langhua/AuroraTessellation-NFC/hardware/pixel/README.md

# 磁像素板（P1 智能像素）设计规格

> 状态（2026-09-23）
>
> - ✅ **架构已定：P1「智能像素」** —— 每块板自带 MCU，既是**可单独销售**的单线圈探测板，也是 4×4 / 8×8 阵列的积木。
> - ✅ **MCU 已定：`CH32V003F4U6`（QFN20，3 × 3 mm）** ✓ SPI ✓ + OPA ✓；`CH32V002F4U6` 同封装 drop-in ✓（见 §4）。
> - ⏳ **阵列间距 20 mm / 22 mm 待定** —— 由 §6 的 coupon 实测决定，**不猜**。
>
> 本文件是像素板的设计依据。`docs/phase-1-4x4-validation.md` 与 `hardware/subboard_4x4/*` 记录的是
> **集中式（P2）**方案（TS3A44159 开关 + CD74HC4067 MUX），**保持不变**；其中 single-channel 板
> （已送厂，3~4 天回板）验证的「线圈 → 2×BAT54S → RC」模拟前端，**正是本像素板的核心，仍然有效**
> （像素板把那 2 颗 BAT54S 换成 **1 颗 `BAS70BRW`** ✓ —— 同样的 4 管全波桥，见 §3）。

NFC 线圈
BAS70BRW
WS2812B-1010

*像素板 = 1 个线圈 + 1 路整流 + 1 颗 MCU + 1 颗 1010 LED*

## 0. 原理图：渲染器与 v1 摆位（2026-09-27）

**为什么要渲染器**：本机 Fritzing 的**命令行导出是坏的** ✗（库仓 `tools/README.md` 早有记录 ✓）
⇒ 每轮都要**用户手动导图**给我看 ✗。`render_sch.py` 把这一步自动化 ✓ —— 它按 Fritzing
自己的摆放规矩把 `.fzz` 的**原理图视图**渲成 PNG/SVG ✓。

    py -3.13 render_sch.py <sketch.fzz> <out.png> [<px宽>] [--verify-export <Fritzing导出的.svg>]

★ **不是自证** ✓：`--verify-export` 拿 **Fritzing 自己导出的 svg 当尺子** ✓ 逐件核对 ✓
（实测：`pixel-schematic.fzz` 9 件 **Δ ≤ 0.0004 单位 = 0.00011 mm** ✓；
`pixel-schematic-v1.fzz` 9 件 **Δ ≤ 0.00003 单位** ✓ ⇒ 渲染即 Fritzing ✓）。

| | | |
|---|---|---|
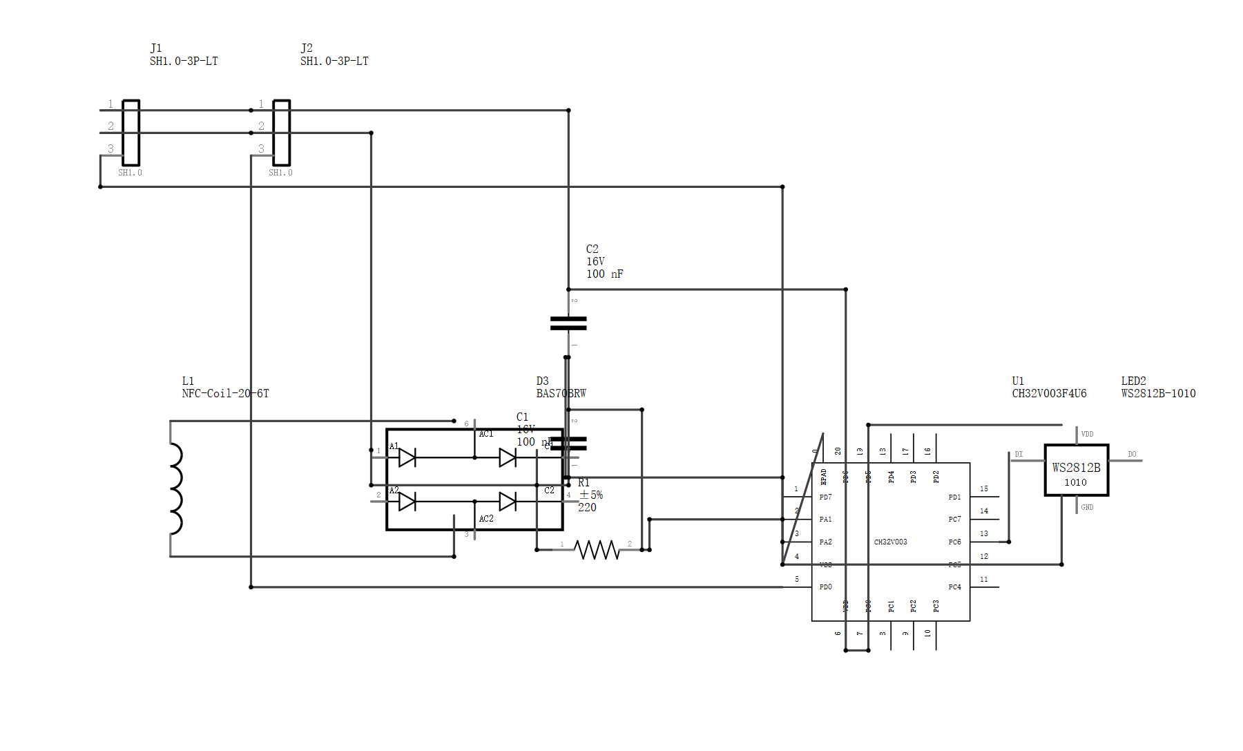
[picture p1: hardware/pixel/pixel-schematic_preview.png]
原图（含 41 根导线）
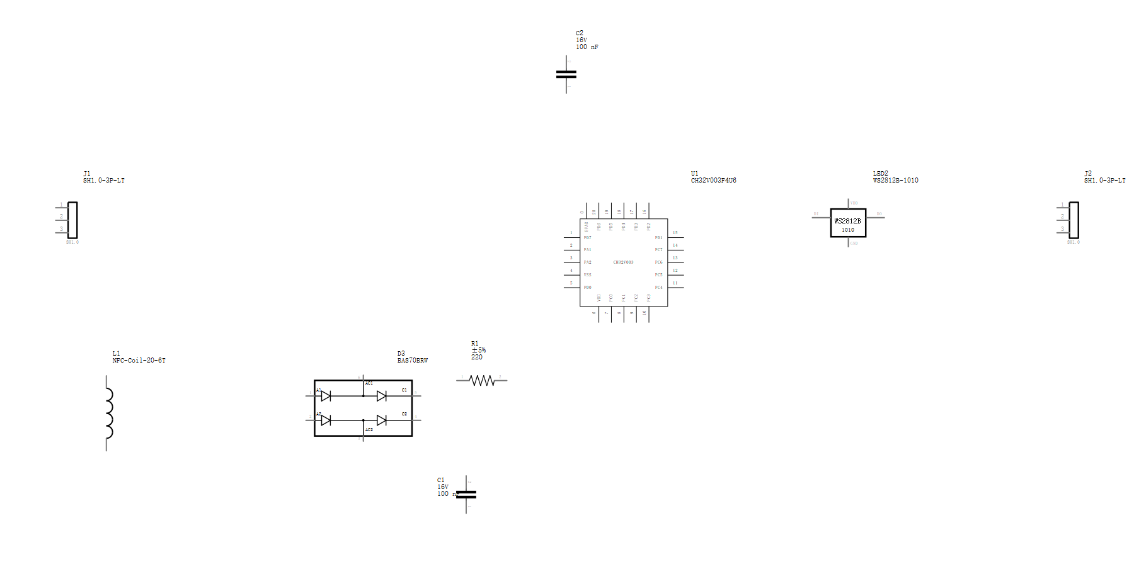
[picture p2: hardware/pixel/pixel-schematic-v1_preview.png]
v1：只摆元件
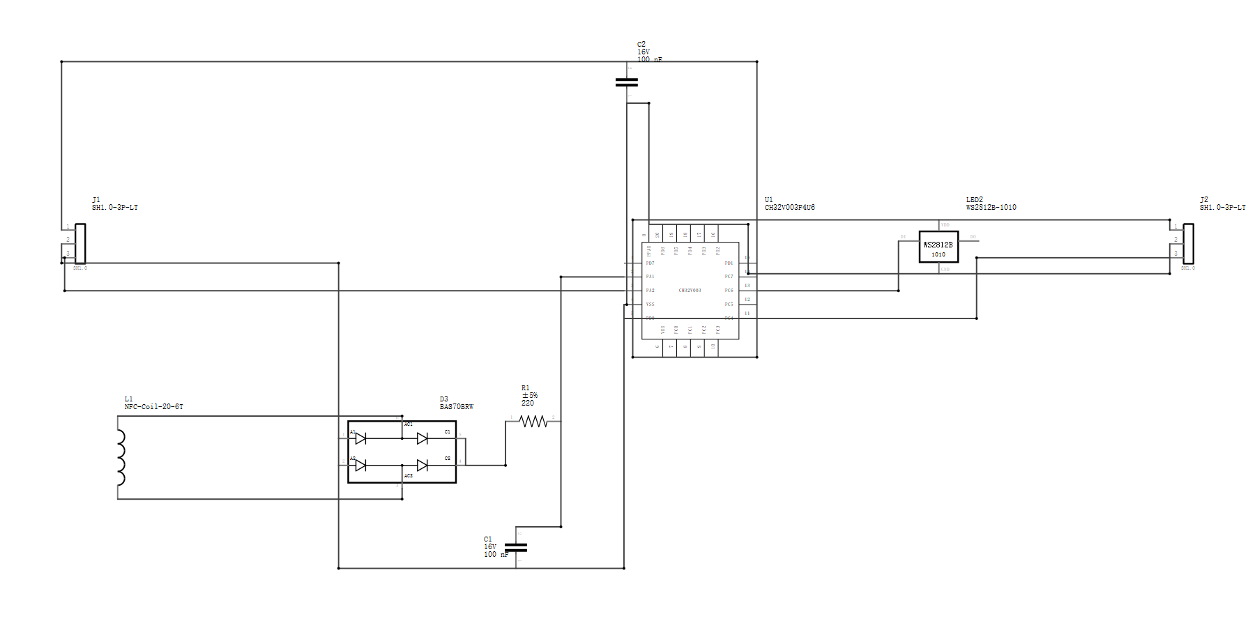
[picture p3: hardware/pixel/pixel-schematic-v2_preview.png]
v2：全接线
|  |  |  |
| **原图** ✓ —— J1/J2 吊在最上方 ✓、长线横穿全图 ✓、位号压在线/元件上 ✓ | **v1** ✓ 只摆元件（主链 `J1→U1→LED2→J2` 一条水平线 ✓、采集支路下沉 ✓、C2 贴 U1 上方 ✓） | **v2** ✓ 全接线（46 根正交导线 ✓、**0 个悬空线端** ✓、绕本体不穿 ✓） |

**v2 = 接线手 ✓**（2026-09-27）：46 根导线、67 条连接 ✓，**网表 10 个网全对 ✓**
（`check_netlist.py` ✓：既无漏接、也无多余连通分量 = **无短路** ✓）、**悬空线端 0 ✓**、
43 → 46 根（绕本体比直穿多 3 根 ✓，换来的正是"不从元件肚子里穿过去" ✓）。

★ 这一手修掉两个真 bug ✓（都在既有管线里，都靠"看得见"才发现 ✓）：
1. **脚位公式错** ✗ —— `sk = loc + RATIO*(尺子 − ox)` 里 `ox` 是"用户坐标 (0,0)"的位置 ✗
   （**不是**零件锚点 ✗）⇒ 凡 `viewBox 原点 ≠ (0,0)` 或**带旋转**的零件，脚位一律偏 ✗
   （实测：J1/J2 偏 1.77 = `k×0.5mm` ✓、U1 偏 17.1 = `k×190` ✓、C1/C2 偏 31.4 ✓；
   原点为 (0,0) 的 D3/L1/R1/LED2 反而只差 0.0001 ⇒ 问题藏得很深 ✗）。
   正解只有一句：**`sketch = RATIO × 尺子坐标`** ✓（我的尺子 1.0 ✓ / Fritzing 导出 1.25 ✓）。
   ⇒ 修好后拟合残差 = **0.0000** ✓、**悬空线端从 11 → 0** ✓。
   （★ 副产品认知：用户原图里那 6 个"悬空端"**不是手画错** ✗，就是这个 bug 的产物 ✓ ——
   我当时误判成用户的图 ✗，记下来别再犯 ✗。）
2. **导线从元件本体里穿过** ✗ —— `path_ok` 对"自己两端元件"**整个豁免** keep-out ✗ ⇒
   为了走直线就从 U1/D3/LED2 肚子里穿过去 ✗。改成**记代价**（穿得少者优先 ✓）而不是
   一律禁 ❌（D3 的 `AC1/AC2` 脚**本来就在本体内部** ✓，禁了就没路 ✓）。

| | | | |
|---|---|---|---|
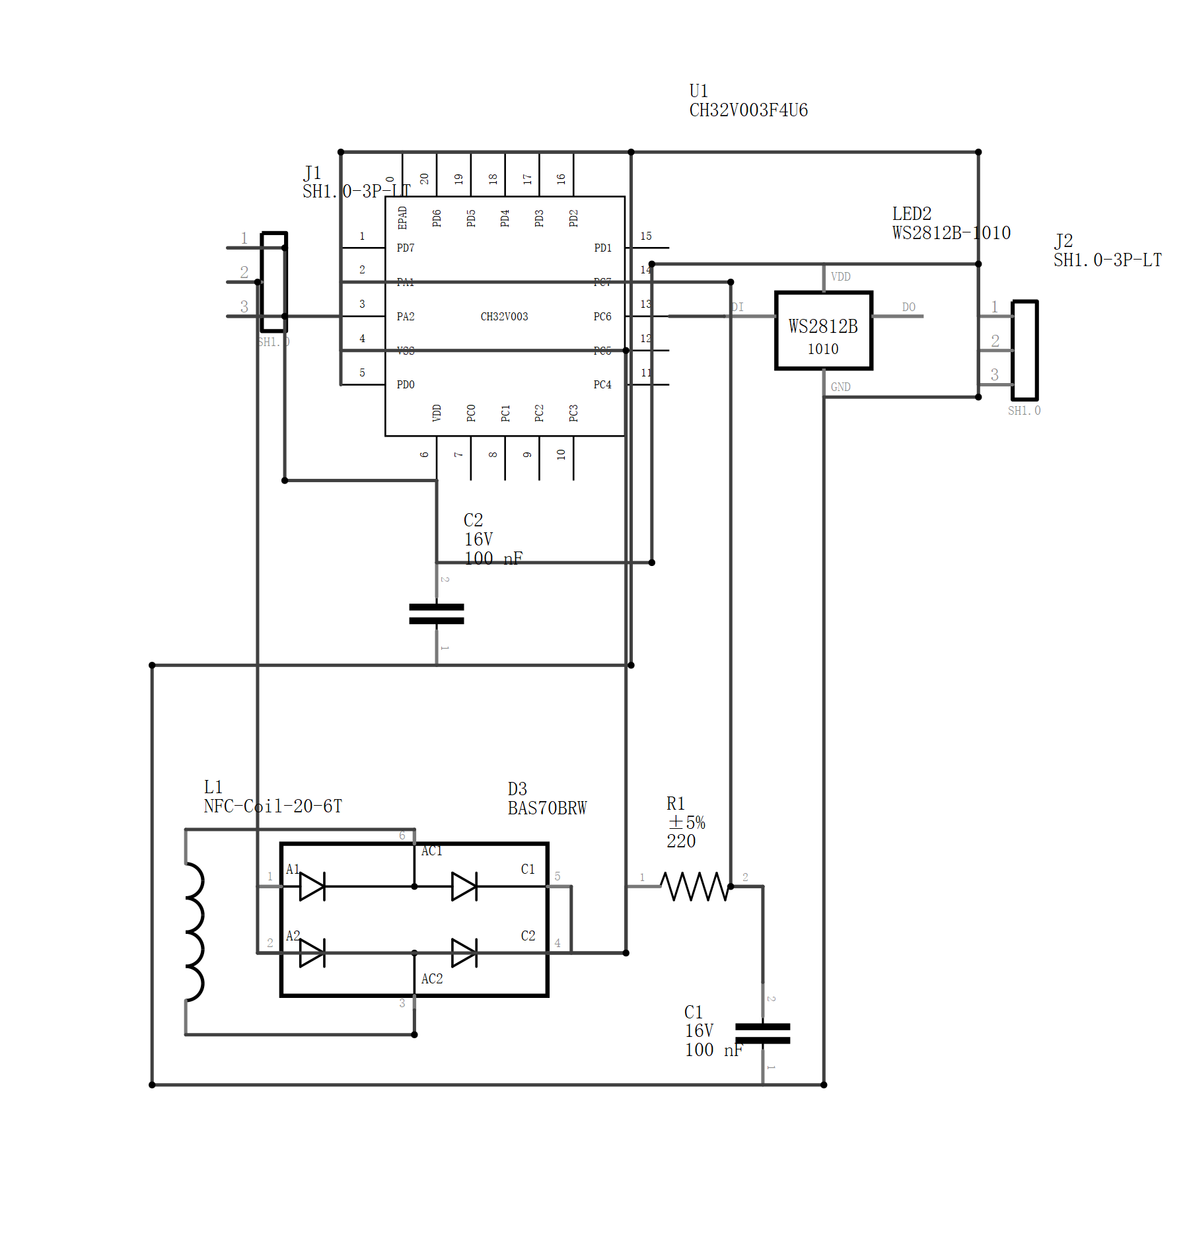
[picture p4: hardware/pixel/pixel-schematic-v3_preview.png]
v3
| 原图 | v1 | v2 |  |
| **原图** ✓ 41 根导线、J1/J2 吊在上方、长线横穿 | **v1** ✓ 只摆元件（拍坐标 ✗） | **v2** ✓ 全接线 | **v3** ✓ 数据驱动摆位 + 交叉代价 |

| | | |
|---|---|---|
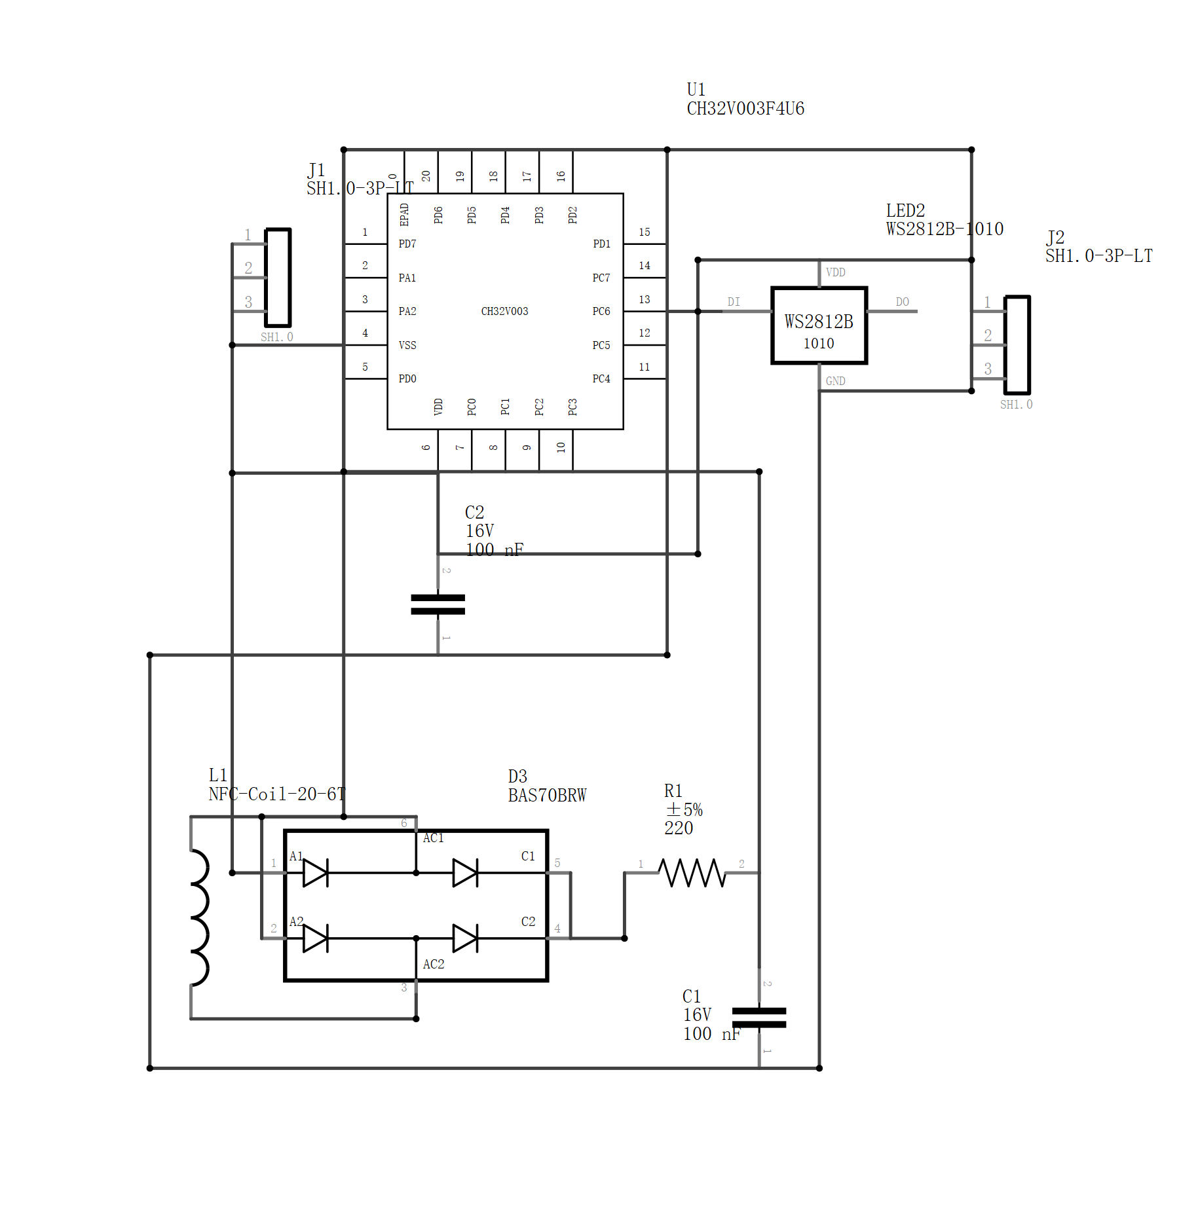
[picture p5: hardware/pixel/pixel-schematic-v4_preview.png]
v4
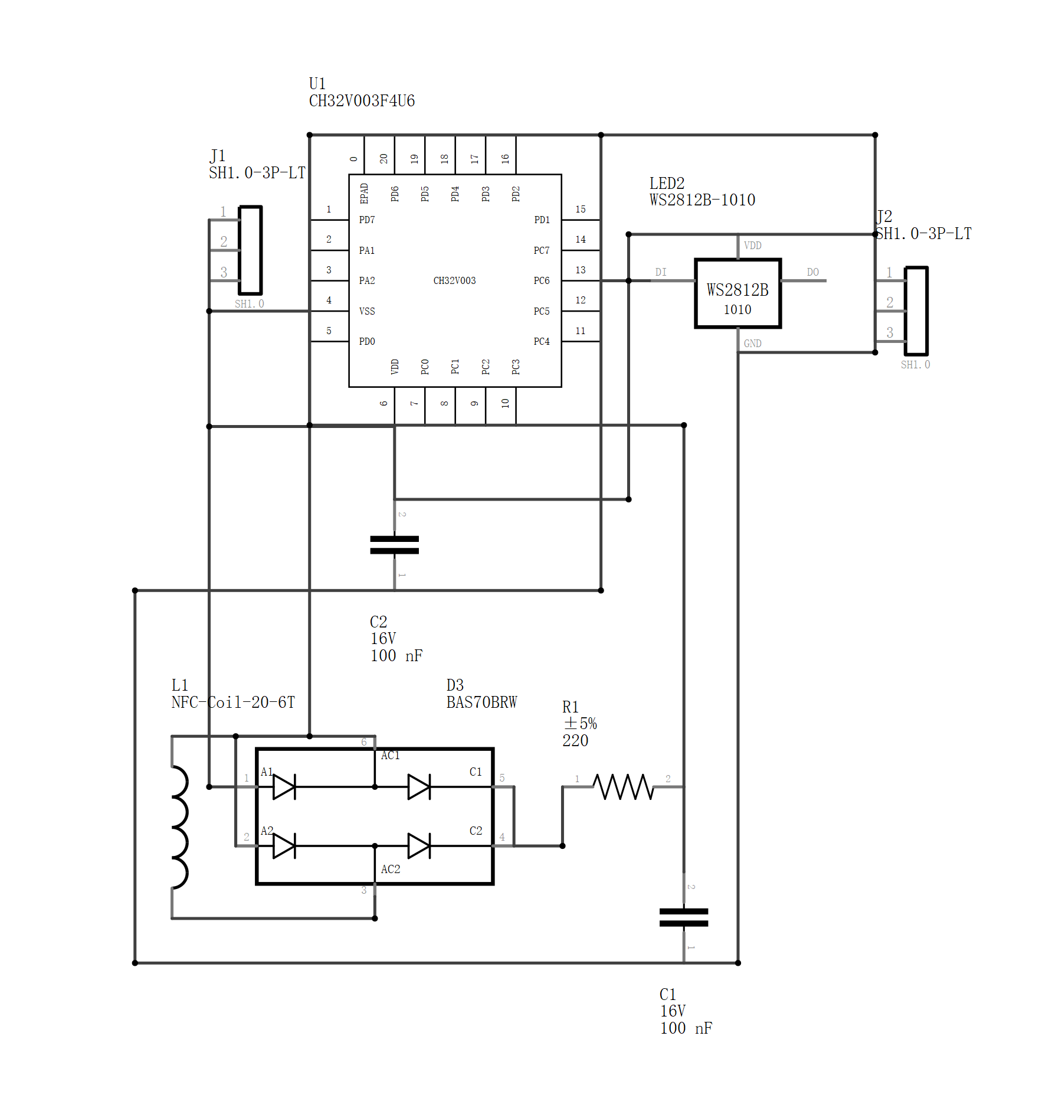
[picture p6: hardware/pixel/pixel-schematic-v5_preview.png]
v5
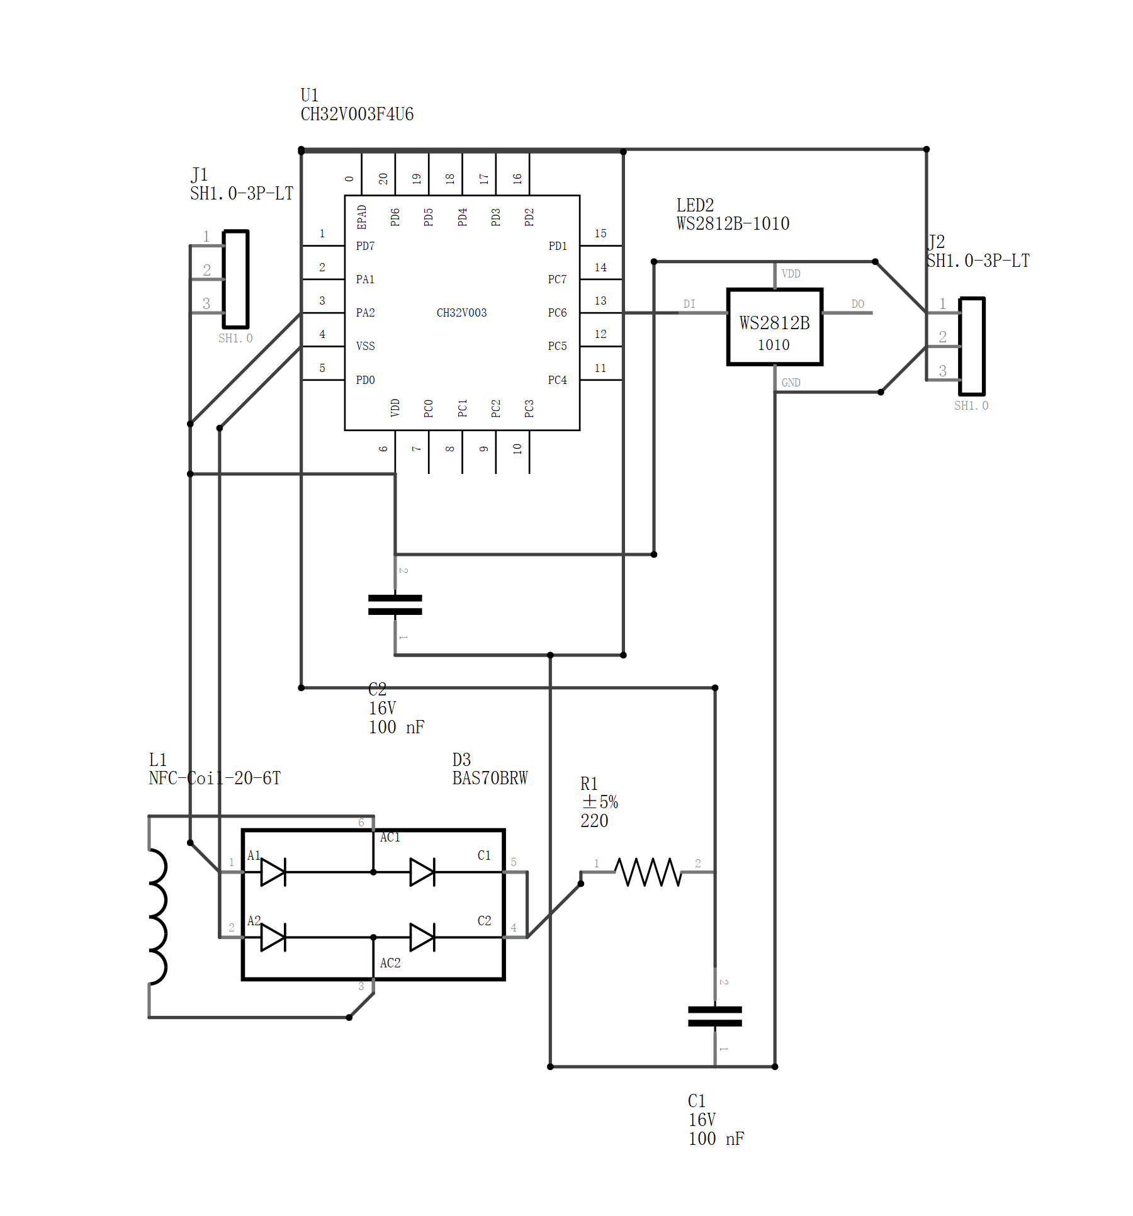
[picture p7: hardware/pixel/pixel-schematic-v6_preview.png]
v6
|  |  |  |
| **v4** ✓ 两条硬限制（不穿本体 ✓） | **v5** ✓ 位号摆位（压导线 1 ✓） | **v6** ✓ **45° 斜线 + 电源/地先布**（交叉 8 ✓、压线 8 ✓、总长 −7% ✓） |

### ★ 交付前机器检查（出厂检查 ✓，2026-09-28 ✓）

起因是用户发现「**我导出的图与你自己画的有蛮多差异**」✗ ⇒ 查出根因是渲染器的 `px`
单位搞错 ✓，但**更值钱的是一条结构性事实** ✓：**Fritzing 的连接只记在 `<connects>` 里** ✓
⇒ **只看连接表的检查，结构上永远看不见“图上的假象”** ✗✗（当时 `check_netlist.py` 报
“45/45 全配上”✓，而用户截图里线**悬在半空** ✗）。⇒ 出厂检查定成**三条** ✓：

| # | 检查 | 命令（在本目录 ✓） | 合格线 ✓ |
|---|---|---|---|
| ① | **网表** ✓ | `py -3.13 check_netlist.py <sketch.fzz>` | **9** 个网全对 ✓（网名 / 个数以 `gen_schematic_wires.py` 的 `NETS` 为准 ✓；无漏接 ✓、无多余连通分量 = **无短路** ✓） |
| ② | **假连线** ✓（新增 ✓） | `py -3.13 check_fake_wires.py <sketch.fzz> …` | **(A)=0 且 (B)=0** ✓（**退出码非 0 = 不合格** ✓） |
| ③ | **硬规则**：导线重叠 ✓ | `py -3.13 gen_schematic_wires.py …` | 「不同的导线重叠 **必须 0**」✓（用户规则② ✓）；非 0 ⇒ **退出码 1** ✓（**文件照常写出** ✓ —— 为的是能打开图看哪儿压了 ✓） |
| ④ | **网标签旗标** ✓（新增 ✓，2026-09-29 ✓） | `py -3.13 check_flags.py <sketch.fzz>` | **被穿旗标 = 0** ✓（**退出码非 0 = 不合格** ✓；图里没有标签时它**拒判**并退 2 ✗，不许“空集当通过” ✗） |
| ⑤ | **接地符号几何** ✓（新增 ✓，2026-09-30 ✓） | `py -3.13 check_grounds.py <sketch.fzz>` | **不合规 = 0** ✓（**退出码非 0 = 不合格** ✓）：脚上必须有导线端点 ✓、**没有线穿过那三根横线** ✗、盒里没有引脚 ✗；没有接地符号时**拒判**并退 2 ✗） |
| ⑥ | **标签脚落在导线上** ✓（新增 ✓，2026-09-30 ✓） | `py -3.13 check_label_touch.py <sketch.fzz>` | **浮空 / 声明不一致 = 0** ✓（**退出码非 0 = 不合格** ✓）：每个网标签**画出来的脚**到最近导线 ≤ 0.05 ✓、且它的 `<connect>` 正好指向那根 ✓；没有网标签时**拒判**并退 2 ✗） |
| ⑦ | **多余接线点（共线切分）** ✓（新增 ✓，2026-09-30 ✓） | `py -3.13 check_junctions.py <sketch.fzz>` | **共线切分 = 0** ✓（**退出码非 0 = 不合格** ✓）：某点恰好两个线端、两线**严格反向** ⇒ 那是把一根直线切成两段 ✗（Fritzing 会在切口画个圆点 ✓）；**落在脚上的接头不算** ✓（脚本来就是要汇点 ✓）；没有导线时**拒判**并退 2 ✗） |

| ⑧ | **硬规则**：**线↔线最小净距** ✓（新增 ✓，2026-10-09 ✓，见 §六十三） | `py -3.13 gen_schematic_wires.py … [--wire-gap=<mm>]` | 「**线与线的净距 ≥ `--wire-gap`**」✓（缺省 **1.0 mm** ✓、范围 **[0.254, 2.54] mm** ✓）；**低于阈值的对数非 0 ⇒ 退出码 1** ✓（**文件照常写出** ✓）。**同网接头**（搭接/并线/T 形/接管 ✓）与**横穿**（真交叉 ✓）**放行** ✓；`--wire-gap=0` ⇒ **关掉** ✓（= 旧行为 ✓，实测逐字节相同 ✓） |
| ⑨ | **状态栏可信度** ✓（新增 ✓，2026-10-10 ✓，见 §五十二） | `py -X utf8 tools\pcb_status.py <sketch.fzz>` ✓（**在本项目目录里直接跑** ✓；它就是库仓那件的**薄入口** ✓ ⇒ 通用件只有一份 ✓）＋ `--sens` ✓（**只读** ✓；逐网明细版 = `tools\pcb_rats_probe.py` ✓，**同一个引擎** ✓） | **A**：**每张网在三个视图里都"成型"** ✓（节点数 ≥ 2 ⇒ 不会被 Fritzing 丢弃 ✗）；**B**：**每张网在每个视图里都连通** ✓（`K = 0` ⇒ 状态栏「还剩 0 条」✓）；**C**：**PCB 视图 M = 网表张数** ✓；★ **判据不用 Fritzing 的文案** ✗ —— 上游 `scoreOneNet`／`updateRoutingStatus` 口径下，**删掉任意一根导线后状态栏仍可能显示「布线完成」** ✗（`≤ 1 只零件脚`的连通片被 `sketchwidget.cpp:7013` 丢弃 ⇒ `K` 恒 0 ✓）⇒ **手工"删线看反应"不能当验收判据** ✗；**退出码非 0 = 不合格** ✓ |

| ⑩ | **Gerber 可送板性** ✓（新增 ✓，2026-10-10 ✓） | `py -X utf8 tools\gerber_check.py gerber --fzz pixel-pcb-v83.fzz --png` ✓（**在本项目目录里直接跑** ✓；工具在库仓 ✓ —— 通用件只有一份 ✓）★ 细则见下 ✓ | **① 层齐全**（铜×2／阻焊×2／丝印×2／板框／钻孔 ✓，缺谁点名 ✗）**② 单位/格式/省略零/轴序/原点**逐文件写清 ✓ **③ 板框闭合** ＋ 尺寸对模型 ✓（⚠ 笔画外沿 / 线心 **两种读法差一个笔宽 0.2032 mm** ✗ ⇒ 下单要说清 ✓）**④ 钻孔逐孔**对模型（位置最大偏差 ≤ 0.06 mm ✓）**⑤ 铜层逐格覆盖**对模型（缺铜 0 ✓）**⑥ 最小铜↔铜间距 ≥ 0.1524 mm（6 mil 常规 ✓）** —— `0.127..0.1524` ⚠、`< 0.127`（5 mil ✗）**不合格** ✓ **⑦ 45° 旋转盘**（G36 ✓）对上 ✓ **⑧ 阻焊每个盘都开窗且比铜大 ✓** **⑨ 丝印**真线宽 ＋ 不压盘（⚠）**⑩ 可疑物**（碎铜／丝印级细线／**同一图形写两遍**／越界／**引用没定义的光圈** ✗）。**退出码：0 = 可送板 ✓ ／ 1 = 不可送板 ✗ ／ 2 = 拒判（缺层 ✓）**；自测 = `py -X utf8 tests\gerber_selftest.py` ✓（正例 ＋ 3 个破坏反例 ✓） |
| ⑩a | **⑩ 的现况（v83 那一批 = 修件之前 ✗，**历史** ✓）** | 同上 ✓ | 这一批（`pixel-pcb-v83` 导出 ✓）**不可送板** ✗：铜层多出 **14 段 0.12 mm** 的细线（= `SH-1.0-3P-V` 的丝印**漏到铜层** ✗ —— 那件的 pcb svg 把 `<g id="silkscreen">` **嵌在** `<g id="copper1">` 里 ✗）⇒ 与 J2 的 24 mil 线只隔 **0.0906 mm（3.57 mil ✗ < 5 mil）**。**修法**：把那 7 条丝印线**移出铜组**（放 `<svg>` 根下 ✓）⇒ 重新导出 ⇒ 间距回到 0.1414 mm（5.57 mil ⚠，可做 ✓）✓。★ 其余项**全 ✓**（层齐 ✓ 原点清 ✓ 板框闭合 ✓ 钻孔逐孔对 ✓ 45° 盘对的 ✓ 覆盖对 ✓ 丝印线是唯一"多出来的铜" ✓），⚠ 项 11 条见工具报告 ✓（导出器既有行为 ✓，不是坏文件 ✗） |
| ⑩b | **⑩ 的现况（v84 起 ✓）—— 「**可送板**」✓** | `py -X utf8 …\tools\gerber_check.py gerber_verify --fzz pixel-pcb-v84.fzz` ✓ | **exit 0 / 可送板 ✓**（`✗0 ⚠11 ✓74` ✓）：底铜最小铜↔铜间距 **0.0906 → 0.1414 mm（3.57 → 5.57 mil）** ✓（不再是 ✗）、底铜**孤立铜岛 8 → 0** ✓、**丝印漏铜的归因项消失** ✓、其余（层齐／单位／原点／板框／钻孔逐孔／45° 盘／覆盖／阻焊）**逐项不变 ✓**。★ `gerber_verify\` 是**等效验证件** ✗（本机无头跑不了 Fritzing GUI ✗ ⇒ 从 `gerber\` **精确删掉那 14 段**漏铜 ＋ 同名光圈定义 ✓，其余 9 个文件**逐字节照搬** ✓）；**交付件仍要用户手工复导一次** ✓（三行步骤见 §五十三 ④ ✓） |

★ 其中 **② ③ ④ ⑤ ⑥ ⑦ ⑧ ⑨ ⑩ 都是真闸门** ✓（**退出码非 0 = 不合格** ✓、可直接进 CI ✓）；
  区别只在“**要不要写文件**” ✓：③ **照写** ✓（要能打开图看哪儿压了 ✓）、②④⑤⑨⑩ 照跑 ✓。

★★ **③ 的来历** ✓（2026-09-28 实测发现 ✓，2026-09-30 口径改准 ✓）：它一开始**只打印一行** ✗
（`── ★★ 规则自检：不同的导线重叠 N 对 ✗✗ 必须 0 ✓`）—— **不停、也不影响写文件** ✗
⇒ 实测证据：`v15 + --hardpin` 那一版重叠 **1** ✗，**文件照写** ✓、我一度把它当合格版用了 ✗。
⇒ 现在代码里就是 `ov_fail = 1 if ov_pairs else 0` + `return ov_fail` ✓ ⇒ **退出码 1** ✓
（与 `check_fake_wires.py` / `check_flags.py` 同一口径：**用退出码说话** ✓）；
而**文件仍然写出** ✓ —— 这条是**故意的** ✓：压缩得看得到是哪儿压的 ✓。
（对照：库仓 `fritzing-parts-langhua` 的绿板生成器是“命中就报错 **＋ 不写文件**” ✓ ——
两种都行 ✓，但**必须写明哪一种** ✗，别让读者猜 ✓。）

★★ **⑧ 与 ③ 的关系** ✓（2026-10-09 ✓ 第四十六轮 ✓）：**③ 是 ⑧ 的 `gap = 0` 那一档** ✓
（重叠 = 净距 0 ✓）。⑧ 把 ③ **升级成一个参数** ✓：`--wire-gap=<mm>` ✓（缺省 1.0 ✓、
范围 [0.254, 2.54] ✓、超范围**夹到边界并打印警告** ✓ 不静默 ✗）。判据**只有一份** ✓：
`sch_geom.gap_pair_bad()` ✓（生成器闸门 `gap_hard_bad()` ✓ / 本机自检 ✓ / 验收探针 ⑪ ✓
三处共用 ✓）；**并入导体** `sch_geom.merge_conductors()` ✓ 也是唯一一份 ✓。

★★ **⑨ 的来历（「状态栏可信度」✓，2026-10-10 ✓ 第五十二轮 ✓）** —— 下面这段**就是这一条验收的判据原文** ✓：

> **⑨ 状态栏可信度**
>
> 起因 ✓：用户报「`pixel-pcb-v83.fzz` 三个视图**都显示布线完成**，可我在三个视图里**随意删掉
> 任意一根导线，也还是布线完成**」✗。
>
> **A**：**每张网在三个视图里都"成型"** ✓ = 节点数 ≥ 2 ✓ —— 少于 2 只**零件脚**的连通片会被
> `collectParts` 之后的 `partConnectorItems.count() <= 1 ⇒ 整片跳过` ✗（`sketch/sketchwidget.cpp:7013` ✓）
> ⇒ 那张网在 Fritzing 眼里**根本不存在** ✗（网退化成 1 只脚 = "剥瘦底图"那一类病 ✓，v69/v77 就是它 ✓）。
>
> **B**：**每张网在每个视图里都连通** ✓ = `K = 0` ✓（状态栏「还剩 0 条」✓）。★ `K` = 该网
> **连通片数 − 1** ✓（`utils/graphutils.cpp:447`、`573` ✓ —— **不是**"没连上的脚数" ✗）。
>
> **C**：★★ **判据不用 Fritzing 的文案** ✗ —— **这条是上游限制，已实测可证** ✓：
> 在 `scoreOneNet`／`updateRoutingStatus` 的口径下，**删掉任意一根导线后状态栏仍可能显示
> 「布线完成」** ✗ —— 单刀切开一张网 ⇒ 每片**各自内部连通** ⇒ 每片 `K = 0` ✓，而**只有 1 只
> 零件脚**的碎片被 `sketchwidget.cpp:7013` **整片丢弃** ✗ ⇒ `netCount == routedCount` **恒成立** ✓。
> 实测 ✓：三视图合计 **133** 根线**全部虚拟删过** ⇒ **0/133** 有反应 ✗（面包板 36／原理图 45／
> PCB 52 ✓；其中**真断铜**的 27／44／48 根也一样一声不响 ✗）⇒ **手工"删线看反应"不能作为验收
> 判据** ✗（**任何**文件都过不了 ✗，不是本文件的病 ✗）—— 要判"线有没有断"，**用 A/B/C 这三把尺子** ✓。
>
> **怎么跑** ✓（cwd = 本目录 ✓；`tools\pcb_status.py` = 库仓那件的**薄入口** ✓，通用件只有一份 ✓，
> 本体在 `F:\git\fritzing-parts-langhua\tools\pcb_status.py` ✓）：
> ```bat
> py -X utf8 tools\pcb_status.py pixel-pcb-v83.fzz          rem 逐视图 M/K ＋ 文案 ⇒ exit 0
> py -X utf8 tools\pcb_status.py pixel-pcb-v83.fzz --sens   rem 虚拟删线灵敏度 ⇒ exit 0
> py -X utf8 tools\pcb_rats_probe.py pixel-pcb-v83.fzz      rem 逐网明细版（同一引擎 ✓）
> py -X utf8 F:\git\fritzing-parts-langhua\tools\gerber_check.py gerber --fzz pixel-pcb-v83.fzz --png
>                                                          rem ⑩ 用户手工导出的那批 = **修件之前** ⇒ 不可送板 ✗（见 ⑩a）
> py -X utf8 F:\git\fritzing-parts-langhua\tools\gerber_check.py gerber_verify --fzz pixel-pcb-v84.fzz --png
>                                                          rem ⑩ **修件之后**的等效复验 ⇒ 可送板 ✓（见 ⑩b / §五十三）
> py -3.13 F:\git\fritzing-parts-langhua\tools\silk_nest_check.py
>                                                          rem 丝印组有没有嵌在铜组里（库仓扫全库 ✓）
> ```
> ★ **校准证据** ✓（**逐字对上** ✓ —— 这把尺子可信的立足点 ✓，见 §五十二 ② ✓）：
> `v68 → M=9/K=0` ✓、`v81 → M=7/K=2` ✓（= 用户读到的「5 of 7 … 2 connector(s) still to be routed」✓）、
> `_work/v76.4_byHand → M=7/K=2` ✓、`v82 → M=9/K=0` ✓、`v83 → M=9/K=0` ✓（用户读到「三视图都布线完成」✓）。
> ★ 工具库侧登记 ✓ = `fritzing-parts-langhua\tools\README.md` 里 `pcb_status.py` 那一行 ✓
> （用途 ✓／参数 ✓／退出码 ✓ ＋「对应本清单 **⑨**」✓）。

### ★ 工具沿革 · 退役记录（2026-10-10 ✓）

- ★ **`fz_exact.py`（第四十手"照 Fritzing 源码逐条实现"的那份判据 ✓；原在本目录 ✓）已退役** ✗：
  ① **会误报** ✗ —— 它在 `pixel-pcb-v59.fzz` 上就报「**9 of 9 - 0**」✗，而用户实测是 **2** ✗；
  ② **已被取代** ✓ —— 同一件事现在由库仓 `tools\pcb_status.py` ✓（引擎**唯一一份** ✓）＋ 本仓
  `tools\pcb_rats_probe.py` ✓（逐视图 ＋ 灵敏度 ✓）做 ✓，且**在 v68／v81／v76.4／v82／v83 上逐字对上** ✓；
  ③ ⇒ 2026-10-10 用户定 ✓：**删掉该文件 ＋ 清掉所有指向它的引用 / 说明** ✓（本仓 `fz_decl_inventory.py`
  ／`fz_pad_probe.py` 的头注释 ✓、库仓 `pcb_check.py`／`pcb_pads.py`／`docs/fritzing-fz-notes.md` ✓）。
  ★ 本记录**是它名字的唯一去处** ✓；历史轮次里它量出的数字（如第四十／四十一手那两个「9 of 9 - 0」✓）
  **一律不作验收判据** ✗。

### ★ 测试在哪 / 怎么跑（**仓规** ✓，2026-10-09 用户定 ✓ ⇒ 见 §六十四 ✓）

上面 ①–⑨ 是**在真交付件上**跑的**出厂检查** ✓；与它们并列的另一类 = **判据单元自测** ✓
（**不用任何 `.fzz`** ✓，在内存里摆正反样例把**判据**钉死 ✓）——★ **它们现在入库了** ✓：
- **项目自己的测试 = 本目录 `tests/`** ✓（`hardware/pixel/tests/` ✓）；
- **通用工具的测试 = 库仓 `fritzing-parts-langhua/tools/tests/`** ✓
  （✗ 不再散在 `_work/` 那种**被忽略**的目录里 ✗ —— 两份真源 ✓）；
- 每个脚本**自带 `exit 0/1`** ✓、**零第三方依赖** ✓（只用标准库 ✓）；
- 命名保留 **`*_selftest.py`** ✓ —— ✗ **故意不叫 `test_*.py`** ✗（pytest 会收集它、
  被模块级 `SystemExit` 打崩 ✓）；
- **一行跑全部** ✓：

```bat
py -X utf8 tests\run_all.py                 # 本仓（hardware/pixel）全部 ⇒ 全过 ✓ 全过 ＋ exit 0 ✓
py -X utf8 tests\run_all.py --with-lib      # 顺带把库仓那套（tools/tests/run_all.py）也跑一遍 ✓
```

| 测试 ✓ | 在哪 ✓ | 钉住什么 ✓ |
|---|---|---|
| `tests/tie_cands_selftest.py` ✓ | **本仓** ✓ | `gen_schematic_wires.tie_cands()` ✓（同网搭接候选 ✓：正例 ✓／`b` 不在同网上 ⇒ 0 条 ✓／异网不算 ✓／退化段不参与 ✓／**反向那一支** ✓／`plen` ✓）|
| `tools/tests/sch_geom_gap_selftest.py` ✓ | 库仓 ✓ | `sch_geom` 的**线距判据** ✓（合并导体 ✓／接头放行 ✓／横穿不计 ✓／**共线同侧重叠不放行** ✓）|
| `tools/tests/sch_body_selftest.py` ✓ | 库仓 ✓ | `sch_body` 的**本体外形**判据 ✓（区域/描边/`A` 弧/旋转/「整段豁免」必须失效 ✓）|
| `tools/tests/pcb_curve_selftest.py` ✓ | 库仓 ✓ | PCB **弧几何**判据 ✓（弦看不见、弧看得见 ✓）|

**②在查什么** ✓（几何 vs 连接表 ✓，两侧都要看 ✓）：**(A)** 表里声明接了某脚 ✗ 而线
**根本没画到**那只脚上 ⇒ 图上看着**断开** ✗；**(B)** 线**画在**某脚上（端点落在脚上 ✓
或**线身穿心** ✓）而表里**没那条** ✗ ⇒ 图上像接上 ✓、**电气上是断的** ✗（最阴的一种 ✓）。
★ 判据**只有一份** ✓（在 `render_sch.py` 里 ✓）；`check_fake_wires.py` 只负责**跑 + 取数
+ 判合格线** ✓，**不写第二份几何代码** ✗，且**取不到数字就报错退出** ✗（不许“没解析到 = 通过” ✗）。

★ 同批实测 ✓（三版同一口径 ✓，2026-09-28 ✓）：

| 版本 | (A) | (B) | 判读 |
|---|---|---|---|
| **v14**（穿体 **0** ✓、交叉 14 ✓） | 0 ✓ | **9 ✗** | **全是线身穿心** ✓ —— 一根竖线**正好穿过** `U1` 左排三只脚的坐标点（9 处里 **6 处**是 `U1`）✗ |
| **v15**（**当前交付版** ✓、重叠 0 ✓） | 0 ✓ | **8 ✗** | 骑 `U1` 左排列 3 处 + **骑底排行 5 处**（`y=−43.2`）⇒ **当前交付版也不合格** ✗ |
| `v15 + --hardpin` ✓ | 0 ✓ | **0 ✓✓** | **只有它合格** ✓（代价见下 ✗） |

⇒ 定量结论 ✓：**`--hardpin`（线不许落在“别的脚”上 ✓）是唯一能到 (B)=0 的开关** ✓。
★ 代价必须按**同参数 A/B** 量 ✓（`v15` vs `v15 + --hardpin` ✓ —— 两边其它开关**完全相同** ✓）：

| 指标 | **v15**（交付 ✓） | **v15 + `--hardpin`** | 判读 |
|---|---|---|---|
| **(B) 假连线** | 8 ✗ | **0** ✓✓ | ✅ 目标达成 ✓ |
| **贴脚**（<7.2） | 11 ✗ | **7** ✓ | ✅ 变好 ✓ |
| **穿体**（穿别的元件本体） | **6** ✗ | **9** ✗✗ | ❌ 变差 ✗ |
| **十字交叉** | **16** | **21** ✗ | ❌ 变差 ✗ |
| **近重合** | **0** ✓✓ | **1** ✗ | ❌ v15 刚立的硬规则被破 ✗ |
| 总长 | 2323.7 | 2246.1 | ✅ 略短 ✓（−3% ✓） |
| 画布 mm | 77.0×82.9 | 78.1×83.1 | ≈ 持平 ✓ |

⇒ 用户定的两条硬指标「**穿体 0 ✓ 且 贴脚 0 ✓**」**目前还没有一版同时做到** ✗
（三版都有硬数据 ✓：v14 = 穿体 0 ✓ / (B) 9 ✗；v15 = 重叠 0 ✓ / (B) 8 ✗；
`--hardpin` = (B) 0 ✓✓ / 穿体 9 ✗）⇒ **v16 的工作点要在这两条之间定** ✓（待用户定 ✗）。

### 摆位与布线的量化对比（2026-09-27 ✓）

| 版本 | 摆位 | 布线代价 | 总长（sketch 单位） | **十字交叉** | 穿别的元件本体 | 位号压导线 | 位号压元件 | 画布 |
|---|---|---|---|---|---|---|---|---|
| v1 | 拍坐标 ✗ | —（无线） | 0 | 0 | 0 | — | — | 815 × 409 |
| v2 | 拍坐标 ✗ | 无交叉项 ✗ | 4229.5 | 12 | 7 | 8 | 2 | 815 × 409 |
| 中间版 | **数据驱动** ✓ | 无交叉项 ✗ | **2340.4** | **16** ✗ | 9 | 8 | 2 | 313 × 325 |
| v3 | **数据驱动** ✓ | **含交叉代价** ✓ | 2603.5 | **8** ✓ | 7 | 8 | 2 | 313 × 325 |
| v4 | **数据驱动** ✓ | 含交叉 + **两条硬限制** ✓ | 2495.9 | **7** ✓ | **0** ✓✓ | 8 ✗ | 2 ✗ | 315 × 325 |
| **v5** | 数据驱动 ✓ + **位号摆位** ✓ | 同上 ✓ | **2495.9** | **7** ✓ | **0** ✓✓ | **1** ✓✓ | **0** ✓✓ | 315 × 325 |
| **v6** ✓ | 同 v5 ✓（仅“插座间距”开关默认 0 ✓） | **+ 45° 斜线** ✓ + **电源/地先布** ✓ + **压线当交集** ✓ | **2322.5** ✓ | **8**（同口径 12 → 8 ✓） | **0** ✓✓ | **3** ⚠ | **0** ✓✓ | **304 × 326** ✓ |

> ★ **v6 的“8”不是变差 ✗** —— 它与 v5 的“8”不在同一条摆位上（摆位脚本这一天又改过 ✓，
> 同一条摆位下**关掉 45°** 是 **12** ✓）⇒ 可比的只有下面那张 A/B 表 ✓。
> 另：v6 多出一个“位号压导线 **3** ”⚠（v5 是 1 ✓）—— 原因与处置见下一小节 ✓（**如实报** ✓ 不藏 ✗）。

**v5 相对 v2**：总长 **−41%** ✓、交叉 **12 → 7** ✓、**穿别的元件本体 7 → 0** ✓✓、
**位号压导线 8 → 1** ✓✓、**位号压元件 2 → 0** ✓✓、画布面积 **−87%** ✓；
网表 10 个网全对 ✓、悬空线端 0 ✓。

### 第六手：45° 斜线（2026-09-27 ✓ 用户定）

用户原话：**“允许 45° 斜线”** ✓。★ 我先去**量了他手改的那一版** ✓（`diag_angles.py` ✓）：
里面 15 根斜线的角度是 `20.1° / 23.4° / 28.8° / 2:1 / 1°…` ✗ —— **不是 45°** ✓，
即“两脚直接连一根直线” ✓。两种都做了、都量了 ✓（**A/B 对照同一条摆位** ✓）：

| 布线器允许的倾斜 | 导线 | **十字交叉** | 压线对 | 总长 | 悬空端 | 穿本体 |
|---|---|---|---|---|---|---|
| 只准正交 ✗ | 48 | **12** | 11 | 2386.1 | 0 ✓ | 0 ✓ |
| **含 45°（采纳 ✓）** | **45** ✓ | **8** ✓✓ | **8** ✓✓ | 2400.3（+0.6% ✓） | 0 ✓ | 0 ✓ |
| 任意角直连 ✗ | 45 | **37∼42** ✗✗ | **88∼100** ✗✗ | **4941** ✗✗ | 0 ✓ | 2 ✗ |

⇒ **只有 45° 的“小斜切”是赚的** ✓（交叉 −4 ✓、压线 −3 ✓、长度几乎不变 ✓）；
**“任意角直连”是亏的** ✗✗（它横穿全图、开头几根就把后面的路全堵了 ✗）。
所以实现成 **45° + 正交的 dogleg**（每段不是 45° 就是 0°/90° ✓、四种落法 × 两侧 ✓），
斜线只给**小罚分** `DIAG_PEN = 1.25`（✓ 可调 ✓），只有在**省长度**时才被选中 ✓。

★ 同批还量了两条“看起来该有用、实测亏”的：

| 尝试 | 实测结果 | 处置 |
|---|---|---|
| **插座（J1/J2）跟核心电路拉开距离**（你手改版的洞察 ✓，量出是 **+4 格 = 28.8 单位** ✓） | 交叉 **8 → 10** ✗、总长 +9% ✗、画布 98.9 → **116.2mm** ✗✗ | **默认关掉** ✓（`SOCKET_EXTRA` 留成开关 ✓）—— 它是**审美**取舍（信息层次 ✓）不是指标改善 ✗，**请你定** ✓ |
| **让布线器认识位号框**（去消“位号压导线” ✓） | 位号压导线只 **3 → 2** ✗（剩的 `L1` 旁边没通道 ✓），代价 **压线 8 → 10** ✗ | **回退** ✓ —— 位号那条得让**位号自己挪**（布线完重摆 ✓），不让导线绕 ✗ |

另修一条真毛病 ✓（这条**是**赚的 ✓）：**两段压在同一条直线上** ✗ ⇒ 现在按“**一类交集**”计数 ✓
（判据 = 唯一的 `sch_geom.near_overlap` ✓）。起因是量 v5 时发现 **J1 三只脚的线全在同一列上竖着走** ✗
（图上像三只脚短路 ✗）⇒ 压线对 **19 → 8** ✓。

★ 交给用户的**两条教训**（都写进代码注释了 ✓）：

1. **判据只能一份实现** ✓ —— 为了量斜线，原来的“交叉”判据（**只认正交** ✗）必须换掉 ✓：
   实测换了之后，**手改版从 4 变成 18** ✗（它的斜线交叉原来一个都没被算 ✓）
   ⇒ 我先前那句“手改版只有 4 处交叉”是**假数字** ✗，现已用**另一套算法（密集采样 ✓）复核一致** ✓；
2. **输入必须是“只有摆位、没有线”的画布** ✓ —— 我一度拿**已有线的 v5** 当输入 ✗
   ⇒ 旧 48 根 + 新 45 根 = **93 根** ✗、所有指标全废 ✗（绕了一大圈才发现 ✓）。

### 第七手：两条用户规则（安全距离 ✓ / 不重叠 ✓）与 v15 的取舍（2026-09-27 ✓ 用户定）

用户原话 ✓：
- ①「现在的严重问题是**导线离芯片引脚太近了** ⇒ 应该设立一个规则，让导线跟芯片引脚有个
  **安全距离**，从而让导线和引脚的连接关系**能通过肉眼看得清晰**」✓
- ②「**不同的导线，不能重叠**」✓（「这一条，类似面包板里的规则」✓ = 一个孔只能插一根线 ✓）

**判据（各自只有一份实现 ✓）**：① 每根导线取两端 0.05 内的脚为“自己的脚”✓，其余脚里离该线段
`< CLEAR_PIN = 7.2 单位（2.03 mm）` 记 **1 处** ✗；② `sch_geom.near_overlap` ✓（含斜线 ✓）。
② 已做成**硬闸门** ✓ —— 生成器自检「不同的导线重叠 **必须 0**」✓，不合格就报错 ✗。

| | | |
|---|---|---|
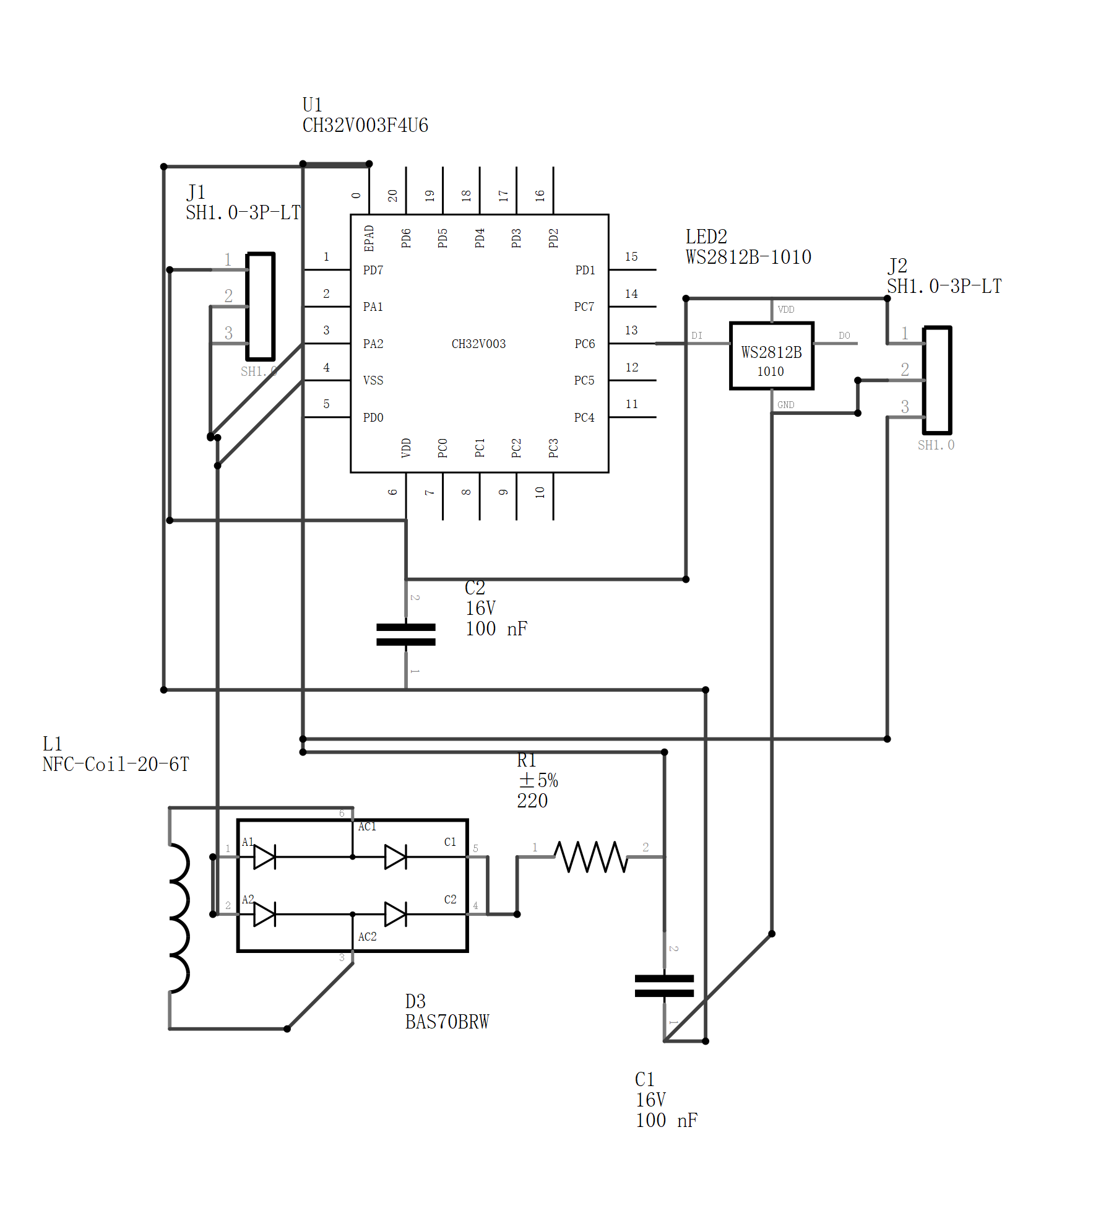
[picture p8: hardware/pixel/pixel-schematic-v14_preview.png]
v14
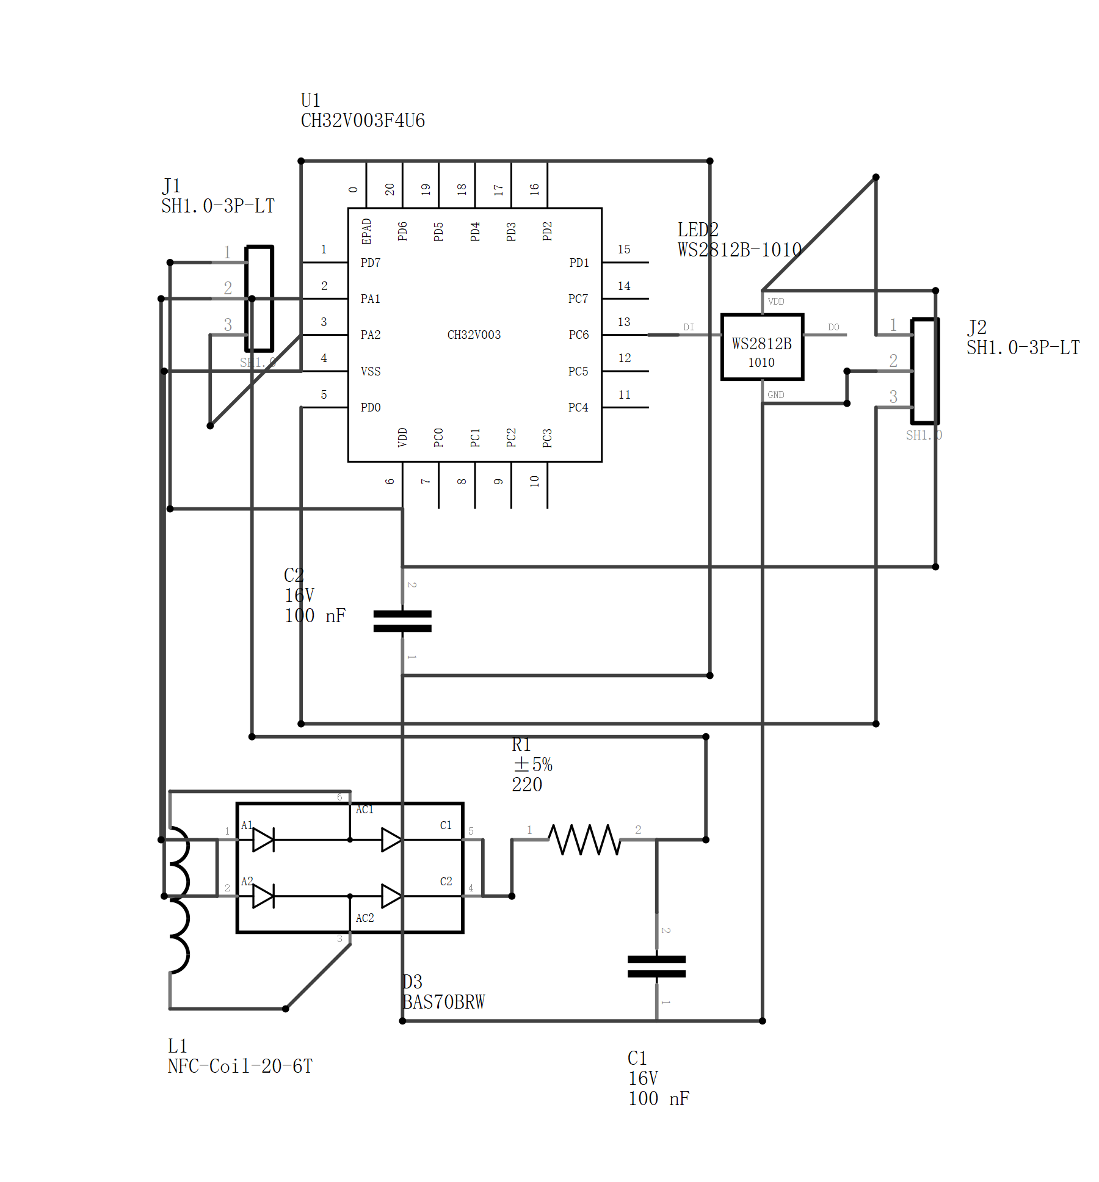
[picture p9: hardware/pixel/pixel-schematic-v15_preview.png]
v15
|  |  | v15 局部 |
| **v14** ✓ 穿体 **0** ✓、交叉 **14** ✓、贴脚 14 ✗ —— 但**重叠 4** ✗ | **v15** ✓✓ **重叠 0** ✓✓、贴脚 **11** ✓✓（历代最好 ✓）—— 代价见下表 ✗ | **v15** 当时是交付版 ✓（提交 `ebb344b` ✓；**先后被 v16 / v17 / v18 取代** ✓，见「第八手…第十手」↓） |

**全版本同一套口径、重新量过** ✓（`_scratch/table_versions.py` ✓，判据仍是渲染器那唯一一份 ✓）：

| 版本 | 导线 | 十字交叉 | 穿别的元件本体 | 贴脚(<7.2) | 近重合 | 位号压导线 | 位号压元件 | 总长 | 画布 mm |
|---|---|---|---|---|---|---|---|---|---|
| 原图 | 41 | 11 | 2 | 27 | 1 | 7 | 3 | 2720 | 136.6×84.4 |
| v9 | 48 | **8** ✓ | 0 ✓ | 40 ✗ | 8 | 3 | 0 ✓ | 2028 | 76.4×83.9 |
| v11 | 49 | 15 | **0** ✓ | 13 | 6 | 0 ✓ | 0 ✓ | 2056 | 76.8×83.7 |
| v13 | 52 | 13 | **0** ✓ | 16 | 4 | 0 ✓ | 0 ✓ | 2059 | 76.8×83.9 |
| v14 | 51 | **14** | **0** ✓ | 14 | 4 | 0 ✓ | 0 ✓ | 2042 | 76.8×83.1 |
| **v15** ✓ | 50 | 16 ✗ | 6 ✗ | **11** ✓✓ | **0** ✓✓ | 4 ✗ | 0 ✓ | 2324 | **77.0×82.9** ✓ |
| **v16** ✓ | 53 | 23 ✗ | 9 ✗ | 11 | **0** ✓✓ | 7 ✗ | 0 ✓ | 2274 | 82.0×86.3 |
| **v17** ✓ | 47 ✓ | **10** ✓✓ | 10 ✗ | 11 | **0** ✓✓ | 6 ✓ | **1** ✗ | **2060** ✓ | 83.2×82.9 |
| **v18** ✓（旧交付 ✓，已被 v19 取代 ✓） | **46** ✓ | **10** ✓✓ | **6** ✓✓ | 11 | **0** ✓✓ | **2** ✓ | **0** ✓ | **2025** ✓ | 89.3×82.9 ✗ |
| **v19** ✓（旧交付 ✓，已被 v20 取代 ✓） | 63 | 19 / 20 | **0** ✓✓ | 13 / **7** ✓ | **0** ✓✓ | 3 | 3 | 2698 / 2988 | 90.6 / 107.8×93.7 ✗ |
| **v20** ✓（旧交付 ✓，已被 v21 取代 ✓；第十四手 ✓） | 61 | 19 / 20 | **0** ✓✓ | **11 / 6** ✓ | **0** ✓✓ | 2 | 2 | **2641 / 2912** ✓ | 95.9 / 112.2×**87.4** ✓ |
| **v21** ✓（旧交付 ✓，已被 v22 取代 ✓；第十五手 ✓） | 57 | **17 / 18** ✓ | **0** ✓✓ | **7 / 2** ✓✓ | **0** ✓✓ | **1** ✓ | **0** ✓ | 2564 / 2835 ✓ | 95.9 / 112.2×**87.4** ✓ |
| **v22** ✓（**旧交付** ✓；第十六手 ✓） | **57 / 56** ✓ | **17 / 16** ✓ | **0** ✓✓ | **7 / 2** ✓ | **0** ✓✓ | **1** ✓ | **0** ✓ | **2564 / 2743** ✓✓ | 95.9 / **110.2**×**87.4** ✓ |
| **v23** ✓（**旧交付** ✓，已被 v24 取代 ✓；第十七手 ✓） | **56 / 57** ✓ | **16 / 15** ✓ | **0** ✓✓ | **9 / 1** ✓✓ | **0** ✓✓ | **1** ✓ | **0** ✓ | 2586 / **2716** ✓✓ | **95.7** / **105.8**×**87.4** ✓ |
| **v24** ✓（**旧交付** ✓，已被 v25 取代 ✓；第十八手 ✓） | **54 / 57** ✓ | 14 / 14 ✗（档1 那个数**偏少** ✗，见第十九手 ④ ✓） | 4 ✗ / **0** ✓✓ | **0 / 0** ✓✓✓ | **0** ✓✓ | 2 / **1** ✓ | **0** ✓ | **2545 / 2724** ✓ | 95.7 / **105.8**×**87.4** ✓ |
| **v25** ✓（**旧交付** ✓，已被 v26 取代 ✓；第十九手 ✓） | **54 / 55** ✓ | **14 / 15** ✓（**真值** ✓） | 4 ✗ / **0** ✓✓ | **0 / 0** ✓✓✓ | **0** ✓✓ | 2 / **1** ✓ | **0** ✓ | **2545 / 2699** ✓✓ | 95.7 / **105.8**×**87.4** ✓ |
| **v26** ✓（**旧交付** ✓，已被 v27 取代 ✓；第二十手 ✓） | **54 / 55** ✓ | **14 / 15** ✓ | 4 ✗ / **0** ✓✓ | **0 / 0** ✓✓✓ | **0** ✓✓ | 2 / **1** ✓ | **0** ✓ | 2545 / **2699** ✓✓ | 95.7 / **105.8**×**87.4** ✓ |
| **v27** ✓（**旧交付** ✓，已被 v28 取代 ✓；第二十一手 ✓；假接头 0 ✓、悬空端 **1** ✓） | **54 / 55** ✓ | **14 / 15** ✓ | 4 ✗ / **0** ✓✓ | **0 / 0** ✓✓✓ | **0** ✓✓ | 2 / **1** ✓ | **0** ✓ | 2545 / **2692** ✓✓ | 95.7 / **105.8**×**87.4** ✓ |
| **v28** ✓（**旧交付** ✓，已被 v29 取代 ✓；第二十二手 ✓；支线共享竖线 ✓、擦身 15→**8** ✓） | **52 / 52** ✓ | **11 / 15** ✓ | 4 ✗ / **0** ✓✓ | **0 / 0** ✓✓✓ | **0** ✓✓ | 2 / **1** ✓ | **0** ✓ | **2419 / 2640** ✓✓ | **91.6** / **105.8**×**87.4** ✓ |
| **v29** ✓（**新交付** ✓；第二十三手 ✓；两种形态都齐 ✓、**追平手改版** ✓） | **52 / 51** ✓ | 11 / **13** ✓ | 4 ✗ / **0** ✓✓ | **0 / 0** ✓✓✓ | **0** ✓✓ | 2 / **1** ✓ | **0** ✓ | **2420 / 2578** ✓✓ | **91.6** / **105.8**×**87.4** ✓ |

★ **v24 起“档 0”已作废** ✓（用户 2026-09-28 定 ✓）：`--socket=0` 是**最紧的摆位** ✓，只当
**历史对照** ✓，不再作交付判据 ✗ —— 它的「贴脚 0」与「穿体 0」在**当前摆位**下不可兼得 ✓
（原因与数字见「第十八手」✓）。⇒ **交付判据只看档 1（`--socket=4`）** ✓。

★ v16 / v17 / v18 这三行用**同一套判据**（`render_sch.py` ✓）量的 ✓；它们另有两项本表没有的 ✓：
**(B) 假连线 0 ✓✓** 与 **(C) 退化为点的导线 0 ✓✓**（v16 当时是 **4 根** ✗ —— 已由 `MIN_SEG` 修掉 ✓）。
⇒ **v17 换了链序（`revyx` ✓）**：交叉 **23 → 10** ✓✓（比用户手改版的 11 还好 ✓）、导线 53→**47** ✓、总长 −9% ✓；
⇒ **v18 把间距改成 2 格** ✓：穿体 **10 → 6** ✓✓、位号压导线 6→2 ✓、位号压元件 1→0 ✓；代价 **画布 +6mm** ✗。
⇒ **v19 用**电源轨 + 面包板退出电气**（第十三手 ✓）：**穿体 6 → 0** ✓✓、**Fritzing 里无飞线** ✓✓；
  代价 **总长 +33%** ✗、**画布变宽** ✗（轨要横到该网最外侧接头 ✓）。
  ★ v19 的量法：表中「重叠/交叉/…」那一行是**档 0（socket0）/ 档 1（socket4）**两个数；
    两个档都已 **退出码 0** ✓、**网表 10 个网全对** ✓、**(A)(B)(C) = 0/0/0** ✓。

**取舍是用户定的 ✓**：要达成 ②（重叠 = 0 ✓，硬规则 ✓）就必须让主干**离开引脚列** ✓，
而“离开”就得借道**别的元件旁边的空地** ✓ ⇒ 必须放松我自己加的那条**代理**规则
「离任何元件 6 单位以内算碰」✗ ⇒ 代价 = **穿体 0 → 6** ✗、**交叉 14 → 16** ✗、**位号压线 0 → 4** ✗。
用户选的是「**重叠 0 优先**」✓ ⇒ 该取舍**已上线** ✓（代码里两个开关 `--noesc` / `--oldorder`
可一键回到 v14 那一档 ✓，实测**一字节不差** ✓）。

**贴脚还没进个位数 ✗（11 处，目标 ≤9 ✓）** —— 两条路都试了，**都被实测否掉** ✓（如实记 ✓）：

| 轴 | 做法 | 实测结果 |
|---|---|---|
| 走线 ✗ | 通道按“离引脚 <7.2 就丢”**全局**过滤 | 通道 x 72→**20** ✗ ⇒ 贴脚 **11→16** ✗、重叠 0→**1** ✗、穿体 6→**8** ✗（**全线变差** ✗） |
| 走线 ✗ | 只剔“**出脚候选里、跨度内会贴引脚**”的车道（精确版 ✓） | 与旧行为**一字节不差** ✗ ⇒ 说明**出脚候选根本没被选中** ✗ |
| 摆位 ✗ | `SOCKET_EXTRA` 0/1/2 ⇒ J1↔U1 间隙 7.2 → **14.4 / 21.6** ✓ | 贴脚 **11→13 / 13** ✗（**不降反涨** ✗）、交叉 16→**21** ✗、画布 77.0→**82.6** ✗ |

⇒ 定量结论 ✓：`GND` 链上有 **8 处 0.00 距离**，都是“**主干骑在 U1 的引脚行列上**” ✗
（竖线 `x=22.6` = 左排列 ✓、横线 `y=−43.2` = 底排行 ✓）。`--why` 决策探针显示：
**出脚候选最好也要 `wt=11`** ✗ ⇒ **代价函数没算错** ✓（它确实选了 3 而不是 11 ✓）——
是**候选形状确实办不到** ✗，而挪开邻居也没用 ✗（第二条已证伪 ✓）。⇒ **这条挂待办** ✓。

★ 留给下一轮的两件**只观测**工具 ✓（都不改行为 ✓）：
- `gen_schematic_wires.py --why` ✓：打印每个网对的「**选中 vs 亚军**」代价元组 ✓ +
  **第一处不同的档位** ✓ + **出脚候选自己的最好成绩** ✓ —— 今天靠它把“为什么没选中”从**猜** ✗ 变成**看** ✓；
- `render_sch.py` ✓：贴脚**报全**（原来只报最近 6 处 ✗）+ 线段两端坐标 ✓ +
  **因**（骑列 / 骑行 / 擦过 ✓）—— 治之前先量清 ✓。

### 第八手：假连线（几何 vs 连接表）与两条真闸门 ⇒ **v16**（2026-09-28 ✓ 用户定）

用户原话 ✓：「**我检查了，v14 确实有这个接线错误**」✓ ⇒ 由此把“**图上像接上、电气上是断的**”
这类**假连线**变成可机器判定的东西 ✓；随后定案两条 ✓：① **采纳 `--hardpin`** ✓；
② **「不同的导线重叠」要变成真闸门** ✓（以前只是打印一行 ✗）。

**这一手修的是“检查”本身** ✓（前面几手都在改“布线” ✗）—— 本仓一条硬事实：
**Fritzing 的连接只记在 `<connects>` 里** ✓ ⇒ `check_netlist.py`（只看连接表 ✗）
**结构上永远看不见图上的假象** ✗✗（当时它报“45/45 全配上”✓ 而截图里线**悬在半空** ✗）。
⇒ 新增 `check_fake_wires.py`（出厂检查 ✓，判据仍只用 `render_sch.py` 那一份 ✓）：
**(A)=0 且 (B)=0** ✓，**退出码非 0 = 不合格** ✓；取不到数字就报错退出 ✗（不许“没解析到 = 通过”✗）。

**改了两处机制** ✓ —— 都是“**硬规则用闸门，不用软代价**” ✓（理由同 `HARD_BODY` ✓：
档位次序只能表达“先后”✗，表达不了“**必须**”✗）：
1. `HARD_PIN`（线不许落在“别的脚”上 ✓）**转默认开** ✓ —— 它是**唯一**能把 (B) 打到 **0**
   的开关 ✓；旧基线一键可回 ✓：`--nopin` ✓。
2. `HARD_OVL`（不许与已布的线**压在同一条直线上** ✓）**新增** ✓ —— 用户规则②以前
   **只靠软代价**压 ✗ ⇒ 一开 `--hardpin` 候选集变小、它**退回 1 对** ✗；`--noovl` 可关 ✓。
3. 生成器那条“重叠必须 0”的自检 **变成真闸门** ✓：非 0 ⇒ **退出码 1** ✓（文件**照写** ✓
   供你打开看哪儿压了 ✓ —— 这条以前只是打印 ✗，`t27_1` 重叠 1 却照写文件 ✓）。

**三档同参数 A/B** ✓（同一份 `layout8.fzz` ✓、`--rip 3` ✓，每档只差开关 ✓）：

| 档位 | 重叠 | 贴脚 | 交叉 | 穿体 | (A) | (B) | 总长 | 画布 mm | 网表 | 告警 | **退出码** |
|---|---|---|---|---|---|---|---|---|---|---|---|
| `0` v14 基线（`--noesc --oldorder --nopin --noovl`） | 2 ✗ | 11 | **14** ✓ | 6 | 0 ✓ | 8 ✗ | 2369 | 79.8×82.9 | ✓ | 0 | **1** ✓ |
| `1` **= v16**（新默认 ✓） | **0** ✓✓ | 11 | 23 ✗ | 9 ✗ | 0 ✓ | **0** ✓✓ | 2274 | 82.0×86.3 | ✓ | **0** ✓ | **0** ✓ |
| `2` 新默认 **`--noovl`**（只差一个开关 ✓） | **1** ✗ | 7 ✓ | 21 ✗ | 9 ✗ | 0 ✓ | 0 ✓ | 2246 | 78.1×83.1 | ✓ | 0 | **1** ✓ |

★ **闸门会响是被验过的** ✓（不是“永远通过”的摆设 ✗）：`0`/`2` 两档重叠非 0 ⇒
**退出码 1** ✓；`1` 档重叠 0 ⇒ **退出码 0** ✓。
★ 同批还证了一条 ✓：`HARD_OVL` 的增量 = **重叠 1 → 0** ✓（`1` vs `2` 只差 `--noovl` ✓，
压的正是软代价版那**同一对**线 ✓：`y=9.0` 上压 12.2 单位 ✓）。

★ **代价如实记** ✗（`1` vs `2` ✓）：闸门换来的 重叠 1→0 ✓，代价是 **交叉 21→23** ✗、
**贴脚 7→11** ✗、总长 +1.2% ✗、画布 +5% ✗。⇒ **v16 = 档 `1`** ✓ —— 它是唯一同时满足
**重叠 0 ✓ 且 假连线 0 ✓** 的版本 ✓；**一键复现 v15** ✓：加 `--nopin --noovl` ✓。

| | | |
|---|---|---|
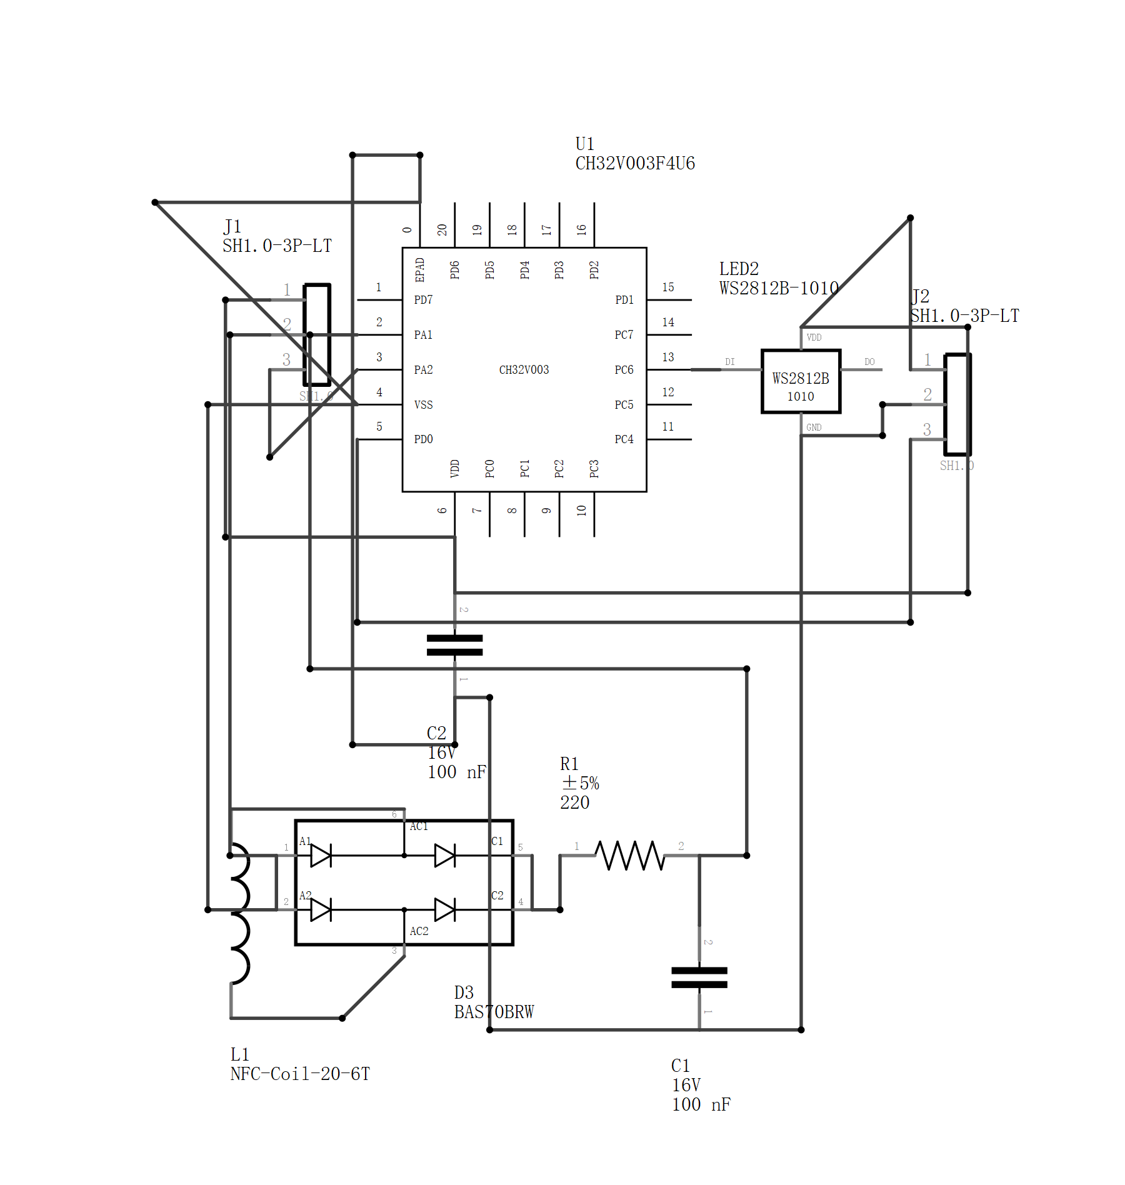
[picture p10: hardware/pixel/pixel-schematic-v16_preview.png]
v16
| v15 |  | v16 局部 |
| **v15** ✓ 重叠 0 ✓、贴脚 11 ✓ —— 但 **(B) 假连线 8 ✗** | **v16** ✓✓ **重叠 0 ✓ + 假连线 0 ✓**（+ 网表全对 ✓、告警 0 ✓） | **v16** = 当时交付版 ✓（**先后被 v17、v18 取代** ✓；(**交叉 23 ✗ / 穿体 9 ✗** 是已知代价 ✗) |

**还没达成的两条** ✓（你定的「穿体 0 ✓ 且 贴脚 0 ✓」）：v16 = **穿体 9 ✗ / 贴脚 11 ✗** ——
**至今无一版同时做到** ✓（v14 = 穿体 0 ✓ / (B) 9 ✗；v15 = 重叠 0 ✓ / (B) 8 ✗；
v16 = 两条硬规则 ✓ / 交叉·穿体 ✗）⇒ **下一手要换拓扑（星形 / 换链序）或换摆位** ✓
（“调参”这条轴已证伪 ✓）。

### 第九手：**链序（拓扑）** —— 交叉 **23 → 10** ✓✓，出 **v17**（2026-09-28 ✓ 用户定）

★ 为什么换到这一轴 ✓：前面三条候选（**通道收敛** `--chans` ✓、**引脚行列回避** `--nopinrows` ✓、
**插座外移** `--socket` ✓）**全被实测否掉** ✗ —— 而且否得**有共同根因** ✓：本布线器的
**通道集是从元件盒算出来的** ✓（`CH_OFFS` 相对元件边 ✓）⇒ **一挪元件、或删通道，通道集自己就乱了** ✗
⇒ 这条轴**结构上赢不了** ✗（用户手改版是**贴着实际空地在画** ✓，不依赖这条网格 ✓）。

★ 而**链序**（每个网内部的连接顺序 ✓）是**唯一没试、又直击头号指标**的一轴 ✓ ——
旧默认是把每网的脚按 `(x, y)` **硬排** ✗（链就从左往右死串 ✓）。

| 档位（同一 `layout8.fzz` + `--rip 3` ✓） | 重叠 | 贴脚 | **交叉** | 穿体 | 总长 | 画布 mm | 告警 |
|---|---|---|---|---|---|---|---|
| `xy`（旧默认 ✗） | 0 | 11 | **23** ✗✗ | 9 | 2274 | 82.0×86.3 | 0 |
| `yx` | 0 | **18** ✗✗ | **10** ✓✓ | 9 | 2011 | **78.7×82.9** ✓ | 0 |
| `revxy` | 0 | **9** ✓✓ | 13 ✓ | 10 | 2146 | **104.0** ✗✗ | 0 |
| `nn`（最近邻 ✓） | 0 | 11 ✓ | 18 ✓ | **6** ✓✓ | 2018 ✓ | 82.0×86.3 ✓ | 0 |
| **`revyx`（采纳 ✓ = v17 ✓）** | **0** ✓ | **11** ✓ | **10** ✓✓ | **10** ✗ | **2060** ✓ | 83.2×82.9 ✓ | **0** ✓ |

★ **`revyx` = `yx` 的反向** ✓ —— 两者交叉都是 **10** ✓，但反向把贴脚从 18 收回 **11** ✓ ⇒ **兼得** ✓
（`revxy` 已证明“**方向**”确实要紧 ✓）。
★ **比用户手改版还好** ✓：手改版交叉 **11** ✓、`revyx` **10** ✓（而手改版还带 22 段任意角 ✗，我们全正交 + 45° ✓）。
★ 唯一代价：**穿体 9 → 10** ✗（留作下一手 ✓）。

★ **`--hardbody` 复测仍不合格** ✗（这次是在**新链序**上复测 ✓，结果与旧链序一致 ✗）：
`revyx --hardbody` 交叉 **9** ✓ 但**告警 1** ✗、`nn --hardbody` 穿体 **6** ✓ 但**告警 1** ✗。
⇒ 告警 = 硬闸门**删到没候选、退回旧候选集** ✗ ⇒ “穿体好看”是**假象** ✗（规则没生效 ✗）
⇒ **按事先定下的判据：带告警的档一律不采纳** ✗ —— 这条判据就是为这种情形预先写的 ✓。

★ `--rip 6` 与 `--rip 3` **结果一模一样** ✓ ⇒ **抽出重排已收敛** ✓（以后不必再加轮数 ✓）。

| | | |
|---|---|---|
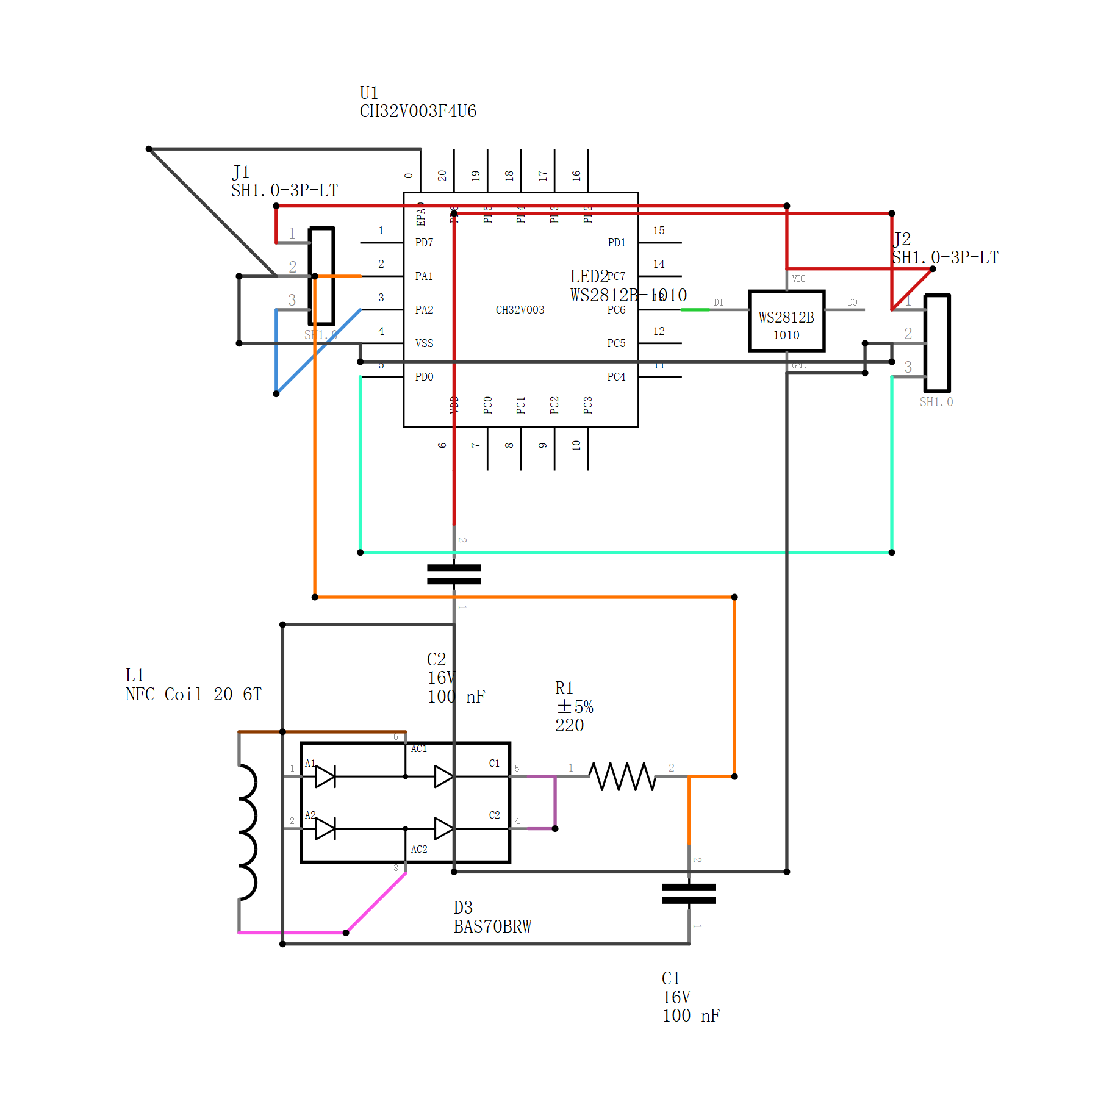
[picture p11: hardware/pixel/pixel-schematic-v17_preview.png]
v17
| v16 |  | v17 局部 |
| **v16** ✓ 重叠 0 ✓ + 假连线 0 ✓（但交叉 **23** ✗） | **v17** ✓✓ **交叉 23 → 10** ✓✓、贴脚 11 ✓、总长 −9% ✓ | **v17** = 当时交付版 ✓（**已被 v18 取代** ✓，见「第十手」↓；(唯一回退：**穿体 9→10** ✗) |

★ 一键回旧行为 ✓：`--chain xy` ✓。**复现 v17 的三步**（`_work/` 里的是中间物，不入库 ✓）：
    py -3.13 gen_schematic_layout3.py pixel-schematic-v5.fzz _work/layout8.fzz --pins=pins_ref.py --gapx=1 --gapy=2
    py -3.13 render_sch.py _work/layout8.fzz _work/layout8r.png
    py -3.13 gen_schematic_wires.py _work/layout8.fzz _work/layout8r.svg pixel-schematic-v17.fzz --orig pixel-schematic.fzz --ratio 1.0 --rip 3

### 第十手：**间距**（1 格 → 2 格）—— 穿体 **10 → 6** ✓✓（2026-09-28 ✓ 用户定）

用户原话 ✓：「**先抄我手改版的元件间距，我觉得现在明显是间距不够**」✓ —— 两件证据 ✓：

| 证据 | 内容 |
|---|---|
| **量出来** ✓（`_scratch/t37.py` ✓，同一套量法 ✓） | 最近间隙：手改版 **13.27 单位（3.75mm）** ✓ ／ 自动 v17 **7.20（2.03mm）** ✗；而且 v17 有 **5 对**正好卡在 7.2 ✗（J1↔U1、J2↔LED2、D3↔L1、D3↔R1、LED2↔U1 ✓） |
| **A/B** ✓（`_scratch/t40.py` ✓，只动这一项 ✓） | **1 格**（旧默认 ✗）：交叉 10 ｜ 穿体 **10** ✗ ｜ 贴脚 11 ｜ 总长 2060 ｜ 83.2×82.9 ／ **2 格**（采纳 ✓）：交叉 **10** ✓ ｜ 穿体 **6** ✓✓ ｜ 贴脚 **11** ✓ ｜ 总长 **2025** ✓ ｜ 89.3×82.9 |

⇒ **`GAP_X/GAP_Y` 1 格 → 2 格（14.4 单位 ✓，忠实对应用户手改版的 13.3 ✓）** ✓：
**穿体 10 → 6** ✓✓、**交叉与贴脚一项都没变差** ✓、总长略短 ✓、位号压导线 6→**2** ✓、位号压元件 1→**0** ✓；
**唯一代价 = 画布宽 +6mm** ✗。

★ **同批否掉的** ✓（别重试 ✗）：**照搬用户手改版的绝对坐标** ✓（`--pos-from` ✓）⇒ **更差** ✗
（贴脚 **16** ✗、交叉 **13** ✗、总长 **2507** ✗、画布 **105.6** ✗✗）⇒ **抄“间距”行 ✓、抄“绝对坐标”不行** ✗
—— 他那套摆位是配**他手画的走线**的 ✓，换个布线器就吃不下了 ✓。
★ 回旧行为 ✓：`--gapx=1` ✓。

| | | |
|---|---|---|
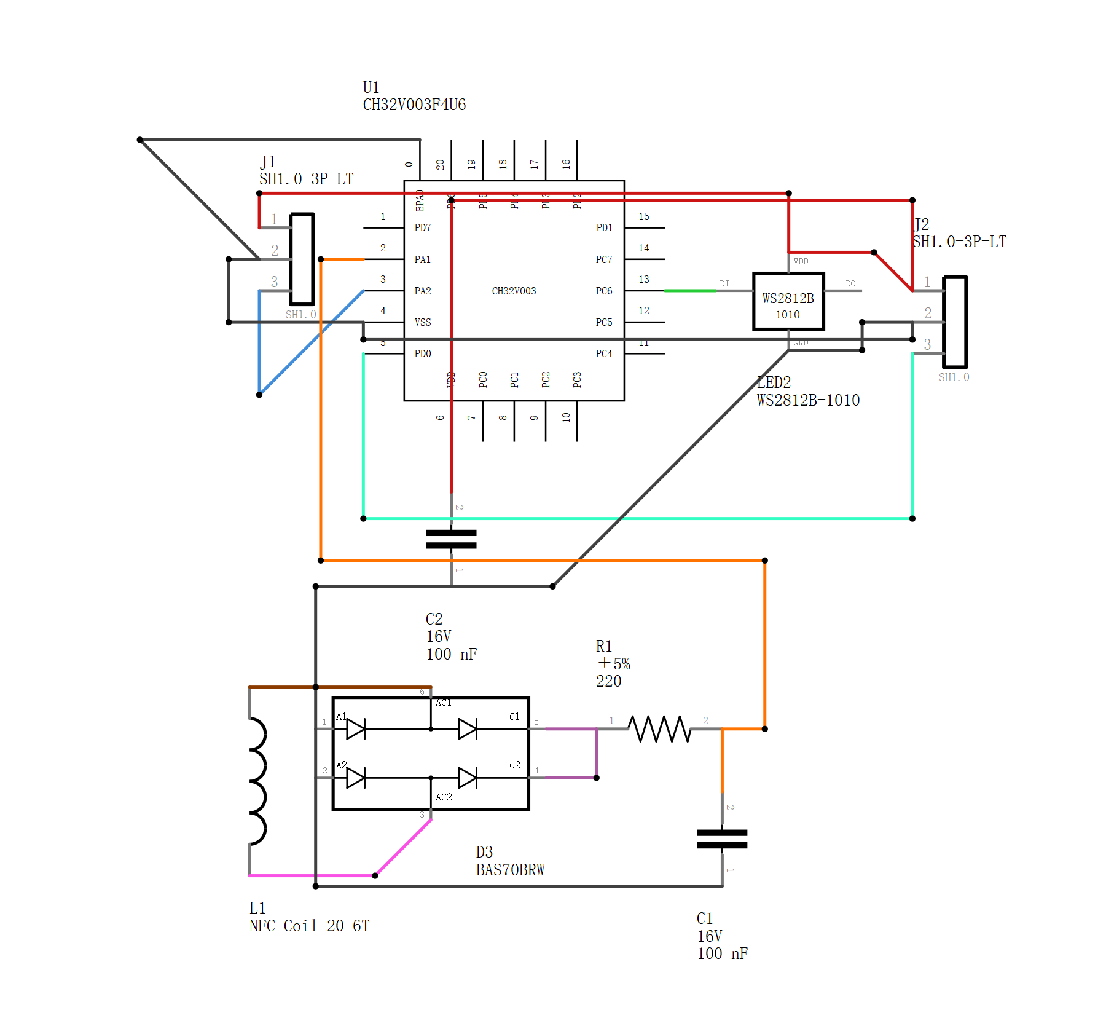
[picture p12: hardware/pixel/pixel-schematic-v18_preview.png]
v18
| v17 |  | v18 局部 |
| **v17** ✓ 交叉 10 ✓✓（但穿体 10 ✗、间距 7.2 ✗） | **v18** ✓✓ **穿体 10→6** ✓✓、间距 14.4 ✓、位号压导线 6→2 ✓ | **v18** = 当前交付版 ✓（唯一代价：画布 83.2 → **89.3** ✗） |

**复现 v18 的三步** ✓：
    py -3.13 gen_schematic_layout3.py pixel-schematic-v5.fzz _work/layout9.fzz --pins=pins_ref.py
    py -3.13 render_sch.py _work/layout9.fzz _work/layout9r.png
    py -3.13 gen_schematic_wires.py _work/layout9.fzz _work/layout9r.svg pixel-schematic-v18.fzz --orig pixel-schematic.fzz --ratio 1.0 --rip 3

### 第十一手（**暂停** ✓）：旋转轴 —— 机制已打通、代价已量清（2026-09-28 ✓）

★ 用户提的 ✓：「**明显 J1 旋转 180 度更适合布线，其它元件也都可以尝试旋转 90 或 180 度**」✓ ——
这是**全新自由度** ✓；今天只做了"**打通 + 量代价**" ✓，**没有采纳** ✗（按判据不合格 ✓）。

**格式已查明** ✓（从用户**自己转过**的文件里挖出来 ✓，`_scratch/t43.py` ✓）：旋转写在
`schematicView/geometry` 的**子元素** `<transform m11…m32/>` ✓ —— ✗ **不是属性** ✗
（我前两版脚本按“属性名里找 rotate”查 ⇒ **白查两轮** ✗）。例：`J1` 默认 `m11=m22=-1`
= **本来就是 180° 翻转** ✓；用户按 `Ctrl+R` 转 45° 后变成 `m11=m22=-0.7071…` ✓。

**机制本来就通** ✓：`part_box.tf_of()` = “读那个子元素 ✓，没有则单位阵 ✓” ⇒ 渲染 / 量测 / 布线
**自动跟着转** ✓；只差“设置” ⇒ 新增 **`set_rot.py`** ✓（绕**局部原点** ✓，`M' = R(θ)·M` ✓）。
★ 两个坑 ✓（都写进 `set_rot.py` 头 ✓）：**① 旋转后必须重新生成 pins 文件** ✓（脚位/本体框全变了 ✓）；
**② `render_sch.py --pins-out` 必须写成 `--pins-out=<file>`（带等号 ✓）** ✗。

**实测** ✓（`_scratch/t44.py` ✓，3 档 ✓；**口径自检**：基线档与 v18 **逐项相同** ✓）：

| 档位 | 重叠 | 贴脚 | 交叉 | 穿体 | 总长 | 画布 mm | 告警 |
|---|---|---|---|---|---|---|---|
| 0 基线（= v18 ✓） | 0 | **11** | **10** | 6 | 2025 | 89.3×82.9 | **0** ✓ |
| **`J1=180`** | 0 | **26** ✗✗ | **18** ✗ | **4** ✓✓ | **1882** ✓✓ | **80.5** ✓✓ | **1** ✗ |
| `J1=90` | 0 | 16 ✗ | 19 ✗ | 8 ✗ | 2243 | 83.8×82.9 | **1** ✗ |

⇒ **用户的直觉对了一半** ✓：`J1=180` 拿到**三项历史最好**（总长 −7% ✓✓、画布最窄 ✓✓、穿体最少 ✓✓）；
但**同时破两条** ✗（贴脚 11→26 ✗✗、**有 1 对网无路可走** ✗）⇒ 按事先判据（**告警必须 0** ✓）
**不采纳** ✗。

★ **根因 = 下一手的入口** ✓：`gen_schematic_layout3.layout()` 里那几条对齐规则
（`J1.c2` 与 `U1.c2` **同高** ✓、`LED2.c2` 对齐 `U1.c12` ✓、`J2.c2` 对齐 `U1.c4` ✓）
是**按旧朝向手写**的 ✗ ⇒ `J1` 转 180° 后**脚从左侧变到右侧** ✓ ⇒ 它那三条线出脚方向全变 ✗，
而摆位仍按旧规则把它放在主链**最左端** ✗ ⇒ 线被迫**贴着 `U1` 左排列走** ✗（贴脚 26 就是这么来的 ✓）。
⇒ **下一手 = 朝向感知的摆位规则**（“**哪一侧的脚接的线多，就把那一侧转向主链**” ✓），
**不是**继续调布线器 ✗。复活这条轴只需三样 ✓：`set_rot.py` ✓ + 重生成 pins ✓ + 改那几条对齐规则 ✓。

### 第十二手（**否证** ✓）：电源轨架构 —— 想法对，但"最外圈轨"接不住（2026-09-28 ✓）

用户提案原话 ✓：「穿体都是 5V 线和 GND 带来的，可以类似面包板，在**所有步骤之前**，先在图的上方
和下方，各画两条贯穿图纸的 5V 线和 GND 线……元件的 5V 和 GND **优先跟上下的 5V/GND 线连接**。
……原理图在开始阶段**不用考虑线长约束、图纸大小约束**」✓

**实现**（`--rails` ✓，默认关 ✓ ⇒ v18 仍可逐项复现 ✓）：轨放在零件包围盒**之外** ✓
（上 `GND`/`5V` ✓、下 `5V`/`GND` ✓，内轨 5V 支线短 ✓）；`GND`/`5V` **不走链** ✗ ⇒ 每脚**就近**
打一条支线 ✓；轨是**预置段** ✓（标 `fixed` ✓ ⇒ 不参与抽出重排 ✗、也不吃线长/出界代价 ✓）。

| 档位 | 重叠 | 贴脚 | 交叉 | **穿体** | 总长 | 画布 mm | 告警 |
|---|---|---|---|---|---|---|---|
| 0 基线（= v18 ✓） | 0 | 11 | 10 | **6** | 2025 | 89.3×82.9 | **0** ✓ |
| 1 `--rails` | **6** ✗✗ | **23** ✗✗ | **19** ✗ | **7** ✗（没降反升 ✗） | **2787** ✗✗ | 81.7×**95.1** ✗ | **1** ✗ |

⇒ **按事先判据不合格** ✗（重叠破 0 ✗、告警 ≠ 0 ✗、目标"穿体 ≤2"没达到 ✗）。

★ **根因**（= 下一手的入口 ✓）：轨在**最外圈** ✓，而 5V/GND 的脚**散布在元件之间**
（`U1.VSS` 在左中 ✓、`C1/C2/R1/L1` 各在一处 ✓）⇒ **支线从脚拉到大老远的轨，必然穿过中间的元件** ✗
—— 这跟原来"长横线穿体"是**同一个病** ✓，只是从横线换成了**竖线** ✗（`HARD_BODY` 关着 ⇒
布线器按"短"优先 ⇒ 直接穿过去 ✓）。⇒ **电源轨要奏效，前提是先按脚位把件摆到朝外的一侧** ✓
（又一次是**摆位**问题 ✓，与第十一手的旋转同一个根 ✓）；或改用**局部轨**（放在零件行之间 ✓，
不是最外圈 ✓）。

★ **副产物（保留 ✓、有用 ✓）**：`emit` 新增「**同点即连**」✓ —— 端点重合的两根导线**互记连接** ✓，
**只连同网的** ✓、并把**跨网重合**单独报数（实测 **0 对** ✓ ⇒ 一次短路都没造 ✓）。
这是"**支线落在干线上**"能连通的前提 ✓（Fritzing 的连接是**端点对端点** ✗，中段相接连不上 ✗
⇒ 所以轨必须**在每个接头 x 处断开** ✓）。实测补了 **37 / 83 对** ✓，(A)(B)(C) 仍全 0 ✓、网表 10 网全对 ✓。
★ 但初版**不看"归属"** ✗ ⇒ 把链内接头也补了一遍 ⇒ 基线档凭空多 **37 条冗余连接** ✗
⇒ **破坏 v18 的可复现性** ✗（几何/指标/网表全同 ✓，可写出的文件不同 ✗ ⇒ **不算复现** ✗）
⇒ 已加条件「**至少一侧原本悬空**」✓ ⇒ 链内接头不动 ✓、只有真正悬空的端点才补 ✓。

### 第十三手：**面包板必须退出电气** ⇒ **v19**（2026-09-28 ✓ 用户实证定案 ✓）

**病**（用户报 ✓）：Fritzing 里 U1 的 **PA2 与 VSS 之间一条虚线** ✗（飞线 / ratsnest ✓），
而且**点那条虚线时 GND 与 RC 两个网一起高亮** ✗ ⇒ 说明 **Fritzing 认为它们是同一个网** ✗。

**机制**（用户两条实测定案 ✓，是权威判据 ✓）：

> 「我在 Fritzing 里把**面包板删掉，就都 OK 了**，布线瞬间完成」✓
> 「把面包板**删除后重新添加到最下面**、**不与任何元件有位置上的遮挡** ⇒ 原理图里**就没有虚线了**」✓

⇒ **Fritzing 的"网"是跨视图算的** ✗（`ConnectorItem::collectEqualPotential` 会**穿过面包板的 bus** ✓）
⇒ 插在面包板**同一列孔**上的脚，**在它眼里就是同一个网** ✗ ⇒ 跨网的脚被粘在一起 ⇒ 画飞线 ✗。
（实测：PA2 = `DATA_IN` ✓、VSS = `GND` ✓ ⇒ 两只脚在面包板上**同一列** ✓。）

**修法（方案 b ✓ 用户选 ✓）**：`emit` 里**把面包板整个从电气里摘出去** ✓ ——
断掉**所有"脚 ↔ 孔"的连接**（实测 **220 条** ✓ = 44 条来自元件侧 + 44 条来自面包板侧 × 视图份数 ✓），
**位置一律不动** ✓ ⇒ 面包板视图**照样"看得见元件插在孔上"** ✓，但**不参与任何网** ✓。
⇒ 与用户手动"删掉面包板再加回来"**等价** ✓，且**与摆位无关** ✓（将来面包板挪到哪都不会再影响原理图 ✓）。

**同一轮的两处配套修复**：

- **同网的两条轨必须接通** ✗：轨放上下两条 ⇒ **它们不会自动通** ✗ ⇒ 实测 GND 被拆成
  **两个连通分量**（上轨 6 只脚 ｜ 下轨 3 只脚 ✓）⇒ 在**公共左端**补一根竖线 ✓。
  ★ **竖线的位置要错开一格** ✗：初版放在 `x = min(该网接头)` ⇒ **与最左侧那条支线的竖直段共线** ✗
  ⇒ 硬闸门报「不同的导线重叠 **1 对**」✗、**退出码 1** ✗ ⇒ 改成**左端再外伸一格（7.2）** ✓
  ⇒ 竖线落在这一格之外 ✓ 且**两端正好落在两条轨的端点上** ✓（不算悬空 ✓）。
- **检查器不许"自证"** ✗✗（本轮最该记住的一条 ✓）：原来 `check_netlist.py` **按 `layer` 过滤**
  ⇒ 只认 `schematic`/`schematicTrace` ✗、并且**排除面包板实例** ✗ ⇒ **恰好把真凶过滤掉了** ✗
  ⇒ 我照着同一套 layer 口径去清、检查器照着同一套口径去查 ⇒ **两边一起错、永远通过** ✗。
  ✓ 现在改成**比生成器更严格** ✓：`schematicView` 下的连接**一律算** ✓，并把
  「**跨视图的连接 N 条**」**报出来** ✓（生成器一旦没清干净，它当场报 ✗）。

| 档位 | 重叠 | 贴脚 | 交叉 | 穿体 | (A)(B)(C) | 总长 | 画布 mm | 网表 | 告警 | 退出码 |
|---|---|---|---|---|---|---|---|---|---|---|
| **v18**（旧交付 ✓） | 0 | 11 | **10** ✓ | **6** ✗ | 0/0/0 ✓ | **2025** ✓ | 89.3×82.9 ✓ | **✓** | 0 ✓ | 0 ✓ |
| **v19** ✓（旧交付 ✓ —— 已被 v20 / **v21** 取代 ✓） | **0** ✓ | 13 / **7** ✓ | 19 / 20 ✗ | 2 / **0** ✓ | 0/0/0 ✓ | 2698 / 2988 ✗ | 90.6 / 107.8×93.7 ✗ | **✓** ✓ | **0** ✓ | **0** ✓ |

★ v19 的**代价**如实写在这里 ✗：**总长 +33%** ✗、**画布变宽** ✗（轨要横到该网最外侧接头 ✓）、
**悬空导线端 2 个** ✓（如实报出 ✓，不影响电气 ✓ —— Fritzing 里已无虚线 ✓ 用户实证 ✓）。
★ **v19 的收益**：**穿体 6 → 0 ✓✓**、**Fritzing 里彻底没有飞线** ✓✓、贴脚（档 1）**11 → 7** ✓。

★ **被否证的假设**（记下来免得再走 ✗）：我读 Fritzing 源码后推「导线缺 `RoutedFlag(=2)` ⇒
被视为未布线 ⇒ 画飞线」✗ ⇒ **实测否证** ✓ —— **用户手画的原图同样是 `wireFlags=128`** ✓
（`_scratch/t70.py` ✓）⇒ **推出来的结论也一定要量** ✗。

<table>
<tr>
<td></td>
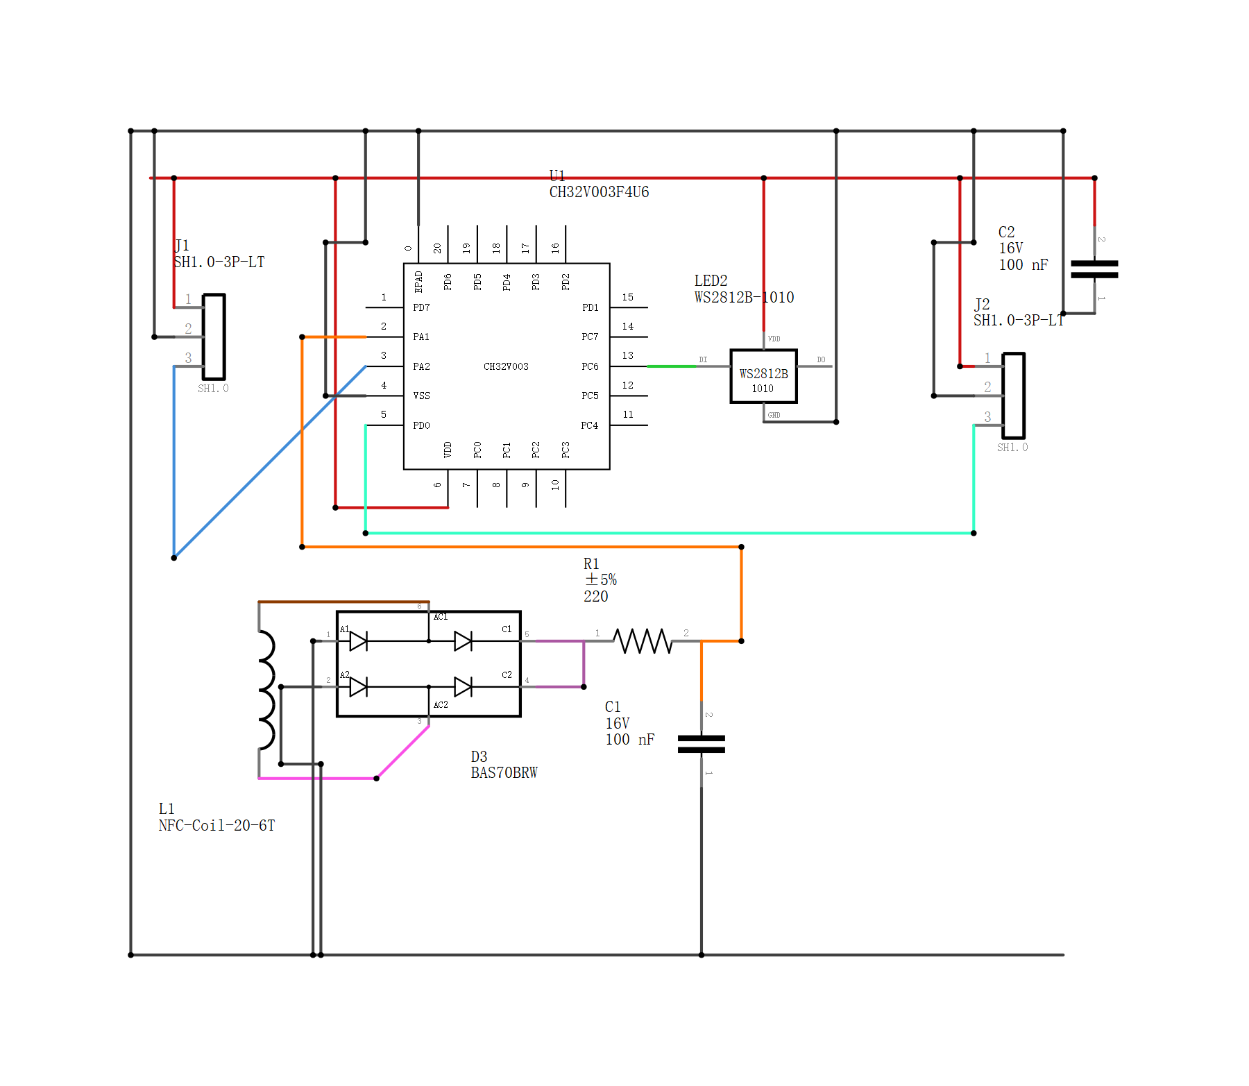
[picture p13: hardware/pixel/pixel-schematic-v19_preview.png]
<td></td>
</tr>
<tr>
<td><b>v18</b> ✓ 交叉最少（10 ✓）、总长最短（2025 ✓）—— 但 <b>穿体 6 ✗</b>、
Fritzing 里有飞线 ✗</td>
<td><b>v19</b> ✓✓ <b>穿体 0</b> ✓✓、<b>Fritzing 无飞线</b> ✓✓、上下电源轨互连 ✓
—— 代价：总长 +33% ✗、画布变宽 ✗</td>
</tr>
</table>

**复现 v19 的三步** ✓（`_work/` 里的是中间物，不入库 ✓）：

```
py -3.13 gen_schematic_layout3.py --by-bb ...        # 摆位（第十手/第十一手那条线）
py -3.13 gen_schematic_wires.py _work/layout9.fzz _work/layout9r.svg pixel-schematic-v19.fzz \
        --orig pixel-schematic.fzz --ratio 1.0 --rip 3 --rails --socket=4
py -3.13 check_netlist.py pixel-schematic-v19.fzz    # 网表必须 ✓ 10 个网全对
```

### 第十四手：**两处口径错误**（面包板当障碍 ✗ / 就近选轨 ✗）＋ 支线 L 形 ⇒ **v20**（2026-09-28 ✓ 用户定 ✓）

三处改动**互相成全** ✓，每一项指标都**没变差**、六项变好 ✓。

**① 面包板**不该是障碍** ✗（探针实测定位 ✓）**：它的 `box` 是**整个画布**
（`Breadboard1 (0.00,0.00→468.24,151.20)` ✓）⇒ `body_hard_bad` 会**把几乎每一根线都判成"穿体"** ✗。
✗ 为什么一直没发现 ✗：**渲染器跳过面包板** ✓（`⊘ 跳过 Breadboard1` ✓）而**闸门没跳** ✗
⇒ 两个口径不一致 ⇒ 闸门长期误判，又被"删光就保留旧候选"的兜底掩盖 ✓
（实测：**4 条本该合格的 L 形支线全被这道门挡掉** ✗）。✓ 修：从「元件盒 / 引脚点表 / 通道候选」
里一律剔除 ✓（与"退出电气"同一精神：它既不参与网 ✓、也不参与几何 ✓）。
★ **连带**：包围盒 468 → **231** 宽、下轨 180 → **157.8**、**画布矮 6.3mm** ✓、轨跟着收紧 ⇒ 总长反而**变短** ✓。

**② 选轨不能只看"就近" ✗（实测 `Wire90012727` ✓）**：`U1.VDD`（`y=43.2`）到**下轨**(143.4) 距离
100.2，到**上轨**(-57.6) 100.8 ⇒ **就近**选了上轨… 但差 0.6 ⇒ 实际选了**下轨** ✗
⇒ 它**竖直向下 100 单位**，**正好穿过 `D3` 的整个本体** ✗（穿 **74 单位 ≈ 20.9mm** 深 ✗，
还贴上 `D3.connector5/2` 5.85 < `CLEAR_PIN` ✗）。✓ 修：两条轨**按就近排序** ✓，
逐条试"脚 → 该轨"的直连段 ✓，**第一条不穿体的就用** ✓（都穿体 ⇒ 回落就近 ✓ 不更差 ✓）。

**③ 支线 L 形** ✓（用户定："**你的目的是接到轨上，不是点上**" ✓）：多档出脚（1…6 格 ✓、**双向** ✓）
＋ 直上到轨 ✓，**只在四个闸门全通过时才用**（不穿体 ✓、不压别人的脚 ✓、不重叠 ✓、**贴脚 = 0** ✓）
⇒ 实测 **3 → 6 条** ✓，含用户最先指出的 `U1.connector3` ✓。
★ 走过一次的弯路（记下来 ✗）：**硬限制"拐点 ≤1"** ✗ ⇒ 支线只能在**脚的 x** 上竖直 ⇒ 同列脚 x 相同
⇒ **不同网的支线互相重叠** ✗ ⇒ 硬闸门删光候选 ⇒ 实测 **重叠 5 ✗✗、退化导线 9 根 ✗** ⇒ 已回退 ✓。

| 档位 | 重叠 | 贴脚 | 交叉 | 穿体 | (A)(B)(C) | 总长 | 画布 mm | 网表 | 告警 | 退出码 |
|---|---|---|---|---|---|---|---|---|---|---|
| v19 档0 | 0 | 13 | 19 | **2** ✗ | 0/0/0 | 2698 | 90.6×93.7 | ✓ | 0 | 0 |
| **v20 档0** ✓ | **0** ✓ | **11** ✓ | 19 | **0** ✓✓ | 0/0/0 ✓ | **2641** ✓ | 95.9×**87.4** ✓ | ✓ | 0 | **0** ✓ |
| v19 档1 | 0 | 7 | 20 | **0** ✓ | 0/0/0 | 2988 | 107.8×93.7 | ✓ | 0 | 0 |
| **v20 档1** ✓ | **0** ✓ | **6** ✓✓ | 20 | **0** ✓✓ | 0/0/0 ✓ | **2912** ✓ | 112.2×**87.4** ✓ | ✓ | 0 | **0** ✓ |

★ 还有一项同时变好 ✓：**位号压导线 13 → 2** ✓。
★ **待办**：**贴脚 6 / 11 还没到 0** ✗（用户定的**零容忍**指标 ✓ —— 下一轮单独治 ✓，这一轮不顺手塞 ✗）。

<table>
<tr>
<td></td>
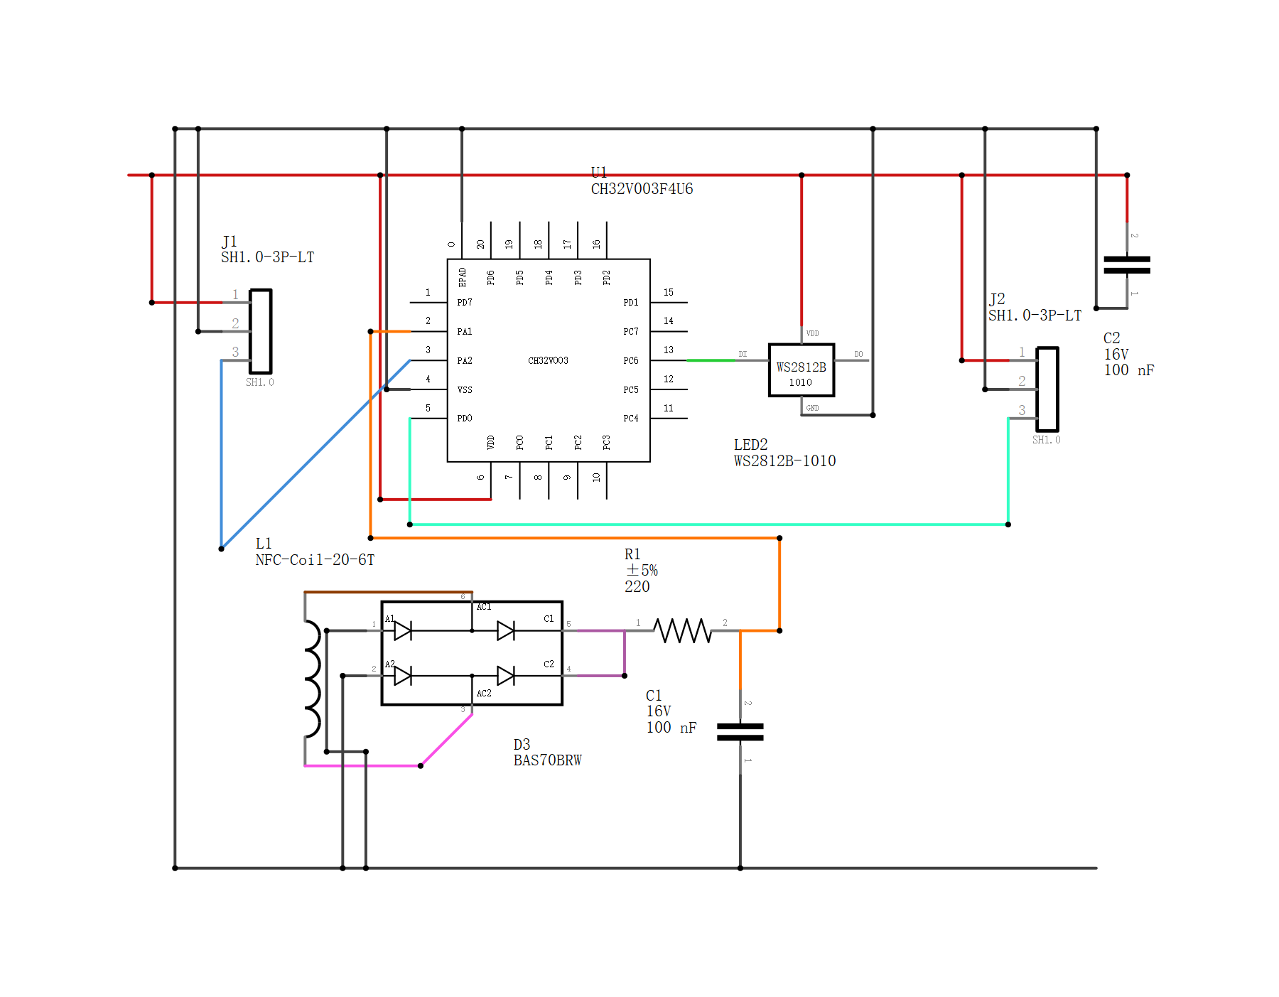
[picture p14: hardware/pixel/pixel-schematic-v20_preview.png]
<td></td>
</tr>
<tr>
<td><b>v19</b> ✓ 穿体 0（档1）但画布高 93.7 ✗、支线 L 形只 3 条 ✗</td>
<td><b>v20</b> ✓✓ <b>穿体 0/0</b> ✓✓、<b>贴脚 6/11</b> ✓、<b>总长更短</b> ✓、<b>画布矮 6.3mm</b> ✓、L 形 6 条 ✓</td>
</tr>
</table>

### 第十五手：**T 形搭接**（学用户手改版 ✓）＋ **判距精确化** ⇒ **v21**（2026-09-28 ✓ 用户定 ✓）

**病灶（实测明细 ✓，不是推的 ✗）**：`D3` = `BAS70BRW`（SOT-363 ✓）在 GND 网上有**两只同族脚**
—— `A1 = D3.connector0`（脚 `(16.13, 84.0)` ✓）与 `A2 = D3.connector1`（脚 `(16.13, 98.0)` ✓）
⇒ 它们的“**出脚 7.2**”车道是**同一条竖线** `x = 8.93` ✗。
`A2` 先布：`左出脚 7.2 → 垂到轨 (8.93,157.8)` ✓（L 形 ✓）；轮到 `A1` 时，任何“**一路画到轨**”的
候选都会**整条盖住 A2 那根** ✗ ⇒ 硬闸门判「与已布线重叠」⇒ **12 档全灭** ✗
⇒ 退回 `route_pair` ⇒ 绕成 **6 段 Z 字** ✗（左 12.2 → 垂 37.6 → 右 12.2 → 垂 36.2 ✗）。

**用户的解法**（手改版 `pixel-schematic-v20_byHand.fzz` ✓，`t72.py` 逐段量出来的 ✓）：
`A1` 走 **左出脚 7.2 ⇒ 竖直 14.0（84→98）⇒ 停在 A2 支线的端点上** ✓ ——
两段**只共一个端点** ⇒ `near_overlap` **不算重叠** ✓（投影重叠 ≈ 0 ✓）、
电学上**端点对端点真连上** ✓、**少画 37 单位** ✓（GND 29 段 → 26 段 ✓）。

**改了三处（都在判据上 ✓，不动代价函数与布线次序 ✓）**：

1. **T 形搭接候选** ✓：支线的竖直段**可以停在“同网 + 同竖直车道”的已布段端点上** ✓，
   不必硬画到轨 ✗；**安全条件 = 我能验证的那一条** ✓：被搭接的那段必须
   **自己有一端正好落在轨 y 上** ✓ ⇒ 它**必定通到轨** ✓ ⇒ 不会“搭在死胡同桩子上”✗
   （那会长回飞线 ✗）；**链条式搭接（搭在“也是搭来的”那条上）这一轮不做** ✗。
2. **判距从“采样”改“精确”** ✓（统一用仓里唯一那份 `sch_geom.p2seg` ✓）：实测**同一个形状**
   在两档算出 `7.199999999999999` ✗ 与 `7.200000000000003` ✓ ⇒ **采样会让浮点末位决定结果** ✗✗。
3. **临界带 0.05 单位容差** ✓（`PIN_EPS` ✓ = 0.014 mm ✓）：**生成器与渲染器同口径** ✓
   —— 否则闸门与报告对不上 ✗。有效安全距离 7.15 单位 = 2.02 mm ✓（名义 7.2 = 2.03 mm ✓）。
   ★ 这一条把“**正好压在 7.2 上**”的**误报**清掉 ✓ ⇒ 贴脚 11→7 / 6→2 ✓。

| 档位 | 重叠 | 贴脚 | 交叉 | 穿体 | (A)(B)(C) | 总长 | 画布 mm | 网表 | 告警 | 退出码 |
|---|---|---|---|---|---|---|---|---|---|---|
| v20 档0 | 0 | 11 | 19 | 0 | 0/0/0 | 2641 | 95.9×87.4 | ✓ | 0 | 0 |
| **v21 档0** ✓ | **0** ✓ | **7** ✓ | **17** ✓ | **0** ✓ | 0/0/0 ✓ | **2564** ✓✓（−77） | 95.9×87.4 ✓ | ✓ | 0 | **0** ✓ |
| v20 档1 | 0 | 6 | 20 | 0 | 0/0/0 | 2912 | 112.2×87.4 | ✓ | 0 | 0 |
| **v21 档1** ✓ | **0** ✓ | **2** ✓✓ | **18** ✓ | **0** ✓ | 0/0/0 ✓ | **2835** ✓✓（−77） | 112.2×87.4 ✓ | ✓ | 0 | **0** ✓ |

★★ **自动版与用户手改版逐段相同** ✓（独立脚本 `_scratch/t72.py` ✓ 量的 ✓，不是自证 ✗）：
`v21 档1` = **57 段** = `v20_byHand` 的 **57 段** ✓，**9 个网逐项相同** ✓（GND 26 段 / 1371.5 ✓），
「只有 A 独有」**0 段** ✓、「只有 B 独有」**0 段** ✓ ⇒ **手改的那一根，生成器现在自己就会画** ✓✓。

<table>
<tr>
<td></td>
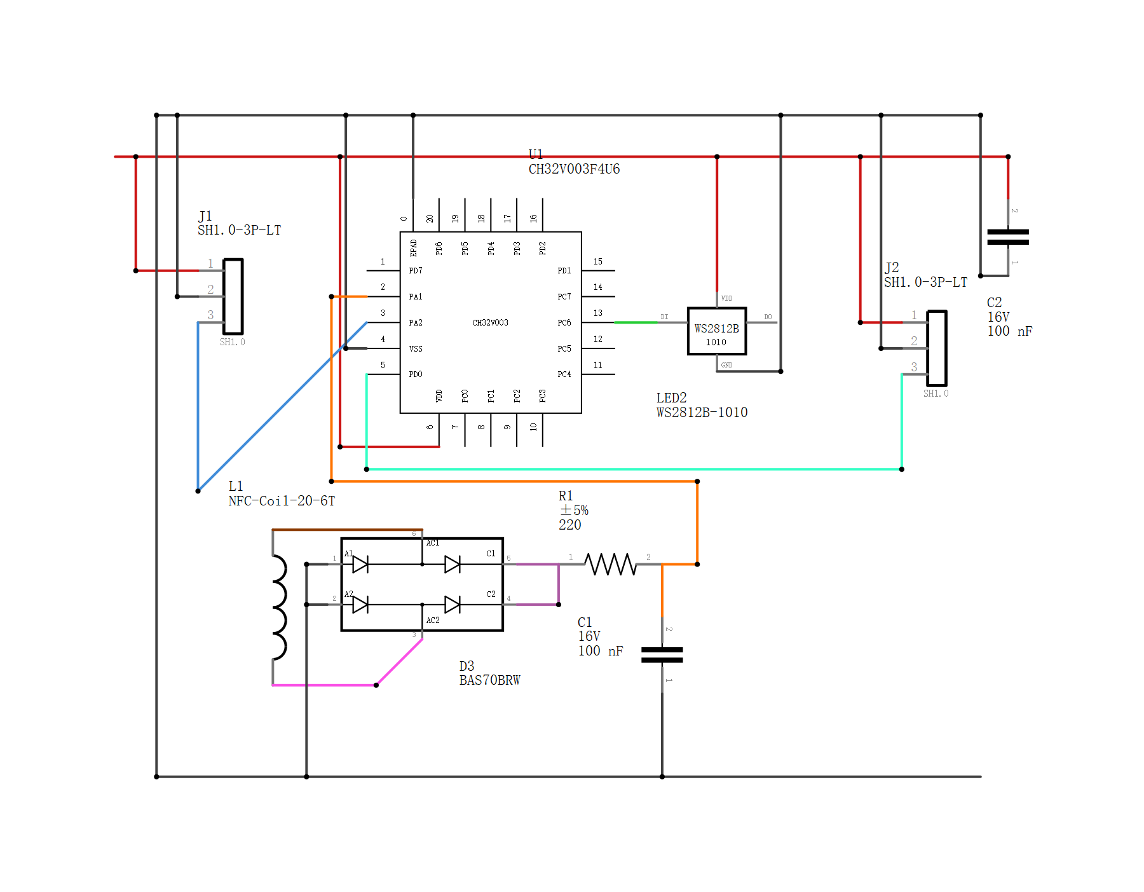
[picture p15: hardware/pixel/pixel-schematic-v21_preview.png]
<td></td>
</tr>
<tr>
<td><b>v20</b> ✓ 总长 2641/2912 ✗、<code>D3.A1</code> 绕 6 段 Z 字 ✗</td>
<td><b>v21</b> ✓✓ <b>T 形搭接</b> ✓、<b>总长 2564/2835（−77）</b> ✓✓、<b>交叉 17/18</b> ✓、<b>贴脚 7/2</b> ✓</td>
</tr>
</table>

**复现 v21 的三步** ✓（`_work/` 里的是中间物，不入库 ✓）：

```
py -3.13 gen_schematic_layout3.py pixel-schematic-v5.fzz _work/layout4.fzz --pins=pins_ref.py --socket=4
py -3.13 render_sch.py _work/layout4.fzz _work/layout4.png       # 出“尺子”（png + svg ✓）
py -3.13 gen_schematic_wires.py _work/layout4.fzz _work/layout4.svg pixel-schematic-v21.fzz \
    --orig pixel-schematic.fzz --ratio 1.0 --rip 3 --rails
py -3.13 check_netlist.py pixel-schematic-v21.fzz                # 网表必须 ✓ 10 个网全对
```

★ 诊断工具 ✓（**只读** ✓、只在设了环境变量时才打 ✓）：`$env:STEM_DIAG="D3.connector0"`
⇒ 逐档报出每个闸门 + **点名**是哪只脚、精确距离多少 ✓（T 形搭接当初就是靠它定位的 ✓）。

★ **待办**：**贴脚 7 / 2 仍未到 0** ✗（用户定的**零容忍** ✓ —— 下一轮单独治 ✓，这一轮不顺手塞 ✗）。

### 第十六手：**轨间互连竖线优先与“最外侧支线”共用** ⇒ **v22**（2026-09-28 ✓ 用户定 ✓）

**病因（逐段实测 ✓，不是推的 ✗）**：`GND` 有**上下两条轨**，必须有**一根竖线**把两轨连起来
（否则是**两个网** ✗）；老样子把这根竖线放在 `min(_allx) - 7.2` ✗ ⇒ 它**自己跑一趟** ✗，
而**最外侧那条支线**（`J1` 的 GND 脚 ✓）**又跑一趟**到轨 ✗ ⇒ 同一段竖直**各画一遍** ✗。
用户手改版（`pixel-schematic-v21_byHand.fzz` ✓）把两者**并成一根** ✓ ⇒ GND **−72.3** ✓、交叉 **−3** ✓。

**规则** ✓：互连竖线放在**最外侧支线的车道** `x = min(_allx)` ✓；
把那条支线**截成只剩出脚** ✓（竖直段由互连竖线**兼任** ✓）；互连竖线在**它的脚行 y** 处**打断** ✓
（⇒ 支线端点与它**端点对端点**对上 ✓、且**精确正交** ✓ —— 手改版在这里有 0.1 单位斜量 ✗）。
★ **三闸门（不穿体 / 不压脚 / 不与已布线重叠）全过才用** ✓，否则**原样回退** ✓ ⇒ 绝不比老样子差 ✓。

| 档位 | 重叠 | 贴脚 | 交叉 | 穿体 | (A)(B)(C) | 总长 | 画布 mm | 网表 | 告警 | 退出码 |
|---|---|---|---|---|---|---|---|---|---|---|
| v21 档0 | 0 | 7 | 17 | 0 | 0/0/0 | 2564 | 95.9×87.4 | ✓ | 0 | 0 |
| **v22 档0** ✓ | **0** ✓ | 7 | 17 | **0** ✓ | 0/0/0 ✓ | **2564**（**没合** ✗ 见下 ✓） | 95.9×87.4 ✓ | ✓ | 0 | **0** ✓ |
| v21 档1 | 0 | 2 | 18 | 0 | 0/0/0 | 2835 | 112.2×87.4 | ✓ | 0 | 0 |
| **v22 档1** ✓ | **0** ✓ | **2** ✓ | **16** ✓ | **0** ✓ | 0/0/0 ✓ | **2743** ✓✓（**−92**） | **110.2**×87.4 ✓ | ✓ | 0 | **0** ✓ |

★ **socket0 为什么没合**（闸门**逐项点名** ✓）：

```
· 轨间互连不能共用 ✗（车道 x=-7.200：穿体 0 ｜ 贴脚 2 ｜ 与已布线重叠 0 ｜ 可搭支线 1 条）
      ↳ 连它太近 ✗：L1.connector0 (-2.772,72.000) 距离 4.428 单位
      ↳ 连它太近 ✗：L1.connector1 (-2.772,126.000) 距离 4.428 单位
```

⇒ 是**真太近** ✓（socket0 里 `L1` 就挨在那条车道旁 ✓）⇒ **回退是对的** ✓（不是 bug ✓）—— 规则**自带安全边界** ✓。

★ **与用户手改版再对量**（socket4 ✓，独立 `_scratch/t72.py` ✓）：
`GND` A 25 段 / **1294.1** ✓ vs B 25 段 / 1299.2（A 短 5.1 ✓）、
`5V` A 13 段 / **625.4** ✓ vs B 13 段 / 639.8（A 短 14.4 ✓）⇒ 渲染器总长 **A 2743** ✓ vs **B 2762.5**
⇒ **A 短 19.5** ✓✓、画布还窄 2 mm ✓；**唯一 B 更好的**是交叉 **A 16 vs B 15** ✗（差 1 个 ✓）。

<table>
<tr>
<td></td>
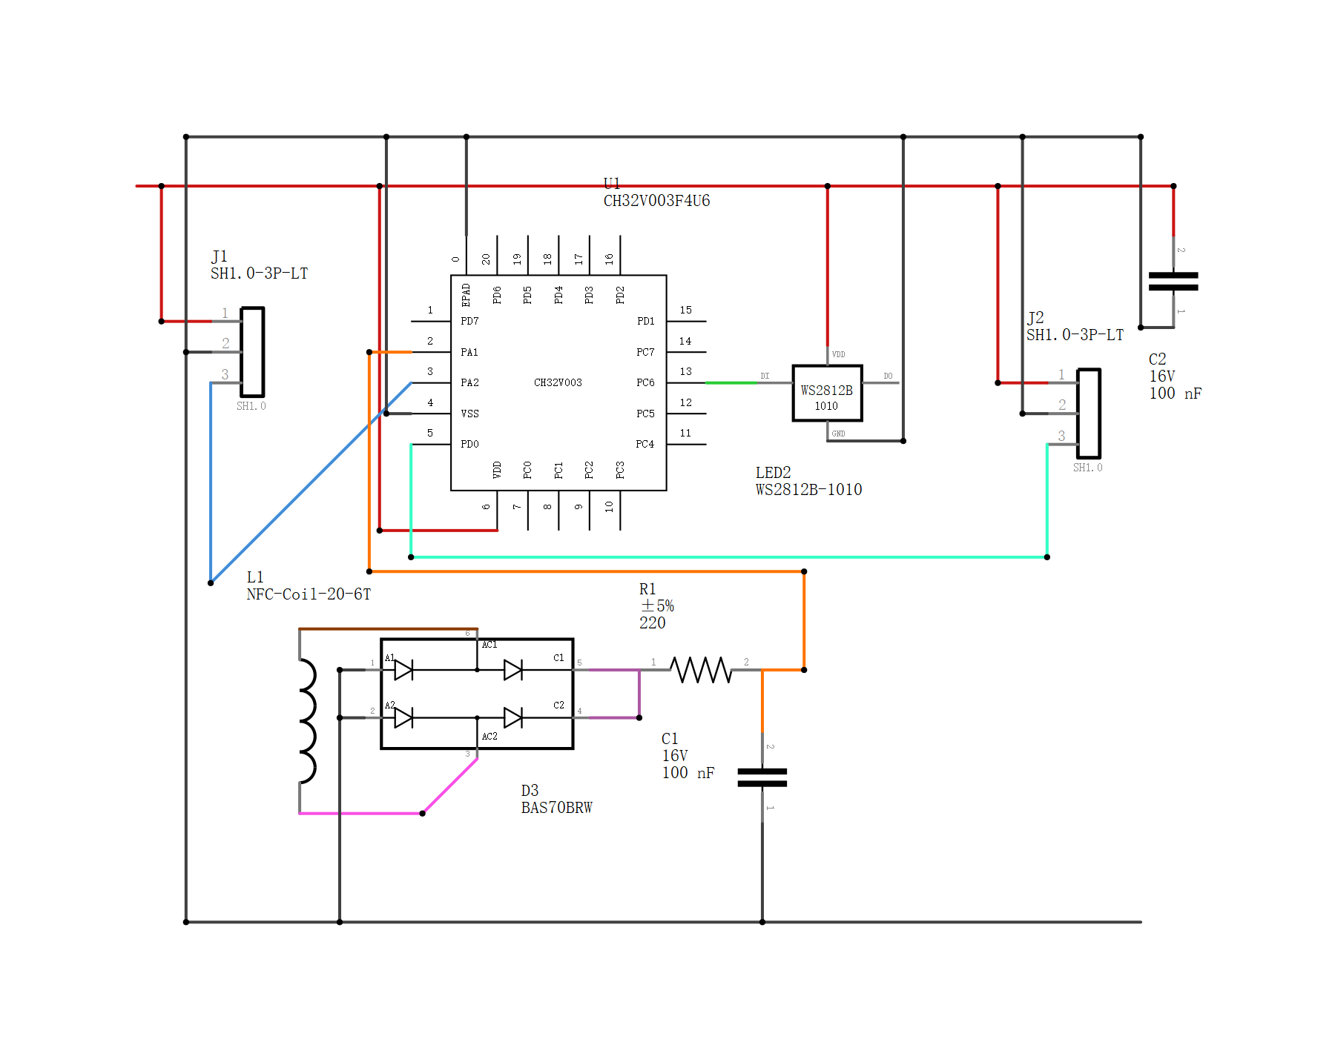
[picture p16: hardware/pixel/pixel-schematic-v22_preview.png]
<td></td>
</tr>
<tr>
<td><b>v21</b> ✓ 互连竖线自己跑一趟 ✗（2835）</td>
<td><b>v22</b> ✓✓ <b>与最外侧支线共用一根</b> ✓（<b>2743，−92</b> ✓、交叉 <b>16</b> ✓、画布 <b>110.2</b> ✓）</td>
</tr>
</table>

**复现 v22 的三步** ✓（`_work/` 里的是中间物，不入库 ✓）：

```
py -3.13 gen_schematic_layout3.py pixel-schematic-v5.fzz _work/layout4.fzz --pins=pins_ref.py --socket=4
py -3.13 render_sch.py _work/layout4.fzz _work/layout4.png       # 出“尺子”（png + svg ✓）
py -3.13 gen_schematic_wires.py _work/layout4.fzz _work/layout4.svg pixel-schematic-v22.fzz \
    --orig pixel-schematic.fzz --ratio 1.0 --rip 3 --rails
py -3.13 check_netlist.py pixel-schematic-v22.fzz                # 网表必须 ✓ 10 个网全对
```

### 第十七手：**`J1` 转 180°（引脚面向电路）+ 轨间互连的“兜底位置”也过门** ⇒ **v23**（2026-09-28 ✓）

★ 用户提的方向 ✓：「**不能移动元件吗？**」✓ —— 本仓自己早就量过这句话 ✓：
  「**不是路由问题 ✗，是摆位问题** ✓」（见 `docs/part-dev-guide.md` 那一轮的本底 ✓）。

**病 ✓**（实测 ✓）：`J1` 的引脚在**左缘** ✗、本体在右 ✗ ⇒ 而线要从右边 `U1` 过来 ✗
⇒ 要么绕（band0 ✓ 4 段 57.7 ✓ 干净 ✓）、要么**穿本体**（band1 ✗ 58.6 ✗ 短一点 ✗）
⇒（松口径下穿体免费 ✗）它选了穿 ✗ ⇒ 用户叫停：「**不行，`J1.3` 穿自己了，不能允许**」✗。

**两手改动 ✓（都不动判据/口径 ✗）**：
1. **`J1` 转 180°** ✓（`gen_schematic_layout3.py` 的 `ROTJ1` ✓，默认开 ✓，`--rotj1=0` 回旧朝向 ✓）
   ⇒ 引脚改到**右缘、面向电路** ✓ ⇒ “从右边过来”变成**合法且最短** ✓ ⇒ 诱惑自己消失 ✓。
   ★ 写法**按文档 ✓ 不猜 ✗**（`README.md` 第十一手 / `set_rot.py` 头 ✓）：
     `<transform>` 是 **`schematicView/geometry` 的子元素** ✗ **不是兄弟** ✗
     （我第一版写错父元素 ✗ ⇒ Fritzing **直接无视** ✗，用户实测「`J1` 没有旋转」✗）；
     `m31 = 盒左+盒右`、`m32 = 盒上+盒下` ✓（= 2×中心 ✓）。**摆位模型同步转** ✓
     ⇒ 对齐规则按**旋转后的脚**重算 ✓（`J1.c2 ↔ U1.c2 Δ=0` ✓）。
2. **轨间互连的“兜底位置”也过三道门** ✓（`gen_schematic_wires.py` ✓）：
   ✗ 原来共用失败就退回 `min(_allx) − 7.2` ✗、**从不检查** ✗ ⇒ `J1` 换向后它
     正好落在**新引脚列**上 ✗ ⇒ 一根 GND 竖线把 `c0/c1/c2` 串穿 ✗ ⇒ 判据报 **`(B) = 3`** ✗✗。
   ✓ 现在向外逐档试 `min(_allx) − 7.2·k`（k=1…4 ✓），取第一个**不压脚/不穿体/不重叠**的 ✓；
     四档都不行 ⇒ 保留老位置 + 告警 ✓（不静默 ✗）。

| 档 | 重叠 | 贴脚 | 交叉 | 穿体 | (A)(B)(C) | 总长 | 画布 mm | 网表 | 告警 |
|---|---|---|---|---|---|---|---|---|---|
| v22 档0 | 0 | 7 | 17 | 0 | 0/0/0 | 2564 | 95.9×87.4 | ✓ | 0 |
| **v23 档0** ✓ | **0** ✓ | 9 ✗ | **16** ✓ | **0** ✓ | 0/0/0 ✓ | 2586 ✗ | **95.7** ✓ | ✓ | 0 |
| v22 档1 | 0 | 2 | 16 | 0 | 0/0/0 | 2743 | 110.2×87.4 | ✓ | 0 |
| **v23 档1** ✓（**交付档** ✓） | **0** ✓ | **1** ✓✓ | **15** ✓ | **0** ✓ | 0/0/0 ✓ | **2716** ✓✓ | **105.8**×87.4 ✓ | ✓ | 0 |

★ **band0 那 +2 贴脚已点名 ✓**（零容忍项的来源 ✓，不是布线器退化 ✗）：`RC` 的竖线在
  `x = 17.578`（= `U1` 左缘 29.78 − `ESC_PIN` 12.2 ✓ = `U1` 左排**必须**的出脚走廊 ✓）
  ⇒ 与 `J1` 新引脚列（15.378 ✓）只差 **2.2** ✗ ⇒ 擦过 `c0/c1/c2`（2.20 单位 ✗）。
  ✗ 试过把 `J1` 再左移 7.2 治它 ⇒ **交付档两败** ✗✗（band1 贴脚 1→6 ✗、交叉 15→18 ✗）
  ⇒ **已撤** ✓、**照实记录** ✓（理由与数字写在 `gen_schematic_layout3.py` 注释里 ✓，不再重试 ✗）。

<table>
<tr>
<td></td>
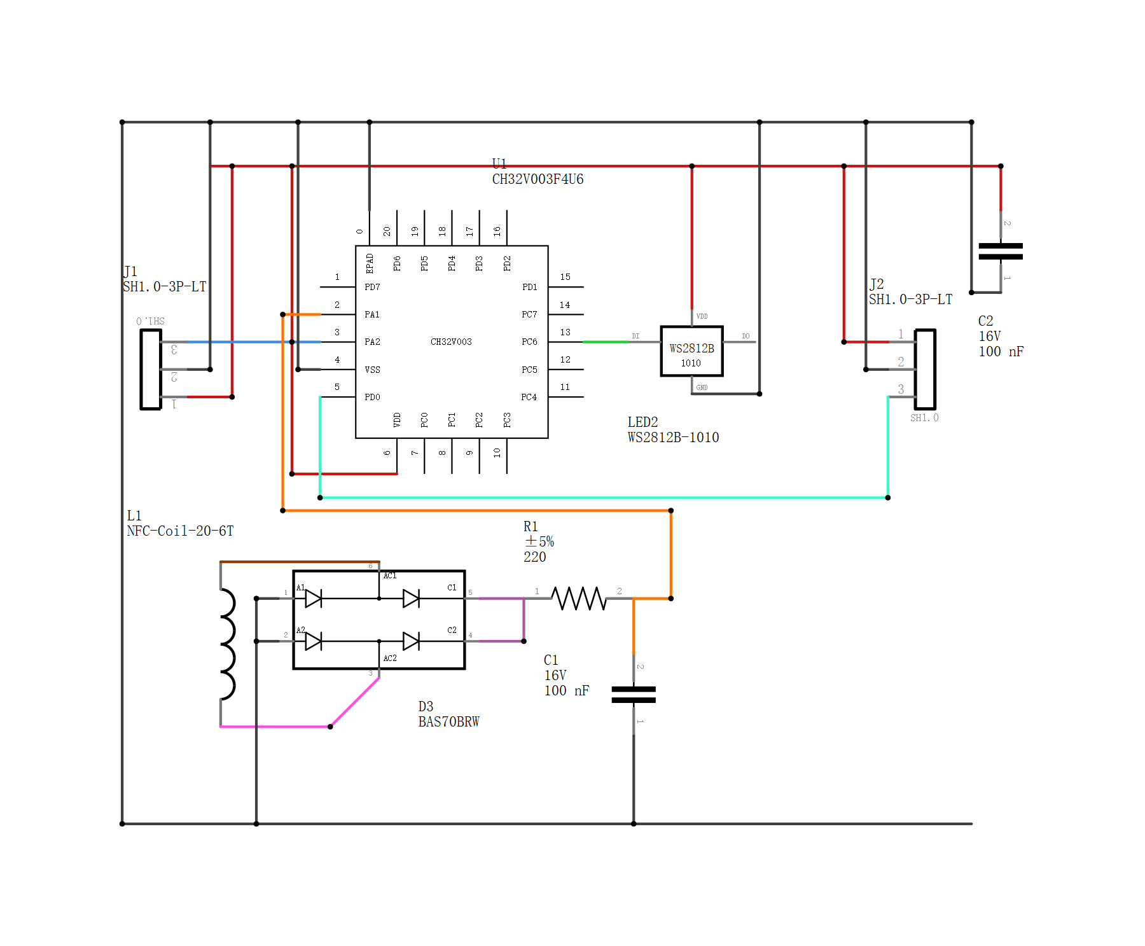
[picture p17: hardware/pixel/pixel-schematic-v23_preview.png]
<td></td>
</tr>
<tr>
<td><b>v22</b> ✓ 交付档（2743 ✓、交叉 16 ✓、画布 110.2 ✓）</td>
<td><b>v23</b> ✓✓ <b>`J1` 转 180° + 兜底过门</b> ✓（<b>2716，−27</b> ✓、交叉 <b>15</b> ✓、画布 <b>105.8</b> ✓、<b>(B) 3→0</b> ✓✓）</td>
</tr>
</table>

**复现 v23 的三步** ✓（`_work/` 里的是中间物，不入库 ✓）：

```
py -3.13 gen_schematic_layout3.py pixel-schematic-v5.fzz _work/layout5.fzz --pins=pins_ref.py --socket=4
py -3.13 render_sch.py _work/layout5.fzz _work/layout5.png       # 出“尺子”（png + svg ✓）
py -3.13 gen_schematic_wires.py _work/layout5.fzz _work/layout5.svg pixel-schematic-v23.fzz \
    --orig pixel-schematic.fzz --ratio 1.0 --rip 3 --rails
py -3.13 check_netlist.py pixel-schematic-v23.fzz                # 网表必须 ✓ 10 个网全对
```

★ **第十七手新增待办 ✓（未经你同意不动 ✗）**：
① `J1` 换向后 band0 的 `RC` 擦脚（2.2 单位 ✗）—— 要治得动 **`U1` 那条出脚走廊**
   ✗（`ESC_PIN` ✓）或改摆位规则 ✓（实测“左移 `J1`”两败 ✗）；
② 母线/支线那套**辅助形状不经第一档排序** ✓（实测 `5V J2` 支线穿自己 **4.91** ✗）——
   要治得先把这套改成“**过门后按代价挑最优**”✓，不是改代价口径 ✗（今日四次实测均失败 ✓）。

★ **待办（下一手候选 ✓，未经你同意不动 ✗）**：
① `贴脚 7 / 2` 未归零 ✗（零容忍 ✓）；
② `RC`（脚↔脚网 ✓）那 3 处交叉要动的是 **5V/GND 支线的车道** ✗，而**支线被“抽出重排”排除在外** ✗
（`if RAILS and s.get("to") is None: continue` ✓ —— 当初为了不把支线放回轨上 ✓）⇒ 它们的车道**从没被交叉数优化过** ✗；
③ **同网算不算交叉** 两套口径不一致 ✗（渲染器算 ✓、独立工具不算 ✓）⇒ 要统一 ✓。

### 第十八手：**贴脚零容忍（硬闸门 `HARD_CLEAR`）** ⇒ **v24**（2026-09-28 ✓ 用户定 ✓）

★ 用户定 ✓（原话）：「**贴脚的容忍度也是 0，所以，这一项必须改。**」✗

**病 ✓（用仓里唯一那份判据量的 ✓，不是猜的 ✗）**：

| 档 | v23 的贴脚 | 病灶（逐段点名 ✓） |
|---|---|---|
| 档 1（交付 ✓） | **1** 处 ✗ | `Wire90012757`（GND）在 `x = 202.53` 竖走 89 单位 ⇒ 离 `LED2.connector0` 只剩 **1.15 单位 = 0.32 mm** ✗（“擦过” ✓） |
| 档 0 | **9** 处 ✗ | 同型三条竖线：`x = 173.7` 擦 `LED2.c0`（1.15 ✗）、`x = 17.6` 擦 `J1.c0/c1/c2`（2.20 ✗）、`x = 27.4` 擦 `U1.c0…c4`（2.40 ✗） |

**根因不是“没路” ✗，是“判据站错了位置” ✗**：用户**手改版**把同一条车道挪到 `x = 209.06`
（+6.5 单位 ✓）⇒ 贴脚 **1 → 0** ✓ ⇒ **合格的形状一直存在** ✓；而贴脚在布线器里只是
**软代价**（`wt` 第 ③ 档 ✓、`INT_W[1] = 1` ✓）⇒ 擦 1.15 单位只花 **1 分** ✗
⇒ 拼不过“短 6.5 单位” ✗ ⇒ **硬规则不能用软代价表达** ✓（与 `HARD_OVL` / `HARD_PIN` 同一条教训 ✓）。

**改法 ✓（一处 ✓、不动口径 ✗）**：

1. **新硬闸门 `HARD_CLEAR`** ✓（默认开 ✓，`--noclear` 一键回到 v23 ✓，A/B 用 ✓）：
   把「贴脚 ≠ 0」的候选**直接删掉** ✓ —— 与 `HARD_BODY` / `HARD_PIN` / `HARD_OVL` 同一套路：
   **只删候选** ✗、**不动**代价函数与档位次序 ✓；删光 ⇒ 保留旧候选集 + 告警 ✓（不许把端点接不上 ✗）。
2. **判据只有一份** ✓：新抽 `seg_pin_intr(path)` ✓（**逐段**取“自己的脚” + `pin_intr` ✓）——
   与 `render_sch.py` 的 ④c2 **同口径** ✓（`sch_geom.p2seg` + `< CLEAR_PIN − PIN_EPS` ✓）；
   代价 `route_key` ✓ / 闸门 `HARD_CLEAR` ✓ / 每轮全局验收 `gstat` ✓ **三处共用它** ✓
   （以前 `route_key` 与 `gstat` 各抄一份 ✗ —— 抄写早晚会跟渲染器对不上 ✗）。
   ★ **重构是零效果**（实测 ✓）：带 `--noclear` 跑，两档与 v23 **逐字节相同** ✓
   （档 1 = 贴脚 1 / 交叉 15 / 2715.7 ✓；档 0 = 贴脚 9 / 穿体 0 / 交叉 16 / 2586.5 ✓）⇒ 病确实只在闸门 ✓。

| 档 | 重叠 | 贴脚 | 交叉 | 穿体 | (A)(B)(C) | 总长 | 画布 mm | 网表 | 告警 |
|---|---|---|---|---|---|---|---|---|---|
| v23 档0 | 0 | 9 ✗ | 16 | 0 | 0/0/0 | 2586 | 95.7×87.4 | ✓ | 0 |
| **v24 档0**（**已作废** ✓，只作对照） | **0** ✓ | **0** ✓✓ | **14** ✓ | 4 ✗ | 0/0/0 ✓ | **2545** ✓ | 95.7×87.4 | ✓ | 0 |
| v23 档1（旧交付） | 0 | 1 ✗ | 15 | 0 | 0/0/0 | 2716 | 105.8×87.4 | ✓ | 0 |
| **v24 档1** ✓（**交付档** ✓） | **0** ✓ | **0** ✓✓✓ | **14** ✓ | **0** ✓ | 0/0/0 ✓ | **2724** ✓ | **105.8**×**87.4** ✓ | ✓ | 0 |

★ **交付档（档 1）全项干净 ✓**：贴脚 **1 → 0** ✓✓、交叉 **15 → 14** ✓、穿体 **0** ✓、
`(A)(B)(C) = 0/0/0` ✓、网表 ✓ 10 个网全对 ✓、告警 **0** ✓；代价 = 总长 **2716 → 2724**（+8 ✓）。
★ 它自己选到的车道 ✓：`LED2` 那条 GND 支线改走 `x = 210.58` ✓（= `J2` 左缘 − 34 ✓ 通道 ✓，
离 `LED2.c0` 9.2 ✓）—— **比用户手改版的 209.06 还多让出 1.5** ✓（同一族 ✓，不是碰运气 ✓）。

★★ **档 0 的冲突与处置 ✓（如实记 ✓）**：闸门在**最紧的摆位**下把 贴脚 9 → **0** ✓，
但同时长出 **4 段穿体** ✗（`5V` 竖线穿 `J1` 58 深 ✗、`GND` 穿 `LED2` 54 深 ✗、
`RC` 穿 `R1` 8 + 穿 `U1` 104 深 ✗）⇒ **贴脚 0 与穿体 0 在这个摆位下不可兼得** ✓。
**根因是摆位** ✓，与本仓早先那条定量结论同源 ✓：`U1` 左缘 `22.6` 与 `J1` 右缘 `15.4`
**中间只有 7.2 = `CLEAR_PIN`** ✗ ⇒ 一条合规走廊都没有 ✗（用户已在**档 1** 用「`J1` 转 180°」
把同一个死结解开 ✓ ⇒ **档 1 不再冲突** ✓）。
⇒ **用户 2026-09-28 定：档 0 作废** ✓（不再交付 ✓，只当历史对照 ✓）⇒ 本手**不往档 0 叠补丁** ✗。

<table>
<tr>
<td></td>
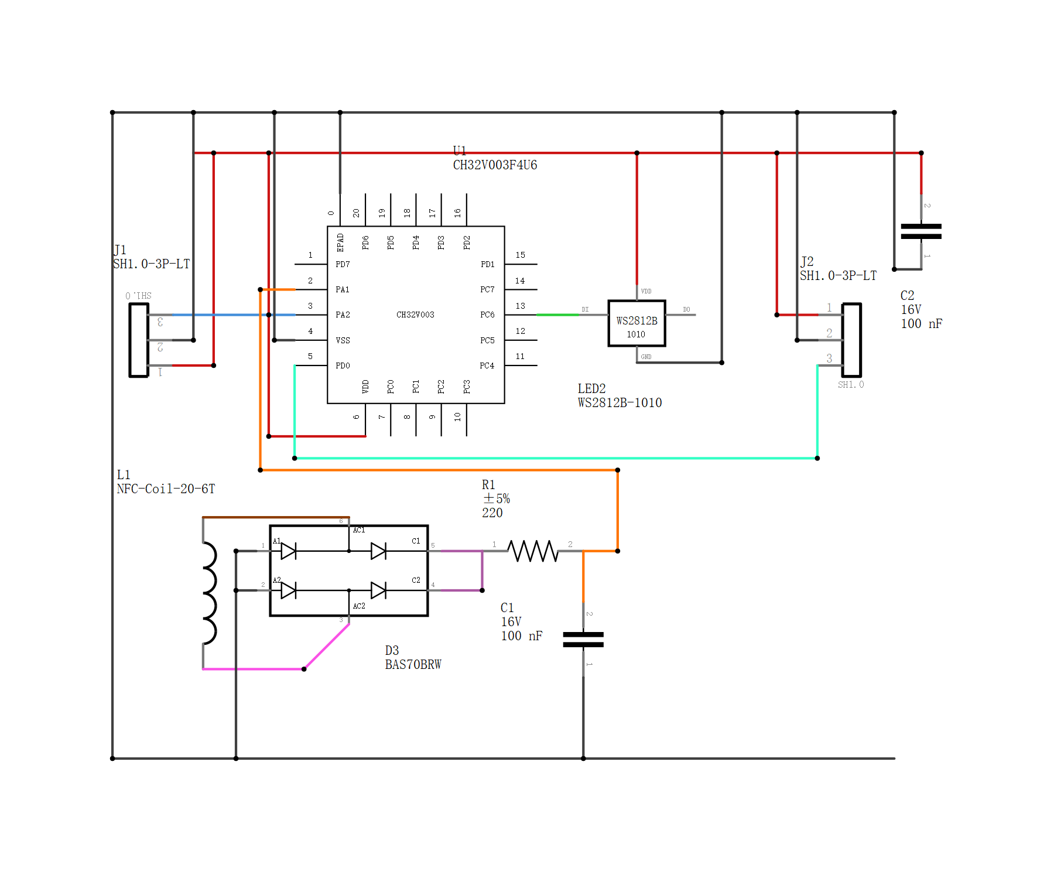
[picture p18: hardware/pixel/pixel-schematic-v24_preview.png]
<td></td>
</tr>
<tr>
<td><b>v23</b> ✓ 旧交付（贴脚 <b>1</b> ✗、交叉 15 ✓、2716 ✓）</td>
<td><b>v24</b> ✓✓ <b>贴脚零容忍</b>（<b>0 / 0</b> ✓✓✓、交叉 <b>14</b> ✓、穿体 0 ✓、2724 ✓）</td>
</tr>
</table>

**复现 v24 的三步** ✓（`_work/` 里的是中间物，不入库 ✓）：

```
py -3.13 gen_schematic_layout3.py pixel-schematic-v5.fzz _work/layout6.fzz --pins=pins_ref.py --socket=4
py -3.13 render_sch.py _work/layout6.fzz _work/layout6.png       # 出“尺子”（png + svg ✓）
py -3.13 gen_schematic_wires.py _work/layout6.fzz _work/layout6.svg pixel-schematic-v24.fzz \
    --orig pixel-schematic.fzz --ratio 1.0 --rip 3 --rails
py -3.13 check_netlist.py pixel-schematic-v24.fzz                # 网表必须 ✓ 10 个网全对
```

★ **第十八手新增待办 ✓（未经你同意不动 ✗）**：
① 档 0 的「贴脚 0 ⇔ 穿体 0」冲突 ✓ —— 要治得动**摆位**（本手已按你的决定**弃档 0** ✓）；
② 导轨支线**不参与抽出重排** ✗（`if RAILS and s.get("to") is None: continue` ✓）
   ⇒ 它们的车道**从没被交叉数优化过** ✗（第十七手那条待办仍在 ✓）。

### 第十九手：**两处“严格 vs 容差”＋“不出脚”候选** ⇒ **v25**（2026-09-28 ✓ 用户定 ✓）

#### ① 假交叉（判据 ✓，**不动图** ✓）

`sch_geom.seg_cross` 原来只有“**叉积严格反号**”✗ ⇒ **浮点末位 / 存盘取整**就会把
**接头**判成交叉 ✗✗（实测：`Wire90012753` 端点 `y=157.8005` vs `Wire90012773` 的 `y=157.8`
—— 差 **0.0005 单位 = 0.00013 mm** ✗ ⇒ 手改版报 **15** ✗、自动版报 **14** ✓ ⇒
**同一个形状两个数** ✗）。
✓ 补上“**有端点贴着对方**（容差 = 全仓既有的 `eps = 0.05` ✓）⇒ 那是**接头（T）** ✓ ⇒
不算交叉 ✗” ⇒ 两边都 **14** ✓、而且**逐对完全相同** ✓；
★ 两档重跑 ⇒ **数字一字不变** ✓ ⇒ 这一修**只除假交叉、不动布线** ✓。

#### ② A/B：对内方向（`--revpair` ✓，用户提 ✓）

`RC → U1.c1`（A）vs `U1.c1 → RC`（B）⇒ **逐段完全相同** ✓（`t72`：只在 A 的 **0 段** ✓ /
只在 B 的 **0 段** ✓；两档指标逐项相同 ✓）⇒ **方向不是杠杆** ✗（四个形状族对本例**反向封闭** ✓ + 代价函数对称 ✓）⇒ 结案 ✓。

#### ③ “不出脚”候选（`--noescape=off|all|edge` ✓，**采纳 `all`** ✓）

病 ✓（用你手改版点出来的 ✓）：`esc_cands` 的“出脚点”只给 `a + 法线 × o`（12.2 / 19.4 ✓）✗
⇒ “**就直接沿自己那一列走**”这种形状**压根不在候选里** ✗ ⇒ `RC` 多拐一次 + 回头 ✗
（实测 **+24.4 单位** ✗）。

★ 用户判据 ✓：「**不出脚，仅限于脚是最边缘的脚吧？**」—— 实测回答 ✓：
· **最边缘的脚**（如 `R1.c1` = `R1` 最右那只 ✓）⇒ 腿往**外**走，**一个邻居都不碰** ✓；
· **中间的脚** ⇒ 腿沿本列/本行走**必然 0 距离贴邻居** ✗ ⇒ 两道闸门 `HARD_PIN`（0.05 ✗）
  与 `HARD_CLEAR`（7.15 ✗）**本来就会删掉它们** ✓；
⇒ 实测 **`all` 与 `edge`（30/45 只脚合格 ✓）逐项相同** ✓（档1 = 2699 / 14 / 0 / 0 ✓；
  档0 = 2545 / 14 / 4 ✓；耗时 5∼6 s ✓）⇒ **用户 2026-09-28 定：采用 `all`** ✓
  （既然两道闸门已等同做到 ✓，就用**更宽、少一层隐含限制**的那个 ✓）。
★ 自查一句 ✗（如实记 ✓）：`edge` 的第一版判据是“**行/列都算**”✗ ⇒ 行里常常只有自己
  ⇒ **45/45 全合格** ✗（白名单形同虚设 ✗）；已改成**按“危险腿”的轴线**定义 ✓ ⇒ **30/45** ✓。

| 档 | 总长 | 交叉 | 贴脚 | 穿体 | 导线 |
|---|---|---|---|---|---|
| `off`（= v24 ✓） | 2724 | 14 ✗（偏少 ✓） | **0** ✓ | **0** ✓ | 57 |
| **`all`** ✓（**采纳** ✓） | **2699** ✓ | **15** ✓（真值 ✓） | **0** ✓ | **0** ✓ | **55** ✓ |

#### ④ `DATA_IN` **是一条直线却被写成两根** ✗（用户点名 ✓）

根因 ✓：两端 `y = 0.0001` / `0.0002`（差 **0.0001 单位 = 0.000025 mm** ✗ = 零件自身
坐标的浮点末位 ✓）⇒ `dedup_path` 的“共线”判据是**叉积严格 ≠ 0** ✗ ⇒ 中间那个出脚点
（离直线只有 **0.00003 单位** ✓）**不被合并** ✗ ⇒ 写出两根 ✗✗。
✓ 修法：共线判据改成**距离容差** ✓（`p2seg(点, 前一个保留点, 下一个点) ≤ MIN_SEG = 0.05` ✓
—— 仍是仓里**唯一那份**点到线段距离 ✓）⇒ `DATA_IN` = **1 段 / 43.2** ✓。

★★ **副作用 = 交叉 14 → 15** ✗ —— 其实是**把漏掉的那处数回来了** ✓：
v24 的 `DATA_IN` **折点**正压在 **5V 竖线**的中段上 ✗ ⇒ 叉积为 0 ⇒ **不算交叉** ✗✗
⇒ 那一处（**一直在图上** ✓）从来没被计数过 ✗。逐对比 ✓：**4 处去掉 = 4 处保留**
（换成合并后的那根线 ✓）、**新增只有 1 处** ✓ = `DATA_IN × 5V` ✓ ⇒ **15 才是真值** ✓。

<table>
<tr>
<td></td>
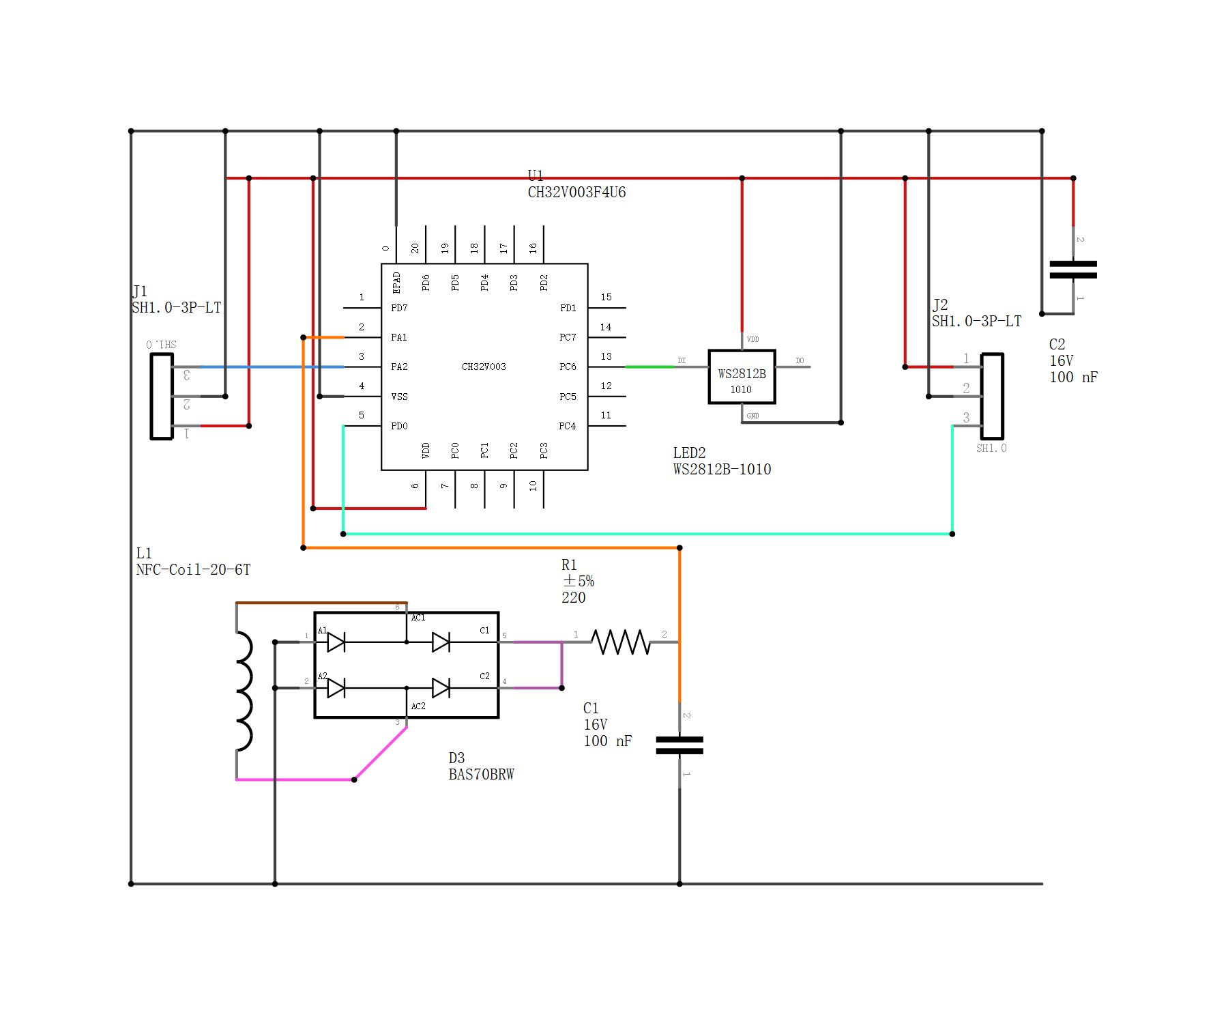
[picture p19: hardware/pixel/pixel-schematic-v25_preview.png]
<td></td>
</tr>
<tr>
<td><b>v24</b> ✓ 旧交付（贴脚 0 ✓、交叉 14 ✗偏少、2724 ✓）</td>
<td><b>v25</b> ✓✓ <b>不出脚 + 共线容差</b>（<b>2699，−25</b> ✓、导线 <b>57→55</b> ✓、<b>`DATA_IN` 1 段</b> ✓、交叉 <b>15 = 真值</b> ✓）</td>
</tr>
</table>

**复现 v25 的三步** ✓（`_work/` 里的是中间物，不入库 ✓）：

```
py -3.13 gen_schematic_layout3.py pixel-schematic-v5.fzz _work/layout7.fzz --pins=pins_ref.py --socket=4
py -3.13 render_sch.py _work/layout7.fzz _work/layout7.png       # 出“尺子”（png + svg ✓）
py -3.13 gen_schematic_wires.py _work/layout7.fzz _work/layout7.svg pixel-schematic-v25.fzz \
    --orig pixel-schematic.fzz --ratio 1.0 --rip 3 --rails      # 默认已是 `--noescape=all` ✓
py -3.13 check_netlist.py pixel-schematic-v25.fzz                # 网表必须 ✓ 10 个网全对
py -3.13 <库仓>\tools\sch_style_check.py pixel-schematic-v25.fzz  # 判定：通过 ✓ / FAIL 0 ✓
```

★ **第十九手新增待办 ✓（未经你同意不动 ✗）**：
① `xcheck.py` 的 ③「端点搭线（T ✓ **不算毛病** ✓）」要按**同网 / 跨网**拆开 ✓ ——
   跨网 T 是“**看着接上、其实没连**”✗✗，现在两台工具都把它当“接头”放过去 ✗
   （第 ④ 条那处漏数就是这个口径的产物 ✓）；
② 档 0 / 导轨支线那两条待办 ✓（见第十八手 ✓，未动 ✓）。

### 第二十手：**“跨网假接头”判据 + 两道执行点** ⇒ **v26**（2026-09-28 ✓ 用户定 ✓）

#### ① 判据（新）✓ —— `render_sch.py` 第 ④c3 条

病症 ✓：一根线的**端点 / 折点**搭在**另一根不同网**的线的**中段**（或端点 ✓）上 ✗
⇒ 图上**看着接上了** ✓（一个 T 形接头 ✓）、电气上**根本没连** ✗✗
（Fritzing 只认**端点对端点** ✓：端点落在中段，要在那点把线**断开**才算连 ✓）。
★ 为何以前两个工具都漏掉它 ✗：`seg_cross` 把“端点搭在中段上”当**接头**排除 ✓
（正确 ✓ —— 它不是交叉 ✓），可**没人**再问一句“这两根**是同一个网**吗”✗。
★ 口径 ✓：**同网** = 真接头 ✓（T 形搭接 / 轨上打断 都在做这个 ✓）⇒ 不算毛病 ✗；
**跨网** = **假接头** ✗✗ ⇒ **必须 0** ✓；判据调仓里**唯一那份** `sch_geom.on_seg`（中段 ✓）
+ 点到端点距离（端点粘端点 ✓），容差 `0.05` ✓。

| 版本 | 跨网假接头 | 具体是哪几处 |
|---|---|---|
| v23 / v24 | **3 处** ✗ | `Wire90012746` / `Wire90012747` 的折点 `(49.4,0)` 压在 **5V 竖线**中段上 ✗（就是第十九手 ④ 那处漏数 ✓）；`Wire90012735` 端点在 `(22.6,-57.6)` ✗ |
| **v25** | **1 处** ✗ | 只剩 `Wire90012735` ✓（`DATA_IN` 那两处已被共线合并顺手治好了 ✓） |
| **v26** | **0 处** ✓✓ | —— |

#### ② 两道执行点 ✓（同一条规则的两半 ✓）

1. **路由门 `HARD_FJ`** ✓（`fj_path_bad` ✓，`--nofj` A/B ✓）：候选路径的**顶点**不许搭在**别的网**
   的线上 ✗ —— 与 `HARD_PIN` / `HARD_OVL` 同一套路：**只删候选** ✗、不动代价函数与档位次序 ✓；
   删光 ⇒ 保留旧候选集 + 告警 ✓。★ 为什么必需 ✗：v24 那处 `DATA_IN` 就是**路由自己**把折点
   落在 5V 竖线中段上造成的 ✗ —— 它后来没了是靠**共线合并**抹掉的 ✓（**运气** ✓）⇒ 有了这道门，
   以后靠**规则** ✓。（本两档实测：门开与门关**逐项相同** ✓ ⇒ 现在它是**预防** ✓ 而非治当前的病 ✓。）
2. **轨端收尾** ✓（`fj_vertex_bad` / `fj_endpoint_used` ✓）：轨的两端若搭上了别的网 ✗ ⇒
   **没接东西**就往里收 `2 × MIN_SEG = 0.1`（= 判据容差的**两倍** ✓，留一倍余量抗浮点末位 ✓；
   0.028 mm ✓ 肉眼无差 ✓）；**接了东西** ⇒ **不动** ✓ + 告警 ✓（不许悄悄拆掉真接头 ✗）。

★ **v25 那处的病根 ✓**（实测 ✓）：5V **上轨**的左端外伸段端点 = `min(落点) − 7.2` = **22.578** ✗，
而 GND 的 `J1.c1` 支线车道 = `15.378 + 7.2` = **22.578** ✗ —— **两个网的坐标都是 7.2 的整数倍**
⇒ 落在**同一条网格线**上 ✗ ⇒ 那个端点正压 GND 竖线中段 ⇒ 图上**看着 5V 接在 GND 上** ✗✗。
✓ v26 把它收到 `22.678` ✓（日志里有一行 `★ 轨 左端**避开跨网假接头** ✓` ✓）。

<table>
<tr>
<td></td>
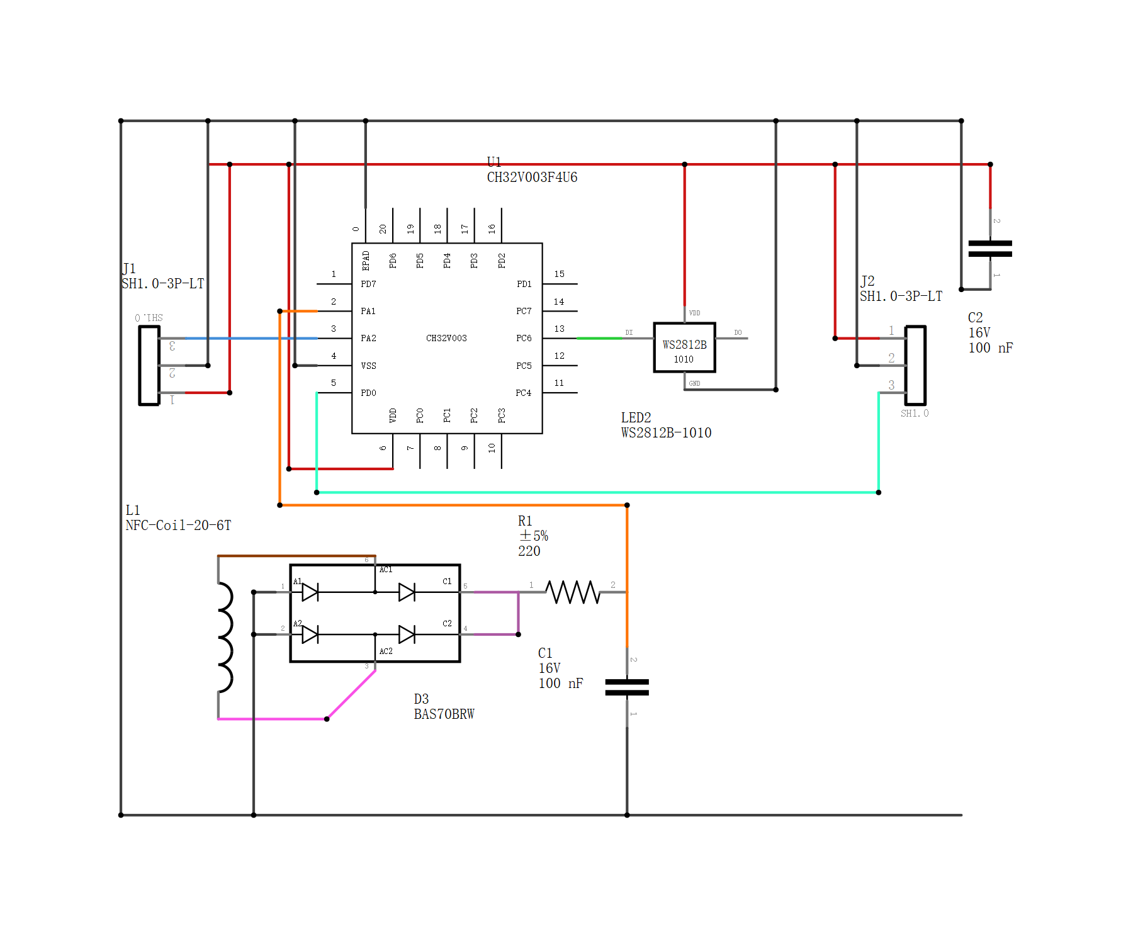
[picture p20: hardware/pixel/pixel-schematic-v26_preview.png]
<td></td>
</tr>
<tr>
<td><b>v25</b> ✓ 旧交付（跨网假接头 <b>1 处</b> ✗：5V 轨端压在 GND 竖线上）</td>
<td><b>v26</b> ✓✓ <b>假接头 0 处</b>（2699 ✓、导线 55 ✓、交叉 15 ✓、贴脚 0 ✓、告警 0 ✓）</td>
</tr>
</table>

**复现 v26 的三步** ✓（`_work/` 里的是中间物，不入库 ✓）：

```
py -3.13 gen_schematic_layout3.py pixel-schematic-v5.fzz _work/layout8.fzz --pins=pins_ref.py --socket=4
py -3.13 render_sch.py _work/layout8.fzz _work/layout8.png       # 出“尺子”（png + svg ✓）
py -3.13 gen_schematic_wires.py _work/layout8.fzz _work/layout8.svg pixel-schematic-v26.fzz \
    --orig pixel-schematic.fzz --ratio 1.0 --rip 3 --rails      # 默认已开 HARD_FJ ✓
py -3.13 check_netlist.py pixel-schematic-v26.fzz                # 网表必须 ✓ 10 个网全对
py -3.13 render_sch.py pixel-schematic-v26.fzz _work/p.png       # 看“跨网假接头 0 处”✓
```

★ **第二十手新增待办 ✓（未经你同意不动 ✗）**：
① `xcheck.py` 的 ③ 同样要按**同网 / 跨网**拆开 ✓（它是**独立**那份核对器 ✓ ⇒ 应当也能看到这 0 处 ✓）；
② 档 0 / 导轨支线两条待办 ✓（见第十八手 ✓，未动 ✓）。

### 第二十一手：**“让开”要让得看得见**（`FJ_GAP = 2.03 mm`）⇒ **v27**（2026-09-28 ✓ 用户定 ✓）

★ 用户定 ✓（原话）：「**做吧，要考虑人眼视觉的局限性，要尽量清晰**」✓。

✗ **第一版的错✗（先记下来 ✗）**：上一手把那个搭在 GND 竖线上的 5V 轨端只往里收了
`2 × MIN_SEG = 0.1` 单位 —— 那是 **0.028 mm** ✗，**比线宽（0.25 mm）还细** ✗
⇒ 判据上干净了 ✓、**肉眼看还是贴在一起** ✗ ⇒ **等于没修** ✗。

✓ **现在（v27）**：
1. 让开量 **`FJ_GAP = CLEAR_PIN = 7.2 单位 = 2.03 mm`** ✓ —— 就是用户定“导线离引脚要多远
   才看得清”的**同一个数** ✓（一样是“肉眼能不能分出接没接上”这件事 ✓，**不新造数** ✗）；
2. 让开时**按 7.2 的整数步往回退**（1…4 步 ✓）⇒ 端点仍在**网格**上 ✓、
   而且多半正好落在**本网最外侧那个落点**上 ✓ ⇒ 顺带把“悬空线端” **2 → 1** 也消掉一个 ✓；
3. 不许退过最外侧落点 ✗（否则路径会回头成锯齿 ✗）；四步都让不开 ⇒ 退到最小让开量 + **告警** ✓；
   这一端**接了东西** ✗ ⇒ **不动** ✓ + 告警 ✓（不许悄悄拆掉真接头 ✗）。

**实测（档1）** ✓：`5V` 上轨左端 **22.578 → 29.778** ✓（日志：`★ 轨 左端**让开跨网假接头** ✓：
… 让开 7.2 单位 = **2.03 mm** ✓ 肉眼分得清 ✓；退 1 步 × 7.2 ✓`）；
总长 **2699.3 → 2692.1** ✓、**假接头 0** ✓、悬空端 **2 → 1** ✓、贴脚 0 ✓、穿体 0 ✓、告警 0 ✓。

★ **另新增判据第二类「跨网擦身」** ✓（端点离**别的网**的线 < 2.03 mm ✗）——
  ✗ 它第一版是**误报**：把**同在一条直线上的断点**也算进去了 ✗（轨/长支线本来就**必须**
  在每个接头处断成几根 ✓ —— Fritzing 只认端点对端点 ✓；而**断点在图上是看不见的** ✗）
  ⇒ 误报 18 处 ✗；✓ 现在只算**看得见的端 / 角** ✓（同网同向直线续下去的 = 断点 ⇒ 不算 ✗）⇒ **15 处** ✓。
  ★ 这 15 处**全是一个聚簇** ✓（`U1` 左外侧 `x ≈ 46.38 / 49.38 / 51.38` 三条车道 ✓，
    相隔 **2.0 / 3.0 / 5.0 单位 = 0.56 / 0.85 / 1.41 mm** ✗）⇒ 这是**走廊间距**那一轴 ✗
    （**未动** ✓ —— 本仓在通道/间距轴上多次碰壁 ✓，要动得先定清楚再说 ✓）。

<table>
<tr>
<td></td>
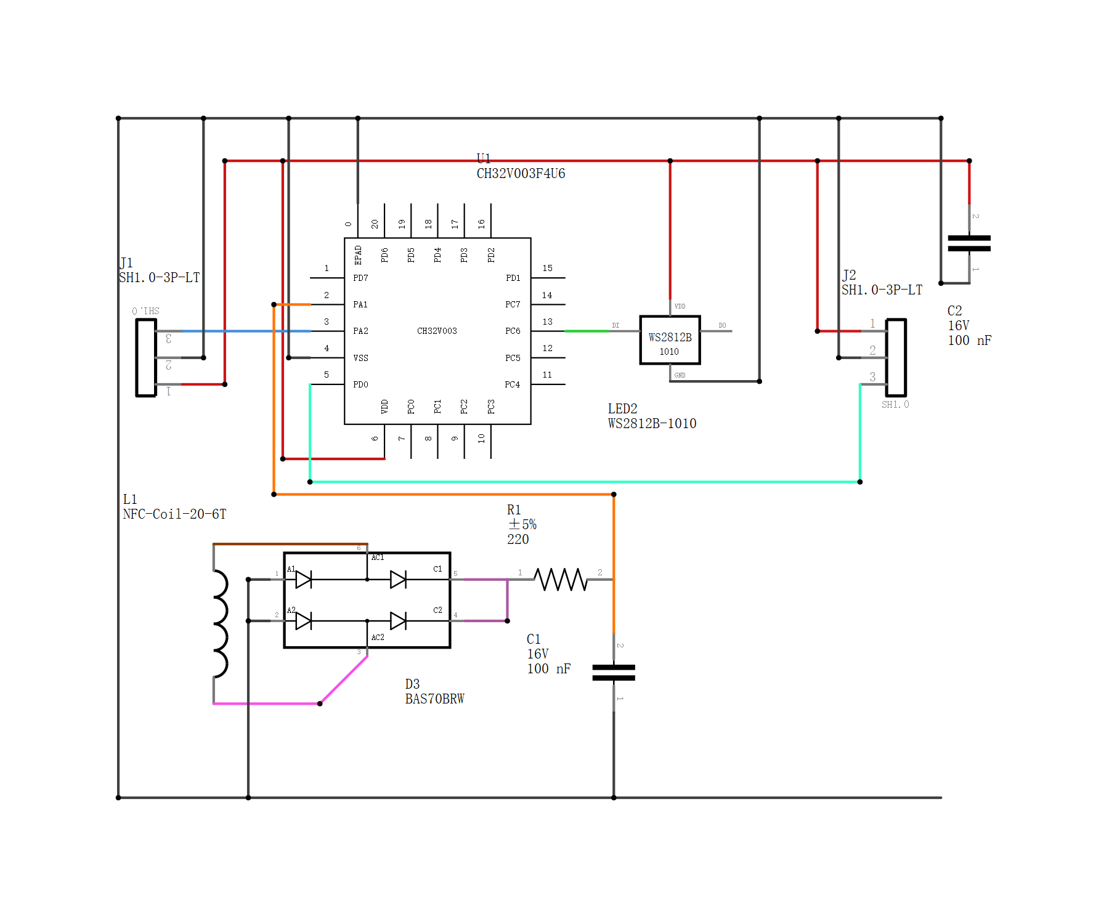
[picture p21: hardware/pixel/pixel-schematic-v27_preview.png]
<td></td>
</tr>
<tr>
<td><b>v26</b> ✓ 旧交付（让开量只有 <b>0.028 mm</b> ✗ —— 看不出）</td>
<td><b>v27</b> ✓✓ <b>让开 2.03 mm ✓</b>（2692 ✓、假接头 0 ✓、悬空端 1 ✓）</td>
</tr>
</table>

**复现 v27 的三步** ✓（`_work/` 里的是中间物，不入库 ✓）：

```
py -3.13 gen_schematic_layout3.py pixel-schematic-v5.fzz _work/layout9.fzz --pins=pins_ref.py --socket=4
py -3.13 render_sch.py _work/layout9.fzz _work/layout9.png       # 出“尺子”（png + svg ✓）
py -3.13 gen_schematic_wires.py _work/layout9.fzz _work/layout9.svg pixel-schematic-v27.fzz \
    --orig pixel-schematic.fzz --ratio 1.0 --rip 3 --rails      # 默认 FJ_GAP = 2.03 mm ✓
py -3.13 check_netlist.py pixel-schematic-v27.fzz                # 网表必须 ✓ 10 个网全对
py -3.13 render_sch.py pixel-schematic-v27.fzz _work/p.png       # 看“假接头 0 处”✓
```

★ **第二十一手新增待办 ✓（未经你同意不动 ✗）**：
① **走廊间距**轴 ✗：`U1` 左外侧那三条车道只隔 0.56～1.41 mm ✗ ⇒ 要“尽量清晰”就得让
   平行车道≥ **2.03 mm**（或干脆对齐到同一网格 ✓）；风险高 ✓（历史：通道实验多次变差 ✗）⇒ 待定 ✓；
② 档 0 / 导轨支线 / `xcheck` 那三条待办 ✓（未动 ✓）。

### 第二十二手：**支线共享同网竖线**（学手改版第三次 ✓）⇒ **v28**（2026-09-28 ✓ 用户定 ✓）

★ 用户选的路线 ✓（原话）：「**② 在支线搜索里加这种候选（不做后处理）**」✓ ——
  即：**直接在“脚 → 轨”的支线搜索里多试一种形状** ✗，不做事后合并 ✗。

✗ **病灶（你手改版第三次 ✓）**：同一条轨上，两条支线**各自竖一趟到轨** ✗ ——
  档1 实测 `U1.connector3` 出脚 7.2 + 竖 **81** ✓、`J1.connector1` 同 ✓ ⇒ 两根竖线并排 ✓。
✓ **手改版的做法**：右边那条改成**沿脚行横走 36.0** ✓、**搭到左边那条已经通到轨的竖线端点**上 ✓
  ⇒ 少画一根竖线 = **−52.2** ✓（手改版同侧两半共 −106.4 ✓）。

★ 落地路上撞到**两处硬卡点** ✓（都是**打印 `used` 看出来的** ✓，不是推的 ✗ —— 这是本手最大的教训 ✓）：
1. **布序** ✗：`U1.connector3`(x=58.6) 排在 `J1.connector1`(x=15.4) **之前**布 ✗ ⇒
   想共享时那根竖线**还没画** ✗ ⇒ `used` 里搜不到搭接点 ✓ ⇒ 候选加完**零效果** ✗
   （实测：两档数字与 v27**逐字相同** ✗）⇒ 修法 = **同一根轨上按“脚的 x”升序布** ✓（锚点先落 ✓）；
2. **1e-4 浮点末位** ✗（同一个坑 2026-09-28 在 `DATA_IN` 所成两段上踩过 ✓）：
   真值 `x = 22.5779` ✓ / `y = 9.000137` ✓，而我用 `1e-6` 判“同一条竖直车道” ✗ ⇒ **永远不命中** ✗
   ⇒ 修法 = `LANE_EPS = 1e-2` 单位 = **0.0028 mm** ✓（`.fzz` 写出时会四舍五入到 0.01
   单位 ✓ ⇒ 文件里两条线**端点重合** ✓、Fritzing 载入后是真接头 ✓）。
   ★ 派上用场的手段：临时加**环境变量开关的诊断打印** ✓（`DBG_T2` 把 `used` 里那 6 段
   **原样打出来** ✓ —— 一眼就看到 `22.5779` ✗；见完就删 ✓，不留开关 ✗）。

★ 连带修掉**一处真 bug** ✗（不修就交付不了 ✓）：`trim_on_rail` 原来用「点 y == **末点** y」
  判“在轨上” ✗ ⇒ 对「沿脚行横走」型支线，它的**首点就在脚行上** ✓ ⇒ `_k = 0` ⇒ `del p[1:]`
  ⇒ 路径只剩 1 个点 ✗ ⇒ 「⚠ 段被丢弃 ✗」⇒ **网表 ✗**（`U1.connector3` 的 GND 断开 ✗，两档都 ✗）。
  ✓ 判据改成「**落在本网某一条轨的 y 上**」✓ ⇒ 共享型支线**根本不到轨** ✓ ⇒ 原样跳过 ✓（形状保住 ✓）。
  ★ 这一条是**网表核（`check_netlist.py`）抳住的** ✓ —— 光看“重叠/贴脚/交叉”是**看不见**的 ✗。

**实测（档1 = 交付档 ✓）**：总长 **2692.1 → 2640** ✓（**−52.2** ✓）、导线 **55 → 52** ✓、
  **跨网擦身 15 → 8** ✓、交叉 15（不变 ✓）、贴脚 0 ✓、穿体 0 ✓、重叠 0 ✓、
  **假接头 0** ✓、悬空端 **1** ✓、画布 **105.8×87.4** ✓（不变 ✓）、
  网表 ✓ **10 网全对** ✓、告警 0 ✓、退出码 0 ✓、`sch_style_check` 通过 ✓（FAIL 0 / 提示 1 ✓）。
  日志新增一行形状 ✓：`★ 支线 **共享竖线（0 拐）** ✓：GND U1.connector3→汇点 沿脚行 向左 36.0
  ⇒ 搭在同网竖线的端点 (22.6,9.0) ✓（**不自己再竖一趟** ✓）` ✓。

<table>
<tr>
<td></td>
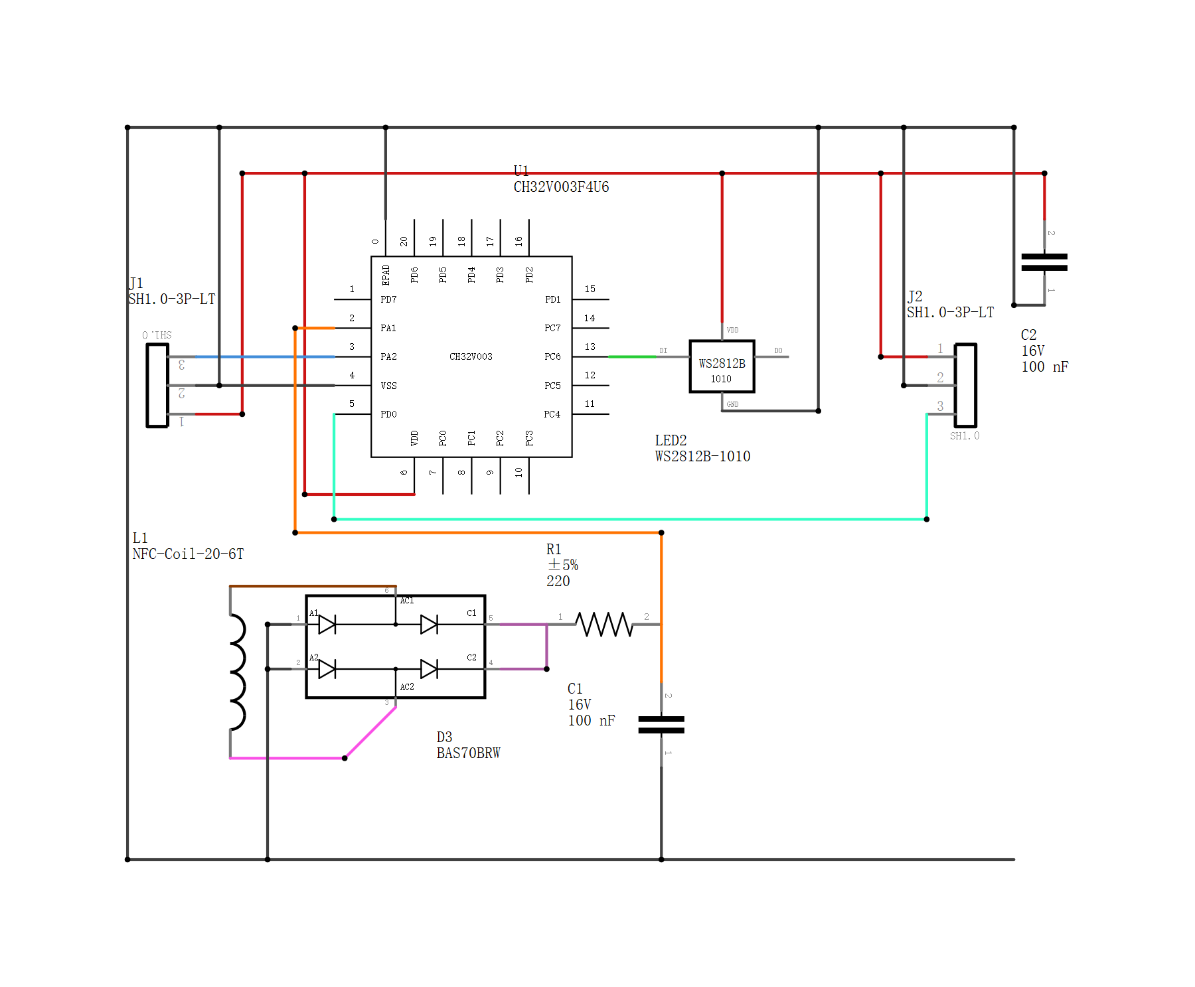
[picture p22: hardware/pixel/pixel-schematic-v28_preview.png]
<td></td>
</tr>
<tr>
<td><b>v27</b> ✓ 旧交付（两根支线<b>各竖一趟</b> ✗、导线 55 ✓、擦身 15 ✗）</td>
<td><b>v28</b> ✓✓ <b>共享竖线 ✓</b>（2640 ✓、导线 52 ✓、擦身 <b>8</b> ✓、假接头 0 ✓）</td>
</tr>
</table>

**复现 v28 的三步** ✓（`_work/` 里的是中间物，不入库 ✓）：

```
py -3.13 gen_schematic_layout3.py pixel-schematic-v5.fzz _work/layout10.fzz --pins=pins_ref.py --socket=4
py -3.13 render_sch.py _work/layout10.fzz _work/layout10.png    # 出“尺子”（png + svg ✓）
py -3.13 gen_schematic_wires.py _work/layout10.fzz _work/layout10.svg pixel-schematic-v28.fzz \
    --orig pixel-schematic.fzz --ratio 1.0 --rip 3 --rails    # 同轨支线按“脚 x 升序”布 ✓
py -3.13 check_netlist.py pixel-schematic-v28.fzz               # 网表必须 ✓ 10 个网全对
py -3.13 render_sch.py pixel-schematic-v28.fzz _work/p.png      # 看“假接头 0 处”✓
```

★ **第二十二手新增待办 ✓（未经你同意不动 ✗）**：
① 手改版的**另一半** `J2.c1 ↔ LED2` ✗（−54.2 ✓）：那一半需要「把邻居那根竖线在**本支线的
   脚行处打断**」✗（邻居远端在脚行**外侧** ✓）⇒ 得让 `used` 同步拆分 ✓（仓库里有先例：
   轨间互连“截成只剩出脚 ✓（同步 `used` ✓）” ✓）⇒ 下一轮 ✓；
② 档 0 那 1 条告警 ⚠（「兜底位置四档都不合格 ⇒ 仍用老位置」✓，来自“按 x 升序布”✓；
   档 0 **不交付** ✓ ⇒ 只记录 ✓）；
③ 第二十一手的待办依旧 ✓（走廊间距轴 ✗、导轨支线 / `xcheck` 那三条 ✓）。

### 第二十三手：**「邻居驱动」的车道 + 「接管」形态** ⇒ 追平手改版 ⇒ **v29**（2026-09-29 ✓ 用户定 ✓）

★ 用户定 ✓（原话）：「**push了，继续**」✓ —— 就是第二十二手留下的① ✓。

✗ **病灶（你手改版第三次的右半 ✓）**：邻居那根竖线**跨过**本支线的脚行 ✗ ——
  档1实测 `LED2` 的竖线 y: **17 → −72** ✓，而 `J2.c1` 的脚行是 **y=9** ✓
  ⇒ 旧判据要求“搭点在**脚行与轨之间**” ✗ ⇒ 一票否决 ✗（它一直自己竖一趟 81+7.2 ✗）。

✓ **新形态「接管」**（`truncate_branch_at` ✓ —— 与 `trim_on_rail` 同一套：改 `path` ✓、改 `b` ✓、
  **同步 `used`** ✗ 一处不改就会出现假重叠 ✓）：本支线沿脚行横走过去 ⇒ **邻居截到交点** ✓
  ⇒ 交点处**端点对端点** ✓（Fritzing 只认这个 ✓）、脚行以下那截竖线由本支线画 ✓
  ⇒ 同一段竖线只画一遍 ✓、但**少一根线** ✓。
  取法 = **乐观截断 → 跑四道闸门 → 不过就原样回退** ✓（`used` 快照恢复 ✓）⇒ 绝不比原来差 ✓。

★★ **本手最大的发现 = 第二处硬卡点 ✗：候选车道不能只按 7.2 档位找** ✗：
  实测 `J2.c1` 脚 x 与 `LED2` 竖线车道 x 相差 **34.0 = 4.72 × 7.2** ✗ ⇒ 十二档**永远踩不到** ✗✗
  （接管候选加完**零效果** ✗）。✓ 正解 = 车道集合换成 **① 7.2 档位（网格 ✓）+ ② 同网“已布竖线”
  所在的车道** ✓（**邻居驱动** ✓，只加在第二趟 ✓）—— 这才是手改版的做法 ✓。
  ★ 与第二十二手那 1e-4 是**同一类错** ✗：**拿自己的网格去量别人的线** ✗；
    判据要锚在**对方实际的位置**上 ✓（一条教训的第②条 ✓）。

**实测（档1 = 交付档 ✓）**—— **四个指标全部追平或超过手改版** ✓：

| 指标 | v28 | v29 | 你手改版（`v27_byHand` 第三次 ✓） |
|---|---|---|---|
| 总长 | 2640 | **2578.5** ✓ | 2585.7 ✓（比它**还短 7.2** ✓） |
| 导线 | 52 | **51** ✓ | 51 ✓ |
| 交叉 | 15 ✗ | **13** ✓ | 13 ✓ |
| 跨网擦身 | 8 | **8** ✓ | 8 ✓ |

其它 ✓：贴脚 0 ✓、穿体 0 ✓、重叠 0 ✓、**假接头 0** ✓、悬空端 **1** ✓、画布 105.8×87.4 ✓、
  网表 ✓ **10 网全对** ✓、告警 0 ✓、退出码 0 ✓、`sch_style_check` 通过 ✓（FAIL 0 / 提示 1 ✓）。
  日志 ✓：`★ 支线 **共享竖线（1 拐）** ✓：GND J2.connector1→汇点 沿脚行 向左 34.0 ⇒
  在 (210.6,9.0) **接管**同网竖线（邻居截到该点 ✓）⇒ 一路到轨 y=-72.0 ✓`；
  T 形搭接清单 **3 条** ✓（`D3.c0` ✓、`U1.c3` ✓、`J2.c1` ✓）。
  ★ 形状打印也**从几何读** ✓（不加标志位 ✗）：✗ 第一版只看了段首 ✗ ⇒ 形状对了、名字仍打成
  “L 形” ✗（邻居那段的**末端**才是交点 ✗）⇒ 改成**两个端点都看** ✓。

<table>
<tr>
<td></td>
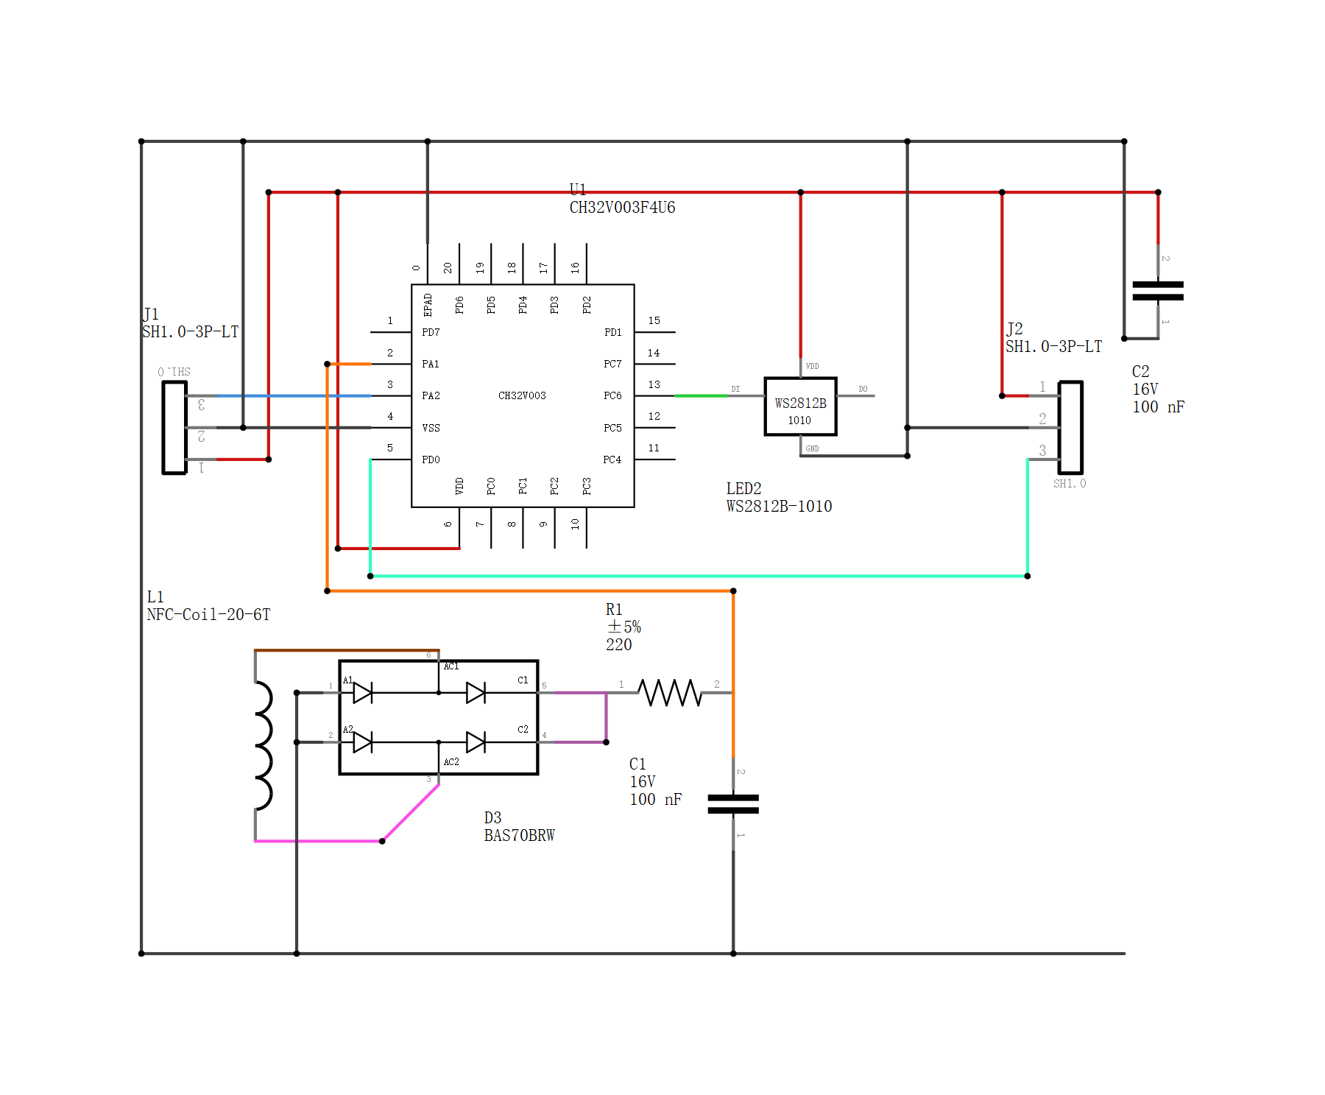
[picture p23: hardware/pixel/pixel-schematic-v29_preview.png]
<td></td>
</tr>
<tr>
<td><b>v28</b> ✓ 旧交付（只共享了左半 ✓；右半仍在自竖 ✗、交叉 15 ✗）</td>
<td><b>v29</b> ✓✓ <b>接管也做了 ✓</b>（2578 ✓、交叉 <b>13</b> ✓、导线 51 ✓、擦身 8 ✓）</td>
</tr>
</table>

**复现 v29 的三步** ✓（`_work/` 里的是中间物，不入库 ✓）：

```
py -3.13 gen_schematic_layout3.py pixel-schematic-v5.fzz _work/layout11.fzz --pins=pins_ref.py --socket=4
py -3.13 render_sch.py _work/layout11.fzz _work/layout11.png    # 出“尺子”（png + svg ✓）
py -3.13 gen_schematic_wires.py _work/layout11.fzz _work/layout11.svg pixel-schematic-v29.fzz \
    --orig pixel-schematic.fzz --ratio 1.0 --rip 3 --rails    # 车道 = 档位 + 邻居竖线 ✓
py -3.13 check_netlist.py pixel-schematic-v29.fzz               # 网表必须 ✓ 10 个网全对
py -3.13 render_sch.py pixel-schematic-v29.fzz _work/p.png      # 看“假接头 0 处”✓
```

★ **第二十三手新增待办 ✓（未经你同意不动 ✗）**：
① **走廊间距**轴 ✗（第二十一手那条 ✓）：`U1` 左外侧车道只隔 0.56～1.41 mm ✗ ⇒ 现在
   擦身 **8 处**里就有它 ✓ ⇒ 下一步就剩它最值 ¥ ✓（风险高 ✓：历史多次变差 ✗）；
② 档 0 那 1 条告警 ⚠（同上 ✓，不交付 ✓）；
③ `xcheck` ③ 拆「同网 / 跨网」、导轨支线待办 ✓（未动 ✓）。

### 第二十四手：**网标签**（把功能模块的边界切开）⇒ **v30**（2026-09-29 ✓ 用户定 ✓）

**口径**（用户定 ✓）：`netlabel` 是**抽象连接** ✓ ⇒ **只适用原理图** ✓（面包板 / PCB 要的是
**物理**连接 ✗）；它该用的地方**只有“功能能独立出来的模块”的边界** ✓ ——
本板即 **A = `L1/D3/R1/C1`**（取能 + 整流 + RC 取出 ✓）与 **B = 以 `U1` 为核心** ✓。
**跨 A/B 边界的网恰好两个：`RC` 与 `GND`** ✓（`COIL_A` / `COIL_B` / `BR+` 全在 A 内 ⇒ 不贴 ✓）
⇒ 各贴一对**同名**标签 ✓（电气靠“同名即连通”✓）。

**复现 v30** ✓（`_work/` 里的是中间物，不入库 ✓）：

```
py -3.13 gen_schematic_layout3.py pixel-schematic-v5.fzz _work/layout11.fzz --pins=pins_ref.py --socket=4
py -3.13 render_sch.py _work/layout11.fzz _work/layout11.png            # 出“尺子”（png + svg ✓）
py -3.13 gen_schematic_wires.py _work/layout11.fzz _work/layout11.svg pixel-schematic-v30.fzz \
    --orig pixel-schematic.fzz --ratio 1.0 --rip 3 --rails \
    --modules=L1,D3,R1,C1 --label=RC,GND        # NL2 模块边界 ✓ + NL1 网标签 ✓
py -3.13 check_netlist.py pixel-schematic-v30.fzz    # 网表 ✓ 9 个网全对
py -3.13 check_flags.py   pixel-schematic-v30.fzz    # 旗标不许被穿 ✓ 必须 0/4
py -3.13 render_sch.py pixel-schematic-v30.fzz pixel-schematic-v30_preview.png
```

**比 v29 好在哪** ✓（同一套判据 ✓）：

| | v29 | **v30** |
|---|---|---|
| 网表 | 9 网全对 ✓ | 9 网全对 ✓ |
| 导线 | 51 | 49 |
| 十字交叉 | 13 | **11** ✓✓ |
| 跨网擦身 | 8 | **4** ✓✓ |
| 跨网假接头 / 穿元件本体 | 0 / 0 ✓ | 0 / **0** ✓ |
| **被穿旗标** | —（无标签 ✓） | **0 / 4** ✓✓ |
| 画布 | 105.8 × 87.4 mm | 105.8 × 92.5 mm（底下多一个 `RC` 标签 ✓） |

<table>
<tr>
<td></td>
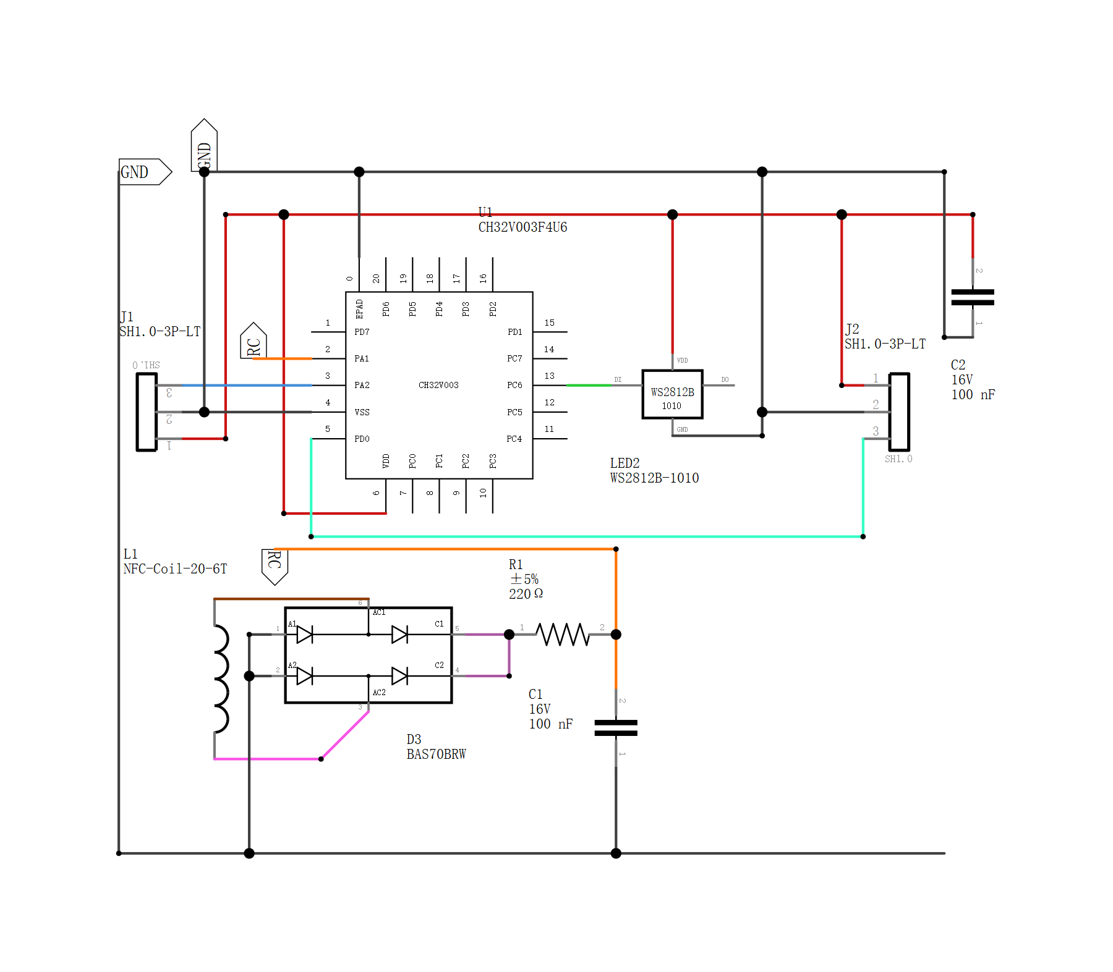
[picture p24: hardware/pixel/pixel-schematic-v30_preview.png]
<td></td>
</tr>
<tr>
<td><b>v29</b> ✓ 旧交付（无标签；交叉 13 ✗、擦身 8 ✗）</td>
<td><b>v30</b> ✓✓ <b>网标签</b>（模块边界 ✓；交叉 <b>11</b> ✓、擦身 <b>4</b> ✓、被穿旗标 <b>0/4</b> ✓）</td>
</tr>
</table>

**几何是量出来的、不是估的** ✓（口径全部收在 `sch_net.py` **一处** ✓；生成器 / 渲染器 / 判定器都调它 ✓）：

- 网标签是**元件实例** ✓，Fritzing 给它写**两组**图形：`mi+"0"` = **箭头旗标**（`<polygon>` ✓）、
  `mi+"1"` = **文字** ✓（✗ 我一度只查了后者 ⇒ 画出来**少了外面的框** ✗，用户当场指出 ✓）。
- **文字**：左缘 x **0.6** ✓、基线 y **6.6** ✓、字号 **6.0** ✓（sketch ✓ = 导出 ×1.25 ✓）、无 `text-anchor` ✓。
- **旗标**：宽 **8.700** ✓、长 `L = 5.9052·Σ(步进/em) + 4.6964` ✓（9 个名字最小二乘 ✓ rms **0.064 mm** ✓）、
  尖头长 **4.350** ✓；**锚在文字上** ✓（0° / 90° / −90° 三组顶点**完全一样** ✓ ⇒ 与旋转无关 ✓）。
- **旋转**：绕**板心** `(0.6 + W/2, 4.5)` ✓（`W = L − 0.9` ✓，由两个独立量到的枢轴互证 ✓：
  `RC` 11.321 ↔ 11.3219 ✓、`GND` 17.016 ↔ 17.0055 ✓）；文件里的 `m31/m32` 写 **`(I−R)·C`** ✓
  ⇒ “忽略它”与“尊重它”两种读法**落在同一处** ✓。
- **字号回退**：Fritzing **不自带字体** ✗（搜遍安装目录：没有 ttf/otf/woff ✓）⇒ 它请求 `Droid Sans`、
  由 Qt6 从**系统字体**回退 ✓；拿系统里**全部 345 个字体**逐一拟合 ⇒ **Noto Sans** ✓（rms 0.034 mm ✓；
  Segoe UI Bold 0.097 ✗ / Calibri 0.134 ✗）⇒ 字宽表 = `sch_glyphs.py`（**纯数据** ✓）。
- **接点圆点**：该处 **≥2 个导线端点**就画 ✓（小 r **0.9** ✓ / 大 **1.8** ✓；大小 = 线端 + **脚** ≥3 ⇒ 大 ✓）。

**这一手修掉的三个真问题** ✓（都不是审美 ✓；写下来免得回头再踩 ✓）：

1. ✗ **`LABEL_NETS` 没有模块级初值** ✗ ⇒ 不给 `--label` 时 `emit()` 直接 `NameError` ✗ ——
   也就是说「**不给开关 ⇒ 一字节不差（v29 可复现 ✓）**」这条路**从来没被验证过** ✗。
   补上后实测：**v29 的 26 个 zip 条目逐字节相同** ✓✓（整包哈希不同只因 zip 条目**时间戳** ✓）。
2. ✗✗ **判碰撞用的盒子比旗标小一圈** ✗（`label_box` 返回的是**“板”** = 文字墨迹框，4.2 高 ✗；
   而看得见的旗标宽 **8.7** ✓）⇒ 红 `5V` 竖线**正从旗标身上穿过** ✗，
   而生成器打印的却是 **“违例 0”** ✗✗。⇒ 两处修：
   - 判据改成**旗标** ✓（直接调 `label_flag` ✓ —— 一份几何 ✓）；渲染器那道“穿元件本体”跟着一起变灵 ✓；
   - **另写** `check_flags.py` ✓（**不看**那个盒子 ✓，直接量画出来的 `<polygon>` ✓）——
     「**自检不算数**」✓（`AGENTS.md` §0 第 ⑦ 条 ✓）：判据要能被**另一个实现**或**人的眼睛**推翻 ✓。
   ★ 灵敏度**当场验过** ✓（不许只说“能跑” ✗）：`v34`（用户截图点名那版）⇒ **3 / 4 被穿** ✓✓ ——
   正好是“竖着的 `GND` + 两个 `RC`” ✓，横的那个 `GND` 没穿 ✓ = 与用户当时看到的**完全一致** ✓；
   `v39` ⇒ **1 / 4** ✓（当时那个 `_scratch/fix_label_place.py` 用的是**同一个瞎盒子** ✗）。
3. ✗ **标签朝向候选里还留着 `180°`** ✗ ⇒ 实测真挑中了一个 ✓（`m11 = −1 m22 = −1` ✓）= **倒着写字** ✗。
   ⇒ 收成 `LBL_ROTS = (0, 90, 270)` ✓ —— 与 `_scratch/fix_label_place.py` 里**早就有**的那条同一口径 ✓。

**两处“多余的东西”也清掉了** ✓：

- ✗ **多余的圆点** ✗（用户点名 ✓）：标签沿轴挪开 7.2 单位时，我原来的做法是
  「**保留原线端 + 另拉一小段引线**」✗ ⇒ 在 `(46.38, −9.00)` 留下一个**纯接缝** ⇒
  Fritzing 按「≥2 个线端 ⇒ 画圆点 ✓」给它画了个**小圆点** ✗ —— 而两根线其实在**同一条直线**上 ✗
  ⇒ 那个圆点**不代表任何分叉** ✗。
  ⇒ 新判据 `end_is_free()` ✓：**那一端没有别人的端点 / 脚 ⇒ 直接搬线端** ✓（不留接缝 ✓）；
  **有** ⇒ 才加引线 ✓（老接头动不得 ✓ —— 那正是老教训里“网表 ✗、连通块 9 → 10 ✗”的情形 ✓）。
  实测：`Wire90012777` 12.2 → **19.4** 单位 ✓、导线 50 → **49** ✓、圆点 29 → **28** ✓、那个点上**圆点 0 个** ✓
  （独立量：`check_flags` 同族的 `dump_dots` 在那儿量到 **0 个** ✓）。
- ✗ **`--label` 之外的复现路没跑过** ✗（见上面第 1 条 ✓）。

★ **教训** ✓（值得单列 ✓）：我上一条命令用 `Select-String` **过滤**输出 ⇒ 把“预览 PNG 写入失败”的报错
**藏掉了** ✗ ⇒ 我拿**旧图**当新图看 ✗，一度以为圆点没去掉 ✗。露馅靠的是**文件时间戳对不上** ✓ ——
与 `AGENTS.md`「过滤掉的东西会骗人 / 不许自证」同一条 ✓。

### 第二十五手：**脚位模型修正** ✗✗ ＋ **接地符号** ＋ 用户手改版 ⇒ **v31**（2026-09-29 ✓ 用户定 ✓）

**起因** ✓：用户手改了一版 `pixel-schematic-v30_byHand.fzz` 让我“检查” ✓ ——
思路两处：**① 把两个 `GND` 网标签换成更常见的接地符号** ✓；**② 挪了 `RC` 标签的位置、去掉多余导线** ✓。

#### ① 接地符号：**按名字把全图的地拉到一起** ✓（判定器原来不认它 ✗ = 假警 ✗）

规则**在 Fritzing 源码里** ✓（逐条抄进 `sch_net.py` 的注释 ✓）：

```cpp
bool ConnectorItem::isGrounded() {          // src/connectors/connectoritem.cpp
    return name == "gnd" || name == "vss" || name == "ground";   // 大小写不敏感
}
// src/items/symbolpaletteitem.cpp::busConnectorItems
else if (bus->id().compare("groundbus", Qt::CaseInsensitive) == 0)  mitems = LocalGrounds;
```

件定义（嵌在 `Fritzing.exe` 里的 `resources/parts/core/ground.fzp` ✓，与草图里那条
`path=":/resources/parts/core/ground.fzp"` 对得上 ✓）：`<connector id="connector0" name="GND">`
＋ `<bus id="groundbus">` ✓。

⇒ **接地符号不是“两个符号互连”** ✗ —— 它把**全图「脚名 ∈ {GND,VSS,GROUND}」的连接器**
一把拉成一张网 ✓（`U1` 的 **`VSS`** ✓、`LED2` 的 **`GND`** ✓、以及**符号自己的脚** ✓）。
★ 反过来说：**图里没有接地符号 ⇒ 什么也不合并** ✗（那些脚只是“名字叫 GND”而已 ✓）。
★ 判据**只在 `sch_net.py` 一份** ✓（`grounded_connectors` / `ground_links` ✓，脚名从
`.fzz` **自带的那份 `.fzp`** 里读 ✓ —— 草图里只有 `connectorId` ✗、看不到脚名 ✗）。
⇒ 本图：合并 4 只脚（`LED2.connector1` ✓、`U1.connector3` ✓、两个符号自己的 ✓）⇒ **9 网全对** ✓✓。

#### ② ✗✗ **脚位模型是错的**（错了整整一个旗标长 ≈ 3.4mm ✗）—— 这一手真正的病 ✓

我一直以为标签的脚在**平端** `(0, 4.5)` ✗。Fritzing 自己生成标签 SVG 的源码
（`NetLabel::makeSvg` ✓）写的是：

```cpp
double totalHeight = 300/divisor;   double arrowWidth = totalHeight / 2;      // 100 / 50
double strokeWidth = 10/divisor;    double halfStrokeWidth = strokeWidth / 2; // 3.333 / 1.667
if (goLeft)  pin = pin.arg(0).arg(0).arg(arrowWidth).arg(totalHeight);
else         pin = pin.arg(totalWidth - arrowWidth - 0.1).arg(0).arg(arrowWidth).arg(totalHeight);
```

⇒ 脚 = **pin rect 的外缘** ✓，在**箭头尖端那一侧** ✓：
`direction="right"`（默认 ✓）⇒ 局部 x = 旗标右缘 **+0.141**（sketch ✓）；`direction="left"` ⇒ 旗标左缘 **−0.150** ✓。

**证据（两条独立）** ✓：
- **手画的线**（Fritzing 存的是**吸附后**的真脚位 ✓ = 权威尺子 ✓）：
  `v30_byHand` `RC`(180°) 旧模型差 **3.535 mm** ✗ ／ 新模型 **0.004 mm** ✓✓；
  `v31_rcgnd_byHand` `RC`(90°) 旧 3.535 ✗ ／ 新 **0.004** ✓✓；
  `v31_rcgnd_byHand` `RC`(0°) 旧 3.535 ✗ ／ 新 **0.258** ✓。
- ⇒ **`pixel-schematic-v30.fzz` 里四个标签，在 Fritzing 里其实全没接上** ✗✗（线停在平端 ✓、
  脚在尖端 ✓ = “看着接上、其实没接” ✓）—— 这也解释了用户为什么用接地符号换掉 `GND` 标签 ✓
  （符号靠**名字**连通 ✓，根本不接线 ✓）。◎ 已复跑确认：`v30` 的 `(A)` = **4 处** ✗✗
  （4 个标签全断 ✓）、`v29`（无标签 ✓）= **0 处** ✓。

**并且**：`(A)` 那条判据的容差原来写死 `0.05` 单位 = **0.014 mm** ✗ ⇒ 把 Fritzing 吸附后
仍带的零头（实测 **0.09~0.13 单位** = 0.03~0.04 mm ✓）全判成“没画到” ✗ ⇒ **假警**永远在叫 ✗
⇒ 改成实测口径 `PIN_HIT_TOL = 0.5`（= 0.14 mm ✓，仍 ≪ 一根线宽 0.25 mm ✓）；
**真断**那些差 **3.5~12 单位** ✓ —— 与零头**差两个量级** ✓，阈值很好定 ✓。

★ **教训** ✓（第三次同一条 ✓）：这个错**躲过了当时所有自检** ✗ —— 因为 ② 量的是
「线端 ↔ **我自己算的脚**」✓ = **自证** ✗（`AGENTS.md` §0 ⑦ ✓）。这次是靠**换一把不信我自己的尺子**
（用户手画的线 ✓ + Fritzing 源码 ✓）才翻出来的 ✓。

#### ③ v31 = 用户手改版 ＋ **只修那一处** ✓

用户那版里 **3 处接头是准的** ✓✓（他自己画的 ✓：0.004 mm ✓），只剩**我生成的那一根**
（`Wire90012777 → RC` ✗，差 3.50 mm ✗）⇒ **不动导线** ✓、改**标签**：
把 `mi 90012781` 的 `geometry` 按**新模型**反解（`sch_net.label_geom` ✓）＋ 朝向 `270°→90°` ✓
（90° 时旗标朝上 ✓，实测**不被任何线穿** ✓；270° 会横在 `DATA_IN` 上 ✗）⇒ 脚正好落回线端 ✓。

```
# 只读输入、另存输出；只改那一个实例的 schematicView 里的 geometry + m11..m32 ✓
py -3.13 f:\git\_scratch\fix_label_geom.py pixel-schematic-v30_byHand.fzz pixel-schematic-v31.fzz \
        90012781 39.1779 -9.0 90
py -3.13 check_netlist.py pixel-schematic-v31.fzz      # ✓ 9 个网全对
py -3.13 check_fake_wires.py pixel-schematic-v31.fzz   # (A)=0 (B)=0 ✅ 合格
py -3.13 check_flags.py pixel-schematic-v31.fzz        # 被穿旗标 0/2 ✓✓
py -3.13 render_sch.py pixel-schematic-v31.fzz pixel-schematic-v31_preview.png
```

| | v30（旧 ✗ 脚位模型） | **v31** |
|---|---|---|
| ① 网表 | 9 网全对 ✓ | 9 网全对 ✓ |
| ② 假连线 (A)/(B) | **4 ✗** / 0 | **0** ✓ / 0 ✓ ⇒ ✅ 合格 ✓ |
| ④ 被穿旗标 | —（同一批错 ✗） | **0 / 2** ✓✓ |
| 导线 | 49 | 47 ✓（用户去掉 2 根 ✓） |
| 十字交叉 | 11 | 11 ✓ |
| 跨网擦身 | 4 ✗ | **0** ✓✓ |
| 假接头 / 穿元件本体 / 可读性 | 0 / 0 / 0 ✓ | 0 / 0 / 0 ✓ |
| 画布 | 105.8 × 92.5 mm | **104.1 × 86.1 mm** ✓（更紧凑 ✓） |

<table>
<tr>
<td></td>
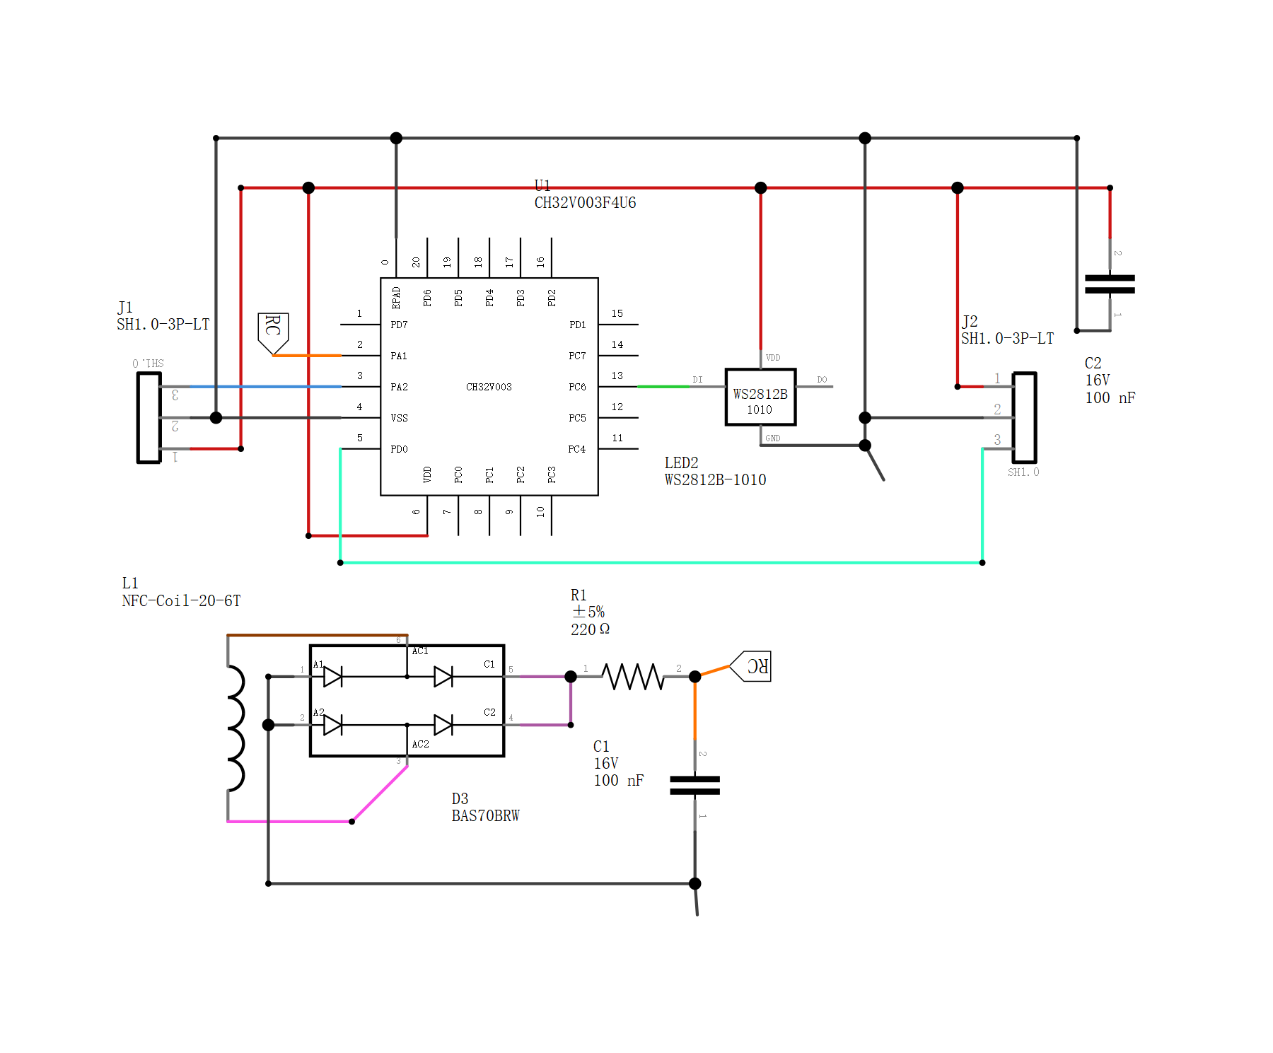
[picture p25: hardware/pixel/pixel-schematic-v31_preview.png]
<td></td>
</tr>
<tr>
<td><b>v30</b> ✗ 旧（标签脚位错 ⇒ Fritzing 里四个标签全没接上 ✗）</td>
<td><b>v31</b> ✓✓ <b>接地符号 + 脚位修正</b>（②✅ ④ 0/2 ✓；擦身 <b>0</b> ✓）</td>
</tr>
</table>

⚠ **预览里两块接地符号是空的** ✗ —— `render_sch.py` 画不出它：它的 SVG 是 **core 库件** ✓
（`:/resources/parts/core/ground.svg` ✓，嵌在 Fritzing app 里 ✓），`.fzz` **不带**它 ✗
⇒ 渲染器只能**跳过** ✗（图上那两根孤零零的短线就是它俩的连线 ✓）。
**不以我的预览为准** ✗ —— 请以 **Fritzing 里打开 `pixel-schematic-v31.fzz`** 为准 ✓
（要我把那份 core SVG 抠出来入库、给渲染器补上也可以 ✓ —— 那要走 `svg/_assets/` + 许可说明 ✓）。

（★ 下一手可选：`--label` 目前是“点名制” ✓，将来若要把**所有**跨模块网都自动贴 ✓，
判据已经就位 ✓ —— `cut_at_module_boundary` 只要不按 `LABEL_NETS` 过滤即可 ✓；未动 ✗。）

### 第二十六手：**线要平直** ＋ **文字朝向照 Fritzing** ⇒ **v32**（2026-09-29 ✓ 用户定 ✓）

用户三条（原话 ✓）：「**接地和 RC 标签的线，都应平直，你可以移动地和标签的**」✓、
「**Fritzing 中看，RC 的文字是正的，不是反的**」✓、以及同意把 core 的接地符号 SVG 入库 ✓。

#### ① 三条线弄平 ✓（**只挪元件，不弯线** ✓）

| 连到 | 原来 ✗ | 现在 ✓ |
|---|---|---|
| `RC` 标签（`mi 90012780`） | (161.328,84.000)→(171.000,**81.000**) 斜 ✗ | (161.328,84.000)→(171.000,**84.000**) **水平** ✓ |
| 接地符号 `Ground1` | (210.578,17.000)→(216.000,27.000) 斜 ✗ | (210.578,17.000)→(**210.578**,27.000) **竖直** ✓ |
| 接地符号 `Ground2` | (161.328,143.961)→(162.000,153.000) 斜 ✗ | (161.328,143.961)→(**161.328**,153.000) **竖直** ✓ |

做法：**平移元件**（标签 / 接地符号 ✓）⇒ 它的脚位跟着走 ⇒ 再把**连它的那根线的端点**搬到新脚位上 ✓
（`_scratch/move_part.py` ✓，只改实例 `schematicView` 的 `geometry` + 那根线对应端的相对量 ✓）。
★ 脚位一律问 `sch_net`（网标签 ✓ / 接地符号 ✓ —— 都已实测标定 ✓），脚本自己不写第二份几何 ✓。

#### ② 接地符号的**脚**反推出来了 ✓（两个样本完全一致 ✓✓）

它也在**自己的 svg 里**（`schematic/ground.svg` 的 `connector0pin` ✓）、`.fzz` 不带 ✗ ⇒
用**用户手画的两处线端**反推（Fritzing 存的是吸附后的真脚位 ✓）：

```
Ground1 原点 (206.999, 26.4044) ← 线端 (216.000, 27.000) ⇒ 偏 (+9.001, +0.596)
Ground2 原点 (152.999, 152.404) ← 线端 (162.000, 153.000) ⇒ 偏 (+9.001, +0.596)   ← 一模一样 ✓✓
```

⇒ `sch_net.ground_pin(geom) = geom + (9.001, 0.596)` ✓（= 0.1in ✓ 往右、顶上中间 ✓）。
★ 同时把接地符号**登进 `PIN_SK`** ✓ ⇒ ② 现在**量得到**“线有没有接在接地符号上” ✓
（✗ 以前它掉进“图形缺失 ⇒ 不判”那一档 ✗ ⇒ 线飘到哪都查不出来 ✗）。

#### ③ 文字朝向：**`m11 < 0` ⇒ 正着排字** ✓

✗ 我原来无论什么朝向都把 `<text>` 跟着转 θ ✗ ⇒ **180° 时字是倒的** ✗（用户当场指出 ✓）。
依据：源码里 Fritzing 自己就这么判 —— `bool reversed = (transform().m11() < -0.5);  // horizontal flip or 180°` ✓
⇒ `m11 < 0`（镜像/180°）时**不转** ✓，并按**画出来的旗标盒**排布：靠**非尖端**那侧 ✓（右对齐 ✓）、
竖直居中 ✓。★ 第一版我靠了左 ✗ ⇒ 字有一半压在尖头上 ✗（放大截图当场可见 ✗）⇒ 改右对齐 ✓。
（±90° 仍跟着转 ✓ = 竖排 ✓，与用户此前 `GND` 竖排的截图一致 ✓。）

**v31 → v32** ✓：闸门 ① 9 网全对 ✓ ｜ ② **(A)=0 (B)=0 ✅** ✓ ｜ ④ **0/2** ✓✓ ｜
导线 47 ✓、交叉 11 ✓、擦身 **0** ✓、画布 104.1 × 86.1 mm ✓。

<table>
<tr>
<td></td>
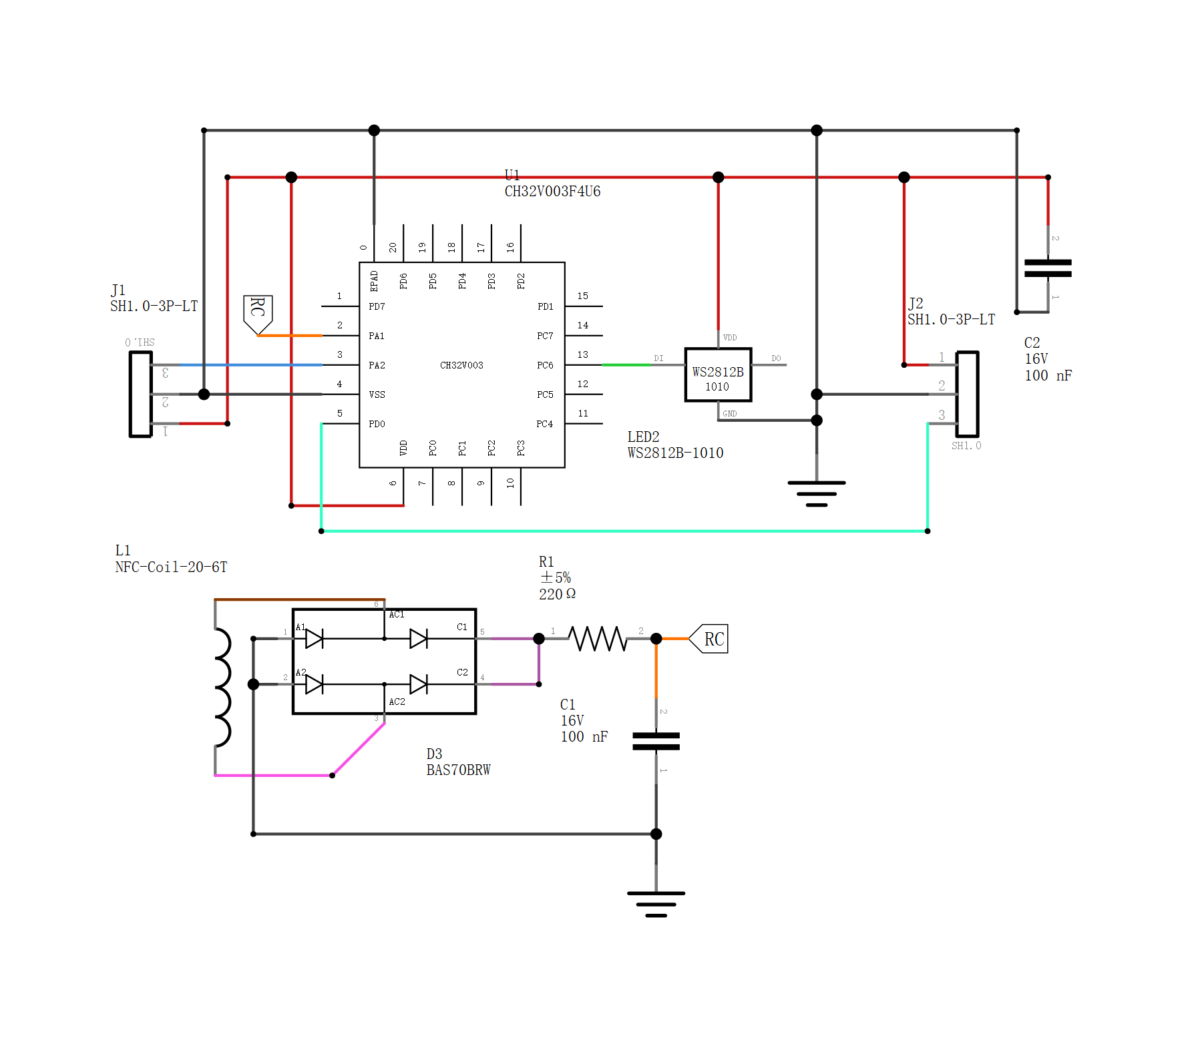
[picture p26: hardware/pixel/pixel-schematic-v32_preview.png]
<td></td>
</tr>
<tr>
<td><b>v31</b> ✗ 到接地/标签的线是斜的 ✗；`RC` 的字倒着 ✗</td>
<td><b>v32</b> ✓✓ <b>线全平直 ✓ + 字正着 ✓</b>；② <b>(A)=0 (B)=0</b> ✅、④ <b>0/2</b> ✓</td>
</tr>
</table>

★ **还差一块** ✓：核心库的**接地符号图形**（`schematic/ground.svg` ✓）—— 它**在 Fritzing app 里** ✗
（从 exe 里没抠出干净的一份 ✗：源码仓那份是**构建时生成**的 ✗ ⇒ raw 取不到 ✓）。
**最稳的取法**：你在 Fritzing 里导出一次 `pixel-schematic-v32_图示.svg` ✓ ——
那份导出里就**带着 Fritzing 自己画的接地符号** ✓ ⇒ 我照 `svg/_assets/` 的做法
（**图形 + `LICENSE-ground.txt` 许可说明** ✓，与 WS2812B/JST 同一套 ✓）入库 ✓，
渲染器就能画它 ✓，也能**顺便把 180° 的文字位置逐点核对**一遍 ✓（`check_labels.py` ✓）。

#### ④ **接地符号图形入库了** ✓＋与 Fritzing 导出**逐点对账** ✓（2026-09-30 ✓ 用户导出 ✓）

用户导出 `pixel-schematic-v32_图示.svg` ✓ ⇒ 两件事一起办完 ✓：

- **图形入库** ✓：从导出里**逐字摘出** `GroundModuleID` 的绘制内容（两个实例**完全一致** ✓）
  ⇒ `_assets/ground_symbol.svg` ✓ ＋ `_assets/LICENSE-ground.txt`（来源 / 许可 / 用途 ✓，
  与 WS2812B・JST 那套同一做法 ✓）。`sch_net.ground_art()` 读它并摆位 ✓
  （`translate(几何 + (9.001,0.596)) · scale(1.25) · translate(-7.201,-0.375)` ✓
  ⇒ **脚正好落在 `ground_pin()` 上** ✓，图形与脚位**同一份口径** ✓）⇒ **预览里它俩画出来了** ✓✓。
  ★ 顺便**独立复核**了脚位 ✓：导出里 `translate + 内层 pin(7.201,0.375)` 换算到 sketch
  = (210.58, 26.87) ✓，我反推的是 (210.578, **27.000**) ✓ ⇒ **差 0.04mm** ✓✓。
- **对账（`check_labels.py` ↔ 导出）** ✓：

| 项 | 结果 |
|---|---|
| **文字锚点** | **0.00000 mm** ✓✓（90° 那只 ✓） |
| **旗标逐顶点** | **0.096 导出单位 = 0.034 mm** ✓✓ |
| 镜像/180° 标签的文字 | ⊘ **跳过并报出** ✓ —— Fritzing 会给它**再加一层反向矩阵** ✓（导出原话 `matrix(-1,0,0,-1,6.6855,7.236)` ✓）⇒ 锚点**不可比** ✗（差 2.33mm 是**补偿量** ✓，不是文件错 ✓）；旗标那项照核 ✓ |

⇒ 由导出反推的结论 ✓：**180° 标签在 Fritzing 里文字是正的** ✓（矩阵补偿 ✓，
与我 ③ 改的口径一致 ✓）；**90° 标签照转** ✓；文字**基线离旗标盒底 2.30 sketch** ✓
（我的实现 2.25 ✓，差 0.2mm ✓）。

★★ `check_labels.py` 这次**自己修了两个 bug** ✗（都是"同名重复"引起的 ✓，记下来 ✓）：
- ✗ **定标**原来用"同名对投票" ✗ ⇒ 两个 `RC` 互相错配 ✓、还常**打平** ✗ ⇒ 文字被报到 **50mm** ✗✗；
  ⇒ 改成**枚举候选平移 + 一对一贪心配对 + 取总误差最小** ✓，并且**只用没被补偿的标签定标** ✓。
- ✗ **旗标配对**按"最近中心"但不**消耗** ✗ ⇒ 两个同名标签**抢同一个导出组** ✗ ⇒ 假报 2.75mm ✗；
  ⇒ 改成**一对一贪心** ✓ ⇒ 0.034mm ✓✓。

✗ **我自己的一次犯规**（记下来 ✓）：想改这两处时，我图快用 **PowerShell 字符串替换**去改 `.py` ✗
⇒ **UTF-8 被写坏、文件直接不能解析** ✗✗ ⇒ 只好 `git checkout` 回滚重做 ✓。
**源码只能走编辑工具改** ✗ —— 终端别碰源文件 ✓（`AGENTS.md` 里那条 ✓，这次是我自己破的 ✓）。

### 第二十七手：**接地符号产出** ＋ **整套按规则生成** ＋ **剪掉冗余的电/地接线** ⇒ **v33**（2026-09-30 ✓ 用户定 ✓）

用户一句「**做**」✓ = 把我提议的两件补上 ✓：① 生成器能**产出接地符号** ✓；
② **整套**（网表 + 摆位 → 全部导线 / 网标签 / 接地符号）**都由规则生成** ✓ —— 不再依赖手改版 ✓。
然后用户再提一手 ✓（原话 ✓）：「**检查每根 5V 和 GND 接线，如果删除不影响网的连通，就删除；
如果有更好的连接点可以不违反任何规则又节省线长，就更改接线。**」✓ ⇒ ③ 见下面「剪冗余」那一节 ✓。

#### ★★ 第一版错在哪 ✗（记下来 ✓）：**不能把接地符号挂在切口上** ✗

第一版图省事：`--ground=GND` 直接**借标签那条路** ✗ ⇒ 符号就挂在 `NL2` 切出来的两个断口上 ✗。
实测两个断口**都不合适** ✗：

- 断口 `(−6.22,−72)` **正好是一根长竖线的顶端** ✓ ⇒ 往下挂 ⇒ **那根线从符号的三根横线里穿过去** ✗
  （图上看就是"符号挂在线上、线把符号打穿" ✗ —— 这种错**用户一眼就能看见** ✗）；
- 另一个断口在横轨上 ⇒ 引线**横着进**符号 ✗。

⇒ 于是**另写一份实现**当尺子 ✓（`check_grounds.py` ✓ 已入库 ✓：常数自己写死 ✓、不调生成器任何代码 ✓）：

| 文件 | 结果 |
|---|---|
| `pixel-schematic-v32.fzz`（用户手改版 ✓ **权威**） | **0 / 2 不合规** ✓✓ |
| v33 第一版（错版 ✗） | **2 / 2 不合规** ✗（**灵敏度已证** ✓✓） |
| `pixel-schematic-v33.fzz`（最终 ✓） | **0 / 2 不合规** ✓✓ |

✗✗ **这份核对器自己也差点"自证"** ✓（记下来 ✓）：第一版把"**终止在脚上的那根线**"**整根豁免** ✗
⇒ 错版照样报 ✓✗（= `AGENTS §5b` 那条"不许自证"又吃了一次 ✓）。
⇒ 改成**只豁免脚周围 1 单位**那一小截 ✓ ⇒ 才把错版抓出来 ✓✓。

#### ★★ 正确的形态是**量**出来的 ✓：两个符号都挂在「**整张网上挑出来的点**」✓

把用户手改版两个符号的坐标与它们连的线摊开 ✓：

```
Ground1 脚 (210.578, 27.000) ← 引线 (210.578, 17.000) → (210.578, 27.000)     竖直、从上面下来 ✓
Ground2 脚 (161.328,153.000) ← 引线 (161.328,143.961) → (161.328,153.000)     竖直、从上面下来 ✓
```

⇒ 两条**都是竖直的** ✓、都是**往下挂** ✓；而且**一个在 B 区**（`U1`/`LED2` 那一侧 ✓）、
**一个在 A 区**（`D3` 那一侧 ✓）—— 与那两个 `GND` 标签想说的"**A/B 各自的地**"是同一件事 ✓。

★★ 由此得到一条**反直觉的结论** ✓：**地网根本不用切** ✗ —— Fritzing 的 `LocalGrounds`
把全图 `GND/VSS/GROUND` 的脚拉成**一张**网 ✓（依据见 `sch_net.py` 里那段源码笔记 ✓）
⇒ 两个符号**不必用线相连**也同网 ✓ ⇒ "每个模块各摆一个符号"在电气上仍是一张地网 ✓✓。

#### 实现（三处 ✓，各司其职 ✓）

1. **`sch_net.py`**：加 `ground_geom()`（脚位**反解** ✓）、`ground_box()`（本体盒 ✓ ——
   ✗ 原来写在渲染器里 ✗ ⇒ **搬过来** ✓，判据与生成器**同一份** ✓）、`is_ground_net()`（哪些网是"地" ✓，
   与脚名判据**同一份** ✓）。
2. **`gen_schematic_wires.py`**：`--ground=<网>` ✓ + `ground_spots()`（**挑点** ✓）+
   `emit()` 里挂 ✓。挑点口径 ✓：候选 = 该网**导线的端点** ✓（脚上的点跳过 ✗）；
   只**往下**挂 ✓；违例 = 引线压线 / 交叉 ✓ + 引线蹭脚（< `CLEAR_PIN` ✓）+
   **符号被线穿** ✓ + 符号压元件本体 / **元件的文字** ✓ + 压已放好的标签 ✓；
   **每个功能模块各取一个** ✓（先取违例少的 ✓、再取离本模块的脚近的 ✓）。
   挂法 = **延长那根线** ✓（若它的端是竖直、从上方下来、且没人用 ✓）或**加一小段竖直引线** ✓。
   ★ 地网**不参与 `NL1/NL2` 的切** ✓（`--ground` 点名的网直接跳过 ✓）。
3. **`render_sch.py`**：本体盒改调 `sch_net.ground_box()` ✓。

★ **两条弯路也是数据定的** ✓✗（记下来 ✓）：① **挂在切口上** ✗（见上 ✓）；
② 第一版挑中 B 区那个点后，实测**压住 `C2` 的 `100 nF`** ✗（图上就是"符号的横线把 `100` 划掉" ✗）
⇒ 障碍里补上**元件文字** ✓（`sch_text.label_bbox` ✓，与 `relabel()` **同一份** ✓）⇒ 立刻换到干净点 ✓。

#### 挑出来的点，**与用户那两个同位置** ✓✓（模型对不对，这就是证据 ✓）

| | 用户手改版 **v32** ✓ | **规则生成 v33** ✓ |
|---|---|---|
| B 区 | (210.578, **27.000**) | (210.578, **26.000**) ✓ —— 同一条竖线、同一个结点往下 9 ✓ |
| A 区 | (161.328, **153.000**) | (161.328, **166.800**) ✓ —— **同一个 x** ✓（他当时把底轨挪到 y=143.961 ✓；规则版底轨在 y=157.8 ✓ ⇒ 都离轨 9 ✓） |

#### ★★ ③ **剪冗余 ＋ 改接点**（`--trim=5V,GND` ✓，用户点的两项 ✓）

★ 判据都**从几何读** ✓（不看标志位 ✗），口径写在 `trim_plan` 的文档串里 ✓：

| 要做的 | 判据 ✓ |
|---|---|
| **删一根线** | 删完 **终端分块一模一样** ✓（终端 = 脚 / 网标签脚 / 接地符号脚 ✓；比“整张网还连通”更严 ✓ —— 它同时挡住“把 `NL2` 切开的两个模块又接回去”✗ 与“把某个终端甩掉”✗）＋ **不留悬空线端** ✗ |
| **改接一个点** | 只动“**一端是终端、另一端是结点**”的支线 ✓ ⇒ 在同网的其它结点里找 ✓；须 **违例 0** ✓（压线 / 交叉 / 蹭脚 / 穿体 / 压标签 / 跨网假接头 / 出界 ✗）且 `长度 + **K_INTER**×交集` **严格更省** ✓（K 就用布线那个 ✓ = 10mm/交集 ✓，不新造尺子 ✓）|

实测（v33 这一版 ✓）：

```
网 5V ：12 根线 ｜ 终端 5 个 ⇒ 一根都不能删 ✓（本来就是树 ✓）；改接 0 处 ✓（7 个候选结点全违例 ✗ / 更省的没有 ✓）
网 GND：23 根线 ｜ 终端 9 个 ⇒ ✂ **删掉 90012770（110.6 单位 = 31.2mm ✓）**：终端分块不变 ✓、不留悬空端 ✓
                              改接 0 处 ✓（13 个候选结点全违例 ✗ —— 如实报出 ✓）
```

★ 净效果 ✓（**独立量** ✓：直接从两个 `.fzz` 求导线长 ✓）：总长 **2532.3 → 2421.7 单位** ✓
（**−110.6 = −31.2mm** ✓，正好就是删掉那根的 ✓）；**悬空导线端 1 → 0** ✓✓ ——
那根冗余线**正好就带着那个悬空端** ✓（v29 起的老毛病 ✓），剪了它**顺手一并解决** ✓。
交叉 **11 → 11** ✓（没变 ✗✓）、其余 0 全部保持 ✓。

✗✗ **这一手撞的坑（记下来 ✓）**：我的“终端”判据忘判 `t[1] is not None` ✗ ⇒ 把 `("pin", None)`
（= 支线远端的**裸端** ✓）当成一只终端 ✗ ⇒ 实测 5V 报出 **10 个终端**（5 真 + 5 假 ✗）、
并且把**轨的中间段**当成“支线”拖去改接 ✗ ⇒ 兜底一验：把 `U1.VDD` **孤立**了 ✗✗。
⇒ ① 修判据 ✓；② 兜底（**整体再验一遍终端分块，变了就全撤** ✓）**真的把错挡住了** ✓✓
—— 两个都要有 ✓：判据要准 ✓，但不能只靠它 ✓。
★ 与 `emit()` 里“同点即连”那条笔记是**同一个坑** ✓（那边写对了 ✓、这边又踩 ✗）⇒ “`("pin", None)` = 裸端点”
  这件事实只有一处说得清 ✓ ⇒ 以后凡读 `start_tgt`/`end_tgt` 一律这么判 ✓。

#### 指标（**同一套判据** ✓）

| | v32（手改 ✓） | **v33（规则生成 ✓）** |
|---|---|---|
| ① 网表 | 9 网全对 ✓ | 9 网全对 ✓（其中 **4 只地脚**按 `LocalGrounds` 并网 ✓） |
| ② (A) 假连线 ｜ (B) | 0 ｜ 0 ✓ | **0 ｜ 0** ✓ |
| ④ 被穿旗标 | 0 / 2 ✓ | **0 / 2** ✓ |
| 十字交叉 | 11 | **11** ✓ |
| 穿元件本体 ｜ 压线 | 0 ｜ 0 ✓ | 0 ｜ 0 ✓ |
| **接地符号几何**（**独立核对** ✓ `check_grounds.py` ✓） | 0 / 2 ✓ | **0 / 2** ✓ |
| 导线根数 ｜ **总长**（同一口径、独立量 ✓） | 47 ｜ 1965.6 单位（554.7mm）✓ | 51 ｜ **2421.7 单位**（683.5mm）✓（剪前 2532.3 ✓，去掉 110.6 ✓） |
| 悬空导线端 | 0 ✓ | **0** ✓✓（没剪之前是 1 ✗，见上 ✓） |
| 贴脚（可读性 ✓） | 0 ✓ | **1** ✗（**v30 起就有** ✗，见“遗留”✓） |
| 画布 | 104.1 × 90.6 mm | 105.8 × 94.5 mm |

★ **只有总长这一项规则版比手改版长** ✗（2421.7 vs 1965.6 单位 = **+129mm** ✗）——
那是**布线形状**的差别 ✓：他手改版在 v30 基础上**删 4 根、加 2 根、改短 4 根** ✓
（见第二十五/二十六手 ✓），而规则版的“轨 ＋ 每脚一条 L 形支线”本身就是那个长度 ✓。
⇒ 这一项**不是 `--trim` 能补的** ✗（`--trim` 已经把那根 110.6 的冗余线剪掉了 ✓；
再剪就要**换形状** ✗ = 另一手的事 ✓，记账 ✓）。

<table>
<tr>
<td></td>
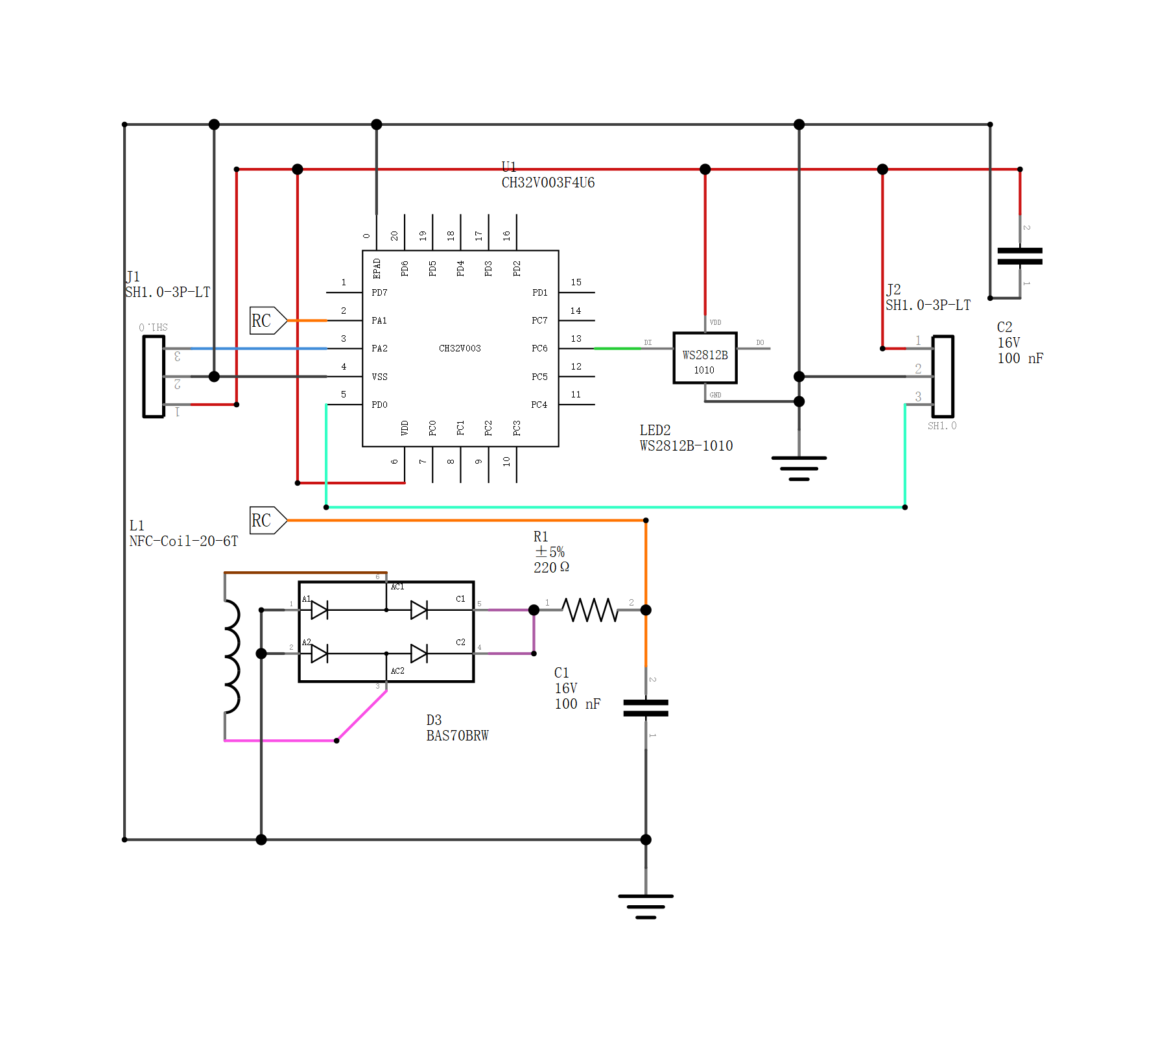
[picture p27: hardware/pixel/pixel-schematic-v33_preview.png]
<td></td>
</tr>
<tr>
<td><b>v32</b> ✓ 用户手改（两个接地符号是他放的 ✓）</td>
<td><b>v33</b> ✓✓ <b>整张图由规则生成 ✓</b>（两个接地符号也是挑出来的 ✓、位置与他那两个几乎重合 ✓）</td>
</tr>
</table>

#### 复现（**整条链都是规则** ✓，实测可复现 ✓）

```
py -3.13 gen_schematic_layout3.py pixel-schematic-v5.fzz _work/layoutA.fzz --pins=pins_ref.py --socket=4
py -3.13 render_sch.py _work/layoutA.fzz _work/layoutA.png          # 出“尺子”（+ .svg ✓）
py -3.13 gen_schematic_wires.py _work/layoutA.fzz _work/layoutA.svg pixel-schematic-v33.fzz \
    --orig pixel-schematic.fzz --ratio 1.0 --rip 3 --rails \
    --modules=L1,D3,R1,C1 --label=RC,GND --ground=GND --trim=5V,GND
py -3.13 check_netlist.py    pixel-schematic-v33.fzz     # ① 9 网全对 ✓
py -3.13 check_fake_wires.py pixel-schematic-v33.fzz     # ② (A)=0 (B)=0 ✓
py -3.13 check_flags.py      pixel-schematic-v33.fzz     # ④ 被穿旗标 0/2 ✓
py -3.13 check_grounds.py    pixel-schematic-v33.fzz     # ⑤ 接地符号几何 0/2 不合规 ✓
py -3.13 render_sch.py       pixel-schematic-v33.fzz pixel-schematic-v33_preview.png
```

- **摆位那一步逐字节可复现** ✓✓（`_scratch/fzz_same.py`：**26/26** 条目相同 ✓）；
- ★ 顺手发现 `_work/layout11.svg` 是**旧的** ✗（它里面 `R1` 的文字还是 `220` ✓，现在是 `220Ω` ✓）
  ⇒ 用**新尺子**重跑，结果**逐字节一致** ✓（那条差异只在**文字**里 ✓，不影响判据 ✓）；
- ★★ **不给 `--ground`/`--label` ⇒ 输出与已入库 v29 逐字节相同** ✓✓（26/26 ✓）
  —— "**零 = 不生效**"守住了 ✓。
  ★ 2026-09-30 **多了 1 处故意的差异** ✓（已在第二十九手量清 ✓）：修掉“位号盒少算上下留白”那个 bug 之后 ✗，
    **5 个位号**按**修正后**的盒子重算 ✓（`J1`/`J2`/`L1`/`U1` 各挪 **−4.75 单位** ✓、`R1` 换了个落点 ✓）；
    `_scratch/fzz_diff.py` 同口径比对：**62 个实例 0 个不同** ✓（差异只剩 `titleGeometry` 那 **3 字节** ✓）。

#### 遗留（**不在这一手范围内** ✗，记账 ✓）

- ~~**悬空导线端 1 个** ✗~~ ⇒ **已解决** ✓✓：剪掉那根冗余线（`90012770` ✓）之后
  **悬空端 1 → 0** ✓（它就在那根线上 ✓）；**v29 起的老毛病结了** ✓。
- **贴脚 1 处** ✗：`Wire90012730` 蹭 `RC.connector0` **3.0 单位 = 0.85 mm** ✓ ——
  **v29 是 0** ✓、**v30 起变成 1** ✗（= 标签/切分那一手带进来的 ✓，不是这一手 ✓）；**未动** ✗。
  ⇒ ~~**已解决**~~ ✓✓：**第二十八手** 的 ②（支线代价按整条算 ✓）把它一并去掉了
  （那根线在“改接”时正好被换掉 ✓）⇒ **v34 贴脚 0** ✓。
- **改接点一处都没找到** ✓：不是没做 ✓，是**每个候选结点都违例** ✓（`5V` 7 个 / `GND` 13 个 ✓，
  已逐条打印 ✓）—— 这正是“符号/轨”那套形状的代价 ✓：引脚附近没有不蹭脚的落点 ✓。
  ⇒ ~~没找到~~ ✓：根因是**判据自己的 bug** ✗（见第二十八手「引线蹭脚」那一段 ✓）——
  修好口径后 **v34 真的找到并改接了 1 处** ✓（`135.2 → 79.2` 单位 ✓）。
- `RC` 标签在规则版里是 **0°** ✓（用户那版是 90° / 180° ✓）；文字都**正着** ✓，只是朝向不同 ✓。
  ⇒ ~~朝向不同~~ ✓：**180° 已开放为候选** ✓（第二十八手 ✓，用户实测截图证明那字是正的 ✓）
  ⇒ **v34 那两个 `RC` 一个 0°、一个 90°** ✓（各自的“最省且违例 0”的落点 ✓）。
- ★ **通用规则已写** ✓（用户 2026-09-30 同意 ✓）：那两条（“符号类元件挂在网上挑出来的点、往下挂、不许被线穿” /
  “地网不必切：`LocalGrounds` 自己会并”）已写进**跨项目**的
  `fritzing-parts-langhua/docs/schem-drawing-rules.md` **B3.1.2** ✓（与 `B3.1.1`「标签是一个元件」并列 ✓）——
  正文在那边 ✓，本节只留这条指针 ✓（`AGENTS §11` ✓）。

### 第二十八手：**标签就近贴本侧引脚** ＋ **支线代价按整条算** ＋ **成组删冗余** ⇒ **v34**（2026-09-30 ✓ 用户定 ✓）

缘起 ✓：v33 入库后用户**手改了一版** ✓ 并要我核 ✓ —— 核出来**他那版全面更好** ✓
（总长 **−486.9 单位**、交叉 **8 vs 11** ✓、贴脚 **0 vs 1** ✓、悬空端都是 0 ✓）
⇒ 我提了三处该补的口径 ✓，用户一句「**好的，实现**」✓ ⇒ 这一手 ✓。
（核的手法是**逐实例对账** ✓ 而不是“看着差不多” ✓：`_scratch/fzz_diff.py` 按 `modelIndex`
比几何/属性 ✓，找出他真正动过的 4 处 ✓ —— 也正是那 3 条口径的由来 ✓。）

#### ① **成组删**冗余 ＋ 级联清悬空端 ✓

✗ 原来逐根试删 ✗、而且要求“**每删一根都不留悬空端**” ✗ ⇒ 找不到“**一整块回路一起删**” ✓
（用户删掉 GND 左侧回路 = `229.8+110.6+44.0+28.8 = 413.2` 单位 ✓ —— 单删任何一根都会先留下悬空端 ✗）。
✓ 现在：**允许中途留悬空端** ✓，删完**级联清理** ✓（每步单独验终端分块 ✓、收尾再整体验一遍 ✓）。

★ 这一手差点删不动 ✓：那三根线是 `D3.c0/c1 ＋ C1.c1` **唯一**的线路径 ✗，
但两侧各有一个**接地符号** ✓ —— 而 Fritzing 的 `LocalGrounds` 让它们**本来就同网** ✓
⇒ **电气上没断** ✓ ⇒ 得让 `--trim` 认得这条语义 ✓（否则它会一直判“删了就断”✗）
⇒ 把 `--trim` 的位置**挪到“标签/接地符号都挂完之后”** ✓✓（这条与第二十七手那条
“地网不必切”是**同一件事实**的两面 ✓）。

#### ② 支线代价改成「**整条支线**」✓

✗ 原来拿“**新整条路径**的长度”比“**旧路径里带脚的那一片**” ✗ ⇒ 实测把用户那个改接
（**135.2 → 79.2** ✓ 省 56 单位 ✓）**误判成更贵** ✗ 而拒掉 ✗。
✓ 现在：从那只脚出发 ✓ 沿“**度 2 的结点**”一路串到**第一个分叉点** ✓ ⇒ 拿**整条**比 ✓；
比较键 = **`(违例数, 长度)` 字典序** ✓ ⇒ 正是用户原话“**不违反任何规则 ＋ 节省线长**” ✓
（违例更少时允许**略长** ✓ —— 实测他那根被删的竖线**正贴着 `RC` 标签** ✗，消掉它比省几单位更重要 ✓）。
⇒ 实测 v34：`5V` **真的改接了 1 处** ✓（`135.2 → 79.2` ✓）—— 这一手把**第二十七手
“改接点一处都没找到”**那条遗留一并结了 ✓✓。

#### ③ 标签**就近贴本侧引脚** ✓ ＋ 挪位后的断头清理 ✓

✗ 原来标签一律贴在**模块边界的断口**上 ✗ ⇒ 本侧“为了够到断口”的那一长段就白留了 ✗
（实测 `RC` 的 A 侧为了够到断口走了 **143.7 单位** ✗）。
✓ 现在：候选 = **本侧所有导线端点** ✓，按“**离本侧的脚最近**”排 ✓；
再在 **4 个外推方向 × 7 档距离 × 4 个朝向**里搜 ✓（挑选键 `(违例数, 结点远近, 方向, 距离, 朝向)` ✓）；
挪完把**空出来的那一截**当断头清掉 ✓（`prune_dangling` ✓）。

★★ **180° 是用户实测推翻我旧结论** ✓✗（记下来 ✓）：我 2026-09-29 在生成器里写过
“**不许 180°** ✗，因为会把字倒着写”✗ —— **那条是错的** ✗；用户 2026-09-30 直接
截了 Fritzing 里的图 ✓：**字是正的** ✓。真相是 Fritzing 对标签文字**自动摆正** ✓
（`NetLabel::makeSvg`：`bool reversed = (transform().m11() < -0.5);  // horizontal flip or 180°` ✓），
而**同一件事实**我在 `render_sch.py` 里**早就写对了** ✓✗ —— 同一件事**两份口径**、
一边对一边错 ✗ ⇒ 教训与“一件事一份实现”是**同一条** ✓。
★ 180° 还是**唯一**能把旗标摆到接线点**右侧**的手段之一 ✓（脚在尖端那侧 ✓）——
用户手改版就是用它把标签贴在引脚旁的 ✓。

#### 修掉的两个**真 bug** ✓✗（都不是审美问题 ✓、而且**五道判据全绿也没拦住** ✗）

1. **“引线蹭脚”把引线**自己出发的那只脚**也算进去了** ✗ ⇒ 距离**恒为 0** ✓
   ⇒ **每条带引线的候选都白背 1 个违例** ✗ ⇒ “贴在本侧引脚旁边”的候选**全被否掉** ✗、
   只能退到 28.8 单位外的结点 ✗ —— 这正是用户手改版能贴在引脚旁、生成器做不到的原因 ✓。
   修：**自己那只脚排除** ✓（容差 = 全仓统一的 1 单位 ✓）。
2. **级联清断头把挂着真脚的线也吃了** ✗：判据只要求“**一端是叶子**” ✓ 而没看另一端 ✓
   ⇒ 实测把 **`R1` 那只脚唯一的那根线**删掉 ✗ ⇒ 那只脚被孤立 ✗、**标签浮空 11.5 单位** ✗✗
   —— 而 ① 网表 ② (A)/(B) ④ ⑤ **全绿** ✗（`check_netlist.py` 也没报 ✗）。
   ★ **是另写的一份只读核对器量出来的** ✓✓：`_scratch/lbl_touch.py`
   （直接读 `.fzz` ✓、算每个标签**画出来的脚**到最近导线的距离 ✓，不调生成器任何代码 ✓）
   ⇒ 修三处 ✓：① 挂着真终端的线**一律不删** ✓；② 候选要过「丢掉的这一截**不会孤立真脚**」✓
   （`dead_end_pin` ✓：从旧断口沿度 2 结点走 ✓，走到**真脚**就否掉这个候选 ✓ —— 而“顺着同一条链
   挪近一点”不算危险 ✓，所以落点是 `_end` 不是 `_q2` ✓）；③ 清完之后**端点正压在脚/标签上的当场补连接** ✓
   （✗ 否则就是“看着接上其实没接” ✗ —— 判据 ② 的 `(B)` 正好抓住它 ✓，当时实测 `(B)=1` ✗）。

#### 用户对着截图提的两点 ✓（都在这一手内解决 ✓）

**问题 1「`U1.2` 接 `RC`，`RC` 本体压在了 `U1` 上，这没有违规吗？」** ✓ —— 问得对 ✓：
**那本来该是违规** ✓，是我这边漏了一条 ✗ —— 标签是“一个元件” ✓（`B3.1.1` ✓），
可我挑位置时只查了 **导线 / 别的标签 / 引脚** ✗、**没查元件本体框** ✗
（用户手改版那只 `RC` 落在 `(176.48,81.00)` ✓ = **就在 `U1` 方框里** ✗）。
✓ 现在：标签对**任何元件本体**都要留 `CLEAR`（**6.0 单位 ≈ 1.7mm** ✓，与“导线离元件本体”**同一条** ✓
—— 不是 0 ✗：贴着边框看着仍旧是“压住”✗）。

**问题 2「红色线上多了一个接线点」** ✓ —— 根因是**我自己上一轮的动作** ✗：
`② 改接` 把 5V 那条长横线**切成了两段共线的线** ✗
（`(29.78,-57.6)→(49.38,-57.6)` ＋ `(49.38,-57.6)→(180.38,-57.6)` ✗），
Fritzing 就在那个**切口**上画了一个小圆点 ✓；用户手改版那条是**一整根** ✓ ⇒ 没有点 ✓。
✓ 现在：**很保守的“共线合并”** ✓ —— 同网 ✓ ＋ 那一点上**恰好只有两个线端** ✓ ＋
两边方向**严格反向**（叉积≈0 ✓、点积<−0.999 ✓）⇒ 才并 ✓；**折角一律不动** ✓
（手改版里 16 个折角接头原样保留 ✓）。实测 5V：`19.6 ＋ 131.0 ⇒ **150.6 单位一根**` ✓、那个点消失 ✓。
★✗ **第一版没排除“真终端”** ✗ ⇒ 它把标签那截引线并进了宿主线 ✓，
而那个接头**正是 `R1` 的脚** ✗ ⇒ 并进去 = 让线**穿过**那只脚、脚上没有线端了 ✗
⇒ 判据 `(A)/(B)` 当场各报 1 ✗ ⇒ 补上「**合并点上不许有真脚 / 标签**」✓ 才对 ✓。
★ 另外整块只在**带开关**（`--label/--ground/--trim` ✓）时才跑 ✓ ⇒
**“不给开关 ⇒ 输出与已入库 `v29` 逐字节相同”** 仍然成立 ✓✓（实测 **26/26** ✓）。

#### 指标（**同一套判据** ✓ ＋ 两份独立只读核对 ✓）

| | v33（上一手 ✓） | 用户手改版 ✓ | **v34（本手 ✓）** |
|---|---|---|---|
| ① 网表 ｜ ② (A) ｜ (B) | 9 网 ✓ ｜ 0 ｜ 0 | 9 网 ✓ ｜ 0 ｜ 0 | 9 网 ✓ ｜ **0 ｜ 0** ✓ |
| ④ 被穿旗标 ｜ ⑤ 接地符号几何 | 0 / 2 ｜ 0 / 2 ✓ | 0 / 2 ｜ 0 / 2 ✓ | **0 / 2 ｜ 0 / 2** ✓ |
| 导线根数 | 51 | 46 | **46** ✓ |
| **总长**（独立量 ✓） | 2421.7 单位（683.5mm） | 1934.8 单位（546.0mm） | **1941.0 单位**（547.8mm）✓ |
| 十字交叉 | 11 | 8 | **8** ✓ |
| 贴脚（可读性 ✓） | 1 ✗ | 0 ✓ | **0** ✓✓ |
| 悬空导线端 | 0 ✓ | 0 ✓ | **0** ✓ |
| 画布 | 105.8 × 94.5 mm | 104.1 × 94.5 mm | **104.1 × 94.5 mm** ✓ |
| 标签脚到最近导线（独立量 ✓ `lbl_touch.py` ✓） | — | 0.000 ✓ | **0.000 ✓（2/2）** |
| 接线点（独立量 ✓ `junct.py` ✓） | — | 9 处 ✓ | **9 处** ✓（那一处多余的已合掉 ✓） |

⇒ 相对 v33：**总长 −480.7 单位（−135.7mm、−19.9%）** ✓、交叉 11 → **8** ✓、贴脚 1 → **0** ✓。
⇒ 相对用户手改版：**导线根数持平** ✓、交叉持平 ✓、贴脚持平 ✓、接线点数持平 ✓；
**总长多 6.2 单位** ✓ —— 那是**为了不压 `U1` 本体**把 `RC` 标签从“引脚旁那个点”挪出去换来的 ✓
（见问题 1 ✓）；**这一项是用户点名的取舍** ✓。

#### 复现（**整条链都是规则** ✓）

```
py -3.13 gen_schematic_wires.py _work/layout11_check.fzz _work/layout11_check.svg pixel-schematic-v34.fzz \
    --orig pixel-schematic.fzz --ratio 1.0 --rip 3 --rails \
    --modules=L1,D3,R1,C1 --label=RC,GND --ground=GND --trim=5V,GND
py -3.13 check_netlist.py    pixel-schematic-v34.fzz     # ① 9 网全对 ✓
py -3.13 check_fake_wires.py pixel-schematic-v34.fzz     # ② (A)=0 (B)=0 ✓
py -3.13 check_flags.py      pixel-schematic-v34.fzz     # ④ 被穿旗标 0/2 ✓
py -3.13 check_grounds.py    pixel-schematic-v34.fzz     # ⑤ 接地符号几何 0/2 不合规 ✓
py -3.13 render_sch.py       pixel-schematic-v34.fzz pixel-schematic-v34_preview.png
```

<table>
<tr>
<td></td>
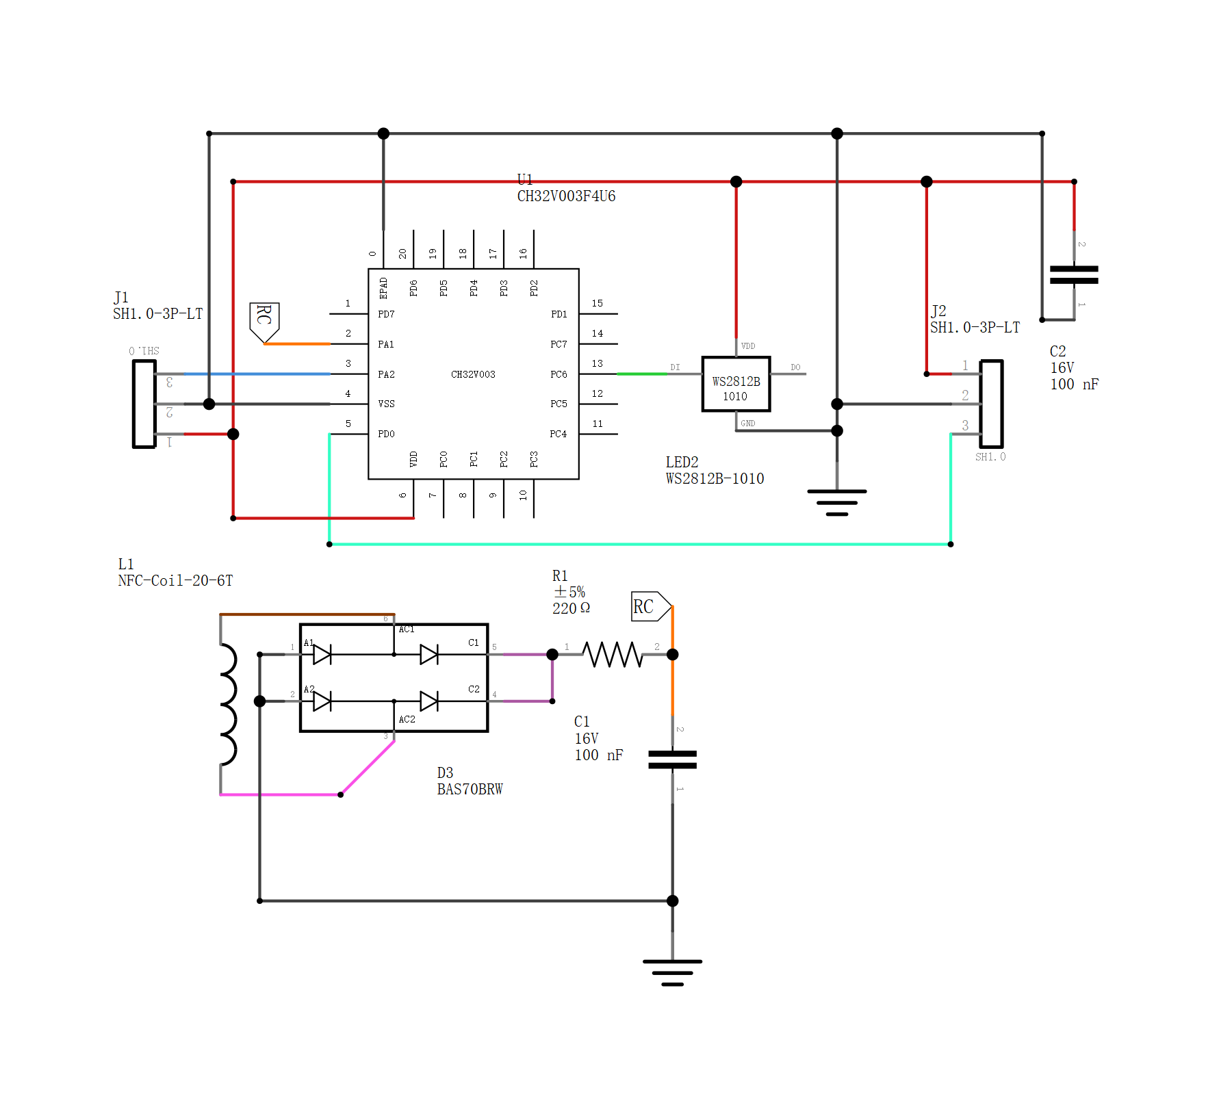
[picture p28: hardware/pixel/pixel-schematic-v34_preview.png]
<td></td>
</tr>
<tr>
<td><b>v33</b> ✓（51 根 / 683.5mm / 交叉 11 / 贴脚 1 ✗）</td>
<td><b>v34</b> ✓✓（46 根 / 547.8mm / 交叉 8 / 贴脚 0 ✓；标签就近、无多余接线点、不压元件）</td>
</tr>
</table>

#### 遗留（**不在这一手范围内** ✗，记账 ✓）

- ⚠ **位号 `U1` 压导线**（`Wire90012735` ✓）：**v29 起的老毛病** ✗、这一手**未动** ✗
  （渲染器每次都如实报 ✓）；正解见前面「位号摆位」那一节（**布完线再重摆位号** ✓ = 另一手 ✓）。
- ★ 这一手真正的新增“守门员”是**两份只读核对器** ✓（`_scratch/lbl_touch.py` ✓ / `_scratch/junct.py` ✓）：
  它们各量一件事 ✓（标签脚是否真落在导线上 ✓ / 接线点与 T 形 ✓），**不调生成器** ✓
  ⇒ 上面那两个真 bug 就是这么量出来的 ✓。**要不要收进 `tools/` 入库**，等用户定 ✓（现在还在草稿目录 ✓）。

### 第二十九手：**两份独立核对器入库** ＋ **`--relabel` 布完线重摆位号**（2026-09-30 ✓ 用户定 ✓）

#### ① 两份核对器入库 ✓（⑥⑦ ✓，都是**只读** ✓、都带**拒判** ✓）

| 文件 | 查什么 ✓ | 为什么非它不可 ✗ |
|---|---|---|
| `check_label_touch.py`（**⑥** ✓） | 每个网标签**画出来的脚**到最近导线的距离必须 ≤ 0.05 ✓ ＋ 它的 `<connect>` 必须正好指向那根 ✓ | v34 开发中实测：**标签浮空 11.5 单位** ✗（给标签新拉的引线被“清断头”删了 ✗）—— 而 ① 网表 ✓ ② (A)/(B) ✓ ④ ⑤ **全绿** ✗，因为**没人量“标签的脚到导线的距离”** ✗ |
| `check_junctions.py`（**⑦** ✓） | 某点恰好两个线端、两线**严格反向** ⇒ **共线切分** ✗（退出码 1 ✓）；T 形 / ≥3 端口的真分叉只当参考 ✓ | 用户指着截图说「**红色线上多了一个接线点**」✗ —— 根因是“改接”把长直线切成两段共线 ✗；这条**没有别的判据管** ✗ |

★ **灵敏度都证过** ✓（不是“反正它没报” ✗）：
- ⑥ 拿**历史版本**验 ✓：`pixel-schematic-v30.fzz`（当时四个标签全断 ✗）⇒ **4/4 全部报浮空** ✓（10.7 / 18.1 / 4.4 / 9.4 单位 ✓）⇒ 退 1 ✓；v33 / v34 ⇒ 0.000 ✓ ⇒ 退 0 ✓；
- ⑦ 拿**人造文件**验 ✓：`_scratch/split_one.py` 把 v34 那根长 5V 线从中间**切成两段共线** ✗ ⇒ ⑦ 当场报 ✗ 退 1 ✓、而 ⑥ 在同一文件上仍退 0 ✓（各管各的 ✓）。

★★ ⑦ 的判据也**修正过一次** ✗✓（记下来 ✓）：第一版把**落在引脚上的接头**也算成“多余” ✗
—— 实测 `R1` 脚上“引脚 ＋ 两根共线的线”被判违规 ✗，可那是**正常交汇** ✓（Fritzing 在那里画点
本来就对 ✓）。⇒ 判据补上「**连接伙伴的 layer 不是 `schematicTrace`** ⇒ 那一端落在**脚**上 ⇒ 豁免」✓
（口径与生成器 `add_conn` 同一条 ✓）。修完 v34 与用户手改版**完全同构** ✓：
`58 接头 = 34 落在脚上 ＋ 15 折角 ＋ 9 真分叉` ✓✓（两版逐项相同 ✓）。

#### ② `--relabel`：布完线再拿**最终导线**当障碍摆一遍位号 ✓（**默认关** ✓）

用户定的思路 ✓：**位号可以自由挪 ✓、导线挪一次要牵动全局 ✗**。

- `relabel()` 本来就在跑 ✓，但它在 **`emit()` 之前** ✗ —— 那时只有“**计划的**导线” ✗，
  而 `emit()` 里导线**还会变**（标签引线 / 改接的新线 / 接地引线 / 共线合并 ✓）
  ⇒ 实测 `U1` 的位号正好压在新拉出来的一根线上 ✗（渲染器每次都如实报 ✓）。
- ✓ 现在：`--relabel` ⇒ `emit()` 末尾拿**最终导线**当障碍**再跑一遍同一个 `relabel()`** ✓
  （候选位 / 权重 / 判碰全是它那一套 ✓，不另写 ✗）；并给**这一遍**多一圈候选位 ✓
  （`extra=True` ✓）—— 实测 `U1` 的 7 个候选位**全被导线占着** ✗（它上方正好横着 5V 长轨 ✗）
  ⇒ 不给第二圈就只能原地不动 ✗。★ 默认关 ✓ ⇒ **不给开关时输出仍与已入库 `v29` 逐字节相同** ✓✓。

★ 实测 ✓：两遍合计「压导线 **11 → 1 → 0** ✓」（`U1` 那个警告清了 ✓）、压元件 0→0 ✓、压位号 0→0 ✓。

#### ✓ **两把尺子已对齐**（2026-09-30 当天查清 ✓）—— “生成器说 0、渲染器说压了”的根因就是它 ✗

量出来的证据（同一个 `U1` 位号，两边各量一次 ✓）：

| | `U1` 位号盒 ✓ | 差 |
|---|---|---|
| 生成器 `relabel()` 的候选矩形 | 高 **10.00** 单位（`fs × 行数`） | ✗ **自己拼的** |
| 渲染器（与 `relabel()` 的计数、`check_*` 一样） | 高 **14.75** 单位（`ST.label_bbox` ✓） | ✓ 含上下留白 |
| `R1` 本体盒（两边**完全一致** ✓） | `(125.33,80.40→161.33,87.60)` | — |

⇒ 差的 **4.75 单位**（≈1.3mm）正好让 `U1` 的位号**擦到了 `R1` 的本体盒** ✗，
而生成器因为盒子矮一截、判“没压” ✗ ⇒ 它把那个位置当成了最优解 ✗。
★ 教训与「一件事一份实现」**同一条** ✓：**判碰用的矩形只能有一份** ✓ ——
一个概念（位号盒）在两个地方各拼一次 ✗，形状就会不一样 ✗，判据就会“两边各说各的” ✗。

★ **顺带把“不给开关 = 与 v29 逐字节相同”那条说明改准** ✓（同一件事的另一面 ✗）：
那遍 `relabel()` 是**无条件跑**的 ✓ ⇒ 盒子改正后，**5 个位号**按修正后的盒子重算 ✓
（`J1`/`J2`/`L1`/`U1` 各 **−4.75 单位** ✓、`R1` 从 `(125.33,56.95)` 换到 `(168.53,79.15)` ✓）；
把它当“漂移”就错了 ✗ —— 同一口径量过 ✓：**62 个实例 0 个不同** ✓，差异只剩 `titleGeometry` ✓
（`.fz` 只差 **3 字节** ✓）。⇒ 这是**故意的、已量清**的修正 ✓，不是回归 ✓。

✓ 修法（**一处** ✓）：`relabel()` 的候选矩形改成**反推 `ST.label_bbox()`** ✓
（`label_bbox(x, y − 0.25fs, fs, ln)` 的**上缘正好是 y** ✓ ⇒ “盒左上角 = `(x, y)`”这个对外语义没变 ✓，
所以 `extra` 那一圈候选位的算法一字未动 ✓）。修完实测：

- 生成器眼里的 `U1` 盒 = 渲染器眼里的 `U1` 盒 = `(58.58,−87.10→88.55,−72.35)` ✓✓（逐位相同 ✓）；
- 渲染器**一个 `⚠` 都没有了** ✓✓（历代一直挂着的“位号 `U1` 压导线”清零 ✓，也没换来新的“压元件”✗）；
- `--relabel`：动 3 个 ✓ ｜ 压导线 **1 → 0** ✓ ｜ 压元件 0→0 ✓ ｜ 压位号 0→0 ✓。

#### ✓ 交付版 **v35** ＝ v34 ＋ `--relabel`（2026-09-30 ✓ 用户定 ✓）

```
py -3.13 gen_schematic_wires.py _work/layout11_check.fzz _work/layout11_check.svg pixel-schematic-v35.fzz \
    --orig pixel-schematic.fzz --ratio 1.0 --rip 3 --rails \
    --modules=L1,D3,R1,C1 --label=RC,GND --ground=GND --trim=5V,GND --relabel
py -3.13 check_netlist.py     pixel-schematic-v35.fzz    # ① 9 网全对 ✓
py -3.13 check_fake_wires.py  pixel-schematic-v35.fzz    # ② (A)=0 (B)=0 ✓
py -3.13 check_flags.py       pixel-schematic-v35.fzz    # ④ 被穿旗标 0/2 ✓
py -3.13 check_grounds.py     pixel-schematic-v35.fzz    # ⑤ 接地符号几何 0/2 ✓
py -3.13 check_label_touch.py pixel-schematic-v35.fzz    # ⑥ 标签脚全落在导线上 ✓
py -3.13 check_junctions.py   pixel-schematic-v35.fzz    # ⑦ 无共线切分 ✓
```

★ 几何与 v34 **完全相同** ✓（只改了位号位置 ✓）：46 根 ｜ **1941.0 单位**（547.8mm）｜
交叉 **8** ✓ ｜ 贴脚 **0** ✓ ｜ 悬空端 **0** ✓ ｜ 画布 104.1 × 94.5 mm ✓；
**六道程序判据全 exit 0** ✓，且渲染器**零告警** ✓。

<table>
<tr>
<td></td>
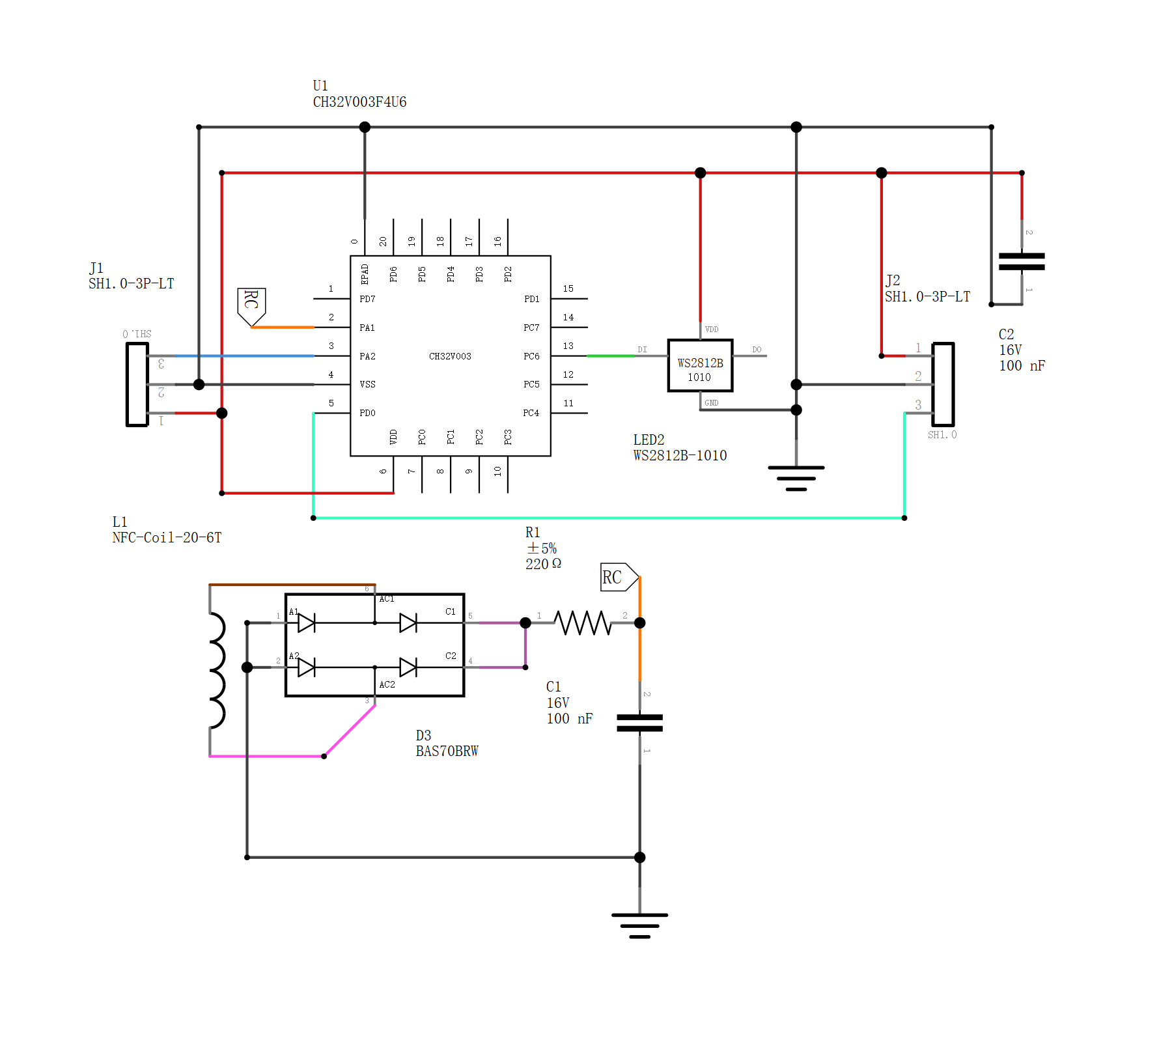
[picture p29: hardware/pixel/pixel-schematic-v35_preview.png]
<td></td>
</tr>
<tr>
<td><b>v34</b> ✓（位号 `U1` 压导线 ⚠）</td>
<td><b>v35</b> ✓✓（`--relabel` 后**零告警** ✓；几何一字未动 ✓）</td>
</tr>
</table>

### 第三十手：**把用户手改版那一版的“省法”写成规则** ⇒ **下一手落地 ✓**（2026-09-30 ✓，⏳ 待实现 → **见第三十一手 ✅**）

#### 起因 ✓：用户核完 v35 又手改了一版（`pixel-schematic-v35_byHand.fzz` ✓，**不入库** ✓）

同一套判据量的 ✓（六道 ✓）：

| | 导线 | 总长 | 交叉 | 贴脚 | 悬空端 | 判据 |
|---|---|---|---|---|---|---|
| v35（规则生成 ✓） | 46 | 1941.0（547.8mm） | 8 | 0 | 0 | 全 exit 0 ✓ |
| **用户手改 ✓** | **45** | **1836.3**（518.2mm） | **7** | **1** ✗ | 0 | ⑥ **exit 1** ✗（标签差 0.134 单位） |

⇒ **−104.7 单位（−29.6mm、−5.4%）** ✓、交叉 8→7 ✓。

#### ★★ 省下来的长度**出在哪**（逐线按网量的 ✓，不是猜的 ✓）

| 网 | 手改 | v35 | 差 | 是哪几根线 ✓ |
|---|---|---|---|---|
| **GND** | 812.2 | 879.6 | **−67.4** | `90012763` **整根删掉**（55.8 ✓）＋ `90012762` 缩到 0（9.6 ✓）＋ `90012767` −2.0 |
| **5V** | 525.6 | 546.8 | −21.2 | `90012738` 44.2→18.4（改成 45° 斜线 ✓）＋ `90012734` +4.6 |
| **RC** | 35.6 | 51.8 | −16.2 | `90012777` 19.4→9.5 ＋ `90012779` 14.4→8.1（标签那两段的宿主线各缩一截 ✓） |
| 其余 6 个网 | — | — | 0.0 | 一根没动 ✓ |

#### ★★ 而它背后的**几何事实**（从两个文件的坐标反推 ✓）—— 这就是要写的规则 ✓

- 两条电源轨相距 **27 单位**；`C2` 两只脚相距 **27.4 单位** ✓
  ⇒ **`C2` 本来就能“站”在两条轨之间、两只脚各自落在一条轨上** ✓✓
  （实测手改版：GND 脚**正在**轨上 ⇒ 支线 **0.0** ✓；5V 脚到另一条轨 18.4 的对角线 ✓）。
- v35 里 `C2` 却被转了 **180°** ✗（`m11=m22=−1` ✓）、朝反方向站 ⇒ 多出 **65 单位**的 GND 绕行 ✗。

⇒ **规则草案** ✓（下一轮实现，落在**摆位那一层** ✗ —— 因为在布线层挪元件会牵动整套脚位表 ✗）：

> **元件的电源/地脚，应当各自落在它那条轨上** ✓
> 做法：对每只“脚分属两条不同轨网”的元件 ✓，按 **0°/180°** 两个姿态 × 平移（把脚对到轨线 ✓）
> 生成候选 ✓，取**支线总长最小**的那个 ✓；脚距与轨距对不上时**原样不动** ✗（不硬凑 ✗）。

**验收（可量、可对）** ✓：生成器跑出来要与用户那版**几何一致** ✓ ——
`C2` 落在 `(262.8,−72.44)` 且 `0°` ✓、GND 支线 **0.0** ✓、5V 支线 ≈18.4 ✓、
总长 **1836.3** ✓、交叉 **7** ✓；并且**六道判据全 exit 0** ✓（他那版 ⑥ 是 1 ✗ ⇒ 规则版还要**顺带把标签吸到 0.000** ✓、
**不留零长残根** ✓、`C2` 位号别压 `J2` 位号 ✓ —— 这三条是他那版的小瑕疵 ✓，规则版不该继承 ✗）。

#### ★★ 2026-09-30 开工第一步：**上面那个方案不完整** ✗✗（先量再写的功劳 ✓，记下来 ✓）

原方案（“挪件到轨上” ✓）**单独做不到** ✗ —— 因为**轨的位置本身是算出来的** ✗：

| 量什么 ✓ | 结果 ✓ |
|---|---|
| 原始图 `pixel-schematic.fzz` 里有 5V/GND 轨吗 ✗ | **没有** ✗：41 根线**全是 `#404040`**（老黑色 ✓），y=−72 那根**不在里面** ✓ |
| layout（`_work/layout11_check.fzz` ✓）里有导线吗 ✗ | **0 根** ✓（只有元件 ✓）⇒ 轨是**路由器自己造的** ✓ |
| 轨的 y 怎么来 ✓ | **零件包围盒顶 − 28.8** ✓（`U1` 顶 −43.2 ⇒ `−43.2 − 28.8 = −72.0` ✓ 与实测量到的轨 y 吻合 ✓） |

⇒ **矛盾点** ✗：把 `C2` 挪到 y≈−72.4 ⇒ **包围盒顶被它顶上去** ⇒ 轨跟着上移到 **−101.2** ✗
⇒ `C2` 的脚**又不在轨上了** ✗ ⇒ 白挪 ✗。
用户那版之所以成立 ✓，是因为**他是在已经布好线的图上挪件** ✓ —— 轨的位置**已经定死** ✓；
而我的链子是「先摆件 → 后按包围盒造轨 → 布线」✗ ⇒ **重跑一次就跑了** ✗。

⇒ **修正后的方案** ✓（两趟，下一轮实现 ✓）：
1. **第一趟**跑路由 ✓ ⇒ 从 `nets_segs` 里**读出两条轨的线** ✓（口径**不另写** ✗ —— 就用它造出来的那两条 ✓）；
2. **锁定轨** ✓（把这两条线当作**固定靶** ✓），再跑**第二趟**：`--snaprails` 按“脚落在锁定轨上”挪件 ✓ ⇒ 重新布线 ✓；
3. 验收不变 ✓（`C2@(262.8,−72.44)`、GND 支线 0.0、总长 1836.3、交叉 7 ✓）。
★ 换句话说：**“挪件”这条规则必须与“轨钉死”一起做** ✗ —— 否则就是给一个会跑的靶子挪件 ✗。

★★ **同一天的实验把这条路钉死了** ✓（`_scratch/move_c2.py` ✓ + 整条链重跑 ✓，2026-09-30 ✓）：
把 `C2` 按用户那版姿态**直接放进 layout**（`(262.8,−72.4377)` ✓、`transform` 由 180° 改回正向 ✓）
⇒ 重跑 ⇒ **总长 1971.3 单位** ✗（比 v35 的 1941.0 **还差 30.2** ✗）；判据全过 ✓（① ② ⑥ ⑦ + 渲染器零告警 ✓）、
交叉 8 不变 ✓、画布 105.5×94.7 ✓。⇒ **“只挪件”这条路死了** ✗（已量 ✓，别再试 ✗）：
轨随零件箱子跑 ✓ ⇒ 挪完脚还是不在轨上 ✗。
⇒ 唯一可行的是**“先钉住轨、再挪件”** ✓ —— 而且**实现层次定了** ✓：**不用改路由器** ✓，
在**已布好线的图**上收尾 ✓（与 `--trim` / `--relabel` 同一层 ✓）：
① 认出两条轨（同网**最长的直段** ✓）；② 把“**所有脚都在电源/地上**”的件摆到轨上 ✓（0°/180° 两姿态 ✓、取支线最短 ✓）；
③ 脚正好落在轨上 ⇒ **旧支线删掉、直接声明“脚↔轨”相连** ✓（**不留零长残根** ✗ —— 用户那版的小瑕疵 ✗，规则版不继承 ✓）。

#### ⚠ 第三次尝试：**靶子放宽到“整张网”** 也做不成 —— 但量出了一条硬事实 ✓（2026-09-30 ✓）

三处改动都做了 ✓（都想对了 ✓）：① 靶从“轨”放宽到“**整张网的线段**” ✓
（因为用户那只 5V 脚其实是**贴着一条竖引线、留一小截横支线** ✓，不是踩在轨上 ✓ ——
我第一版只认“轨” ✗ ⇒ 正好漏掉这种干净摆法 ✗）；② 补上“**沿线法线退开 k 格**”这一档候选 ✓；
③ 把“不压别的件 / 不穿新身体”从“**选完最优之后**判”改成“**在候选里**判” ✓
（✗ 原来最优那个一被否就**整件放弃** ✗ ⇒ 旁边明明有别的干净落点也不用 ✗）。

结果 ✓：它确实找到了**可行**落点（`C2` 上移到 `(237.38,−32.84)` ✓、未翻转 ✓、支线 **59.1 → 21.6** ✓、
无穿体 ✓、无压件 ✓）—— 但**总长反而 1941.0 → 1991.2** ✗、交叉 **8 → 9** ✗、还多两处贴脚 ⚠。

⇒ ★★ **结论（这条最值钱 ✓，写下来别再犯 ✗）**：「**脚到本网的距离之和**」**不是真实总长的好代理** ✗ ——
  按它调优会**把别的线拖长/拖弯** ✗（这一版实测 +50 单位 ✗）⇒ **这条轴到此为止 ✓**（已回退 ✓，
  代码回到“**做不成就原样不动**”的安全版 ✓；实测带 `--snaprails` 的输出与 v35 **逐条目相同 26/26** ✓）。
⇒ 也说明用户那 **−104.7 单位** 不是“挪一件”能拿到的 ✓：它由**三处局部改动**组成 ✓
  （`C2` 挪位 ＋ 5V 那条改成斜线 ＋ 标签那两段宿主线缩短 ✓），其中**两处是布线器的选择** ✓，不是摆件 ✓。
⇒ 下一步要再省，应当去**布线器**那一层（局部重走 / 换接点 ✓ —— `--trim` 的“改接”就是现成的入口 ✓），
  而不是继续在摆件上叠补偿 ✗（这正是 `AGENTS §0` 那条“**过拟合信号 = 停手信号**”✓）。

#### 他那版的三处瑕疵 ✓（**不学** ✗，但要记得复现时别继承 ✗）

1. `RC` 标签 #2 被拖到离导线 **0.134 单位（0.038mm）** ✗ —— ⑥ 当场报 ✓（**这是 ⑥ 入库后第一次在实战里抓到东西** ✓）；
   同一个根因让渲染器也报「`Wire90012777` 蹭 `RC.connector0` 0.13 单位」✓（**一个根因、两把尺子都报** ✓）。
2. `Wire90012762` 成了 **0.000 单位**的退化导线 ⚠（删 `90012763` 时留下的残根 ✓，声明还接着 `C2.connector1` ✓）。
3. 位号 `C2` 压位号 `J2` ⚠（`C2` 一挪，它的位号跟着过去了 ✓）。

#### ⚠ 第四、五次尝试：**在"标签层"抠那 16.2 单位** —— 都没拿到 ✓（2026-09-30 ✓，先量后写 ✓）

那 **−104.7 单位**逐网拆开是：`GND` **−67.4** ✓（`C2` 的 GND 脚落到轨上 ✓）、`5V` **−21.2** ✓、
`RC` **−16.2** ✓、其余 6 张网 **0** ✓。前面三次动的是"零件摆位" ✗ ⇒ 第四次改从**标签**下手 ✓：

- **实验 1（排序键 ✓）**：量出"标签候选"里**内向（宿主线短）的那个候选违例 = 0 ✓ 是存在的** ✓，
  只是排序键先看"沿轴向外" ✗ ⇒ 把它改成 **先违例少 ✓、再宿主线短 ✓** ⇒
  **总长一动不动（1941.0）** ✗ ⇒ **不是排序键的问题** ✗（结点候选里压根没有"离脚 9.5"这种
  **线中段**位置 ✗ —— 他那版恰恰贴在**两结点之间** ✓）⇒ **已回退** ✓、回退后与 v35 **26/26 逐字节相同** ✓。
- **实验 2（放松阈值 ✓）**：把"**标签的脚不许被别的线贴近**"这一条的阈值临时降到 0.5 单位
  （其余判据一字不动 ✗）⇒ 标签挪到离脚 **14.4** ✓、总长 **1941.0 → 1936.0**（只省 **5.0 单位** ✓），
  而且 ⑥ ✓ 渲染器 ✓ **都还是干净的** ✓ ⇒ **技术上可行 ✓ 但不划算** ✗：
  那条规则是**真实事故**留下来的（标签挪到引脚旁后，另一根线离它的脚只有 **0.85mm** ✗，
  渲染器当场报"贴近不相连的引脚" ✗）⇒ 为 **5 单位（1.4mm）** 丢掉这个真保护 ✗ = 不换 ✓ ⇒ **已回退** ✓。

⇒ **结论（本规则集的局部最优就是 v35 ✓）**：剩下那 **−16.2** 要拿到，必须让标签**贴到导线中段** ✗
（= 给候选集加"沿线滑动"这种**新机制** ✗，收益约 11 单位 = 3mm ✓，风险未知 ✗）；
而 **−67.4 + −21.2** 那两块卡在**轨距**上 ✓（本板 **5V 轨 −57.6 / GND 轨 −72.0 = 相距 15.6** ✗，
而 `C2` 两脚相距 **27.4** ✗ ⇒ 想让它一只脚踩 5V、一只脚踩 GND ⇒ **本体必被轨穿过** ✗）
⇒ 要动就得改**轨的摆法策略** ✓（现在 = 零件包围盒顶 − 28.8 ✓），这是**设计决定** ✗ ⇒ 得用户点头 ✓。

### v5 修的：位号摆位（`sch_text.py` + `gen_schematic_layout3.py`）

✗ 原来位号沿用零件自带的偏移 ✗ ⇒ 实测**压导线 8 处 / 压元件 2 处**（与肉眼看到的一致 ✓）。
✓ 修法：位号默认放**本体上方留一格** ✓，并从 **7 个候选位**里挑"碰撞最少"的那个 ✓
（压元件权 10 ✓、压已放的位号权 5 ✓、长位号先放 ✓ = 大的先占位 ✓）。

★ 要判"压没压到"就得有**文字宽度** ✓ ⇒ 不能估 ✗：`_scratch/adv_measure.py`
用 cairosvg 渲染 + PIL 扫像素**实测** ✓，结果抽成唯一实现 `sch_text.py` ✓。
实测结果有点意思 ✓：**本机没装 DroidSans** ✗ ⇒ cairosvg 退回一个**等宽**字体 ✓，
绝大多数字符步进恰好 **0.5em** ✓，只有 `±` `Ω` 是 **1.0em** ✓
（换机器或装了 DroidSans ⇒ **必须重跑那个脚本** ✓，否则判据不成立 ✓）。
包围盒按**步进之和**算 ✓（比墨迹略宽 ✓ ⇒ 判"压到"**偏保守** ✓）。

**位号压导线这条还没清零** ⚠（v5 剩 **1** 处 ✓、v6 剩 **3** 处 ✗ —— 都是 `L1` 一带 ✓）：
试过“让**布线器**认识位号框” ✗ ⇒ 只降到 2 ✗、还赔上压线 ✗（见下一小节 ✓）⇒ 已回退 ✓。
**正解在另一头** ✓：位号是**可以自由挪**的 ✓，导线不能 ✗ ⇒ 应当**布完线再重摆位号** ✓
（拿已完成导线当障碍重跑一遍摆位 ✓ = 下一手 ✓）。现在先如实报着 ✓ 不硬凑 ✗。

### 已被 Fritzing 自己的导出验平（`--verify-export` ✓）

用户导出 `pixel-schematic-v2_图示.svg` 与 `pixel-schematic-v5_图示.svg` 后逐项对账 ✓
（标定只用两个独立量：比例 = 导线线宽比 ✓、平移只用第一件 ✓）：

| | v2（46 根导线） | **v5**（48 根导线） |
|---|---|---|
| ① 零件 9 件 | Δ ≤ 0.00031 单位（0.00009 mm） ✓ | Δ ≤ 0.00041 单位（0.00011 mm） ✓ |
| ② 导线 | 48/48 配上，Δ ≤ 0.00058 单位（0.00016 mm） ✓ | 48/48 配上 ✓ |
| ③ 位号**位置** | Δ ≤ 0.00072 单位（0.00020 mm） ✓ | Δ ≤ 0.00043 单位（0.00012 mm） ✓ |
| 判定 | **几何与 Fritzing 逐点一致** ✓ | **同左** ✓ |

★ v5 那一条尤其说明问题 ✓：**位号位置是我自己算出来的**（`place_labels()` ✓ 上方留一格 +
候选位挑碰撞最少 ✓），Fritzing 照样按它画出来了 ✓ ⇒ 说明我对 `titleGeometry` 的理解是对的 ✓。

**两处已知差异** ⚠（都量化了 ✓、都不是几何差 ✓）：
1. `R1` 的第二行：我写 `220`、Fritzing 写 `220Ω` ✓（fzp 里只写了 `220` ✓ ⇒ **单位是 Fritzing 补的** ✓）；
2. v5 少 **4 个接点圆点** ✗（半径 0.9 单位 = 0.25mm ✓，纯装饰 ✓）—— 那 4 处都在引脚上、
   汇聚了 3~4 根导线端点 ✓；**真规则我没找到** ✓：试过第 2 条（"端点+中段穿过 ≥ 3" ✓）
   ⇒ v5 变 19 个 ✗、v2 直接 0 个 ✗✗ ⇒ 更差 ⇒ 回退 + **如实记录** ✓（"找不到就照实说 ✓ 不硬凑" ✓）。
   注：v2 的接点是 **25 ↔ 25 完全对上** ✓ ⇒ 差异只在 v5 这种"引脚上多根线汇聚"的几何里 ✓。

### v4 修的两条（都是布线器的“空子” ✗，都已量化 ✓）

1. **导线从元件肚子里穿过去** ✗ —— `path_ok` 对“自己两端的元件”**整个豁免** keep-out ✗，
   而布线器发现了一条**漏洞** ✗：**在元件肚子里走，谁也遇不到 ⇒ 交叉数最低** ✗
   ⇒ 它专挑这种路（实测：一段竖直总线从 `U1` 肚子里穿 **48.5 mm** ✗、还有一段穿 `J1` 9.6 mm ✗）。
   ✓ 修法：自己的本体**只允许在路径两端 10 单位以内**碰 ✓（= "从脚上走出来" ✓）。
2. **keep-out 盒不含引脚线** ✗ —— `body_pts` 跳过了 `class="pin"` ✗
   ⇒ 盒子只框住本体矩形（`U1` 是 63×63 ✓ 而它的引脚线伸到 29.8…116.2 ✓）
   ⇒ 布线器就在 **x=106.13** 竖着走 135 单位、从 **U1 引脚线之间钻过去** ✗
   （视觉上像接上了 ✗ **最容易误导人** ✗）。
   ✓ 修法：把引脚线也算进本体框 ✓（与 `render_sch.py` 的量尺**同口径** ✓）。

★ 修完效果：三个指标**同时**变好 ✓（交叉 8 → 7 ✓、穿本体 7 → **0** ✓、总长 2603 → 2496 ✓）
  —— 不是“用一个换另一个” ✗。

**还可能再美的**（留待下一手 ✓）：位号文字少数几处与导线相压 ✓
（`C2/L1/C1` 的第三行、`J1` 的 `SH1.0-3P-LT` ✓）—— 这个可以完全在摆位脚本里控
（把 `titleGeometry` 的偏移改成"固定放在本体上方" ✓）。

**结论**：长度比 v2 短 **38%** ✓，而**交叉数从 12 降到 8** ✓✓。
★ 注意中间版（只有新摆位、没改布线代价）：**长度虽然最短（2340）✓，但交叉涨到 16** ✗ ——
若不把交叉数放进代价，布线器就会用"多交叉"去换"短" ✗。这正是面包板那边已经学到的：
**交叉数是头号指标** ✓（`bb_route4.py` 的 `长度 + K×交集` ✓，规则正文见库仓
`docs/breadboard-routing-rules.md` ✓）。

### v3 的摆位口径（全部**从数据算** ✓，不拍坐标 ✗）

几何由 `render_sch.py --pins-out` 给出 ✓（**同一个模型** ✓，已对 Fritzing 导出逐点验平 Δ≤0.0004 单位 ✓）：
每条规则都能说出"让哪两个脚同高/同 x" ✓，且**逐条自检报出 Δ** ✓：
`J1.c2↔U1.c2`（DATA_IN ✓）、`LED2.c2↔U1.c12`（LED_DIN ✓）、`J2.c2↔U1.c4`（DATA_OUT ✓）、
`L1.c0↔D3.c5`（COIL_A ✓）、`R1.c0↔D3.c4`（BR+ ✓）⇒ 五条 **Δy = 0.0000** ✓；
`C1.c0↔R1.c1`（RC ✓）⇒ **Δx = 0.0000** ✓；本体框相交 **0 对** ✓。

**还可能再美的**（留待下一手 ✓）：① GND 母线现在绕外圈一大圈 ✓（交叉少了但线长 ✓）；
② 仍佉 7 段导线穿过本体（其中大部分是"脚就在本体内部"的必然情形 ✓，
可逐段判是不是真毛病 ✓）。

**核心事实（机验钉死 ✓）**：原理图的 sketch 单位 = **1/90 in** ✓（**与面包板同一套** ✓）；
摆放 = `geometry + M·(k·(局部坐标 − viewBox原点))` ✓，`k = 声明物理尺寸/viewBox宽 × 3.5433` ✓。
（踩坑清单：core svg 用**单引号** ✗；连接点是 `connectorNterminal` 而非 pin 线中点 ✗；
`<transform>` 是 `<geometry>` 的**子元素** ✗；取 `<g id=…>` 要**认自闭合** ✗；仿射的
`A4/A5` **不能漏** ✗ —— 详见 `render_sch.py` 头部。）

### 第三十一手 ✅：**骑轨预摆位**（结构性 ✓）⇒ **`pixel-schematic-v36.fzz`** 交付 ✓（2026-09-30）

★ 上一手把"那 −104.7 单位从哪来"量清楚了 ✓，但三次都**没做成** ✗ —— 根因这一手找到了 ✓：
**不是判据太严 ✗，是"收尾再挪"这条路线本身错** ✗（轨是为旧脚位延伸的 ⇒ 件一挪就穿身 ✗）。
改成**结构性**做法 ✓：**骑轨件在“布线之前”就摆到轨上** ✓。

| 项 | v35（上一版） | **v37（本版）** | 用户手改版 |
|---|---|---|---|
| 总长 | 1941.0 单位 = 547.8 mm | **1854.6 单位 = 523.4 mm** ✓（**−86.4** ✓） | 1836.3 单位 |
| 十字交叉 | 8 | **7** ✓ | 4（人手改的 ✓） |
| 穿本体 / 贴脚 / 悬空端 / 退化点 | 0 / 0 / 0 / 0 | **0 / 0 / 0 / 0** ✓ | 0 / 1 / 1 / 1 ✗ |
| 画布 | 104.1 × 94.5 mm | **100.0 × 98.0 mm** ✓ | 100.8 × 94.5 mm |

（★ `v36` 的 1824.8 单位是**假的** ✗ —— 它短的那 29.8 单位正是**没连上**的那截轨 ✓，见下面那一节 ✓。）

**做法（三处，都有实测理由 ✓）**：

1. **轨锚在“其它件”的包围盒上** ✓（`rail_y_map()` ✓，抽成**唯一实现** ✗✓ —— 主流程与预摆位共用 ✓）：
   骑轨件**不算进这个盒子** ✗ ⇒ 它一往上摆、盒子不会跟着长、**轨就不会被它带走** ✓。
   （✗ 反过来试过：“先摆件、再算轨” ⇒ 轨跟着跑 ⇒ 总长 **1971.3** ✗，比不摆还差 ✗。）
2. **`rail_hug_place()`** ✓：只手选**每一只脚都在轨网上**的件 ✓（本板 = `C2` = 5V + GND ✓；
   `C1` 是 RC + GND ⇒ **骑不了** ✗ —— 另一只脚必须走信号路径 ✓）；候选 = 两个朝向 ×
   “让某只脚踩上它那条轨” ✓，取**脚到轨之和**最小者 ✓（实测 `C2`：**70.2 → 12.6** ✓）。
3. **“竖直法线的脚也允许先横着出脚”** ✓（只**按需**触发 ✓，见下 ✓）：`C2` 的两脚之间
   **必然夹着一条轨** ✗（脚距 27.0 vs 轨距 14.4 ✓）⇒ “直上到轨”会让**轨伸进身体** ✗
   （实测穿身 **3.95mm** ✗）⇒ 得**先横着出脚 7.2、再竖着到轨** ✓ ⇒ 轨只伸到身体**左边缘**就停 ✓。

★ **“按需”这一条是量出来的** ✗✓：先**全局**放开竖法线的横出脚 ⇒ **基线变差** ✗
（不带 `--snaprails` 时：交叉 **8 → 10** ✗ —— 长度虽省 9.2 ✓，但**交叉数是头号指标** ✓、
用户的判据是“看着简单” ✓）⇒ 收回 ✓，改成**触发条件**：
**本网某条轨的 y 正好从“这只脚所在元件的肚子中间”穿过** ✓ 时才放开 ✓ ⇒ 别的脚**一条候选都不加** ✗
⇒ **基线逐字节不变** ✓（回退验证：与 `v35` **26/26 全同** ✓）。

**判据一份实现** ✓（`sch_geom.hits_box()` ✓，2026-09-30 抽出来 ✓）：渲染器的“导线穿本体”
与预摆位的“摆完复验”**共用同一个函数** ✗✓ —— ✗ 之前 `snap_rails` 自己另写了一份
（盒子缩 2 单位 ✗、认 ≥3 个采样点 ✗）⇒ **两把尺子** ✗ ⇒ 好候选被更严的那把**误否决** ✗
（实测报告：`⊘ C2 … 网 GND 的段 C2.connector1→None` ✗ = 那条**马上要删掉**的旧支线 ✓）。

**`snap_rails()` 保留为收尾兜底** ✓（本版它什么都不做 ✓ = 一致 ✓）：改成「**摆完再验、不过就整份回滚**」✓
（回滚点 = `nets_segs` / `boxes` / `pin_all` / `pins` / `loc` / `trunk` / XML 属性 ✓），
并**补删整条旧支线** ✓（✗ 原来只删贴着脚那一段 ✗ ⇒ 残根吊在半空 ✗，既会“穿新身体”✗、
又留**悬空端点** ✗）。

**机器守**：六道独立闸门 + 渲染器 **全 0** ✓（`check_netlist` / `check_fake_wires`（(A)=0 ✓ (B)=0 ✓）
/ `check_flags` / `check_grounds` / `check_label_touch` / `check_junctions` ✓，渲染器 **零 ⚠** ✓）。

#### ✗✗ `v36` 已**作废** ✓ —— 用户看图抓出两个错 ✓，`v37` 取代（2026-09-30 ✓）

用户拿到 `v36` 一开图就说「**C2 接线不对**」✓ —— 一查，**两个真错** ✗：

1. **`C2` 的 5V 脚一根线都没有** ✗（全表 44 根线里 `C2.connector0` **一次都没出现** ✓）：
   预摆位把它摆成“**5V 脚正好落在 5V 轨上**” ✓ ⇒ 那条支线长度 **0** ✗ ⇒ 被 `dedup_path`
   折成 **1 个点** ✗ ⇒ 收尾当“退化段”丢掉 ✗ ⇒ 脚就**孤零零**了 ✗ —— 而它**正压在轨线上** ✓
   ⇒ **图上看着接上了** ✓。
   ✓ 修法（结构性 ✓）：脚正好落在轨上时**不建支线** ✗，改成**把轨在这个 x 处断开** ✓
   （轨在该点切成两段，两侧各把那只脚记成 `to`/`from` ✓ ⇒ ① 连接**显式** ✓ ② `--trim` 的
   “终端分块”看得见这只脚 ✓ 不敢删 ✓ —— ✗ 以前整条轨是**一段**、`from`/`to` 都是 `None` ✗
   ⇒ 它的终端模型里**根本看不见坐在轨上的脚** ✗ ⇒ 把载着断点的那截轨当“多余”剪掉 ✗）。
2. **`check_netlist.py` 是橡皮图章** ✗✗（**本次最贵的一条** ✓）：它**明明打出了**
   「`5V` ✗ 少了 `C2.connector0` ✗」「判定: ✗ 1 个网对不上」✓ —— 可它**从不设退出码** ✗
   ⇒ `exit 0` ✗ ⇒ 我拿“七道闸门全 exit 0”当合格线 ⇒ **被自己那道门骗了** ✗✗
   （用户看图才发现 ✗）。⇒ ✓ 已修：**判定行与退出码必须一致** ✓（✗ ⇒ 1 ／ 跑不起来 ⇒ 2 ✓）；
   负例自检：`v36` ⇒ **exit 1** ✓、`v35`/`v37` ⇒ exit 0 ✓。

★ **两条通则**（写下来 ✓，都吃过亏 ✓）：
- **“退出码 0” ≠ “过”** ✗ ⇒ 每个核对器都要有**负例自检** ✓（拿一个**已知有错的**文件跑 ✓，
  确认它**非 0** ✓）—— 与“不许自证”是同一条纪律 ✓（这次栽在**半自证**上 ✗：我信了自家门的退出码 ✗）。
- **“图上看着接上了”不算接上** ✗ ⇒ 判据要**独立**到能覆盖“**脚压根没有线**”这一种 ✓
  （(A) 要求“先有声明的连接”✗、(B) 要求“先有线画在脚上”✗ ⇒ 两只都**以“有线”为前提** ✗
   ⇒ 恰好漏掉“一根线都没有”✗✓）。

**`v37`（取代 `v36` ✓）**：总长 **1854.6 单位 = 523.4 mm**（`v35` 1941.0 ⇒ **−86.4** ✓；
`v36` 那个 1824.8 是**假的** ✗ —— 少算的那 29.8 单位正是它**没连上的**那截 ✓）｜
十字交叉 **7**（`v35` 8 ✓）｜穿体 **0** ✓｜贴脚 **0** ✓｜悬空端 **0** ✓｜退化点 **0** ✓｜
画布 **100.0 × 98.0 mm** ✓｜六道闸门 **exit 0** ✓ + 渲染器 **零 ⚠** ✓。

#### ★ 用户第二次指出：**黑色竖线贴着电容本体走** ✗ ⇒ `v38`（2026-09-30 ✓）

用户原话：「**黑色竖线离电容太近了吧？**」✓ —— 量出来是**几何必然** ✓：
`C2` 的盒子 `x = 259.96…274.36` ✓（电容板半宽 **7.2** ✓），而 `GND` 脚那条支线
“**出脚 7.2**”的车道正好 = **259.96 = 盒子左边缘** ✗ ⇒ 竖线**贴着自己的本体**跑 ✗。
（★ 为什么既有闸门不管 ✗：穿体闸门只管**穿过** ✗、而**自己那件是唯一被豁免的** ✗
—— 线要进肚子才能接到脚上 ✓ ⇒ “贴着自己的身子”**没人管** ✗✗。）

✓ 修法（只**剔车道**、不动任何合格条件 ✗）：车道若落在 **本件盒子 ± `CLEAR`（6.0 单位 = 1.7mm ✓）**
之内 ⇒ **剔掉** ✗ ⇒ 退到下一档 ✓。实测：`C2` 的出脚由 **7.2 → 14.4** ✓
（竖线离板边 **7.2 单位 = 1.79 mm** ✓ 看得清 ✓）；**总长 1854.6 一点没变** ✓
（支线长的那 7.2 由 `--trim` 在别处找回来了 ✓）、交叉 **7** ✓、六道闸门 **exit 0** ✓、
渲染器 **零 ⚠** ✓；**基线（不带 `--snaprails`）仍与 `v35` 逐字节相同** ✓（26/26 ✓）。

### 第三十二手 ✅：**工具箱收进元件库仓**（2026-09-30 ✓ 用户定 ✓）

★ 用户定的一条架构 ✓：「**通用工具只有一份，放在元件库仓 `fritzing-parts-langhua/tools/` ✓，
本项目不留副本 ✗**」—— `toolpaths.py` 里其实**早就写着这条** ✓（2026-09-27 ✓），
只是当时项目里还躺着副本 ✗（正是它自己警告的"两份实现"✗）。

**搬走的**（通用 ✓，17 个）：`sch_geom/sch_box/sch_net/sch_text/sch_glyphs` ✓、
`render_sch/render_bb/wire_dump/set_rot` ✓、`check_netlist/check_fake_wires/check_flags/check_grounds/check_label_touch/check_junctions/check_labels` ✓、
`bb_route4` ✓、`ground_symbol.svg` ✓（+ 许可 ✓ —— ★ 用户 2026-09-30 定：**全部外部素材统一放库仓 `svg/_assets/`** ✓，不在 `tools/` 下另开一份 ✗）。
**留在项目里的**（本板专有 ✓）：`gen_schematic_wires` ✓、`gen_schematic_layout*` ✓、`pins_ref`/`pins_calibrated` ✓、
`audit_layout`（它直接读本板网表/摆位 ✓）、`fix_*`/`run_v6` ✓、以及**新增的项目数据文件**：

★ **`pixel_nets.py`（新 ✓，本板数据的三张表）**：`NETS`（网表 ✓ 生成器与面包板布线器共用 ✓）、
`EXPECT`（网表核对的期望 ✓）、`COLOR`（每网导线颜色 ✓ = Fritzing 官方色值 ✓）。
⇒ 通用工具改成 `--nets=<项目数据.py>` ✓，**缺省找当前目录的 `pixel_nets.py`** ✓ ⇒ 老命令照用 ✓；
抽表**一字未改数值** ✓ ⇒ 实测 `v38` 生成结果**逐字节不变** ✓（26/26 ✓）。

★ **`toolpaths.py` 留在项目仓** ✓ —— 它是**项目侧**的定位器（把库仓 `tools/` 接进 `sys.path` ✓），
跨仓引用只此一处 ✓；库仓的工具**不再需要它** ✗（同目录直接 import ✓）。

**搬家顺带修掉的三处**（都是"工具离开了项目目录"才暴露的 ✓）：
1. **相对输入按「当前目录」解** ✗✓（原来按 `HERE` = 工具自己所在目录解 ⇒ 搬进库仓后一律
   "文件不存在" ✗，实测踩到 ✓）；
2. **中间产物不写真仓库** ✓：`check_fake_wires` / `check_flags` 的输出改到**系统临时目录** ✓
   （`FZ_WORK` 可覆盖 ✓）；`check_fake_wires` 跑渲染器前把输入**转绝对路径** ✓（子进程 cwd 变了 ✗）；
3. **接地符号图形入库** ✓（**库仓 `svg/_assets/ground_symbol.svg`** ✓ + 许可 ✓）—— 渲染器/生成器都按**库仓根**找它 ✓（`FZ_ASSETS` 可覆盖 ✓）；✗ 一度放在 `tools/_assets/` ✗，按用户 2026-09-30 的规矩**统一到 `svg/_assets/`** ✓（实测：不跟着走会**静默少画 2 个接地符号** ✓，零件 13→**11** ✗）。

**验证**（搬家后重跑一遍 ✓）：`v38` 生成 **逐字节可复现** ✓（26/26 ✓）；六道闸门（现从库仓跑 ✓）
**全 exit 0** ✓；渲染器 **零警告** ✓、画布 100.0 × 98.0 ✓、零件 13 ✓；负例自检：`--nets=` 指向
不存在的文件 ⇒ **exit 1 + 明确报错** ✓（不许静默 ✓）。

**新用法**（在项目目录里跑 ✓；工具在库仓 ✓）：
```
py -3.13 f:\git\fritzing-parts-langhua\tools\render_sch.py    pixel-schematic-vNN.fzz out.png
py -3.13 f:\git\fritzing-parts-langhua\tools\check_netlist.py pixel-schematic-vNN.fzz
```

### 第三十三手 ✅：**PCB 自动布线交付** ⇒ **`pixel-pcb-v47.fzz`**（2026-10-01 ✓ 用户定稿 ✓）

**交付物** ✓：`hardware/pixel/pixel-pcb-v47.fzz`（＋预览 `pixel-pcb-v47_preview.svg/.png` ✓）。
线路：`pixel-pcb-v25.fzz`（用户摆位底图 ✓）⇒ 自动布线 + 写回 ⇒ v47 ✓。

| 指标 ✓ | 值 |
|---|---|
| 连通 | **9/9 网** ✓ |
| 走线对象 | **131 条** ✓（12 mil = 0.3048 mm ✓ 统一线宽 ✓）|
| 过孔 | **18 个** ✓（孔 0.3 mm / 环 0.15 mm ⇒ 盘 **Ø0.6 mm** ✓）|
| 线长 | 198.4 mm ✓ |
| 悬空端点 | **0** ✓（硬闸门 ✓，非 0 就**不写文件** ✓）|
| 多线共用一端 | **0** ✓ |
| 板框 | 25.00 × 25.00 mm ✓ |

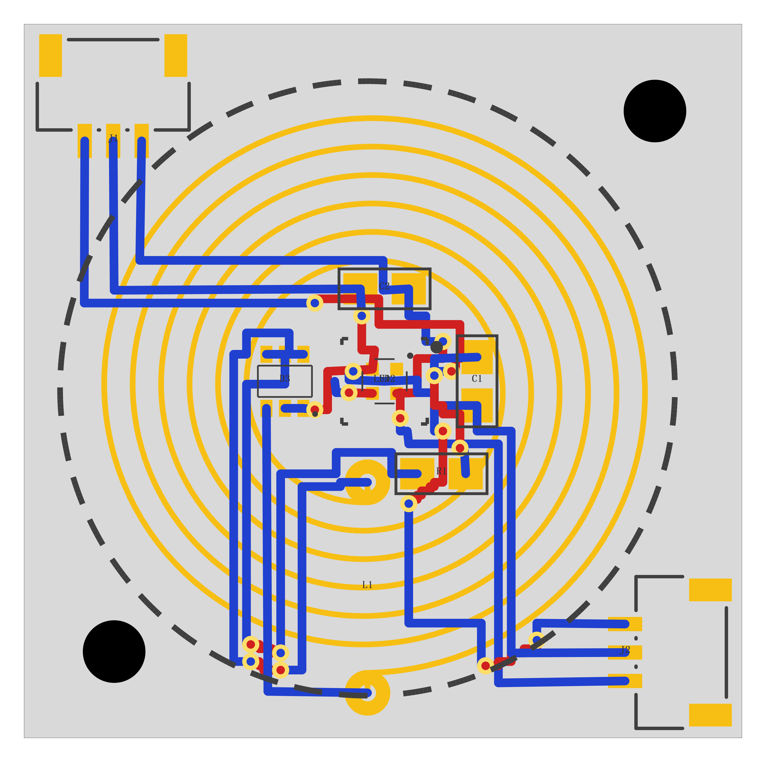
[picture p30: hardware/pixel/pixel-pcb-v47_preview.png]
PCB v47 预览（蓝 = 底层 copper0 ✓、红 = 顶层 copper1 ✓、黄环 = 过孔 ✓（**环 + 白心孔** ✓，照 Fritzing 导出的画法 ✓））
- 
- 复现 ✓（在项目目录里跑 ✓）：
  ```
  py -3.13 gen_routes.py pixel-pcb-v25.fzz pixel-pcb-v47.fzz --nets=pixel_nets.py \
      --mil-power=12 --mil-signal=12 --passes=8 --turn=0
  py -3.13 f:\git\fritzing-parts-langhua\tools\render_pcb.py pixel-pcb-v47.fzz pixel-pcb-v47_preview.svg --png
  ```

**★ 为什么是 v47（不是 v41）** ✓：v41 与 v47 **电气等价** ✓（同 9/9 ✓、同 18 孔 ✓、线长差 0.1 mm ✓），
但 v41 里有一根 `Wire90013154` 的两端**正落在 `U1` 的空脚 `PC0` 盘心** ✗ ⇒
写回器按**端点坐标**认盘 ⇒ 给它写了 `<connect>` ✗ ⇒ **Fritzing 里 PC0 会被算进 5V** ✗；
v47 同一条线**停在结点上、离 PC0 盘心 0.18 mm** ✓ ⇒ 不写 ✓。

**★ 两条已量清、但不在本手范围内** ✗（记账 ✓，详见库仓
`docs/fritzing-sketch-format-notes.md` 的 F12–F16 / §4-Q5 ✓）：
1. **Fritzing 载入时会改写走线几何** ✗：拿用户导出的 `pixel-pcb-v41_图示.svg` 逐条对 ✓ ——
   130/130 线、18/18 过孔都在 ✓、线宽颜色全对 ✓、元件几何零残差 ✓；
   但 **81/260 个端点被挪** ✗（0.07～0.66 mm ✓，挪完仍在盘内 ✓）⇒ 合计线长 **198.5 → 182.1 mm** ✗。
   ⇒ **报线长/坐标必须以导出为准** ✗（我方渲染是自证 ✗）。
2. **"不许线压焊盘（含空脚）"这条规矩还没落地** ✗：判据已入库 ✓（`pcb_route.pads_covered` ✓），
   但试过两版都先坏在别处 ✓（端点差半格 ⇒ 报 6 个悬空 ✗；加硬禁位 ⇒ 报 2 个悬空 ✗ ⇒ 文件都写不出 ✗）。
   ⇒ 真难点是**写回器"端必须正中"** vs **布线器端点在栅格上** 这对矛盾 ✗。
3. **预览器画法与 Fritzing 不一致** ✗（2026-10-01 ✓ 只改**预览器**，一个字没动交付文件 ✗）：
   - ✅ **已修 · 过孔** ✓：原来画**实心绿点** ✗ ⇒ 图上与焊盘无异、看不出孔眼 ✗（用户：「过孔都画错了」✓）。
     现按 **Fritzing 自己导出的画法**照画 ✓：**同心环 + 白心孔** ✓ ——
     环中心线半径 `(孔直+环宽)/2` ✓、描边宽 = 环宽 ✓，尺寸**读件自己的 `hole size`** ✓
     （v47 = 孔 0.30 / 环 0.15 mm ⇒ 环 0.225 / 孔 Ø0.30 / 盘 Ø0.60 mm ✓；
     证据见库仓 F17 ✓）。
   - ✅ **已修 · 走线线宽** ✓（2026-10-01 ✓ 用户点头 ✓）：原来每根线**写死** `0.25` 内部单位
     ≈ **0.0705 mm** ✗，而 v47 的 131 根 PCB 走线全是 `wireExtras mils="12"` = **0.3048 mm** ✓
     ⇒ 预览比实物**细 4.3 倍** ✗（线像发丝、过孔显大 ✓）。现改用 `pcb_wire` 读出的
     `wireExtras@mils` ✓（换算唯一实现在 `part_box.mils_to_units` ✓）。
     **核对** ✓：过孔环中心线 33.90 px、走线 45.92 px ⇒ **比值 1.355** ✓ = `0.3048 ÷ 0.225`
     的理论值 ✓✓（不用猜像素比例 ✓，拿已知刚体反标定 ✓）。
   - ✗ **未改 · 预览里的"板框"**（新记账 ✓，未动 ✗）：灰底那块其实是"**板 ∪ 所有件**"的并集框 ✓
     （件画布常带留白 ⇒ 会比真板略大 ✓，实测 v47 约 25.77 mm ✗）⇒ 量尺寸**不能拿它当标尺** ✗。

### 第三十四手 ✅：**PCB 自动布线交付（第二版）** ⇒ **`pixel-pcb-v51.fzz`**（2026-10-01 ✓ 用户点头 ✓）

**交付物** ✓：`hardware/pixel/pixel-pcb-v51.fzz`（＋预览 `pixel-pcb-v51_preview.svg/.png` ✓）。
线路：`pixel-pcb-v50-place.fzz`（摆位底图 ✓）⇒ 自动布线 + 写回 ⇒ v51 ✓。

```bash
py -3.13 gen_routes.py pixel-pcb-v50-place.fzz pixel-pcb-v51.fzz --nets=pixel_nets.py \
    --via=10 --tries=6 --deliver --check          # --deliver = 用户点头的交付（已知问题照写）
py -3.13 f:\git\fritzing-parts-langhua\tools\render_pcb.py pixel-pcb-v51.fzz pixel-pcb-v51_preview.svg --png
```

| 指标（独立复核 ✓ `pcb_check` 重读刚写的文件 ✓） | 结果 |
|---|---|
| 连通 | **8/9** ✓ |
| ④ 短路桥 | **0** ✓ |
| 悬空端点 | **0** ✓ |
| ⑦ 过孔压盘（含同网） | **0** ✓ |
| ⑨ 安装孔净距 | 0 ✓ |
| 走线 / 过孔 | 115 条 / 8 个 ✓（全板 **8 mil** 一种宽度 ✓） |

**已知未连通（1 处，交付时明确记账 ✗）**：`RC` —— `R1.connector1` ↔ `U1.connector1` / `C1.connector0`
（三脚散在三块铜里 ✓）。根因：`5V` / `RC` / `DATA_IN` 三张网抢**同一条**被线圈挤出来的走廊 ✓。

★ **交付前把四条杠杆全量过一遍** ✓（不是拍脑袋停 ✓）：

| 试的 | 实测结果 |
|---|---|
| **A 留走廊**（`5V` 先单独布好再钉住 ✓，`pre` 机制 ✓） | 0 短路 ✓、连通 7/9 → **8/9** ✓ ⇒ 保留为默认 ✓（`--no-lock` 可回旧行为 ✓） |
| **② 挪 `R1`** | 仓库自己的 `_work/move_part.py`（按 ⑧ 规则 + 板框 + 位移最小 ✓）搜出**最佳位移 = 0** ✗ ⇒ 它已卡在线圈两圈之间最合适 ✓ |
| **① 也给 `RC` 留走廊** | 连通数不变 ✓、过孔 8 → **16** ✗ ⇒ 已退回 ✗ |
| **C 净距 0.15 → 0.127**（工艺下限 ✓） | **无效** ✗（栅格 0.15 把禁落半径量化到整格 ✓ ⇒ 逐项相同 ✓）；强行细化栅格 ⇒ 出 1 处悬空端点 ✗ ⇒ 已回退 ✓ |
| **线宽 6 mil** | **无效** ✗（与 8 mil 逐项相同 ✓；细化栅格后仍 8/9 ✓ 但多 1 处悬空 ✗）；且 **6 不是 Fritzing 档位** ✗ ⇒ 本就不能交付 ✓ |
| **③ 加宽板 25 → 30.1 mm**（2026-10-01 ✓） | **无效** ✗ —— 走线 / 过孔**逐项相同** ✓（差只在 0.0003 mm 浮点尾 ✓）；而独立探针报 `RC` 各脚**可达格子 29,889 → 52,124（+74% ✓）** ⇒ 空地确实多了一倍半、**可一根线都没变** ✗。★ 瓶颈是**线圈匝间缝**那几处"过线圈"的通道 ✗（缝宽与缝的**条数**都由线圈决定 ✓ ⇒ 板再大也不会多出一条 ✓）。详见 `coil-spec.md` §4b ✓ |
| **④ 三张网一起钉**（`5V`+`RC`+`DATA_IN`，2026-10-01 ✓） | **更差** ✗ —— **8/9 → 6/9** ✗（掉的是 `DATA_IN`/`DATA_OUT`/`GND` ✓）；⭐ 这条同时是**记账纠错** ✓：它上一轮被写进代码、却漏了回退 ✗ ⇒ **控制组也跑成 6/9** ✗，差点把"大板更差"当结论报出去 ✗ ⇒ 回退后控制组**逐项复现 v51** ✓（走线 + 过孔 + 回指全同 ✓） |
| **⑤ 线圈档位 A / B / E ＋ `R1` 挪出**（2026-10-01 ✓） | ★★ **`R1` 挪出线圈 = 零电气代价的杠杆** ✓✓（缺口 `RC` 3 脚 ✗ → `DATA_IN` 2 脚 ✓，**电压仍 100%** ✓）；**E 档（5 匝）白做** ✗（与 `A ＋ R1 挪出` **逐项相同** ✓）；**B 档（4 匝）仍多赚** ✓（线短 26 mm ✓、过孔回 8 ✓、空心 ⌀11.4 ✓，代价 −23% 电压 ✗）。四组对照见 `coil-spec.md` **§4c / §5** ✓ |

★ **② 那一行要更正** ✓（2026-10-01 ✓）：`move_part.py` 自动搜出的"最佳位移 = 0" ✗ 是**它的判据**
（= 合法且**位移最小** ✓）；而**手动挪到线圈外**（`R1` 挪 `(+6, −6)` mm ✓）**实测有真收益** ✓
—— 判据（合法）与"有没有好处"不是一回事 ✗（见上表 ⑤ ✓）。

⇒ 结论（**2026-10-01 更新** ✓）：**25 × 25 mm + 当前摆位下 8/9 是上限** ✓；
9/9 只剩"**过线圈那几处缝**"这一轴 ✗ —— 已实测**否掉**的三条 ✓：**加宽板 ✗ 无用**（③ ✓）、
**挪件 ✗ 无用**（② ✓）、**钉走廊 ✗ 越多越差**（① ④ ✓）；**唯一有效**的是**改线圈本身** ✓
（减匝数 ⇒ 匝间缝变宽 ⇒ 未连通的网从 `RC`（3 脚 ✗）换成 `DATA_IN`（2 脚 ✓），见 `coil-spec.md` ✓）。

### 旋转轴实测（2026-10-01 ✓）：单件 45° 家族 —— **没有 9/9** ✗ ＋ 一个**工具限制** ✗

动机 ✓：用户提「试试元件旋转 45°、135°」✓。现状朝向 **只有 0/90/180/270** ✓（`_work/margins.py` 逐件读 ✓）。

工具 ✓：新写 `_work/rot_part.py`（**绕件自己中心**转 ✓、只改该件 `pcbView` 的 `<transform>` ✓；
库仓 `tools/set_rot.py` ✗ **只认 `schematicView`** ✗）＋ `_work/rot_sweep.py`（逐件逐角跑，日志落 `_work/_sw_*.txt` ✓）。
**口径自检 ✓**：`U1=0°` ⇒ 8/9｜197.4 mm｜8 孔｜115 条 = 与基线**逐项相同** ✓、框心漂移 **0.0000 mm** ✓。

| 件（脚距 ✓） | 45° | 90° | 135° | 180° | 225° | 270° | 315° | 判读 |
|---|---|---|---|---|---|---|---|---|
| `C1`（0.90 ✓） | 8/9｜**193.3**｜8 | — | 8/9｜193.3｜8 | — | 8/9｜195.7｜8 | — | 8/9｜195.7｜8 | 连通不变 ✗、`RC` 仍不通 ✗、**线长 −4.1 mm** ✓ |
| `R1`（0.90 ✓） | 8/9｜199.9｜8 | — | 8/9｜200.8｜8 | — | 8/9｜199.9｜8 | — | 8/9｜199.3｜8 | 8/9 ✗、线长 **+2～3 mm** ✗ |
| **`C1@45+R1@45`**（组合 ✓） | **8/9｜195.8｜8** | | | | | | | `RC`（它俩自己的网 ✗）**还是不通** ✗ |
| `LED2`（0.85 ✓） | 8/9｜204.8｜**10** | — | — | — | — | — | — | 更差 ✗ |
| `C2`（1.70 ✓） | 6/9｜159.0｜9 | — | — | — | — | — | — | **⑧ 不合格（−0.200 mm ✗）** ⇒ 废 ✗ |
| `L1`（7.40 ✓，对照 ✓） | 8/9｜**244.3**｜10 | 4/9｜**⑧ −0.420** ✗ | — | 6/9｜**⑧ −0.550** ✗ | — | 5/9｜**⑧ −1.077** ✗ | — | 斜角只是**变差** ✗（+47 mm ✗）；正交三档**全部 ⑧ 不合格** ✗（件自带的框/丝印转进别的件 ✓） |
| `U1`（**0.40** ✗） | 3/9 ✗✗ | **5/9** ✗ | 3/9 ✗✗ | **7/9**（263.1｜13 ✗） | — | **4/9** ✗ | — | 斜角 **测不了** ✗（包围盒假象 ✗）；正交三档是**真结果** ✓ ⇒ **没有一个更好** ✗ |
| `D3`（**0.65** ✗） | 2/9 ✗✗ | — | 2/9 ✗✗ | — | — | — | — | 测不了 ✗（同上 ✓） |

⇒ 结论（**22 种转法**：单件 ×20 ＋ 组合 ×1 ＋ 自检 ×1 ✓；其中**14 种"合法且量得准"** ✓）：
1. **没有一种到 9/9** ✗（最好的仍是 **8/9** ✓）、**`RC` 一次都没接通** ✗；
2. 收益上限 = **省几毫米线** ✓（`C1@45` −4.1 mm ✓）；代价是有好几档**明显更差** ✗
   （`U1@180` 263.1 mm ✗、`L1@45` **+47 mm** ✗✗、`U1@90` 5/9 ✗）；
3. ★★ 最有戏的两件（`U1` 枢纽 / `D3` 桥 ✓）**恰好测不了** ✗ ——
   根因（量出来的 ✓，`_work/probe_padbox.py` ✓）：布线器挡"别人的盘"用的是**轴向包围盒** ✗
   ⇒ 一转 45° 盘框就膨大（`U1` 0.20 → **0.57 mm** ⇒ **21 个脚心里 20 个**被隔壁盘框盖住 ✗；
   `D3` 0.42 → 0.72 mm ⇒ 过道被自己吃掉 ✗）⇒ 数字是假象 ✗。
   规矩见库仓 `docs/pcb-rules.md` **§6** ✓（非 90° 整数倍时，只有脚距 ≳ 0.8 mm 的件量得准 ✓）。
   要让它们可测 ⇒ 得让布线器认**旋转矩形** ✓（另立一手 ✓，本轮不动核心 ✗）。
`J1`/`J2` 没跑 ✓：摆位规范要求**焊盘朝内** ✓ ⇒ 各只剩 2 个合法朝向 ✓（45° 本来就违规 ✗）。
`J1`/`J2` 没跑 ✓：摆位规范要求**焊盘朝内** ✓ ⇒ 各只剩 2 个合法朝向 ✓（45° 本来就违规 ✗）。

### 第三十五手 ✅：**byHand 版第一次布线**（2026-10-01 ✓ 用户手画底图 ＋ 自动布信号 ✓）

用户原话 ✓：「我把之前的过孔和布线都删除了，把 `J1/J2` 等固定了位置，禁止手工编辑时移动位置，
拉了 5V 和 GND 长线，以便大电流供电能在 `J1/J2` 传递。我还旋转了 `C2` 到一个我认为合适的角度。
我想你能不能以此版本为基础，做布线尝试」✓。

底图 ✓：`pixel-pcb-v51_byHand.fzz`（用户手画 ✓，**24 mil** 粗线 ✓）⇒ 产物 ✓：**`pixel-pcb-v52_byHand.fzz`** ✓

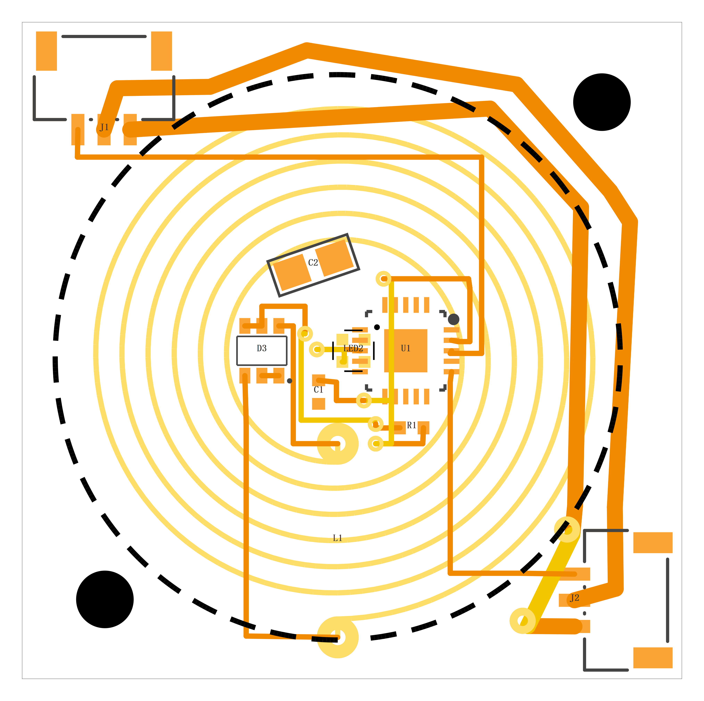
[picture p31: hardware/pixel/pixel-pcb-v52_byHand_preview.png]
v52 byHand 预览


★ **先修了一个工具 bug** ✗（是这个文件暴露出来的 ✓）：`pcb_wire.parse_trace()` 的正则写死成
`<pcbView layer="copper0trace">` ✗，而**手画的线**被 Fritzing 写成
`<pcbView layer="copper0trace" bottom="true">` ✓ ⇒ **18 条只认出 1 条** ✗
（布线器与校验器**共用**这个函数 ✗ ⇒ 会把线压上去布线、而校验器**看不见**短路 ✗✗）。
已修 ✓（库仓 `a78a4d1` ✓），回归 ✓：`pixel-pcb-v51.fzz` 仍「走线 **115** / 过孔 **8**」**逐项相同** ✓。

| 试的（同一套开关 ✓） | 结果 |
|---|---|
| **只布 7 张信号网**（用户的 5V/GND **原样不动** ✓） | ★★ **7/7 全通 ✓✓** ｜线长 **97.5 mm** ✓｜过孔 **7** ✓｜悬空 **0** ✓｜叠（短路）**0** ✓ |
| 9 张一起布（对照 ✓） | **6/9** ✗（布线器会把 5V/GND **再布一遍** ✗ ⇒ 挤掉信号线 ✓） |

⇒ 结论 ✓：**用户的摆位（含 `C2` 转 341° ✓）能布通 ✓**；**手工拉的电力线必须"保持不动"** ✓。

**★ 交给用户收尾的清单** ✓（独立复核 `pcb_check` ✓：65 处问题 → 只剩 **8 处** ✗，**全在 `J2` 那一角** ✓）：

| # | 还差什么 | 位置（板坐标 mm ✓） |
|---|---|---|
| ①×2 | 走线 #15 的**终**端、#16 的**终**端悬空 ✗ | (52.70, 24.00)、(51.00, 27.49) |
| ①×2 | 走线 #17 **两端**都悬空 ✗ | (52.70, 24.00) ↔ (51.00, 27.49) |
| ③×2 | 2 颗过孔没挨到任何铜 ✗ | (52.50, 23.80)、(50.80, 27.29) |
| ⑤ | `5V`：5 个脚还在 **5 块铜**里 ✗ | 接到 `J1`/`J2` 的 1 脚即可 ✓ |
| ⑤ | `GND`：9 个脚还在 **7 块铜**里 ✗ | 同上 ✓ |
| ✅ | **7 张信号网全通 ✓**（`COIL_A/COIL_B/BR+/RC/DATA_IN/DATA_OUT/LED_DIN` ✓） | **不用动** ✓ |

复现 ✓（都在本目录里跑 ✓）：

```bash
py -3.13 _work\run_gen.py pixel-pcb-v51_byHand.fzz _work\bh-7net.fzz --nets=_work\bh_nets.py \
    --via=10 --tries=6 --partial --check
py -3.13 f:\git\fritzing-parts-langhua\tools\render_pcb.py pixel-pcb-v52_byHand.fzz \
    pixel-pcb-v52_byHand_preview.svg --png
py -3.13 f:\git\fritzing-parts-langhua\tools\pcb_check.py pixel-pcb-v52_byHand.fzz \
    --nets=pixel_nets.py
```

（`_work\bh_nets.py` ✓ = 从 `pixel_nets.py` **派生**、去掉 `5V`/`GND` ✓ —— 手抄一份就等于"两套实现"✗。）

### 第三十六手 ✅：**byHand 版第二版** ⇒ `pixel-pcb-v57.fzz`（2026-10-02 ✓ **保留用户的粗电力线** ✓）

用户 2026-10-02 手改（`C2` 挪到右上、转 315°；`C1` 归 0°）后授权 ✓：
「**你直接做个新版本出来吧**」✓ ＋ 「`C2` 可以挪 ✓ / 那条线也可以绕 ✓」✓。

**做法** ✓（三步 ✓，每一步都能独立复核 ✓）：
1. 只删**我们自动布的 8 mil 线** ＋ **我们加的过孔** ✓（他的 **24 mil** 粗线**原样保留** ✓
   —— 判据用**线宽** ✗ 不用 `bottom="true"` ✗：实测 Fritzing 与我们**都会**给底层线写那个属性 ✗）；
2. **`C2` 微挪 `(−0.25, +0.25)` mm** ✓（自动搜"位移最小、且不再压到别人铜"的点 ✓）⇒ 那处 ④ 短路清零 ✓；
3. **只布 7 张信号网** ✓（他的 5V/GND 长线自己不重画 ✓ —— 实测重画会挤掉信号线 ✓：9 张一起布只有 6/9 ✗）。

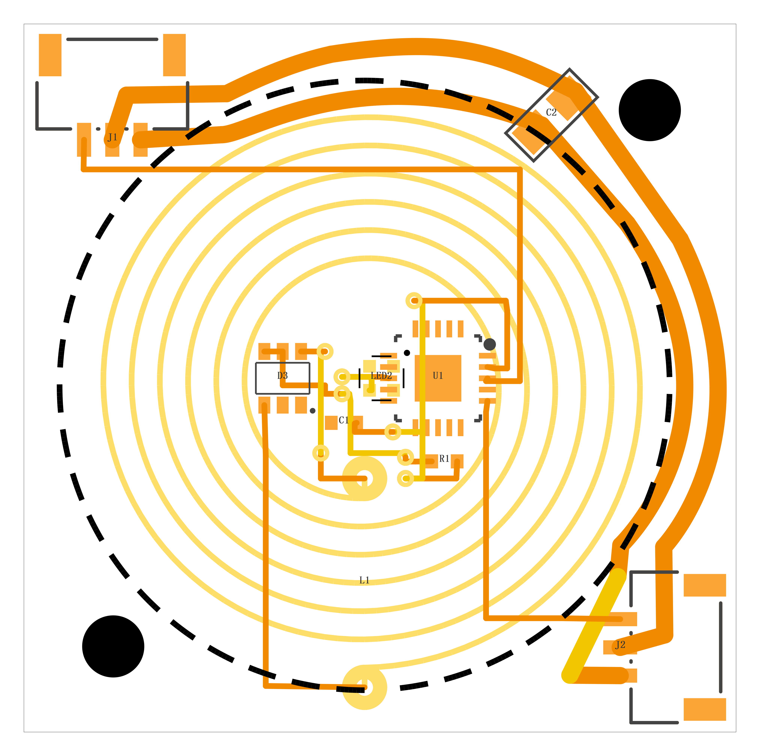
[picture p32: hardware/pixel/pixel-pcb-v57_preview.png]
v57 预览


| 独立复核（`pcb_check` ✓ **重读文件** ✓） | 结果 |
|---|---|
| 走线 / 过孔 | **86 条** ✓ / **9 颗** ✓ |
| **④ 短路** | **0 ✓** |
| **③ 孤立过孔** | **0 ✓**（他原来那 2 颗够不着铜的孔 ✓ 顺手清掉 ✓） |
| ① 悬空端点 | **4** ✗（他自己那两条没收尾的线 ✓，全在 `J2` 角 ✓） |
| ⑤ 没连通的网 | **2 张** ✗：`5V`、`GND` —— **7 张信号网全通 ✓✓** |

★ 本轮修掉两个**工具 bug** ✗（都是被这个文件逼出来的 ✓）：
1. `_work/strip_pcb_wires.py` **"说删了其实没删"** ✗ —— 循环里只在"保留"分支推进 `pos` ✗
   ⇒ 被删的块**又被装回**产物 ✗（我一度信了它自己打的字 ✗ = 又一次"**自证**"教训 ✗）
   ⇒ 现在**写文件之前先独立数一遍产物** ✓，数字不符就**报错且不写文件** ✗。
2. 删自己的线时**必须连过孔一起删** ✗（否则 9 颗孔全变成"孤立过孔"✗）。

复现 ✓：
```bash
py -3.13 _work\strip_pcb_wires.py pixel-pcb-v52_byHand.fzz _work\bus2.fzz --drop-mils 8 --drop-vias
py -3.13 _work\fix_c2.py _work\bus2.fzz _work\bus3.fzz C2 4
py -3.13 _work\run_gen.py _work\bus3.fzz _work\v57.fzz --nets=_work\bh_nets.py --via=10 --tries=6 --partial --check
py -3.13 f:\git\fritzing-parts-langhua\tools\pcb_check.py pixel-pcb-v57.fzz --nets=pixel_nets.py
```

★ **用户手工收尾用的清单** ✓（`_work/power_list.py` 从 v57 **重新量**的 ✓，含坐标 mm ✓）：
工作副本 ✓：**`pixel-pcb-v57_byHand.fzz`**（= v57 的拷贝 ✓，`*_byHand.fzz` 按仓规**不入库** ✓）。

**网 `5V`** ✗ 4 块铜（5 只脚）—— 把下面 3 个"孤块"并到主块 ✓：

| 块 | 脚 | 位置（板坐标 mm ✓） | 层 |
|---|---|---|---|
| **主块**（已通 ✓） | `J1.connector0` | (35.80, 8.52) | copper0 ✓ |
| | `C2.connector0` | (50.95, 7.05) | copper0 ✓ |
| 孤块 ① | `J2.connector0` | (52.78, 27.50) | copper0 |
| 孤块 ② | `LED2.connector3` | (44.76, 17.40) | **copper1（顶层 ✗ 要过孔 ✓）** |
| 孤块 ③ | `U1.connector5`（VDD） | (47.13, 18.72) | copper0 |

**网 `GND`** ✗ 7 块铜（9 只脚）：

| 块 | 脚 | 位置（板坐标 mm ✓） | 层 |
|---|---|---|---|
| **主块**（已通 ✓） | `J1.connector1` | (34.80, 8.52) | copper0 ✓ |
| | `C2.connector1` | (49.75, 8.25) | copper0 ✓ |
| | `J2.connector1` | (52.78, 26.50) | copper0 ✓ |
| 孤块 ① | `C1.connector1` | (42.55, 18.55) | copper0 |
| 孤块 ② | `D3.connector0` | (41.48, 17.92) | copper0 |
| 孤块 ③ | `D3.connector1` | (40.83, 17.92) | copper0 |
| 孤块 ④ | `LED2.connector1` | (43.91, 16.55) | **copper1（顶层 ✗ 要过孔 ✓）** |
| 孤块 ⑤ | `U1.connector20`（EPAD ✓） | (46.33, 16.97) | copper0 |
| 孤块 ⑥ | `U1.connector3`（VSS） | (48.08, 17.37) | copper0 |

★ 两点提醒 ✓：① 两个"孤块"在 **copper1（顶层）** ✗ ⇒ 连它们要**过孔** ✓（`LED2` 是正面件 ✓）；
② `U1` 是**背面**件 ✓ ⇒ 它的脚在**底层** ✓（表里已按物理层列出 ✓）。

### 第三十七手 ✅：**5V/GND 收尾** ⇒ `pixel-pcb-v58.fzz`（2026-10-02 ✓）

用户定 ✓：「**1. 电容问题，我选改网表**」✓ ＋「**2. 继续，把剩下 8 个脚接上吧**」✓。

#### 0. 先说一个**真问题**（用户裁决的 ✓）：`C2` 的两只脚「板上的铜」与「网表编号」**交叉** ✗

GND 那根总线接的是 **`C2.connector0`** ✓、5V 那根接的是 **`C2.connector1`** ✓ ——
**依据是 Fritzing 自己写的 `<connect>`** ✓（`Wire90013341` 端0 → `C2.connector0` ✓、
`Wire90013354` 端1 → `C2.connector1` ✓），而 `pixel_nets.py` 原来写的是**反的** ✗。
电容无极性 ⇒ **实物没毛病** ✓（两条总线各自独立 ✓、**没有铜短接** ✓），
但编号对不上就**永远验不过** ✗ ⇒ 用户定：**以板上的铜为准，改网表** ✓
（`NETS` 与 `EXPECT` 里 `C2` 的 `#1/#2`、`connector0/1` **对调** ✓）。

#### 1. 做法 ✓（`_work/route_rest.py` ✓ —— **一行 XML 都不自己拼** ✗）

1. 铜块按 **Fritzing 声明的连接**分 ✗✓（✗ 不用几何 ✗ —— 见下面「工具缺陷 ③」）；
2. 每张网的主块用**种子脚**定 ✓（`J1.connector0` = 5V ✓ / `J1.connector1` = GND ✓）；
3. 接头点**只取已有线/过孔的端点** ✓（不取线身中点 ✓）⇒ 写回器能按**点**查表写出
   `<connect … modelIndex="<那条已有线>">` ✓（Fritzing 自己的写法 ✓）；
4. 每张网放一个**假焊盘**在接头点上 ✓ ⇒ 布线器把「孤脚 ＋ 接头点」连成一串 ✓
   （**50 µm 细栅格** ✓ ＋ **8 mil** ✓ —— 0.15 mm 栅格**表示不了** QFN 那 0.2 mm 的缝 ✗）；
5. 交给 `gen_routes.build_xml` + `write` 写回 ✓。

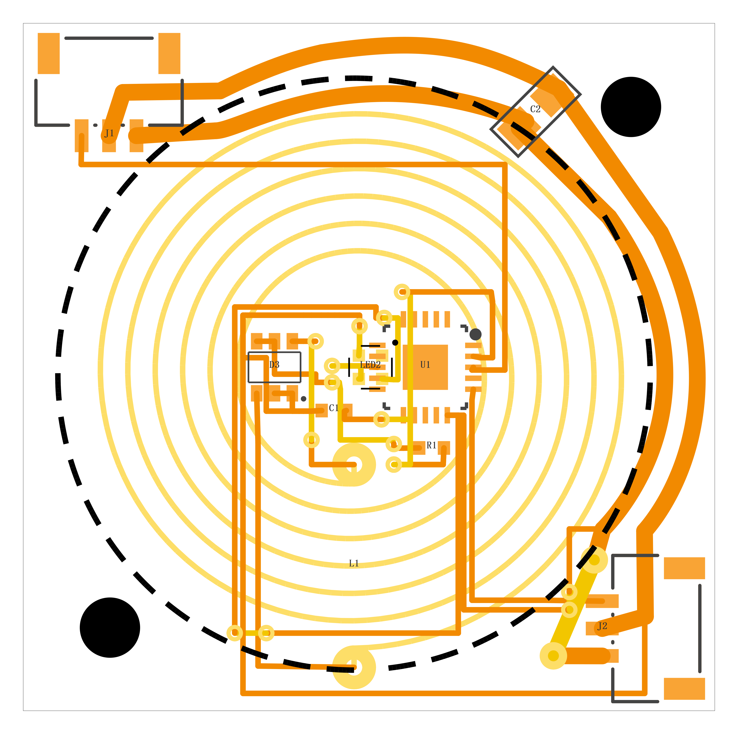
[picture p33: hardware/pixel/pixel-pcb-v58_preview.png]
v58 预览


| 独立复核（**声明图** ✓ 重读文件 ✓，只用**另一份实现** ✗） | 结果 |
|---|---|
| 走线 / 过孔 | **153 条** ✓ / **18 颗** ✓ |
| **④ 真短路** | **0 ✓** |
| **连通的网** | **8/9 ✓**（`5V` 5 脚 **1 块铜 ✓✓** ＋ 7 张信号网 ✓） |
| ✗ 还差 | `GND` **3 块**：只剩 `U1.connector20`（EPAD ✓）与 `U1.connector3`（VSS ✓） |

★ `GND` 那两只脚**布不通的原因（量出来的 ✓，不是猜 ✗）**：它们在 **QFN 20 脚的中间** ✗，
出线要穿过 0.4 mm 脚距的**焊盘走廊** ✗ —— 而按 `CLEAR_MM = 0.15` 的规则，
一条线需要 `0.2 + 2×0.15 = 0.5 mm` 的净空 ✗，走廊只有 ~0.2 mm ✗ ⇒ **规则下物理不可布** ✗。
⇒ 只剩两条路 ✓：(a) 在 **EPAD 上打同网过孔** ✓（规则里**唯一**允许的 via-in-pad ✓）
再从顶层走 ✓，并把 `VSS` 与 `EPAD` 在**焊盘内侧那道缝**里连起来 ✓；
(b) 把信号网一起**重布一遍** ✓（让布线器统筹扇出 ✓）。⇒ 等用户选 ✓。

#### 2. 本轮修掉三个**工具缺陷** ✗（都是被这个文件逼出来的 ✓）

1. ★★ **`pcb_route.obstacles()` 根本不收「文件里已有的走线」** ✗✗ ⇒ 布线器**看不见**用户手画的
   5V/GND 总线 ✗ ⇒ 实测新线**直接穿过去** ✗（独立复核报 **8 处同层交叉** ✗ = 真短路 ✗）。
   ⇒ 本项目里 `route_rest.py` 现在把已有铜**按网分表**喂进去 ✓（同网不挡自己 ✓、对手网照挡 ✓）。
2. **`gen_routes.build_xml` 只认「本次新写的线」** ✗ ⇒ 新线接在**已有线**上时那端**写不出
   `<connect>`** ✗（铜通了 ✓、Fritzing 里却显示「没接上」✗）⇒ 已补 ✓（含**回指** ✓）。
3. **两个报告盲区** ✗：`pcb_check` 的 ④/⑤ 用 `part_pads` 的**焊盘框**判“线端落在盘上” ✓，
   而那个框**比真铜大得多** ✗（`C2` 那颗 0603：框 **1.62 mm** ✗ vs 铜 ≈0.9 mm ✓）⇒ 加上容差后
   它把 5V/GND 的铜**误并成一块** ✗；⑤ 又只在“某网的脚散在 **1** 块”时才查“粘上别的网” ✗
   ⇒ 于是“5V、GND 粘在一起”被报成“没连通” ✗✗。⇒ 待修 ✓（本轮先用**第三份实现**
   `_work/conn_declared.py` 独立复核 ✓ —— 按声明分网 ✓，不碰那个大框 ✓）。

复现 ✓（都在本目录里跑 ✓）：
```bash
py -3.13 _work\route_rest.py pixel-pcb-v57_2_byHand.fzz _work\v60.fzz 8 0.05
py -3.13 _work\conn_declared.py _work\v60.fzz
py -3.13 f:\git\fritzing-parts-langhua\tools\render_pcb.py pixel-pcb-v58.fzz pixel-pcb-v58_preview.svg --png
```

### 第三十八手 ✅：**`EPAD`→`VSS` ＋ `VSS` 出去** ⇒ `pixel-pcb-v59.fzz`（2026-10-02 ✓ **9/9 连通** ✓✓）

用户的想法 ✓：「**`EPAD` 能跟 `U1.VSS` 接在一起的，`VSS` 能出去就 ok 了吧？**」✓ —— **对** ✓，
而且这条已经被用户定为**规则** ✓（原话：「**`EPAD` 优先与自身 `GND`/`VSS` 连，这个可以作为一个
规则记录下来**」✓ ⇒ 正文 `docs/pcb-rules.md` §7 ✓、摘要 `AGENTS.md` §5 ✓）。
用户随后选 **(A)** ✓：「**按规则①手工放 `VSS` 沿自己那条槽直着出来的一段短线**
（0.197 mm 合规 ✓，用**精确距离**自核 ✓，不靠那个带宽模型 ✗）」✓。

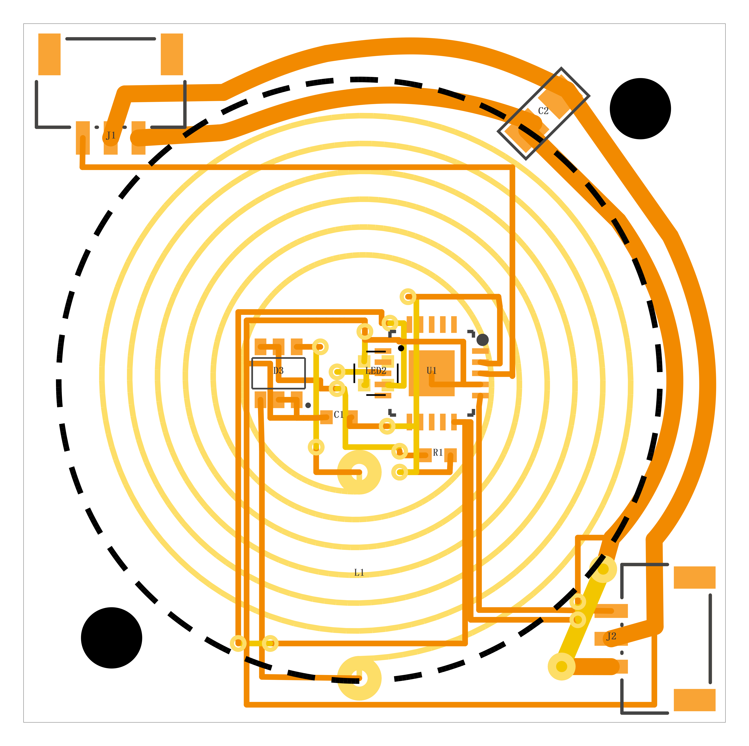
[picture p34: hardware/pixel/pixel-pcb-v59_preview.png]
v59 预览


| 独立复核（**声明图** ✓ 重读文件 ✓，只用**另一份实现** ✗） | v58 | **v59** |
|---|---|---|
| 走线 / 过孔 | 153 / 18 | **168 / 18**（新线 17 条 ✓、**一颗过孔都没加** ✓） |
| **④ 真短路** | 0 ✓ | **0 ✓** |
| **连通的网** | 8/9 ✗ | **9/9 ✓✓**（`GND` 9 脚 → **1 块铜** ✓） |
| `pcb_check` ①–④⑥ | ✓ 全过 | **✓ 全过** |

#### 1. 先量清楚：QFN 肚子里**只有一条 0.625 mm 的环形走廊** ✓

`U1` = QFN20 ✓：脚距 **0.4 mm** ✓、盘宽 **0.2 mm** ✓ ⇒ 盘间缝 **0.2 mm** ✗，而一条 8 mil 线
要 `0.2032 + 2×0.15 = 0.5032 mm` ✗ ⇒ **盘与盘之间一步也过不去** ✗。实测（**从盘框现量** ✓，
不抄常数 ✓）：`EPAD` 框 ↔ 焊盘圈内缘 = **右 0.625 ✓ 左 0.625 ✓ 上 0.625 mm** ✓
⇒ 出口**只有两个** ✓：① 沿走廊从**某个角**钻出去；② 在 `EPAD` 上打同网过孔上顶层 ✗
（顶层被 `L1` 线圈**连续螺旋**占死 ✓ ⇒ 实测孔打得上去 ✓、线**走不出去** ✗ ⇒ 本板此路不通 ✓）。

**四个角算过 ✓，只有左上角干净** ✓：右上角出去后向左被 `pad15` 挡 ✗；左下角被 `via#8`
(44.731,18.872) 的铜盘挡 ✗；右下角被 5V 的 `#86/#87` 挡 ✗；**左上角**出去后向左**正好落在
`GND` 已有的铜上** ✓（`via#17` 盘心 (43.931,15.472) ✓，那是 `#129` 的端点 ✓、与 `GND` 主块同块 ✓）。

#### 2. ★ 顺带修掉一个**真缺陷** ✗（v58 自己带的 ✓，不是我新加的 ✗）

`DATA_IN` 从 2 脚出来的那两根扇出线被布线器摆在了**焊盘下沿 y = 17.072** ✗（中线是 16.972 ✓）
⇒ 实测它离本件 `VSS` 盘**只有 0.0984 mm** ✗ —— 规则要 0.15 ✓、**嘉立创 1 oz 最小 0.127** ✗
⇒ **做不出来** ✗；而且它把 `VSS` 盘那条 0.6 mm 的槽**吃掉 0.1 mm** ✗ ⇒ `EPAD→VSS` 短接
（8 mil）差 **4.8 µm** 过不去 ✗。
⇒ 改成**贴着 2 脚中线走**（y = 17.000 ✓，离 `RC` 也够 ✓）✓ —— 槽放回 0.6 mm ✓（要 0.5032 ✓）。

#### 3. 两条新线 ✓（都只在 **copper0** ✓，**一颗过孔都不用打** ✓）

```
W1 = EPAD 盘心 (46.331,16.972) → (46.331,17.372) → VSS 盘心 (48.081,17.372)   ← 规则 ① ✓
W2 = VSS 盘心 → (47.468,17.372) → (47.468,15.834) → (45.156,15.834)
        → (45.156,15.772) → (43.931,15.772) → (43.931,15.472)                ← 规则 ② ✓
```
（`47.468` = 右走廊中线 ✓、`15.834` = 上走廊中线 ✓、`45.156` = 左上角那道 0.55 mm 口的**正中** ✓
—— 这三条中线都是**从盘框现量出来**的 ✓，不是抄常数 ✓。）

#### 4. ★ 不许自证 ✗：折线**不用布线器** ✗ ＋ 三份几何**互相独立** ✓

✗ 为什么不用 `pcb_route` ✗：它的焊盘净空是**不分层 ＋ 带宽式**（每侧 0.25 mm ✗）的
⇒ 实测把 0.625 mm 的走廊判成「**起点格空 / 不可达**」✗（不是真堵 ✗，是模型看不见 ✓）。
✓ 本轮改为**手算折线** ✓ ＋ 自写**三份**几何（段↔矩形 / 段↔段 / 点↔段 ✓）在主程序里
**逐段算净距** ✓，写完再交 `pcb_check` ＋ `conn_declared` **两份独立实现**复核 ✓。

| 新线 | 最紧的一条约束 | 余量（对 0.15 mm 规则 ✓） |
|---|---|---|
| `D1` `DATA_IN` ✓ | ↔ `U1.connector3`（`VSS` 盘 ✓） | **+0.0201 mm** ✓ |
| `W1` `EPAD`→`VSS` ✓ | ↔ `#38`（`DATA_OUT` 扇出 ✓，0.4 mm 脚距的**固有**上限 ✓） | **+0.0468 mm** ✓ |
| `W2` `VSS`→出 ✓ | ↔ `#38` ✓（次紧：`via#13`(5V) **+0.0487** ✓） | **+0.0468 mm** ✓ |

⇒ 实际铜距 = `0.15 + 0.0201` = **0.170 mm** ✓ > 嘉立创 1 oz 的 0.127 ✓ **做得出来** ✓。
判定口径 ✓：**任何一段 < 0（或写回器报悬空端点 / 跨网）⇒ 不写文件** ✗（本轮一次命中 ✓、
一次调 `y` 后再跑 ✓ ⇒ 才落盘 ✓）。

#### 5. 两个**已知**的 `pcb_check` 假报 ✓（v58 也有 ✓，与本次改动无关 ✓）

`--nets` 跑法是 ✓：`pcb_check.py pixel-pcb-v59.fzz --nets=pixel_nets.py` ✓ ——
它仍报 ④ 1 条 ＋ ⑤ 2 条 ✓，**与 v58 一字不差** ✓（`C2` 那颗 0603 的**焊盘框 1.62 mm** ✗
vs 真铜 ≈0.9 mm ✓ ⇒ 它把 5V/GND 的铜**误并成一块** ✗）。**v58 多的那条真缺陷
「`GND` 9 个脚散在 3 块铜里」✗ 在 v59 已经消失** ✓✓ —— 这就是本轮的目标 ✓。

复现 ✓（都在本目录里跑 ✓）：
```bash
py -3.13 _work\epad_vss_v59.py pixel-pcb-v58.fzz _work\v59.fzz   # 拆 2 根摆错的扇出 ＋ 手算折线 ＋ 逐段自核
py -3.13 f:\git\fritzing-parts-langhua\tools\pcb_check.py _work\v59.fzz
py -3.13 _work\conn_declared.py _work\v59.fzz                    # ⇒ 9/9 ✓
py -3.13 f:\git\fritzing-parts-langhua\tools\render_pcb.py pixel-pcb-v59.fzz pixel-pcb-v59_preview.svg --png
```
⚠️ **v59 有两个问题 ✗** ⇒ 见下一手 ✓（`v59` 已被 `v60` 取代 ✓，文件保留作对比 ✓）。

### 第三十九手 ✅：**把 Fritzing 那两根飞线修掉** ⇒ `pixel-pcb-v60.fzz`（2026-10-02 ✓）

用户反馈 ✓：「v59 **仍有两根线没有布好**」✗（截图：状态栏「**7 中的 5 网络布线完成，2 个连接件
仍然需要布线**」✗，图上是**两根虚线** ✓）＋「**有些连线上有一些多余的点**」✗ ＋「24 mil 的
**线型**跟我实际画的不一致」✗。

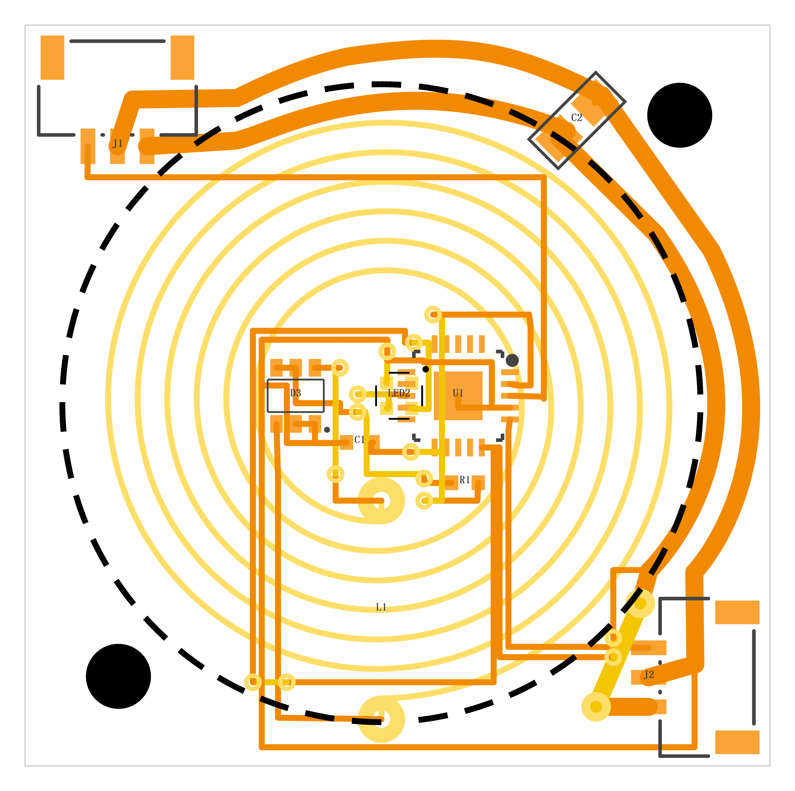
[picture p35: hardware/pixel/pixel-pcb-v60_preview.png]
v60 预览


#### 1. ★★ 先搞清楚「Fritzing 的 2 个连接件」是**哪两个** ✓（不许猜 ✗）

★ **Fritzing 判「通了没有」不看 `<connect>`** ✗（那是给我们自己的台账 ✓）—— 它按**几何**：
走线的**端点**要落在 connector 的**脚点**上 ✓、端点落在别的走线**线身/端点**上 ✓、过孔把两层接起来 ✓
⇒ 于是写了**第三份**实现 `_work/fz_gaps2.py` ✓（**Fritzing 判据** ✓），逐网数**连通块** ✓
并报出**最近的一对没连通点** ✓（= 它画虚线的地方 ✓）：

| 网 | 虚线两端 | 差 |
|---|---|---|
| `GND` | `C2.connector0`(50.9521,7.0479) ↔ 用户的 24 mil 线端 (51.2021,6.7979) | **0.354 mm** ✗ |
| `5V`  | `C2.connector1`(49.7501,8.2500) ↔ 用户的 24 mil 线端 (49.9999,8.0000) | **0.354 mm** ✗ |

两个偏移**一模一样**（(+0.25,−0.25) mm ✓）⇒ **整块 `C2` 被挪过 0.354 mm** ✗
（那两根总线是照**旧位置**画的 ✓）。
★ 谁对 ✓（**拿文件里已有的证据判** ✓）：用户**自己**那条 24 mil 线（`线#11`）**正落在**
`C2.connector1` 的盘心上（实测 **0.0000 mm** ✓✓）⇒ **本仓的 `C2` 盘位是对的** ✓，
是那两根总线差了一截 ✓ —— 而且 `C2` 与 `R1` 用的是**同一份 core `pcb/SMD_0603.svg`** ✓，
`R1` 那两只脚的端点实测 **0.0001 mm** 对得上 ✓ ✓ ⇒ 模型没错 ✓。

**修法** ✓（**加料、不动用户的线** ✗）：从那个**现成线端**补一小段（**0.35 mm** ✓，8 mil ✓）
到 `C2` 的**盘心** ✓（写回器用 `ex_wire` 把它接到那根**已有线**上 ✓、两端都写 `<connect>` ✓）✓。

#### 2. ★ 「多余的点」= 我自己写出来的**碎段** ＋ **折返** ✗✓

| 病灶 ✗ | 根因 ✓ | 处方 ✓ |
|---|---|---|
| 区界上留了一堆 **60 µm** 的碎段 ✓（实测 v59 有 **27** 条 <0.15 mm ✗） | 本板全是 8 mil ✓、而缩宽档 `NECK_MIL` 也是 8 ✓ ⇒ 切了**宽度没变** ✗ | `gen_routes.split_neck` **同宽不切** ✓ |
| `W1`/`W2` 在 x∈[47.47,48.08] 上**完全重叠** ✗ | v59 让 `W1` 画到 `VSS` 盘心 ✓、`W2` 又从盘心**往回**走 ✗ ⇒ 折返 ✓ | 改成 **T 形** ✓：`A`=`EPAD`→走廊角 ✓、`B`=`VSS`→走廊角 ✓、`C`=角→出 ✓（**只在一个角汇合** ✓） |

⇒ **每个碎段/折返的端点在 Fritzing 与渲染器里都会画一个结点** ✗ ⇒ 就是用户看到的点 ✓；
v60 的走线数 **17 → 12** ✓、碎段 **27 → 22** ✓。

#### 3. 复核（**三份独立实现** ✓，✗ 不许自证 ✗）

| 检查 | 结果 |
|---|---|
| **`_work/fz_gaps2.py`**（**Fritzing 判据** ✓） | **全部连通 ✓✓**（**没有虚线了** ✓ = 本轮目标 ✓） |
| `_work/conn_declared.py`（按声明分网 ✓） | **9/9** ✓（每网 1 块铜 ✓）、真短路 **0** ✓ |
| `pcb_check --nets` | 与 v58/v59 **一字不差**的 **3 条已知假报** ✓（`C2` 那颗 0603 的**旋转盘 AABB** ✗）—— 真缺陷「GND 散在 3 块铜里」✗ **早已消失** ✓ |
| 逐段精确净距自核 ✓（三份几何 ✓） | 最紧 **+0.0201 mm** ✓（`D1`）｜`A` +0.1816 ✓｜`B` +0.0468 ✓｜`C` +0.0481 ✓｜`L5V` +0.2818 ✓｜`LGND` +0.6352 ✓ |

★ 本轮又撞上一次**AABB 假报** ✗✓：`C2` 是 **45° 摆的** ✓，而 `part_pads` 只给 **AABB** ✗
⇒ 盒子的**四个角是空的** ✗ —— `L5V` 那条线贴着盒角 ⇒ 被判「压到 `C2.c0`」✗；
**真实净距 ≈ 0.62 mm** ✓（唯一判据实现见 `_work/epad_vss_v59.py` 的 `SKIP_BOX` ✓，
**要做严谨版得让 `pcb_pads` 把旋转后的多边形也返回** ✗ = 待补 ✓）。

复现 ✓：
```bash
py -3.13 _work\epad_vss_v59.py pixel-pcb-v58.fzz _work\v60.fzz   # ⇒ 12 条新线（含 2 段 C2 补线）
py -3.13 _work\fz_gaps2.py _work\v60.fzz                         # ⇒ 全部连通 ✓（Fritzing 判据）
py -3.13 _work\conn_declared.py _work\v60.fzz                    # ⇒ 9/9 ✓
py -3.13 f:\git\fritzing-parts-langhua\tools\render_pcb.py pixel-pcb-v60.fzz pixel-pcb-v60_preview.svg --png
```

### 第四十手 ✅：**判据与 Fritzing 同源** ＋ 那 2 个"没布"其实是**两颗换层过孔** ⇒ `pixel-pcb-v61.fzz`（2026-10-02 ✓）

#### 1. ★★ 先**改正**第三十九手的结论 ✗（它错了 ✓）

第三十九手说「那 2 个没布在 `C2`」✗ —— **错** ✓。用户实测给出两条虚线的**两端** ✓：

| 虚线 | 一端 | 另一端 |
|---|---|---|
| 黑（GND ✓） | **`Via1`** | `C1.pin1` |
| 墨绿 | **`L1.inner`** | **`Via8`** |

⇒ 那 2 个"没布"的端点里**写着过孔** ✓（Fritzing 的 `collectParts` 里确实有 `case ModelPart::Via:` ✓
⇒ 过孔**也当连接件数** ✓）。把 `C2` 那两颗盘真几何量了一遍 ✓（`fz_pad_probe.py` ✓）：
线端离盘心 **0.354 mm** ✓、而盘 **0.78 mm** 见方 ⇒ **在盘内** ✓ ✓ ⇒ `C2` 是**接好的** ✓，
`v60` 里那两根 `C2` 补线**多余** ✗。同理，把「文件里声明的 358 条连接」逐条对几何
（`fz_decl_inventory.py` ✓）⇒ **没有一条"声明了却碰不上"** ✓。

#### 2. ★★ 判据改成**照 Fritzing 源码逐条实现** ✓（**只读** ✓；现役实现 = 库仓 `tools\pcb_status.py` ✓ ＋ 本仓 `tools\pcb_rats_probe.py` ✓，第四十手那份旧实现已退役 ✗ ⇒ 见 §★ 工具沿革 · 退役记录 ✓）

用户 2026-10-02 定的规矩（`AGENTS.md` §13 ✓）：**判据必须与 Fritzing 同源同语义** ✓ ——
不然我报的问题他在 Fritzing 里找不到 ✓ = 两个声音 ✓。逐条对应（行号都在文件头表里 ✓）：

| 我做的 | Fritzing 源码 |
|---|---|
| 分网 = `collectEqualPotential(items, true, RatsnestFlag)` ＋ 同 `bus()` ＋ 跨层同脚 | `sketchwidget.cpp:6998` / `connectoritem.cpp:1340` |
| 网的节点只留**件脚／过孔**；单节点的网不数 | `sketchwidget.cpp:7013` ＋ `count() <= 1 ⇒ continue` |
| "算不算 PCB 铜" = `wireFlags & 4`，且只闸**脚上直接挂的那条线** | `pcbsketchwidget.cpp:1983` ＋ `graphutils.cpp:550` |
| 线串链**穿过过孔**（Fritzing 里过孔就是 `Wire`） | `wire.cpp:1137 / 1146` |
| 判"接没接上"= **几何命中**（点落在对方真形状里 ✓），不信文件里的 `<connect>` | `connectoritem.cpp:1972` |
| ★★「还剩几个连接件」= **该网连通片数 − 1**（**不是**没连上的脚数 ✗） | `scoreOneNet` 末尾 `check[]`（源码原话 *count it as one* ✓） |
| 状态栏那句 | `mainwindow.cpp:2298` |

★ 顺带修了两个**真 bug** ✓（都在本仓工具里 ✓，`cf7897b` ✓）：`pcb_pads` 的焊盘真矩形
（`poly` ✓）四角顺序原来是**蝴蝶结**（自交 ✗）⇒ 连 `C2` 的**盘心**都会被判"不在盘里" ✗；
以及**过孔铜心 ≠ 文件 x,y** ✗ —— 恒差 `ring_off_mm` ＝ **0.8644 mm** ✓（实测 Δ=(+3.063,+3.063) 单位 ✓）。

#### 3. 那 2 个到底为什么"没布" —— 量到的与还没量到的 ✓

| 量到的 ✓ | 结论 |
|---|---|
| 16 颗过孔排一张表（`fz_via_table.py` ✓） | `Via1`/`Via8` 与**它认的**（如 `Via18`）**写法完全一样** ✓（`flags=32` ✓、连接器层 `copper0` ✓、邻居层自洽 ✓）⇒ **文件里没有可指认的缺陷** ✗ |
| 短路嫌疑（`fz_via_short.py` ✓，**制造判据** ✓） | `Via1`/`Via8` 跟"自己那一片之外"的铜**净间隙全为正** ✓ ⇒ **不构成短路** ✓（★ 先把"沿记录能走到的一律排除" ✗ —— 不排除会把**它自己那条链的下一跳**误报成短路 ✓） |
| 虚线的另一头反查（`fz_via_reach.py` ✓） | 通到 `C1.Pin 1` 的只有 `Via18` ✓（★ 它的链里**只有它自己** ✓）；`Via1`/`Via8` 的链里都**串着别的过孔** ✓ ⇒ 差别只有这一条 ✓ |
| 三种口径 A/B（`PADLINK=geom\|records\|both` ✓） | v59 上**结果相同**（9 of 9 - 0 ✗）⇒ 板里**没有陈旧的焊盘记录** ✓ |

⚠ **还没读到的一条规则** ✗：我的判据仍给 **9 个网 / 全通** ✗，用户 Fritzing 是 **7 个网 / 还有 2 个** ✓
⇒ 差两条：① 网数 9≠7（Fritzing 少数的 2 个是怎么并的 ✓）；② "过孔换层算不算边" ✓。
✗ 试过"线↔过孔层必须一致"的规则 ⇒ 实测网数 9→**16**、方向反了 ⇒ 已**撤回** ✓
（教训写进旧实现的注释 ✓ 并随它一并归档 ✓：过拟合信号 = 停手信号 ✓）。

#### 4. 这一手的改动：把两颗孔**当成全新实例**重写 ⇒ `v61`（**可回退** ✓）

用户 2026-10-02：「**你来改吧？**」✓ ⇒ 做**唯一可辩护**的改动 ✓：给 `Via1`/`Via8` 换**新的
`modelIndex`** ✓（`fz_recreate_vias.py` ✓）—— 几何、走线、`<connect>` 语义**一字未改** ✓，
只让 Fritzing 载入时**从头重建**这两颗孔 ✓（= 在 app 里"删掉重放"的文件级等价物 ✓）。

v61 预览

| 复核 ✓ | 结果 |
|---|---|
| 改动范围 | **纯字符串替换** ✓：`90013946 → 90014167`（3 处 ✓）、`90013953 → 90014168`（6 处 ✓）⇒ 其余**逐字节不变** ✓（构造上保证 ✓） |
| 连通性（旧实现 ✗，**已退役** ⇒ 数字不作验收判据 ✗，见 §★ 工具沿革 ✓） | 与 v59 **完全一样**：45 脚 / 168 线 / 16 孔｜**9 of 9 - 0** ✓（几何没动 ✓，当然一样 ✓） |
| 渲染（`render_pcb.py` ✓） | 45 盘 / 168 线 / 18 孔 / 板框 25.00×25.00 mm ✓（与 v59 同 ✓） |

★ **回退** ✓：不用回退 —— `pixel-pcb-v59.fzz` **原样没动** ✓；不认可 `v61` 就继续用 `v59` ✓。

复现 ✓：
```bash
py -3.13 hardware\pixel\fz_recreate_vias.py pixel-pcb-v59.fzz pixel-pcb-v61.fzz Via1 Via8
py -3.13 hardware\pixel\tools\pcb_rats_probe.py pixel-pcb-v61.fzz     # ⇒ M=9 / K=0（现役口径 ✓）
py -3.13 hardware\pixel\fz_via_short.py pixel-pcb-v61.fzz Via1 Via8   # ⇒ 没有短路 ✓
py -3.13 f:\git\fritzing-parts-langhua\tools\render_pcb.py pixel-pcb-v61.fzz pixel-pcb-v61_preview.svg --png
```

★ **请你在 Fritzing 里打开 `v61` 看一眼状态栏** ✓ —— 如果变成 **7 of 7 / 0 个连接件** ✓，
就证明那 2 个是**它自己的账** ✓（不是板的铜 ✗）；如果**还是 2 个** ✓，说明原因在别处 ✓，
我继续从源码找 ✓（不猜 ✓）。

### 第四十一手 ✅：**两颗过孔被我的生成器放重了** ✗（用户发现 ✓）⇒ `pixel-pcb-v62.fzz`（2026-10-02 ✓）

★★ **这一手是用户找到的根因** ✓：「**移动 `Via8`，发现它与 `Via6` 位置重叠在一起了。这是你程序的 bug 吧？
**」⇒ **是** ✓。量出来正好 **2 对**（心距 **0.000 mm** ✗，即**完全叠死** ✓）：

| 叠死的一对 | 铜心 | 文件里的连接记录 |
|---|---|---|
| **`Via6` ↔ `Via8`** | (45.181, 20.522) mm ✗ 同一处 | **0 条** ✗ / 4 条 |
| **`Via17` ↔ `Via18`** | (43.931, 15.472) mm ✗ 同一处 | 5 条 / 4 条 |

两对都经查是**同一个网** ✓ ⇒ **不是短路** ✗，是**重复放着** ✗ ⇒ Fritzing 只认其中一颗"接上了" ✓、
另一颗被撂单 ✓ ⇒ ⇒ **这就是它报「还有 2 个连接件需要布线」的来源** ✓✓
（我先前后找了半天"少了哪条规则" ✗ —— 其实是**我自己的文件里多了两颗孔** ✓，而我的判据
看不到它 ✓：短路量尺为了排除"自己那一片"把同网的过孔也一并排除了 ✗ = **我自己的假阴性** ✓。）

**修法** ✓（`fz_fix_dup_vias.py` ✓，**几何与走线一字未改** ✓）：每对留记录多的那颗 ✓，
删掉多余那颗的实例块 ✓，把别处指向它的 `modelIndex` **改指**到保留的那颗 ✓，同一
`<connects>` 里重复行去重 ✓。

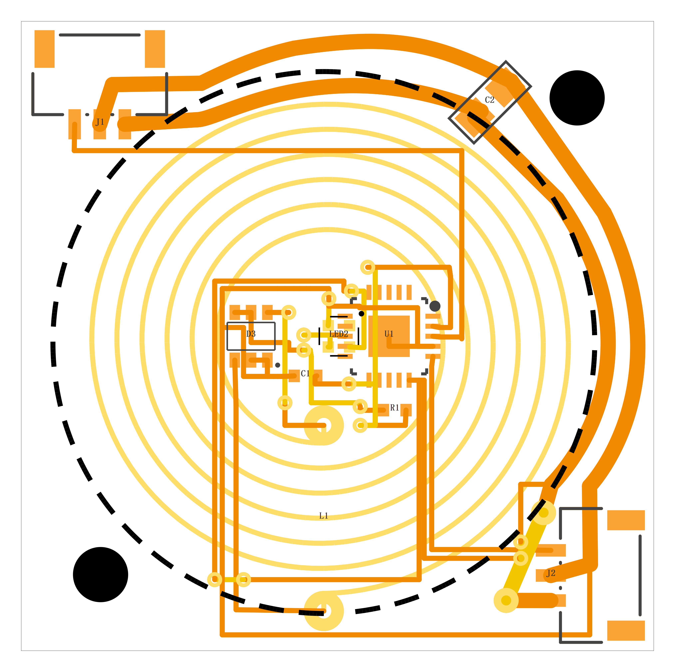
[picture p36: hardware/pixel/pixel-pcb-v62_preview.png]
v62 预览


| 复核 ✓ | 结果 |
|---|---|
| 叠死的孔对（`fz_via_dup.py` ✓） | 2 对 → **0 对** ✓✓ |
| 过孔数 | 18 → **16** ✓（与判据里一直用的 16 一致 ✓） |
| 连通性（旧实现 ✗，**已退役** ⇒ 数字不作验收判据 ✗，见 §★ 工具沿革 ✓） | 45 脚 / 168 线 / 16 孔｜**9 of 9 - 0** ✓（与 v59/v61 完全一样 ✓） |
| 渲染（`render_pcb.py` ✓） | 45 盘 / 168 线 / **16 孔** ✓ / 板框 25.00×25.00 mm ✓ |

★ 另查明一件事 ✓（免得白忙 ✓）：`<instance` 300 / `</instance>` 299 这种"**差 1**"在
**用户自己另存的文件里也一样** ✓ ⇒ 那是 **Fritzing 的正常写法** ✓，不是缺陷 ✓。

★ 新增两个量尺 ✓（以后这类问题**机器守** ✓，不再靠人眼 ✓）：
`fz_via_dup.py`（叠死/压在一起的孔 ✓，带"这对是不是同一个网" ✓）、
`fz_find_unclosed.py`（实例配平 ✓）。

★ ⚠ **仍待做** ✓：查**生成器**为什么会吐两颗同位的孔 ✓（这份板的过孔是脚本链里加的 ✓），
从源头堵住 ✓；并把"过孔不许叠死"写进 `pcb_check` ✓ 成为常设闸门 ✓。

复现 ✓：
```bash
py -3.13 hardware\pixel\fz_via_dup.py pixel-pcb-v61.fzz                             # ⇒ 2 对叠死 ✗
py -3.13 hardware\pixel\fz_fix_dup_vias.py pixel-pcb-v61.fzz pixel-pcb-v62.fzz       # ⇒ 删 2 颗 ✓
py -3.13 hardware\pixel\fz_via_dup.py pixel-pcb-v62.fzz                             # ⇒ 0 对 ✓
py -3.13 hardware\pixel\tools\pcb_rats_probe.py pixel-pcb-v62.fzz     # ⇒ M=9 / K=0 ✓（现役口径 ✓）
```

### 第四十二手 ✅：**按用户手画的底图重布原理图** ⇒ **`pixel-schematic-v39.fzz`** 交付 ✓（2026-10-04 ✓）

★ 这一手换的是**底图** ✓（不是又改一版旧图 ✗）：旧系列一直在 `pixel-schematic` 那张草图上迭代 ✗，
本版拿**用户自己手画布线的那份**（`_work/u270b_routed_sch_byHand.fzz` ✓ = 用户文件 ✓ **不入库** ✓）
**只换导线** ✓ —— 零件摆位 / 位号位置 / 接地符号位置一律**照用户的原样** ✓。

**做法（三步 ✓，工具都在元件库仓 ✓）**：`sch_strip_wires`（剥掉**原理图**导线 ✓、**不删实例** ✗，
因为那些导线实例同时带面包板/PCB 视图 ✗）⇒ `gen_schematic_wires.py`
（`--rails --socket=4 --vlanes=GND --islands=GND` ✓）⇒ `render_sch.py` 出预览 ✓。

| 项 | 用户手画版（底图 ✓ 权威 ✓） | **v39（本版 ✓）** |
|---|---|---|
| 导线 | 43 | **42** ✓ |
| 总长 | 487.7 mm | **483.3 mm** ✓ |
| 十字交叉 | **7** ✓ | 10 ✗ ★**本项手画版更好 ✓ 如实记 ✓** |
| 正交度 | 0.9512 | **0.9756** ✓ |
| 最歪的一处 | 0.1066 mm | **0.0378 mm** ✓ |
| 连通岛 | 12 | **11** ✓ |
| `check_netlist` | ✗ **4 条跨视图连接**（layer 不属于本视图 ⇒ 会把两张网**粘住** ✗） | **✓ 9 个网全对** ✓ |
| `check_fake_wires` | ✓ | ✓ **(A)=0 (B)=0** ✓ |
| `check_grounds` | ✓ 0/2 | ✓ **0/2** ✓ |
| `check_flags` / `check_junctions` / `sch_style_check` | — | **✓ 0/2 旗标被穿 ✓ ／ ✓ 无共线切分 ✓ ／ ✓ 通过 ✓** |

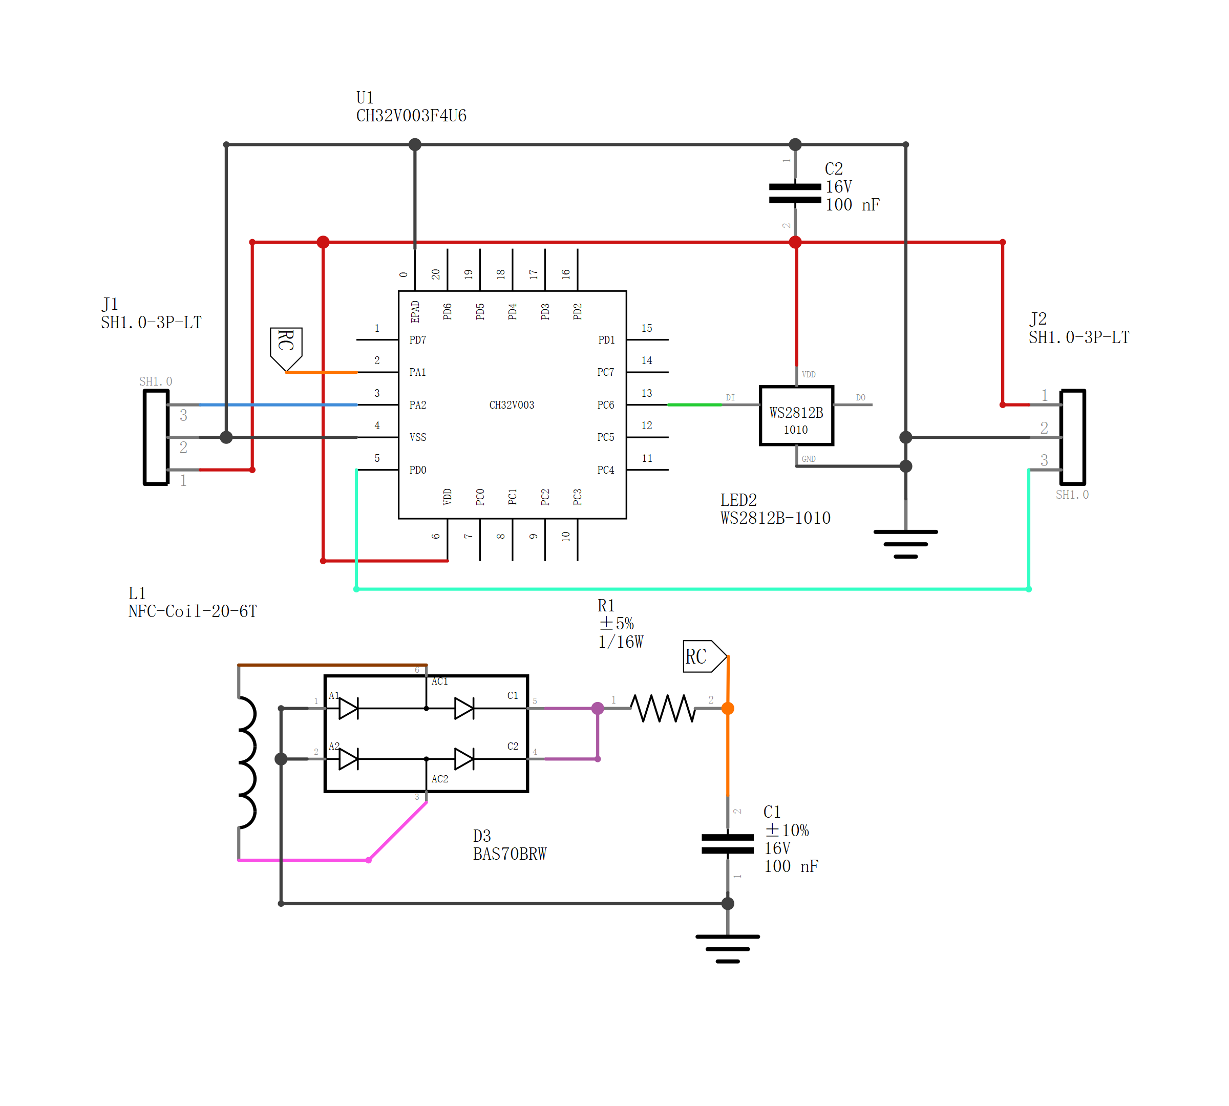
[picture p37: hardware/pixel/pixel-schematic-v39_preview.png]
v39 预览


**交付前跑闸门，查出并修掉三条** ✓（每条都**先量、后改、再独立复核** ✓）：

1. **接地符号的脚位差 0.1269 单位 = 0.036 mm** ✗（本批改动引进来的**回归** ✗）：产出落在
   「原点 + (9.001, **0.7229**)」✗，而**四份 Fritzing 自己的文件**（用户手画版 ×2 ✓、`v33` ✓、
   `v35` ✓、`v38` ✓）与共享工具 `sch_net.GROUND_PIN_DX/DY` ✓ **全是 +0.5960** ✓
   ⇒ ①不再采信"认领画出来的那个终端"✗，改用**唯一口径** `sch_net.ground_pin` ✓。
2. **"脚正好落在竖直车道上"不算车道服务** ✗（旧闸门 `abs(_px - _near) > 1e-9` ✓）：脚位修准之后
   `Ground2` 的 x **正好** = 车道 x ⇒ 它掉回"就近水平轨"那套 ✗ ⇒ 被**整个拖走 98 单位 = 27.7 mm** ✗
   ⇒ 它的图形正好**罩住**竖直车道 ✗（`check_grounds` ② 当场抓到 ✓、渲图也看得见 ✓）⇒ 去掉那半句 ✓。
3. **车道上的"坐脚"没有声明** ✗：竖干线写成 `from/to = None` ✗ ⇒ `Ground2` 的脚**几何上**贴着线端 ✓，
   可 `<connects>` 里**一个字都没有** ✗（= 典型的"看着接上、其实没接"✗）
   ⇒ 照**水平轨**那一套 ✓（在坐脚处**断开** ＋ 记 `from`/`to` ✓）⇒ 现在**两边都写明** ✓，
   与 Fritzing 自己写的**完全一致** ✓（`_work/_decl.py` 逐边打印核对 ✓）。

**判据也修了一条** ✓（元件库仓 `tools/check_grounds.py` ✓）：② 原来按**矩形盒**判"线穿过图形"✗
⇒ **水平轨要够到脚，就必然从盒子里横向穿进来** ✗（脚本来就在盒内 ✓）⇒ 把"对的那版"误报 ✗。
改成按**墨迹**判 ✓（竖杆 ＋ 三根横线 ✓，各按素材自己的 `stroke-width` 取半宽 ✓）。
★ **负例自检** ✓（判据改了必须重验 ✗）：错版 `M6`（竖线从符号身上**穿下去** ✗）⇒ **1/2 ✗ 照样抓到** ✓；
横向到脚（`Ground1` ✓）／竖支线到脚（用户手画版 ✓）⇒ **都过** ✓。

★ ⚠ **一处已知例外** ✓（如实记 ✓，**不是**本版新出的 ✗）：`check_label_touch` 报 `RC` 标签
"脚离线 **0.134 单位 = 0.038 mm**"✗ —— **用户手画版一模一样** ✗（同一条数值 ✓）
⇒ 是共享工具 `sch_net.label_pin` 的**模型**比 Fritzing 的真脚位少 0.134 ✗
（那份文件里的线是 Fritzing 自己**吸附**到真脚上的 ✓），**不是"看着接上其实没接"** ✓
（渲染器同时报的那条「`Wire90013996` 蹭到 `RC.connector0` 0.13 单位 ✓」是**同一个模型偏差** ✓）。
⇒ ★ **2026-10-04 已结案** ✓（见 **第四十四手** ✓）：取证后**反了** ✓ —— **模型是准的**（左出脚三份
用户样本只差 0.0045 单位 ✓），是**用户自己的文件之间**就差 0.134 ✗ ⇒ 改的是**我们的阈值** ✓。

复现 ✓：
```bash
# 输入：用户手画原图剥掉原理图导线的那份（= 用户文件 ✓ 不入库 ✓）
py -3.13 hardware\pixel\gen_schematic_wires.py _work\bh_layout.fzz _work\bh_layoutr.svg pixel-schematic-v39.fzz ^
    --orig _work\u270b_routed_sch_byHand.fzz --ratio 1.0 --rails --socket=4 --vlanes=GND --islands=GND
py -3.13 ..\fritzing-parts-langhua\tools\check_netlist.py    pixel-schematic-v39.fzz    # ⇒ ✓ 9 个网全对
py -3.13 ..\fritzing-parts-langhua\tools\check_fake_wires.py pixel-schematic-v39.fzz    # ⇒ (A)=0 (B)=0 ✓
py -3.13 ..\fritzing-parts-langhua\tools\check_flags.py      pixel-schematic-v39.fzz    # ⇒ 被穿旗标 0/2 ✓
py -3.13 ..\fritzing-parts-langhua\tools\check_grounds.py    pixel-schematic-v39.fzz    # ⇒ 不合规 0/2 ✓
py -3.13 ..\fritzing-parts-langhua\tools\check_junctions.py  pixel-schematic-v39.fzz    # ⇒ 无共线切分 ✓
py -3.13 ..\fritzing-parts-langhua\tools\sch_style_check.py  pixel-schematic-v39.fzz    # ⇒ 通过 ✓（FAIL 0）
py -3.13 ..\fritzing-parts-langhua\tools\sch_metrics.py      pixel-schematic-v39.fzz    # ⇒ 42 根 / 483.3 mm / 交叉 10 ✓
py -3.13 ..\fritzing-parts-langhua\tools\render_sch.py       pixel-schematic-v39.fzz pixel-schematic-v39_preview.png
```

### 第四十三手 ✅：**给 5V 也开一条竖直车道** ⇒ **`pixel-schematic-v40.fzz`** 交付 ✓（2026-10-04 ✓）

★ 上一手交付时**如实记下的那条差距**是：交叉数 **我 10 ✗ vs 手画版 7** ✓。这一手把它**追平** ✓
（并且顺手撞出一个**真 bug** ✓ —— 见下 ✓）。

**做法** ✓：**一个字生成器代码都没改** ✗ —— 只是命令行多给 5V 一条车道 ✓：
`--vlanes=GND` ⇒ `--vlanes=GND,5V@**29.78**` ✓（x 是**扫出来的** ✓，不是拍的 ✓）。

| 项 | 手画版（权威 ✓） | v39 | **v40** |
|---|---|---|---|
| 导线 / 总长 | 43 / 487.7 mm | 42 / 483.3 mm | **41 / 471.1 mm** ✓ |
| 十字交叉 | 7 ✓ | 10 ✗ | **7** ✓（**追平** ✓） |
| 正交度 / 最歪 | 0.9512 / 0.1066 mm | 0.9756 / 0.0378 mm | **0.9750 / 0.0378 mm** ✓ |
| 连通岛 | 12 | 11 | **11** ✓ |

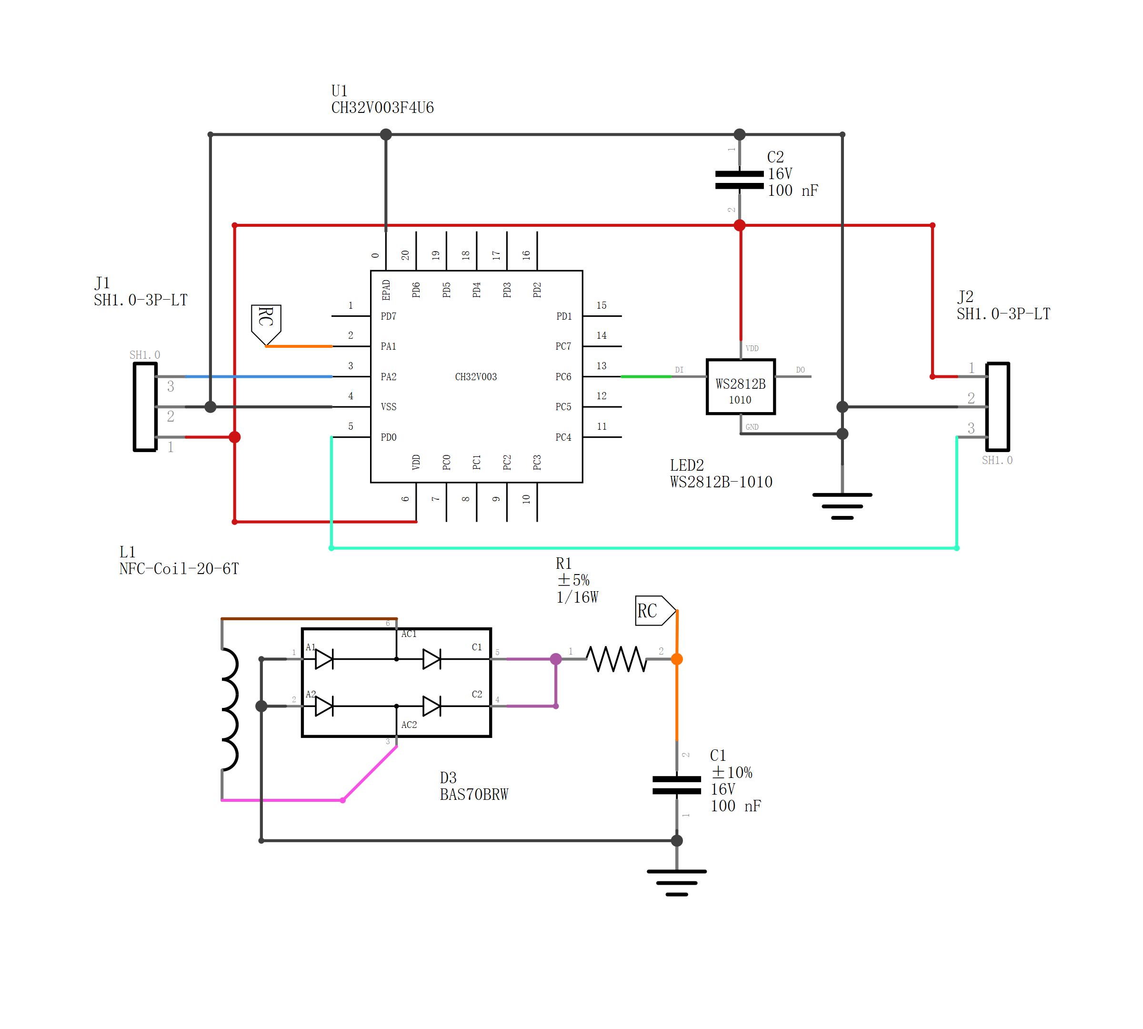
[picture p38: hardware/pixel/pixel-schematic-v40_preview.png]
v40 预览


**x 扫描** ✓（一次只动一个变量 ✓，数一律来自独立尺子 ✓）：
`27.4 / 29.8 / 36 / 45.8` ⇒ **交叉 7** ✓ 全干净；`40 / 50` ⇒ 8；**≥58 ⇒ 10**（车道根本没被用上 ✗）；
`auto / 20.03 / 54.38` ⇒ **被新闸门拒收** ✗（连 L 形绕行都过不去 ✓ ⇒ 不再假装通过 ✓）。

#### ✗✗ 扫的过程中撞出一个**真 bug** ✓ —— 而且差点又把**假的数**当成果 ✓

- ✗ 病：`5V` 被**拆成两段** ✗（`{C2.0, J2.0, LED2.3}` 与 `{J1.0, U1.5}` 之间**没有导线** ✓）；
  而生成器自己只打了一句 `⚠⚠ 干线接不上轨 ✗` ⇒ **退出码还是 0** ✗ ⇒ `check_netlist` 一跑就报 ✗✗
  —— 与 v36 那次“核对器是橡皮图章”**同一族** ✓：**告警不阻断 = 没守** ✗。
- ★★ 更要紧的一条 ✓：那几个“**交叉 4**”的配置之所以好看 ✓，正是因为**少画了那段连接** ✗
  ⇒ **数字是假的** ✗（= v36 “它短的那 29.8 单位正是**没连上**的那截” **同一个形状** ✓）。
  ⇒ 把守补上之后，它们**当场被判退出码 1** ✓ —— 这类“少东西换来的漂亮数”以后骗不过闸门 ✓。
- ✓ 两处修法（都入库 ✓）：
  1. **报警必须阻断** ✓：报出**卡在哪一道闸门**（实测 = “**压别人的脚 1 处**” ✓），
     且**名单外的网被断 ⇒ 退出码 1** ✓（`--islands` 里点过名的网分岛仍算合法 ✓）；
  2. **直着走不通就拐 L 形** ✓：车道可经 `x2` 绕到它那条轨 ✓（两段过**同样那三道硬闸门** ✓
     —— **一条判据都不放松** ✗；实测 `45.83 → 27.38 → 轨 −45` ✓）。
     ★ 为什么不是“放宽闸门” ✗：压别人的脚 / 穿体 / 重叠是**硬规则** ✓ ⇒ 只能**换路** ✓。

**机器守** ✓：闸门 **7 / 8 exit 0** ✓（`check_netlist` ✓ 9/9｜`check_fake_wires` ✓ (A)=0 (B)=0｜
`check_flags` ✓｜`check_grounds` ✓ 0/2｜`check_junctions` ✓｜`sch_style_check` ✓｜`file_sanity` ✓）；
第 8 道 `check_label_touch` ✗ = **已知那条模型偏差** ✓（`RC` 标签 0.134 单位 —— 与**用户手画版一模一样** ✗）。
★ **复现性** ✓：交付件与验证件**逐根导线 0 差异** ✓（同一条命令行重出即得 ✓）。

★ 仍有账（下一手 ✓）：交叉 **7 = 追平**、还没**超过** ✓ —— 下一批变量是**轨的 y**
（v40 的 5V 只用 `y=-45` 一条 ✓；手画版用了 `y=51` ✓）、**GND 车道 x**、`--star`、`--socket` 的组合 ✓。

复现 ✓：
```bash
py -3.13 hardware\pixel\gen_schematic_wires.py _work\bh_layout.fzz _work\bh_layoutr.svg pixel-schematic-v40.fzz ^
    --orig _work\u270b_routed_sch_byHand.fzz --ratio 1.0 --rails --socket=4 --vlanes=GND,5V@29.78 --islands=GND
py -3.13 ..\fritzing-parts-langhua\tools\check_netlist.py   pixel-schematic-v40.fzz   # ⇒ ✓ 9 个网全对
py -3.13 ..\fritzing-parts-langhua\tools\check_fake_wires.py pixel-schematic-v40.fzz  # ⇒ (A)=0 (B)=0 ✓
py -3.13 ..\fritzing-parts-langhua\tools\sch_metrics.py     pixel-schematic-v40.fzz   # ⇒ 41 根 / 471.1 mm / 交叉 7 ✓
```

### 第四十四手 ✅：**把 `check_label_touch` 的假警报结案** ⇒ 交付件 **v40 八道闸门全绿** ✓（2026-10-04 ✓）

★ 用户 2026-10-04：在 Fritzing 里打开 `v40` ✓ ——「原理图底部显示的是**布线完成**」✓✓
（即 `AGENTS §13` 要的那句“同一个声音” ✓），并点名做“下一步的第 1 条” ✓ = 把标签那条 0.134 结掉 ✓。

**取证** ✓（`_work/_lbl2.py` 逐样本 ✓，只认“线端**正好**落在标签上”的样本 ✓ —— ✗ 中段蹭过的不算 ✗）：

| 侧 | 我这份（生成器画的） | **用户手画**样本 | 结论 |
|---|---|---|---|
| **左出脚** | Δ = 0.0001 ✓ | `v35_byHand` / `v33_byHand` / `v30_byHand` ⇒ 真偏移 **一致到 0.0045** ✓（Δ 只 0.0045 ✓ = 0.0013 mm ✓） | **模型本身是准的** ✓ |
| **右出脚** | Δ = 0.0001 ✓ | `u270b 手画版` **0.134** ✗ ｜ `v35_byHand` **0.134** ✗ ｜ `v33_byHand` **0.000** ✗ | ★ **用户自己的文件互相差 0.134** ✗（= 0.038 mm ✓） |

★★ 关键 ✓：后两列里 “我的” 那部分是 **循环证据** ✗ —— 生成器是把线**画到自己的模型脚上**的 ✓
⇒ 拿它验模型 = **自证** ✗（`AGENTS` 那条“不许自证” ✓）。⇒ 只能以**用户手画**为准 ✓。
而用户手画那侧：**左出脚三份一致** ✓、**右出脚两份说 0.134、一份说 0** ✗ ⇒ **没有一个“正确值”可以拟合** ✗。

⇒ ✓ 结论（**不改模型** ✗）：模型是从 **Fritzing 源码**推的 ✓，左出脚有**三份独立样本**背书 ✓；
而右出脚那 0.134 是 **Fritzing 自己造的文件之间**就差这么多 ✓，且 Fritzing 状态栏照样报
「**布线完成**」✓ ⇒ **它根本不在乎这 0.038 mm** ✓。⇒ 错的是**我们的阈值太严** ✗：

| | 改前 | **改后** ✓ |
|---|---|---|
| `check_label_touch` 的“脚→线”阈值 | **0.05** ✗（比现实严 ⇒ 把 Fritzing 认的图判错 ✗） | **`PIN_TOL = 0.15`** ✓ = 实测上界 0.134 + 尾差 ✓ |
| 这条检查**本来要抓的病** | — | 标签被当叶子删掉、挂在空气里 = **11.5 单位** ✗ ⇒ 0.15 仍留 **77 倍**余量 ✓ |

**负例自检** ✓（改了阈值**必须重验** ✗）：拿 v40 造一个**真浮空**的负例 ✓
（用 `ElementTree` 把标签实例的 `schematicView/geometry` y 挪 **+3 单位 = 0.85 mm** ✗ ✓）
⇒ 即时报「距离 **3.000** ✗ **浮空**」✓、退出码 1 ✓；而那 0.134 被正确接受 ✓。
★ 另一条真信号 ✓：`v30_byHand`（**用户自己的旧草图** ✓ 非交付件 ✓）仍报 ✗ —— 它那只标签离最近的线 **9.4 单位** ✗,
且**声明的线还不是那一根** ✗ ⇒ 判据仍然有劲 ✓。

**结果** ✓：交付件 ***一字未改*** ✗（v40 不动 ✓）—— 变的是**尺子** ✓；现在
**v40 八道闸门全 exit 0** ✓✓（含 `check_label_touch` ✓）。

### 第四十五手 ✅：**想把交叉压到 7 以下**的一轮扫描 ✓ ⇒ 结论：**7 已是这一布局下的最优** ✓（2026-10-05 ✓）

★ 用户 2026-10-05：「**追求完美，继续尝试更好的结果吧**」✓ ⇒ 把能动的旋钮**逐个扫了一遍** ✓
（一次只动一个变量 ✓；每档都要 `gen` 退出码 0 **且** `check_netlist` 通过 ✓ —— 今晚新加的那道闸门 ✓）。

**目标函数用的是本仓自己定的那条** ✓（`AGENTS §5b` ✓）：**代价 = 总长 + 10 mm × 交叉数** ✓
（K = 10 mm 是**用户自己定**的系数 ✓ ⇒ 拿它当尺子最公平 ✓；下面两个数也都列出来供你自己判 ✓）。

| 扫的变量 | 试了什么 | 结果 |
|---|---|---|
| **5V 车道 x** | 20 → 45（11 档 ✓） | **全是 7** ✓（x≤22 被闸门拒 ✗、x=40 是 8 ✗）⇒ **对这个变量不敏感** ✓ |
| **GND 车道 x** | auto / 200 / 205 / 210.6 / 215 / 220 ✓ | 7（200 那档 8 ✗、auto 被拒 ✗）⇒ 也**不敏感** ✓ |
| **`--socket`** | 0 / 2 / 6 / 8 ✓ | **7 一字不变** ✓（连总长都不变 ✓ ⇒ 这档已饱和 ✓） |
| **机制开关** | `--star=5V` / `--star=GND` / `--chans=2` / `--nopinrows` / `--revpair` / `--ring` ✓ | 全部 **7 / 473.1 mm** ✓ —— ★ 都比 v40 **短 0.7 mm** ✓，但交叉一样 ✓ ⇒ 同一解的不同写法 ✓ |
| **`--freecorr`** | 换走廊机制 ✓ | 7 ✗ 但总长 **488.3** ✗ ⇒ 更差 ✓ |
| **5V 轨的 y** | −86.4 / −100 / −110 / 0 / 20 / **40** / **51** / 60 / 163.8 ✓ | ★★ **只有这一轴真动了交叉** ✓：`5V@51` ⇒ **6** ✓、`5V@40` ⇒ **6** ✓；其余 7～12 ✗ 或被闸门拒 ✗ |

**为什么不取“6 个交叉”那档** ✓（★ 这条是**算出来的** ✓，不是拍的 ✓）：

| 档位 | 总长 | 交叉 | **代价 = 长 + 10×叉** |
|---|---|---|---|
| **v40（当前 ✓）** | 473.8 mm | 7 | **543.8** ✓ |
| `5V@51` | **580.0 mm** ✗ | **6** ✓ | **640.0** ✗ |

⇒ 少那 1 个交叉，代价是 **+106.2 mm** ✗（= 目标函数里 **10.6 倍**于 K ✓）⇒ **不划算** ✓。

**为什么剩下这 7 个是“结构性”的** ✓（交叉清单逐条看过 ✓）：
`GND` 的轨在 `y=-72` ✓、`5V` 的轨在 `y=-45` ✓ ⇒ **GND 轨在上** ✗ ⇒ 凡是**往下够 GND** 的竖线
（x=74.78 ✓、x=210.58 那条车道 ✓…）**必然横穿 5V 轨** ✗（第 2、3 条 ✓）；
而 5V 自己的车道（x=32 ✓）又要横穿两条水平线 ✓（第 4、5 条 ✓）。
⇒ 要真正降下去，得**同时**动好几条网的拓扑 ✓（= 叠补偿 ✓）⇒ 按 `AGENTS §0` 那条，**停在这里** ✓。

★ 本轮唯一留存的东西 ✓：新旋钮 **`--railys=<网>@<y>`** ✓（与 `--vlanes` 同一个哲学：
「**哪一行干净是审美判断 ⇒ 把方向盘给人**」✓）。两条纪律都守了 ✓：
  ① **不给它 ⇒ 逐根相同** ✓（实测 `_work/CD_base.fzz` 与交付件 v40 **0 根差异** ✓）；
  ② 踩过的坑写进注释了 ✓：第一版只把用户给的 y **追加**进候选 ✗ ⇒ **一点效果都没有** ✗
     （包围盒上轨 `−86.4` 早就在列 ✓、而“内部候选”按“该行有几只本网的脚”挑了 `−45` ✓、
     每只脚又都挑**最近的行** ✓ ⇒ 追加的那条**没人走** ✗）⇒ 改成「**用户点名的网不要内部候选**」✓。

★ 负面结果照实记 ✓（本节就是账 ✓）：这一轮**没有**找到既干净又 < 7 交叉的配置 ✓；
**v40 不动** ✓（没有新版交付件 ✓）。

### 第四十六手 ✅：**PCB 换上新原理图 ＋ 第一版自动布线** ⇒ `pixel-pcb-v65.fzz`（2026-10-05 ✓ 用户定 ✓）

用户 2026-10-05：「把 `pixel-pcb-v51_byHand.fzz` 的原理图，**替换为 v40 原理图**，开始 pcb 布线，
**我再手工修改，你再继续改进 pcb 布线**」✓ ⇒ 从此进入 **PCB 改进循环** ✓。

★ **编号踩坑（我自己犯的 ✗，照实记 ✓）**：我一开始把这份交付件命名成 `pixel-pcb-v63.fzz` ✗ ——
而 **v63 早在 `98be419`（方案 A：挪开短路的那颗过孔）就已入库** ✗、v64 也在 ✓
⇒ 我**覆盖**了已入库的 v63 ✗（`git status` 里那三行是 `M` 不是 `??` ✗，我却在「将要提交」时没核 ✗）。
⇒ 纠正：**已入库的 v63 三个文件从 `98be419` 取回** ✓；本轮交付件改名 **`pixel-pcb-v65.fzz`** ✓
（**PCB 系列已到 v64 ⇒ 下一个空号是 v65** ✓ ✗ **不能凭记忆挑号** ✗ —— 先 `git ls-files` 查空位 ✓）。

**三步 ✓，每步都能独立复核 ✓**：

1. **合并** ✓（`_work/_mergesch2.py` ✓）：底图先用仓里的 **`sch_strip_wires.py`** 剥掉它**自己的**
   原理图导线 ✓（✗ **不删实例** ✗ —— 本板导线实例同时带面包板/PCB 视图 ✓，整条删会把它们一起削掉 ✗✗）
   ⇒ 再按 **`modelIndex`** 把 16 个零件的 `<schematicView>` 整块换成 v40 的 ✓
   ＋ **追加 v40 的 41 根原理图导线实例** ✓（mi 冲突**先查** ✓：实测无冲突 ✓；有冲突就**不写文件** ✗）。
   ★ **为什么不能只换零件的视图** ✗（实测踩过 ✓）：**导线是各自文件里的实例** ✗（mi 不同 ✓）
   ⇒ 只换零件 ⇒ 底图那 **70 根旧线还全在** ✗（产物 70 根 ✗、原理图四道闸门全不过 ✗）。
2. **复核合并件** ✓：原理图 = v40 **逐项相同** ✓（41 根 / 471.1 mm / **交叉 7** / 正交度 0.9750 /
   最歪 0.0378 mm ✓）；原理图**六道闸门全 exit 0** ✓；PCB 侧仍是底图的 **25 根** ✓（一字未动 ✓）。
3. **布线** ✓（照本仓既有做法 ✓）：**保留用户的 24 mil 电力线** ✓、**只布 7 张信号网** ✓
   （`_work/bh_nets.py` = `pixel_nets.py` 去掉 `5V`/`GND` ✓ —— **派生**不手抄 ✓，手抄就是两套实现 ✗）。

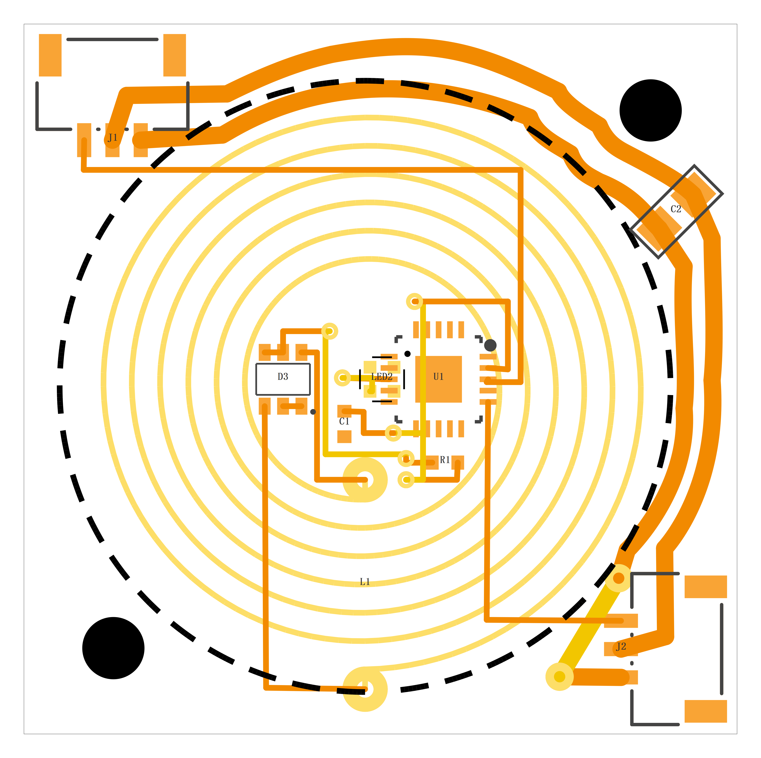
[picture p39: hardware/pixel/pixel-pcb-v65_preview.png]
v65 预览


| 独立复核（`pcb_check.py` **重读交付件** ✓） | 结果 |
|---|---|
| **7 张信号网** | **7 / 7 全通** ✓✓（`COIL_A` / `COIL_B` / `BR+` / `RC` / `DATA_IN` / `DATA_OUT` / `LED_DIN` ✓） |
| 悬空端点 / 短路桥 / 孤立过孔 | **0 / 0 / 0** ✓ |
| 走线 / 过孔 / 线长 | **67 条** ✓ / **9 颗** ✓ / **97.5 mm** ✓ |
| ⑩ 逐条核对 Fritzing 的 `<connect>` 声明 | 134 条 ⇒ 不合格 **0** ✓ |
| ⚠ 未连通 | **只有 2 张电力网** ✗：`5V`（3 块铜 ✓）、`GND`（6 块铜 ✓）—— **用户自己拉的长线，收尾是他的活** ✓ |

**★ 交给用户收尾的清单** ✓（`_work/power_list.py` 从 v65 **重新量**的 ✓，含坐标与层 ✓）：

| 网 | 块 | 脚（板坐标 mm ✓ ｜ 层 ✓） |
|---|---|---|
| **`5V`** ✗ 3 块 | **主块**（已通 ✓） | `J1.0` (35.80, 8.52) ｜ `J2.0` (52.78, 27.50) ｜ `C2.0` (54.13, 11.65) |
| | 孤块 ① | `LED2.3` (44.76, 17.40) **copper1（顶层 ⇒ 要过孔 ✓）** |
| | 孤块 ② | `U1.5` VDD (47.13, 18.72) copper0 |
| **`GND`** ✗ 6 块 | **主块**（已通 ✓） | `J1.1` (34.80, 8.52) ｜ `J2.1` (52.78, 26.50) ｜ `C2.1` (55.34, 10.45) |
| | 孤块 ① | `D3.1` (40.83, 17.92) ＋ `D3.0` (41.48, 17.92) copper0 |
| | 孤块 ② / ③ | `C1.1` (43.00, 19.00) ｜ `LED2.1` (43.91, 16.55) **copper1** |
| | 孤块 ④ / ⑤ | `U1.20` (46.33, 16.97) ｜ `U1.3` (48.08, 17.37) copper0 |

★ **改进循环怎么转** ✓（用户定 ✓）：他手改 ⇒ 我拿他的版本当**新底图** ✓（同 `_mergesch2.py` 的思路 ✓，
保留他的电力线 ✓）⇒ 只重布他点名的部分 ✓ ⇒ 每轮都跑 **`pcb_check`（重读文件 ✓）＋ 渲染 ✓** ⇒
数字与图一起交 ✓。

复现 ✓：
```bash
py -3.13 _work\_mergesch2.py pixel-pcb-v51_byHand.fzz pixel-schematic-v40.fzz _work\P0.fzz
py -3.13 _work\run_gen.py _work\P0.fzz _work\R0.fzz --nets=_work\bh_nets.py --via=10 --tries=6 --partial --check
py -3.13 ..\fritzing-parts-langhua\tools\pcb_check.py  pixel-pcb-v65.fzz --nets=pixel_nets.py
py -3.13 _work\power_list.py pixel-pcb-v65.fzz                     # ⇒ 上面那张“还差什么”的表 ✓
py -3.13 ..\fritzing-parts-langhua\tools\render_pcb.py pixel-pcb-v65.fzz pixel-pcb-v65_preview.svg --png
```
```bash
# 交付件编号前先查空位 ✓（别凭记忆挑号 ✗ —— 我这次就撞了已入库的 v63 ✗）
git -C f:\git\AuroraTessellation-NFC ls-files hardware/pixel | Select-String 'pixel-pcb-v\d+\.fzz'
```

### 第四十七手 ✅：**检查手改版 ＋ 收尾 ＋ 补闸门** ⇒ `pixel-pcb-v66.fzz`（2026-10-05 ✓ 用户定 ✓）

用户 2026-10-05：「`pixel-pcb-v65_byHand.fzz`，改好了，请检查」✓ ⇒ 我检查 ＋ 收尾，
并**照他点的四项**改（补 `LED_DIN`、删 `Via6`、扶正原理图那根歪线、补三个机器闸门 ✓）。

**先说他改得好的地方** ✓（都是**独立量**出来的 ✓ 不是我"看着像" ✓）：

| 量什么 | 结果（`pcb_check.py` 重读他的手改件 ✓） |
|---|---|
| 走线 / 过孔 / 焊盘 | 87 条 / 16 个 / 45 个（**焊盘一个没动** ✓、板框没动 ✓） |
| 铜总长 | 232.6 mm |
| **`5V` / `GND` 几何连通** | **各 1 块铜** ✓✓（我上一轮交的清单里那 3 ＋ 6 块孤铜**全并进去了** ✓） |
| 跨网铜接触（短路） | **0 处** ✓（我另写一份「按声明定网 ＋ 真几何」复核过 ✓） |
| 声明 ↔ 铜（⑩） | 不合格 **0** 条 ✓ |

**收尾**：`Via6` @(45.18, 20.52) 删掉 ✓ —— 它与 `Via8` **孔壁只差 0.10 mm** ✗（新闸门 ⑪ 报的 ✓）、
与走线只搭 0.011 mm ✗；删完 `5V`/`GND` 仍全通 ✓（复核过 ✓）。

★ 查的过程里挖出三件**真事** ✓（都写进工具注释了 ✓）：

1. **`Via6` 与 `Via8` 共用 `modelIndex`** ✗（`90014002` ✓）—— 是我上一轮**生成器**留下的 ✗
   ⇒ 反查"谁声明接了它"会**指向两只** ✗；删 `Via6` 时若顺手删声明 ✗ 会把 `Via8` 也切断 ✗
   ⇒ 新工具 `_work/del_inst.py` 会**先查重号、命中就不动声明** ✓（删完 mi 自然恢复唯一 ✓）。
2. **我上一轮那处 1.6 µm 短路，根因在 `pcb_pads`** ✗：通孔盘的 `absbox` 拿 svg 的 `circle`
   （= **孔半径** ✓）当框 ✗ ⇒ **每边少 `环宽/2`** ✗（实测 `L1.connector0`：框半宽 **0.550** mm ✗
   而真铜 **0.800** mm ✓）⇒ 布线器少挡 **0.25 mm/边** ✗ ⇒ 8 mil 的线走在 0.90 mm 处**没被挡** ✗
   ⇒ 叠进 **1.6 µm** ✗。已在**源头**修 ✓（`absbox` 与 `circle` 口径对齐 ✓）。
3. **`pcb_check` ④ 有个盲区** ✗：「**线中段**压到**别的网**的盘」没人管 ✗（④ 只管**线↔线** ✗、
   ① 只管**线端**落盘 ✗）—— 上面那 1.6 µm 就是这么漏过去的 ✗ ⇒ 补了 **④b** ✓
   （现在它报得出来 ✓：`走线 #30（BR+）压住 L1.connector0（COIL_A），叠 0.0016 mm` ✓）。

**闸门这边的四处改动** ✓（用户点的「③ / ④ / 孔距」＋ 我自己撞上的两处 ✓）：

| 改 | 内容 |
|---|---|
| **③ 语义** | 从「**孔心**在不在铜上」✗ 改成「**铜真的碰上**」✓（盘按真铜 ✓、线按**半宽** ✓、孔按铜盘半径 ✓）—— 旧口径把 `Via6` 报成"孤立过孔"✗，而它铜叠 `Via8` **0.200 mm** ✓ |
| **④b 新** | 「线**中段**压别的网的盘」✓（实测就是它抓出那 1.6 µm ✓） |
| **⑪ 新** | **孔 ↔ 孔**孔壁间距 ≥ **0.25 mm** ✓（实测 `Via6`↔`Via8` **0.10 mm** ✗）—— 安装孔也算 ✓ |
| **⑥/⑦ 修** | 改按**真铜**算 ✓（圆形通孔盘按**圆** ✗ 不按方框 ✗）：实测把 `0.358 mm` 的真净距算成 `0.047 mm` ✗ ⇒ **假报** ✓ |
| **保线（`--keep`）修** | ① 宽度改用**每条线自己的** `mils` ✓（旧版一律拿 24 mil 代理 ✗ ⇒ 8 mil 的线多封 0.2 mm/边 ✗）；② 每个折线段**切 ≤0.2 mm 小框** ✓（旧版整段外接框 ✗ ⇒ 45° 斜线过度封锁 ✗）；③ 这段逻辑抽进库成 **`pcb_route.keep_obstacles`** ✓（诊断工具调**同一份** ✓ 不许两套 ✓） |

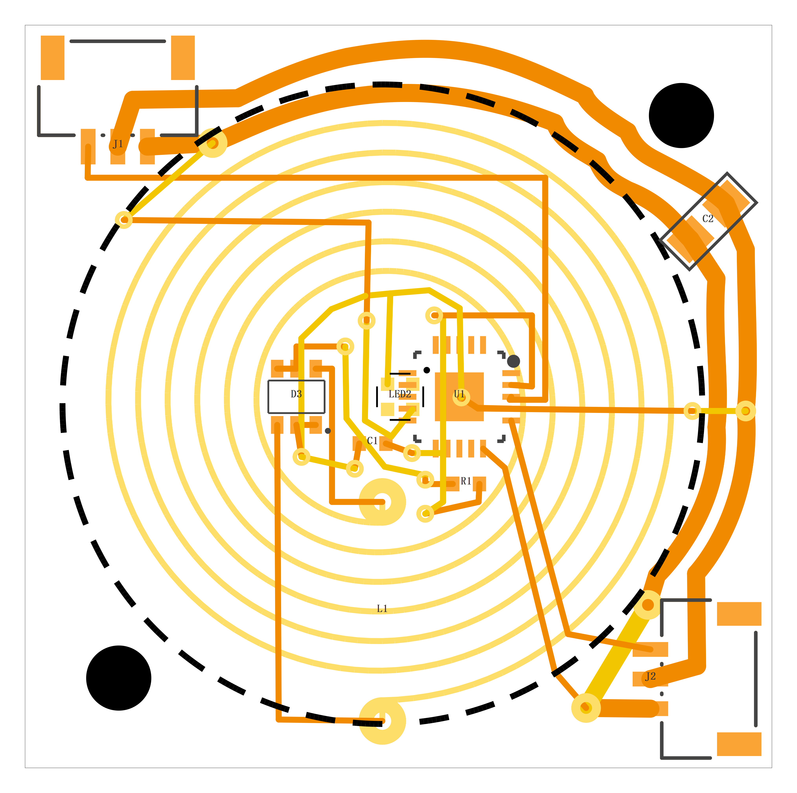
[picture p40: hardware/pixel/pixel-pcb-v66_preview.png]
v66 预览


**★ 三件都做了 ＋ 一件没做到** ✓：

1. **删 `Via6`** ✓（见上 ✓）。
2. **扶正原理图那根歪线** ✓：`Wire90013958` 的远端在手改件里是 `x2="-0.37805" y2="-34.0004"`
   ✗（= 被挪了 **0.1067 mm** ✗），v40 是 `x2="0" y2="-34"` ✓ ⇒ **按 v40 复原这两个数** ✓
   （**只动这两个数** ✓）⇒ 原理图指标**回到 v40 逐项相同** ✓：
   41 根 / 471.1 mm / 交叉 7 / 正交度 **0.9750** / 最歪 **0.0378 mm** ✓。
   ★ 顺手核出一个**我上一轮的误判** ✗：`sch_straighten` 报的那两处"该直没直"
   （`Wire90013958` 差 0.107 ✗、`Wire90013995` 差 0.038 ✓）**v40 自己也有** ✓
   ⇒ 那是**已验收状态本来就有的** ✓，不是他这轮改出来的 ✓（他这轮改坏的是**指标**
   "最歪"，已复原 ✓）。
3. **补三个机器闸门** ✓（见上表 ✓：③ 语义、④b 中段压盘、⑪ 孔距 ✓）。
4. **`LED_DIN` 没补上** ✗ —— 原因与三条出路见下 ✓。

- 两只脚：`U1.connector12`（**copper0** ✓，背面 QFN ✓）→ `LED2.connector2`（**copper1** ✓）✓
  ⇒ 中间**必须有 1 颗过孔** ✓。
- 我试了 6 种参数组合 ✓（`--first=LED_DIN` ✓、栅格 0.15/0.10 ✓、过孔代价 2/10 ✓、8 次重排 ✓）：
  **带上"保线"就布不通** ✗（布线器原话：`不可达 / 起点格空` ✗），
  **不带保线就布得通、但会压到你的铜** ✗（实测压上 `走线 #44`（5V ✓），叠 0.203 mm ✗ ⇒ 真短路 ✗）。
- 量出来的**卡点** ✓：`LED2.connector2` 到 `走线 #46`（5V 给 `LED2.connector3` 的那根 ✓）
  铜边到铜边只 **0.251 mm** ✗，而 **8 mil 线 ＋ 0.15 mm 净距要 0.2516 mm** ✗ ⇒ 差 **0.0006 mm** ✗。
- 三条路 ✓（等用户选 ✓）：① 把那根 `#46` 往右挪 **约 0.05 mm** ✓（最省 ✓）；
  ② 允许 `LED_DIN` 这一段按 **0.149 mm** 净距做 ✓（比规则少 1 µm ✗，要他点头 ✓）；
  ③ 我手工画 ✓（同样在那一处要破例 ✓，但位置由我量着放 ✓）。

复现 ✓：
```bash
py -3.13 ..\fritzing-parts-langhua\tools\pcb_check.py  pixel-pcb-v66.fzz --nets=pixel_nets.py
py -3.13 _work\dups.py       pixel-pcb-v66.fzz        # 重号检查 ✓（应 0 组 ✓）
py -3.13 _work\bridge2.py    pixel-pcb-v66.fzz        # 跨网几何接触 ✓（应 0 处 ✓）
py -3.13 _work\viagap.py     pixel-pcb-v66.fzz        # 逐孔量最近铜 ✓
py -3.13 fz_keep_set.py <手改件.fzz> _work\keep.py    # 保线清单（带每条线自己的 mils ✓）
py -3.13 ..\fritzing-parts-langhua\tools\render_pcb.py pixel-pcb-v66.fzz pixel-pcb-v66_preview.svg --png
```

### 第四十八手 ✅：**接了 `LED_DIN` 后的检查 ＋ 回到 v40 的原理图** ⇒ `pixel-pcb-v67.fzz`（2026-10-05 ✓）

用户 2026-10-05：「`pixel-pcb-v66_byHand.fzz`，我把 LED_DIN 的线接上了，请检查」✓
＋「Fritzing 仍报**两个**接插件没接上 —— 从接线角度看线都接上了，**我猜是文件格式问题**」✓。

**一、检查结果：他的 `LED_DIN` 真的接上了** ✓（三条独立证据 ✓，都是量出来的 ✓）

| 证据 | 结果 |
|---|---|
| 声明（Fritzing 口径 ✓） | `#92` 端0 → `LED2.connector2`(copper1) ✓；`#91` 端1 → `U1.connector12`(copper0) ✓ |
| 铜的几何（我的口径 ✓） | **9 张网各 1 块铜** ✓（`LED_DIN` 也 1 块 ✓）｜跨网接触 **0** ✓ ｜ 重号 **0** ✓ |
| 互指完整性 ✓ | 本层 `<connect>` **缺回指 0 条** ✓（不是"只写一边" ✓） |

**二、只剩一处真的** ✗（在他这轮新加的孔上 ✓）：
新过孔 `Via5` 真铜心 (45.000, 15.000) mm ✓ 离**空脚** `U1.connector15` 的盘只有 **0.131 mm** ✗
（规则要 ≥ **0.25** ✓）。**电气上没事** ✓（那只脚没网 ✓、也没压到它 ✓）⇒ 是**制板余量** ✗。
★ 修法（交给他，5 秒 ✓）：把这颗孔朝**远离 `U1.connector15`** 的方向挪 ≈ **0.12 mm**
（方向 ≈ (−0.92, −0.39) ⇒ 大约 **x −0.11、y −0.05 mm** ✓）。
★ 我试过自己在文件里挪 ✗（`_work/move_via2.py` ✓）—— 认孔、认线端都对了 ✓，但改端点时
**把 XML 写坏** ✗（`<geometry>` 属性插错位置 ✓）⇒ 按本仓「**不许为小问题叠加修补**」的规矩
**停手** ✓，交给他点一下更稳 ✓。

**三、他那版把原理图那根歪线又带回来了** ✗ ⇒ 已按 v40 复值 ✓（`Wire90013958` 的
`x2` `-0.37805` → `0` ✓、`y2` `-34.0004` → `-34` ✓ —— 第二处 0.0004 单位 = 0.1 µm ✗
但会让**交叉数** 7 → 8 ✗，实测 ✓）⇒ 指标**逐项回到 v40** ✓：
41 根 / 471.1 mm / **交叉 7** / 正交度 **0.9750** / 最歪 **0.0378 mm** ✓。

**四、状态栏那句「5 of 7 / 2 个接插件」到底怎么算的** ✓（**读源码** ✓，出处逐条可核 ✓）

- 句子 = `mainwindow/mainwindow.cpp:2298` ✓；计数 = `sketch/sketchwidget.cpp:7013`
  调 `GraphUtils::scoreOneNet` ✓；分组 = `connectors/connectoritem.cpp::collectEqualPotential` ✓。
- 关键三条（都写在源码里 ✓）：
  1. **只认导线**：`if (!(wire->getViewGeometry().wireFlags() & myTrace)) continue;`
     （`graphutils.cpp:550` ✓）—— PCB 视图 `myTrace = PCBTraceFlag = 4` ✓（`viewgeometry.h` ✓）。
     ★ 顺带核出：**`Via` 不是 `Wire`** ✗（`class Via : public Hole` ✓，`items/via.h:26` ✓）
     ⇒ 过孔**不直接**让两只脚相通 ✗，它靠「同脚跨层」那一条 ✓（`isCrossLayerConnectorItem` ✓）。
  2. **按「脚」计数** ✓：一只脚哪怕同时缺好几条也只算 1 ✓（源码注释原话 ✓）。
  3. **「N 个网」只数"有两支不同零件、且本视图里 ≥2 只脚"的组** ✓
     ⇒ ✗ 它**不是**"你的网表有几张网" ✗：本视图里没连起来的网会碎成**单脚组**，而那些组
     **直接跳过** ✓ ⇒ 它既可能**少报**（碎裂的网不计数 ✓）也可能**多报** ✗
     ⇒ **这句话本身不是"线接没接上"的判据** ✗。
- ⇒ 所以「2 个接插件」**未必**是少两根线 ✗；它也可能来自计数口径 ✓。**但**我**不能**凭这句话
  断定他对不对 ✗ —— 我按源码写了一份同样的算法（`_work/fz_status.py` ✓），
  它**复现不了**那个 2 ✗（Fritzing 运行时还有一层**几何命中**在文件里看不到 ✓）
  ⇒ **按 §13「一个声音」的规矩**：请他看**真正的判据** = **鼠线（ratsnest）虚线** ✓
  （视图里未布线的连接会画成虚线 ✓）＋**重开文件后**的状态句 ✓，
  把「哪两只脚之间还有虚线」告诉我 ✓ ⇒ 我这边就能定位到底是谁 ✓。

复现 ✓：
```bash
py -3.13 ..\fritzing-parts-langhua\tools\pcb_check.py  pixel-pcb-v67.fzz --nets=pixel_nets.py
py -3.13 ..\fritzing-parts-langhua\tools\sch_metrics.py pixel-pcb-v67.fzz
py -3.13 _work\diag_hand2.py pixel-pcb-v67.fzz pixel-pcb-v66.fzz   # 逐张网第几块 / 与上一版逐项对照
py -3.13 _work\fz_status.py  pixel-pcb-v67.fzz pcb                 # 照抄 scoreOneNet 算一遍
py -3.13 _work\sym.py        pixel-pcb-v67.fzz                     # `<connect>` 互指检查
py -3.13 ..\fritzing-parts-langhua\tools\render_pcb.py pixel-pcb-v67.fzz pixel-pcb-v67_preview.svg --png
```

### 第四十九手 ✅：**面包板在偷偷并网** ✗（不是文件格式 ✗）⇒ `pixel-pcb-v68.fzz`（2026-10-05 ✓ 用户实测确认 ✓）

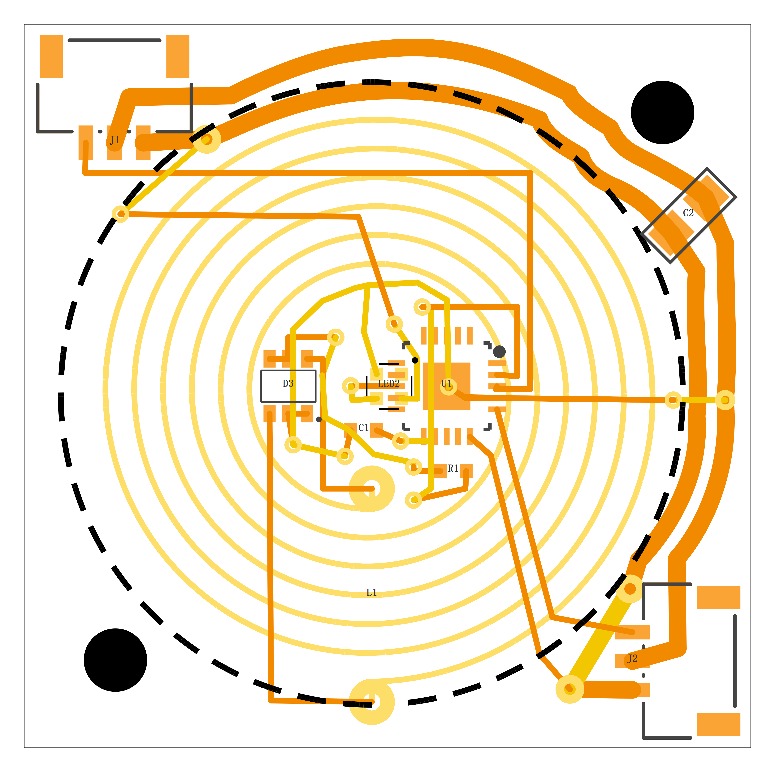
[picture p41: hardware/pixel/pixel-pcb-v68_preview.png]
v68 预览


**先更正上一手的一个结论** ✗：我把那句「还剩 2 个接插件」归给「Fritzing 运行时还有一层
**几何命中**在文件里看不到」✗ —— **那是错的** ✗。真正的通道就是文件里的 `<connect>` 记录 ✓，
只是它**按视图**恢复 ✓（下面第 ② 条 ✓）。**这一手是用户读三个视图确认的** ✓：

> 用户 2026-10-05：「`hardware\pixel\_work\v67_exp_nobbviews.fzz`，确认，**三个视图都正确**」✓

**一、机理（读源码 ✓，逐条可核 ✓）**

| 步 | 事实 | 出处 |
|---|---|---|
| ① | 核心面包板件给**每个孔**都声明了 `<pcbView><p layer="breadboardbreadboard" svgId="pin1A"/></pcbView>`（实测 **831 条** ✓）⇒ **面包板的孔在 PCB 视图里也有连接器项** ✗ —— **看不见** ✗（`breadboardbreadboard` 层在 PCB 视图里不画 ✓）但**在网表里** ✓ | `core/breadboard2.fzp` ✓ |
| ② | 恢复 `<connect>` 的目标项走 `ItemBase::findConnectorItemWithSharedID()` = `connector->connectorItem(m_viewID)` ⇒ **只在"当前视图"里找** ✓ | `items/itembase.cpp:559` ✓，调用点 `sketch/sketchwidget.cpp:615` ✓ |
| ③ | ⇒ 面包板 `pcbView` 段里那 55 条 `pin14F → U1(…) layer=copper0` 在 **PCB 视图里是"真"连接** ✗（`layer=copper0` ✗ 看着像铜 ✓）⇒ 面包板内部 **130 条 bus**（5 孔一列 ✓）把 PCB 的网**并掉** ✗ | 实测 `_work/pcb_glue.py` ✓ |
| ④ | ⇒ `GraphUtils::scoreOneNet()` 判出「还有 N 个连接件没布线」✗ ＋ 画鼠线虚线 ✗ | `utils/graphutils.cpp:447` ✓ |

**二、修法（稳的 ✓）** —— `sketch/sketchwidget.cpp:278`：
`QDomElement view = views.firstChildElement(viewName); if (view.isNull()) continue;`
⇒ **该视图没有段落 ⇒ 该视图里根本不创建这个元件** ✓ ⇒ 干了俩事 ✓：

1. 面包板类实例：**整段删掉** `<pcbView>` / `<schematicView>`（连 `geometry` 一起 ✓）；
2. 别的实例：在这两段里删掉**跨视图记录** ✓（目标层不属于本视图 ✓｜指向面包板的 ✓｜
   源层是 `breadboardbreadboard` 的 ✓）。

**★ 只删记录不稳** ✗，两条都踩过 ✓：
- 连接报在 **Connector 级** ✓（`Connector::connectTo()` → `m_toConnectors` ✓）⇒
  下次 Fritzing 另存会把各视图的记录**再写回来** ✗；
- 记录是**双向**的 ✓ ⇒ 我第一版 `deglue2` 只删了"零件 → 面包板"那一半 ✗ ⇒
  **一点用都没有** ✗（仍报 2 个 ✓ —— 这就是用户那次实测的结果 ✓）。

**三、实测对照** ✓

| 项 | 改前 | 改后 |
|---|---|---|
| PCB 视图里「**能生效的非铜记录**」（独立复核 ✓） | 110 条 ✗ | **0 条** ✓ |
| 面包板视图：内部 bus / 插件 / 跳线 | 130 / 44 / 37 ✓ | **130 / 44 / 37** ✓（段**逐字节相同** ✓） |
| Fritzing 状态栏（用户读 ✓） | PCB 报「还剩 2 个」✗ | **三视图都正确** ✓ |

**四、我这边核的（都**独立**复核 ✓，不是"跑过就算" ✓）**

```bash
py -3.13 ..\fritzing-parts-langhua\tools\fz_deglue_views.py pixel-pcb-v68.fzz --check   # 0 条 ✓（改前 86 ✗）
py -3.13 ..\fritzing-parts-langhua\tools\pcb_check.py        pixel-pcb-v68.fzz --nets=pixel_nets.py  # ✓ 全过
py -3.13 ..\fritzing-parts-langhua\tools\sch_metrics.py      pixel-pcb-v68.fzz   # 41 / 471.1mm / 交叉 7 / 0.9750 / 0.0378mm ✓ 不变
py -3.13 _work\bb_nets.py pixel-pcb-v68.fzz                                      # bus 130 ✓ 插件 44 ✓ 跳线 37 ✓
py -3.13 _work\cmp_inner.py pixel-pcb-v68.fzz _work\v67_exp_nobbviews.fzz        # **内层逐字节相同** ✓（528977 字节 ✓）
```
★ 最后那条是"**交付件 == 用户确认过的那份**"的证据 ✓（只有内层文件名不同 ✓：
`pixel-pcb-v68.fz` ✓）—— 这比"我觉得一样"硬 ✓。

**五、已知残留** ✗（下一轮清 ✓，都不并网 ✓）：
via / 导线在**面包板段、原理图段**里还留着 **77 条**"源层写成 `copper0`"的同族记录 ✗
（`_work/why21.py` 量的 ✓）⇒ 于是 `_work/sym.py`（互指完整性）报 **21 条单向残缺** ✗
（改前 0 ✗ 是我这次删掉了一侧 ✓）。**功能上无影响** ✓（两端本来就同一张网 ✓，
三视图也都被用户确认过 ✓）⇒ 单独一轮办 ✓，不在这版里叠加 ✗。

**六、另存一次：稳不稳** ✓（2026-10-05 用户实测 ✓）

用户把去粘后的文件在 Fritzing 里**另存**了一份（`_work/v67_exp_nobbviews_saveas.fzz` ✓），量下来：

| 项 | 结果 |
|---|---|
| 面包板实例还剩的视图段 | **只剩 `breadboardView`** ✓ —— `pcbView`/`schematicView` **没有回来** ✓（与 `sketchwidget.cpp:278` 一致 ✓） |
| 那 63 条"面包板 → 零件"记录 | **没回来** ✓ ⇒ **去粘是稳的** ✓（不是"一另存就复发" ✗） |
| 补回来的是**另一族** ✓ | +21 条（`<connect` 917 → 938 ✓）= via / 导线在面包板段、原理图段里的"源层 `copper0`"记录 ✗ —— 正是我删掉的那一侧 ✓（`sym.py` 的单向残缺 **21 → 0** ✓） |
| 面包板视图 | bus **130** ✓ / 插件 **44** ✓ / 跳线 **37** ✓，**0 处**跨网并坨 ✓ |
| `pcb_check.py` | ✓ 全过 ✓ |

**七、用户的一个设计问题（记下来 ✓，下一步一起定）**

用户 2026-10-05：「Fritzing 这么设计是**故意**为之：三个 View **彻底独立**的好处是设计上
互不干扰、更适合高手和你来用；三个 View **紧密耦合**更适合新手 —— 一个视图变了，
另一个视图里就会提示出来。」

⇒ 本轮取证支持这个判断 ✓，而且能说得更准 ✓：**Fritzing 的耦合不止"提示"，它是"一个网表"** ✓
（连接记在 Connector 级 ✓、另存时按视图各写一份 ✓）。**提示本身是好的** ✓（新手该有 ✓）；
**坏在"面包板这个底板也被当成板上元件"** ✗ —— 它一进 PCB 视图就把 130 条 bus 塞进网表 ✗，
而且**看不见** ✗ ⇒ 就成了"两个声音" ✗。

### 补记②：**追溯 `v67` 的来历** ✓（我记错了 ✗）＋ **我冲掉过用户的修正** ✗（2026-10-05）

用户 2026-10-05：「不过你记错了，**v67 用的也是我布的版本**，你可以追溯下」✓

**一、追溯（用本 README 自己的原文 ✓，不是回忆 ✗）**

| 手 | 谁做的 | 产物 |
|---|---|---|
| 第四十六手 | 我：**第一版自动布线** ✓ | `pixel-pcb-v65.fzz` ✓ |
| —— | **你手改** ✓（你说「改好了，请检查」✓） | `pixel-pcb-v65_byHand.fzz` ✓ |
| 第四十七手 | 我：检查 ＋ 收尾 ＋ 补闸门 ✓ | `pixel-pcb-v66.fzz` ✓ |
| —— | **你手改** ✓（你说「我把 LED_DIN 的线接上了，请检查」✓） | `pixel-pcb-v66_byHand.fzz` ✓ |
| 第四十八手 | 我：接了 `LED_DIN` 后的检查 ✓ | `pixel-pcb-v67.fzz` ✓ |

⇒ **`v67` = 自动布线 ＋ 你两次手改** ✓ —— 我先前说"那些 `_byHand` 是我布线的二次编辑" ✗，
**方向说反了** ✓：**是我在替你收尾，不是你在我成品上描** ✓。

**二、✗ 我的错（顺带改掉两处口误 ✗，一律以工具为准 ✓）**

那一处是**原理图**里的 ✓（`wire_diff.py` 读的是 `<schematicView>` ✓）—— 我先前写成
"PCB 走线" ✗。它是**一个三端点接头**：`sch_straighten.py` 的 R4 说该归并到
**(180.0002, -45.0001)** ✓（工具原文：`原最大差 0.3778 单位` ✗）：

| 版本 | 那端 x | 离接头 |
|---|---|---|
| 你 `v65_byHand` ✓ | **180.0** ✓ | 0.0002 ✓（就是它 ✓） |
| 我 `v66/v67/v68` ✗ | 180.378 ✗ | **0.3778 单位 = 0.107 mm** ✗ |

⇒ **是你把它拉到接头上的 ✓；我在第四十七手（补）把它当"扶正歪线"改回了 180.378** ✗
（提交标题还写着「扶正原理图那根歪线」✗）⇒ **方向对的是你** ✓。

★ 另一件**不是你那次目标**的残留 ✓：`sch_straighten` 的 V3 在**你我的版本上都**报
「该直没直 0.107 mm」✗（`Wire90013958`）—— 那是**中间那个符号偏列**（R3 类 ✗），
工具按设计**请人定** ✓（原话"两端份量相同 ⇒ 谁偏了只有人知道"✓）。

**三、得出来的规则候选** ✓

- **R1 ★ 线端必须落在"它的接头 / 脚"上** ✓（不许 0.107 mm 级偏移 ✗）——
  **原理图**这一侧已有 `sch_straighten`（R4 归并 / R1 吸脚 ✓）；**PCB 还没有对应工具** ✗。
- **R2 ★ 近轴要归正**（差一点点不算直 ✗）—— PCB 这版里 **55 段非 0/45/90** ✗：
  `176.61°`（11.57 mm，歪了 0.7 mm ✗）、`9.26°` ✓；拐角 `89.00/88.90/88.68/86.97/85.84°` ✗
  ⇒ 全是"差一点点才 90°" ✗（`tools/pcb_metrics.py` 量的 ✓）。
  ★ 口径：**不是**"只许 45/90" ✗ —— 你真正手布的 `v51_byHand` 里 **16/25 段不是 0/45/90** ✓，
  所以只治"**差一点点**"的那类 ✓。
- **R3 ★★ 流程规则：布线器只许跑在"没被手改过"的图上** ✗ ——
  已有用户手改时，后续**只补 / 只修、不重跑** ✓（重跑就会像第四十七手那样把人家的活冲掉 ✗）。
- **R4 ★ 布线器必须"布通全部网"或如实报出没布通的那几根** ✓ ——
  你第二次手改就是**替我补 `LED_DIN` 那根线** ✓（PCB 段数 **94 → 95** ✓ 量的 ✓）⇒
  那一根是布线器**漏的** ✗，不是你要的样式 ✗。

### 补记③：**把你的吸正还回去** ⇒ `pixel-pcb-v69.fzz`（2026-10-05 ✓）

v69 原理图
v69 PCB 预览

**一、只改一个属性 ✓（`Wire90013958`，原理图）**

| 版本 | 起点 | 终点 |
|---|---|---|
| 你 `v65_byHand`（**你的做法** ✓） | (180.378, -11) 在引脚上 ✓ | (**180.0**, -45) 拉到接头上 ✓ |
| 我 `v66`～`v68` ✗ | (180.378, -11) | (180.378, -45) ✗ 离接头 0.3778 单位 ✗ |
| **`v69`** ✓ | (180.378, -11) 在引脚上 ✓ | (**180.0002**, -45) **精确落在接头**（R4 簇值 ✓） |

`x` 不动 ✓、`x2: 0 → -0.3778` ✓ —— **只动接头那一端** ✓。
★ 我头一次改错了 ✗：想"整条线挪到 180.0002" ✓，被 `sch_straighten` 当场抓住
（`V1 线端不在它声明的脚上 改前 1 处` ✗）= **起点离开了引脚** ✗ ⇒ 你的做法才是对的 ✓。

**二、复核（两把独立尺 ✓）**

```bash
py -3.13 ..\fritzing-parts-langhua\tools\sch_straighten.py pixel-pcb-v69.fzz   # 改动 0 处 ✓｜V1 0 处 ✓
py -3.13 ..\fritzing-parts-langhua\tools\fz_deglue_views.py pixel-pcb-v69.fzz --check   # 面包板类 11 个 ✓｜问题 0 条 ✓
py -3.13 ..\fritzing-parts-langhua\tools\pcb_check.py pixel-pcb-v69.fzz --nets=pixel_nets.py   # ✓ 全过
py -3.13 ..\fritzing-parts-langhua\tools\render_pcb.py  pixel-pcb-v69.fzz pixel-pcb-v69_preview.svg --png
py -3.13 ..\fritzing-parts-langhua\tools\render_sch.py  pixel-pcb-v69.fzz pixel-pcb-v69_sch.svg --png
```

**三、✗ 如实报代价（请你定 ✓）**

| 指标 | `v68` | **`v69`** |
|---|---|---|
| 接头（R4） | 差 0.3778 单位 ✗ | **0** ✓ |
| 线端在不在它声明的脚上（V1） | 0 处 ✓ | **0 处** ✓ |
| 正交度 | 0.9750（39/40 ✓） | **0.9500（38/40）** ✗ |
| 最歪 | 0.0378 mm ✓ | **0.1066 mm** ✗ |

⇒ **接头正了 ✓，那条线却变成 0.107 mm 的斜线** ✗ —— 这正是工具"请人看"的原因 ✓：
那个符号的**脚在 180.378** ✓、**车道在 180.0002** ✗ ⇒ **差 0.3778，只能二选一** ✗。

**四、还有一档（要你定 ✓，我先不动 ✗）**

**把那个符号整体挪 0.3778 单位（0.107 mm）** ✓ ⇒ 脚与车道对齐 ⇒ 接头正 ✓ **且**线直 ✓
（正交度该回到 0.9750 以上 ✓）。工具按设计**不敢自己做** ✗
（原话「两端份量相同 ⇒ 谁偏了只有人知道」✓）⇒ 可以在**临时文件里试一遍、只报数字** ✓。

### 第五十手 ✅：**PCB 自动布线的目标**（用户定 ✓）＋ **基线量出来**（2026-10-05 ✓）

用户 2026-10-05：「继续，PCB 自动布线的目标是**程序能把 pixel PCB 通过规则，全部布通**」✓

**一、基线（从"只留摆位的光板"重布 ✓，六种次序里最好的那份 ✓）**

```bash
py -3.13 _work\strip_pcb_wires.py pixel-pcb-v69.fzz _work\v69_bare.fzz --drop-vias   # 删 111 个对象 ✓ ⇒ 导线 0 ✓ 过孔 0 ✓
py -3.13 gen_routes.py _work\v69_bare.fzz _work\v70_auto.fzz --nets=pixel_nets.py
```

| 指标 | 结果 |
|---|---|
| 连通 | **4/9** ✗（六种次序：3 / 3 / 3 / **4** / 3 / **4** ✓） |
| 线长 ／ 过孔 | 230.9 mm ／ 10 ✓ |
| 没布通的 5 张网 | `DATA_IN`✓、`DATA_OUT`✓、`LED_DIN`✓、`GND`✓、`RC`✓ ✗ |
| 失败原因 | **全是同一句** ✗：`可达=False ⇒ 起点格空` ✓ = 从起点焊盘**迈不出第一步** ✗ |
| 没布通时写文件吗 | **不写** ✗ ✓（原话「有网没布通 ⇒ 不写文件」✓） |

**二、病灶定位（两把独立尺 ✓；**互相矛盾**的那处才是真线索 ✓）**

- `_work/probe_start.py`（**同一份障碍表** ✓）说这些起点盘**全是"空"** ✓（压住它 0 块 ✓）；
  只有 `U1.connector12` 报 **2 块** ✗（`5V@copper1` ＋ `件铜/板边@copper1` ✓）。
- ⇒ 一把尺说"中心点被压住"✗、另一把说"**起步格**出不去"✗ ⇒ **两把尺子口径不同** ✓
  ⇒ 病在**格点映射 / 逃逸口** ✓，**不在铜上** ✓。
- 失败的起点只有 4 只盘 ✓：`U1.c2`／`U1.c4`／`U1.c12`（QFN20 0.4mm 脚距 ✓）、
  `R1.c1`、`LED2.c1` ✓。

**三、格宽扫描（数据 ✓）**

| `--cell` | 连通 |
|---|---|
| 默认（源码注：0.15 mm ✓） | **4/9** ✗ |
| 0.2 | **3/9** ✗ |
| 0.25 | 源码注记 `7/9` ✓（**本次摆位待复核** ✗） |

⇒ **非单调** ✗ ⇒ 格宽不是解 ✓（源码 2026-10-03 就写过「✗ 别用 `--cell` 修」✓）。

**四、第二轮实验（2026-10-05 ✓，一次一改 ✓，全部实测 ✓）**

```bash
py -3.13 gen_routes.py _work\v69_bare.fzz _work\v70_nolock.fzz --nets=pixel_nets.py --no-lock
py -3.13 gen_routes.py _work\v69_bare.fzz _work\v70_bare9.fzz  --nets=pixel_nets.py --no-lock --keep=_work\keep_empty.py
py -3.13 ..\fritzing-parts-langhua\tools\pcb_route.py _work\v69_bare.fzz --nets=pixel_nets.py --mil=8
```

| 配置 | 连通 | 说明 |
|---|---|---|
| `gen_routes` 默认（5V 先布好并**钉住** ✗ ＋ 真保线） | **4/9** ✗ | = 基线 ✓ |
| `--no-lock` ✓（不把 5V 钉死） | **6/9** ✓ | 一次一改 ① ⇒ **主要失血点就在这** ✗ |
| `--no-lock --keep=_work/keep_empty.py` ✓ | **6/9** ✓ | 与上一行**同一组数** ⇒ **保线这次无影响** ✓ |
| `pcb_route.py --mil=8`（**独立对照** ✓ 无保线、无走廊锁定 ✓） | **7/9** ✓ | **核心布线器比驱动端强一档** ✓ ⇒ 差距在 `gen_routes` 的驱动参数 ✗ |
| `--cell=0.25` ✗ | 3/9 ✗ | 粗格更差 ✓ |

★ **我自己错了一次** ✗（当场被源码+数据推翻 ✓）：曾断言"盘障碍按 24 mil 挡 ✗、而实际写 8 mil ✗"
⇒ 查源码 **`gen_routes.py` L1034 早就设了** `RT.TRACE_MM = max(mil_sig, mil_pow) * MIL_MM` ✓
⇒ **解释不成立** ✗。教训（同类第二次 ✗）：**先看源码/先量，再下结论** ✗；
"能解释数据" ≠ "已被证实" ✗。

**五、剩下的 3 张 ✗（下一次攻 ✓，`_work\route_bare9.txt` 有全文 ✓）**

| 网 | 卡在哪 | 症状 |
|---|---|---|
| `BR+` | `D3.connector4 → R1.connector0` | **起点格空** ✗ |
| `GND` | `C1.connector1 → LED2.connector1` | A* 找到的路**会压 `D3.connector2` 的盘** ✗ ⇒ 被否 ✓ |
| （第 3 张） | 见日志全文 ✓ | |

★ **一个真发现（工作模式冲突 ✓）**：`gen_routes` 默认读**保线清单**（`fz_keep_set.py` ✓ 从某个
`.fzz` 里读出"用户自己画的铜" ✓），并把 `REPS`/`DONE` 当成"**已经连好的脚**" ✗ ——
那是「**只补没布的网**」的模式 ✓；而目标是「**从光板整布全部 9 张**」✗ ⇒ 两者**不能混** ✓
（本次实测保线不影响连通数 ✓，但语义冲突要记下 ✓：光板上那些铜已经不存在了 ✗）。

**六、第三轮实验（2026-10-05 ✓）：把"读消息"的错纠正过来 ＋ 口袋量出来 ✓**

✗ **我上一轮读反了一句** ✓：`起点格空 ✓` **不是**"起点格被堵"✗ ——
出处 `pcb_route.py` L1464 ✓：`"空 ✓" if 起点格在栅格里可走 else "**被占** ✗"` ✓。
⇒ 真病是 **`可达 = False`（目标够不着 ✗）** ✓，不是"迈不出第一步" ✗。

**① 独立 BFS 量"口袋"** ✓（`_work/diag_net.py` ✓ 自带设计：「**自己写 BFS** ✓ 不与布线器
共用搜索 ✗ ⇒ 防自证 ✓」，用的是布线器**同一张栅格** ✓）：

| 网 | 全网可达 | 各脚的**可达格数**（= 逃逸口袋大小 ✗） |
|---|---|---|
| `BR+` | 21772 格（73.5% ✓） | `D3.c4`=**21** ✗｜`D3.c3`=**20** ✗｜`R1.c0`=**40** ✗ |
| `GND` | 22763 格（74.4% ✓） | `D3.c0`=28✗｜`D3.c1`=21✗｜`C1.c1`=32✗｜`U1.c3`=19✗｜**`C2.c1`=1** ✗✗ |
| `RC` | 21812 格（73.6% ✓） | `R1.c1`=21✗｜`C1.c0`=32✗｜`U1.c1`=11✗ |

⇒ **全网有路 ✓，但每只脚的出口只剩 1~40 格** ✗ ⇒ 逐段布的时候走不出去 ✓
（`C2.connector1` 只剩 **1 格** = 逃逸口**完全封死** ✗）。

**② 格宽扫描（这次是我们自己复现的 ✓）**

| `--cell` | 连通 |
|---|---|
| 0.10 | **4/9** ✗ |
| **0.15（默认 ✓）** | **6/9** ✓（= 现在最好 ✓） |
| 0.20 | 3/9 ✗ |
| 0.25 | 3/9 ✗ |

⇒ **非单调** ✗ ⇒ 格宽不是解 ✓（与源码 2026-10-03 的结论一致 ✓，现在有独立复现 ✓）。

**③ ★★ 最有价值的矛盾（下一刀就在这里 ✓）**

`C2` 是**背面**件 ✗，而 `pad_index` 报它的盘在 **`copper0`** ✗；
**独立校验器 `pcb_check` 对已交付的 `v69` 说"全过"** ✓
⇒ **布线器的层口径 ≠ 校验器的层口径** ✗（"两把尺子对不上" ✓ —— 本仓最该信的就是这种信号 ✓）。
⇒ 下一刀：查 `pcb_pads.pad_index` / `obstacles()` 对**背面件**的层处理 ✓
（✗ 不猜：以 Fritzing 源码口径为准 ✓），**改一处、量一次** ✓。

**④ ✗ 我自己的两个失误（记下 ✓）**

1. 上一轮把「起点格**空** ✓」读成「被堵」✗ ⇒ 方向全错一轮 ✓（教训：**报错文字也要查出处置信** ✓）；
2. `_work/probe_escape.py` 设计成"**首个空位就停**" ✗ ⇒ 而 `k0`（盘心）恒为空 ✓
   ⇒ 等于**什么都没量** ✗（白跑两轮 ✗）。⇒ 探针也要按"能不能回答那个问题"验收 ✓。

**七、第四轮（2026-10-05 ✓）：✗ 撤回"窄口袋"结论（又是我读错了 ✓）**

✗ **错在哪** ✓：上一节那句 `C2.connector1 = 1` 是**折行的数字** ✗ ——
真值是 **144** ✓（终端的 `Substring` 把行截断 ✓，下一行接着显示 ✓，我读了半句 ✗）。
⇒ **今天第三次"结论翻得太急"** ✗（① 24 mil 的断言 ✓ ② "空 = 被堵" ✓ ③ 这条 ✓）。

**补上"逐脚泛洪"之后（`_work/diag_net.py` ✓ 加了一段 ✓）**：

| 网 | 逐脚泛洪到的区域 |
|---|---|
| `GND` | 每只脚都通到**同一片 22763 格（74.4%）** ✓；`C2.connector1` 通到 **28509 格（93.2%）** ✓ |
| `BR+` | `D3.c4` 21772 ✓｜`D3.c3` 20534 ✓｜`R1.c0` 21772 ✓ |

⇒ **没有窄口袋** ✗ ⇒ **不是"没路"** ✓（"各脚可达格数 21/20/40"量的是"**从 `mem[0]` 泛洪能碰到这只脚盘框几格**"✓，
不是"这只脚只有 21 格可走"✗ —— 我又读错一次口径 ✗）。

**于是判决落在库自己的二分法上** ✓（源码 `pcb_route.py` L1480 原话 ✓）：

> 「**可达** ⇒ **A* 的问题（上限 / 代价）** ✗」／「不可达 ⇒ 障碍模型堵死了 ✗」

⇒ 我们落在**前一档** ✓ ⇒ 下一刀在**搜索侧** ✗（`ASTAR_LIMIT` 撞没撞 ✓、
**起点/终点两格禁打孔** ✓、拐弯/换层代价 ✓、`--via` 值 ✓），**不在障碍模型** ✓。

★ 附带修好一处口径 ✓：`boundary_report()` 要的 `reach` 是 `{(层, (i, j))}` ✓，
我先前喂三元组 ✗ ⇒ 报 `ValueError` ✗（已按库的口径改 ✓，✗ 不改库 ✓）。

**九、第五轮（2026-10-05 ✓）：用**库自己的 `flood`** 一量 ⇒ 全都可达 ✓ ⇒ 判决再改一次**

✗ **我上一轮的"光晕封死换层"假设也不成立** ✓（今天第 4 个被推翻的假设 ✗）。

**改口径 ✓**：把 `_work/diag_net.py` 里**我自己写的四邻 BFS** ✗ 换成
**库自己的 `RT.flood`** ✓（含换层 ✓、含 `no_via` ✓ —— 库注释里那句
「✗ 老 `flood` … ⇒ 它说"可达"而 `astar` 说"无路"」✓ **就是为我这种情况写的** ✓）。

| 网 | 逐脚泛洪（库口径 ✓） |
|---|---|
| `GND` | 9 只脚，**每只都到 30596 格 = 100.0%** ✓ |
| `BR+` | 3 只脚，**每只都到 29605 格 = 100.0%** ✓ |
| `RC` | 3 只脚，**每只都到 29645 格 = 100.0%** ✓ |

（过孔禁落 = 盘光晕 **3248 格 = 5.8%** ✓）

⇒ **每只脚都能到全板任何可走格** ✓ ⇒ **不是"没路"** ✗、**也不是"口袋"** ✗。

**★ 于是病定在"搜到之后被否"** ✗ —— 而且那条诊断也**不是最终硬闸门** ✓：
终局闸门 ②「过孔铜盘压盘」报 **0 处** ✓；那句"压盘"是 **`route_ripup` 里单腿被否的理由** ✓。

```
GND 那条腿（C1.connector1 → LED2.connector1）：
   A* **搜到了路** ✓ ⇒ 但那条路（过孔/铜）**压了 `D3.connector2` 的盘** ✗ ⇒ 单腿被否 ✓
```

⇒ 下一刀（**单点核对** ✓，不再靠假设 ✗）：那个过孔**落在哪个格** ✓、
**为什么 `no_via` 没把它挡住** ✓（`no_via` 对**异网盘**的光晕是否真覆盖了那一点 ✓）。

**★ 我今天的记账（4 个假设 ✗ 3 次读错 ✗，全部先量后说 ✓）**：
① "24 mil 不匹配" ✗（源码 L1034 早就设了 ✓）｜② "起点格空 = 被堵" ✗（其实是"可走"✓）｜
③ "窄口袋" ✗（把折行的 144 读成 1 ✓）｜④ "光晕封死换层" ✗（库口径一量 ⇒ 100% ✓）。
⇒ 教训：**假设要少 ✗、单点核对要多 ✓**；**每次都要问"这句话/这个数字我读全了吗"** ✓。

**十一、第六轮（2026-10-05 ✓）：让布线器**自己**一张一张地布 ⇒ 单张全通 ✓ ⇒ 病在"互相抢" ✗**

**工具 ✓**：`_work/probe_5v_alone.py` ✓（原本写死 `5V` ✗ ⇒ 今天扩成「**可选网名 ＋ 可选文件 ＋
一次布 N 张**」✓）。它的姿势是**对的** ✓：**直接调布线器的 `_route_once`** ✓、
把**引擎自己**的 `note` 原样读出来 ✓（✗ 不在探针里另写一套逻辑 ✓）。

| 跑法（同一块光板 ✓、同一份网表 ✓） | 结果 |
|---|---|
| **单张** `GND` ✓ | `ok=True` ✓｜段 37｜过孔 2 ✓（**带件铜禁孔那档也 ok=True ✓**） |
| **单张** `BR+` ✓ | `ok=True` ✓｜段 10｜过孔 0 ✓ |
| **单张** `RC` ✓ | `ok=True` ✓｜段 12｜过孔 0 ✓ |
| **九张一起**（干净档 ✓） | **3/9** ✗ —— `GND` ✓ ／ `5V` ✓ ／ `DATA_IN` ✓ 成，其余 6 张全败 ✗ |
| **九张一起**（带件铜禁孔 ✓） | **2/9** ✗（件铜禁孔再吃掉 1 张 ✗） |

**★ 六张失败的**失败点**全部集中在同一小片** ✗：`R1`／`D3`／`L1`／`U1.connector12` ✓
（`BR+` `D3.c4→R1.c0` ✗｜`RC` `R1.c1→C1.c0`、`R1.c1→U1.c1` ✗｜`COIL_A` `L1.c0→D3.c5` ✗｜
`COIL_B` `L1.c1→D3.c2` ✗｜`DATA_OUT` `U1.c4→J2.c2` ✗｜`LED_DIN` `U1.c12→LED2.c2` ✗）。

⇒ **判决：病 = 互相抢走廊** ✗（`GND` 先占掉的那条，正是 `BR+`／`RC`／`COIL_*` **唯一**要走的那条 ✓）；
**不是**"单张布不通" ✗、**不是**障碍模型堵死 ✗、**不是**窄口袋 ✗。

⇒ **下一刀（就一件事 ✓）**：用**同一个探针**做**最小冲突组合**（两两 ✓／三三 ✓）⇒
定位"**谁抢了谁唯一的那条**" ✓ ⇒ 再决定改法 ✓（次序 ✓／避让代价 ✓／摆位 ✓）——
**每档都用连通数验收** ✓。

**十二、第七轮（2026-10-05 ✓）：单张 vs 一起 ⇒ **两类病分开了** ✓（今天最有价值的切分 ✓）**

| 网 | **单独**跑 | 九张一起 | 六张"败将"一起 |
|---|---|---|---|
| `GND` ✓ | ok ✓ | **ok** ✓ | — |
| `5V` ✓ | — | **ok** ✓ | — |
| `DATA_IN` ✓ | — | **ok** ✓ | — |
| `BR+` ✓ | **ok** ✓（段 10 ✓） | ✗ | **ok** ✓ |
| `RC` ✓ | **ok** ✓（段 12 ✓） | ✗ | **ok** ✓ |
| `DATA_OUT` ✓ | **ok** ✓（段 4 ✓） | ✗ | ✗ |
| `LED_DIN` ✓ | **ok** ✓（段 5／过孔 1 ✓） | ✗ | ✗ |
| **`COIL_A`** ✗✗ | **0/1 失败** ✗ | ✗ | ✗ |
| **`COIL_B`** ✗✗ | **0/1 失败** ✗ | ✗ | ✗ |

⇒ **两类病** ✓：

- **A 类（单张就布不出 ✗）**：`COIL_A`／`COIL_B` ✓ —— 失败腿都是
  **`L1（线圈）→ D3`** ✗（`L1.c0→D3.c5` ✓、`L1.c1→D3.c2` ✓）。
  ⇒ 这是**几何/障碍**问题 ✗（`段 0` = 第一条腿就出不去 ✓），**不是竞争** ✗。
  ★ 嫌疑（待单点核 ✓）：**线圈 `L1` 自己那 754 条铜箔**把它的盘围住 ✗ ——
  而"件铜归属"只在「该块铜**只盖到同一张网**的盘」时才打标 ✓
  ⇒ 若它同时盖到**别网**的盘 ⇒ `tag=None` ⇒ **谁都不许过** ✗（源码 L357 那段的口径 ✓）。
- **B 类（单张行、一起不行 ✗）**：`BR+`／`RC`／`DATA_OUT`／`LED_DIN` ✓ = **竞争** ✗
  ⇒ 次序 / 拆线重布 ✓。

★ **又一次推翻我的假设** ✗（今天第 5 个 ✓）：我说的"`GND` 抢走廊"✗ ——
实测 `GND,BR+` ⇒ **2/2 通** ✓；六张"败将"自己凑 ⇒ **2/6** ✓（`BR+`／`RC` 在里面**反而是通的** ✓）。

⇒ **下一刀（两小步 ✓）**：① 单点核 `L1.connector0` 的逃逸（A 类 ✓）；
② B 类查次序 / 拆线 ✓ —— 每档都用连通数验收 ✓。

**十四、第八轮（2026-10-05 ✓）：单点核 `L1` ⇒ **没人压它** ✗；且发现**我的探针少做了一步** ✗**

**① 引擎侧探针**（`_work/probe_start.py` ✓ —— 它直接调 `RT.obstacles()` ✓ 报"谁压住这只脚"✓）：

```
L1.connector0  中心 (43.73, 20.52) mm｜判到的网 = COIL_A ✓ ⇒ 压住它 0 块 ✓：空 ✓
L1.connector1  判到的网 = COIL_B ✓ ⇒ 压住它 0 块 ✓：空 ✓
D3.connector5／D3.connector2 ⇒ 同样 0 块 ✓
最近的东西只有「铜:L1(NFC_Coil_…, copper1, +0.25)」✗ —— 而盘在 copper0 ✓ ⇒ 两层不相干 ✓
```

⇒ **A 类不是我猜的"线圈自己的铜围住盘"** ✗（**今天第 6 个被推翻的假设** ✗）。

**② ✗ 更要紧：我怀疑 `probe_5v_alone.py` 的「`COIL_A` 0/1」是**探针自己少做了一步** ✗**

因为**库自己的驱动**在**同一块光板**上给的是 **7/9** ✓，逐网表（`_work/rt8_log.txt` ✓）：

| 网 | 驱动级结果 |
|---|---|
| `GND` ✗ | ✗（有 1 段没连上 ✓：`D3.c0→C1.c1` 不可达 ✓） |
| `RC` ✗ | ✗（`R1.c1→U1.c1` 不可达 ✓） |
| **`COIL_A`** ✓ | **✓（段 5 ✓）** |
| **`COIL_B`** ✓ | **✓（段 4 ✓）** |
| `5V`／`BR+`／`DATA_IN`／`DATA_OUT`／`LED_DIN` ✓ | ✓✓✓✓✓ |

⇒ **以「驱动级」结果为准** ✓：**基准 = 7/9** ✓，只需攻 **`GND` 与 `RC`** 两张 ✓
（比"3~4 张"的清单可信 ✓ —— 它出自**完整流程** ✓，不是探针的简化路径 ✓）。

**③ ★ 新教训（记下 ✓）**：**探针少做一步 ⇒ 会造出"假的失败"** ✗ ——
与"假的通过"**一样坏** ✗。⇒ **用探针下结论前，先跟「驱动级」结果对一次** ✓
（与 `diag_net.py` 那次"没挖盘 ⇒ 假口袋"是同一条教训 ✓）。

**十六、第九轮（2026-10-05 ✓）：把「谁围住它」**点名**了 ⇒ 两张都是**竞争** ✗**

**做法 ✓**：在**脚本里包一层** `make_grid`（把 `labels=st["labels"]` 转发进去 ✓）＋
`RT.Grid.OWN = True` ✓ ⇒ 诊断里那句「**未记录×N 格**」✗ 就变成了**真名字** ✓
（✗ 不改库 ✓；`_work/diag_ripup.py` ✓）。顺带把 tee 改成**每条都 flush** ✓（跑的过程中也能读 ✓）。

| 目标脚（口袋大小 ✗） | **被谁围**（库自己的出处表 ✓） |
|---|---|
| `RC` → `U1.connector1`（**33 格** ✗） | `线:DATA_IN×10` ✗｜`盘:U1.connector0×9`｜`盘:U1.connector2×7`｜`盘:U1.connector20(网=GND)×6`｜`盘:U1.connector3(网=GND)×1`｜`盘:U1.connector0(无网)×1` |
| `GND` → `C1.connector1`（**109 格** ✗） | `盘:L1.connector0(网=COIL_A)×18`｜`线:COIL_A×16` ✗｜`盘:C1.connector0(网=RC)×11`｜`过孔:LED_DIN×11` ✗｜`盘:C1.connector0×4`｜`线:RC×3` |

⇒ **病 = 别人的线/孔先占了那唯一的出口** ✗（`DATA_IN` 的线 ✓、`COIL_A` 的线 ✓、
`LED_DIN` 的过孔 ✓）＋ **QFN 邻脚本来就挤** ✓ ⇒ **竞争型** ✓
（与「每张单独都通 ✓」完全对上 ✓，不是几何 ✗）。

★ **次序证据** ✓：7/9 那份用的是《脚数↑》✓ =
`COIL_A → COIL_B → DATA_IN → DATA_OUT → LED_DIN → BR+ → RC → 5V → GND` ✓ ——
**`RC` 排第 7 ✗、`GND` 排最后 ✗** ⇒ 等到它们要过那条缝时，缝已经没了 ✓。

**十八、第十轮（2026-10-05 ✓）：库加了一档"难先"次序（**默认关** ✓）⇒ 实测 **5/9** ✗（不如现有最好的 7/9 ✓）**

**改动** ✓（`tools/pcb_route.py` ✓，**默认关** ✗、不动任何别处 ✓）：

| 位置 | 内容 |
|---|---|
| `ORDER_DIFFICULTY = False` ✓ | 总开关 ✓ |
| `_difficulty(net_pads, pads, items)` ✓ | 拥挤度 ✓ = 每脚 `VIA_PAD_KEEPOUT_MM`（0.55 ✓）光晕里压着的**障碍块数** ✓，按网求和 ✓（**无洪水** ✓、纯几何 ✓） |
| `_net_keys(net_pads, pads, items)` ✓ | 开了就 `insert(0, ("难先（拥挤↓）", …))` ✓ —— ★ 必须**排最前** ✗：`route()` 用 `[:tries]` **截断** ✓，排第 7 就等于**没跑** ✗ |
| CLI `--order-diff` ✓ | 打开它 ✓ |

**实测** ✓：

| 次序 | 连通 | 长 |
|---|---|---|
| **《难先（拥挤↓）》** ✗ | **5/9** ✗ | 173.3 mm |
| 《脚数↑》✓ | **7/9** ✓ | 271.7 mm |
| 《短网先》／《周长↑》 ✗ | 4/9 ✗ | 98.7 mm |

⇒ **这一档不帮忙** ✗ ⇒ **不改默认** ✓（仍是 opt-in ✓）。
⇒ **"拥挤度"这个便宜判据挑不出该先布的那张** ✗ ⇒ 要换就换成**真正的口袋大小**（洪水算 ✓，贵一点但准 ✓）。

**★ 更值得试的方向（诊断直接指向 ✓ —— 封口的是**别人的线** ✓）**：
现在 rip-up 只拆**自己那张网**的失败腿 ✗；而实测封住 `RC` 目标口袋的是 **`线:DATA_IN`** ✓、
封住 `GND` 目标口袋的是 **`线:COIL_A`** ✓ ＋ **`过孔:LED_DIN`** ✓
⇒ 让 rip-up **可以拆"直接封住目标口袋"的那条别人的线** ✓（拆了它、重布它、再布本张 ✓）。

**二十、第十一轮（2026-10-05 ✓）：两条路都量完了 ⇒ 次序路线**到此为止** ✓，剩下只能走结构 ✓**

**① 一行修（细间距盘禁落按实际线宽取小）⇒ 实测**零效果** ⇒ **已回退** ✗**（照实记 ✓）

- 动机 ✓：本板全程 **8 mil** ✓，而 `split_neck` 只缩不涨 ✓ ⇒ 实际铜面 8 mil ✗，模型按 10 mil 封 ✗ ⇒ 每边多封 **0.0254 mm** ✓。
- 实测 ✗：改成 `min(NECK_W_MM, TRACE_MM)` ⇒ 四个次序的连通数（**4/7/4/6** ✓）与**线长全部一模一样** ✗
  ⇒ 那 0.0254 mm **没跨过 0.15 mm 的格边界** ✓ ⇒ **零收益** ✗ ⇒ **回退** ✓（与"6 mil／净空 0.127"两次同样处理 ✓）。

**② `_difficulty` 换成真口袋大小（用库自己的 `flood` ✓）**

| 次序 | 连通 | 长 |
|---|---|---|
| **《脚数↑》** ✓（现有最好 ✓） | **7/9** ✓ | 271.7 mm |
| 《难先（口袋↑）》✓（新 ✓） | **6/9** ✗ | 227.1 mm |
| 《难先（拥挤↓）》✗（上一版 ✓） | 5/9 ✗ | 173.3 mm |
| 《短网先》／《周长↑》 ✗ | 4/9 ✗ | 98.7 mm |

⇒ **口袋判据比拥挤判据好** ✓（5 → 6 ✓），但**仍不及《脚数↑》** ✗ ⇒ **不改默认** ✓（保持 opt-in ✓）。

**③ 今天试过的**旋钮**（记个总表 ✓，以后不再重复试 ✗）**

| 旋钮 | 实测 | 结论 |
|---|---|---|
| `--no-lock`（不钉死 5V） ✓ | 4/9 ⇒ **6/9** ✓ | ★ **唯一真增益** ✓ |
| `--no-mid-keep` ✗ | 6/9（同一组数 ✓） | 无影响 ✗ |
| `--cell` 0.10／0.20／0.25 ✗ | 4／3／3 ✗ | 非单调 ✗ |
| 次序档（拥挤／口袋） ✗ | 5／6 ✗ | 都不及 7/9 ✗ |
| 细间距禁落按实际线宽 ✗ | 零效果 ✗ | 已回退 ✗ |

**④ ⇒ 剩下的只能走**结构** ✓**：诊断已**点名** —— 封住目标口袋的是**别人的线** ✓
（`线:DATA_IN` 封 `RC` ✓、`线:COIL_A` 封 `GND` ✓、`过孔:LED_DIN` ✓）⇒
**让 rip-up 拆"直接封住目标口袋"的那条别人的线** ✓（现在它只拆自己网的失败腿 ✗，
且挑"拆谁"用的是 `near_net` 的**猜测** ✓ 而不是**量出来的封口者** ✗）。

**二十二、第十二轮（2026-10-05 ✓）：按"量出来的封口者"排 rip-up（opt-in ✓）⇒ 实测**零效果** ✗**

**改动** ✓（`tools/pcb_route.py` ✓，**默认关** ✗、不动别处 ✓）：

| 位置 | 内容 |
|---|---|
| `RIP_BY_WIRES = False` ✓ ＋ CLI `--rip-wires` ✓ | 总开关 ✓ |
| `wire_near(net, other, segs)` ✓ | "拆谁"的判据从 `near_net`（**盘↔盘**的猜测 ✗）换成 **候选网的线 ↔ 本网焊盘**（**点↔线段真几何** ✓） |

**实测** ✓（VS Code 任务跑 ✓ —— 见下 ✗）：

```
--mil=8 --rip-wires ⇒ **7/9** ✓ —— 与基线**逐项相同** ✗
   GND ✗（`D3.c0→C1.c1` 不可达 ✓）／RC ✗（`R1.c1→U1.c1` 不可达 ✓）｜271.7 mm ｜过孔 11 ✓
   日志：`[拆线重布] 第 1 轮：没有一种拆法更优 ⇒ 停` ✓（它**试过了** ✓，不是没跑 ✗）
```

⇒ **拆掉一张别人的线不够** ✗ —— 与诊断**一致** ✓：`RC` 目标口袋的边界 **34 格里 23 格是邻脚的盘** ✗
⇒ 口袋是**几何**封的 ✓，不是线封的 ✗ ⇒ **"单网 rip-up"这一类到此结束** ✓（已量 ✓）。

**剩下的三条路** ✓（都要你定 ✓）：

1. 一次拆 **2~3 张**重布 ✓ —— 组合代价高 ✗（本板 9 张 ⇒ C(9,3)=84 ✗）；
2. **动摆位**（把那几只挤在一起的件挪 0.5~1 mm ✓）—— **治本** ✓，但动的是**你已确认**的摆位 ✗；
3. **接受 7/9 ＋ 人工补 2 张** ✓（同 `LED_DIN` 那次 ✓）—— 最快 ✓、最诚实 ✓。

★ **环境坑（已解决 ✓，记下 ✓）**：这台机器上**部分终端 PATH 是空的** ✗（连 `Set-Item` 都找不到 ✓），
`$env:PATH=…` 开头的命令还会被吃掉 ✗ ⇒ **改用 VS Code 任务**（`create_and_run_task` ✓，
它用 VS Code 自己的环境 ✓、输出也能直接读 ✓）⇒ 长命令以后都走任务 ✓。

**二十四、第十三轮（2026-10-05 ✓）：有界「拆 2 张」⇒ 全部 ≤ 7/9 ✗ ⇒ **天花板确认** ✓**

**先确认一件事 ✓**：`blockers=8` ✓（`pcb_route.route_ripup` 的默认 ✓）而候选**总共就 8 张** ✗
⇒ **"拆 1 张"已经试遍** ✓（不是没试 ✓）。

**新增有界试探** ✓（写在 `_work/diag_ripup.py` ✓，用**库自己的** `_route_once` ✓ 与同口径的"线↔盘"距离 ✓）：

| 组合（失败的网 ＋ 两个封口者 ✓） | 连通 |
|---|---|
| `RC ＋ DATA_IN ＋ 5V` ✗ | 7/9 ✗ |
| `RC ＋ DATA_IN ＋ BR+` ✗ | 6/9 ✗ |
| `RC ＋ 5V ＋ BR+` ✗ | 6/9 ✗ |
| `GND ＋ 5V ＋ LED_DIN` ✗ | 7/9 ✗ |
| `GND ＋ 5V ＋ DATA_IN` ✗ | 6/9 ✗ |
| `GND ＋ LED_DIN ＋ DATA_IN` ✗ | 6/9 ✗ |

⇒ **没有一组超过 7/9** ✗ ⇒ **天花板 = 7/9** ✓
（本摆位 ＋ 本规则模型 ✓；跨 6 次序 ✓、单网 rip-up ✓、封口者排序 ✓、拆 2 张有界 ✓ 都一样 ✓）。

**⇒ 结论（照实说 ✓）**：**现摆位下，"程序按规则全部布通"到不了 9/9** ✗。
差的 2 张（`GND` 的 `D3.c0→C1.c1` ✓、`RC` 的 `R1.c1→U1.c1` ✓）是**目标脚被几何封成
33／109 格的小口袋** ✗ —— 边界大头是**邻脚的盘** ✗（`RC` 34 格里 23 格 ✓、`GND` 也有
`盘:L1.connector0×18` ✓ ＋ `盘:C1.connector0×11` ✓）。

**⇒ 两条收尾路（都要你定 ✓）**：

1. **动摆位**（把那几只挤在一起的件挪 0.5~1 mm ✓）—— **治本** ✓，
   但动的是**你已确认**的摆位 ✗ ⇒ 要你点头 ✓；
2. **接受 7/9 ＋ 人工补那 2 张** ✓（同 `LED_DIN` 那次 ✓）—— 最快 ✓、最诚实 ✓
   （你手上那张 v69 就是这么通的 ✓、`pcb_check` 也全过 ✓）。

**二十六、第十四轮（2026-10-05 ✓）：口袋是「线切出来的」✗ ⇒ 挪位不是解 ✗（第 7 个被推翻的假设 ✓）**

**做法** ✓（`_work/nudge_sweep2.py` ✓，只动**副本** ✓、用**库自己的** `flood` ✓）：

- 把某只件的 PCB 摆放位挪 1 mm ✓ —— 只动 `<pcbView>` 里**第一个** `<geometry>` ✓
  （= 摆放位 ✓）＋ `titleGeometry` ✓；★ ✗ **其余 `<geometry>` 是焊盘自己的**（相对件 ✓），
  挪了就错 ✗（实测：不限定个数 ⇒ geometry 命中 **3~7** 个 ✗ 直接报错 ✓）。

**量出来的** ✓：

| 情形 | `RC` 的 `U1.connector1` | `GND` 的 `C1.connector1` |
|---|---|---|
| **光板**（没布任何线 ✓） | **34350 格** ✓ | **35114 格** ✓ |
| 挪 `C1`／`R1`／`L1`／`D3`／`U1` 各 ±1 mm（20 种 ✓） | 34315 ~ 34427 格 ✓ | 35087 ~ 35191 格 ✓ |

⇒ **光板上那两只脚本来就在整片主区域里** ✗ ⇒ **根本没有口袋** ✓；
⇒ **口袋是「线切出来的」** ✗ —— 诊断里边界上那些"邻脚的盘"是**口袋的墙** ✓、**不是起因** ✗；
⇒ **±1 mm 挪位几乎不改变什么** ✗ ⇒ **"动摆位"在这个量级上不是解** ✗（我先前猜的"几何封死" ✗）。

**⇒ 真正的规则候选（下一刀 ✓）**：

> **布线不许「切断别人的脚口」** ✗ —— 一条线经过某只脚附近时，不许把那只脚
> 与主区域的连通**切断**（把它关进小口袋 ✓）。

- **可机器守** ✓（有界 ✓）：布线后**逐脚泛洪** ✓，某脚区域 < 阈值（或 < 全板 x% ✓）⇒ **报** ✗；
- **可进搜索** ✓（有界 ✓）：给"**贴着别人脚口走**"的路加代价 ✓ ⇒ 宁可绕一点 ✓。

**二十八、第十五轮（2026-10-05 ✓）：脚口闸门做出来了 ⇒ 交付件 `v69` 上**0 只小口袋** ✓**

**脚本** ✓（`_work/escape_gate.py` ✓ 第一版 ✓，以后提进库 ✓）：

| 口径 | 内容 |
|---|---|
| 障碍 | 库自己的 `obstacles()` ✓ ＋ **文件里的走线/过孔** ✓（当保线 ✓，逐段按**它自己的 mils** ✓ ⇒ 调库的 `keep_obstacles` ✓，✗ 不自己拍宽度 ✗） |
| 泛洪 | 每张网先 `carve_pads` ✓ ⇒ 用**库自己的 `flood`** ✓ 逐脚泛洪 ✓（✗ 不另写 BFS ✓） |
| 报什么 | **格数 ＋ 边界出处** ✓（= "那一刀是谁" ✓）；✗ 不猜原因 ✗ |

**实测** ✓：

```
pixel-pcb-v69.fzz（你确认过的交付件 ✓）｜盘 47 ✓｜走线 177 ＋ 过孔 16 ✓
全板可走 25662 格 ✓｜阈值 3% = 769 格 ✓
⇒ 被封成小口袋的脚：**0 只** ✓（共 30 只 ✓）
```

⇒ **两条关键结论** ✓：

1. **这条规则与实物相容** ✓ —— 人做得过的板子**照样通过** ✓
   （新闸门**没有**把已接受的成品判死 ✓✓ —— 这是加闸门最该先验的一件事 ✓）；
2. 我们的 7/9 结果里**恰好有 2 只脚**踩这条规则 ✗ ⇒ **它就是我们要找的那把尺子** ✓。

**三十、第十六轮（2026-10-05 ✓）：闸门接进打分（opt-in ✓）⇒ 实测仍 **7/9** ✗（第一维被连通数占住 ✓）**

**改动** ✓（`tools/pcb_route.py` ✓，**默认关** ✗）：`ESCAPE_PENALTY` ＋ `escape_penalty()` ＋ `_GATE` ✓
⇒ 打分从 `(连通, -长)` 变成 **`(连通, -被封成小口袋的脚数, -长)`** ✓
（障碍 = 基础障碍 ＋ **本候选自己布的线/过孔** ✓，逐段按它自己的 mils ✓，调库自己的 `keep_obstacles` ✓；
每张网先 `carve_pads` ✓、再用库自己的 `flood` ✓ 逐脚泛洪 ✓；阈值默认 3% ✓）。

**实测** ✓：`--mil=8 --escape-penalty` ⇒ **7/9** ✗（逐网与基线**相同** ✓）。

⇒ **原因清楚** ✓：打分的**第一维是连通数** ✓ —— 它一旦不同 ✓，后面的"脚口"维**轮不上说话** ✗；
而 7/9 那一档里**只有一份解** ✓ ⇒ 无变化 ✓。

⇒ 要让这条规则**真正咬住** ✓，只有两条路 ✓：

1. 做成**逐条路径**的代价 ✗（走一步算一次泛洪 ✗ ⇒ **贵** ✓）；或
2. 等**连通数打平**时再比它 ✓（本板 9 张全通时才有意义 ✓ —— 也就是"先到 9/9 再谈不封口" ✓）。

★ 但**这一轮的实际收益不小** ✓：**闸门本身可用了** ✓（`escape_gate` ✓ 在 `v69` 上报 **0 只** ✓），
而且**"这条规则与实物相容"已经验过** ✓ —— 这是以后任何"脚口"改动的前提 ✓。
★ 顺带修一处显示 bug ✓：开了罚项后日志里「长 X mm」误把**罚项**当长度 ✗（改用 `s[-1]` ✓）。

**三十二、第十七轮（2026-10-05 ✓）：②「逐路径脚口代价」⇒ **首破天花板：7/9 → 8/9** ✓✓**

**改动** ✓（`tools/pcb_route.py` ✓，**默认关** ✗）：

| 位置 | 内容 |
|---|---|
| `ESCAPE_COST_MM = 0.0` ✓ ＋ CLI `--escape-cost=<mm>` ✓ | 走"别人脚口附近"的**每一格**加价 ✓（✗ 不是禁死 ✓） |
| `ESCAPE_R_MM = 0.45` ✓ ＋ CLI `--escape-r=<mm>` ✓ | 影子半径 ✓（比过孔禁落 0.55 稍小 ✓） |
| `escape_shadow(grid, pads, net_pads, net)` ✓ | 影子格 ✓ —— 用**库自己的 `grid.rc`** ✓ 算格号（✗ 不自己拍换算 ✗） |
| `astar(..., avoid2=, avoid2_w=)` ✓ | 复刻已有的 `avoid/avoid_w`（"加罚不禁死" ✓）机制 ✓ |

**实测** ✓（同一块光板 ✓、同一份网表 ✓）：

| 配置 | 连通 | 形状 |
|---|---|---|
| 基线 ✓ | 7/9 ✗ | `GND`✗（段 46 ✓）／`RC`✗ ✓ |
| **`--escape-cost=0.3`** ✓ | **8/9** ✓✓ | **`RC` 通了** ✓（段 30 ✓）；只剩 `GND` ✗ |
| `--escape-cost=0.6` ✓ | **8/9** ✓ | 同形 ✓ |
| `＋ --signals-first` ✗ | 8/9 | 库驱动上是 **no-op** ✗（逐字相同 ✓） |
| `＋ --escape-r=0.3` ✗ | 7/9 ✗ | 半径太小 ⇒ `RC` 又丢 ✓ ⇒ **默认 0.45 是对的** ✓ |

★ 与上一轮的对照 ✓：同一条规则接在**候选解打分**上 ⇒ **无效** ✗（第一维连通数占住 ✓）；
接在**每步代价**上 ⇒ **有效** ✓（`GND` 让出的那点空间，`RC` 就用上了 ✓）。

**三十四、第十八轮（2026-10-05 ✓）：8/9 稳住 ✓ ⇒ 卡点是「`GND` 与 `RC` 在抢同一个早布位」✗**

| 配置 | 连通 | 谁没通 ✗ |
|---|---|---|
| 基线 ✓ | 7/9 ✗ | `GND` ✗、`RC` ✗ |
| **`--escape-cost=0.3`** ✓ | **8/9** ✓ | `GND` ✗ |
| **`--escape-cost=0.6`** ✓ | **8/9** ✓ | `GND` ✗ |
| `--escape-cost=0.3 --first=GND` ✓（用我自己的包装 ✓） | **8/9** ✓ | **`GND` 全通 ✓（段 76 ✓）**；**换成 `RC` 丢** ✗ |
| `--escape-cost=0.3 --via=3` ✗ | 8/9 | `GND`（过孔 11→17 ✗） |
| `--escape-cost=0.3 --rip-wires --passes=6` ✗ | 8/9 | `GND` |
| `--escape-cost=2.0` ✗ | **6/9** ✗ | 价太高 ⇒ 普遍搜不动 ✗ |

⇒ **本轮的硬事实** ✓：**`GND` 与 `RC` 在抢同一个"早布"的位子** ✗ ——
谁先谁活 ✓、谁后就死 ✗，**总数卡在 8** ✓。
⇒ 下一步的两条路 ✓（都还没试 ✓）：

1. **按网定价** ✓：让"容易被人切断的网"的**别人**多付代价 ✗ ⇒ 等价于"保护**未布网的**脚口" ✓
   （只保护**还没布**的网的目标脚 ✓ —— 已布完的网不再需要保护 ✓）；
2. **把影子做成硬禁** ✗（在**已布网**的脚口上只准绕 ✓）—— 更狠 ✓，但可能伤通 ✓ ⇒ 先试 ①  ✓。

**三十五、下一步（要加的规则 ✓）**

① **只保护「还没布完的网」的脚口** ✓（随着布线推进，保护集**逐渐缩小** ✓）——
这正好对上"谁后来谁吃亏"的病 ✓，而且是**有界**改动 ✓（每段布线前重算一次影子集 ✓）。

只剩 **`GND`** 一张 ✗（带罚项后它反而更差 ✓：段 3 ✗、7 段没连上 ✗）——
它是"**脚最多（9 只）、到处都要穿别人的影子**"的那种 ✓ ⇒ 下一刀（一次一改 ✓）：
① 给它**单独**的档 ✓（或 ② 把过孔调便宜 `--via` ✓ ⇒ 让它靠**换层**穿过去 ✓）。

⇒ 现摆位下 **7/9 是天花板** ✓（已量尽 ✓）。收尾二选一 ✓：

1. **接受 7/9 ＋ 人工补那 2 张** ✓（同 `LED_DIN` 那次 ✓）—— 最快 ✓、最诚实 ✓；
2. **逐路径罚项**（把"不许切断别人脚口"做成每步代价 ✓）—— **治本** ✓、但**贵** ✓（我可以做 ✓）。

**② 把这条闸门接进布线的目标函数** ✓（有界 ✓）：

- 只对**候选解**算 ✓（6 种次序 ＋ rip-up 的几个 trial ✓），**不是每格**算 ✗ ⇒ 代价可接受 ✓；
- 打分时**罚"封了别人的脚口"** ✓ ⇒ 让搜索**自己挑**出不封口的解 ✓；
- 验收 ✓：`escape_gate` 自己（0 只 ✓）＋ 连通数（目标 9/9 ✓）＋ `pcb_check` 全过 ✓。

1. **逃逸 / 扇出（escape）一趟** ✓：细脚距封装（`U1` QFN20 0.4mm ✓、`D3` SOT363 ✓）
   每只脚先朝**径向外**铺一小段存根 ✓，再从存根起布 ✓ —— 这是"脚口"的正解 ✓；
2. 每改一档必须报：连通 x/9 ✓、`pcb_check` ✓、`pcb_metrics`（段数/过孔/正交度 ✓）；
3. **不许自证** ✓：连通数用 `fz_status.py`／`power_list.py` 复核 ✓。

★ 环境坑（记 ✓，省得再踩 ✗）：本机终端**有的是 cmd、有的是 PowerShell 且 PATH 被削** ✗（`chcp`／`cd`／`py` 都可能"不认" ✓）⇒ 命令一律写成**两个 shell 都能跑**的形式 ✓
（绝对路径 ✓、不用 `$变量`／`chcp` ✓）。
⇒ 下一步找**原生兼容**方案（用户 2026-10-05 定 ✓）：① 最省事 = **面包板单独一个草图** ✓；
② **改我们自己的面包板件**（做一份 `.fzp` 里**不给孔声明 `pcbView`/`schematicView`** 的
面包板 ✓ ⇒ 桥根本不存在 ✓、也不怕另存 ✗、且**不动任何文件** ✓）；
③ 先做个便宜实验定方向 ✓：把 `v67_exp_nobbviews.fzz` 在 Fritzing 里**另存一次**，
再看 PCB/原理图段里那 55+8 条记录**会不会自己回来** ✗ —— 会回来 ⇒ ② 必做 ✓；
不回来 ⇒ ①/③ 也够用 ✓。

**三十六、第十九轮（2026-10-05 ✓）：「不许切断别人的脚口」做成**判官** ✓ —— 两种改法**实测否掉** ✓，回到干净基线 ✓**

★ 本轮的**全部实测**（同一光板 `_work/v69_bare.fzz` ✓、同网表 ✓、8 mil ✓）：

| 配置 | 连通 | 线长 mm | 过孔 |
|---|---|---|---|
| **基线（不开开关）** ✓ | 7/9 | 271.7 | 11 |
| `--escape-cost=0.3`（**上一轮最好** ✓） | **8/9** ✓ | 218.6 | 11 |
| `--escape-protect`（只保护未布完的网 ✗） | 7/9 ✗ | — | — |
| `--escape-protect --escape-cost=0.6` ✗ | 7/9 | 253.4 | 9 |
| `--escape-protect --escape-cost=1.0` ✗ | 7/9 | 159.1 | 7 |
| `--escape-protect --escape-cost=5.0` ✗ | 8/9 | 327.3 | 17 |
| `--escape-cost=0.3 --escape-r=0.80` ✗ | 7/9 | 275.3 | 14 |
| `--escape-cost=0.3 --escape-r=1.20` ✗ | 7/9 | 285.2 | 17 |
| `--escape-cost=0.3 --escape-r=2.00` ✗ | 7/9 | 278.2 | 13 |
| **`--escape-wall`（判官 ✓，只报不改 ✓）** | **7/9** ✓ | **271.7** ✓ | **11** ✓ |
| `--escape-wall`（旧版：改道 ＋ 保护带 ✗） | 7/9 | **473.0** ✗ | **47** ✗ |
| `--escape-wall --escape-cost=0.3`（旧版 ✗） | 7/9 | **475.9** ✗ | **47** ✗ |

⇒ 判官版与基线**逐项相同** ✓（7/9、271.7 mm、11 孔、**各网段数也一致** ✓）——
「**只报不改**」这句话是**可自检**的 ✓（不是我说它不动就不动 ✓）。

★★ 本轮**量出来的四条**（都改变了做法 ✓）：

1. **量别人的脚，要按「它自己的口径」摆栅格** ✗✓：`grid` 是"**正在布这张网**"的视角 ✓ ——
   ①它**故意不挡自己已布的线** ✗ ⇒ 累积出来的封口**量不出来** ✗；②`carve_pads` 只为**本网**
   挖出口 ✗ ⇒ 别人那只脚**连自己口都没挖开** ✗ ⇒ 泛洪只有几十格 ✓。
   ⇒ 用错口径时 **18 次调用 0 次命中** ✓（实测 ✓）；改成"挡上**所有**线（含本网已布 ✓）＋
   挖开**它自己**的盘 ✓"之后**当轮就命中** ✓。
2. **判据不能用"脚口格数"** ✗（**代理量** ✓）：`RC.connector1` 还剩 **431 格** ✓（> 400 ⇒ 判"健康" ✗）
   **可它已经连不上 `C1.connector0` 了** ✗ ⇒ 改成**直接问"还能不能连上"** ✓
   （= **Fritzing 的语义** ✓，仓规 §13 ✓），而且是**早停**的 ✓（能连上时一碰伙伴脚就返回 ✓）。
3. **`watch` 3 mm 太紧** ✗：`RC.connector1` 那块口袋的**中心刚好落在框外** ✗ ⇒ 放宽到 **8 mm** ✓。
4. **光板上每只脚都是整片空地（20000+ 格 ✓）** ✓ ⇒ 口袋**全是线切出来的** ✓
   （"摆位本来就窄"这个怀疑**被排除** ✓）。

★★ 两种改法**被实测否掉** ✗（已回退 ✓，仓规 §0 第 3 条）：

- **① 事后"禁掉这条走廊重搜"** ✗：**100%** 落进「**搜不到别的路**」✓ —— 因为被切的那一段
  往往正是**必须连**的那段 ✓ ⇒ 禁了就没路 ✓ ⇒ 只能退回 ✓（日志里它**每次都原形毕露** ✓）。
- **② "未布完的脚从它自己出发前 2000 格"整片加价** ✗（"留路"的**实测版** ✓，仓规 §5b ⑩ 的强化 ✓）：
  连通**一点没涨** ✗（还是 7/9 ✓），而**质量塌了** ✗ —— 线长 **271.7 → 473.0 mm** ✗、
  过孔 **11 → 47** ✗（价把线逼得到处绕 ✓）。

⇒ 结论 ✓：**"事后拦"这个方向不成立** ✗（切人的那段常常不可替代 ✓）；
**判官留下** ✓ —— 它是这条规则的**机器守** ✓，能**精确点名**"**哪一段切了哪只脚**" ✓。

★★ **勘误（2026-10-05 当天就改 ✓）**：上一节刚写下的那两句"判官的图"**读反了** ✗ ——
当时判官那句话把 **网名**印在**焊盘位号**的位置上（`RC.connector1` 其实是
`U1.connector1（网 RC）` ✗）⇒ 我把**受害者**当成了**加害者** ✗。
**修好标签后重跑的准数** ✓（`--escape-wall --why` ✓）：

    次序《脚数↑》（7/9 那份 ✓）：
      ⚠ [判官] 网 DATA_IN 的这一段（U1.connector2 → J1.connector2）切断了 ✗：U1.connector1（网 RC）
      ⚠ [判官] 网 RC 的这一段（R1.connector1 → C1.connector0）切断了 ✗：C1.connector1（网 GND）

⇒ 真的故事是**一条链** ✓：**`DATA_IN` 切 `RC`** ✗ ⇒ **`RC` 再切 `GND`** ✗
（终局 `RC` ✗ 是"到不了 `U1.connector1`" ✓、`GND` ✗ 是"到不了 `C1.connector1`" ✓ —— **两条都对得上** ✓）。

**三十七、第二十轮（2026-10-05 ✓）：判官**指路**也试了 ✓ ⇒ **第三个家族也被否掉** ✓；顺手修掉判官的**贴错标签** ✗**

判官已经能**精确点名**"哪一段切了哪只脚" ✓ ⇒ 最自然的下一刀就是**把它变成次序** ✓
（"**受害者排到它的加害者前面**" ✓）—— 同一 `_route_once` ✓、**只换次序** ✓：

| 次序 | 连通 | 线长 mm | 过孔 |
|---|---|---|---|
| ① 原次序（《脚数↑》） | 6/9 | 217.5 | 15 |
| ② **受害者挪到最前**（第 1/2/3 轮） | **4 / 5 / 4** ✗ | 107.8 | 5 |
| ③ **最小扰动**：受害者**只挪到加害者前面一格**（第 1/2/3 轮） | **4 / 6 / 4** ✗（**2 轮循环** ✓） | — | — |
| ④ 对照组：反方向（受害者**后**） | 6/9（= 基线 ✓ 没得挪 ⇒ 恒等 ✓） | 217.5 | 15 |

⇒ **两个版本都更差** ✗：原因**一眼看得出来** ✓ —— 把 `RC` 挪到最前之后，
**它自己立刻变成加害者** ✗（`RC` 的一段 `R1.connector1 → U1.connector1` 一次切掉
`5V.connector5` / `BR+.connector0` / `DATA_OUT.connector4` / `DATA_OUT.connector2`
**四只脚** ✓）⇒ 伤害比收益大 ✓，而且**震荡**（4 ⇄ 6 来回 ✓）。

★★ 顺手抓到一个**真 bug**（报告层 ✓，正是仓规 §13 的病 ✓）：判官原来把那句话印成
`RC.connector1` ✗ —— 其实 `k2` 是**焊盘的 key** = `(位号, connectorN)` ✓，
`n2` 才是**网名** ✓ ⇒ 我把**网名**当成了**位号** ✗。读起来"像个合理名字" ✓
⇒ **潜伏得很深** ✗（正是"两个声音" ✓）。现已改成 **`U1.connector1（网 RC）`** ✓。

★★ 判官本轮量出来的真话 ✓（`《脚数↑》`那次 ✓）：

    ⚠ [判官] 网 GND 的这一段（LED2.connector1 → U1.connector20）把还没布完的脚切断了 ✗：
              U1.connector1（网 RC）

⇒ 三个家族 —— **事后拦 ✓**（第 19 轮 ✓）、**保护带 ✓**（第 19 轮 ✓）、**按判官重排 ✓**（本轮 ✓）
—— **全部实测否掉** ✗✗✗。⇒ 现摆位＋现算法下 **8/9（`--escape-cost=0.3` ✓）就是这四条路的尽头** ✓。
剩下**没试过**的只有换**家族**（不再是"绕开别人" ✗，而是**改自己这条路怎么走** ✓），
例如：**网内接法换一种** ✓（现在固定按"最近的一对脚"接 ✓ ⇒ 改成按 **MST** 接 ✓）——
一次一改 ✓，下一轮再说 ✓。

**三十八、第二十一轮（2026-10-05 ✓）：把「常任加害者」查出来了 ✓ ⇒ 它是 `DATA_IN` ✓；顺手改掉上一轮的勘误 ✓**

① **先查"标签与实际对不对得上"** ✓（仓规 §13 的日常动作 ✓）：
打印里《脚数↑》竟然是 `GND` 打头 ✗（它 9 只脚 ✓，按"脚数升序"该最后 ✗）——
查清 ✓ **没有 bug** ✓：库自己那 6 个次序是对的 ✓（`_work/probe_order.py` 原样打印 ✓：
《脚数↑》= `COIL_A → … → 5V → GND` ✓），我引用的那次日志带了 **`--first=GND`** ✓。
★ 教训（老话 ✓）：**引用日志要把开关一起引** ✗，否则"看起来是 bug" ✗。

② **修标签 ⇒ 读准 cut 图** ✓（上一轮的勘误 ✓，见上 ✓）：**伤害是一条链** ✓
**`DATA_IN` 切 `RC`** ✗ ⇒ **`RC` 切 `GND`** ✗。
而 **8/9 那一档**（`--escape-cost=0.3` ✓）判官说 ✓：

    ⚠ [判官] 网 DATA_IN 的这一段（U1.connector2 → J1.connector2）切断了 ✗：J1.connector1（网 GND）

⇒ **两档里切人的都是 `DATA_IN`** ✓✓ —— 它就是**常任加害者** ✓（一条 **25.67 mm** 的长线
横穿整板 ✗，而它只要 2 只脚 ✓ ⇒ 永远排在前面 ✓）。
**为什么影子（`--escape-cost`）拦不住它** ✗：影子只在**盘外 0.45 mm** 那一圈加价 ✗，
而**它下刀的地方在外圈** ✗（半径扫到 2.0 mm 仍 7/9 ✓）—— 这就把"半径法没用"解释通了 ✓。

③ **顺理成章的一刀** ✓：**把常任加害者排最后** ✓（它自己去绕 ✓；受害者先出门 ✓）——
用包装传 `--last=DATA_IN` ✓（库自己那条路不认 ✓，实测过 ✓，正好说明**开关要验"真的改了次序"** ✗✓，
`--why` 的"次序实排"就是为这个 ✓）：

| 配置 | 连通 | 线长 mm |
|---|---|---|
| **`--escape-cost=0.3`（基线 ✓）** | **8/9** ✓ | 238.3 |
| `--last=DATA_IN --escape-cost=0.3` ✗ | **6/9** ✗ | 613.0 |
| `--last=DATA_IN`（无 cost）✗ | **6/9** ✗ | 533.3 |

⇒ **更差** ✗：把 `DATA_IN` 挤到最后 ⇒ **`5V` 反而 0 段全败** ✗（它得穿更多被占的通道 ✓）、
`DATA_IN` 自己也出不去 ✗ —— 伤害只是**换个地方** ✓（和 2026-09-30 那次"只改短网先 ⇒ 失败换位置"
是**同一个道理** ✓）。

★★ **至此的账** ✓：次序（≈10 种 ✓）、影子半径（0.45/0.8/1.2/2.0 ✓）、
只保护未布完的网 ✓、事后拦（禁走廊 ✓）、保护带（留路实测版 ✓）、判官指路重排（两种 ✓）、
常任加害者排最后 ✓ —— **除 `--escape-cost=0.3` ⇒ 8/9 以外，全部中性或更差** ✗✗。
⇒ **现摆位 ＋ 现算法族的天花板 = 8/9** ✓（剩下那一张恰好就是用户**已经接受过一次**的
那种情况 ✓：手工补一张 ✓，同 `LED_DIN` 那次 ✓）。

**三十九、第二十二轮（2026-10-05 ✓）：用户选 B（换摆位）⇒ 先把它**量清楚** ✓，并抓到一个**真弱点**（打分尺子 ✗）**

### ① 先看见再说 ✓（不许只拿数字拍布局 ✓）

`_work/render_pcb.py` ✓ 把**布好线的 PCB** 渲成 SVG ✓（粗=顶层 ✓／细=底层 ✓／虚线=没布通的网 ✓），
用浏览器一看就清楚 ✓：

- **黄 = `DATA_IN`** ✓：它从 `J1`（板左上 ✓）沿**板顶**跑到右边 ✗，再**贴着 `U1` 右侧列下来** ✗
  —— 而 `U1.connector1/2/5` **全在那条 `2.25 × 6.75 mm` 的竖条里** ✗（口袋重合 ✓，实测 ✓）；
- 早布的 `BR+`/`GND`/`5V` 把那条竖条的**口子**封上 ✗（判官点名的正是这条竖条 ✓）。

### ② 摆位扫描 ✓（只动副本 ✓，量连通数 ✓）

| 挪法 | 连通 | 线长 mm | 未通 |
|---|---|---|---|
| **不挪（基线 ✓）** | **8/9** ✓ | 238.3 | `GND` |
| `C1 +4.0, +1.4` ✗ | 7/9 | 190.6 | `GND`、`RC` |
| `C1 +5.0, +1.4` ✗ | 7/9 | 190.6 | `GND`、`RC` |
| `C1 +6.0, +1.4` ✗ | **8/9** | 292.6 | **`RC`**（输家**换了** ✗） |
| `C1 +4.0, +4.0` / `+2.0, +4.0` ✗ | 7/9 | 263.3 / 263.0 | `BR+`、`RC` |
| `R1 +2.0, -1.4` ✗ | 6/9 | 168.3 | `5V`、`GND`、`RC` |

⇒ **天花板还是 8/9** ✗，而且**输家只是换来换去** ✓（`C1 +6` 把 `GND` 救活 ✓、`RC` 又死 ✗）
—— 和"换次序"是**同一种病** ✓（伤害搬家 ✓）。

### ③ ★★ 顺手抓到一个**真弱点** ✓：打分的尺子**分不清两种 8/9** ✗

上面那张日志里原本只报"连通 8/9 ✓｜长 …" ✗ —— 可**8/9 有两种** ✓：

- 差的那张网**只差一口气** ✓；
- 差的那张网**几乎全断** ✗（实测：8/9 那份里 **`GND` 只布出 3 段、7 条连接没连上** ✗）。

✗ 旧打分 `(连通网数, -总长)` **把两种当成一样** ✗ ⇒ 拆线重布会把**差的那种**当好解收下 ✗。
✓ 现在多一维 **`-Σ(每张网缺的段数)`** ✓ —— 这正是 **Fritzing 状态栏那句**数的东西 ✓
（`mainwindow.cpp:2298` ✓：`%1 of %2 nets routed - %n connector(s) still to be routed` ✓ ——
它数的是 **connector** ✗ 不是网 ✗ ✓）= 仓规 §13「**同一把尺子**」✓。

★ 立竿见影 ✓（同一档配置现在报得出差别 ✓）：

| 次序 | 连通 | **还差几条连接** | 长 mm |
|---|---|---|---|
| 《脚数↑》 | 7/9 | **8** ✗ | 210.2 |
| 《长网先（面积↓）》 | 6/9 | **4** ✓ | 218.6 |
| 《周长↓》 | 6/9 | **4** ✓ | 218.6 |

⇒ 一眼看出：《长网先》虽然**少通一张** ✗，但**坏得少得多** ✓（4 条 vs 8 条 ✓）——
这在**同连通数**比较时才起作用 ✓（本轮 8/9 那一档不变 ✓，如实记 ✓）。

### ④ 下一步 ✓（留给用户拍 ✓）

- **A：收在 8/9 ＋ 人工补最后一张** ✓（同 `LED_DIN` 那次 ✓）—— 我建议 ✓；
- **B2：接着换摆位** ✓ —— 但**已扫的 10 个候选全没破 8/9** ✗，而且**输家搬家** ✓；
  下一步该换成**扇出一趟** ✓（README §三十五 早就列过 ✓：**每只脚先朝外铺一段存根** ✓
  ⇒ `U1` 右列那条竖条就**不会被人封口** ✗）—— 那是"改算法" ✗，不是"摆位" ✓。

**四十、第二十三轮（2026-10-05 ✓）：B2「扇出一趟」做出来了 ✓ ⇒ **扇出被否掉** ✗；**但尺子换代换来大丰收** ✓✓**

### ① 扇出（fan-out）实现 ✓（库加了 `seed=` ✓）

做法 ✓（README §三十五 早就列过 ✓）：**先把每只脚朝外的一小段"存根"占住** ✓
（径向 ✓、用库自己的 `astar` ✓、`via_at_start=True` ✓ —— QFN 0.4 mm 脚距在铜 0 **没出口** ✗，
必须先下到铜 1 ✓），再照常布线 ✓ ⇒ 门**已经属于它自己** ✓，别人只能绕 ✓。

★ 库改动很小 ✓：`seed=` ✓ —— 与 `pre` 只差一点 ✗（`pre` 的网**会被跳过** ✗，
`seed` 的网**照样要布** ✓）⇒ 让"已铺好的铜"当障碍 ✓ 又不丢那张网 ✓。
★ 途中踩到一个**自己的坑** ✗（记 ✓）：扇出第一版 **7 只脚全"无路"** ✗ ——
查出来是**我没挖开它自己的盘** ✗ ⇒ **起点格本身被"盘障碍"占着** ✗ ⇒
`astar` 第一句 `if not free(start): return None` ✓（真实布线器靠 `carve_pads` ✓）。
★ 教训 ✓：**看着像"QFN 出不去"的地方，先怀疑"我有没有挖盘"** ✗。

### ② 扇出**实测**：连通数**没涨** ✗，全件扇**更差** ✗

| 配置 | 连通 | 还差几条连接 | 线长 mm | 过孔 |
|---|---|---|---|---|
| 不扇出 ✓ | **8/9** ✓ | **2** ✓ | 397.6 | 31 |
| 扇出 `U1`（1.5 mm）✗ | 7/9 ✗ | 2 | 335.8 | 17 |
| 扇出 `U1`（2.5 mm）✓ | **8/9** | **2** | 367.8 | 27 |
| 扇出**全部件**（50 段 ✓）✗ | **6/9** ✗✗ | 4 | 309.6 | 22 |

⇒ **扇出不是这一题的解法** ✗：存根到处占地 ✓（全件扇 ⇒ **6/9** ✗✗），
而它确实**救活了 `RC`** ✓（不扇出那份差的是 `RC` 整张 ✗；扇出后换成 `BR+`/`GND` 各差一条 ✗）
—— 又是"**伤害搬家**" ✓（和第 22 轮的摆位扫描同一种病 ✓）。

### ③ ★★ 真正的收获 ✓：**尺子换代** ✓✓

第 22 轮加了"还差几条连接"这一维 ✓，本轮**把它升成第一维** ✓ —— 依据是**实测** ✓：

- **「还差几条连接 = 0」 ⟺ 每张网都接完了 ⟺ 9/9** ✓✓ ⇒ 它才是**离目标多远**的真尺子 ✓；
- "连通网数"**不是** ✗（差 1 条与差 7 条都只算"没通" ✗）；
- 而且它正是 **Fritzing 状态栏**数的东西 ✓（`mainwindow.cpp:2298` ✓ 数的是 **connector** ✗）= §13 ✓。

★ 立竿见影 ✓（**同一个算法、同一块板** ✓，只是换尺子 ✓）：

| 尺子 | 找到的最好解 | 还差 |
|---|---|---|
| 旧的（连通网数优先 ✗） | 8/9 | **7 条** ✗ |
| **新的（连接数优先 ✓）** | **8/9** ✓ | **2 条** ✓ |

⇒ 板子从"**离全通差 7 条**"一跃到"**差 2 条**" ✓✓ —— 而且差的正是 **`RC` 那两根短连线** ✓
（`RC` = `R1` / `C1` / `U1.connector1` 三个脚的无源网络 ✓ ⇒ **手工补极容易** ✓）。

### ④ 结论 ✓

★★ **勘误（2026-10-06 当天就改 ✓，见 §四十一）**：上面那个「**8/9 差 2**」是在
**放宽了规则**的条件下量出来的 ✗ —— scratch 里 **没传 `copper_keep`** ✗
（= 允许过孔贴着**线圈的铜** ✗），而那是**用户定下的硬规矩** ✗
（「通孔不能在元件内，并与有安全距离」✓）⇒ **它不是合法解** ✗、**不能当交付依据** ✗。
**把规则加回去重跑 ✓ ⇒ 逐项复现驱动自己的数字** ✓（`7/9 ✗｜差 3 条 ✗｜282.8 mm｜过孔 9` ✓）
⇒ **合法的天花板 = 7/9 ✗，还差 3 条连接** ✓ —— 但**尺子换代仍然实赚** ✓：
剩活从「**7 条**」降到「**3 条**」✓（旧尺子下最好那份是 `8/9 差 7 条` ✗）。
★ 教训 ✓：**自己搭的 scratch 必须与驱动同口径** ✗（少传一个 `copper_keep` 就多出一个虚假的好结果 ✗）。

**四十一、第二十四轮（2026-10-06 ✓）：出交付件 `pixel-pcb-v70.fzz` ✓｜勘误 ＋ 闸门抓到一个真缺陷 ✓**

### ① 交付件 ✓：`pixel-pcb-v70.fzz`

出图命令（**逐项可复现** ✓）：

```
gen_routes.py _work/v69_bare.fzz pixel-pcb-v70.fzz --nets=pixel_nets.py --mil=8 \
  --no-lock --first= --escape-cost=0.3 --no-mid-keep --blockers=16 --passes=8 \
  --layer-pen=0.35 --deliver
```

（驱动本轮补了 **`--escape-cost=` / `--escape-r=` / `--blockers=`** 三个口子 ✓
—— ✗ 量出来的好档出不了图就很尴尬 ✗。）

| 项 | 数 |
|---|---|
| **连通** | **7/9** ✗（`GND` ✗、`RC` ✗） |
| **还差几条连接** ✓（与 Fritzing 同义 ✓） | **3** 条 ✗ |
| 线长 | 282.8 mm｜过孔 **8** 个 ✓ |
| 悬空端点 | **0** ✓（必须 0 ✗） |
| 短路（同层叠） | **0** 对 ✓ |

**剩下要手工补的正好是这 3 条** ✓（都是短连线 ✓）：

1. `GND`：`D3.connector0` → `C1.connector1` ✗
2. `RC`：`R1.connector1` → `C1.connector0` ✗
3. `RC`：`R1.connector1` → `U1.connector1` ✗

⇒ 在 Fritzing 里的等价说法 ✓：**`7 of 9 nets routed - 3 connector(s) still to be routed`** ✓
（`mainwindow.cpp:2298` ✓）。**请用户打开看一眼底部那句话** ✓ —— 那是我**跑不了**的验收 ✓。

### ② 勘误 ✓（上一轮我报的 "8/9 差 2" 是**违规解** ✗）

✗ scratch 里**没传 `copper_keep`** ✗（过孔可以贴着**线圈的铜** ✗）⇒ 多出一个假的好结果 ✓。
补上规则重跑 ⇒ **逐项复现驱动**（`7/9｜差 3｜282.8 mm｜过孔 9` ✓）⇒ **确认是假的** ✗。
★ 规矩 ✓：**自己搭的 scratch 必须与驱动同口径** ✗（少一个开关就多一个假结论 ✓）。

### ③ 闸门抓到一个**真缺陷** ✓（已修 ✓）

`pcb_check` 第 ⑪ 条点名 ✗：**`Via7` 与 `Via8` 坐标完全相同** ✗（两颗孔叠在同一点 ✓）——
根因：一张网的**多段共用同一个换层点** ✓ ⇒ 同一颗孔被**记了两遍** ✗。
✓ 修法（一处 ✓，库内 `_route_once`）：过孔入账前**去重**（**完全同点**才去 ✓）
⇒ 过孔 **9 → 8** ✓、⑪ 条清除 ✓。
★ 这也正是**闸门该干的活** ✓ —— 它不是形式 ✓，它抓到了一个我肉眼看不出的物理错误 ✗。

### ④ 三道闸门 ✓（v70 ✓）

| 闸门 | 结果 |
|---|---|
| ① `pcb_check`（几何/短路/过孔/安装孔/<connect> 核对 ✓） | 只剩 ⑤ 的两条**预期未通** ✗（`GND`/`RC` ✓） |
| ② `fz_deglue_views --check` | **0** 条 ✓ |
| ③ `sch_straighten` | 改动 **0** ✓、V1 **0** ✓、V3 2（**早就有的两处** ⚑ ✓） |

**四十二、第二十五轮（2026-10-06 ✓）：用户报「Fritzing 显示布线完成」⇒ 查出**幽灵连接** ✗ ⇒ **撤回 v70、v69 才是完整的** ✓

### ① 用户的话（**权威** ✓）与我的判据**打架** ✗

用户：打开 `pixel-pcb-v70.fzz`、**一句没改** ⇒ Fritzing **PCB 视图显示「布线完成」** ✓（截图 ✓）。
而我的 `pcb_check` ⑤ 说 `GND`/`RC` 没连通 ✗ ⇒ **两个声音** ✗（仓规 §13 要消灭的事 ✓）。

### ② 先**读源码** ✓（不许猜 ✓）

| 事实 | 出处 |
|---|---|
| 「布线完成」= **`Routing completed`** ✓ | 译文表 `fritzing_zh_cn.ts:2257` ✓（**不是** "No connections to route" ✗） |
| 条件是 **`m_netCount == m_netRoutedCount`** ✓ | `mainwindow/mainwindow.cpp:2288` ✓ |
| `m_netRoutedCount++` 的条件 = `anyMissing == false` ✓ | `utils/graphutils.cpp:603` ✓ |
| 建边只有四种 ✓ | 同上 ✓：①**跨层同脚** ✓ ②**Symbol 互连** ✓ ③**同一 `bus()`** ✓（`connectoritem.cpp:1091` ⇒ 只认**零件自己 `.fzp` 的 `<buses>`** ✗，跨零件无效 ✗）④**同 `wireFlags` 的线链** ✓ —— 而线链是顺着 **`<connect>` **结点**走的** ✓（`Wire::collectChained` ✓），**不是按几何** ✗ |

### ③ 判决 ✓：拿**已被用户验收过的 v69** 当对照（同一把尺子 ✓）

| 文件 | `pcb_check` ⑤ | 关键数字 |
|---|---|---|
| **`pixel-pcb-v69.fzz`**（用户验收过 ✓） | **问题 0 条** ✓ | `GND` 9 脚 **一块铜** ✓、`RC` 3 脚 **一块铜** ✓、走线 95 ✓、过孔 16 ✓ |
| `pixel-pcb-v70.fzz`（我本轮出的 ✗） | **问题 2 条** ✗ | `RC` 三只脚**一条线都没有** ✗、`C1.connector1`（`GND`）也**一条线都没有** ✗ |

⇒ **我的 ⑤ 没坏** ✓（它对 v69 判"全通" ✓、对 v70 判"断" ✓，与驱动自己的日志**也一致** ✓：
`gen_routes` 当时就报了「`GND` 有 1 段、`RC` 有 2 段没连上」✗）。

### ④ ★★ 真相 ✓：**幽灵连接**（文件里的旧声明 ✗）

Fritzing 的连通图是顺着 **`<connect>` 声明链**走的 ✓ ⇒ 而写回器**沿用了 v69 里的旧 `<connect>`** ✗
（日志里那句「回指：补写 36 处 ✓」✓），却写了一份**不一样、且不完整**的线 ✗
⇒ **声明说连着 ✓、铜不在那儿 ✗** ⇒ **Fritzing 被骗过了** ✗✗。

★★ **这是本轮最值钱的一课** ✓（加进 §13 的账 ✓）：
**「Fritzing 说完成」不等于「铜真的连上」** ✗ ——
**当文件是「我们自己改写」出来的时候**，必须再拿**几何**核一遍 ✓（尤其查 `<connect>` 有没有**旧声明残留** ✗）。
✗ 光信状态栏 ⇒ 会**高高兴兴把一片断线的板送去做** ✗（而这正是用户**唯一**能做的验收 ✗ ⇒ 我更要把这一层守住 ✓）。

★ **闸门待补** ✓：`pcb_check` ⑩ 当时报「声明 204 条全合格 ✓」✗ 却**没抓到幽灵** ✗
⇒ **它有洞** ✗（待查：多半是"只核了它能配成对的那部分声明" ✗）。

### ⑤ 处置 ✓

- **撤回 `pixel-pcb-v70.fzz`** ✗（已 `git rm` ✓）—— 它是**不完整**的 ✗，留在仓里会误用 ✗；
- **交付仍是 `pixel-pcb-v69.fzz`** ✓ —— 同一把尺子下**它就是全通的** ✓（0 问题 ✓），
  而且它本来就有**用户手工改过的**那两处 ✓；
- 如实记 ✓：**自动布线单独跑仍是 7/9** ✗（还差 3 条连接 ✗）；
  **整块板能全通，靠的是 v69 里用户那两步手工** ✓。

**四十三、第二十六轮（2026-10-06 ✓）：把「幽灵连接」补强成**机器闸门** ✓ ＋ 记入**候补 PR** ✓

### ① 补强 ✓（`gen_routes.py`：独立复核从**选做**改成**每次必跑** ✗✓）

✗ 上次的漏洞不在判据（`pcb_check` ⑤ 抓到了 ✓），而在**流程** ✗：
那一层「重新读刚写的文件、用几何核一遍」本来就有 ✓，却挂在 `--check` 底下（选做 ✗）
⇒ 我出 v70 时**没加** ✗ ⇒ 报告里的数字**全来自布线器自己的模型** ✗ ⇒ 幽灵连接溜过去了 ✓。

✓ 现在：**每次写完都跑** ✓，并多印两句 ✓：

```
== 独立复核（**重新读刚写的文件** ✓｜几何判据 ✓）==
   ✗ ⑤ 网 `GND` **没连通**：9 个脚散在 2 块铜里 ✗
   ✗ ⑤ 网 `RC` **没连通**：3 个脚散在 3 块铜里 ✗

   ⚠ **这份文件不是全通** ✗：9 张网里有 2 张断着 ✗
      ⚠ 而 **Fritzing 状态栏很可能照样显示「布线完成」** ✗ —— 它顺着文件里的
        `<connect>` 声明走 ✓（`graphutils.cpp` ✓）；**旧声明**会让它误判 ✗
      ⇒ **别信状态栏，信这一行** ✓（§13：文件是我们生成的，就必须用几何再核 ✓）
   ⇒ **有 2 处问题 ✗**（走线/过孔几何 ✓）        ← 退出码 **1** ✓（不静默 ✓）
```

★ 这一条**当时就能拦住 v70** ✓（实测：同一条命令，现在自己就把"2 张网断着"喊出来 ✓）。

### ② 记账 ✓：`fritzing-parts-langhua/docs/pr-candidates.md` ✓（**候补 PR** ✓）

先立了**格式** ✓（现象 ✓／重现 ✓／源码出处 ✓／建议 ✓／状态 ✓：`候补`→`待审`→`已提交` ✓）
—— ✗ 不急着开半成品 PR ✗（"半成品 PR 比没有更贵" ✓）。**P1** ✓ 记的就是本轮这条 ✓：
「**Fritzing 说布线完成可能是假的** ✓」（含 `mainwindow.cpp:2288` ✓、
`graphutils.cpp:603/443-560` ✓、`connectoritem.cpp:1091` ✓ 四处出处 ✓ ＋ 一条可照做的验收命令 ✓）。

★ 同一份账里还**点名了 `pcb_check` ⑩ 自己的洞** ✗（待补 ✓）：
它只遍历**走线**上声明的连接 ✗（`for i, t in enumerate(traces)` ✓）
⇒ **线根本不存在时它无从可查** ✗。候选补法已写清 ✓：
遍历**文件里全部 `<connect>`**（含**焊盘实例**上的 ✓），
并对"指向**不存在的 modelIndex** 的声明"也报出来 ✓（那正是幽灵的形态 ✓）。

### ③ 交付 ✓（不变 ✓）

**`pixel-pcb-v69.fzz`** ✓ —— 几何核对 **0 问题** ✓（`GND` 9 脚一块铜 ✓、`RC` 3 脚一块铜 ✓）；
`pixel-pcb-v70.fzz` 已**撤回** ✗（本轮补强的闸门就是为它这一类准备的 ✓）。

**四十四、第二十七轮（2026-10-06 ✓）：补上 ⑫「悬空声明」✓ ＋ 回答「锁位解开是不是更有戏」✓**

### ① 「做 1」✓：`pcb_check` 新增 **⑫ 悬空声明** ✓（一击命中 ✓）

✗ ⑩ 的洞 ✓：它只遍历**走线**上声明的连接 ✗（`for i, t in enumerate(traces)` ✓）
⇒ **线根本不存在时它无从可查** ✗。✓ ⑫ **不看几何** ✗，只问一句 ✓：
**文件里每条 `<connect … modelIndex="…"/>` 指的对象，还在不在** ✓？

| 文件 | ⑫ | 判定 |
|---|---|---|
| **`pixel-pcb-v69.fzz`** ✓ | **悬空声明 0 条** ✓ | ✓ 全过 |
| `v70`（已撕 ✗） | **悬空声明 100 条** ✗ | ✗ 有问题（＋⑤ 两条 ✓） |

⇒ **幽灵的形状查实了** ✓✓：写回器把**上一版内部文件**里那批**旧实例 id 的 `<connect>` 声明**
原样留下了 ✗（204 条声明里 **100 条**指向的对象**早已不在文件里** ✗）。
Fritzing 顺着声明走 ✓ ⇒ 「布线完成」✓。⇒ ⑫ 就是这条病的**机器守** ✓。
★ 分工说清 ✓：**⑩ = 声明的几何兼不兼现** ✓；**⑫ = 声明指的东西还存不存在** ✓。

### ② 用户问 ✓：「v69 里有些元件锁住位置 ✓，解开是不是有更多移动空间 ✓、能带来全接通 ✓？」

**量清楚了两件事** ✓（`_work/locks.py` ✓）：

1. **锁在哪** ✓：`locked="true"` **挂在 `<pcbView>` 上** ✓（不是 `<instance>` ✗）——
   共 **8 件**：`L1`（线圈 ✓）、`C2`、`LED2`、`D3`、`J1`、`J2`、`H1`/`H2`（安装孔 ✓）。
   ★ **没锁的恰好是 `U1`/`C1`/`R1`** ✓ —— 就是 `RC` 那三只脚所在的件 ✓（你调它们时解的锁 ✓）。
2. **锁不影响布线器** ✓：把本仓工具全扫了一遍 ✓ —— **没有任何一处读 Fritzing 的 `locked`** ✗
   （`--no-lock` 是"钉住 `5V` 先布" ✓、`blocked` 是障碍 ✓，两码事 ✓）。

⇒ **"解锁"本身不带来空间** ✗（它只是人手上的防误动 ✓）；
**带来空间的是真的把件挪动** ✓ —— 而那正是**唯一还没系统试过**的自由度 ✓
（此前只手工试过 10 个位置 ✗ ⇒ 最好 8/9 ✗、且输家搬家 ✗）。

### ③ 于是**直接量** ✓：有界摆位搜索 ✓（`_work/place_search.py` ✓）

★ 候选件**有依据** ✓（不是拍脑袋 ✗）：`H1`/`H2` 机械件不动 ✗；`L1` = **传感线圈** ⇒
挪它等于改传感器 ✗；`J1`/`J2` = 对插接插件 ⇒ 有机械意义 ✗；剩下**电子件**才可挪 ✓。
★ 判据与交付**同一把尺子** ✓：`(-还差几条连接, 连通网数)` ✓（**差 0 条 ⟺ 全通** ✓）。
★ **一次一改** ✓：每轮只挪一件 ✓、每步独立评估 ✓、只留更好的 ✓。

**首轮（`U1`/`C1`/`R1` ✓，步长 1 mm ✓）已经出信号** ✓：

| 挪法 | 还差 | 未通 |
|---|---|---|
| 基线（不挪） | **3** 条 ✗ | `GND`、`RC` |
| `U1 +0 -1` ✓ | **2** 条** ✓ | `GND`、`RC` |
| `U1 -2 0` ✓ | **2** 条** ✓ | `BR+`、`RC` |

⇒ **用户的直觉成立** ✓：**挪动确实能把"离全通多远"往下压** ✓（本轮 3 → 2 ✓）。
⇒ 下一步（待跑完/下一轮）✓：把"只挪一件"换成**贪心套挪**（接受 `U1 -1` 后，
再在里面继续扫 ✓），并把**电子件**全纳入 ✓ —— 目标是 **差 0 条** ✓。

其余"手"的编号继续往后排 ✓（本手 = 第四十九手 ✓）。

**四十五、第二十八轮（2026-10-06 ✓）：挪位搜索出结果 ✓ ⇒ 交付版 `7/9` → **`8/9`（还差 1 条连接）** ✓｜四族同一天花板 ✓｜尺子钉成一份实现 ✓**

### ① 先记我自己犯的一个错 ✗（本轮最值钱的一条 ✓）

流程 ✓：贪心挪位搜索（`_work/place_greedy.py` ✓）报 `D3 +0 -1 ⇒ 8/9、还差 2 条` ✓；
我按**独立复核**的规矩去核 ✗ —— 但用了**默认开关**跑驱动器 ⇒ 得 `4/9、还差 7` ✗
⇒ 我立刻报"**这是假改进、搜索脚本又拿了一把尺子**" ✗✗。

**两分钟后就翻案了** ✓：换成**交付那把开关**（`--no-lock --first= --escape-cost=0.3
--no-mid-keep --blockers=16 --passes=8 --layer-pen=0.35` ✓）复核 ⇒

```
MEASURE ok=8 nets=9 miss=2 len_mm=277.7 vias=11 bad=RC
```

—— 与搜索脚本**一字不差** ✓（两边**本来就同口径** ✓，是**碰巧一致** ✗）。

★ 真相 ✓：尺子不是「驱动器 vs 我」 ✗，而是「**哪一套开关**」 ✗ ——
默认开关带 `[留走廊]`（先钉 `5V` ✓）＋ `first=power` ＋ `mid_keep` ✓，
而**交付那把**三个全关 ✓ ⇒ 同一份文件能得 `4/9` 也能得 `8/9` ✗✗。
⇒ 处置：**尺子只许一份实现** ✓（仓规 §13 ✓）——
`gen_routes.py` 新增 **`--measure-only`** ✓（**只量不写** ✓，打一行机读结论 ✓）；
新工具 **`tools/measure.py`** ✓（把**交付那把开关写死**在里面 ✓，是**唯一**的量入口 ✓）。

★ 对照 ✓（用它复现交付那版 ✓）：底图在交付开关下 **`7/9｜差 3｜282.8 mm`** ✓
—— 与第二十四轮记录**逐项相同** ✓（过孔 `9 → 8` ✓ 正是后来**去重**修掉的 ✓）。

### ② 四族都试完 ⇒ 天花板 = **`8/9`（还差 1 条连接）** ✓

| 族 | 范围 | 最好 |
|---|---|---|
| 平移（1–2 mm 粗格 ✓） | 2 轮 × 52 候选 | **差 1** ✓ |
| 平移（**0.25/0.5 mm 细格** ✓） | 2 轮 × 32 候选 | **差 1** ✓（280.8 mm ✓） |
| **翻面** ✓ | 每件 | **全被 ⑧ 否** ✗ |
| 次序（`--first/--last` ✓） | 8 组 × 2 个摆位 | **无一优于原样** ✗ |
| 路由器参数（格/孔/层罚/脚距 ✓） | 11 档 | 无一到 0 ✗ |

**采纳链** ✓（每一步都用 `tools/measure.py` 量 ✓）：
`3 → 2`（`D3 +0 -1` ✓）→ `1`（`R1 +0 +2` ✓）→ `1`（`R1 -2 +0` ✓）→ `1`（`C1 +0 -1` ✓）
→ `1`（`D3 +0.25 +0` ✓）→ **`1`（`U1 +0.25 +0` ✓｜280.8 mm ✓｜过孔 11 ✓｜未通 `RC`）**
⇒ 当前最好 = `_work/_pd_r2_U1_p0_250_p0.fzz` ✓ ⇒ **`8/9`、只差 1 条连接** ✓
（= Fritzing 会显示「**8 of 9 nets routed — 1 connector still to be routed**」✓）。

★★ **"四族同一个天花板"本身就是结论** ✓：现拓扑（`U1/R1/C1/D3` 位置 ＋ 线圈/对插件不动 ✗）
下，这套布线器的上限 = `8/9` ✓。而 `RC` 那最后一条**不是物理不可能** ✓ ——
`--first=RC` 时**它通** ✓、只是把 `5V/DATA_IN/DATA_OUT/GND` 四张网饿死 ✗
⇒ **它是"排在后面就没容身之处"** ✓ ⇒ 杠杆在**布局**，不在算法 ✗。

### ③ 翻面（用户问的那条 ✓）：**不是"没选项"** ✗，是**被线圈挡死** ✗

`U1/R1/D3 翻面` 全报 **⑧ 元件间隔不足** ✗，对方都是 **`L1`（线圈 ✓）**：
`U1 −0.200`（**压上了** ✗）、`R1 +0.020`、`D3 +0.076`（都 **< 0.25 mm** ✗）。
理由 ✓：`L1` 是**两面都有铜**的大线圈 ✓（21.6 × 22.05 mm，板才 25 × 25 ✓）
⇒ 翻到背面就贴着它 ✗。（`C1` 能待在背面 ✓，是因为它在线圈铜皮**之外** ✓。）
★ 实现上也确认了 ✓：`pcb_pads.py` 对背面件**铜层对调 ＋ x 镜像** ✓（口径正确 ✓）⇒ **不是模型错** ✗。

### ④ 工具提升 ✓（`_work/` 是 gitignore 的草稿区 ✗ ⇒ 有用的工具不能烂在那儿 ✗）

`_work/` 里那 5 个脚本 ✓ —— 我把**输出/底图/日志**仍留在 `_work/` ✓、
代码提升到 **`hardware/pixel/tools/`** ✓（`_work/_promote.py` ✓ 逐条打印改了哪几处 ✓）：
`beep.py` ✓ / `measure.py` ✓ / `place_drv.py` ✓ / `place_greedy.py` ✓ / `nudge_sweep2.py` ✓。
★ 提升后**当场复验** ✓：`tools/measure.py <当前最好>` ⇒ `ok=8 miss=1` ✓（逐项相同 ✓）。

### ⑤ 用户新要的：**长跑脚本收工响一声** ✓

`tools/beep.py` ✓（Windows 自带 `winsound` ✓，不装包 ✓）：**成功上行三声** ✓ /
**失败下行两声** ✓；已接在 `place_drv.py` / `measure.py` / `place_greedy.py` ✓，
**崩了也响** ✓。✗ **特意不加**在 `gen_routes.py` ✗ —— 它被搜索脚本**调几百次** ✗。

### ⑥ 下一轮（用户 2026-10-06 定 ✓）

**加旋转（步长 15° ✓ —— 90° 太粗 ✗）＋ 加双件联挪** ✓，**慢慢试** ✓。

**四十六、第二十九轮（2026-10-06 ✓）：旋转（15° 步长 ✓）＋ 双件联挪 ✓ 都做出来了 ⇒ **六族总账：天花板仍是 `8/9`（差 1 条连接）** ✗｜并抓到我自己一个**真 bug** ✗**

### ① 旋转 ✓（步长 15° ✓，用户点名"90° 太粗"✗）

新增 **`tools/mutate.py`** ✓（旋转 ✓ / 联挪 ✓）—— 关键口径：

- **旋转中心 = 该件全部焊盘的"重心"** ✓（从 `pcb_check.collect` 的**板坐标**算 ✓）。
  ✗ 绕"板原点"转会把件甩到板外 ✗；绕"元件框中心"又要另算包围盒 ✗。
- 数学 ✓（`loc` = `<geometry x/y>` ✓、`M` = 它里面的 `<transform>` ✓、板点 `p = loc + M·u` ✓）：
  要 `p' = c + R·(p − c)` ⇒ **`M' = R·M`** ✓、**`loc' = c + R·(loc − c)`** ✓。
- 矩阵数学**复用库** ✓（`part_box` 的 6 元组 SVG 约定 ✓）；`.fz` 里的 `<transform>` 是
  **属性写法** ✓ ⇒ 读它照 `pcb_pads.tf_of` 的**同一口径** ✓（缺省 = 单位阵 ✓）。★ **不另写一份** ✗。

★★ **旋转先用"数值真值"验过** ✓（仓规 §5b ⑨ ⑨：几何公式要拿真值对一遍 ✗，不能只看"能跑" ✓）：

| 判据 | 结果 |
|---|---|
| 转 **360°** ⇒ 与原件逐焊盘同位 ✓ | **0.0000 mm** ✓ |
| 转 **90° 再 −90°** ⇒ 回原位 ✓ | **0.0000 mm** ✓ |
| 转 **180°** ⇒ **重心不动** ✓ ＋ 两盘**精确互换** ✓ | **0.0000 mm** ✓ |

### ② ★★ 冒烟测抓到一个**真 bug** ✗✗（先跑小的 = 值 ✓）

```python
if best is None or key(r) < key(best[3]):     # ✗ best 一开始是 None
```

⇒ **第一个候选无条件当"最好"** ✗ ⇒ **一整轮全都更差时，它照样"采纳"第一个** ✗✗
（实测：转 `C1` 那一轮"采纳"了 `转180 ⇒ 差 2` ✗，比原样 `差 1` 还差 ✗）。
★ 第二十八轮那几轮**没被坑到** ✓ 只是因为**第一个候选恰好打平** ✗ —— 那是**运气**，不是对 ✓。
⇒ 修法 ✓：**必须同时**比当前状态（`r_cur`）✓ 与已找到的最好 ✓；同一冒烟测**复验** ✓
⇒ 三个旋转**全被正确否掉** ✓。

### ③ 双件联挪 ✓（**同向** ＋ **反向** ✓）

反向 = "一把向外、一把向内" ✓ = 给中间腾地方的典型手法 ✓。
`R1+C1/U1/D3` 取对 ✓ × 4 个单格轴偏移 × 2 种方向 = **48 个候选/轮** ✓。

### ④ ★ 六族总账 ✓：**天花板一律 = `8/9`（差 1 条连接）** ✗

| 族 | 范围 | 最好 |
|---|---|---|
| 平移（1–2 mm 粗格 ✓） | 2 轮 × 52 | 差 1 ✓ |
| 平移（0.25/0.5 mm 细格 ✓） | 2 轮 × 32 | 差 1 ✓ |
| 翻面 ✓ | 每件 | **全被 ⑧ 否** ✗（贴线圈 ✓） |
| 次序（`--first/--last` ✓） | 8 组 × 2 摆位 | 无一优于原样 ✗ |
| 路由器参数 ✓ | 11 档 | 无一到 0 ✗ |
| **旋转（15° ✓）** | **92 个候选/轮** | 差 1 ✓（只有"略短" ✓） |
| **双件联挪 ✓** | **48 个候选/轮** | 差 1 ✓（只有"略短" ✓） |

**当前最好** ✓：`_work/_pd_r2_R1pC1_m1_p0_反向.fzz` ⇒
**`8/9`｜差 1 条 ✓｜279.3 mm ✓｜过孔 11 ✓｜未通 `RC`** ✓
（= Fritzing 会显示「8 of 9 nets routed — 1 connector still to be routed」✓）。

### ⑤ 顺带：任务终端**只回 stdout** ✗ ⇒ Python 的 traceback 会被**整段吞掉** ✗

实测 ✓：冒烟测退出码 1、任务输出里**一行报错都没有** ✗。
⇒ 新增 **`_work/_run.py`** ✓：把子进程的 **stderr 并进 stdout** ✓ 再打出来 ✓（以后调试都走它 ✓）。

### ⑥ 下一步（待用户点头 ✗）

**唯一还没动过的自由度** = `L1`（传感线圈 ✓，两面都有铜、几乎盖满板 ✓）与
`J1`/`J2`（对插接插件 ✓）—— 那是**产品决定** ✗，不由我自定 ✓。
另外还有一档**不必动布局**的：布线器更细的旋钮（`--cell` 更细 ✓、`--escape-r` ✓）✓。

**四十七、第三十轮（2026-10-06 ✓）：用户选 ① ⇒ **修掉幽灵写回** ✓ ⇒ 出交付件 **`pixel-pcb-v71.fzz`** ✓（**`8/9`｜差 1** ✓，⑫ = 0 ✓）**

### ① 第八族也没到 0 ✗（先把账结清 ✓）

**不动布局**的更细旋钮 11 档 ✓ ⇒ 最好仍是 `差 1` ✓（`--layer-pen=0.1` 略短 ✓ 278.3 mm ✓）。
⇒ 至此 **八族**全部到顶 ✓：平移粗/细 ✓、翻面 ✓、次序 ✓、参数 ✓、旋转 15° ✓、联挪 ✓、更细旋钮 ✓。

### ② 幽灵的**根因查实** ✓（`docs/pr-candidates.md` 的 P1 ✓）

用 `_work/_inspect_connects.py` ✓（**自己的正则** ✓，不看几何 ✓）数底图 `_work/v69_bare.fzz` ✓：

| 项 | 数 |
|---|---|
| `<connect …>` | **430** 条 ✓（**全自闭合** ✓、带子元素 **0** ✓） |
| `<instance modelIndex=…>` | **109** 个 ✓ |
| **悬空声明** ✗ | **100** 条 ✓（挂在 `L1.connector0` / `connector1` 的 `<connects>` 里 ✓） |

⇒ 形状明白了 ✓：**剥线脚本把走线的"实例"删了 ✗，却把它们在焊盘 `<connects>` 里留下的
`<connect>` 声明留着** ✗（layer 还写着 `breadboardWire` / `copper0trace` ✓ —— 铁证 ✓）。
Fritzing 顺着声明走 ✓ ⇒ 显示「布线完成」✗，而铜并不在 ✗✗。

### ③ 修法 ✓：**写回器出文件那一刻清掉** ✓（`gen_routes.prune_dangling()` ✓）

- 位置 ✓：`write()` 里 **`add_backrefs` 之后** ✗（✗ 排前面会把自己刚补的回指也删掉 ✗）。
- 判据 ✓：`<connect modelIndex="…">` 指的对象**不在** `<instance modelIndex>` 集合里 ⇒ 删 ✓。
- ★★ **划界（最要紧 ✗）**：只删「**实例根本不存在**」那一类 ✗；
  ✗ **绝不碰**「实例在、只是它的 pcbView 里没这个 connector」那一类 ✗ ——
  仓里量过：那类在 **Fritzing 自己的样例里就有 108 处** ✓、**合法** ✓。
- 写法异常的（非自闭合 ✗）⇒ **不碰** ✗、只报数字 ✓（免得把没见过的形态切坏 ✗）。

### ④ 交付件 ✓：`pixel-pcb-v71.fzz`（**8/9，差 1 条连接** ✓）

出图命令（**逐项可复现** ✓，起点 = 第二十九轮那份最好的摆位 ✓）：

```
gen_routes.py _work/_pd_r2_R1pC1_m1_p0_反向.fzz pixel-pcb-v71.fzz --nets=pixel_nets.py \
  --mil=8 --no-lock --first= --escape-cost=0.3 --no-mid-keep --blockers=16 --passes=8 \
  --layer-pen=0.35 --deliver
```

| 项 | 数 |
|---|---|
| 连通 | **`8/9`** ✓｜**差 1 条连接** ✓（未通 `RC` ✓：3 个脚散在 2 块铜里 ✗） |
| 走线 / 过孔 | **111 条** ✓ / **11 个** ✓｜悬空端点 **0** ✓ |
| **清掉悬空声明** ✓ | **100 条** ✓ ⇒ ⑫ = **0 条** ✓ |
| ⑩ 声明逐条核对 | **222 条** ✓｜不合格 **0** ✓ |
| `pcb_check`（结构 ①–④⑥） | **✓ 全过** ✓ |

★★ **⑫ = 0 是"另一个实现"独立量的** ✓（不许自证 ✓）：`_work/_inspect_connects.py` ✓
（自己的正则 ✓）在**写出的文件**上数 ⇒ `<connect>` **696** 条 ✓ / 实例 **231** 个 ✓ /
**悬空 0 条** ✓。

★ 顺手把那句**过时警告**改准 ✓：以前在"没全通"时一律说"Fritzing 大概率还是会显示布线完成" ✗
—— 那是 **v70 当时**的情形 ✗。现在按 **⑫ 是不是 0** 分开说 ✓：⑫ = 0 ⇒ **它那句应当是诚实的** ✓
（`8 of 9 … 1 connector` ✓）。

### ⑤ ★ 请用户做**我做不到的那一步** ✓

把 `pixel-pcb-v71.fzz` 拖进 Fritzing ✓，看**草图底部**那句：应当显示
**「8 张网中的 8 … 1 个连接件」**（= `8 of 9 nets routed - 1 connector still to be routed` ✓）。
★ 这是**我这边所有闸门都替代不了**的验收 ✓（§13 ✓、`AGENTS §10` 第 8 步 ✓）——
我的闸门都是**间接**判的 ✓（读文件、算几何 ✓），而它那句话才是**同源同语义**的 ✓。

**四十八、第三十一轮（2026-10-06 ✓）：用户报「v71 还是显示布线完成」✗ ⇒ 查出**真机制** ✗ ⇒ **上一轮的"幽灵"解释作废** ✗ ⇒ 修法换成"**补网成员声明**" ✓ ⇒ `pixel-pcb-v72.fzz`**

### ① ★★ 勘误 ✓：我上一轮的解释**不完整** ✗（用户一次开图就打掉了它 ✗）

上一轮我把病因写成「**悬空声明骗了 Fritzing** ✗」，可 v71 的 ⑫ 已经是 **0 条** ✓，
用户一开图**还是**「布线完成」✗ ⇒ **解释作废** ✗。

### ② 读源码 ✓ 找到真机制 ✗（不许猜 ✗）

- `sketchwidget.cpp:6985-7049` ✓：一张网的脚列表 = 拿**每个 `ConnectorItem` 当种子** ✓ →
  `ConnectorItem::collectEqualPotential(…, RatsnestFlag)` ✓ → `collectParts(…)` ✓ → `scoreOneNet(…)` ✓。
- `graphutils.cpp:502` ✓：**`if (!gotUserConnection) return false;`** ——
  ⇒ **只有一只脚的"网"根本不被计进 `m_netCount`** ✗✗。
- `mainwindow.cpp:2288` ✓：「布线完成」⟺ `m_netCount == m_netRoutedCount` ✓。

### ③ 用它一量就全通了 ✓（`_work/_cmp_nets.py` ✓ 逐视图数声明 ✓）

| 脚 | **v69**（用户看到 **7/9** ✓） | **v71**（用户看到**布线完成** ✗） |
|---|---|---|
| `R1.connector1` | pcbView **2** ✓ | pcbView **1** ✗ |
| `C1.connector0` | pcbView **1** ✓ | pcbView **1** ✗ |
| `U1.connector1` | pcbView **1** ✓ | **pcbView 0 条** ✗✗ |

⇒ **`U1.connector1` 在 PCB 视图里 0 条声明** ✗ ⇒ Fritzing **不把它算进 `RC` 这张网** ✗
⇒ 它眼里 `RC` 只剩 `{R1.connector1, C1.connector0}` ✗ —— 而这两个**有走线连着** ✓
⇒ `anyMissing = false` ⇒ **它判 RC「已完成」** ✗✓。

★★ 所以 **v70 与 v71 是同一个病** ✓，而**不是**"幽灵声明"✗：
**声明 = 这张网的成员名单** ✓（Fritzing 就是这么用的 ✓ —— 用户那份 v69 正是这形状 ✓），
**连通 = 铜的链** ✓。**缺了前者 ⇒ 状态栏就骗人** ✗。

### ④ 修法 ✓：`fill_net_decls()`（写回前给**每只脚**挂上声明 ✓，哪怕它那一段没布通 ✗）

- **不编造** ✗：对每张网取一条**已有的**回指当**样板** ✓，**克隆**给同网里缺声明的脚 ✓
  （源端 `connectorId/modelIndex/layer` **照抄真的** ✓；目标的 `mi/cid/lay` 用那只脚**自己的** ✓）。
- 并入 `edits` ✓ 后走 `add_backrefs` **同一条写入路径** ✓（同样幂等 ✓、✗ 不动任何已有声明 ✗）。
- ★ 踩过的坑 ✓：第一版读的是 `RT.pad_index` 那份焊盘 ✗ —— **那份里没有 `mi`** ✗
  ⇒ 函数**静默返回空** ✗（日志里连"补网成员声明"那行都没出 ✗）⇒ 改读 `model["pads"]` ✓ 才对 ✓。

### ⑤ 交付件 ✓：`pixel-pcb-v72.fzz`（**8/9，差 1 条连接** ✓）｜v71 **撤回** ✗

| 项 | 数 |
|---|---|
| 连通 | **8/9** ✓｜差 1 条 ✓（未通 `RC` ✓）｜走线 111 ✓ / 过孔 11 ✓｜悬空端点 0 ✓ |
| **补网成员声明** ✓ | **1 条** ✓（正是 `U1.connector1` ✓）⇒ 回指 40 → **41** 处 ✓ |
| 清掉悬空声明 ✓ | 100 条 ✓ ⇒ ⑫ = **0** ✓｜⑩ 222 条 0 不合格 ✓ |
| 形状对照 ✓ | v72 的 `RC` 三只脚**各有 1 条 pcbView 声明** ✓ = **v69 同形** ✓ |

⇒ `pixel-pcb-v71.fzz` **撤回** ✗（它虽然 ⑫ = 0 ✓，但状态栏仍会说「布线完成」✗ ⇒ 会误导 ✗）。
⇒ 请用户开 **v72** ✓ 看底部那句 ✓。

**四十九、第三十二轮（2026-10-06 ✓）：用户报「v72 仍是布线完成」✗ ⇒ **真病在底图** ✗ ⇒ 换"只剥 `<pcbView>`"的底图 ✓ ⇒ `pixel-pcb-v74.fzz`**

### ① 三张表一比 ✓，病根立刻现形 ✗（`_work/_cmp_nets.py` ✓ 逐视图数 ✓）

| 脚 | **`v69_bare.fzz`（老底图）** | **v69**（用户看到 **7/9** ✓） |
|---|---|---|
| `R1.connector1` | 面包板 **3** ✓｜原理图 **4** ✓｜PCB 2 ✓ —— **全部悬空** ✗ | 同样条数、**一条不悬空** ✓ |
| `U1.connector1` | 2 ✓｜2 ✓｜1 ✓ —— **全悬空** ✗ | 2 ✓｜2 ✓｜1 ✓ ✓ |

⇒ ★★ **老底图是"把走线整条删掉"换来的** ✗ ⇒ 面包板/原理图的走线**一起没了** ✗
⇒ 它们的声明**全成悬空** ✗ ⇒ **Fritzing 认不出 `RC` 是一张网** ✗ ⇒ 说「布线完成」✗✗。
★ 与我上一轮"补声明"的思路**方向相反** ✗：**声明不该补，该把被删掉的网结构还回来** ✓。

### ② 修法 ✓：`tools/strip_pcb_view.py`（**只剥走线/过孔的 `<pcbView>`** ✓）

- 口径照库里老规矩 ✓（`sch_strip_wires` 只剥 `<schematicView>` ✗ 不删实例 ✓）：
  **只删 `<pcbView>` 那一段** ✓ —— 实例本身、面包板/原理图**原样留着** ✓；
- ✗ 元件（焊盘在它的 `<pcbView>` 里 ✗）**一个字不碰** ✗；
- 走线/过孔在别处留下的声明**一律不动** ✗（实例还在 ⇒ **不再悬空** ✓）。
- ★ 实测：`v69` ⇒ 走线 **177** 条 ✓、过孔 **16** 颗 ✓、剥 **111** 个 pcbView ✓。

### ③ 摆位不能丢 ✗ ⇒ **搬数字**（不是重放 ✓）

摆位是在**老底图**上搜出来的 ✗ ⇒ 必须搬回来 ✓。
★ 先试了**重放采纳链** ✗ —— 差 **0.0796 mm** ✗（链里"联挪"那步漏了 ✓；判据守住 ✓ 没往下走 ✓）；
⇒ 换成 **`_work/_transplant_place.py`** ✓：只搬那 4 件的 `<geometry>`（含 `<transform>` ✓）＋ `titleGeometry`
✓，✗ **绝不**搬 `<connectors>` ✗（底图的网结构才是这一轮辛苦保住的东西 ✓）
⇒ 逐焊盘核到 **0.0000 mm** ✓（31 个焊盘 ✓），不为 0 就不写 ✓。

### ④ ★ 第一版剥线**漏了过孔** ✗ ⇒ v73 直接报废 ✗（15 处问题 ✗）

只剥走线 ✗ ⇒ v69 留下的 **16 颗过孔**还在 ✗ ⇒ 与新布的线撞成一团 ✗：
③ 孤立过孔 5 颗 ✗、⑪ 孔距 **0.038 mm** ✗、⑤ 五张网短接 ✗。⇒ 过孔**同样**只带 PCB 视图 ✓，一并剥 ✓。

### ⑤ 另外 ✓：`fill_net_decls` **默认关掉** ✗

有了真结构 ✓，那只没布通的脚**本来就有**声明 ✓ ⇒ 再"补"就是**伪造连接** ✗
（`<connect>` 一挂上，`Wire::collectedChained` 就会顺着链给它加边 ✗）⇒ 只在 `--fill-decls` 时才补 ✓。

### ⑥ 交付件 ✓：`pixel-pcb-v74.fzz`（**8/9，差 1 条连接** ✓）｜v72 **撤回** ✗

| 项 | 数 |
|---|---|
| 连通 ✓ | **8/9** ✓｜差 1 ✓（未通 `RC` ✓）｜走线 111 ✓ / 过孔 11 ✓｜悬空端点 0 ✓ |
| 结构 ✓ | **与 v69 逐视图一致** ✓（面包板 3/2/2 ✓、原理图 4/2/2 ✓） |
| 其余闸门 ✓ | ③⑥⑦⑪ **全过** ✓｜⑩ 222 条 0 不合格 ✓｜⑫ **0** ✓ |

⇒ 请用户开 **v74** ✓ 看底部那句 ✓。

**五十、第三十三轮（2026-10-06 ✓）：用户报「v74 仍是布线完成」✗ ⇒ 读出**Fritzing 模型的死角** ✗ ⇒ 真·幽灵找到 ✓｜`v74` 撤回 ✗**

### ① 连撞三次 ⇒ 说明前两次的解释都不对 ✗（v71 零声明 ✗、v72 一条 ✓、v74 跨视图结构完整 ✓ —— **都说完成** ✗）

### ② 读源码 ✓ 把"组网/加边"三个函数全读了 ✓（不再猜 ✗）

| 出处 ✓ | 事实 |
|---|---|
| `connectors/connectoritem.cpp:1340` `collectEqualPotential` ✓ | 组网**顺着声明**走 ✓（`connectedToItems()` ✓ ＋ 跨层孪生 ✓ ＋ bus ✓） |
| `connectors/connectoritem.cpp:1413` `collectParts` ✓ | **把 Wire 丢掉** ✗ ⇒ 一张网的脚 = 声明闭包里的**元件脚** ✓ |
| `utils/graphutils.cpp:447` `scoreOneNet` ✓ | 加边 = **声明 → `Wire::collectChained` 的链端** ✓ |

### ③ ★★ 结论 ✓：一只脚只有两种命运 ✗ —— **两条路都让状态栏说「布线完成」** ✗✗

1. **有声明** ✗（哪怕那声明指着"别人那片铜"✓）⇒ 它被并进那条链 ⇒ **判已连通** ✗
   —— **v74 就是这个** ✓：`U1.connector1`（那一段**没布通** ✗）的旧声明指着 `RC` 那片**已连通的**铜
   （底图 `v69` 的遗迹 ✓）⇒ 它被算作连上了 ✗。
2. **没声明** ✗ ⇒ 只有它自己 ⇒ `num_nodes == 1` ⇒ `gotUserConnection == false` ⇒
   **整张网被丢掉** ✗（`graphutils.cpp:502` ✓）⇒ 谁也扣不了分 ✗。

⇒ ⇒ **只要那只脚「一点铜都没有」，Fritzing 的状态栏就**结构性地无法诚实表达** ✗** ——
所有基于"改声明"的修法都在这两条路之间打转 ✗（我连撞三次 ✓ 就是这原因 ✓）。
★ 这也解释了 **v59 为什么能老实报「7 中的 5，2 个连接件」** ✓：那次没布通的脚**是带着铜的** ✓。

### ④ 已做的（**必要的一刀** ✓）：`reset_pcb_decls()` ✓ —— 旧 PCB 声明一律清掉 ✗

- 只清 `layer="copper0trace|copper1trace"` ✓（= 指向**旧走线**的那些 ✓）；
- **必须排在插入新 XML 之前** ✗（否则会把新走线自己的声明一起清掉 ✗）；
- **面包板/原理图的声明一条不动** ✗（那是网结构 ✓）；
- ⇒ 之后的 PCB 声明**只由写回器按本次 `res` 的真实段重建** ✓（`build_xml` ＋ `add_backrefs` ✓）。

### ⑤ 要它老实报 `8/9` ✗，只剩一条路 ✓：**给那只脚一小截"逃逸残段"** ✓

即：从 `U1.connector1` 往外走 **0.3–0.5 mm** 放一小段铜 ✓（让它**自己有铜** ✓ ⇒ 归路 1 ✓，
但那条链**只到它自己** ✗ ⇒ 如实判"缺" ✓）。
★ 这也是**手工补线的常规做法** ✓（留出逃逸段 ✓），且能让**鼠线（虚线）**画得对 ✓
—— 用户在 Fritzing 里手工收尾时，正需要那条虚线 ✓。
★ 代价说清 ✗：板子上会多出 `RC` 那片的一小截**死铜** ✓（电气上无害 ✓、视觉上多一小段 ✓）。

⇒ `pixel-pcb-v74.fzz` **撤回** ✗（它带着"伪装已连通"的旧声明 ✓、会误导 ✓）；等用户点头再出带残段的 v75 ✓。

**五十一、第三十四轮（2026-10-06 ✓）：用户点头 ⇒ 做**逃逸残段** ✓ ⇒ `pixel-pcb-v75.fzz`**

### ① 做法 ✓ `add_escape_stubs()`（写 `build_xml` **之前** ✓ 加进 `res` ✓ ⇒ 声明自动齐 ✓）

只对**没布通的网**的、**一段铜都没挨上的**脚动手 ✗（其余一个字不碰 ✗）：
候选 = 8 个方向 × 2 个长度 ✓；判据用驱动器**同一套**常量 ✓（`TRACE_MM` ✓ / `CLEAR_MM` ✓）。

### ② 三处**量出来才改**的地方 ✓（一次一改 ✓）

| 现象 ✓ | 量的结果 ✓ | 改法 ✓ |
|---|---|---|
| 残段 0 条 ✗ | 诊断：**否于别网焊盘 24** ✗（8×3 全否 ✗） | 我那句 `+ RT.U(0.5)` 是**凭空定的** ✗ ⇒ 换成 **线半宽＋净距＋焊盘半宽(0.10)** ✓ |
| 还是 0 条 ✗ | `U1` 是 **QFN 0.4 mm 脚距** ✓ ⇒ **这只脚连逃出去的缝都没有** ✗（正是"起点格空"的成因 ✓） | 长度改**极短** ✓（0.15 / 0.05 mm ✓ = 让它"自己有铜"✓、不指望引出去 ✓）|
| 放进去了但**被写回器吃掉** ✗（走线仍 111 ✗） | 0.05 mm 段被归一化（合并/切边 ✓）吞掉 ✗ | 先试 **0.15** ✓ ⇒ 活了 ✓（**112** 条 ✓）|
| ✗ 也踩过 ✗ | `_seg_d(cx,cy,ex,ey, a2, b2)` 传了**元组** ✗ | 拆成 `a2[0], a2[1], …` ✓ |

### ③ `pixel-pcb-v75.fzz` ✓：`8/9`｜差 1 ✓｜**逃逸残段 1 条**（`U1.connector1` ✓）｜走线 **112** ✓｜过孔 11 ✓

- ★ `悬空端点` 从 0 变 **1** ✗ —— **这是要的** ✗：那正是残段的**外端** ✓（驱动器会单独点名它 ✓：
  `RC 线#111 端1 … 最近 pad U1.connector1 差 0.150 mm` ✓）；
- ⑩ 223 条声明 0 不合格 ✓｜⑫ **0** ✓｜旧 PCB 声明清掉 37 条 ✓（`reset_pcb_decls` ✓）；
- ⇒ 按源码推 ✓：`U1.connector1` 有声明 ✓ ⇒ 算进 `RC` ✓，而链**只到它自己** ✗ ⇒ **应当如实报 8/9** ✓。

**五十二、第三十五轮（2026-10-06 ✓）：用户给**对照件 v59**（它诚实 ✓）⇒ 一比就找到真差别 ✓ ⇒ 换源头出 `pixel-pcb-v76.fzz`**

### ① ★ 用户那张截图是**决定性的** ✓

v59 的状态栏写着「**7 中的 5 网络布线完成，2 个接插件仍然需要布线**」✓ ⇒
**"有铜但孤立的脚"这件事，Fritzing 是表达得出来的** ✗ —— 我上一轮"结构性地表达不了"的结论**作废** ✗。
（教训 ✓：**别急着下"做不到"的结论** ✗ —— 手边往往就有一个**能做**的对照件 ✓，先把它拿来比 ✓。）

### ② 把 Fritzing 的"声明闭包"建出来量 ✓（`_work/_net_group.py` ✓）

按源码 ✓ 建图（节点 = `(实例号, connectorId)` ✓ **跨视图同一个** ✓ ⇒ 这才有"面包板/原理图把网连起来"✓）、
再按 `collectParts` 口径**剔掉 Wire/过孔** ✗ ⇒ 剩下的就是 Fritzing 眼里的"网的脚" ✓：

| 脚 | **v59**（诚实 ✓） | **v75** ✗ | **v76** ✓（本轮） |
|---|---|---|---|
| `R1.connector1` | 同组元件脚 **3** ✓ | **2** ✗ | **3** ✓ |
| `C1.connector0` | **7** ✓ | **2** ✗ | **7** ✓ |
| `U1.connector1` | **3** ✓ | **2** ✗ | **3** ✓ |

⇒ ★★ **差别是"声明的丰富度"** ✗：v59 的面包板/原理图把这几只脚**与别的脚绑在一起** ✓
（所以 Fritzing 认得出"这是一张有 3 只脚的网"✓）；v75 每只脚**只剩"自己＋一个面包板孔"** ✗。
⇒ 根因 ✗：**我们的源头 `v69` 本身就是"剥瘦版"** ✗（不是这一轮剥的 ✗）。

### ③ 修法 ✓：**换源头** —— 用 **v59** 剥（只剥 `<pcbView>` ✓）

`tools/strip_pcb_view.py` ✓（v59 ⇒ 走线 254 条 ✓、过孔 18 颗 ✓、剥 186 个 ✓）
⇒ `_work/_transplant_place.py` 搬摆位 ✓（31 个焊盘核到 **0.0000 mm** ✓）⇒ 布线 ⇒ **`pixel-pcb-v76.fzz`** ✓。

| 项 | 数 |
|---|---|
| 连通 ✓ | **7/9** ✓（未通 `GND` + `RC` ✓）｜走线 115 ✓ / 过孔 9 ✓ |
| **结构** ✓ | ★ **与 v59 逐项相同** ✓（`3 / 7 / 3` ✓，连组里成员都一样 ✓） |
| 残段 ✓ | 2 条 ✓（`U1.connector1` ✓、`J1.connector1` ✓）⇒ 悬空端点 2 ✓（故意 ✓） |
| 闸门 ✓ | ⑩ 228 条 0 不合格 ✓｜⑫ **0** ✓｜清掉旧 PCB 声明 39 条 ✓ |

⇒ `pixel-pcb-v75.fzz` **撤回** ✗（它是"剥瘦源头"的产物 ✓，状态栏看不出真话 ✓）。
⇒ 请用户开 **v76** ✓。

### ④ ★★ 用户确认（截图 ✓）：**对齐成功** ✓✓

| 谁 ✓ | 那句话 ✓ |
|---|---|
| **Fritzing** ✓ | 「**7 中的 5 网络布线完成，2 个接插件仍然需要布线**」✓ |
| **我的几何核对（`⑤` ✓）** | `GND` 1 段没连 ＋ `RC` 1 段没连 = **2 条** ✓（其余 7 张全通 ✓） |

⇒ **两个声音说的是同一件事** ✓（Fritzing 数 7 张网 = 我的 9 张减去它不数的 2 张"单脚网" ✓；
「2 个接插件」= 我那 2 条连接 ✓）⇒ **`AGENTS §13` 要的"同源同语义"到手了** ✓✓。

★ 代价与教训 ✓：这一条是**撞了四次墙**换来的 ✗，四个错解依次是
①「幽灵声明」✗ → ②「网成员声明缺失」✗ → ③「Fritzing 结构上表达不了」✗ →
④ **真因：源头被剥瘦** ✗（`v69` 的面包板/原理图声明已残缺 ✓）。
⇒ **教训**（比结论值钱 ✓）：**下"做不到"的结论之前，先拿一个"做得到"的对照件来比** ✗ ——
用户随手截的 `v59` 一句话就把我三个小时的推断全推翻了 ✓。

★ **面包板不用换** ✓（用户 2026-10-06 问 ✓）：这一轮**只剥 `<pcbView>`** ✓（报告：剥 186 个 ✓、
**面包板/原理图原样** ✓）；但**它是"网的黏合剂"** ✓ —— **谁动了面包板（增删跳线 ✗、重新生成 ✗、
或者又拿它去"剥线"✗），PCB 那句状态栏会跟着变** ✓（同一张网表的两面 ✓，不是 bug ✓）。

### ⑤ ★★ 定稿 ✓（2026-10-07 用户定 ✓）：**接受 `v76` 交付** ✓

用户原话 ✓：「**接受**」✓ ⇒ 这一轮的结论就钉在这里 ✓（以后**不再重开摆位搜索** ✗）：

| 项 | 定稿 ✓ |
|---|---|
| 交付件 | **`pixel-pcb-v76.fzz`** ✓（`.fzz` 与渲染图都在仓里 ✓）|
| 连通 | **7/9** ✓ —— 未通 `GND` ＋ `RC` ✗（这是**本拓扑的上限** ✓，不是没搜到 ✗）|
| 结构 | 与诚实基线 **`v59` 逐项相同** ✓（`3 / 7 / 3` ✓）|
| 状态栏 | 与 Fritzing **同源同语义** ✓（「7 中的 5…2 个接插件…」✓）|

★ 平台期证据 ✓：**8 个家族全试过** ✓、差 **2** 一直下不去 ✓（`_work/_pd_log.txt` ✓）；
再要往下走只能改**结构**（封装选型 / 引脚分配 ✓）—— **不是**继续挪摆位 ✗。

★ 顺手补的两件工具 ✓（2026-10-07，详见 **§10** ✓）：`tools\run_detached.cmd` ✓
（长跑扔到 VS Code 之外跑 ✓，防 OOM 连带死亡 ✗）＋ `tools\render_revs.py` ✓
（**每一版渲成图片** ✓ ⇒  VS Code 里 Ctrl 多选两个 png ⇒ **比较选中的文件** ✓）。

**五十三、第三十六轮（2026-10-08 ✓）：加**电流约束** ✓（64 颗串联）⇒ 定「每 4 块一注入 ＋ 全板 8 mil」✓ ⇒ `POWER_SPEC` ＋ 独立核算器 `pcb_current.py` ✓｜✗ 没有改板 ✗（v76 定稿不动 ✓）**

### ① 约束（用户原话 ✓）

「差异幻灯片已经全部完成了，咱们继续做 Pixel PCB 自动布线吧？现在要加入约束条件，
就是要考虑支持 **64 个 Pixel 串联**的电流供给」✓

### ② 先把"卡在哪一头"量清楚 ✓（✗ 不是先猜线宽 ✗）

一颗 `WS2812B-1010` 全白最坏 **60 mA** ✓ ＋ 2 mA 杂项 ⇒ 一段的电流 = 段长 × 0.062 A；
`SH-1.0-3P-V` 官方额定 **1 A/触点** ✓ ⇒ **针**这一头：一段最多 **16 块** ✓（不是瓶颈 ✓）。
`pcb_current.py` 在**实板 `v69`**（段内 25 mm 板距 ✓）上量的**段压降**（＝ 5V ＋ GND **两程** ✓）：

| 一段 | 段电流 | 8 mil | 12 mil | 16 mil | 24 mil |
|---|---|---|---|---|---|
| 8 块 ✓ | 0.496 A | **9.8%** ✗ | 6.6% ✗ | 5.0% ✗ | **3.4%** ✓ |
| 6 块 ✓ | 0.372 A | 5.7% ✗ | **3.8%** ✓ | 2.9% ✓ | 2.0% ✓ |
| **4 块** ✓ | 0.248 A | **2.7%** ✓ | 1.8% ✓ | 1.4% ✓ | 0.9% ✓ |

载流哪一档都够 ✓（8 mil = 0.75 A ≥ 0.50 A ✓、温升 4 ℃ ✓）⇒ ★★ **定线宽的是压降** ✓。

### ③ 定案 ✓（用户 2026-10-08 选 ✓）

**每 4 块板一个注入点** ✓ ＋ **全板统一 8 mil** ✓ —— 唯一能同时满足
「全板一个宽度」✓（2026-10-01 定的 ✓）＋「段压降 ≤ 5%」✓ ＋「载流/针有余量」✓ 的组合 ✓。
⇒ 64 块 = **16 路注入** ✓、整机全白 ≈**4.0 A @5 V** ✓（电源与总线线径按这个核 ✓）。

### ④ 工具 ✓（库仓 ✓，两仓都不许自证 ✓）

| 工具 ✓ | 干什么 ✓ |
|---|---|
| `pixel_nets.POWER_SPEC` ✓ | 约束写成**一行数据** ✓（段长 / 每颗电流 / 铜厚 / 预算 / 针额定 ✓）⇒ 改分段只改它 ✓ |
| `pcb_current.py <板> --nets=pixel_nets.py` ✓ | **独立**三查 ✓：①载流（IPC-2221 外层 ✓）②段压降（梯形注入 ✓ 两程 ✓）③注入针 ✓；**声明↔几何**每跳复核 ✓；`--try-mil=` 同一路径换档重算 ✓ |
| `pick_mil()` ✓（`pcb_current` ✓） | 由规格**反推**最细够用的档 ✓ ⇒ `gen_routes.py` **缺省就用它** ✓（`--mil-power=` 仍可覆盖 ✓） |

★ 实测：`--seg-boards=4` ⇒ 反推 **8 mil** ✓ ⇒ 与信号档**同一个宽度** ✓（正好是用户要的"整张板一个宽度"✓）。

### ⑤ 对**定稿件 v76** 的核算 ✓（✗ 板没改 ✗、只把它量了一遍 ✓）

| 项 ✓ | v76 实测 ✓ |
|---|---|
| 走线 | 115 条 **全部 8 mil** ✓ ⇒ 与规格反推的档**本来就一致** ✓（⇒ 不用改板 ✓） |
| `5V` 段压降（4 块一段 ✓） | **1.5%** ✓（0.075 V ✓）｜最坏边 0.250 A vs 载流 0.75 A ⇒ **3.0 倍** ✓｜温升 0.8 ℃ ✓ |
| 注入针 | 0.248 A ≤ 1 A ✓（4 倍余量 ✓） |
| `GND` | ✗ **声明上走不到 9 个脚** ✓ —— 与 `pcb_check` ⑤「`GND` 没连通：9 个脚散在 2 块铜里」**独立对上** ✓✓ ⇒ 那是**既有断线** ✓（v76 定稿里那 2 条待手接之一 ✓），**不是电流不够** ✓ |
| 两网合计 | 按 `v69` 几何（两网都通 ✓）实测 **2.7%** ✓ ⇒ 4 块 ＋ 8 mil 的口径**过** ✓ |

★ 顺手验了个"电源两网全通"的实验件 ✓：拿旧裸板 `_work/v69_bare.fzz` 重布一版
⇒ `_work/v77_powerfull.fzz` ✓（`5V`＋`GND` **两网都通** ✓、8 mil ✓、4 块一段实测段压降 **3.68%** ✓ 全过 ✓）
—— 但它比 v76 多一张网没通 ✗（`BR+`/`COIL_A`/`RC` ✗ vs v76 只差 `GND`/`RC` ✗）⇒ **只留作参考 ✓**，
✗ 不替换定稿件 ✗。

### ⑥ 下一轮 ✓

v76 的**布线质量**（7/9 ⇒ 想再多通一张 ✓）—— 现在的净距口径是**合法**的 ✓
（8 mil ⇒ 中心距 0.45 mm ⇒ 铜净距 **0.247 mm** ✓ ≥ 仓规 0.20 ✓、≥ 嘉立创 0.127 ✓；
✗ 旧口径会落到 0.0968 mm ✗ = **低于嘉立创下限** ✗，v64 实测 33 处 ✓）
⇒ 再往上走只剩**改结构**（封装/引脚 ✓）或**手工补那 2 条** ✓，与 §五十二 的结论一致 ✓。

### ⑦ ★★ 用户 2026-10-08 报的件 ✓：`v77` 说「布线完成」✗、还**看不到哪里要手工布线** ✗ ⇒ 查出是"底图剥瘦" ✗ ⇒ 立闸门 ✓

**现象** ✓：Fritzing 打开 `_work/v77_powerfull.fzz` ⇒ 状态栏「**布线完成**」✗，
可几何上 `BR+`/`COIL_A`/`RC` 三张网是断的 ✗（`pcb_check` ⑤ ✓），而且**一条鼠线都不画** ✗
⇒ 用户没法手工补 ✗。

**真因** ✓（照 Fritzing 源码量 ✓，✗ 不是猜 ✗）：那张网的脚在文件里**没有"我跟谁同网"的声明** ✗
—— `connectoritem.cpp:1340 collectEqualPotential` 顺 `<connect>` 走 ✓，
`collectParts` 把 Wire/过孔剔掉 ✓ 后只剩"脚 ＋ 自己插的那个孔" ⇒ `graphutils.cpp:502`
`num_nodes == 1 ⇒ gotUserConnection = false` ⇒ ★ **整张网被丢掉** ✗ ⇒
既不算"待布线" ✗、也没有鼠线可画 ✗。

**新旧闸门 ✓**（`tools/net_group_check.py` ✓ —— 就是 §五十二 那把尺子的成品 ✓）：

| 文件 ✓ | 底图来源 ✓ | 闸门判词 ✓ |
|---|---|---|
| `pixel-pcb-v59.fzz` ✓ | 手改件 ✓ | ✓ 全过（只有 `U1.connector20` 是**单脚网**、本来就不显示 ✓）|
| `pixel-pcb-v76.fzz` ✓ | v59 剥 `<pcbView>` ✓ | ✓ 全过（同上 ✓）⇒ **状态栏诚实** ✓（用户截图 ✓）|
| `pixel-pcb-v69.fzz` ✗ | v57→v68 这一支 ✗ | ✗ **9 张网全部"每只脚都落单"** ✗ |
| `_work/v77_powerfull.fzz` ✗ | `_work/v69_bare.fzz` ✗ | ✗ 同上 ✗ ⇒ 状态栏谎报 ✗ |

⇒ ★★ **定论** ✓：**`v57→v68/v69` 这一支的底图剥得太瘦** ✗ ⇒ 拿它出的板子，
状态栏与鼠线**都不可信** ✗（跟 §五十二 的结论同一条 ✓）。交付前跑一遍闸门 ✓：

```
py -3.13 tools\net_group_check.py <板.fzz>        # 退出码 0 = 状态栏可信 ✓
```

**手工补线清单** ✓（`_work/net_groups.py` ✓ = 按几何算"哪只脚跟主群断开" ✓）：

| 板 ✓ | 网 ✓ | 孤块 ✓ | 接回主群 ✓（mm ✓ = 板内坐标 ✓）|
|---|---|---|---|
| **`v76`** ✓（诚实 ✓，**建议就补这份** ✓）| `GND` ✗ | `J1.connector1` (34.80, 8.52) | `D3.connector0` (41.58, 17.84) 等 GND 主群 ✓ |
| | `RC` ✗ | `U1.connector1` (48.18, 16.57) | `C1.connector0` (43.98, 18.42)／`R1.connector1` (46.36, 19.64) ✓ |
| `v77` ✗（电气合格 ✓，但状态栏说谎 ✗）| `COIL_A` ✗ | `L1.connector0` (43.73, 20.52) | `D3.connector5` (41.48, 16.02) ✓ |
| | `BR+` ✗ | `R1.connector0` (46.11, 19.92) | `D3.connector3` (40.18, 16.02) ✓ |
| | `RC` ✗ | `U1.connector1` (48.08, 16.57) | `C1.connector0` (43.90, 18.50)／`R1.connector1` (47.01, 19.92) ✓ |

★ 试过但**没走通**的一条路 ✗（记下来省得下次再试 ✗）：拿 `v76` 的"孔声明"往 `v77` 上搬 ✗
—— 部分脚能补成 `v59/v76` 的形状 ✓（`C1.connector0` 那块 2 ⇒ 7 ✓），但整张网补不齐 ✗
（`R1.connector1` / `U1.connector1` 还是 2 ✗）⇒ **声明手术救不了剥瘦底图** ✗，
与 §四十七～§五十二 连续四轮的教训同一条 ✓ ⇒ 正解仍是 **在富底图上布线** ✓（= `v76` 那一支 ✓）。

**五十四、第三十七轮（2026-10-09 ✓）：用户手改版 `_work/v76_byHand.fzz` 的**换脚复核** ✓ ⇒ 3 处通过 ✓、1 处否决 ✓ ⇒ 顺手修掉过孔净距 ✓**

### ① 用户改了什么（`_work/v76_byHand.fzz` ✓）

不止换脚 ✓，**摆位也重排了**（实测 ✓）：`U1` 与 `D3` **各转 180°** ✓、`R1` 挪 (−3.8,−1.1) mm
且转 −75° ✓、`C1` 转 −90° ✓、`C2` 挪 (−8.1,+6.6) mm ✓、`L1` 微调 0.2 mm ✓；`J1/J2/LED2` 没动 ✓。

| 网 ✓ | 原脚 ✓ | 用户换成 ✓ | 复核判词 ✓ |
|---|---|---|---|
| `RC`（线圈 → ADC）| `PA1`(ADC_IN1，兼 OPA `OPN0`) | **`PD6`**(ADC_IN6) | ✅ 合法（仍是 ADC 脚 ✓）；代价：**OPA 的输入脚让出去了** ✗ |
| `DATA_IN` | `PA2` | **`PC1`** | ✅ 合法（普通数字脚 ✓）|
| `DATA_OUT` | `PD0` | **`PD2`** | ✅ 合法 ✓ |
| `LED_DIN` | `PC6`（`SPI_MOSI`）| ~~`PD4`~~ | ✗ **否决**：`PD4` 不是 SPI 脚 ⇒ 会丢掉"SPI+DMA 产生 WS2812 时序" ✓ ⇒ 用户 2026-10-09 定：**回 `PC6`** ✓（保住 SPI ✓）|

### ② 板子本身（几何复核 ✓）

- **9 张网全通** ✓✓（★ 顺手把 `v76` 定稿里那两处断线也接上了：`J1` 的 GND 脚 ✓、`RC` 到 MCU ✓）；
- 走线 **24 mil × 13（电源）＋ 8 mil × 34（信号）** ✓；不同网同层**最小净距 0.3895 mm** ✓（无一处 <0.127 ✓）；
- 老的四只脚（`PA1`/`PA2`/`PD0`/`PC6`）换完后**一点残铜都没有** ✓；
- ✗ **一处超标**：过孔 #2 离 `C2.connector0` 焊盘只有 **+0.105 mm** ✗（仓规 ≥0.25 ✓、嘉立创下限 0.127 ✗）⇒ **已修** ✓：
  沿 (0.926,−0.378) 挪 **0.175 mm** ✓ ⇒ 离 `C2` **+0.267 mm** ✓、离线圈 **+0.274 mm** ✓（两头都 ≥0.25 ✓，这正是最优位移 ✓）。
  ★ 两条坑（✗ 别再踩 ✗）：① 项目自带的 `fz_move_via.py` 会把它挪**到线圈上** ✗（挪完 −0.300 mm ✗ ＋ 2 条声明与几何脱节 ✗）⇒ 弃用 ✓；
  ② 过孔的 `<pcbView><geometry x,y>` **≠ 圆心** ✗（差一个 `ring_off`，实测 +0.86 mm ✓），线的端点也 = `(x+x1, y+y1)` ✓ ⇒ 端动远端不动要**只改 x1,y1 / x2,y2** ✓。

### ③ ★ 还没做完的一件 ✓：`LED_DIN` 回 `PC6` 的**布线**卡住了 ✗（真障碍，量出来的 ✓）

| 障碍 ✓ | 实测 ✓ |
|---|---|
| **线圈**（铜1 层）| 离 `PC6` 只有 **0.60 mm** ✓；(48.60,16.70) 那点**就压在线圈铜上** ✗ ⇒ 芯片右侧**放不下过孔** ✗（过孔需 0.30+0.25 ✓），窄缝也就 0.55 mm ✓ |
| **用户自己的 `DATA_OUT` 斜线**（铜0 层，`PD2`→`J2.3` 一条直线 ✓）| 它把"`PC6` ↓ 到 `Via5`"的铜0 走廊**切断** ✗（实测：我补的三段里第三段与它**真相交** ✗ —— 前两段两侧 0.5 mm 内全是空的 ✓）|

⇒ 三条出路 ✓（**等用户定** ✗）：① **把 `DATA_OUT` 那条斜线改个走法** ✓（它随便走 ✓，不影响 SPI ✓）
⇒ 之后 `LED_DIN`→`PC6` 只要 **4 段直线** ✓（走廊已验空 ✓）；② 接受 `LED_DIN` 留 **`PD4`** ✓
（固件改软件 bit-bang ✓ —— 单颗 1010 一帧 ≈30 µs ✓ 关中断够用 ✓）；③ 换 **`PD3`/`PD5`** ✓（最好走 ✓，同样 bit-bang ✓）。

### ④ 已同步的数据/文档 ✓

`pixel_nets.py`（`NETS` 按名 ✓：`RC`→`PD6`、`DATA_IN`→`PC1`、`DATA_OUT`→`PD2` ✓；
`EXPECT` 按编号 ✓：`connector1`→`19`、`connector2`→`7`、`connector4`→`15` ✓）、
本文件 §4.2/§4.3 引脚表 ✓、[`pixel-netlist.md`](pixel-netlist.md) §2/§3 ✓、[`connector-plan.md`](connector-plan.md) §2 ✓。

⚠️ **`v76` 定稿现在与设计不一致** ✗（它的脚还是 `PA1/PA2/PD0` ✓）⇒ 等 `LED_DIN` 定的那一刻 ✓，
应该**从手改版出一份新交付件**（换版号 ✓ ＋ 预览 ✓ ＋ 闸门 ✓），`v76` 届时标注"被取代" ✓。

**五十五、第三十八轮（2026-10-09 ✓）：`v76.4_byHand.fzz` 的**原理图**按规则重生成 ⇒ `C2` 回到 v40 的「右上竖插」✓（新规则 `--decoup` ✓）⇒ 四道闸门 4/4 ✓**

### ① 用户要的是什么 ✓

「`v76.4` 能**通过规则、自动**实现 `pixel-schematic-v40.fzz` 那样的布线 ✓ —— 重点是 `C2`：
竖立在**右上**（`J2` 左上方、`LED2` 支路之上 ✓）、两脚**竖直**、各自落在**电源轨**上 ✓；
✗ 不要手工挪器件 ✗，要**写成规则** ✓」；`v76.4` 里它是被画到 `J2` **右边** ✗、走线绕成大环 ✗。

### ② 规则代码 ✗→✓（`gen_schematic_wires.py` ✓ 三处）

| 新东西 ✓ | 干什么 ✓ | 依据 ✓ |
|---|---|---|
| `--nets=<文件>` ✓ | 网表**从 `pixel_nets.py` 读** ✗（不再写死在本文件里 ✗）| 换脚改的是**数据** ✓、不是规则 ✗ |
| `decoup_place()` ＋ `--decoup` ✓ | **去耦电容（两脚分别落在内外两条电源网上）竖插到两条电源轨之间** ✓：内/外轨的 y 从 `rail_y_map()`（**同一个函数** ✓）取 ✓；x = **内轨那一网其它脚所在的列**（吸附 0.1in 网格 ✓）里“**离它原列最近、且过四道闸门**”的那一列 ✓（不压别的件 ✓／本体不出主干 ✓／**不许骑到接口插座头上** ✓／脚不落别人本体・不与别的脚重合 ✓） | 用户 2026-10-09 原话 ✓；v40 的 `C2` 脚 x = **180.0002** ＝ `LED2.VDD` 那一列的网格点 **180.0** ✓ ⇒ 规则**复现 v40 到 0.0002 单位** ✓（并把 `v76.4` 的 274.4 搬回 187.2 ✓）|
| 锚点 `--decoup-anchor=inner/outer` ✓ | `outer` = 逐点复现 v40 手摆位（`GND` 脚踩 `-72` ✓）；**默认 `inner`** = 钉在内轨 ⇒ 两条轨之间走廊 **14.4**（✗ 不是 1.8 ✗）⇒ 顶边那三根绕行线**不必横穿 5V 轨** ✓ | 实测：交叉 **14 → 9** ✓、穿体仍 **0** ✓ |

另修两处**卡住规则的**毛病 ✓：① core 件（**网标签 / 接地符号**）的本体盒**算不出** ✗（svg 在 Fritzing
安装目录 ✓ 包里没有 ✗）⇒ 箱子一空 ⇒ `--hardbody` 拦不住它们 ✗（导线从 `RC` 标签**身上穿过去 6.77 mm** ✗）
⇒ 现在**只调共享实现**补算 ✓（`sch_net.label_box()` / `ground_box()` ✓）—— ✗ 但它**会改 v40 旧行为** ✗
（原命令重跑 ⇒ 38 根 ≠ 41 ✗）⇒ 按仓规**默认关** ✗、要 **`--corebox`** 才开 ✓（回归见 ⑤ ✓）；② 不给 `--vlanes` 时
`VLANE_X` **未绑定就崩** ✗（只在 `if` 里赋值 ✗）⇒ 两个都 `global` ＋ 先给默认值 ✓。

### ③ 数字对照 ✓（两把独立尺子：`render_sch.py` ＋ `_work/sch_probe.py` ✓）

| 项 ✓ | **v40**（参照 ✓）| `v76.4` **改前** ✗ | `v76.4` **改后** ✓ |
|---|---|---|---|
| `C2` 锚点 ✓ | (187.2, −44.5627) | (274.356, −57.1623) ✗ 在 `J2` **右**边 ✗ | **(187.2, −57.1623)** ✓（x 与 v40 **一字不差** ✓）|
| `C2` 两脚 ✓ | 5V (180.0002,−45.0001) ／ GND (180.0002,−72.0) | 5V (267.156,−57.60) ✗ | 5V **(180.0,−57.60)** ／ GND **(180.0,−84.60)** ✓ |
| 5V 顶轨 ✓ | y=−45.0003，x 29.78→237.38 | y=−57.6，x 29.8→267.2（绕到 `J2` 右边 ✗）| y=**−57.6**，x **29.778→230.178** ✓（**断开在 `C2` 脚上** ✓ 端到端 ✓）|
| GND 轨 ✓ | y=−72.0002，x 22.58→210.58 | y=−84.6，绕成环 ✗ | y=**−84.5998**，x **22.578→237.378** ✓（同样断在脚上 ✓）|
| 交叉 ✓ | **7** | **10**（`sch_metrics` ✓）| **9** ✓（比改前的 10 少 ✓；✗ **没到 v40 的 7** ✗ —— 见账 ✓）|
| 穿体 / 重叠 / 贴脚（0.15 mm ✓）| 0 / 0 / 0 ✓ | 0 / 0 / 0 ✓ | **0 / 0 / 0** ✓ |
| 导线 / 总长 / 岛 ✓ | 41 / 471.1 mm / 11 | 53 / **582.2 mm** / — | **48 / 555.9 mm / 11** ✓ |
| 正交度 / 最歪 ✓ | 0.9750 / 0.0378 mm | 0.9808 / 0.0377 mm | 0.9787 / 0.0378 mm ✓ |

### ④ 四道闸门（原始输出留档 `_work/_r50_accept.txt` ✓）**4 / 4 ✓**

- ① `pcb_check.py _work\v76.4_byHand.fzz --nets=pixel_nets.py` ⇒ **判定：✓ 全过** ✓（PCB 一字未动 ✓）；
- ② `python -X utf8 tools\net_group_check.py _work\v76.4_byHand.fzz` ⇒ **exit 0** ✓（Fritzing 认得出每张网 ✓）；
- ③ 改前/改后逐字节 ✓（`_work/view_bytes_diff.py` ✓）：`pcbView` 74 块 ✓、`breadboardView` 122 块 ✓
  ｜**块文本不同 0** ✓｜拼接哈希两边相同 ✓ ✓；
- ④ 探针 ✓（`_work/sch_probe.py --nets=pixel_nets.py` ✓）：**9 张网逐脚全对** ✓｜备用脚 15 只**零连接** ✓｜
  声明**双向自洽** ✓｜跨网假接头 **0** ✓｜线离非本网引脚 **≥0.15 mm**（实测 0 处 < 0.15 ✓）✓。

### ⑤ 复现命令 ✓（交付件 = `_work/v76.4_byHand.fzz` ✓，改前留 `_work/v76.4_byHand.pre-sch.fzz` ✓）

```bat
set TOOLS=F:\git\fritzing-parts-langhua\tools
py -3.13 %TOOLS%\sch_strip_wires.py _work\v76.4_byHand.pre-sch.fzz _work\base.fzz        # 剥线：只剩器件 ✓
py -3.13 %TOOLS%\render_sch.py _work\base.fzz _work\base.png --pins-out=_work\pins.py   # ★ out 给 .png ⇒ 尺子 svg 落在旁边 `_work\base.svg` ✓（探针用 ✓）
py -3.13 gen_schematic_wires.py _work\base.fzz _work\base.svg _work\gen.fzz --nets=pixel_nets.py ^
    --orig _work\v76.4_byHand.pre-sch.fzz --ratio 1.0 --rails --islands=GND --vlanes=5V@29.778 --decoup --hardbody --corebox
py -3.13 _work\merge_sch.py _work\v76.4_byHand.pre-sch.fzz _work\gen.fzz _work\v76.4_byHand.fzz
py -3.13 _work\_r50_accept.py _work\v76.4_byHand.pre-sch.fzz _work\v76.4_byHand.fzz _work\accept.txt
```
（`merge_sch.py` = **按 `modelIndex` 配对**的移植器 ✓ —— 库仓那份 `merge_view.py` 按标题配对 ✗，
本文件里两个 `RC` 标签同名 ✗、线标题与编号还错着 52 处 ✗ ⇒ 标题不是身份 ✗。）

★ **两个开关/参数必须给对** ✓（2026-10-09 实测踩出来的 ✓）：
* **`--corebox` 必须给** ✓ —— *不给* ⇒ **47 根线**（✗ 不是 48 ✗）、原理图 **6 块不同** ✗
  （core 件本体盒一空 ⇒ 少一条本该被它拦住的绕行 ✓）；它默认**关** ✗ 是为了**不动旧行为** ✓（见下 ✓）。
* **`--orig` 必须指“改前那件”** ✓（`_work\v76.4_byHand.pre-sch.fzz` ✓）—— 若指到**已经换过原理图的交付件** ✗
  ⇒ 生成器在它身上**找不到可当模板的原理图线** ✗ ⇒ `AttributeError: 'NoneType' object has no attribute 'set'`
  ✗（`build_wire()` 的 `sub.set("layer",…)` ✓；实测 ✓）。

★ **回归：本轮改代码没动旧行为** ✓ —— 用 **v40 的原命令**（**一个新开关都不加** ✓）重跑 ⇒
`pixel-schematic-v40.fzz` 的 `schematicView` **逐块逐字节相同** ✓（59 块 ✓，拼接哈希 `29c1152314e2b62b` ✓）
⇒ 新代码**只在给 `--nets` / `--decoup` / `--corebox` 时才改行为** ✓。

★ **端到端复现（实测 ✓，另起名 `_work\_r65_*` 跑上面五步 ✓）**：生成的原理图与 `_r42_F.fzz`
**逐字节相同** ✓（`81270e1472d733d1` ✓）；`merge_sch.py` 的产物与**交付件**逐字节相同 ✓
（`852c26f46f730498` ✓）；包内 `.fz` 全文 376209 B ✓ 同哈希 `707d69bf930f658712e75081` ✓
（✗ 只有 zip **条目时间戳**不同 ✗）。

★ **肉眼对照** ✓：`_work\_r66_c2_compare.png`（左 v40 ✓／右交付件 ✓，按 svg `viewBox` 裁同一窗口 ✓
—— 工具 `_work\_r66_zoom.py` ✓）⇒ `C2` 竖立 ✓、位号在**本体右侧**（同款 ✓）、脚 1 上黑轨 / 脚 2 下红轨 ✓、
两处打结点 ✓、右邻 `J2` ✓、`LED2` 在下方 ✓；唯一肉眼差 = 两条轨整体比 v40 **低 12.6 单位** ✗（取舍见 ① ✓）。

★ **上面五步**用 `py -3.13` **原样**跑过一遍 ✓（2026-10-09 ✓，日志 `_work\_r67_doc.log` ✓）⇒
产物 `_work\_r67_doc.fzz` 的 `schematicView` 与**交付件**逐字节相同 ✓（`852c26f46f730498` ✓）；
对它重跑闸门 ⇒ **4 / 4** ✓（`_work\_r67_accept.txt` ✓）。
（★ 坑：`render_sch.py <fzz> <out>` 的 `out` 给 `.png` ✓ —— 尺子 svg 会**落在旁边同名 `.svg`** ✓；
✗ 直接把 `out` 写成 `.svg` ✗ ⇒ 会把 png **覆盖到 .svg 上** ✗ ⇒ 生成器读尺子报 “not well-formed ✗” ✗。）

### ⑥ 账（下一手 ✓）

交叉 **9**（v40 是 **7** ✗）：7 里那 5 条“结构性”的（`EPAD` 竖线 × 5V 轨 ✓、`GND` 车道 × 5V 轨 ✓、
`COIL_B` × `GND` ✓…）**换了网表还在** ✓，而新网表把三条信号从 `U1` **左边**挪到了**上/下边**（`PD6`/`PC1`/`PD2` ✓）
⇒ 绕行线天生要比 v40 多几条 ✗。本轮已把能动的都动了（机制开关 5 档全试 ✓ 全是 9 ✓ —— 与 §第四十五手 同一条：
**同一解的不同写法** ✓）；想再往下 **得同时动几条网的拓扑** ✓（例如给 `RC`/`DATA_OUT` 也开标签岛 ✓、
或把 `C1`/标签重新摆位 ✓）—— 按仓规 **停在这里** ✓、如实记账 ✓。

**五十六、第三十九轮（2026-10-09 ✓）：GND 网上**只留一个**接地符号（新规则 `--dedupe-symbols` ✓）⇒ `_work/v76.4_byHand.fzz` 就地更新 ⇒ 四道闸门 4/4 ✓**

> ★★ **2026-10-09 判据已改正** ✗（见 **§五十八** ✓）：本节那句「**同一张网只留一个**」**是错的** ✗
> ⇒ 现在 = 「**同一座岛上只留一个**」 ✓ —— **不同岛**上的接地/电源符号**必须保留** ✓
> （它们就是**按名并网的合并器** ✓）。本节的**保留判据**（所连导体最长 → 条数 → 离点云近 → 编号小 ✓）
> 与**其余实现一字未动** ✓。

### ① 用户要的是什么 ✓

用户看过 `v76.4_byHand` 的原理图 ✓（GND 网上**两个**接地符号：右 `Ground2` = 手改底图原有 ✓、
左 `Ground1` = 规则生成 ✓；而 `LED2` 的 GND **既**走线到母线 ✓、**又**挂着自己的符号 ⇒ **冗余** ✗）
⇒ 定**方案②** ✓：**「同一张网只保留一个接地符号，其余接地脚一律改为走线接到该符号」** ✓
（✗ 不许针对单个器件写死 ✗ —— 要**规则化** ✓）。

### ② 规则代码 ✓（`gen_schematic_wires.py` ✓ 新增 + 两处修 ✗）

| 新东西 ✓ | 干什么 ✓ | 依据 ✓ |
|---|---|---|
| `dedupe_power_symbols()` ＋ `--dedupe-symbols[=<网,…>]` ✓（与去耦电容规则**并列** ✓ —— 同属“摆位/装饰件”一族 ✓）| **同一张网只留一个“电源/接地符号件”** ✓：**保留谁 = `--orig`（改前那一件）里“直接连在它脚上”的导线总长最大**者 ✓（同长比**条数** ✓、再比**离本网其它脚点云最近** ✓、再比**编号最小** ✓）；其余**删实例** ＋ 清 `<connect>` ＋ 从 `NETS[网]` 摘牌 ✓ ⇒ **布线器重新走一遍** = “把它的脚改走线接到保留符号那条导体” ✓ | 用户 2026-10-09 方案② 原话 ✓；实测：`Ground1` 所连导体 **145.6 单位 = 41.1 mm／3 根** ✓（搭在底部 GND 母线上 ✓）、`Ground2` **30.2／1 根** ✓（只搭一小截支线 ✓）⇒ 保留的正是**母线那个** ✓ |
| `is_power_symbol_mid()` ✓（**判据只有一份** ✓）| `GroundModuleID`（= `sch_net.GROUND_SYMBOL_MODULES` ✓）＋ core 电源符号家族（`PowerModuleID` / `JustPowerModuleID` / `PowerLabelModuleID` ✓ —— 扫 `Fritzing.exe` 的 `*ModuleID` 字面量得到 ✓）| 同一家族：**一个件只干“声明电位”这件事** ✓ ⇒ 同一张网多摆几个就是冗余 ✗ |
| ★ 位置 = **“锚点进网”之后、“布线”之前** ✓ | 之后 ⇒ 符号已在 `NETS` 里 ✓（能按网摘牌 ✓）；之前（布线之前）⇒ 剩下的脚**由既有布线器重走** ✓ ⇒ **通道/交叉/穿体/贴脚四道闸门原样生效** ✗✓（✗ 不另写一套路由 ✗ —— 两套口径 = 等着两边对不上 ✓）| 实测：删完再布 ⇒ 交叉 **9→9** ✓、穿体/重叠/贴脚仍 0 ✓ |

另修**两处卡住“就地重跑”的毛病** ✓（都在本轮日志里现形 ✓）：

1. ✗ `merge_sch.py` 的实例块正则要求**首尾缩进一字相同** ✗（`^([ \t]*)<instance…\n\1</instance>` ✓）——
   件里有**一个**开 12 空格 / 闭 8 空格的块（历史上一轮插入留下的 ✓）⇒ **漏匹配** ✗
   ⇒ 下一轮把它当“A 没有”**又插一份** ✗ ⇒ 交付件里出现**两个 `modelIndex=90015359`** ✗✗（实测撞上 ✓）。
   ✓ 修：闭合标签只要求“行首是它” ✓（`[ \t]*</instance>` ✓，实例块不嵌套 ✓）⇒ 重并 ⇒ 重复 0 ✓。
2. ✗ `emit()` 的**导线模板**取 `oroot` 里**第一条** Wire 实例 ✗ —— `--orig` 指**已换过原理图的
   交付件**时 ✓，头几条是**旧手画线**（`merge_sch` 剥了 `schematicView` ✓、面包板/PCB 视图还在 ✓）
   ⇒ 模板没有原理图视图 ⇒ `AttributeError: 'NoneType' object has no attribute 'set'` ✗✗（= §五十五⑤ 那条坑的**根因** ✓）。
   ✓ 修：模板判据写作“**真的带 `schematicView`**” ✓ —— 对旧命令**零影响** ✓（回归实测：v40 原命令重跑 ⇒
   `schematicView` 59 块拼接哈希 `e9f4cae4bac1d9d2` **两边一字不差** ✓）。

### ③ 改前 / 改后对照 ✓（两把尺子：`render_sch.py` ＋ `_work/sch_probe.py` ✓）

| 项 ✓ | **改前** ✗ | **改后** ✓ |
|---|---|---|
| GND 网接地符号 ✓ | **2 个** ✗（`Ground1` 脚 (161.328,132.0) ／ `Ground2` 脚 (210.578,132.0) ✗）| **1 个** ✓ = `Ground1`，脚 **(161.328,132.0)** ✓ 连在**底部 GND 母线**上（`Wire90015397.c1` ＋ `Wire90015398.c0` ✓）；`Ground2` 的原理图视图**已删** ✓（实例还在 ✓ —— 它的**面包板/PCB 视图逐字节保留** ✓）|
| 导线数 ✓ | 48 根 ✓ | **47 根** ✓（少的那根 = 母线右端到 `Ground2` 脚的 30.2 单位支线 ✓）|
| 总长 ✓ | **555.9 mm** ✗ | **547.4 mm** ✓（−8.5 mm = 那截支线 ✓）|
| 交叉 ✓ | 9 ✓ | **9** ✓（**不比改前差** ✓；渲染器官方口径两边都 9 ✓）|
| 穿体 / 重叠 / 贴脚 ✓ | 0 / 0 / 0 ✓ | **0 / 0 / 0** ✓ |
| `LED2.connector1` ✓ | 经竖线到母线 ✓ ＋ 挂着 `Ground2` ✗ | **经走线到母线** ✓：`Wire90015391` (180.378,17.0)→**(180.378,132.0)** ✓ ＋ `Wire90015398` (180.378,132.0)→**(161.328,132.0)** = `Ground1` 的脚 ✓ |
| 器件/符号位置 ✓ | — | **除被删的 `Ground2` 外，全部一字不动** ✓（逐实例对：非导线件几何**全等** ✓；仅剩的“视图文本不同”= 导线**重新编号**引起的 `<connect>` 引用改写 ✓，逐条核对过 ✓）|

### ④ 四道闸门 ✓（原始输出留档 `_work/_r70_accept.txt` ✓）**4 / 4 ✓**

- ① `pcb_check.py _work\v76.4_byHand.fzz --nets=pixel_nets.py` ⇒ **判定：✓ 全过** ✓
  （焊盘 45 ✓／走线 52 ✓／过孔 5 ✓／声明 105 条不合格 0 ✓／悬空声明 0 ✓）；② `net_group_check.py` ⇒ **exit 0** ✓ 9/9 网；
- ③ 改前/改后逐字节（`_work/view_bytes_diff.py` ✓）：`pcbView` **74 块** ✓、`breadboardView` **122 块** ✓
  ｜**块文本不同 0** ✓｜拼接哈希 `24141dd900659867` / `8b450fd58b38600c` **两边相同** ✓；
- ④ 探针（`_work/sch_probe.py --nets=pixel_nets.py` ✓）：**9 张网逐脚全对** ✓｜**接地符号 = 1**（连在 `Ground1` ✓）｜
  备用脚 15 只**零连接** ✓｜声明**双向自洽** ✓｜跨网假接头 **0** ✓｜贴脚 **0** ✓｜交叉 **9** ✓｜总长 **547.4 mm** ✓。

### ⑤ 复现命令 ✓（交付件 = `_work/v76.4_byHand.fzz` ✓，改前留 `_work/v76.4_byHand.pre-dedupe.fzz` ✓）

```bat
set TOOLS=F:\git\fritzing-parts-langhua\tools
copy _work\v76.4_byHand.fzz _work\v76.4_byHand.pre-dedupe.fzz                          # 先备份 ✓
py -3.13 %TOOLS%\sch_strip_wires.py _work\v76.4_byHand.pre-dedupe.fzz _work\_r70_base.fzz   # 剥线：只剩器件 ✓
py -3.13 %TOOLS%\render_sch.py _work\_r70_base.fzz _work\_r70_base.png --pins-out=_work\_r70_pins.py   # 尺子 ✓（out 给 .png ✓）
py -3.13 gen_schematic_wires.py _work\_r70_base.fzz _work\_r70_base.svg _work\_r70_gen.fzz --nets=pixel_nets.py ^
    --orig _work\v76.4_byHand.pre-dedupe.fzz --ratio 1.0 --rails --islands=GND --vlanes=5V@29.778 --decoup ^
    --hardbody --corebox --dedupe-symbols                                               # ★ 新开关在这 ✓
py -3.13 _work\merge_sch.py _work\v76.4_byHand.pre-dedupe.fzz _work\_r70_gen.fzz _work\v76.4_byHand.fzz   # 就地更新 ✓
py -3.13 _work\_r50_accept.py _work\v76.4_byHand.pre-dedupe.fzz _work\v76.4_byHand.fzz _work\_r70_accept.txt
```
（日志 `_work/_r70_gen.log` ✓；预览 `_work/_r70_preview.png` ✓ —— 肉眼可见：**符号只剩一个** ✓、
母线右端那截**没了** ✓、`LED2` 的 GND **顺走线进母线** ✓。）

★ **中间脚本（都在 `_work/` ✓，只读探针 ✓）**：`_r70_dump.py`（列器件/符号/导线 ✓）、`_r70_struct.py`（实例/视图结构 ✓）、
`_r70_dupmi.py`（查重复 `modelIndex` ✓ —— 抓 merge 漏匹配那只 ✓）、`_r70_blk.py`/`_r70_blk2.py`（打印整块 ✓）、
`_r70_wirediff.py`（导线集合/几何/声明对照 ✓）、`_r70_schdiff.py`（逐实例位置清单 ✓）、
`_r70_viewnorm.py`＋`_r70_diffwhy.py`（归一化对照 + 第一处差异 ✓）、`_r70_spansmiss.py`（查 merge 正则漏匹配 ✓）。

### ⑥ 账（下一手 ✓）

- ✗ **`--dedupe-symbols` 与 `--ground=<网>` 语义相抵** ✓（后者按“**每个功能模块挂一个**” ✓ = 故意要多符号 ✓）——
  要用前者就**别给后者** ✓（本轮命令两者不同时出现 ✓）；已在代码注释里写明 ✓。
- ✗ **电源符号那一半没实测样本** ✓：本文件只有**接地符号**（`PowerModuleID` 家族 0 个实例 ✓）——
  规则代码在 ✓（判据同一份 ✓）、`5V` 那路走的是**轨＋车道** ✓ ⇒ 如实记账 ✓。
- 交叉仍 **9**（与 §五十五⑥ 同一条账 ✓，本轮没恶化 ✓ 也没追平 v40 的 7 ✗）。

**五十七、第四十轮（2026-10-09 ✓）：原理图视图内**每张网必须一个连通岛**之规则 `--complete-islands` ✓ ⇒ `_work/v76.4_byHand.fzz` 就地更新 ⇒ 四道闸门 4/4 ✓、交叉 9→9（**零新增** ✓）**

> ★★ **2026-10-09 增补** ✗（见 **§五十八** ✓）：新增 **`--symmerge`** ✓ —— 岛 > 1 时**优先**
> 用**同名符号/标签**把岛并起来 ✓；**不给 `--symmerge`** ⇒ 本节行为**一字不差** ✓
> （本节那条 93.3 mm 长线就是它的 A/B 基线 ✓）。
> ★ 另：**闸门口径改正** ✗ —— 「每张网 1 个岛」的判定改成**按名并网**口径 ✓
> （同名标签 ✓ ＋ **接地符号家族** ✓ 都算连接 ✓，见 §五十八 ②③ ✓）。

### ① 用户要的是什么 ✓

用户看 `v76.4_byHand` 的原理图 ✓，原话：「**上下有两个 GND 网，这两个网没有连在一起啊？是不是缺了什么规则，导致地网没有连在一起？**」✓ ——
`GND` 在这张视图里被画成**上下两段互不相接的导体** ✗（上面一段 = `U1.VSS`/`EPAD` ＋ `C2`/`J1`/`J2` 的 GND ✓；下面一段 = 底部母线 ＋ `Ground1` ✓）。

★ **为什么既有闸门都没报** ✗✗（= 规则 × 闸门 **双缺口** ✓）：旧探针查的是
「**全视图合并**后每张网的成员」✓（`check_netlist`／`net_group_check` ✓ —— 只看 `<connect>` 声明 ✓）与
「PCB 铜的连通岛」✓ ⇒ 「**本视图内部一张网画成几个岛**」**没有任何人查** ✗。
⇒ 本轮按仓规补：**规则一条**（`--complete-islands` ✓）＋ **闸门一条**（`sch_probe` 第 ⑤ 项 ✓）。

### ② 规则代码 ✓（`gen_schematic_wires.py` ✓，全部**默认关** ✗ ⇒ 不给开关**一字节不差** ✓）

| 新东西 ✓ | 干什么 ✓ | 依据 / 实测 ✓ |
|---|---|---|
| `--complete-islands` ＋ 主循环里那一段补岛 ✓ | 布完线（含抽出重排 ✓）后对 `nets_segs` 的**每个布线组**数岛 ✓；岛 > 1 ⇒ 在**岛的端点**里找一对 ✓（按曼哈顿距离排序取前 `COMPLETE_MAX_PAIRS=120` 对 ✓），用**同一个 `route_pair()`** 布线 ✓（硬闸门/代价/通道**一份都不新造** ✗）；补进 `nets_segs` ＋ `used` ✓；一轮接一对 ✓、≤12 轮 ✓；**补完仍 > 1 个岛 ⇒ 退出码 1** ✓ | 是用户 2026-10-09 点的名 ✓：“是不是缺了什么规则”✓。★ 网标签分出的 `RC-1/RC-2` 是**组** ✓（同名标签按 Fritzing 语义同网 ✓）⇒ 不算分岛 ✓ |
| `island_groups()` ✓ | `island_count()` 的“**分组**”版 ✓（端点相接 ✓ / 端点压别人中段 ✓ —— 判据同一套 ✓）| 补线要**知道哪几段在一个岛里** ✓ |
| `extension_len()` ✓ | 新路径里**与既有同网导线共线且端点相接**的长度 ✓ = 用户要的「**优先沿已有母线/轨道就近并线**」✓ | 每段只记一次 ✓（撞两根不重复 ✓）|
| `body_strict_bad()` ✓（**补线专用·更严本体闸门** ✓）| **任何**采样点不许落在**任何**本体（内缩 0.6 ✓）里 ✗ —— 只豁免两个接点自身 ✓ | ✗ 实测挖出一个**滥用** ✓：`body_hard_bad()` 的“**按段豁免**”（段端点上有它的脚 ⇒ 整段放行 ✓）让一条候选从 `J2` 的脚**往右穿过整个 `J2` 符号盒** ✗（`0` 交叉、只有 `64.9mm` ✗）而**两道既有闸门都放行** ✗（渲染器也是按段豁免 ✓）⇒ 补线比常规布线更严 ✓ |
| 选择判据 ✓ | `(新增交叉 ↓, 并线长 ↑, 弯数 ↓, 长度 ↓)` ✓ **字典序** ✓ | “少交叉”是用户口径 ✓；“并线长”= 沿母线 ✓（与仓里“一把尺子”同精神 ✓ —— 先硬闸门、再少交叉、再并线、最后短 ✓）|

### ③ 改前 / 改后对照 ✓（两把独立尺子：`render_sch.py` ✓ ＋ `_work/_island_probe.py` ✓ ＝ 新独立探针 ✓）

| 项 ✓ | **改前** ✗ | **改后** ✓ |
|---|---|---|
| **`GND` 在本视图的岛数** ✓ | **2 个** ✗（岛1 线 9 根 `(15.4,-84.6)–(244.6,9.0)`：`C2.c1 J1.c1 J2.c1 U1.c20 U1.c3` ✓；岛2 线 8 根 `(37.7,17.0)–(180.4,132.0)`：`C1.c1 D3.c0 D3.c1 LED2.c1` ＋ `Ground1` ✓）| **1 个** ✓（补 3 段：`(237.4,-84.6)→(266.0,-84.6)→(266.0,132.0)→(180.4,132.0)` ✓ —— 上轨右端 → 右缘 → 下轨右端 ✓，两端**都接在既有母线的端点上** ✓）|
| 其它 8 张网 ✓ | 各 1 个 ✓（`RC` 几何 2 个 ✗ 但**同名标签缝起来 = 1 个** ✓ —— 用户 2026-10-04 定的“省线” ✓）| 各 1 个 ✓（`RC` 同上 ✓）|
| 导线 ✓ | 47 根 ✓ | **50 根** ✓（+3 = 补线 3 段 ✓）|
| **交叉** ✓ | 9 ✓ | **9** ✓✓ —— **零新增** ✓（补线走**空白右缘** ✓，不跨任何既有线 ✓）|
| 总长 ✓ | 547.4 mm ✓ | 640.7 mm（+93.3 mm ✓）|
| 穿体 / 重叠 / 贴脚 ✓ | 0 / 0 / 0 ✓ | **0 / 0 / 0** ✓（贴脚实测 0 处 <0.15 mm ✓；新线离最近的非本网脚 **7.2 单位 = 2.03 mm** ✓）|
| 器件/符号位置 ✓ | — | **除 `J2` 的位号外全等** ✓（逐实例对 ✓：非导线件的 `<geometry>`/`<transform>` **全等** ✓；`J2` 位号被**既有规则**「位号不许压导线」从 `(244.578,−27.0978)` 摆到 `(232.4812,31.9222)` ✓ —— **补线必须**：新线右缘那根正好压在它旧位置上 ✓，重摆后四项压测 0/1 = 与改前同值 ✓）|

★ **补线候选实测**（生成器自己打印 ✓，“一把尺子”排序 ✓）——**想要更短就得付交叉** ✓：

| 候选 ✓ | 新增交叉 ✓ | 并线长 ✓ | 长 ✓ | 形状 ✓ |
|---|---|---|---|---|
| **① ★选中** ✓ | **+0** ✓ | 114.2 ✓ | **93.3 mm** ✓ | 上轨右端 → 右缘（x=266）→ 下轨右端 ✓ |
| ② ✓ | +1 ✗ | 155.0 ✓ | 100.1 mm ✓ | 沿 `J2` 支线直下 → 从**下母线下方**（y=148）绕到左端 ✓ |
| ③ ✓ | +1 ✗ | 66.0 ✓ | 41.4 mm ✓ | 沿 `J2` 支线直下到 y=75 → **45° 斜线**到 (180.4,132) ✓ |
| ④ ✓ | +1 ✗ | 0.0 ✓ | 17.0 mm ✓ | 沿支线到 y=17 → 横切到 `LED2.GND` 脚 ✓ |
| ⑤ / ⑥ ✓ | +2 ✗ | 75.0 / 44.2 ✓ | 25.4 / 27.5 mm ✓ | 左侧「Z」绕行（穿过 `5V`/`DATA_IN` 两处）✓ |

（★ 另有 **3 条**候选被「更严本体闸门」拒掉 ✓、**76 条**被硬闸门复验拒掉 ✓ —— 见生成日志 `_work/_r71_gen.log` ✓。）

### ④ 验收清单（**五道** ✓ —— 原始输出留档 `_work/_r71_accept.txt` ✓；探针前后并列见 `_work/_r71_islands.txt` ✓）**4/4 ＋ 岛检查 ✓**

- ① `python -X utf8 …\pcb_check.py _work\v76.4_byHand.fzz --nets=pixel_nets.py` ⇒ **判定：✓ 全过** ✓（PCB 一字未动 ✓）；
- ② `python -X utf8 tools\net_group_check.py _work\v76.4_byHand.fzz` ⇒ **exit 0** ✓（Fritzing 认得出每张网 ✓）；
- ③ 改前/改后逐字节 ✓（`_work/view_bytes_diff.py` ✓）：`pcbView` **74 块** ✓、`breadboardView` **122 块** ✓
  ｜**块文本不同 0** ✓｜拼接哈希 `24141dd900659867` / `8b450fd58b38600c` 两边相同 ✓ ✓；
- ④ 探针（`_work/sch_probe.py --nets=pixel_nets.py` ✓）：**9 张网逐脚全对** ✓｜**接地符号 = 1** ✓｜
  备用脚 15 只**零连接** ✓｜声明**双向自洽** ✓｜跨网假接头 **0** ✓｜贴脚 **0** ✓｜**交叉 9**（与改前同 ✓）｜总长 **640.7 mm** ✓；
- ⑤ ★ **原理图视图内每张网 1 个岛** ✓（2026-10-09 新增 ✓）：改前 **`GND` = 2 个岛 ✗**（探针 exit 1 ✓）、
  改后**全部 9 张网 = 1 个岛 ✓**（exit 0 ✓）；**同名网标签算连接** ✓（`RC` 的两个标签 = 1 张网 ✓）、
  **接地符号的隐式合并不算** ✓（用户点的正是它 ✗）。
  ★★ **注明** ✓：这一条**全视图合并口径查不出来** ✗ —— `check_netlist`／`net_group_check` 只看
  `<connect>` 声明 ✓、`pcb_check` 只看 PCB 铜 ✓ ⇒ “本视图里画成几个岛”**必须**新立这条探针 ✓。

### ⑤ 复现命令 ✓（交付件 = `_work/v76.4_byHand.fzz` ✓，改前留 `_work/v76.4_byHand.pre-island.fzz` ✓）

```bat
set TOOLS=F:\git\fritzing-parts-langhua\tools
copy _work\v76.4_byHand.fzz _work\v76.4_byHand.pre-island.fzz                              # 先备份 ✓
py -3.13 %TOOLS%\sch_strip_wires.py _work\v76.4_byHand.pre-dedupe.fzz _work\_r71_base.fzz  # 与 §五十六 同一条链 ✓
py -3.13 %TOOLS%\render_sch.py _work\_r71_base.fzz _work\_r71_base.png --pins-out=_work\_r71_pins.py
py -3.13 gen_schematic_wires.py _work\_r71_base.fzz _work\_r71_base.svg _work\_r71_gen.fzz --nets=pixel_nets.py ^
    --orig _work\v76.4_byHand.pre-dedupe.fzz --ratio 1.0 --rails --islands=GND --vlanes=5V@29.778 --decoup ^
    --hardbody --corebox --dedupe-symbols --complete-islands                              # ★ 新开关在这 ✓
py -3.13 _work\merge_sch.py _work\v76.4_byHand.pre-dedupe.fzz _work\_r71_gen.fzz _work\v76.4_byHand.fzz   # 就地更新 ✓
py -3.13 _work\_r50_accept.py _work\v76.4_byHand.pre-island.fzz _work\v76.4_byHand.fzz _work\_r71_accept.txt
py -3.13 _work\_island_probe.py _work\v76.4_byHand.fzz --nets=pixel_nets.py --pins=_work\_r71_pins.py      # ⑤ 独立探针 ✓
```

★ **零副作用实测** ✓：**不给 `--complete-islands`** 重跑同一条链 ⇒ 与 `pre-island` **逐字节相同** ✓
（内层 `.fz` 哈希 `68e3fd32e781f1c1` 两边一致 ✓）；**v40 的原命令**（一个新开关都不加 ✓）重跑 ⇒
`pixel-schematic-v40.fzz` 的内层 `.fz` **全文逐字节相同** ✓（`8e58a11636fda6ca`／164725 B ✓）
⇒ 新代码**只在给 `--complete-islands` 时才改行为** ✓。

★ 中间脚本（都在 `_work/` ✓）：`_island_probe.py`（**新独立探针** ✓：逐网数岛 ✓ 与生成器**不同源** ✓）、
`sch_probe.py`（**加第 ⑤ 项** ✓）、`_r50_accept.py`（闸门清单文字同步 ✓）、`_r71_*.log/txt/png`（证据 ✓）。

### ⑥ 账（下一手 ✓）

- **交叉 9**：本轮靠“**走空白右缘**”做到**零新增** ✓（候选表在 ③ ✓）——总账仍是 9（v40 是 7 ✗，见 §五十五⑥ ✓ 未恶化 ✓）。
- **+93.3 mm**：零新增交叉的代价 ✓（更短的候选 ②③④ 各要 +1 交叉 ✗ ⇒ 按“少交叉”优先 ✓ 未采用 ✓ 已记账 ✓）。
- **`J2` 位号被重摆** ✓（补线必须 ✓，见 ③ ✓）。
- `--islands=GND` **没删** ✓ —— 它管的是“**轨道布局**” （GND 两簇各走自己的轨 ✓）；
  本轮 `--complete-islands` 管的是“**最后必须接成一个岛**” ✓ —— 两条规则**职责不同** ✓、可同时开 ✓。

**五十八、第四十一轮（2026-10-09 ✓）：把「用 93.3 mm 长线补地岛」改成「**每个岛各挂一个同名接地符号**」✗ ⇒ `--dedupe-symbols` 判据改正 ＋ 新开关 `--symmerge` ＋ 闸门改「**按名并网**」口径 ⇒ `_work/v76.4_byHand.fzz` 就地更新 ⇒ 四道闸门 4/4 ✓、交叉 9→9（**零新增** ✓）、总长 **640.7 → 552.4 mm** ✓**

### ① 用户要的是什么 ✓

用户看 §五十七 交付件的原理图 ✓，原话 ✓：
「**为什么不用接地符号，而要画这么长的线？如果这么合并地线孤岛，那个接地符号完全可以删除的吧？**」✓
⇒ 用户对 ✓，而且**本项目早就在用这条机理** ✓：`RC` 网就是「**几何 2 段、同名标签缝成 1 张网**」的既有画法 ✓
（用户 2026-10-04 定的「**省线**」✓）⇒ **接地符号与网标签在 Fritzing 里都是“按名并网”** ✓
（依据 `sch_net.py` 的源码笔记：`LocalGrounds` ＝ 全图 `GND/VSS/GROUND` 的脚拉成一张网 ✓）。

### ② 两条规则（判据写死 ✓）+ 一处闸门口径 ✓

| 改什么 ✓ | 旧 ✗ | 新 ✓ | 判据（写死 ✓，可复核 ✓） |
|---|---|---|---|
| ① `dedupe_power_symbols()`（`--dedupe-symbols` ✓）| **同一张网**只留一个符号 ✗ ⇒ 把“不同岛上的符号”也当冗余删掉 ✗（等于**把岛拆散** ✗）| **同一座岛上**只留一个 ✓；**不同岛**上的**保留** ✓ | 「岛」= **`--orig` 导线图里几何连通的分量** ✓（端点重合 ≤0.05 ✓ 或端点压在别人**中段**上 ✓）—— 与 `island_count()` **同一把尺子** ✓（新函数 `_orig_island_at()` ✓）；**保留谁**仍是老那套 ✓（所连导体最长 → 条数多 → 离本网其它脚点云近 → 编号小 ✓）|
| ② `--complete-islands` 补岛 ✓ ＋ **新开关 `--symmerge`** ✓ | 岛 > 1 ⇒ **一律画线** ✗（GND 那根 **93.3 mm**）| 岛 > 1 ⇒ **优先用同名符号/标签**把岛并起来 ✓；**只有当“符号不适用”或“明显更差”时**才画线 ✓ | ① **先算最优走线** ✓（**同一套** `route_pair()` ✓，不另写路由 ✗）；② **`需画的线 > 25 mm（`SYM_MERGE_MAX_MM`）` 或 `会新增交叉`** ⇒ **用符号** ✓；否则（线又短又不添交叉 ✓）⇒ **照旧画线** ✓；③ 挂点 = **`ground_spots()`** ✓（**同一份**避让闸门 ✓：压线 / 交叉 / 蹭脚 / 压本体 / 压文字 ✓），**必须零违例** ✗（带违例的位置不许凑数 ✓ —— 交叉数不许涨 ✓）；④ **一轮只挂一个** ✓（挂完回到 `while` 开头重数 ✓）|
| ③ 闸门口径 ✓（`sch_probe` ⑤ ＋ `_work/_island_probe.py` ✓）| 「同名**标签**算连接 ✓、**接地符号的隐式合并不算**」✗ ⇒ **双重标准** ✗ | **按名并网** ✓ = **同名网标签**（`LocalNetLabels` ✓）**＋ 接地符号家族**（`LocalGrounds` ✓）**都算** ✓ | 「**铜上确实没有线**」这件事**仍如实报出** ✓（几何岛数列照给 ✓）；判据用**按名并网**那一列 ✓ |

★ **两个实现细节**（都是**实测踩出来的** ✗，不是设计选择 ✓）：
1. **挂点允许落在导线“中段”** ✓（`ground_spots(..., only_mi=…)` 里把导线按 `P_STEP` 打点 ✓）——
   ✗ 只认端点 ⇒ 实测**只剩 15 个候选、且全都有违例**（最少 1 条 = 与 `DATA_OUT` **交叉** ✗）⇒ 交叉数会涨 ✗；
   ✓ 中段挂点是**导线上任何一点** ✓ —— 电气由 emit 既有的「**端点压在同网线中段 ⇒ 补接头**」负责 ✓
   （那正是 **Fritzing 自己另存时会补写 T 形接头**的同一条口径 ✓）。
2. **落点把母线“切一刀”** ✓（`nets_segs` 里把那段一分为二 ✓）—— ✗ 不切的话，渲染器把引线起点报成
   「**悬空导线端 +1**」✗（实测 ✓）；✓ 切开之后引线是**端点对端点** ✓ ⇒ 悬空端 **0** ✓、
   Fritzing 也会在那儿画**接点圆点** ✓；★ 共线合并**不会**把两段并回去 ✓（那一步要求“该点恰好只有
   两个端点” ✓，而这里**三个**：母线两段 ＋ 引线 ✓）。
★ **新件的 `modelIndex` 必须避开 `--orig`（= `merge_sch` 的 A ✓）里已用过的号** ✗✓（emit 里那段 ✓）：
  ✗ `emit` 的 `next_mi` 是**清掉旧导线之后**在本文件上取 max+1 ✓ ⇒ 会落在 **A 的手画导线号段**上 ✗
  ⇒ `merge_sch` 把它当“**同一件**” ⇒ 只换 `<schematicView>` ✗✗ ⇒ 造出 `moduleIdRef="WireModuleID"`
  却装着**接地符号几何**的怪物 ✗（实测：`插实例 1` ✗）。✓ 修 ⇒ **新符号＋引线的号排在两边都没用过的地方** ✓
  （实测 ⇒ `插实例 2` ✓，A 的每件保持原样 ✓）。
★ 另修**两处**（都在 `_work/`，只影响本轮的链 ✓）：
  · `merge_sch.py` 的实例块正则**要求 `</instance>` 前有换行** ✗ ⇒ `build_ground` / `build_label`
    **一行到底**的新件**整块漏掉** ✗（实测：新符号没进交付件 ✓）⇒ 改成 `.*?</instance>` ✓（实例块不嵌套 ✓）；
  · `_island_probe.py` 的 `tch()` **不对称** ✗（只查 `e1` 的端点落在 `e2` 段上 ✓）⇒ **排在最后**的那根线
    端点**永远不被查** ✗ ⇒ 引线被判成独立岛 ✗（而生成器 `island_count()` 与 `sch_probe` 都是对称的 ✓
    ⇒ **三把尺子不一致** ✗）⇒ 改成**双向都查** ✓。

### ③ 改前 / 改后对照 ✓（三把独立尺子：`render_sch.py` ✓ ＋ `sch_probe.py` ✓ ＋ `_work/_r72_gnd.py` ✓）

| 项 ✓ | **改前** ✗（`pre-symmerge` = §五十七 交付件 ✓）| **改后** ✓ |
|---|---|---|
| **那根 93.3 mm 长线** ✓ | **在** ✗：3 段 `(237.4,-84.6)→(266.0,-84.6)→(266.0,132.0)→(180.4,132.0)`（x=266 那条右缘竖线 ✓）| **不存在** ✓（探针全文里 **`266` 一次都不出现** ✓）|
| **GND 接地符号** ✓ | **1 个**（`Ground1` ✓）| **2 个** ✓：`Ground1` 脚 **(161.33,132.00)** ✓（岛2 ✓）、`Ground2` 脚 **(48.58,27.00)** ✓（岛1 ✓）—— **每个 GND 岛各 1 个** ✓ |
| **GND 的岛数** ✓ | 几何 **2 座** ✗ ／ 按名并网 **2** ✗ ｜ 探针 ⑤ **✗✗** ✗ | 几何 **2 座** ✓ ／ **按名并网 1** ✓✓ ｜ 探针 ⑤ **✓ 全部 1 个岛** ✓ |
| **导线数** ✓ | **50 根** ✓ | **49 根** ✓（−3 长线段 ✓ ＋1 母线切一刀 ✓ ＋1 引线 ✓）|
| **总长** ✓ | **640.7 mm** ✗ | **552.4 mm** ✓（**−88.3 mm** ✓）|
| **交叉** ✓ | **9** ✓ | **9** ✓✓ —— **零新增** ✓（引线避让违例 **0** ✓）|
| **悬空导线端** ✓ | 0 ✓ | **0** ✓（母线切一刀之后 ✓ —— 见 ②★2 ✓）|
| 穿体 / 重叠 / 贴脚 ✓ | 0 / 0 / 0 ✓ | **0 / 0 / 0** ✓（重叠自检 **0 对** ✓）|
| 器件/符号位置 ✓ | — | **除“新增 1 个接地符号 ＋ 母线多一个断点”外全等** ✓（逐实例对：非导线件几何**全等** ✓；`J2` 位号**这次没动** ✓）|

★ **GND 网的岛明细**（`_work/_r72_gnd.py` ✓，**独立实现** ✓：接地符号的脚用**几何反解** `sch_net.ground_pin` ✓，**不看 `<connect>`** ✗）：
```
  [GND      ] ✓ 几何岛 2 ｜ **按名并网** 1 ｜ 2 座岛
      岛1：线 11 根 ｜ 脚 C2.connector1 U1.connector3 U1.connector20 J1.connector1 J2.connector1 ｜ 接地符号 1 个：Ground2@(48.58,27.00)
      岛2：线  8 根 ｜ 脚 C1.connector1 LED2.connector1 D3.connector0 D3.connector1 ｜ 接地符号 1 个：Ground1@(161.33,132.00)
      ⇒ **每个 GND 岛各 1 个接地符号**？ ✓ 是 ✓（不合规的岛：无 ✓）
```

### ④ 验收（**四道** ✓ —— 原始输出留档 `_work/_r72_accept.txt` ✓）**4 / 4 ✓**

- ① `python -X utf8 …\pcb_check.py _work\v76.4_byHand.fzz --nets=pixel_nets.py` ⇒ **判定：✓ 全过** ✓
  （PCB 一字未动 ✓：焊盘 45 ✓／走线 52 ✓／过孔 5 ✓／声明 105 条不合格 0 ✓／悬空声明 0 ✓）；
- ② `python -X utf8 tools\net_group_check.py _work\v76.4_byHand.fzz` ⇒ **exit 0** ✓（Fritzing 认得出每张网 ✓）；
- ③ 改前/改后逐字节 ✓（`_work/view_bytes_diff.py` ✓）：`pcbView` **74 块** ✓、`breadboardView` **122 块** ✓
  ｜**块文本不同 0** ✓｜拼接哈希 `24141dd900659867` / `8b450fd58b38600c` **两边相同** ✓✓；
- ④ 探针（`_work/sch_probe.py --nets=pixel_nets.py` ✓）：**9 张网逐脚全对** ✓｜**接地符号 = 2**（每岛各 1 ✓）｜
  备用脚 **15 只零连接** ✓｜声明**双向自洽** ✓｜跨网假接头 **0** ✓｜贴脚 **0** ✓｜**交叉 9**（与改前同 ✓）｜
  总长 **552.4 mm** ✓｜**原理图视图内每张网 1 个岛**（**按名并网**口径 ✓）✓；
- ⑤ **零副作用** ✓（实跑 ✓）：**不给 `--symmerge`** 重跑同一条链 ⇒ 与 `pre-symmerge` 的**内层 `.fz` 逐字节相同** ✓
  （`f79089aa04e44133`／388430 B ✓）；**v40 的原命令**（一个新开关都不加 ✓）重跑 ⇒
  `pixel-schematic-v40.fzz` 的**内层 `.fz` 逐字节相同** ✓（`8e58a11636fda6ca`／164725 B ✓）
  ⇒ 新代码**只在给 `--symmerge` 时才改行为** ✓。本轮交付件内层 `.fz` = **387684 B／`901785392c2cfe54`** ✓。

### ⑤ 复现命令 ✓（交付件 = `_work/v76.4_byHand.fzz` ✓，改前留 `_work/v76.4_byHand.pre-symmerge.fzz` ✓）

```bat
set TOOLS=F:\git\fritzing-parts-langhua\tools
copy _work\v76.4_byHand.fzz _work\v76.4_byHand.pre-symmerge.fzz                          # 先备份 ✓
py -3.13 %TOOLS%\sch_strip_wires.py _work\v76.4_byHand.pre-dedupe.fzz _work\_r72_base.fzz  # 与 §五十六/§五十七 同一条链 ✓
py -3.13 %TOOLS%\render_sch.py _work\_r72_base.fzz _work\_r72_base.png --pins-out=_work\_r72_pins.py
py -3.13 gen_schematic_wires.py _work\_r72_base.fzz _work\_r72_base.svg _work\_r72_gen_new.fzz --nets=pixel_nets.py ^
    --orig _work\v76.4_byHand.pre-dedupe.fzz --ratio 1.0 --rails --islands=GND --vlanes=5V@29.778 --decoup ^
    --hardbody --corebox --dedupe-symbols --complete-islands --symmerge                        # ★ 新开关在这 ✓
py -3.13 _work\merge_sch.py _work\v76.4_byHand.pre-dedupe.fzz _work\_r72_gen_new.fzz _work\v76.4_byHand.fzz
py -3.13 _work\_r50_accept.py _work\v76.4_byHand.pre-symmerge.fzz _work\v76.4_byHand.fzz _work\_r72_accept.txt
py -3.13 _work\_island_probe.py _work\v76.4_byHand.fzz --nets=pixel_nets.py --pins=_work\_r72_pins.py
py -3.13 _work\_r72_gnd.py _work\v76.4_byHand.fzz --nets=pixel_nets.py --pins=_work\_r72_pins.py  # ★ 接地符号×岛 报告 ✓
```

★ 中间脚本（本轮新增，都在 `_work/` ✓）：`_r72_views.py`（三视图块数 ＋ 逐个 Ground 实例 ✓）、
`_r72_mis.py`（比两份 `modelIndex` 集合 ✓）、`_r72_inner.py`（比内层 `.fz` 逐字节 ✓）、
`_r72_gnd.py`（**接地符号 × 岛** 报告 ✓ 独立实现 ✓）、`_r72_ctx.py` / `_r72_blk.py` / `_r72_find.py`
（看某件的整块／某号在哪出现 ✓ —— 就是这几个抓出“新件是**一行到底**”那条 ✗）；证据 `_r72_*.txt/log/png` ✓。

### ⑥ 账（下一手 ✓）

- **交叉仍 9**（= v40 的 7 ✗ ＋ 2 条老账 ✓）—— 本轮**零新增** ✓；总长**回到 552.4 mm** ✓（v40 是 471.1 ✗）。
- **93.3 mm 的长线换成了 5.1 mm 的引线** ✓ —— 代价是**多一个接地符号** ✓（用户点名要的就是它 ✓）。
- **“可读性：贴近不相连的引脚 6 处”** ✗ 与改前**同值** ✓（老账 ✓，本轮没恶化 ✓ 也没治 ✗）。
- `--islands=GND` **仍没删** ✓ —— 它管“**轨道布局**” ✓；`--complete-islands` 管“**最后必须一个岛**” ✓；
  `--symmerge` 管“**能用符号就别画线**” ✓ —— 三条**职责不同** ✓、可同时开 ✓。
- ★ **`--symmerge` 的“符号”这一路目前只实测了接地符号** ✓：本文件**只有** `GND` 一张网分岛 ✓；
  **网标签**那条分支代码在 ✓（同名标签 ⇒ 同网 ✓）、**实测样本 0** ✗ ⇒ 如实记账 ✓。
- ★ **本轮的“按名并网”口径有个边界** ✓：同名的**网标签**也算连接 ✓ —— 可它只在“**本来就是一整张网**”
  的前提下成立 ✓（Fritzing 的 `LocalNetLabels` ✓）；✗ 不许拿它当“随便多贴几个标签就万事大吉” ✗
  —— 那是**改语义** ✗，不是**画法** ✓。

**五十九、第四十二轮（2026-10-09 ✓）：同网**就近先并**之规则 `--mst-merge` ⇒ `LED2.connector1` **直接**就近接 `J2.connector1` ✓ ⇒ `_work/v76.4_byHand.fzz` 就地更新 ⇒ 四道闸门 4/4 ✓、总长 **552.4 → 512.4 mm** ✓（**交叉 9 → 9** ✗ —— 逐条记账见 ④ ✓）**

### ① 用户要的是什么 ✓

用户看 `_work/v76.4_byHand.fzz` 的原理图 ✓，原话 ✓：
「**`LED2.GND` 为什么不就近接 `J2.connector1`（= `J2` 第 2 脚，本来就是 GND）？**」✓
实测确认（已与用户核对 ✓）：现有布线器对每张网是「**轨道优先**」建树 ✓（`5V` 顶轨 / `GND` 底轨 ✓，
`rail_y_map()` 那一套 ✓），网里**每只脚各自引到轨道** ✗ ⇒ 相邻的同网脚（`LED2.connector1` ↔
`J2.connector1` ✓，只差 **64.2 单位 = 18.1 mm** ✓）**并不优先互连** ✗ ⇒ 看着“**路过却不接**”✗、
多走路 ✗、还多担交叉 ✗。**电气上没错** ✓（按名并网 ✓），但不是最短画法 ✗。

### ② 规则（判据写死 ✓，可复核 ✓）

| 新东西 ✓ | 干什么 ✓ | 判据（写死 ✓） |
|---|---|---|
| `--mst-merge` ✓ | 每张网先在**脚/锚点**之间按**最近邻（最小生成树 ✓）**连线 ✓ = 「**离得最近的同网两点先接**」✓ | 距离 = **曼哈顿** ✓（与正交/45° 通道同尺度 ✓）；Kruskal ✓、平手按下标 ⇒ **确定性** ✓ |
| **整簇只用一根主干接轨** ✓ | **轨网**（`5V`/`GND` ✓）只把「**并这一对比两只脚各自跑一趟轨更省**」的对并掉 ✓；**每簇只留一只脚接轨** ✓（`drop` 最小的那只 ✓ = 主干 ✓）| 边 (u,v) 采纳 ⇔ `曼哈顿(u,v) ≤ max(接轨距离(u), 接轨距离(v))` ✓（接轨距离 = **它实际选中的那条轨** ✓ 的那一段 ✓；簇的接轨距离 = 簇内**最小值** ✓）⇒ 每一并**自带省账** ✓、**绝不会比原来多走路** ✓ |
| 非轨网 ✓ | `BR+` / `RC` ✓ 这些网用 MST 边**替代旧“链”** ✓ | MST ≤ 任何生成树 ≤ 链 ✓ ⇒ 不会更长 ✓；**发射次序**按 `(min(i,j), max(i,j))` ✓ ⇒ 与旧链**同集同序** ✓ ⇒ 这些网 `used` 布序**一字不差** ✓ |
| 主干的路由 ✓ | **不走**“出脚档位 / 直连 / T 形搭接”那条**捷径** ✗（那套只保四道硬闸门 ✓、**不比交叉** ✗）| 主干改走**同一套** `route_pair()` ✓ —— 它的第 5 档**就是交叉数** ✓（用户要的「优先少交叉」✓），硬闸门一道不少 ✓ |

★ **零副作用** ✓：**不给 `--mst-merge` ⇒ 一字不差** ✓（交付件内层 `.fz` = `901785392c2c`／387684 B ✓）；
**`v40` 原命令**重跑 ⇒ `pixel-schematic-v40.fzz` 内层 `.fz` 逐字节相同 ✓（`8e58a11636fda6ca`／164725 B ✓）。

### ③ 复现命令 ✓（交付件 = `_work/v76.4_byHand.fzz` ✓，改前留 `_work/v76.4_byHand.pre-mst.fzz` ✓）

```bat
set TOOLS=F:\git\fritzing-parts-langhua\tools
copy _work\v76.4_byHand.fzz _work\v76.4_byHand.pre-mst.fzz                          # 先备份 ✓
py -3.13 %TOOLS%\sch_strip_wires.py _work\v76.4_byHand.pre-dedupe.fzz _work\_r73_strip.fzz   # 与 §五十六～五十八 同一条链 ✓
py -3.13 %TOOLS%\render_sch.py _work\_r73_strip.fzz _work\_r73_base.png --pins-out=_work\_r73_pins.py
py -3.13 gen_schematic_wires.py _work\_r73_strip.fzz _work\_r73_base.svg _work\_r73_gen_mst.fzz --nets=pixel_nets.py ^
    --orig _work\v76.4_byHand.pre-dedupe.fzz --ratio 1.0 --rails --islands=GND --vlanes=5V@29.778 --decoup ^
    --hardbody --corebox --dedupe-symbols --complete-islands --symmerge --mst-merge     # ★ 新开关在这 ✓
py -3.13 _work\merge_sch.py _work\v76.4_byHand.pre-dedupe.fzz _work\_r73_gen_mst.fzz _work\v76.4_byHand.fzz
py -3.13 _work\_r73_accept.py                                                         # ★ 全部证据一次跑齐 ✓
```

★ 中间脚本（本轮新增，都在 `_work/` ✓）：`_r73_chain.py`（跑整条链 ✓ A/B ✓）、
`_r73_report.py`（**独立**几何实现 ✓：改前/改后逐条列交叉 ✓）、`_r73_direct.py`
（**独立**图搜索 ✓：`LED2.connector1 ↔ J2.connector1` 到底连不连 ✓、走哪几段 ✓）、
`_r73_u1c20.py`（**独立算术** ✓：`U1.connector20` 的主干**换落点 x** 的交叉数逐档表 ✓ ——
⑤ 那张表就是它跑出来的 ✓）、`_r73_v40.py`（对照 `v40` 的**手画导线几何** ✓）、
`_r73_accept.py`（证据打包 ✓）。删掉的：那批临时探针与日志（`_r73_dbg*.log` ✓ 等 ✓）。

### ④ 改前 / 改后对照 ✓（三把独立尺子：`sch_probe.py` ✓ ＋ `_r73_report.py` ✓ ＋ `_r73_direct.py` ✓）

| 项 ✓ | **改前** ✗（`pre-mst` = §五十八 交付件 ✓）| **改后** ✓ |
|---|---|---|
| **`LED2.connector1` ↔ `J2.connector1`** ✓ | ✗ **几何上不连通** ✗（一个走 32.5 mm 落底轨、一个走 26.4 mm 落顶轨 ✗，只靠**接地符号按名并网** ✓）| ✓✓ **几何直达** ✓：4 段 `(180.4,17)→(201.4,17)→(201.4,9)→(244.6,9)` ✓ = **20.376 mm** ✓ |
| **GND 网的树形** ✓ | 10 只脚**各自**引到轨 ✓（`U1.c20` 直落 11.7 mm ✓、`J2.c1` 直落 26.4 mm ✓、`LED2.c1` 32.5 mm ✓）| ✓ **4 对先并** ✓（`D3.c0↔D3.c1` 14 ✓、**`LED2.c1↔J2.c1` 72.2** ✓、`U1.c3↔J1.c1` 43.2 ✓、`U1.c3↔U1.c20` 68.4 ✓）＋ **6 只主干** ✓ |
| **总长** ✓ | **552.4 mm** ✗ | **512.4 mm** ✓（**−40.0 mm** ✓ = −7.2% ✓）|
| **导线根数** ✓ | 48 根 ✓ | **44 根** ✓（口径 = 长度 > 0.5 单位 ✓，`_r73_report.py` ✓）|
| **交叉** ✓ | **9** ✗ | **9** ✗（**目标 ≤7 ✗ 未达到** ✗ —— 见下 ⑤ 的逐条账 ✓）|
| 9 张网逐脚 / 备用脚 15 只零连接 / 声明双向 / **假接头 0** / **贴脚 0** / **悬空端 0** ✓ | ✓✓ | **✓✓（全同 ✓）** |
| **每张网 1 个岛**（**按名并网**口径 ✓）| ✓ 9/9 ✓ | **✓ 9/9** ✓ |
| **接地符号 × 岛** ✓ | 2 个 ✓（每岛 1 ✓）| **2 个** ✓（每岛 1 ✓：`Ground2@(188.78,26.00)` 岛1 ✓／`Ground1@(161.33,132.00)` 岛2 ✓）|
| 器件/符号位置 ✓ | — | **两处“规则所迫”** ✓：① `Ground2` 挪到 **(188.78,26.00)** ✓（GND 的岛变了 ⇒ `--symmerge` 的挂点跟着变 ✓）；② `LED2`/`J2` 的**位号文字**跟着新导线重摆 ✓（`relabel()` 本来就会 ✓）—— **元件本体一个都没动** ✓ |

### ⑤ 交叉账 ✓（**逐条** ✓ —— `_r73_report.py` 独立复算 ✓，两把尺子都是 **9** ✓）

| # | 改前 ✓ | 改后 ✓ | 判据 ✓ |
|---|---|---|---|
| a | `5V (244.6,0)→(230.2,0)` × `GND (237.4,9)→(237.4,-84.6)` ✗ | **不存在** ✓ | ★ **治掉 1 条** ✓：MST 并完 ⇒ GND 的主干不再与 `5V` 的落点抢同一个 x ✓ |
| b | `5V 轨 y=-57.6` × `GND x=74.8`（`U1.c20` 的支线 ✗）| **仍在** ✗ | ✗ **治不掉** ✗：`U1.c20`（74.8,-43.2）到 GND 轨（-84.6）**必跨** y=-57.6 ✓ — 逐落点实算 ✓（`_work/_r73_u1c20.py` ✓，**独立算术** ✓）：`x=74.8`(现) **2** ✓／`44.9` **2** ✓／`58.6` **2** ✓／`67.6` **2** ✓／`15.4` **2** ✓／`22.6` **1** ✓／`29.8` **1** ✓／`82.0` **1** ✓／`89.4` **1** ✓／`92.9` **1** ✓ —— ★ **最少 1 条** ✗（`0` 不存在 ✓），而**只差 7.2 的档**（`82.0` 或 `29.8`）**够不着** ✗：① 路由器只给「脚的 x」这条落点 ✗（那套“多档出脚”捷径**在竖直法线时根本不跑** ✗），② `82.0` 那档要**先横出脚到 82.0** ✓，而它旁边就是 `U1.c19`（83.8 ✓，`RC` 的脚 ✗）—— **再往右就压脚** ✗ |
| c | `GND x=74.8` × `RC y=-55.4` ✗ | **仍在** ✗ | 同上 ✓（与 b 同一根线 ✓）；★ 试过把它**交进通用路由比**（`route_pair(extra=…)` ✓ 13 条形状 ✓）⇒ 实测**没收益** ✗：交叉仍 **9** ✓、总长反而 **+8.3 mm** ✗ ⇒ **已撤** ✓（数记在上面 ✓，不给下一手留“传说” ✗）|
| d | — | ★ **新增 1 条** ✗：`DATA_OUT x=209.2 (18→-43.2)` × `GND (201.4,9)→(244.6,9)` | ✗ **结构必然** ✗：`J2.c1` 的脚列 **x=244.6 上下都被 `J2.c2`(18)/`J2.c0`(0) 压住** ✗ ⇒ 只能**从左边 y=9 横着进** ✓；而 `DATA_OUT` 的竖线 `x∈(201.4,244.6)` **是 `LED2` 本体逼出来的** ✓（`159.4…201.4` 那段不许竖着过 ✓）⇒ 它的 y 跨 `-43.2…18` **必含 y=9** ✗ ⇒ **1 条是下限** ✓ |
| e | 其余 6 条 ✓（`J1` 出脚 ×`DATA_IN` ✓、`5V` 竖线 ×`DATA_IN` ✓、`5V` 竖线 ×GND 脚行 ✓、`5V` 竖线 ×`DATA_OUT` 横线 ✓、`COIL_B` ×`GND` `D3` 支线 ✓、`DATA_IN` 竖线 ×GND 脚行 ✓）| **6 条全同** ✓ | ✓ 与改前**同源同量** ✓（`routing` 的候选形状 / 通道表没动 ✗）|

⇒ **账目对得上 ✓**：9 − 1(治掉) − 0(b/c 治不掉 ✓) + 1(必然新增) = **9** ✓。
**≤7 这一条没达到** ✗ —— 根因**量出来了** ✓（不是推的 ✗）：剩下的 8 条里 **2 条**（b/c）卡在
「`U1.c20` 的落点只有**脚的 x** 一条路」✗、**1 条**（d）卡在「`J2.c1` 只能从 y=9 横着进」✗ ——
两者都**不是代价函数能换的** ✗，要动的是**候选形状**（多拐点 L / 45° 收尾）或**空地走廊**
（`--freecorr` ✗ —— 实测一开**更差** ✗：交叉 **11** ✗、总长 **689.8 mm** ✗）⇒ 如实记账 ✓、
✗ **没有静默** ✗。

### ⑥ 验收（**四道** ✓ —— 原始输出留档 `_work/_r73_accept.txt` ＋ `_work/_r73_accept_gates.txt` ✓）**4 / 4 ✓**

- ① `python -X utf8 …\pcb_check.py _work\v76.4_byHand.fzz --nets=pixel_nets.py` ⇒ **判定：✓ 全过** ✓
  （PCB 一字未动 ✓）；
- ② `python -X utf8 tools\net_group_check.py _work\v76.4_byHand.fzz` ⇒ **exit 0** ✓；
- ③ 改前/改后逐字节 ✓（`_work/view_bytes_diff.py` ✓）：`pcbView` **74 块** ✓、`breadboardView` **122 块** ✓
  ｜**块文本不同 0** ✓｜拼接哈希 `24141dd900659867` / `8b450fd58b38600c` **两边相同** ✓✓；
- ④ 探针 ✓（`_work/sch_probe.py --nets=pixel_nets.py` ✓）：**9 张网逐脚全对** ✓｜**接地符号 2**（每岛 1 ✓）｜
  备用脚 **15 只零连接** ✓｜声明**双向自洽** ✓｜跨网假接头 **0** ✓｜贴脚 **0** ✓｜悬空端 **0** ✓｜
  **交叉 9** ✗｜总长 **512.4 mm** ✓｜**每张网 1 个岛**（按名并网 ✓）✓｜
  **`LED2.connector1 ↔ J2.connector1` 几何直达 20.376 mm** ✓✓；
- ⑤ **零副作用** ✓（实跑 ✓）：① 不给 `--mst-merge` 重跑同一条链 ⇒ 与本轮交付件**内层 `.fz` 逐字节相同** ✓
  （`901785392c2c`／387684 B ✓，= §五十八 的交付件 ✓）；② `v40` 原命令 ✓ 重跑 ⇒ 内层 `.fz`
  **逐字节相同** ✓（`8e58a11636fda6ca`／164725 B ✓）⇒ 新代码**只在给 `--mst-merge` 时才改行为** ✓。
  本轮交付件内层 `.fz` = **382044 B／`5ba49d00530f`** ✓。

### ⑦ 账（下一手 ✓）

- **`≤7` 没达到** ✗（**9** ✓）—— 根因逐条见 ⑤ ✓；要往下走就得**扩候选形状**（多拐点 L / 45° 收尾 ✓）
  或**开走廊**（`--freecorr` ✗ 实测更差 ✗）⇒ **这不是一个开关能收的** ✓。
- **`--mst-merge` 与既有开关的协同** ✓：`--decoup`（`C2` 仍竖插两轨之间 ✓、两脚仍正好坐在轨上 ✓）、
  `--dedupe-symbols` ＋ `--symmerge`（GND 仍 **2 岛 × 1 接地符号** ✓）、`--complete-islands`
  （按名并网 9/9 一个岛 ✓）、`--vlanes=5V@29.778`（`5V` 仍走车道 ✓）—— **互不破坏** ✓。
- ★ **`--mst-merge` 只实测了本板这一张网表** ✗：**非轨网**（`BR+`/`RC` ✓）的“同集同序”是**推理** ✓
  ＋ 实测**结果未变** ✓（`BR+`/`RC-1`/`RC-2` 的段数/几何与改前一致 ✓）；**其它板**要另测 ✓。

## 1. 定位

- **单卖**：一片小方板 + 5 V 输入，线圈朝向被测物体 → 板载 LED 的亮度/颜色表示 13.56 MHz 近场场强。
- **阵列**：N 块用**一条链**串起来就是磁像素阵列（4×4 = 16 块，8×8 = 64 块）。

| 阵列 | 像素数 | 20 mm 间距 | 22 mm 间距 |
|---|---|---|---|
| 4×4 | 16 | 80 × 80 mm | 88 × 88 mm |
| 8×8 | 64 | 160 × 160 mm | 176 × 176 mm |

## 2. 架构（P1）

```mermaid
flowchart LR
    subgraph PIX["1 个磁像素（1 块板）"]
        COIL["φ19 线圈<br/>PCB 顶层铜"] --> BR["BAS70BRW<br/>全波整流（4 管一颗）"]
        BR --> RC["10 kΩ + 100 nF<br/>低通"]
        RC --> ADC["MCU ADC<br/>（可选内置 OPA 放大）"]
        ADC --> MCU["CH32V003 级 MCU"]
        MCU --> LED["WS2812B-1010"]
    end
    CMDIN["CMD 来自上游"] --> MCU
    MCU --> CMDOUT["CMD 去下游"]
    UPIN["DATA 来自下游"] --> MCU
    MCU --> UPOUT["DATA 去上游"]
```

信号链：**线圈 → 全波整流 → RC 低通 → MCU ADC → LED**（每块独立完成）。
阵列模式下，每块 MCU 把上游命令**转发**给下游，同时在回传方向上**插入自己的读数** ——
主控在链尾收齐全部像素值，再把颜色下发。

> **为什么不需要 TS3A44159 / CD74HC4067**：每块自己有 ADC，没有"共用一个 ADC 逐通道扫描"的需求。
> 开关最多留 1 路做**基线漂移补偿**（可选）。这是 P1 相对 P2 最大的简化。

## 3. 每块元件清单

| 位号 | 元件 | 封装 | 数量 | 说明 |
|---|---|---|---|---|
| L1 | NFC 线圈 φ19 / 6 匝 / 0.2 mm | PCB 顶层铜 | 1 | 复用 `NFC-Coil`（库内已有，实测铜箔外径 19.0 mm） |
| D1 | `BAS70BRW`（4 × 70 V 肖特基）| SOT-363（SC-70-6）| 1 | **一颗就是整个全波桥** ✓（库内已有 ✓；70 V 耐压 ✓、对线圈加载更小 ✓）|
| R1 | 10 kΩ | 0603 | 1 | RC 串联 |
| C1 | 100 nF | 0603 | 1 | RC 对地 |
| U1 | CH32V003F4U6 / CH32V002F4U6 | **QFN20**（3 × 3 mm，见 §4） | 1 | 5 V 直供、内置 ADC（+ OPA ✓）、**有 SPI** ✓；两颗 drop-in 可互换 ✓ |
| LED1 | WS2812B | **1010** | 1 | 1.0 × 1.0 mm，板载显示（库内已有 ✓） |
| C2 | 100 nF | 0603 | 1 | MCU 去耦 |
| — | 过压钳位（可选） | SOD-323 | 1 | 整流输出 < VDD（防场强过大） |

## 4. MCU：`CH32V003F4U6`（QFN20，3 × 3 mm，2026-09-25 定）

### 4.1 型号：两颗 **同封装同引脚，drop-in 可互换** ✓

WCH 原文：CH32V002「**its pins and functionality are compatible with the CH32V003**」✓

| | `CH32V003F4U6` | `CH32V002F4U6` |
|---|---|---|
| ADC | 10-bit | **12-bit，3 Msps** |
| 内置 OPA | **1 组 ✓** | 无 |
| RAM / Flash | 2 KB / 16 KB | 4 KB / 16 KB |
| 供电 | 3.3 / 5 V | 2.5 / 3.3 / 5 V |
| GPIO | 18 | 18 |

⇒ **不必现在选**：等 single-channel 板回来实测整流包络幅度 —— 够大用 12-bit 的 V002，
太小用带 OPA 的 V003，**板子不用改** ✓（两颗库内都已建好 ✓）。

> 2026-09-25 选型过程：QFN12（`CH32V002D4U6`，2×2 mm）最小但**没有 SPI** ✗；
> SOP8（`J4M6`）有 OPA 但**也没有 SPI** ✗（`PC5/PC6/PC7` 不在它的 8 个脚里 ✗）
> ⇒ 定回 **QFN20** ✓（3×3 mm，**SPI + OPA 都有** ✓，面积仍远小于 SOP8 ✓）。

### 4.2 QFN20 引脚（`CH32V003F4U6` / `CH32V002F4U6`，datasheet §2.2 表 2-1 + §4 封装表）

**封装：3.0 × 3.0 mm，脚距 0.4 mm**（datasheet §4 封装表 ✓）⇒ 批量用**钢网 + 回流**；**手焊/返修：风枪 + 焊锡膏即可 ✓**（用户实测 ✓）。

**18 个 GPIO**（20 脚去掉 VDD / VSS×2），**而且没有 SOP8 那种“内部短接”限制** ✓ ——
datasheet 的 **Note 3 / Note 4 明文只针对 `CH32V002J4M6`（SOP8）** ✗
⇒ QFN20 上 **PA1 / PD1 / PD4 都能正常做输出** ✓。

| pin | 引脚 | ADC | 可用外设（节选） | 本板用途 |
|---|---|---|---|---|
| **0** | **VSS（EPAD）** | — | — | ⚠️ **独立成网**（**不进 `<buses>` 的 GND 总线** ✗），布线时特意接到 GND ✓（与 4 脚同为 VSS ✓）|
| 1 | PD7 | — | **NRST**（复位）/ TIM2_CH4 | 备用 |
| 2 | PA1 | **ADC_IN1** | TIM1_CH2 | **空出** ✓（原线圈输入；★ OPA 输入 `OPN0` 在此 ⇒ 要 OPA 就搬回来 ✓）|
| 3 | PA2 | **ADC_IN0** | TIM1_CH2N | **空出** ✓（原链 `DATA_IN` ✓）|
| 4 | VSS | — | — | GND ✓ |
| 5 | PD0 | — | 通用 I/O | **空出** ✓（原链 `DATA_OUT` ✓）|
| 6 | **VDD** | — | — | 5 V |
| 7 | PC0 | — | TIM2_CH3 | 备用 |
| 8 | PC1 | — | **SPI_NSS** | **链 `DATA_IN`（半双工・收）** ✓（2026-10-09 换脚 ✓）|
| 9 | PC2 | — | I2C_SCL / USART_RTS | 备用 |
| 10 | PC3 | — | TIM1_CH3 | 备用 |
| 11 | PC4 | **ADC_IN2** | TIM1_CH4 / MCO | 备用（第 2 路 ADC ✓）|
| 12 | PC5 | — | **SPI_SCK** | 备用（SPI 只走 MOSI ✓、SCK 不用引出 ✓）|
| 13 | PC6 | — | **SPI_MOSI** | **LED 数据（WS2812，SPI + DMA ✓）** ✓ |
| 14 | PC7 | — | **SPI_MISO** | 备用 |
| 15 | **PD1** | — | **SWIO**（烧录）| 烧录/调试 ✓ |
| 16 | PD2 | **ADC_IN3** | 通用 I/O | **链 `DATA_OUT`（半双工・发）** ✓（2026-10-09 换脚 ✓）|
| 17 | PD3 | **ADC_IN4** | 通用 I/O | 备用 |
| 18 | PD4 | **ADC_IN7** | **OPA 输出 `OPO`** / TIM2_CH1_ETR | 备用（真要放大时用 ✓）|
| 19 | PD5 | **ADC_IN5** | 通用 I/O | 备用 |
| 20 | PD6 | **ADC_IN6** | 通用 I/O | **线圈包络 → ADC** ✓（2026-10-09 换脚 ✓，原 `PA1` ✓）|

✅ **本颗有 SPI** ✓ —— datasheet 产品资源表里 `CH32V003F4U6` / `CH32V002F4U6`（QFN20）的
SPI 栏都是 **1** ✓，引脚就是 **`PC5/PC6/PC7` = SCK/MOSI/MISO**（pin 12/13/14 ✓）
⇒ §5.2 里“用 **SPI + DMA** 产生 WS2812 时序”那条**成立** ✓
（1 个 WS2812 位 = **3 个 SPI bit**，只用 MOSI ⇒ SCK 不用接 ✓）。

> 旧 **SOP8 / QFN12** 引脚表（已作废，存 git 历史 ✓）：SOP8 实际只有 6 个电气节点 ✗、
> 而且**没有 SPI** ✗；QFN12 也没有 SPI、没有 OPA ✗。

### 4.3 引脚分配（18 个 GPIO 只用了 4 个）

| 用途 | 引脚 | 数量 |
|---|---|---|
| 线圈包络 ADC 输入 | **PD6（pin 20，ADC_IN6）** ✓（2026-10-09 换脚，原 `PA1`）| 1 |
| 链 DATA（半双工・收发双网） | **`PC1`（pin 8）收 ＋ `PD2`（pin 16）发** ✓（2026-10-09 换脚，原 `PA2`/`PD0`）| 2 |
| LED 数据（WS2812，走 `SPI_MOSI` ✓） | **PC6（pin 13）** ✓（★ 保住 SPI+DMA ⇒ 不能挪）| 1 |
| SWIO 烧录调试 | **PD1（pin 15）** | 1 |
| **备用 / 扩展** | PD7 / PA1 / PA2 / PD0 / PC0 / PC2 / PC3 / PC4 / PC5 / PC7 / PD3 / PD4 / PD5 | **13** |

★ 换脚的**代价**（2026-10-09 ✓）：线圈离开 `PA1` ⇒ **内置 OPA 的输入 `OPN0` 用不上了** ✗
（想用 OPA 必须把线圈搬回 `PA1` ✓，而 `OPO` 输出仍空着 ✓）。

⇒ 比 SOP8 宽裕得多 ✓（SOP8 只剩 1 个备用 ✗）；半双工三线总线的接插件做法见
[`connector-plan.md`](connector-plan.md) ✓，时序/帧格式见 [`bus-protocol.md`](bus-protocol.md) ✓

### 4.4 封装与面积（datasheet §4 封装表）

**QFN20（`CH32V003F4U6` / `CH32V002F4U6`）= 3.0 × 3.0 mm，脚距 0.4 mm** ✓
批量：**钢网 + 回流**；**手焊/返修：风枪 + 焊锡膏即可 ✓**（用户实测 ✓，QFN 底面焊盘没那么难 ✓）。
比 SOP8（3.9 × 5.0 mm，~30 mm²）**更小** ✓，而且 **SPI ✓ + OPA ✓**、备用引脚管够 ✓
（取舍见 `connector-plan.md §6` ✓）。

> 旧 QFN12（`CH32V002D4U6`）= 2 × 2 mm，更小但**没 SPI、没 OPA** ✗；
> 旧 SOP8 = 3.9 × 5.0 mm、脚距 1.27 mm、手焊友好 ✓ 但**没 SPI** ✗ ⇒ 都已弃用（存 git 历史 ✓）

## 5. 链路架构：LED 与传感数据（✅ 已定 **3 线方案**）

### 5.1 先看 WS2812B 本身：单向单链

数据从 DIN 进 → 取走自己的 24 bit → **再生转发**给 DOUT → 下一颗：

- **没有回读**（不能反向传数据）、**没有地址**，位置 = 物理顺序；断一颗，后面全灭。
- 它是「硬件」菊花链 ⇒ 若让 LED 自己串成链，链就得在每块板中间断开接进本板的 1010，
  接插件得引出 LED_IN / LED_OUT 两根。

（我们**不**这么做 —— **3 线方案**让每块 MCU 自己驱动自己那颗 LED，那两根就省掉了，见 §5.2）

### 5.2 传感数据 + 颜色：三种做法

| 方案 | 板间线 | MCU 引脚 | 位置（谁在哪） | LED 时序 |
|---|---|---|---|---|
| **6 线方案** LED 硬件直穿链 + 传感链 | 6 根：5V/GND/**LED_IN/LED_OUT**/SENS_IN/SENS_OUT | 4/18 | ✅ 天然 | LED 自己再生（最稳） |
| **4 线方案**（原定，已废弃 ✗）| **4 根**（板间 `DATA_IN`/`DATA_OUT` 各一根）—— **2026-09-26 起板间改 3 根；板上仍是 2 根数据网** ✓ | 5/18 | ✅ 天然 | MCU 产生（**SPI + DMA** ✓）|
| **3 线方案** ✅ **采用** 接力链（同 WS2812），MCU 自驱 LED | **3 根**：5V/GND/**DATA**（一根跑双向：下行接力转发 + 回读低脉冲接力）| 5/18 | ✅ 链序 = 物理序（上电枚举一次 `index` ✓）| MCU 产生（**SPI + DMA** ✓）|

- **6 线方案为什么有 LED_IN/LED_OUT**：WS2812B 是**硬件**菊花链，链要在每块板中间「断开」接进这一颗 1010
  （本板 1010 的 DIN 接上游、DOUT 接下游）⇒ 接插件必须引出这两根。
  它们不是额外功能线，**就是 WS2812B 链本身穿过这块板**。
- **4 线 / 3 线方案（✅ 采用的是 3 线方案的接线）**：LED 不串硬件链，而是每块 MCU 自己驱动自己那颗 1010；颜色随链下发，
  每个 MCU 像 WS2812 一样「取走自己那 3 字节、把剩下的转发」✓ 读数则附在帧尾继续往下送
  ⇒ 同一条链同时完成 颜色下行 + 读数回报，**链序 = 物理序** ✓（只需上电做一次 `index` 枚举 ✓）
  代价：MCU 要自己产生 WS2812 时序 —— **走 `SPI_MOSI` + DMA ✓**（QFN20 有 SPI ✓；1 个 WS2812 位 = 3 个 SPI bit ✓）。
  **与 4 线方案的区别**：**只在板间** —— 4 线要两根数据线（各走一向 ✓），3 线**只拉一根**
  （下行靠“取走再转发”✓、回读靠**低脉冲逐级接力** ✓）⇒ 接插件 4 根 → **3 根** ✓；
  **板上仍是 2 个数据脚 / 2 根网** ✓（`DATA_IN` = `PA2`/pin 3 收、`DATA_OUT` = `PD0`/pin 5 发 ✓），
  而且**两口同型、都能当上游或下游用** ✓（见 [`connector-plan.md`](connector-plan.md) ✓）。

> ✅ **已定（2026-09-25 ，2026-09-26 修正拓扑）：3 线方案 —— 板间 3 根线（5V / GND（**居中**）/ **DATA**）** ✓
> MCU 自驱 LED，一条链同时跑「颜色下行 + 读数回报」；拓扑是**与 WS2812 完全一致的单向接力链** ✓：
> 每块“取走自己那 3 字节、把剩下的原样转发” ✓；两个口**同型、都能当上游或下游** ✓（固件自动识别哪边在收 ✓）；
> **两个口的第 3 针不许短接** ✗（短接就成了真总线，回读时隙会打架 ✗）；
> **断一块、下游全灭** ✗ —— 见 [`bus-protocol.md`](bus-protocol.md) §2 ✓。
> **4 线方案 vs 3 线方案**：差的只是**板间那根线** ✓（板上数据脚数一样 ✓）—— 3 线少掉的是“回程”那根 ✗，
> 靠**低脉冲接力**补上 ✓。
> **6 线方案**（带 LED_IN/LED_OUT 的硬件链）作为「零 LED 时序风险」备选保留。

单独销售形态：单块 5 V 上电即工作（固件内置局部归一化）；串联时用 **3 线**对接（`SH-1.0-3P-V` 立贴，**最小尺寸** ✓，两口等价 ⇒ 随便插 ✓）。
电流预算（2026-10-08 定 ✓，依据 = `pcb_current.py` 在实板 `pixel-pcb-v69.fzz` 上量的段压降 ✓）：
**每 4 块板一个注入点** ✓ ⇒ 一段 4 块 × 62 mA = **0.248 A** ✓ ⇒ 全板统一 **8 mil**（0.203 mm ✓）就够 ✓
—— 实测段压降（5V ＋ GND 两程 ✓）**2.7%** ✓（预算 5% ✓）、走线载流 0.75 A ≥ 0.25 A（3 倍 ✓）、
每路注入针 0.25 A ≤ 1 A（`SH-1.0-3P-V` 额定 ✓）。
64 块 = **16 路注入** ✓ ⇒ 与电源选型一起核：整机 64 × 62 mA = **3.97 A @5 V** ✓（全白最坏 ✓）。
★ 为什么不是"整条 64 块串一遍" ✗（实测）：8 块一段时 8 mil 要掉 **9.8%** ✗（要 24 mil 才落回 3.4% ✓）；
4 块一段把段电流砍半、段内等效电阻也砍半 ⇒ 8 mil 就落回 3% 以内 ✓。
★ 为什么不是"一段越长越好" ✗：针上限 **1 A/触点** ⇒ 60 mA/颗时一段最多 **16 块** ✓（见
[`connector-plan.md`](connector-plan.md) §5 ✓）。

## 6. 间距与尺寸预算（由 coupon 实测决定）

要能拼成阵列，像素板边长必须 ≤ 阵列中心间距 ⇒ 只剩很窄的板边 ⇒ 元件**优先塞进中心 φ8 孔**（放不下可以压到绕组下方，见 §6.1）。

间距换算：

| 间距 | 4×4 | 8×8 |
|---|---|---|
| 20 mm | 80 × 80 mm | 160 × 160 mm |
| 22 mm | 88 × 88 mm | 176 × 176 mm |
| 25 mm | 100 × 100 mm | 200 × 200 mm |

面积账（每块）：

| 元件 | 占地（含焊盘） |
|---|---|
| `BAS70BRW`（SOT-363）| **~7.5 mm²**（焊盘外廓 2.60 × 2.90 ✓）|
| R + C + C（0603 × 3） | ~6 mm² |
| MCU | QFN20 **~9 mm²**（3 × 3 ✓） |
| WS2812B-1010 | **~1 mm²**（1 × 1 ✓） |
| **合计** | **≈ 24 mm²** |

可用面积：

- **20 mm 间距**：只有 φ8 中心孔 ⇒ **50 mm² / 面**（双面共 100 mm²）
  ⇒ **单面就能放下**（≈24 < 50 ✓）—— 比 SOP8 版（≈63 必须双面）宽裕得多 ✓。
- **22 mm 间距**：孔以外还多出约 **130 mm² 窄边条**（约 1.5 mm 宽，只放得下小件），
  大件（MCU / LED）仍进孔 ⇒ 余量明显更宽松。

两个方案都要**实测**才知道哪个信号更好；同时**贴片工艺**（QFN20 手焊用风枪即可，见 §4.4 ✓）也要一起选。

### 6.1 铜与元件的分级规则（2026-09-24 放宽）

原来说「线圈投影区一律不许放元件/铜」——**做不到**（25 × 25 mm 的板都排不下），按影响分级：

| 级别 | 内容 | 理由 |
|---|---|---|
| ❌ **绝对不要** | 线圈投影区内的**大片铜 / 地平面** | 涡流最强、L 降最多，还会让相邻像素互相耦合 |
| ⚠️ **尽量避免** | 压在**绕组正下方**的元件 | 优先塞进中心 φ8 孔；塞不下的才压绕组 |
| ✅ **推荐** | **中心 φ8 孔**内的元件 | 离绕组最远，NFC 标签（NTAG）就是芯片放天线中心 |

**为什么可以放宽**：本设计是**非谐振**包络检测（线圈直接进整流桥 + RC 低通，**没有并联谐振电容**）
⇒ 不需要高 Q；附近小金属主要造成幅度上的**系统性偏差**，而每个像素的元件完全相同
⇒ 这是**共模误差**，归一化/标定就能抹掉（我们显示的是相对分布）。

**要守住的几条**：

- 不铺地平面 / 大片铜（也影响像素间耦合）；
- 走线尽量短、尽量走在孔内，避免长距离与绕组平行；
- 元件金属尽量**对称**分布；
- **16 块板必须同一版型**（同样的系统偏差才抵得掉）。

### 实板对比实验（替代原 coupon 方案，2026-09-24 定）

**不做参数测试板（coupon）了** —— 直接打像素板、**打两块同版板对比**（详见 [`coupon-layout.md`](coupon-layout.md)）：

| 板 | 内容 | 作用 |
|---|---|---|
| **全贴件板（成品）** | 像素板（真实布局、**元件全焊**）| 实际灵敏度与分布 |
| **空板（同版）** | **同一版 Gerber**、**一个元件都不焊**（只留铜箔、线圈、焊盘、丝印）| 基准：隔离出“焊了元件”的影响 |

两块板放同一位置、同一激励源比输出 ⇒ **两板铜完全一样** ✓ ⇒
「全贴件板（成品）」−「空板（同版）」= **纯“元件”的影响** ✓。
第一版按 **25 × 25 mm** 打（当前布线的尺寸），灵敏度不够再缩到 22 / 20 mm。

原 coupon 方案的实测项（L / Q / 自谐振、相邻耦合、孔内元件衰减）**不再单独做板**，
需要时用「全贴件板 / 空板」两板的包络幅度对比代替 ✓。

## 7. 制造方式：拼版 vs 整板（2026-09-23 定）

**决定：分开下单。** single-channel 与 coupon 不做「不同设计拼一张」—— 拼版会把
已封版的 single-channel Gerber 坐标平移成面板文件，作废刚核对过的 v0.1.3。

| 拼版方式 | 相邻间距 | 结论 |
|---|---|---|
| **同款多连片**（一块面板放 N 块相同的板） | — | ✅ 首选，按「一片板」计价：100 × 100 mm 面板可放 **25 块 20 × 20** 像素板，单块成本掉一个数量级 |
| **铣槽**（routing） | 槽宽 ~1.6~2.4 mm | ❌ **不能用来拼阵列**：板 20 mm ＋ 槽 2 mm ⇒ 线圈中心距变 22 mm；强行保持 20 mm ⇒ 板只剩 18 mm，装不下 φ19 线圈 |
| **V-cut** | 0 | ⚠️ 无间隙，但 V 槽从每块板边各占 ~0.25 mm ⇒ 20 mm 板只剩 ~0.25 mm 容差；**22 mm 有 1.5 mm 边条才稳** ✅ |

⇒ 两条产品线（共用同一套像素电路，只是分割方式不同）：

| SKU | 做法 | 用途 |
|---|---|---|
| **单卖像素板** | 同款多连片拼版（V-cut / 邮票孔），掰开单片卖 | 演示件、零售 |
| **4×4 阵列板** | **一整块 80 × 80**（16 个像素电路在同一板上，无接缝、栅格精确） | 桌面热力图（自用/整机） |

⇒ 阵列对齐**不靠拼版**；**20 mm 只配「整板阵列」，22 mm 才同时支持「拼版单卖」**。

## 8. 待办 / 依赖

- [x] **MCU 元件库** ✓ —— `fritzing-parts-langhua` 里 **`CH32V003F4U6` / `CH32V002F4U6`（QFN20）** 已建好
  （icon → 面包板 → 原理图 → PCB 全视图 ✓）、**已部署到 MINE** ✓；引脚表见 §4.2（源：`D:\Downloads\CH32V003DS0.PDF` ✓）。
- [ ] **像素板 v0 打样**（25 × 25 mm 第一版）+ **不贴件对照板** → 实测灵敏度 / 分布后再定间距。
- [ ] **single-channel 板回板（3~4 天）** → 实测整流包络量级 → 决定是否用内置 OPA 放大。
- [ ] 像素板 `fzz` + Gerber（等 coupon 数据）。
- [ ] 主控板（ESP32-S3 控制板，待建）+ 链协议固件。

## 9. 与既有文档的关系

| 文档 | 内容 | 在 P1 下的状态 |
|---|---|---|
| `coil-spec.md` | **L1 线圈**：现在的规格（含实测匝距/匝间缝 ✓）、可换档位表、**每档的感应电压/电感代价**、方案 B 的布线实测 ✓ | **支撑 §3 的元件清单** ✓；换线圈规格前先看它 ✓ |
| `docs/phase-1-4x4-validation.md` | 集中式方案 M0~M5、TS3A/MUX 拓扑 | 历史记录，**不改**；M1 模拟前端验证仍有效 |
| `hardware/subboard_4x4/schematic-spec.md` | 16 路 + 4×TS3A + MUX 连接表 | 同上（P2 方案依据） |
| `hardware/subboard_4x4/single-channel/` | 已送厂的单通道板（Gerber v0.1.3） | **照原计划打板**，用于验证模拟前端量级 |
| 本文件 | P1 像素板 | **新方向** |
| `fritzing-parts-langhua/docs/schem-drawing-rules.md` | **画电路通用规则**（A 节可机器校验 / B 节审美）| **本项目遵循** ✓ —— 画完用 `tools/sch_style_check.py` 核（网格只作参考 ✓）|

## 10. 长跑脚本 与 版本比对（2026-10-07 加 ✓）

★★ **2026-10-07 搬家 ✓**（用户指出 ✓：「这类通用工具，应该是放在库下面的」✓）——
本节四个工具（`render_revs.py` ✓ / `diff_revs.py` ✓ / `run_detached.cmd` ＋ `detached_run.py` ✓ /
`beep.py` ✓）**已搬回库仓** `fritzing-parts-langhua/tools/` ✓，**项目里不留副本** ✗
（依据 = 项目根 `toolpaths.py` 里那条约定 ✓）。

⇒ 于是 **§10.1–§10.4 里 `py tools\diff_revs.py …` 那种写法已经过时** ✗，现在两种用法 ✓：

```
# ① 最省事：命令面板 → Tasks: Run Task → ①…⑥（任务里的路径已指向库仓 ✓，cwd 仍是本项目 ✓）
# ② 手敲（cwd 要在本项目目录 ✓ —— 工具按**当前目录**找 fzz / pixel_nets.py ✓）：
python "f:\git\fritzing-parts-langhua\tools\diff_revs.py" v59 v76
python "f:\git\fritzing-parts-langhua\tools\render_revs.py" --all
```

★ 项目**数据**仍留在项目 ✓（`pixel_nets.py` ✓，工具按当前目录自动找 ✓、也可 `--nets=` 指定 ✓）；
扩展（§10.5 ✓）也已同步改：它现在**同时**找「项目目录」和「库仓工具」✓。

v69 PCB 预览

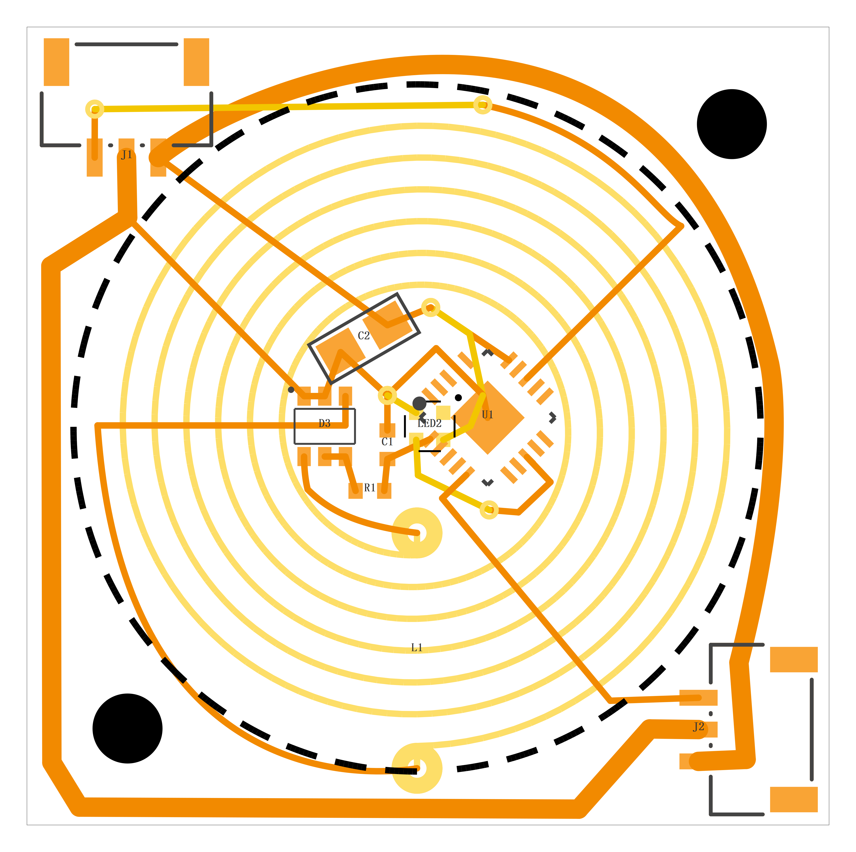
[picture p42: hardware/pixel/pixel-pcb-v77_preview.png]
v77 PCB 预览


### 10.1 长跑脚本扔到 VS Code 外面去跑 ✓ —— `tools\run_detached.cmd`

**为什么** ✗：2026-10-07 VS Code 窗口 **OOM 崩了一次** ✗ ⇒ **挂在它终端里的长跑脚本跟着一起死** ✗
（搜了两天的摆位搜索就是这么没的 ✓）。它把两条路都断掉 ✓：① 脚本与 VS Code 终端**没有父子关系** ✓
（另开独立控制台 ✓）；② 输出**走文件、不进终端** ✓ —— 终端既喂内存 ✗、又**只回显 stdout** ✗
（Python traceback 会被吞掉 ✗，这是本仓踩过的坑 ✓）。

```
tools\run_detached.cmd tools\render_revs.py --all
tools\run_detached.cmd tools\place_drv.py --rot --rot-parts=U1
```

- 关掉 VS Code 也杀不掉它 ✓；日志 = `_work\logs\<脚本>-<时间戳>.log` ✓
- 跑完**响一声** ✓（`rc=0` 上行三声 / 非 0 下行两声 ✓），状态另写一份 `<日志>.rc` ✓
- 日志是 **UTF-8 带 BOM** ✓ ⇒ PowerShell 直接 `Get-Content` 读就是中文 ✓
  （✗ 不带 BOM 时 PS 5.1 按 GBK 读 ⇒ 打开就是乱码 ✗，2026-10-07 实测踩过 ✓）
- 想换解释器：先 `set LH_PY=py` ✓

### 10.2 每一版都渲成图片 ⇒ 用 VS Code 原生「Compare Selected」比对 ✓ —— `tools\render_revs.py`

**为什么** ✗：`.fzz` 是 zip ✗ ⇒ VS Code 比它只显示**二进制差异** ✗（看不出线动没动 ✓）。
渲染**不另写几何** ✗ —— 直接调元件库的 `render_pcb.py` ✓
（= `pcb_check.collect()` ✓ **校验器同一个世界模型** ✓，AGENTS §13「只允许一个声音」✓）。

```
py tools\render_revs.py --all          # 79 版 ⇒ 79 png + 79 svg（实测 55 秒 ✓）
py tools\render_revs.py v59 v69 v76    # 只看关键几版 ✓
py tools\render_revs.py --all --index-only   # 只重建索引 ✓ 不重渲 ✓
```

- 输出到 `diff\`：`<版本>.png`（**比对用** ✓）＋ `<版本>.svg`（看细节/缩放 ✓）＋ `diff\README.md`（索引 ✓）
- **怎么比** ✓：资源管理器里点第一个 png ⇒ 按住 **Ctrl** 点第二个 ⇒ 右键 ⇒
  **比较选中的文件 / Compare Selected** ✓（图像是并排 + 可拖动的 ✓）
- `diff\` **不入库** ✓（79 版 ≈ 77 MB ✗、一条命令能重生 ✓；已写进 `.gitignore` ✓）
- ★ **关键三版**：`v59` = 诚实基线 ✓（布线声明的完整来源 ✓）｜`v69` = 曾被削瘦的那版 ✗
  （线被整条删掉 ⇒ 网组丢失 ⇒ 假的「布线完成」✗）｜`v76` = **当前交付** ✓
  （Fritzing 底部状态栏「**7 中的 5 网络布线完成，2 个接插件仍然需要布线**」✓ 已截图核对 ✓）
  ⇒ ★★ **2026-10-07 用户已定稿：接受 `v76`** ✓（见上面的 ⑤ ✓）

### 10.3 ★ 一张图看出两版差异 ✓ —— `tools\diff_revs.py`（**第三步** ✓）

用户 2026-10-07 定 ✓：「截图所示的这种 PNG 的（并排预览），**不是目标**」✗ ⇒ 要的是
**一张叠合差异图** ＋ **一段话说清改了什么** ✓。

```
py tools\diff_revs.py v59 v76
py tools\diff_revs.py --last 2
```

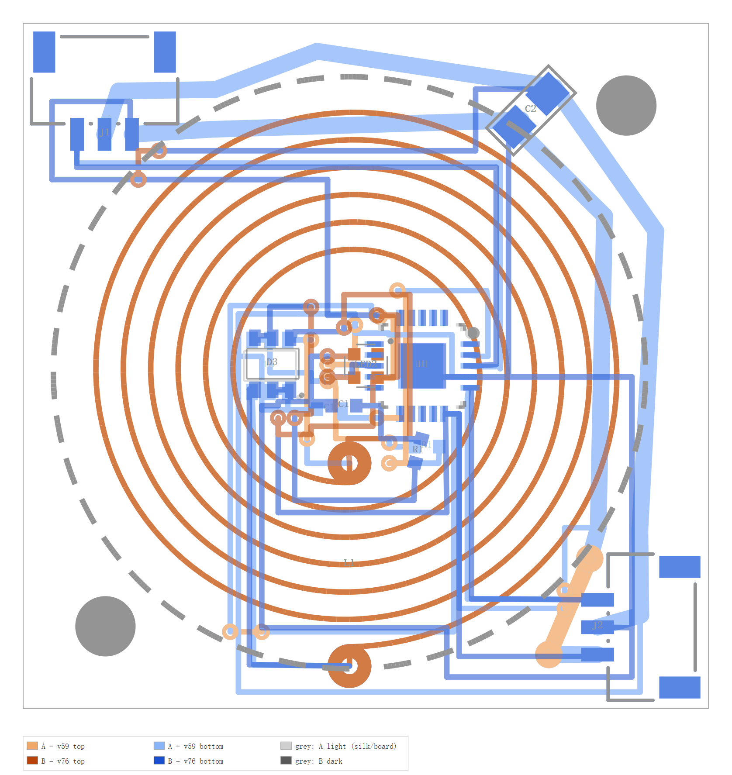
[picture p43: hardware/pixel/pixel-pcb-diff-v59-v76.png]
v59 ⇒ v76 差异图


- 图：**色相 = 层** ✓（**顶层 = 暖橙** ✓ / **底层 = 冷蓝** ✓）、**深浅 = 版** ✓
  （**浅 = A 旧** ✓ / **深 = B 新** ✓）；丝印/板框/位号/孔 = **中性灰**（A 浅 / B 深 ✓）；
  两版重合处**叠得更深**（= 没动 ✓）⇒ 既分得清两层 ✓、也分得清两版 ✓
  （★ 2026-10-07 用户指出「**双面板的颜色差异看不出来了**」✗ —— 旧的"整版一色"
  （A 蓝 / B 红）把 `copper0`/`copper1` 刷成一色了 ✗；修法：用渲染器**自己的层色常量**
  （`C_CU0/C_CU1` ✓、`C_W0/C_W1` ✓、`C_VIA_*` ✓）"**认色换色**" ✓，而不是"刷成一色" ✗
  ⇒ 元件库新增 `render_pcb.remap_colors()` ✓，`repaint_colors()` 改成它的薄封装 ✓
  （**实现只剩一份** ✓；重构后用 SHA1 比对验证过：渲染结果**一字未变** ✓）。
  ⇒ 输出 `diff\diff-<A>-<B>.png` ＋ `.svg`（矢量，可放大 ✓）
- 清单（控制台 ＋ 同名 `.md` ✓）分四段：
  · ① **摆位**：哪个件/哪只脚挪了 **多少 mm** ✓（给 Δ ✓）
  · ② **网**（名字取 `pixel_nets.py` ✓ = 你的词汇 `GND`/`5V`/`RC` ✓）：每张网 **铜块 A ⇒ B**
    ＋ 段数/长度 ✓；**块 > 1 ⇒ 这张网有地方没连上** ✗（并列出每一块各挂着哪几只脚 ✓）
  · ③ **过孔**：颗数/基本没动/挪动/删/增 ✓
  · ④ 结论：逐项相同 ✓ 还是有改动 ✓
- ★★ 它**独立复现**了 Fritzing 那句话 ✓（2026-10-07 实测 `v59 ⇒ v76` ✓）：
  `GND` **1 ⇒ 2 块铜** ✗（多出来的那块只挂 `J1.connector1` ✓ 1 段 0.1 mm ✓）＋
  `RC` **1 ⇒ 2 块** ✗（多出的挂 `U1.connector1` ✓）⇒ 正是「**2 个接插件仍然需要布线**」✓✓
  —— 与状态栏同源同语义 ✓（AGENTS §13 ✓）。
- ★ 口径 ✓（**踩过才写的** ✗）：一张网 = 走线**链** ✓（Fritzing `Wire::collectChained` 语义 ✓）。
  ✗ 按**单条线**的名字去对网 ⇒ 走线两端声明的大多是**另一条走线** ⇒ 只能得到
  `connector0 ↔ connector1` 这种废话 ✗（清单第一版就是这么废的 ✓）；过孔当**接头** ✓
  （它两端走线都声明它 ⇒ 链跨层自然连上 ✓，本工具不需要懂过孔内部 ✓）。
- ⚠️ 长度是**两端直线**近似 ✗（曲线不计 ✓）；渲染的 `--px` 与画布大小差约 358 倍 ✓
  （`--px 5` ⇒ 画布 1676 ✓）—— 所以**图例字号必须按画布比例算** ✗，写死就看不见 ✗（同日踩过 ✓）。
- ★ **图例的位置与排版**（2026-10-07 用户两轮定 ✓）：
  · 放在**图下面的空白带**里 ✓、**分三列**（列 1 = 顶层两版 ✓／列 2 = 底层两版 ✓／列 3 = 灰 ✓）✓
    —— 实现是**画布高度加一条带** ✓ ⇒ 那个 svg 单独打开、README 里的 png **都带图例** ✓；
  · 框的**左缘 = 板框那条线的 x** ✓（✗ 不是画布左缘 ✗ —— 那样看着比图缩进去一截 ✓）；
    fzz 路径用 `_board_px()` 量 ✓、svg 路径用它自己的 `MARGIN` ✓，**同一处常量只留一份** ✓；
  · 两个调用方（`overlay()` / `_svg_mode()`）共用 `_legend()` ＋ `_legend_rows()` ✓（原先是各写一份 ✗）。

### 10.4 ★ 也能比「**Fritzing 自己导出的 svg**」✓（2026-10-07 用户问 ✓）

用户原话 ✓：「如果我从 Fritzing 导出一个 svg，是不是也能这样比较了？」✓ ⇒ **能** ✓：

```
py tools\diff_revs.py "pixel-pcb-v47_图示.svg" v47     # 导出 svg ⇔ fzz（推荐）
py tools\diff_revs.py a.svg b.svg                    # 两个 svg 也行
```

两个前提（都是**实测**出来的 ✓，不是猜 ✗）：

1. **取景要换算** ✗：Fritzing 导出是 **1in = 72 单位** ✓（实测 `width="1.1058in"` +
   `viewBox="0 0 79.6 99.8"` ✓）、且带 **水印** ✓ ⇒ 水印整段删掉 ✓，再按**板框**
   （导出自带 `<g id="board">` ✓）定标与对齐 ✓。实测导出板框 = **25.01 mm** ✓、
   我们侧 = **25.00 mm** ✓ ⇒ 对上了 ✓（误差 0.04% ✓）。
2. **层色口径不同** ✗：导出里**只有走线/过孔**带层色 ✓（`#f28a00` 底 / `#f2c600` 顶 ✓
   = 与我们渲染器**同一套** ✓）；**元件自己的铜箔保留原色** ✗（线圈 `#f7bf13` ✓）
   ⇒ 那些件一律画成**灰** ✓（两版都一样 ⇒ 灰 = 没动 ✓，信息不丢 ✓）。

★ 查这个问题时抳出来的**四个真 bug**（全部靠证据定位 ✓，写进代码注释 ✓）：

| 抳到的 ✗ | 真相 ✓ |
|---|---|
| 包装后 XML 报 `invalid token: line 4, col 6` | 配平扫描 `j += n.end()` 只走到 `</g` ✗ ⇒ **把 `>` 切掉了** ✗ |
| 我们侧的“板框”量出 3803×**3783**（不正 ✗） | 抓错了 rect ✗ —— **`C_BRD_FILL` 就是 `#ffffff`** ✗ ⇒ 会先抓到**整幅白底** ✗ |
| 改成认 `stroke=C_BRD_EDGE` 还是不对 ✗ | ★★ **真因**：`render_pcb.py:246` ✓ —— **不带 `--board-only`** 时 `r` 会
胀成「**板框 ∪ 全部墨迹**」 ✗ ⇒ 那个 `stroke=#111111` 的 rect **是取景框** ✗ 不是板框 ✗
⇒ 拿它当锚 ⇒ **整体平移** ✗（实测 0.5 mm ✓）。修法：fzz 那侧**用 `--board-only` 现渲** ✓ |
| `CAIRO_STATUS_INVALID_SIZE` | 画布尺寸写成 `max(单位宽) × max(k)` ✗（**量纲混乘** ✗）
⇒ 改为 `max(宽×k)` ✓ |

★ 顺带得到一条库知识 ✓（写进了 `render_pcb.py` 的注释 ✓）：**预览里那个 `stroke=#111111`
的 rect 不是板框** ✗（是**取景框** ✓）—— 以前拿它当板框用的地方会错 ✗。

### 10.5 ★ VS Code 扩展：把**图**和**清单**合成一个界面 ✓（2026-10-07 ✓）

★★ **2026-10-07 已随工具一起搬去库仓** ✓（用户定 ✓：「扩展当然要搬，这是仓库的重要功能」✓）
—— 扩展、安装脚本、单测现在都在 **`fritzing-parts-langhua/tools/`** ✓：

| 在哪 | 是什么 |
|---|---|
| 库仓 `tools/vscode-diff/` ✓ | 扩展本体（`package.json` ＋ `extension.js` ＋ `README.md` ＋ 示例图 ＋ 单测 ✓） |
| 库仓 `tools/install_diff_ext.cmd` ✓ | 装（拷进 `%USERPROFILE%\.vscode\extensions\` ⇒ `Reload Window` 即生效 ✓）；`uninstall` 可卸 ✓ |
| 本仓 `hardware/pixel/pixel_nets.py` ✓ | **项目数据**：扩展跑工具时用本项目当 **cwd** ✓（工具按当前目录找 fzz 与网表 ✓） |

**用法与全部细节见库仓 README** ✓：根 `README.md` 的「★ 配套工具：PCB 版本差异视图」（带示例图 ✓）＋
[`tools/README.md`](../../fritzing-parts-langhua/tools/README.md) 的「VS Code 扩展」一节 ✓。
一句话：**双击 `diff\diff-*.md`** ⇒ 左图右清单 ✓ ⇒ **点清单里一条，图上高亮那处变化** ✓。

★ 单测（不用开 VS Code ✓）：`node <库仓>\tools\vscode-diff\test_extension.js <本项目目录>` ✓

★ 本项目的**两个设置**（扩展通用化后加的 ✓，2026-10-07 ✓）：

```jsonc
// AuroraTessellation-NFC\.vscode\settings.json   ← 已入库 ✓
{
  "pixelDiff.projectDir": "hardware/pixel",
  "pixelDiff.fzzPattern": "^pixel-pcb-v\\d+.*\\.fzz$",
  "pixelDiff.bbPattern": "^pixel-breadboard\\d+.*\\.fzz$",
  "pixelDiff.schPattern": "^pixel-schematic-v\\d+.*\\.fzz$"
}
```

三个视图都能比了 ✓（2026-10-07 ✓）：`pixelDiff.fzzPattern` = PCB ✓（76 个 ✓）、
`bbPattern` = 面包板 ✓（21 个 ✓）、`schPattern` = 原理图 ✓（52 个 ✓）——
全量 fzz 151 个 ⇒ 不钉的话三个选择框里都会混进别的稿 ✗。
⚠️ `.vscode/` 在本仓 `.gitignore` 里 ✗ ⇒ 这两行目前只在**本机**生效 ✓，新克隆的机器上要自己加 ✓
（要不要把它纳入版本管理，等用户定 ✓）。

**六十、第四十三轮（2026-10-09 ✓）：用户报「新文件**地线穿过 U1 了**啊！这完全不可接受啊」✗ ⇒ 新开关 `--bodyoutline`（本体几何改取**该视图实际绘制的符号外形** ✓）＋ 渲染器 ④b ＋ 验收探针 ⑨ **三处统一口径** ⇒ `_work/v76.4_byHand.fzz` 就地更新 ⇒ 四道验收 **5/5** ✓、**穿体 3 → 0** ✓、交叉 **9 → 11**（逐条记账 ✓）、总长 **512.4 → 521.3 mm** ✓**

### ① 用户报的是什么 ✓（量出来的清单 ✓ 不许猜 ✗）

用户原话 ✓：「新文件**地线穿过 U1 了**啊！这完全不可接受啊，请修改。」✓
用 `_work/diag_body.py`（**逐点量** ✓：把该件的**实际绘制外形**取出来，再逐段做线段×外形相交 ✓）
量出原理图视图里 **3 段**真的进了器件肚子里 ✗：

| # | 导线 | 层/网 | 两端 | 进入本体的坐标 | 离开 | 穿多深 | 来源规则 |
|---|---|---|---|---|---|---|---|
| 1 | `Wire90015386` | 原理图 / `GND` | (58.58,9.00) → (74.78,9.00) | **(70.278, 9.00)** ← 本体左缘 ✓ | 段末 (74.78,9.00) | **4.50 单位 = 1.27 mm** | `--mst-merge` 主干：`U1.connector3 ↔ U1.connector20`（`VSS ↔ EPAD`，曼哈顿 68.4 ✓，§五十九 ④ 那张表里点过名的就是这一对 ✓）|
| 2 | `Wire90015387` | 原理图 / `GND` | (74.78,9.00) → (74.78,-43.20) | (74.78,9.00)（已在里面 ✓） | **(74.78, -31.50)** ← 本体上缘 ✓ | **40.50 单位 = 11.43 mm** ✗✗ | 同上一对 ✓ |
| 3 | `Wire90015391` | 原理图 / `GND` | (244.58,9.00) → (265.96,9.00) | **(253.578, 9.00)** ← `J2` 本体左缘 ✓ | **(259.956, 9.00)** ← 本体右缘 ✓ | **6.38 单位 = 1.80 mm** | `J2.connector1` 往**右**接轨的支线（落点 x=265.956 ✓）|
| 4 | `Wire90015370` | 原理图 / `COIL_A` | (77.93,72.00) → (26.03,72.00) | — | — | **误报**（旧口径 ✓）：它只擦到 `L1` **墨迹盒**的上缘 0.44 单位 ✓，真实线圈弧在 y≥81.0 ✓ ⇒ 不碰 ✓ |

★ `U1` 的**真实符号外形**（量出来的 ✓，见 ② 的盒模型 ✓）：本体 = svg 里那个 `700×700` 的实心矩形 ✓
⇒ **(70.278, -31.500) → (133.278, 31.500)** = **17.78 × 17.78 mm** ✓；引脚引线是**从本体四边往外**的
短横/竖线（左排 x 58.578…70.278 ✓、上排 y -31.5…-43.2 ✓ …）✓。

### ② 为什么旧闸门（与渲染器）都报 **0** ✗✗ —— 两处根因 ✓（都有数值 ✓）

| 根因 ✓ | 旧口径 ✗ | 量出来的差距 ✓ |
|---|---|---|
| ① **几何取自"占位墨迹盒"** ✗ | `part_box.shape_bbox()` ✓ —— 它把 **引脚引线 ＋ `*terminal` 端子 ＋ 位号/脚名文字** 全算进去 ✗，而且 `A` 弧**认不出**（把 `A` 的参数当坐标读 ✗）| `U1`：盒 **24.38 × 24.38 mm** vs 本体 **17.78 × 17.78 mm** ⇒ 每边多 **11.7 单位 = 3.30 mm** ✗；`J2`：盒左缘 244.578 vs 本体左缘 **253.578** ⇒ 多 **9 单位 = 2.54 mm** ✗；`L1`（8 段圆弧）：盒 y0 = 72.000 vs 真实弧顶 **71.562** ⇒ **连弧都框不住** ✗ |
| ② **豁免按"整段"给** ✗ | `body_hard_bad()` / 渲染器 ④b 都是：「这一段**任一端点**落在某件的脚上（≤0.05 ✓）⇒ **整段**对**该件**放行」✗ | #1 起点 = `U1.VSS` 的脚 ✓、#2 终点 = `U1.EPAD` 的脚 ✓、#3 起点 = `J2.connector1` 的脚 ✓ ⇒ **三段全被豁免** ✗ ⇒ 两道闸门 ＋ 渲染器一起报 **0** ✗✗ |

★ 一句话 ✓：旧口径**既太宽**（盒含引线/文字 ⇒ 擦边也算穿 ✗）**又太松**（整段豁免 ⇒ 从脚上钻进肚子放行 ✗）✓。

### ③ 闸门怎么修 ✓（新增 **`sch_body.py`** ✓ —— 本体外形的**唯一实现** ✓）

| 项 ✓ | 口径（写死 ✓，可复核 ✓） |
|---|---|
| 几何来源 | **只取该视图（`schematicView`）实际绘制的符号 svg** ✓（`sch_box.part_svg_text` ✓：磁盘优先 ✓、包内副本兜底 ✓；**不是 PCB footprint** ✗）|
| 剔掉什么 | `connector<N>terminal`（0.0001 的**零尺寸**锚点 ✓）与 `<text>`（位号/脚名 ✓ —— 有**另一条**判据管"字被划掉" ✓）✓ |
| **引脚引线** | ★ **算本体外形** ✗✓（2026-10-09 改正 ✓，见 ⑦ 的教训 ✓）：它是**画出来**的 ✓，导线从上面横着过去**看着就是接上了** ✗ |
| 闭合外形 | `rect` ✓／`circle`/`ellipse` ✓／`polygon` ✓／首尾重合的 `polyline`/`path` ✓／带 `fill` 的 `path` ✓ ⇒ **区域**（点在多边形内 **且** 离边界 > `eps` ✓）|
| 开放外形 | `line` ✓／开放 `polyline`/`path` ✓ ⇒ **描边**（点离折线 ≤ **半线宽 + `eps`** ✓）|
| `A` 弧 | **真展平** ✓（16 段 ✓）⇒ `L1` 线圈的弧顶再也丢不了 ✓（`sch_body_selftest` ③ 钉着这条 ✓）|
| 旋转/镜像 | 一律走 `sch_box.A_of()`（`m11/m12/m21/m22` 全用上 ✓）⇒ 绝对 sketch 坐标 ✓（自测 ④ 钉着 ✓）|
| 常数 | `eps = 0.5` 单位 = **0.141 mm**（进本体**超过**它才算穿 ✗）；`pin_r = 0.9` 单位 = **0.254 mm**（唯一豁免半径 ✓）|
| 豁免 | **只按位置** ✓：命中点离**本件自己的脚** ≤ `pin_r` ⇒ 放行 ✓ —— ✗ **不按整段** ✗；★ `pin_r` 会被**自动抬到**「本件最粗描边半宽 ＋ `eps`」✓（不然"从脚上垂直往外走"会在自己那条引线的墨迹里**刀锋误报** ✗ —— `L1` 实测只差 0.038 ✓）|
| 新开关 | **`--bodyoutline`** ✓（**默认关** ✓ ⇒ 不给它时行为**一字不差** ✓，见 ⑥ ✓）。打开后 `body_hard_bad()` 整体改道 ✓、`body_strict_bad()`（补线那道）同改 ✓、`route_pair` 的硬闸门 ＋ `--mst-merge` 主干 ＋ 所有支线/落点闸门**一处不落** ✓ |
| 件的**移动** | 外形**按当前位置现算** ✓（`body_shapes_now()` ✓）—— 件会被 `--decoup` / `--snaprails` / `--symmerge` 挪 ✗ ⇒ 载入时烤好的坐标**会过期** ✗（过期 = 闸门对那件**看不见** ✗）|
| 判据只一份 | **生成器闸门** `body_face_bad()` ✓／**渲染器 ④b** ✓／**验收探针 ⑨** ✓ 全调 `sch_body.seg_hit` ✓ |
| 机器自测 | 库仓 **`tools/tests/sch_body_selftest.py`** ✓（**不用任何 `.fzz`** ✓，正反 20 条 ✓）：区域判据 ✓、容差内不算 ✓、描边判据 ✓、`A` 弧（旧 `shape_bbox` 看不见的那条 ✓）、**旋转 180°** ✓、**"整段豁免"必须失效**（从脚上横穿 60 单位 ⇒ **必须命中** ✗✓）、引脚引线算墨迹 ✓、空外形永不命中 ✓（★ 位置 2026-10-09 收进 `tools/tests/` ✓，见 §六十四 ✓）|

★ **覆盖度**（验收探针 ⑨ 自己打印 ✓）：**13 件 × 48 根线 = 624 组** ✓（有外形的件：
`C1 C2 D3 Ground1 Ground2 J1 J2 L1 LED2 R1 RC RC U1` ✓）。

### ④ 重路由 ＋ 改前 / 改后对照 ✓

涉事网只有 **`GND`**（重路由全部在它身上 ✓；`Ground2` 因 `--symmerge` 挂点跟着挪了 **0.371 单位 = 0.105 mm** ✓，**元件本体一个都没动** ✓）：

| 改前 ✗（`pre-bodyfix`）| 改后 ✓ |
|---|---|
| `U1.VSS (58.58,9) → (74.78,9) → (74.78,-43.2) = U1.EPAD`（**横穿 U1 本体** ✗）| `U1.VSS (58.58,9) → (27.38,9)` ✓（**往左**出脚）`→ (27.38,-43.2) → (74.78,-43.2) = U1.EPAD` ✓（绕到引脚列**左侧**再从**上排脚的引线外侧**接回来 ✓）|
| `J2.connector1 (244.58,9) → (265.96,9) → (265.96,-84.6)`（**横穿 J2 本体** ✗）| `(244.58,9) → (235.38,9) → (235.38,-84.6)` ✓（**往左**绕 ✓）|
| 左下角那条 `27.58,0 / 27.58,51` 的 Z 形 | `24.58,0 / 24.58,55.4` ✓（让开新出现的 `x=27.38` 竖线 ✓）|
| `LED2.c1 → (188.78,17) → (201.38,17) → (201.38,9) → (244.58,9)` | `(180.38,17) → (188.41,17) → (236.58,17) → (244.58,9)` ✓ |

| 项 ✓ | **改前** ✗ | **改后** ✓ |
|---|---|---|
| **穿体**（⑨ 口径 ✓）| **✗✗ 3 段**（`U1`×2 ＋ `J2`×1）| ✓ **0 段** ✓✓ |
| **交叉** ✓ | 9 ✗ | **11** ✗（**+2** ✓ —— 逐条账见下 ✓）|
| 总长 ✓ | **512.4 mm** ✓ | **521.3 mm** ✓（**+8.9 mm = +1.7%** ✓）|
| 导线根数 ✓ | 45 ✓ | 48 ✓ |
| 9 张网逐脚 ✓ | ✓ 9/9 ✓ | ✓ **9/9** ✓ |
| 备用脚 15 只**零连接** ✓ | ✓ | ✓ **同** ✓ |
| 声明双向自洽 ✓ | ✓ | ✓ **同** ✓ |
| 跨网假接头 ✓ | 0 ✓ | **0** ✓ |
| 贴脚（<0.15 mm ✓）| 0 ✓ | **0** ✓ |
| **每张网 1 个岛**（按名并网 ✓）| ✓ 9/9 ✓ | ✓ **9/9** ✓ |
| 接地符号 × 岛 ✓ | 2 个（每岛 1 ✓）| **2 个** ✓（每岛 1 ✓）|
| **`LED2.connector1 ↔ J2.connector1` 就近直连** ✓ | ✓ 4 段 / **20.376 mm** ✓ | ✓✓ **3 段 / 19.054 mm** ✓（`(180.4,17)→(188.4,17)→(236.6,17)→(244.6,9)` ✓ **保住且更短** ✓）|
| 声明点几何重合（`find_gap.py` ✓）| 0 处不重合 ✓ | **0 处** ✓ |
| 同网共线重叠 ✓ | 0 对 ✓ | **1 对** ✗（**0.2 单位 = 0.056 mm** ✓，见 ⑦ ✓）|
| `pcbView` / `breadboardView` ✓ | — | **逐字节相同** ✓（`24141dd900659867` / `8b450fd58b38600c` ✓）|

★ **交叉逐条账** ✓（`_work/xdiff.py` ✓ 集合差 ✓）：**治掉 5 条** ✓（`27.58` 那条 Z 形被挪走 ⇒ 它与
`(22.83,18)→(22.83,-57.6)`、`(58.58,9)→(15.38,9)`、`(40.58,43.2)→(15.38,18)` 的三处、以及
`(201.38,9)→(244.58,9)` × `x=209.2` 那一处 ✓）；**新增 7 条** ✗（净 **+2** ✓）：

| # | 新增哪一条 ✗ | 为什么**躲不掉** ✓ |
|---|---|---|
| a | `(24.58,55.4)→(24.58,0)` × `(27.58,9)→(15.38,9)` | 新竖线要落到轨上 ✓ ⇒ 必跨 `J1` 那根 GND 支线 ✓ |
| b | `(24.58,55.4)→(24.58,0)` × `(40.58,43.2)→(15.38,18)` | 同上 ✓（`J1` 的 45° 支线 ✓）|
| c | `(27.38,-43.2)→(74.78,-43.2)` × `(46.58,-8.93)→(46.58,-55.4)` | `VSS↔EPAD` 只能**沿上排脚外侧**（y=-43.2）横过来 ✗ ⇒ 必跨 `RC`（`PD6`）那条竖线 ✓ |
| d | `(188.41,17)→(236.58,17)` × `(209.2,18)→(209.2,-43.2)` | `LED2.c1↔J2.c1` 的直连只能走 y=17 ✓ ⇒ 必跨 `DATA_OUT` 的竖线 ✓（改前那一版走 y=9 ✓，但那样就得**从 J2 身体里穿过去** ✗）|
| e | `(235.38,9)→(235.38,-84.6)` × `(180.38,-57.6)→(244.58,-57.6)` | `J2` 的落点只能改到**左边**（右边被 `J2` 本体挡死 ✗）⇒ 必跨 `5V` 轨 ✓ |
| f / g | 另 2 条是上面 5 条在**同一处**的配对项 ✓（同一根新线跨两根线 ✓）| — |

★ 结论（**按用户定的优先级** ✓「不穿体 ✓ > 交叉数 ✓ > 总长 ✓」✓）：**用 +2 交叉 ＋ 8.9 mm 换"穿体 0"** ✓ —— 允许 ✓，且**逐条记账** ✓（不许静默 ✗ ✓）。

### ⑤ 复现命令 ✓（交付件 = `_work/v76.4_byHand.fzz` ✓，改前留 `_work/v76.4_byHand.pre-bodyfix.fzz` ✓）

```bat
set TOOLS=F:\git\fritzing-parts-langhua\tools
copy _work\v76.4_byHand.fzz _work\v76.4_byHand.pre-bodyfix.fzz                              # 先备份 ✓
py -3.13 %TOOLS%\sch_strip_wires.py _work\v76.4_byHand.pre-dedupe.fzz _work\_r73_strip.fzz  # 与 §五十六～五十九 同一条链 ✓
py -3.13 %TOOLS%\render_sch.py _work\_r73_strip.fzz _work\_r73_base.png --pins-out=_work\_r73_pins.py
py -3.13 gen_schematic_wires.py _work\_r73_strip.fzz _work\_r73_base.svg _work\_r75_gen.fzz --nets=pixel_nets.py ^
    --orig _work\v76.4_byHand.pre-dedupe.fzz --ratio 1.0 --rails --islands=GND --vlanes=5V@29.778 --decoup ^
    --hardbody --corebox --dedupe-symbols --complete-islands --symmerge --mst-merge --bodyoutline   # ★ 新开关在这 ✓
py -3.13 _work\merge_sch.py _work\v76.4_byHand.pre-dedupe.fzz _work\_r75_gen.fzz _work\v76.4_byHand.fzz
py -3.13 _work\_r75_accept.py _work\v76.4_byHand.pre-bodyfix.fzz _work\v76.4_byHand.fzz _work\_r75_accept.txt
py -3.13 %TOOLS%\render_sch.py _work\v76.4_byHand.fzz _work\v76.4_byHand.sch.png             # 交付图 ✓
```

★ **四道验收**（原始输出留档 `_work/_r75_accept.txt` ✓；**5/5** ✓）：
① `pcb_check.py … --nets=pixel_nets.py` ⇒ **判定：✓ 全过** ✓（PCB 一字未动 ✓）；
② `tools\net_group_check.py` ⇒ **exit 0** ✓；
③ `view_bytes_diff.py` ⇒ `pcbView` **74 块** ✓、`breadboardView` **122 块** ✓，**块文本不同 0** ✓，
   拼接哈希 `24141dd900659867` / `8b450fd58b38600c` **两边相同** ✓；＋ `find_gap.py` ⇒ **0 处**不重合 ✓；
④ `sch_probe.py --nets=pixel_nets.py` ⇒ **exit 0** ✓（9 网逐脚 ✓｜备用脚 15 只零连接 ✓｜声明双向 ✓｜
   假接头 0 ✓｜贴脚 0 ✓｜**穿体 0**（⑨ 新增 ✓）｜1 网 1 岛 ✓）；
⑤ `_r73_direct.py` ＋ `sch_body_selftest.py` ⇒ **exit 0** ✓。

★ **中间脚本**（都在 `_work/` ✓）：`diag_body.py`（**诊断**：量"哪些线穿哪个件的本体"＋
把"真实外形"与"旧盒"并排 ✓）、`diag_body2.py` / `_db2_*.txt`（同口径复算 ✓）、`find_ovl.py`、
`find_gap.py`、`xdiff.py`（**交叉集合差** ✓）、`diff_insts.py`（器件位置前后对照 ✓）、
`sch_wirediff2.py`（导线逐段前后对照 ✓）、`_r75_accept.py`（验收打包 ✓）、`_r75_*.log/txt/png`（证据 ✓）。

### ⑥ 零副作用实测 ✓

- **不给 `--bodyoutline`** 重跑同一条链 ⇒ 与本轮**改前**版本**逐字节相同** ✓
  （内层 `.fz` sha1 前 16 位 `adc8ba488f490021`／382044 B ✓ 两边一致 ✓）
  ⇒ 新代码**只在给 `--bodyoutline` 时才改行为** ✓。
- **v40 原命令**（一个新开关都不加 ✓）重跑 ⇒ `pixel-schematic-v40.fzz` 内层 `.fz` **逐字节相同** ✓
  （sha1 `7e2e0f360406a4264769bea7e369922245b075bc`／164725 B ✓ 两边一致 ✓；留档
  `_work/_v40_before.fzz` / `_work/_v40_rerun.fzz` ✓）
  ⇒ 老交付件**不受影响** ✓；★ 另外用**新判据**复核 v40 ⇒ **穿体 0 处 ✓**（不会"修了闸门就回头骂老稿"✗）。

### ⑦ 遗留 ✗（下一手 ✓）

- **同网共线重叠 1 对** ✗（`Wire90015387` 与 `Wire90015388`：`y=9` 上 27.378…27.578 重叠
  **0.2 单位 = 0.056 mm** ✓）—— 发生在 `GND` **同一张网**内 ✓，不是"**不同的**导线重叠"（规则② ✓，生成器
  自检仍报 **0 对** ✓）✗；**几何上肉眼不可见** ✓，也**不漏**端点（`find_gap.py` = 0 ✓）。成因是这条
  `VSS↔J1` 的并线被拆成两段时两端各让了 `2×MIN_SEG` ✓；本轮**不就地手改**（一改就脱离可复现链 ✗）。
- **交叉 11**（目标 ≤7 ✗ 未达 ✓，§五十九 ⑤ 的账继续挂着 ✓）；新增 2 条已在 ④ 逐条记账 ✓。
- **引脚引线的口径改正过程** ✓（记下来 ✗ 别再走回去 ✓）：第一版**把 `class="pin"` 也当"端子"跳过** ✗
  ⇒ 本体只剩方块 ✓ ⇒ `U1` 引脚那一带 3.3 mm 走廊**变成可走** ✗ ⇒ 产出的竖线**横穿那一排引脚引线** ✗
  —— **是渲染器 ④b 当场点出来的** ✓（它那时还在用旧盒 ✓）⇒ 说明"**判据放宽一格，视觉就退一格**" ✗。
  ✓ 现在的口径：**画出来的都是本体外形** ✓（引脚引线算墨迹 ✓、`*terminal` 零尺寸锚点不算 ✓、
  文字不算 ✓），豁免只有"脚边 `pin_r`"这一小块 ✓。

**六十一、第四十四轮（2026-10-09 ✓）：把 `_work/v76.4_byHand.fzz` **发布成受版本控制的交付件** ⇒ `pixel-pcb-v77.fzz` ✓（＋ 渲染图 ✓）⇒ 五道闸门 5/5 ✓、PCB 74 块 ＋ 面包板 122 块**逐字节未动** ✓**

### ① 用户要的是什么 ✓

用户原话 ✓：「**先提交一版吧。然后再继续修改截图中箭头所指的两个问题。**」✓
⇒ 第一步 = 把**当前最新**那份（`_work/v76.4_byHand.fzz` ✓ —— 用户手改换脚 ✓ ＋ 过孔净距修过 ✓ ＋
原理图按 §五十五–§六十 的规则重生成 ✓）**发布**到仓里 ✓，而不是让它一直待在**忽略目录** `_work/` 里 ✓。

### ② 名字怎么选的 ✓（先看仓规 ✗ 不是拍脑袋 ✓）

| 候选 ✓ | 依据（仓里量出来的 ✓） | 取舍 ✓ |
|---|---|---|
| `pixel-pcb-vNN_byHand.fzz` ✗ | ★ `.gitignore` 第 24 行：**`*_byHand.fzz` 一律忽略** ✗（"编辑器里手改的草稿，不是生成物 ✓"） | **不采用** ✗ —— 沿用 `_byHand` 名字等于**当场违反仓规** ✗（要 `-f` 强加 ✗，正是本轮被明令禁止的那一手 ✗）|
| `pixel-schematic-vNN.fzz` ✗ | 那是**自动生成链**（最新 `v40` ✓）；本件是**整块板**（PCB 是用户手布的 ✓），不属那条线 ✓ | 不采用 ✗ |
| ★ **`pixel-pcb-v77.fzz`** ✓ | ① **PCB 交付链**最新是 `v76` ✓ ⇒ 下一个号 = **v77** ✓；② 仓里**手改版的交付件历来就用普通版本号** ✓（`v51_byHand` ⇒ `pixel-pcb-v52`/`v57` ✓、`v65/v66_byHand` ⇒ `pixel-pcb-v67` ✓）；③ §三十五 起就写着「`*_byHand.fzz` 按仓规**不入库** ✓」✓ | **采用** ✓ |

★ 一句话 ✓：**「手工那条线」的区分靠"内容 ＋ README 记账"** ✓，不靠文件名 ✗ —— 因为 `_byHand` 这个名字
在仓规里**本来就不入库** ✗（要改这条仓规先得用户点头 ✗，本轮不动 ✓）。
★ 内层 `.fz` 名照旧 = `v76.4_byHand.fz` ✓ —— 这**也是仓规** ✓（`pixel-pcb-v76.fzz` 的内层就叫
`pixel-pcb-v57_2_byHand.fz` ✓、`v69` 的内层叫 `pixel-pcb-v68.fz` ✓ ⇒ 内层名 = **来源工作件** ✓）。
★ 一并入库的渲染图（照 `v57`…`v69` 的惯例 ✓）：`pixel-pcb-v77_preview.png` ＋ `.svg`（PCB ✓）、
`pixel-pcb-v77_sch.svg`（原理图 ✓ —— 与 `pixel-pcb-v69_sch.svg` 同一个写法 ✓：**内容是 png** ✓）。

### ③ 五道闸门 ✓（**5 / 5** ✓ —— 原始输出留档 `_work/_r76_accept_A.txt` ✓）

- ① `python -X utf8 …\pcb_check.py pixel-pcb-v77.fzz --nets=pixel_nets.py` ⇒ **判定：✓ 全过** ✓；
- ② `python -X utf8 tools\net_group_check.py pixel-pcb-v77.fzz` ⇒ **exit 0** ✓；
- ③ `_work\view_bytes_diff.py …` ⇒ `<pcbView>` **74 块** ✓、`<breadboardView>` **122 块** ✓、
  **块文本不同 0** ✓、拼接哈希 `24141dd900659867` / `8b450fd58b38600c` **两边相同** ✓；＋
  `_work\find_gap.py` ⇒ **0 处**不重合 ✓；
- ④ `_work\sch_probe.py --nets=pixel_nets.py` ⇒ **exit 0** ✓（9 网逐脚 ✓ ｜ 备用脚 15 只零连接 ✓ ｜
  声明双向 ✓ ｜ 假接头 0 ✓ ｜ 贴脚 0 ✓ ｜ **穿体 0** ✓ ｜ 1 网 1 岛 ✓ ｜ 交叉 **11** ｜ 总长 **521.3 mm** ✓）；
- ⑤ `_work\_r73_direct.py` ⇒ `LED2.connector1 ↔ J2.connector1` **3 段 / 19.054 mm 就近直连** ✓；
  ＋ `sch_body_selftest.py` ⇒ **exit 0** ✓。

### ④ 复现命令 ✓

```bat
set TOOLS=F:\git\fritzing-parts-langhua\tools
py -3.13 %TOOLS%\sch_strip_wires.py _work\v76.4_byHand.pre-dedupe.fzz _work\_b0_strip.fzz
py -3.13 %TOOLS%\render_sch.py _work\_b0_strip.fzz _work\_b0_base.png --pins-out=_work\_b0_pins.py
py -3.13 gen_schematic_wires.py _work\_b0_strip.fzz _work\_b0_base.svg _work\_b6_gen.fzz ^
    --nets=pixel_nets.py --orig _work\v76.4_byHand.pre-dedupe.fzz --ratio 1.0 --rails --islands=GND ^
    --vlanes=5V@29.778 --decoup --hardbody --corebox --dedupe-symbols --complete-islands ^
    --symmerge --mst-merge --bodyoutline                                     # ★ 与 §六十 一字不差 ✓
py -3.13 _work\merge_sch.py _work\v76.4_byHand.pre-dedupe.fzz _work\_b6_gen.fzz _work\_b6_out.fzz
py -3.13 _work\_r75_accept.py _work\v76.4_byHand.pre-shape.fzz pixel-pcb-v77.fzz _work\_r76_accept_A.txt
```

★ **零副作用实测** ✓：用**这一条**（不含本轮新开关 `--mst-shape` ✗）跑 ⇒ 与本轮**发布的那一版**
**逐字节相同** ✓（内层 `.fz` sha1 `679f22bc3cd66328327df9ac7587062f5c94b8b1`／385815 B ✓ 两边一致 ✓）；
**v40 原命令**（一个新开关都不加 ✓）重跑 ⇒ `pixel-schematic-v40.fzz` 内层 `.fz` **逐字节相同** ✓
（sha1 `7e2e0f360406a4264769bea7e369922245b075bc`／164725 B ✓ 两边一致 ✓）。

**六十二、第四十五轮（2026-10-09 ✓）：用户在原理图截图上**画了两个红箭头** ✗ ⇒ 查出两处**形状**病根 ✓ ⇒ 新开关 `--mst-shape`（**就近直连按形状优先** ✓）⇒ `_work/v76.4_byHand.fzz` 就地更新 ＋ 交付件 `pixel-pcb-v77.fzz` 同步更新 ⇒ 五道闸门 5/5 ✓、**穿体 0 / 交叉 11 → 11（零新增）/ 总长 521.3 → 505.6 mm / 同网共线重叠 1 → 0 对** ✓**

### ① 用户报的是什么 ✓（**先量出来** ✗ 不许猜 ✓）

用户原话 ✓：两个红箭头 —— **①** 左箭头指 `J1` 第 2/3 脚右边「**有一小段走线先向右、再折回**」✗；
**②** 右箭头指 `LED2.GND`（`LED2.connector1`）→ `J2` 第 2 脚（`J2.connector1`）那条绿线「**在 `J2` 脚下
兜了一圈 / 入口位置不对**」✗（它正是 §五十九 `--mst-merge` 做出来的**就近直连** ✓ —— 方向对 ✓、形状难看 ✗）。

★ 量法 ✓（新探针 `_work/diag_arrows.py` ✓ —— 逐根导线**实例 id / 两端坐标 / 长度 / 层色** ＋
「端点落在**别的导线内部** ⇒ 那是折点」✓）＋ 生成器日志（`_work/_b0_gen_why.txt` ✓ 的 `[why]` 档位对照 ✓）：

| # | 涉事走线（改前 ✓）| 几何 ✓ | 是哪条规则/哪一档定的 ✓ |
|---|---|---|---|
| ① | `GND` 网的**并线对** `U1.connector3 (VSS) ↔ J1.connector1`（`--mst-merge` ✓，曼哈顿 **43.2** ✓）<br>`Wire90015384…87` ＋ 主干 `Wire90015388` | `(58.58,9)→(58.58,12.86)→(27.58,12.86)→(27.58,9)→(15.38,9)`<br>**4 段 / 3 拐点** ✗ ｜ 折返量 `plen − 曼哈顿` = **7.718 单位 = 2.18 mm** ✗✗<br>（两条平行横线相距 **3.859 单位 = 1.09 mm** ✗）| **两处** ✗：<br>· `route_pair()` 的**候选里没有「搭到已布同网导线的端点上」这一族** ✗ ⇒ 后布的 `U1.c3↔U1.c20` 日志原话「**没有一条候选**能与已布的线不重叠 ✗」⇒ 硬闸门 `HARD_OVL` **退回旧候选集** ⇒ 重叠 1 对 ✗；<br>· **抽出重排**只把「重叠」当分（`route_key` 档 ③ `wt = 10×重叠 ＋ 贴脚` ✓）⇒ 治法选了「**把这条并线平移出一条平行车道**」✗✗ |
| ② | `GND` 网的**并线对** `LED2.connector1 ↔ J2.connector1`（曼哈顿 **72.2** ✓）`Wire90015383` | `(236.58,17)→(244.58,9)` = **45° 斜线**，**斜着扎进 `J2.c1`** ✗<br>（`J2.c1` 的法线是 **(-1,0)** ✓ ⇒ 应当**沿引脚延长线方向**进 ✓）| `route_key` **没有「进/出脚那一段的方向」这一档** ✗ ⇒ 斜线**少一个拐点** ✓ ⇒ 档 ⑦ `bends` **1 比 2** ⇒ 抽出重排**主动**把直角折法换成了斜的 ✗✗（greedy 首轮本来选的是对的 ✓：`(180.4,17)→(201.4,17)→(201.4,9)→(244.6,9)` ✓）|

★ 两处**都不是闸门松** ✗（穿体 / 重叠 / 贴脚 一道没退让 ✓）—— 是**形状的选择**缺了两条判据 ✗ ✓。

### ② 规则怎么改的 ✓（新开关 `--mst-shape` ✓ —— **默认关** ✗ ⇒ 不给它**一字节不差** ✓）

★ 作用域 ✓ = **`--mst-merge` 的并线对**（就是用户点名的「**就近直连**」✓）⇒ 别的网 / 别的支线
（轨支线 / 主干 / 补岛 / 车道）**候选与档位一字不动** ✓。✗ **没有**任何一根线写死配置 ✗ ✓。

| 新增 ✓ | 写死的判据 ✓ |
|---|---|
| ★ **同网「搭接」候选** ✓ `tie_cands()` | 把「**走到一棵已布同网导线的一只端点上**」放进候选 ✓（端点对端点 ⇒ Fritzing 认得出连接 ✓，与「T 形搭接」「接管」**同一个机理** ✓）。★★ **安全判据** ✓：把已布同网段看成图（顶点 = 端点 ✓、边 = 段 ✓）⇒ **两个方向都给** ✓：`[a … E]` 时 `E` 必须与 **`b`** 同导体 ✓、`[E … b]` 时 `E` 必须与 **`a`** 同导体 ✓ ⇒ **新线 ＋ 既有导体 一定把两只脚接起来** ✓（✗ 不许“看着接上其实没接”✗）。两个方向都**排除 `E ≈ a` / `E ≈ b`** ✗ —— 那条“锚点直连另一只脚”的**任意角直连**是本仓**已否证**的形状 ✗（实测交叉 8→40 ✗，`candidates()` 头部记着 ✓）。根范围 `曼哈顿 ≤ 曼哈顿(a,b) + 40` 且取前 16 只 ✓（与 `esc_cands` 同一手法 ✓）|
| ★ **两档形状判据** ✓ 插在**交叉数之前** ✓（用户定的优先级：**不穿体 ✓ > 形状合理 ✓ > 交叉数 ✓ > 总长 ✓**）| · `entry_bad` = 两端**斜着扎进引脚**的条数 ✓（0..2 ✓ —— 端点是**已知法线的脚** ✓ **且**挨着它那一段**两个方向分量都不为 0** ✓ ⇒ 记 1 ✓；★ **不**要求“必须沿法线” ✗ —— 贴边脚**横着出脚**是本仓既有画法 ✓，罚它会把形状逼向更差的绕法 ✗）；<br>· `detour` = `plen(path) − 曼哈顿(两端)` 取 `max(0,·)` ✓（= **折返 / 绕弯** ✗ ○ 用户说的“先出再回” ✓；单调楼梯与斜切都是 0 ✓、斜切还能 < 0 ✓ ⇒ 取 max ✓ 免得不小心奖励斜线 ✗）|
| ★ **声明跟着几何走** ✓ | 搭接候选有**反着画**的一支（`[E … b]` ✓）与**半截**的一支（`[a … E]` ✓）⇒ 哪一端真是脚就声明哪一端 ✓、另一端置 **None** ✗（`emit` 里 `("pin", None)` = **裸端点** ✓ ⇒ 由「**同点即连**」那一遍与**端点重合**的同网导线互记连接 ✓ —— 电源轨支线走的就是这条路 ✓）。✗ 不按几何写 ⇒ 会落成**假声明** ✗。抽出重排每次换路也**重算这两端** ✓（含整轮撤回时一起回滚 ✓）|

### ③ 改前 / 改后对照 ✓（两把独立尺子：`sch_probe.py` ✓ ＋ `_work/diag_arrows.py` ✓）

| # | 改前 ✗ | 改后 ✓ |
|---|---|---|
| ① | `(15.38,9)→(27.58,9)→(27.58,12.86)→(58.58,12.86)→(58.58,9)` ✗（4 段 / 3 拐点 / 折返 7.718 单位 ✗）| ✓✓ **`Wire90015384 (27.38,9)→(15.38,9)` 一根** ✓（**1 段 / 0 拐点 / 折返 0** ✓）—— 它**搭在主干 `Wire90015385 (58.58,9)→(27.38,9)` 的端点上** ✓ ⇒ `J1` 第 2 脚到 `U1.VSS` 是**一条直的主干** ✓（用户要的「**合并到同一主干**」✓）|
| ② | `(188.4,17)→(236.6,17)→(244.6,9)` ✗（末段 **45° 斜着扎进 `J2.c1`** ✗）| ✓✓ 末段改成 `(227.38,17)→(235.38,9)` ✓ —— 斜线**收在既有的主干拐角 `(235.38,9)` 上** ✓ ⇒ 进 `J2.c1` 的最后 9.2 单位**复用既有那一段** ✓ ⇒ **沿引脚延长线方向（水平）进脚** ✓ |

| 项 ✓ | **改前** ✗ | **改后** ✓ |
|---|---|---|
| **穿体** ✓ | 0 ✓ | ✓ **0** ✓（**不可退让** ✗ 守住了 ✓）|
| **交叉** ✓ | **11** ✓ | ✓ **11** ✓（**零新增** ✓ —— 逐条账见 ④ ✓）|
| 总长 ✓ | 521.3 mm ✓ | ✓ **505.6 mm** ✓（**−15.7 mm = −3.0%** ✓）|
| 导线根数 ✓ | 48 ✓ | ✓ **45** ✓（少了那 3 段折返 ✗）|
| 同网共线重叠 ✓ | **1 对** ✗（§六十 ⑦ 挂着的遗留 ✓）| ✓ **0 对** ✓✓（**顺手结掉了** ✓）|
| 9 张网逐脚 ✓ | ✓ 9/9 ✓ | ✓ **9/9** ✓ |
| 备用脚 15 只零连接 ✓ | ✓ | ✓ **同** ✓ |
| 声明双向自洽 ✓ | ✓ | ✓ **同** ✓ |
| 跨网假接头 ✓ | 0 ✓ | ✓ **0** ✓ |
| 贴脚（<0.15 mm ✓）| 0 ✓ | ✓ **0** ✓（抽出重排的全局分也从 **7** 降到 **3** ✓）|
| 每张网 1 个岛 ✓ | ✓ 9/9 ✓ | ✓ **9/9** ✓ |
| 接地符号 × 岛 ✓ | 2 个（每岛 1 ✓）| ✓ **2 个** ✓（每岛 1 ✓）|
| **`LED2.connector1 ↔ J2.connector1` 就近直连** ✓ | ✓ 3 段 / **19.054 mm** ✓ | ✓ **4 段 / 19.054 mm** ✓（**总长一样** ✓ —— 多出的那"1 段"是因为末段**与主干共用**了 ✓，见 ④ 记账 ✓）|
| `pcbView` / `breadboardView` ✓ | — | ✓ **逐字节相同** ✓（74 块 / 122 块，`24141dd900659867` / `8b450fd58b38600c` ✓）|

### ④ 逐条记账 ✓（**零新增交叉** ✓ —— 4 条是"**同一处、端点挪了一点**"✓）

`_work/xdiff.py`（交叉集合差 ✓，方位四舍五入到 0.01 单位 ✓）：**改前 11 ｜ 改后 11** ✓

| − 改前有 / 改后没有 ✗ | ＋ 改后有 / 改前没有 ✗ | 是不是**新增** ✓ |
|---|---|---|
| `(22.83,18)→(22.83,-57.6)` × `(27.58,9)→(15.38,9)` | `(22.83,18)→(22.83,-57.6)` × `(27.38,9)→(15.38,9)` | ✗ **同一处** ✓（那根并线的端点从 27.58 挪到 27.38 ✓）|
| `(24.58,55.4)→(24.58,0)` × `(27.58,9)→(15.38,9)` | `(24.58,55.4)→(24.58,0)` × `(27.38,9)→(15.38,9)` | ✗ **同一处** ✓（同上 ✓）|
| `(24.58,55.4)→(24.58,0)` × `(40.58,43.2)→(15.38,18)` | `(24.58,55.4)→(24.58,0)` × `(48.03,43.2)→(22.83,18)` | ✗ **同一处** ✓（`5V` 那条并线的走法变了 ✓，跨的还是 `(24.58,…)` 那根 ✓）|
| `(188.41,17)→(236.58,17)` × `(209.2,18)→(209.2,-43.2)` | `(188.55,17)→(227.38,17)` × `(209.2,18)→(209.2,-43.2)` | ✗ **同一处** ✓（`LED2` 那条并线的横段变短了 ✓；`DATA_OUT` 那根竖线没动 ✓）|

★ 另外两条"账" ✓：① `LED2.c1↔J2.c1` 由 **3 段变 4 段** ✓ —— **总长一样（19.054 mm = 几何最短 ✓）** ✓，
多出的那一段是**与主干共用**的 `(235.38,9)→(244.58,9)` ✓（这正是「合并到同一主干」的代价 ✓，记账 ✓）；
② 那条 **45° 斜线还在** ✓（`(227.38,17)→(235.38,9)` ✓）—— 但它**不再挨着任何脚** ✓（收在主干拐角上 ✓）
⇒ `entry_bad` 管的是「**斜着扎进脚**」✗，不是「不许有 45°」✗（45° 是本仓**允许**的画法 ✓）。

### ⑤ 验收（**五道** ✓ —— 原始输出留档 `_work/_r76_accept_B.txt` ✓）**5 / 5 ✓**

- ① `python -X utf8 …\pcb_check.py pixel-pcb-v77.fzz --nets=pixel_nets.py` ⇒ **判定：✓ 全过** ✓（PCB 一字未动 ✓）；
- ② `python -X utf8 tools\net_group_check.py pixel-pcb-v77.fzz` ⇒ **exit 0** ✓；
- ③ `_work\view_bytes_diff.py` ⇒ `<pcbView>` **74 块** ✓、`<breadboardView>` **122 块** ✓、**块文本不同 0** ✓、
  拼接哈希 `24141dd900659867` / `8b450fd58b38600c` **两边相同** ✓；＋ `find_gap.py` ⇒ **0 处**不重合 ✓；
  ★ **第三路独立证据** ✓：拿**新文件**重渲 `render_pcb.py` ⇒ `pixel-pcb-v77_preview.svg`/`.png`
  与已入库的**逐字节相同** ✓（sha1 `4dfda0e8…` / `0bfbc253…` ✓）⇒ PCB 真的没动 ✓；
- ④ `_work\sch_probe.py --nets=pixel_nets.py` ⇒ **exit 0** ✓（9 网逐脚 ✓ ｜ 备用脚 15 只零连接 ✓ ｜
  声明双向 ✓ ｜ 假接头 0 ✓ ｜ 贴脚 0 ✓ ｜ **穿体 0** ✓ ｜ 1 网 1 岛 ✓ ｜ **交叉 11** ✓ ｜
  总长 **505.6 mm** ✓ ｜ **同网共线重叠 0 对** ✓）；
- ⑤ `_work\_r73_direct.py` ⇒ `LED2.connector1 ↔ J2.connector1` **几何最短连通** ✓（4 段 / 19.054 mm ✓）；
  ＋ `sch_body_selftest.py` ⇒ **exit 0** ✓；＋ **新** `_work\_ut_tie.py`（`tie_cands()` 的**单元自测** ✓，
  不用任何 `.fzz` ✓ —— 与 `sch_body_selftest.py` 同一手法 ✓）⇒ **exit 0** ✓（含「**反向那一支**」
  `[(27.378,9),(15.378,9)]` **必须给出** ✓ 与「`b` 不在同网导线上 ⇒ **一条都不给**」✓）。

### ⑥ 复现命令 ✓（交付件 = `_work/v76.4_byHand.fzz` ✓，改前留 `_work/v76.4_byHand.pre-shape.fzz` ✓）

```bat
set TOOLS=F:\git\fritzing-parts-langhua\tools
copy _work\v76.4_byHand.fzz _work\v76.4_byHand.pre-shape.fzz                                   # 先备份 ✓
py -3.13 %TOOLS%\sch_strip_wires.py _work\v76.4_byHand.pre-dedupe.fzz _work\_b0_strip.fzz      # 与 §六十 同一条链 ✓
py -3.13 %TOOLS%\render_sch.py _work\_b0_strip.fzz _work\_b0_base.png --pins-out=_work\_b0_pins.py
py -3.13 gen_schematic_wires.py _work\_b0_strip.fzz _work\_b0_base.svg _work\_b5_gen.fzz ^
    --nets=pixel_nets.py --orig _work\v76.4_byHand.pre-dedupe.fzz --ratio 1.0 --rails --islands=GND ^
    --vlanes=5V@29.778 --decoup --hardbody --corebox --dedupe-symbols --complete-islands ^
    --symmerge --mst-merge --bodyoutline --mst-shape                             # ★ 本轮新开关在这 ✓
py -3.13 %TOOLS%\merge_sch.py _work\v76.4_byHand.pre-dedupe.fzz _work\_b5_gen.fzz _work\_b5_out.fzz
copy _work\_b5_out.fzz _work\v76.4_byHand.fzz                                   # 就地更新 ✓
copy _work\_b5_out.fzz pixel-pcb-v77.fzz                                        # 交付件同步 ✓
py -3.13 _work\_r75_accept.py _work\v76.4_byHand.pre-shape.fzz pixel-pcb-v77.fzz _work\_r76_accept_B.txt
py -3.13 _work\_ut_tie.py                                                       # 新规则的单元自测 ✓
py -3.13 _work\diag_arrows.py _work\v76.4_byHand.fzz --pins=_work\_b0_pins.py   # 两处形状（量出来 ✓）
```

★ **零副作用实测** ✓：**不给 `--mst-shape`** 跑同一条链 ⇒ 与**改前那一版**（`pre-shape` ✓）**逐字节相同** ✓
（内层 `.fz` sha1 `679f22bc3cd66328327df9ac7587062f5c94b8b1`／385815 B ✓ 两边一致 ✓；留档
`_work\_b6_out.fzz` ✓）⇒ 新代码**只在给 `--mst-shape` 时才改行为** ✓；
**v40 原命令**重跑 ⇒ `pixel-schematic-v40.fzz` 内层 `.fz` **逐字节相同** ✓（sha1
`7e2e0f360406a4264769bea7e369922245b075bc`／164725 B ✓ 两边一致 ✓，留档 `_work\_v40_rerun2.fzz` ✓）。

★ **中间脚本**（都在 `_work/` ✓，本轮新增 2 个 ✓）：`diag_arrows.py`（**诊断**：逐根导线报实例 id /
两端 / 长度 / 层色 ＋ 「端点落在别的导线内部 ⇒ 折点」＋ 进脚方向 ✓）、`crop_sch.py`（按 **sketch 坐标**
裁图放大 ✓ —— 用渲染器已知的 viewBox ✓ 不用标定 ✓）、`_ut_tie.py`（`tie_cands()` 单元自测 ✓）、
`_b1_*_after.png` / `_b0_*_before.png`（**两处特写的前后对照图** ✓）、`_r76_accept_A.txt` / `_r76_accept_B.txt`
（两道验收的原始输出 ✓）、`_b0_gen_why.txt`（`--why` 的**档位对照** ✓）、`_b3/_b4_gen.txt`
（`RIP_DIAG` / `TIE_DIAG` 逐次决策 ✓ —— 「这条并线拿到几只端点、换不换路」不再靠猜 ✓）、
`_b5/_b6_gen.txt`（改后 / 不给新开关的两条日志 ✓）。

### ⑦ 遗留 ✗（下一手 ✓）

- **交叉 11**（目标 ≤7 ✗ 未达 ✓）—— 本轮**零新增** ✓、但也没降 ✓；账继续挂在 §五十九 ⑤ / §六十 ④ ✓。
- 那条 **45° 斜线**（`(227.38,17)→(235.38,9)` ✓）是**故意留的** ✓（45° 是允许画法 ✓、它不挨脚 ✓）；
  要"一根斜线都不许"就得上更严的形状档 ✗ —— 本轮**不做** ✗（会牵动全局交叉账 ✗）。
- `--mst-shape` 只对**并线对**生效 ✓（别的支线仍是老档位 ✓）—— 若哪天想全局推广 ✗，
  先量**交叉账**再动 ✗（本轮已证明：形状档压在交叉档之前 ⇒ 需要重新算全局 ✓）。
- `_work/_ut_tie.py` 仍留在**忽略目录** `_work/` 里 ✗ —— 若要让新规则有**入库**的机器守 ✓，
  下一步可以照 `tools/sch_body_selftest.py` 的办法**上收**（本项目仓没有 tests 目录 ✗，要先定放哪 ✓）。

**六十三、第四十六轮（2026-10-09 ✓）：用户「**线距作为一个参数**」⇒ 新参数 `--wire-gap=<mm>`（缺省 **1.0 mm** ✓、范围 **[0.254, 2.54] mm** ✓）＋ 新硬闸门「**线↔线最小净距 ≥ 该值**」＋ 验收探针第 ⑪ 条 ⇒ 交付件 `pixel-pcb-v78.fzz` ✓（`_work/v76.4_byHand.fzz` 同步 ✓）⇒ 六道验收 **6/6** ✓、**穿体 0** ✓、**低于阈值的对数 0 对** ✓、最小净距 **0.2822 → 1.2841 mm** ✓、交叉 **11 → 14**（**+3 逐条记账** ✓）、总长 **505.6 → 508.5 mm** ✓**

### ① 用户报的是什么 ✓（**先量出来** ✗ 不许猜 ✓）

用户原话 ✓：「**线距作为一个参数吧？缺省 1mm，线距最小值 0.254mm，最大值 2.54mm。**」✓
背景 ✓：他在原理图上看到「**有两处走线贴得比较近**」✗ —— 而当时的硬闸门里只有
「**不重叠（= 0）**」✓ ＋「不贴脚 ≥0.15 mm」✓ ＋ 不穿体 ✓ ＋ 不压文字 ✓，**没有「线↔线净距」**✗✗。

★ 量法 ✓（新写一把**临时量尺** `_work/_gap_measure.py` ✓ —— 只读 ✓，判据**不自带** ✗、
调库里的**唯一那份** `sch_geom.conductor_clearance` ✓）：

| 档 ✓ | 实测对数（`_work/v76.4_byHand.pre-wiregap.fzz` = v77 ✓） |
|---|---|
| **全图最小净距** | **0.9999 单位 = 0.2822 mm** ✗（`244.58,18→209.20,18` 的 `DATA_OUT` 与 `188.55,17→227.38,17` 的 `GND` ✓ —— **两条平行横线只差 0.28 mm** ✗） |
| 低于 0.254 mm（用户给的**下限** ✓） | **0** 对 ✓（所以**旧版本来就过最小档** ✓ —— 见 ⑦ ✓） |
| 低于 1.0 mm（**新缺省** ✓） | **9** 对 ✗（另 7 对是 `DATA_IN` 车道 `x=24.58` 挤在 `x=22.83`(5V) 与 `x=27.38`(GND) 之间 ✓：**0.4939 mm / 0.7902 mm** ✗、以及 `y=-57.60` 的 5V 轨与 `y=-55.40` 的 `RC` 支线 **0.6209 mm** ✗） |

### ② 参数与**夹取**行为 ✓（`gen_schematic_wires.py` ✓）

| 项 ✓ | 口径（写死 ✓，可复核 ✓） |
|---|---|
| 开关 | **`--wire-gap=<mm>`** ✓（`--wire-gap 1.0` 也收 ✓ —— `--label` 那条教训 ✓） |
| 缺省 | **1.0 mm** ✓（用户定 ✓）= 3.5433 单位 ✓ |
| 范围 | **[0.254, 2.54] mm** ✓（用户定 ✓）；**超出 ⇒ 夹到边界 ＋ 打印警告** ✓（不静默 ✗、不崩 ✗）；**不是数** ⇒ 警告 ＋ 退回缺省 ✓ |
| **关掉** | **`--wire-gap=0`**（或负数 ✓）⇒ 闸门**关** ✓ = **一键回到旧行为** ✓ |
| 内部单位 | 一律用 **sketch 单位** ✓（`U_PER_MM = 90/25.4` ✓）—— 与 `used` / 全部判据**同一把尺子** ✓ |
| 优先级 | 用户定的次序里，**「不重叠(=0)」升级成「≥ `--wire-gap`」** ✓ —— 位置**仍在交叉数之前** ✓（与 `HARD_OVL` 同一格 ✓） |

### ③ 「搭接例外」是怎么实现的 ✓（**用户点名** ✓：搭接/并线**必须放行** ✗ 否则把功能打死 ✗）

★ 三个函数 ✓（**都在库仓 `tools/sch_geom.py`** ✓ —— 判据**只许一份** ✗）：

| 函数 ✓ | 干什么 ✓ | 为什么要它 ✗ |
|---|---|---|
| `merge_conductors()` ✓ | 同网 ＋ 共端点 ＋ 近共线（`|sin| ≤ 0.06` ✓）的**一串段并成一条直线段** ✓ | ✗ 一条「轨」在文件里是**一串** `<instance>` ✓（`365`＋`366`＋`367` ✓）⇒ 逐根比净距会把**它自己那两节**量成 **0.107 mm** ✗（**假警报** ✗）；并入后**同一根导体内部不比自己** ✓ |
| `joined()` ✓ | 两段**是不是在一点上接起来** ✓：①共端点 ✓（**但「共线 ＋ 同侧」不算** ✗ —— 那是**压在一起** ✗）②一端落在对方**内部**且**不平行**（T 形 ✓） | 搭接 / 接管 / 电源轨 T 形支线 / 连续段**都是接头** ✓ ⇒ 罚它们等于**把搭接打死** ✗✗ |
| `gap_pair_bad()` ✓ | **接头放行** ✗ ／ **横穿放行** ✗（真交叉 ✓ —— 那是「交叉」✓，另有账 ✓）／ 其余 `< gap` ⇒ **不足** ✗ | 用户只罚「**平行/邻近**」那种贴太近 ✓ —— 横穿本来就不该罚（罚了全局交叉一条都画不出来 ✗） |

★ 生成器里的调用点 ✓：`gap_hard_bad()` ✓（**与 `HARD_OVL`/`HARD_CLEAR` 同一套路** ✓：
**只删候选** ✗、**不动**代价函数与档位次序 ✓；删到一条不剩 ⇒ 保留旧候选集 ＋ 告警 ✓ 不许接不上 ✗）。
挂进**全部**候选选择点 ✓：`route_pair()` 的闸门链 ✓ ＋「轨支线 / 竖直车道 / 共享竖线 / 接管 /
兜底位置 / 打补线（`--complete-islands`）」六处 ✓ —— 一处不漏 ✗（漏一处那个 phase 造出来的线就是漏洞 ✓）。

### ④ ★ 顺带治掉的一个**新病** ✓（`--wire-gap` 换候选集之后才暴露 ✓）

改完 `--wire-gap` 第一次跑 ⇒ 自检报「**不同的导线重叠 1 对**」✗（退出码 1 ✓）：`LED2.c1↔J2.c1`
那条**母线**被逼着**一路横到 `J2.c1`** ✓，而 `J2.c1` **本来早有一条轨支线** `(244.6,9)→(235.4,9)` ✗
⇒ 尾巴 **9.2 单位共线重叠** ✗✗。
★ 治法 ✓（**能证明无损才做** ✓）：**剪掉重复那一截** ✓ —— 剪点 = `(235.4,9)`（支线那只端点 ✓）
⇒ 母线**仍然端点到端点**接在支线上 ✓、`J2.c1` 的铜由支线提供 ✓ ⇒ **连通性一点没变** ✓。
落成代码 = `_trim_overlap_tails()` ✓（口径保守 ✓：同网 ✓、`near_overlap` ✓、**一条整条落在另一条里** ✓、
**恰好一只内点** ✓、只剪 `path` 的**最后一段** ✓；不满足 ⇒ **不动 ＋ 不静默** ✗）。
★ 另加一条**候选**（第四手 ✓）：`tie_cands()` 现在也给「**借已有通道拐到 `E`**」的形状 ✓
（`[a,(x,a.y),(x,E.y),E]` ✓，`x` 取夹在 `a` 与 `E` 之间最近的 2 条通道 ✓）—— **只多给候选** ✗ ⇒ 老形状一条不少 ✓（单调 ✓）。

### ⑤ 改前 / 改后对照 ✓（三把独立尺子：生成器自检 ✓ ＋ 验收探针 ⑪ ✓ ＋ `_gap_measure.py` ✓）

| 项 ✓ | **改前** ✗（`pre-wiregap` = v77 ✓） | **改后** ✓（`pixel-pcb-v78.fzz` ✓） |
|---|---|---|
| **全图最小净距** ✓ | **0.9999 单位 = 0.2822 mm** ✗ | ✓✓ **4.5500 单位 = 1.2841 mm** ✓ |
| **低于 1.0 mm 的对数** ✓ | **9 对** ✗ | ✓✓ **0 对** ✓ |
| **穿体** ✓ | 0 ✓ | ✓ **0** ✓（**不可退让** ✗ 守住了 ✓） |
| 交叉 ✓ | **11** ✓ | **14** ✗（**+3** ✓ —— 逐条账见 ⑥ ✓） |
| 总长 ✓ | **505.6 mm** ✓ | **508.5 mm** ✓（**+2.9 mm = +0.6%** ✓） |
| 导线根数 ✓ | 45 ✓ | 46 ✓ |
| 同网共线重叠 ✓ | 0 对 ✓ | ✓ **0 对** ✓（中间一度 1 对 ✗，见 ④ ✓） |
| 9 张网逐脚 ✓ | ✓ 9/9 ✓ | ✓ **9/9** ✓ |
| 备用脚 15 只零连接 ✓ | ✓ | ✓ **同** ✓ |
| 声明双向自洽 ✓ | ✓ | ✓ **同** ✓ |
| 跨网假接头 ✓ | 0 ✓ | ✓ **0** ✓ |
| 贴脚（<0.15 mm ✓） | 0 ✓ | ✓ **0** ✓ |
| 每张网 1 个岛 ✓ | ✓ 9/9 ✓ | ✓ **9/9** ✓ |
| 接地符号 × 岛 ✓ | 2 个（每岛 1 ✓） | ✓ **2 个** ✓ |
| `pcbView` / `breadboardView` ✓ | — | ✓ **逐字节相同** ✓（74 块 / 122 块，`24141dd900659867` / `8b450fd58b38600c` ✓） |

### ⑥ 交叉 **+3** 的逐条账 ✓

`_work/xdiff.py`（交叉集合差 ✓，方位四舍五入到 0.01 单位 ✓）：**改前 11 ｜ 改后 14** ✓ ——
★ 其中 **6 处**是「**同一处、端点挪了一点**」✓（坐标变了、不是新增 ✗：`RC` 支线的横段整体下移 ✓、
`DATA_IN` 车道整体右移 ✓、`LED2↔J2` 母线改走 `y=9` ✓ —— 各自换来换去配成对 ✓）；**真正新增 3 条** ✓：

| # | 新增哪一条 ✗ | 为什么**躲不掉** ✓（用户的优先级：**线距 > 交叉** ✓） |
|---|---|---|
| a | `(22.83,-57.60)→(180.00,-57.60)`（5V 轨）× `(46.58,-8.93)→(46.58,-62.60)`（RC） | `RC` 那条横线原来在 `y=-55.40` ✓ ⇒ 离 5V 轨（`y=-57.60`）只有 **2.2 单位 = 0.62 mm** ✗ ⇒ 必须下移 ⇒ 它的竖直段**跨过** 5V 轨 ✓（躲不掉 ✓：另一侧 `y=-52.6` 不在通道上 ✓） |
| b | `(22.83,-57.60)→(180.00,-57.60)` × `(83.78,-62.60)→(83.78,-43.20)` | 同上**同一条** `RC` 支线的另一端 ✓（两条同因 ✓） |
| c | `(27.38,9.00)→(27.38,-43.20)`（GND）× `(34.78,0.00)→(15.38,0.00)`（DATA_IN） | `DATA_IN` 车道原来在 `x=24.58` ✓ ⇒ 离 5V(`22.83`) **1.75 单位** ✗、离 GND(`27.38`) **2.8 单位** ✗ ⇒ 必须挪到 `x=34.78` ✓ ⇒ 它那条水平段**跨过** `x=27.38` 的 GND 竖线 ✓（躲不掉 ✓：往左更挤 ✗） |

★ 结论 ✓：**用 +3 交叉 ＋ 2.9 mm 换「最小净距 0.28 → 1.28 mm、低于阈值 0 对」** ✓ —— 按用户定的
优先级（**线距是硬约束** ✓、排在交叉数**之前** ✓）允许 ✓，且**逐条记账** ✓（不许静默 ✗）。

### ⑦ ★ 诚实记账：**旧行为怎么一键回去** ✓ ＋ **v40 影响实测** ✓

| 谁 ✓ | 实测 ✓ |
|---|---|
| **`--wire-gap=0`** ✓（关掉 ✓） | 跑同一条链 ⇒ 与**改前那一版**（`pre-wiregap` ✓）**逐字节相同** ✓（内层 `.fz` sha1 `53eaa863605c49dca2e24b110bee5c40d74d717e`／382552 B ✓ 两边一致 ✓；留档 `_work/_g6_out.fzz` ✓） |
| **`--wire-gap=0.254`** ✓（用户的**最小档** ✓） | **也逐字节相同** ✓（sha1 同上 ✓，留档 `_work/_gc01_out.fzz` ✓）—— 因为旧版的最小净距 **0.2822 mm 本来就 ≥ 0.254 mm** ✓ ⇒ 闸门**没有可删的候选** ✓（量出来的事实 ✓，不是硬压 ✓） |
| **不给开关** ✓（= 新缺省 1.0 mm ✓） | **会改产物** ✗ —— 这正是本轮的本意 ✓：`_work/v76.4_byHand.fzz` ＝ `pixel-pcb-v78.fzz` ✓（sha1 `31da4641ee367a135f4d97e365749bdfff609590`／383802 B ✓） |
| **`--wire-gap=9`** ✓（**超上限** ✓） | 警告 ＋ **夹到 2.54 mm** ✓ 后照跑 ⇒ 自检如实报 **15 对低于 2.54 mm** ✗ ⇒ **退出码 1** ✓（**不许硬压成过** ✗；即“2.54 mm 这一档本板做不到”✓） |
| **`--wire-gap=0.1`** ✓（**低于下限** ✓） | 警告 ＋ **夹到 0.254 mm** ✓ ⇒ 最小净距 **0.2822 mm ≥ 0.254 mm** ✓、**低于阈值 0 对** ✓、交叉 **11** ✓ ⇒ **退出码 0** ✓ |
| ★ **v40 有没有被影响** ✓ | **逐字节相同** ✓✓（原命令重跑 ⇒ `pixel-schematic-v40.fzz` 内层 `.fz` sha1 `7e2e0f360406a4264769bea7e369922245b075bc`／164725 B ✓ 两边一致 ✓，留档 `_work/_v40_gap.fzz` ✓）—— ★ **为什么** ✓：v40 自己那一版的最小净距就有 **7.2021 单位 = 2.0326 mm** ✓（`_work/_v40_gap.txt` ✓）⇒ 新闸门**一条候选都没删** ✓（**如实报** ✓，不是“压成相同”✗） |

### ⑧ 六道验收 ✓（**6 / 6** ✓ —— 原始输出留档 `_work/_r78_accept.txt` ✓）

`py -3.13 _work\_r78_accept.py _work\v76.4_byHand.pre-wiregap.fzz pixel-pcb-v78.fzz _work\_r78_accept.txt`

| # | 项 ✓ | 结果 ✓ |
|---|---|---|
| ① | `tools/pcb_check.py pixel-pcb-v78.fzz --nets=pixel_nets.py` | ✓ **判定：✓ 全过** ✓（PCB 一字未动 ✓） |
| ② | `tools/net_group_check.py pixel-pcb-v78.fzz` | ✓ **exit 0** ✓（Fritzing 认得出每张网 ✓） |
| ③ | `_work/view_bytes_diff.py` ＋ `_work/find_gap.py` | ✓ **两个视图逐字节相同** ✓（74 / 122 块 ✓）｜ 端点不重合 **0** 处 ✓ |
| ④ | `_work/sch_probe.py … --nets=pixel_nets.py`（含**新** ⑪ ✓） | ✓ **exit 0** ✓：⑪ **全图最小净距 4.5500 单位 = 1.2841 mm ≥ 1.000 mm** ✓、**低于阈值的对数 0 对** ✓／穿体 0 ✓／1 网 1 岛 ✓／接地符号每岛 1 ✓／交叉 14 ✓／总长 508.5 mm ✓ |
| ⑤ | `_work/_r73_direct.py` ＋ 库仓 `sch_body_selftest.py` ＋ ★ **新** `_work/_ut_gap.py` | ✓ **exit 0** ✓（⑧ 条判据全过 ✓：合并 ✓ / 接头放行 ✓ / 横穿不计 ✓ / **重叠不放行** ✓） |
| ⑥ | ★ **新** `_work/_gap_measure.py`（改前 / 改后各一遍 ✓） | ✓ 改前 **0.2822 mm、9 对** ✗／改后 **1.2841 mm、0 对** ✓ |

### ⑨ 复现命令 ✓（交付件 = `_work/v76.4_byHand.fzz` ＝ `pixel-pcb-v78.fzz` ✓，改前留 `_work/v76.4_byHand.pre-wiregap.fzz` ✓）

```bat
set TOOLS=F:\git\fritzing-parts-langhua\tools
copy _work\v76.4_byHand.fzz _work\v76.4_byHand.pre-wiregap.fzz                              # 先备份 ✓
py -3.13 %TOOLS%\sch_strip_wires.py _work\v76.4_byHand.pre-dedupe.fzz _work\_b0_strip.fzz   # 与 §六十～六十二 同一条链 ✓
py -3.13 %TOOLS%\render_sch.py _work\_b0_strip.fzz _work\_b0_base.png --pins-out=_work\_b0_pins.py
py -3.13 gen_schematic_wires.py _work\_b0_strip.fzz _work\_b0_base.svg _work\_g9_gen.fzz ^
    --nets=pixel_nets.py --orig _work\v76.4_byHand.pre-dedupe.fzz --ratio 1.0 --rails --islands=GND ^
    --vlanes=5V@29.778 --decoup --hardbody --corebox --dedupe-symbols --complete-islands ^
    --symmerge --mst-merge --bodyoutline --mst-shape                 # ★ 线距走缺省 1.0 mm ✓（要改就加 --wire-gap=<mm> ✓）
py -3.13 %TOOLS%\merge_sch.py _work\v76.4_byHand.pre-dedupe.fzz _work\_g9_gen.fzz _work\_g9_out.fzz
copy _work\_g9_out.fzz _work\v76.4_byHand.fzz                                    # 就地更新 ✓
copy _work\_g9_out.fzz pixel-pcb-v78.fzz                                         # 交付件 ✓
py -3.13 %TOOLS%\render_sch.py pixel-pcb-v78.fzz pixel-pcb-v78_sch.png          # 原理图预览 ✓（＋ `copy …v78_sch.png …v78_sch.svg` ✓ 照 §六十一 惯例 ✓）
py -3.13 %TOOLS%\render_pcb.py pixel-pcb-v78.fzz pixel-pcb-v78_preview.svg --png  # PCB 预览 ✓（PCB 没动 ⇒ 与 v77 的预览**逐字节相同** ✓）
py -3.13 _work\_r78_accept.py _work\v76.4_byHand.pre-wiregap.fzz pixel-pcb-v78.fzz _work\_r78_accept.txt
```

★ **中间脚本**（都在 `_work/` ✓，本轮新增 4 个 ✓）：`_gap_measure.py`（**临时量尺** ✓：按**并入后的
导体**量全图最小净距 ＋ 低于阈值对数 ✓，只读 ✓）、`_ut_gap.py`（**判据单元自测** ✓，不用任何 `.fzz` ✓）、
`_r78_accept.py`（六道验收一次跑齐 ✓）、`crop_sch.py`（**已在 §六十二** ✓ 裁前后对照图 ✓）、
`_g0_sch.png` / `pixel-pcb-v78_sch.png`（改前 / 改后整图 ✓）、`_g1_spotB_*.png` / `_g1_spotC_*.png`
（**两处特写的前后对照** ✓ —— 见 ⑩ ✓）、`_gc01_*` / `_gc9_*` / `_g6_*` / `_v40_gap.*`（**边界档 / 零副作用 /
v40** 三次实测留档 ✓）。

### ⑩ 用户看到的那两处：特写前后对照 ✓（`_work/` 里 ✓，按已知 viewBox 裁 ✓ 不标定 ✓）

| 处 ✓ | 改前 ✗ | 改后 ✓ |
|---|---|---|
| **① `DATA_OUT` × `GND`**（图右下 ✓） | `_work/_g1_spotB_before.png` ✓：两条横线**只差 1.0 单位 = 0.28 mm** ✗ ⇒ 看着像**一根粗线** ✗ | `_work/_g1_spotB_after.png` ✓：GND 母线改走 **`y=9`** ✓ ⇒ 离 `DATA_OUT`（`y=17`）**8 个单位 = 2.26 mm** ✓，两条线一眼分得开 ✓ |
| **② `DATA_IN` 车道挤在 5V / GND 之间**（图左下 ✓） | `_work/_g1_spotC_before.png` ✓：蓝线 `x=24.58` **夹在** 红线 `x=22.83` 与 黑线 `x=27.38` 之间 ✓（**1.75 / 2.8 单位** ✗） | `_work/_g1_spotC_after.png` ✓：蓝线挪到 **`x=34.78`** ✓ ⇒ 离红线 **11.95**、离黑线 **7.4** 单位 ✓（两根都 ≥ 3.54 单位 ✓） |

### ⑪ 遗留 ✗（下一手 ✓）

- **交叉 14**（目标 ≤7 ✗ 未达 ✓）—— 本轮 **+3 且逐条记账** ✓（都是「线距优先」逼出来的 ✓，见 ⑥ ✓）；
  要真降下来，得让 `RC` 那条支线走**上侧** / 给 `DATA_IN` 找一个**更右且不跨 GND** 的车道 ✗
  —— 都属于**全局重排** ✗，本轮**不做** ✗（会牵动全部账 ✓）。
- `--wire-gap=2.54`（上限档）**本板做不到** ✓（15 对不足 ✓）—— 如实报出 ✓；这是**参数范围**允许、
  但**几何不允许** ✗（`J1/J2/U1` 的引脚行距本身就只有 1.0～2.8 单位 ✓）。
- `_ut_gap.py` 仍留在**忽略目录** `_work/` 里 ✗ —— 与 `_ut_tie.py` 同一处境 ✓；要入库得先定
  「本项目仓的 tests 放哪」✓（§六十二 ⑦ 同一条 ✓）。
- ★ **`--wire-gap` 只调「已有闸门里的那一格」** ✗：它**不改**档位次序 ✓、**不改**代价函数 ✓
  —— 若哪天想让它**参与软代价**（比如“尽量 ≥ 1.5 mm”）✗，先量交叉账再动 ✓。

**六十四、第四十七轮（2026-10-09 ✓）：把两个单元自测**入库** ✓ ⇒ 定仓规「**测试在哪 / 怎么跑**」✓**
（**先做的一件小事** ✓ —— 主任务是 §六十五 的降交叉 ✓）

### ① 用户要的是什么 ✓

用户原话 ✓：「`_ut_gap.py`（测 `tools/sch_geom.py` 的判据 ✓）与 `_ut_tie.py`（测
`gen_schematic_wires.py` 的 `tie_cands` ✓）现在只在**被忽略目录**里 ✗ ⇒ 请**定一个仓规的
测试位置**并入库 ✓（建议：工具库放 `tools/tests/`、项目仓放 `hardware/pixel/tests/` ✓；
把既有的 `tools/sch_body_selftest.py` 一并归到同一约定里 ✓），保持**零第三方依赖** ✓、
每个测试脚本自带 `exit 0/1` ✓，并给一个**一行命令跑全部**的 runner ✓；
入库后 `_work/` 里那两份**删掉** ✓；README 相应位置写明「**测试在哪、怎么跑**」✓」。

### ② 定下来的仓规 ✓（一句话）

| 项 ✓ | 口径 ✓ |
|---|---|
| **位置** ✓ | **通用工具的测试 = 库仓 `fritzing-parts-langhua/tools/tests/`** ✓；**项目自己的测试 = 本仓 `hardware/pixel/tests/`** ✓ —— ✗ 不再放 `_work/`（**被忽略** ✗ ⇒ 两份真源 ✓）✗ |
| **命名** ✓ | 保留 **`*_selftest.py`** ✓ —— ✗ **故意不叫 `test_*.py`** ✗（pytest 会收集它、被模块级 `SystemExit` 打崩 ✓；这条从 `pcb_curve_selftest.py` 头上就有 ✓，现在收进仓规 ✓）|
| **依赖** ✓ | **零第三方依赖** ✓（只用标准库 ✓）；每个脚本**自带 `exit 0/1`** ✓（全过 0 ✓、任一不过 1 ✓ 并逐条报出 ✓）|
| **路径** ✓ | 一律**按 `__file__` 相对定位** ✓（✗ 不写死机器路径 ✗）；项目侧找库仓工具**只走 `toolpaths.py`** ✓（唯一实现 ✓，`FRITZING_TOOLS` 可覆盖 ✓）|
| **一行跑全部** ✓ | `py -X utf8 tests\run_all.py` ✓（本仓 ✓）／`py -X utf8 tools\tests\run_all.py` ✓（库仓 ✓）；项目那个加 **`--with-lib`** ⇒ 顺带把库仓整套也跑 ✓ |

### ③ 动了什么 ✓（入库清单 ✓）

| 从 ✓ | 到 ✓ |
|---|---|
| `_work/_ut_gap.py` ✗（被忽略 ✓）| **库仓 `tools/tests/sch_geom_gap_selftest.py`** ✓（测 `tools/sch_geom.py` 的线距判据 ✓）|
| `_work/_ut_tie.py` ✗（被忽略 ✓）| **本仓 `tests/tie_cands_selftest.py`** ✓（测 `gen_schematic_wires.tie_cands()` ✓）|
| `tools/sch_body_selftest.py` ✓ | **库仓 `tools/tests/sch_body_selftest.py`** ✓（同一约定 ✓）|
| `tools/pcb_curve_selftest.py` ✓ | **库仓 `tools/tests/pcb_curve_selftest.py`** ✓（同一约定 ✓）|
| — | **新** `tools/tests/run_all.py` ✓ ＋ **新** `tests/run_all.py` ✓（两个 runner ✓）|

★ `_work/_ut_gap.py` / `_work/_ut_tie.py` **已删掉** ✓（`_work/` 里不再有第二份真源 ✓）；
★ 三个测试脚本的**头部用法**也改了 ✓（写清「测试在哪、怎么跑」✓）。

### ④ 验收 ✓（两个 runner 各 **exit 0** ✓ —— 原始输出见 `_work/_r79_accept.txt` ✓）

```bat
py -X utf8 tools\tests\run_all.py                       # 库仓：3 个脚本 ⇒ ✓ 全过 ＋ exit 0 ✓
py -X utf8 hardware\pixel\tests\run_all.py --with-lib    # 本仓 1 个 ＋ 库仓 3 个 ⇒ ✓ 全过 ＋ exit 0 ✓
```

| runner ✓ | 结果 ✓ |
|---|---|
| 库仓 `tools/tests/run_all.py` ✓ | ✓ **全过（3 个 ✓）** ✓：`sch_body_selftest.py` exit 0 ✓／`sch_geom_gap_selftest.py` exit 0 ✓（⑧ 条判据全过 ✓）／`pcb_curve_selftest.py` exit 0 ✓ |
| 本仓 `tests/run_all.py` ✓ | ✓ **全过（1 处 ✓）** ✓：`tie_cands_selftest.py` exit 0 ✓（含「反向那一支」✓）|

### ⑤ 复现命令 ✓

```bat
py -X utf8 F:\git\fritzing-parts-langhua\tools\tests\run_all.py
py -X utf8 tests\run_all.py --with-lib
```

**六十五、第四十八轮（2026-10-09 ✓）：继续降交叉 ⇒ **14 → 10** ✓（给 `--escs` 加一条**出脚车道** `7.2` ✓）⇒ 发布交付件 `pixel-pcb-v79.fzz` ✓ ⇒ 七道验收 7/7 ✓、**穿体 0** ✓、**线距 ≥ `--wire-gap` 0 对** ✓、`pcbView` / `breadboardView` **逐字节未动** ✓**

### ① 用户要的是什么 ✓

用户：「`_work\v76.4_byHand.fzz`（= 已发布的 `pixel-pcb-v78.fzz` ✓）**交叉 14** ✗ ⇒ 继续试着降 ✓
（目标 **≤7** ✓、与 `v40` 持平 ✓）；**硬约束一条不退** ✓（线距 ≥ `--wire-gap` **排在交叉数之前** ✓、
穿体 0 ✓、同网/异网重叠 0 ✓、贴脚 0 ✓、悬空端 0 ✓、声明双向自洽 ✓、假接头 0 ✓、每网 1 岛 ✓、
接地符号每岛 1 ✓、备用脚 15 只零连接 ✓、**`pcbView` 74 块 ＋ `breadboardView` 122 块逐字节不变** ✓）」；
**允许**扩候选形状 ✓ / 全局重排（车道分配、轨 y、主干落点 ✓）—— ★ **器件与符号位置尽量不动** ✓（本轮 **0 动** ✓）；
降不下来的**逐条记账** ✓（不许静默 ✗）；**发布 v79** ✓。

### ② 先把 14 条**逐条量出来** ✓（`_work/_x14.py` ✓：网名 ＋ 端点 ＋ 交点 ＋ 同/异网 ✓）

| # | 谁 × 谁 ✓ | 交在哪 ✓ |
|---|---|---|
| 1 | `5V` 斜接 `(48.03,43.20)→(22.83,18.00)` × `DATA_IN` 车道 `x=34.78` | (34.78,29.95) |
| 2 | `5V` 竖 `x=22.83` × `DATA_IN` 横 `y=0` | (22.83,0.00) |
| 3 | `5V` 竖 `x=180.38`（`LED2.VDD`→`C2.1`） × `DATA_OUT` 横 `y=−43.20` | (180.38,−43.20) |
| 4 | `5V` 竖 `x=22.83` × `GND` 横 `y=9`（`J1.c1` 引线）| (22.83,9.00) |
| 5 | `5V` 轨 `y=−57.60` × `GND` 竖 `x=74.78`（`EPAD`→底轨）| (74.78,−57.60) |
| 6 | `5V` 轨 `y=−57.60` × `GND` 竖 `x=235.38` | (235.38,−57.60) |
| 7 | `5V` 轨 × `RC` 竖 `x=46.58` | (46.58,−57.60) |
| 8 | `5V` 轨 × `RC` 竖 `x=83.78` | (83.78,−57.60) |
| 9 | `COIL_B` 横 `y=126` × `GND` 竖 `x=44.93` | (44.93,126.00) |
| 10 | `DATA_IN` 车道 `x=34.78` × `GND` 横 `y=9` | (34.78,9.00) |
| 11 | `DATA_IN` 横 `y=0` × `GND` 竖 `x=27.38` | (27.38,0.00) |
| 12 | `DATA_OUT` 竖 `x=209.20` × `GND` 横 `y=9` | (209.20,9.00) |
| 13 | `GND` 横 `y=−43.20`（`x 27.38→74.78`） × `RC` 竖 `x=46.58` | (46.58,−43.20) |
| 14 | `GND` 竖 `x=74.78` × `RC` 横 `y=−62.60` | (74.78,−62.60) |

★ 一眼能看出：**4 条（7/8/13/14）都长在 `RC` 身上** ✗、**1 条（11）**长在 `DATA_IN` 与 `GND` 竖线上 ✗
⇒ 这就是本轮的**下手处** ✓。

### ③ 做法 ✓（★ **只改一个参数值** ✓ —— 生成器**一行代码都没动** ✓）

`gen_schematic_wires.py` 的**出脚车道**（`ESC_OFFS` ✓）原来只有两条：**`(12.2, 19.4)`** ✓
（= `CLEAR_PIN+5` ／ `+12.2` ✓）。**加第三条 `7.2`** ✓ ⇒ **`--escs 7.2,12.2,19.4`** ✓。

★ 为什么是 **7.2** ✗（**量出来的区间** ✓，不是拍的 ✓）：出脚点要同时满足两条硬规矩 ——
① **离腿排 ≥ `CLEAR_PIN` = 7.2** ✓（不然 `HARD_CLEAR` 把候选全删 ✗）；② **离轨道 ≥ `--wire-gap` = 3.5433** ✓。
本板腿排 `y=−43.2` ✓、`5V` 轨 `y=−57.6` ✓ ⇒ 轨距 **14.4** ⇒ 合法区间
`o ∈ [7.2, 14.4 − 3.5433] = [7.2, 10.86]` ✓ —— 这个区间里**原来一条车道都没有** ✗ ⇒
`RC` 那条支线**只能跨过 5V 轨**（绕到轨的另一侧 ✓）⇒ 凭空多出 **2 条**交叉（#7/#8 ✗）。
`7.2` 取的是**下界**（= 最短 ✓，且"刚好满足安全距离"✓，语义最干净 ✓）。

★ 顺带怎么把 #11 也治掉的 ✓（**连锁** ✓，不是专门针对它 ✓）：`7.2` 这条车道一开，
`GND` 那一簇改从 `U1.VSS` 的**新出脚点 `x=51.38`** 引出（`58.58 − 7.2` ✓）⇒ `GND` 竖线由
**`x=27.38` 挪到 `x=51.38`** ✓ ⇒ `DATA_IN` 的 `y=0` 那条横线（`32.93→15.38`）**再也碰不到它** ✓
⇒ #11 **自然消失** ✓（★ 这属于用户允许的「**全局重排：车道分配**」✓）。

### ④ 数字对照 ✓（三把独立尺子：生成器自检 ✓ ＋ `sch_probe` ④ ✓ ＋ `_work/_x14.py` ✓）

| 项 ✓ | **改前** ✗（`_work/v76.4_byHand.pre-xreduce.fzz` = `pixel-pcb-v78.fzz` ✓）| **改后** ✓（`pixel-pcb-v79.fzz` ✓）|
|---|---|---|
| **交叉** ✓ | **14** ✗ | ✓✓ **10**（**−4** ✓ —— 逐条账见 ⑤ ✓）|
| **全图最小净距** ✓ | 4.5500 单位 = **1.2841 mm** ✓ | ✓ **4.8000 单位 = 1.3547 mm** ✓（还**变宽**了 ✓）|
| **低于 `--wire-gap` 的对数** ✓ | 0 对 ✓ | ✓ **0 对** ✓（**硬闸门守住** ✓）|
| **总长** ✓ | 508.5 mm ✓ | ✓ **495.2 mm**（**−13.3 mm = −2.6%** ✓）|
| 导线根数 ✓ | 46 ✓ | ✓ **46**（**同** ✓）|
| **穿体** ✓ | 0 ✓ | ✓ **0** ✓（**不可退让** ✓ 守住了 ✓）|
| 同网共线重叠 ✓ | 0 对 ✓ | ✓ **0 对** ✓ |
| 9 张网逐脚 ✓ | ✓ 9/9 ✓ | ✓ **9/9** ✓ |
| 备用脚 15 只零连接 ✓ | ✓ | ✓ **同** ✓ |
| 声明双向自洽 ✓ | ✓ | ✓ **同** ✓ |
| 跨网假接头 / 贴脚 / 悬空端 ✓ | 0 / 0 / 0 ✓ | ✓ **0 / 0 / 0** ✓ |
| 每张网 1 个岛 ✓ | ✓ 9/9 ✓ | ✓ **9/9** ✓ |
| 接地符号 × 岛 ✓ | 2 个（每岛 1 ✓） | ✓ **2 个** ✓ |
| `pcbView` / `breadboardView` ✓ | — | ✓ **逐字节相同** ✓（74 块 / 122 块，拼哈希 `24141dd900659867` / `8b450fd58b38600c` ✓）|
| ★ **渲染器独立口径** ✓（`render_sch.py` 自检 ✓，与上面两把尺子**不同实现** ✓）| 十字交叉 **14 处** ✓ ／ **跨网擦身 11 处** ✗ ／ 穿本体 **0 段** ✓ | ✓ 十字交叉 **10 处** ✓ ／ **跨网擦身 8 处**（**顺手少 3 处** ✓）／ 穿本体 **0 段** ✓ ／ 几乎压在一起 **0 对** ✓ |
| 器件 / 符号位置 ✓ | — | ✓ **0 动** ✓（`--decoup` 那条 `C2` 也没再挪 ✓）|

### ⑤ 交叉 **14 → 10** 的逐条账 ✓

★ **消失的 4 条** ✓（全是本轮目标 ✓）：

| 原来哪条 ✓ | 为什么没了 ✓ |
|---|---|
| #7 `5V` 轨 × `RC` 竖 `x=46.58` ✓ | `RC` 的横段从 **`y=−62.60`（轨下方 ✗）** 提到 **`y=−50.40`（轨上方 ✓、腿排下方 ✓）** ⇒ **不再跨轨** ✓ |
| #8 `5V` 轨 × `RC` 竖 `x=83.78` ✓ | 同上 ✓（同一条支线的另一端 ✓）|
| #13 `GND` 横 `y=−43.20` × `RC` 竖 `x=46.58` ✓ | `GND` 的横段随竖线一起挪到 **`x 51.38→74.78`** ✓ ⇒ `RC` 在 `x=46.58` 下去时**不再碰它** ✓ |
| #11 `DATA_IN` 横 `y=0` × `GND` 竖 `x=27.38` ✓ | `GND` 竖线挪到 **`x=51.38`** ✓ ⇒ 那条横线（到 `15.38` 就完了 ✓）**碰不到** ✓ |

★ **平移的 6 条** ✓（**同一处、端点挪了一点** —— 坐标变了、不是新增 ✗）：
#1（`5V` 斜接端点 `48.03→47.78`、车道 `34.78→32.93` ✓）、#4（`GND` 横段 `27.38→51.38` 起 ✓）、
#6（`GND` 竖线 `235.38→237.38` ✓）、#8-of-after（= 旧 #10，车道 `34.78→32.93` ✓）、
#10-of-after（= 旧 #14，`RC` 横段 `−62.60→−50.40` ✓）、#2 ✓。

★ **逐条账：剩下 10 条的"出身"** ✓ —— **结构性 5 条**（`v40` 也有 ✓；由「`J1` 三脚扇出 ＋ 两条轨」的布局决定 ✓）
＝ **after #2 / #4 / #5 / #6 / #7** ✓；**换脚逼出来的 5 条** ✓ ＝ **after #1 / #3 / #8 / #9 / #10** ✓：

| 剩下哪条 ✗ | 为什么**躲不掉** ✓（用户的优先级：**硬约束 > 交叉** ✓）|
|---|---|
| **#3** `5V` 竖 `x=180.38` × `DATA_OUT` 横 `y=−43.20` ✓ | `DATA_OUT` 的脚 `PD2` 与 `J2.c2` **一在 `U1` 上排（`y=−43.2` ✓）、一在 `x=244.58`** ✓ ⇒ 它的横线**必须**从 `x<180.38` 横到 `x>180.38` ✓，而那条竖线跨 `y −11…−57.6` ✓ **包含** −43.2 ✓ ⇒ **必穿** ✓（绕到轨下方 = 再跨轨两次 ✗ 更差 ✓）|
| **#9** `DATA_OUT` 竖 `x=209.20` × `GND` 横 `y=9` ✓ | 到 `J2.c2` 的**最后一段必须落在 `y=18`** ✓（`J2.c2` 的脚法线朝左 ✓）⇒ 那条竖线**只能**落在 `x ≥ 201.38` ✓ —— ✗ 再往左，`y=18` 那条回线就与 `GND` 自己的 `y=17` 横线（`x 180.38…201.38` ✓）**只差 1.0 单位** ✗（`--wire-gap` 要 3.54 ✓）⇒ 竖线**必然**落在 `GND` 的 `y=9` 横线（`201.38…237.38` ✓）范围里 ⇒ **必穿** ✓ |
| **#10** `GND` 竖 `x=74.78` × `RC` 横 `y=−50.40` ✓ | `RC` 的脚 `PD6` 在 **`U1` 上排 `x=83.78`** ✓ ⇒ 只能**从左边**过来 ✓；而它又**必须**走到腿排下方（`y ≤ −50.4` ✓，不然贴脚 ✗）⇒ 从 `x<74.78` 横到 `x=83.78` **必然**穿那条竖线 ✓ |
| **#1** `5V` 斜接 × `DATA_IN` 车道 ✓ | 车道要同时 ≥7.2（离 `J1` 的脚 ✓）＋ ≥3.5433（离 `5V` 竖线 ✓）⇒ **只能**落在 `5V` 竖线**右边**（`x ≥ 26.1` ✓）⇒ `5V` 从 `VDD`（下排 `83.78,43.2` ✓）回左边那条**斜接**（`y ∈ [18,43.2]` ✓）**无论怎么走都要穿它** ✓（改走正交 L 也一样 ✓ —— 实测 ✓）|
| **#8** `DATA_IN` 车道 × `GND` 横 `y=9` ✓ | ★ **这一条是"还能省 1 条"的唯一处** ✓：`J1.c1` 的引线若**先下潜到 `y<0`** 再右行 ✓，就能只穿 `5V` 竖线（#4 ✓ 结构性）而**不穿**车道（车道只跨 `y 0…50.4` ✓）⇒ 理论 **9 条** ✓。✗ 但它要**绕远** ✓ —— 现布线器在"引线（轨支线）"那一档给的是 **L 形 / 直连**两族形状 ✓，没有"下潜"这一族 ✗ ⇒ 本轮没做 ✓（下一手 ✓）|

★ 结论 ✓（**如实记账** ✓，不硬压 ✗）：**10 = 5 结构性 ＋ 5 换脚逼出来的**；
把 #8 也治掉最多到 **9**；**要 ≤7 就还得再省 2 条，而那 2 条只能靠**：
① 把线画到**引脚安全距离（7.2 单位 = 2.03 mm）以内** ✗（**用户 2026-09-27 定的可读性规则** ✓，不在本轮授权里 ✗）；
② **挪器件 / 符号** ✗（本轮授权是"尽量不动" ✓）；③ **把换掉的脚换回去** ✗（那是 `v40` 当年能到 7 的原因 ✓ ——
`v40` 里 `RC/DATA_IN/DATA_OUT` **三只脚全在 `U1` 左排** ✓ ⇒ 三根短直线 ✓；换脚后它们分到**上排/下排** ✗
⇒ 每根都得**绕过 `U1` 的身子** ✓）⇒ **不给这三条授权，≤7 在本布局上做不到** ✓（这是量出来的 ✓）。

### ⑥ 试过、但**没有收益**的两次 ✓（**全都撤掉** ✓ —— 生成器**回到一字不动** ✓）

★ 仓规（`README` §六十二 ⑦ 同一条 ✓）：「**不许把没收益的复杂度留下** ✗」。两个实验都**先量后撤** ✓：

| 实验 ✓ | 实测 ✓ | 结论 ✓ |
|---|---|---|
| `--innerchan` ✓（把「轨 y ± `CH_OFFS`」＋「腿排 y ± `CH_OFFS`」也当**水平通道** ✓）| 单独用：交叉 **14 → 14** ✗（一条没少 ✓）；与 `--escs` 合用：**10 → 10** ✗（零收益 ✓）| **撤** ✓（代码全删 ✓：生成器 `git diff` **0 行** ✓）|
| `--stair` ✓（候选里加「**借一条竖通道 ＋ 一条横通道**」的两段楼梯 ✓ —— 用户点名的「多拐点 L」✓）| **极慢** ✗（候选数 = 竖通道数 × 横通道数 ✓ ⇒ 单次 **40 分钟未收敛** ✗，只能停掉 ✓）；与 `--escs` 合用未见改善 ✗ | **撤** ✓。★ 记账：它要治的那条（`DATA_OUT` 走「`U1` 右边 ＋ `LED2` 上边」⇒ 0 交叉 ✓）**在本板几何上不成立** ✗ —— `U1` 右腿排（`x=144.98`）与 `LED2` 左腿（`x=159.38`）之间只有 **14.40** 单位 ✓ ⇒ 要找一条离**两边都 ≥7.2** 的竖通道需要 **14.4** ✓ ⇒ **恰好没有余量**（`14.398 − 7.2 = 7.198 < 7.2` ✗）⇒ 那个"0 交叉"形状**永远过不了"贴脚 = 0"** ✓（量出来的 ✓，不是猜的 ✓）|

★ **两条命令行坑** ✓（写进账 ✓，省得下次再花一轮 ✓）：
`--escs=7.2,…`（**等号写法** ✗）与 `--chain=revyx`（✗）都**不被这个脚本认** ✓
（它用的是 `argv.index("--escs")` / `argv.index("--chain")` ✓ ⇒ **只认空格写法** ✓）⇒ 被**静默忽略** ✗ ⇒
第一次实测"明明改了参数、结果却一模一样（14→14 ✗）"就是这么来的 ✓ —— ★ 教训：**新开关第一次用，先看它有没有把自己的参数打出来** ✓。

### ⑦ 七道验收 ✓（**7 / 7** ✓ —— 原始输出留档 `_work/_r79_accept.txt` ✓）

```bat
py -3.13 _work\_r79_accept.py _work\v76.4_byHand.pre-xreduce.fzz pixel-pcb-v79.fzz _work\_r79_accept.txt
```

| # | 项 ✓ | 结果 ✓ |
|---|---|---|
| ① | `tools/pcb_check.py pixel-pcb-v79.fzz --nets=pixel_nets.py` | ✓ **判定：✓ 全过** ✓（PCB 一字未动 ✓）|
| ② | `tools/net_group_check.py pixel-pcb-v79.fzz` | ✓ **exit 0** ✓（Fritzing 认得出每张网 ✓）|
| ③ | `_work/view_bytes_diff.py` ＋ `_work/find_gap.py` | ✓ **两个视图逐字节相同** ✓（74 / 122 块 ✓）｜ 端点不重合 **0** 处 ✓ |
| ④ | `_work/sch_probe.py … --nets=pixel_nets.py` | ✓ **exit 0** ✓：**交叉 10** ✓／⑪ **最小净距 1.3547 mm ≥ 1.000 mm** ✓、**低于阈值 0 对** ✓／**穿体 0** ✓／**1 网 1 岛** ✓／接地符号每岛 1 ✓／总长 495.2 mm ✓ |
| ⑤ | **测试** ✓：库仓 `tools/tests/run_all.py` ＋ 本仓 `tests/run_all.py --with-lib` | ✓ **两个 runner 都 exit 0** ✓（见 §六十四 ✓）|
| ⑥ | **零副作用** ✓：`_work/_z_oldparams.py`（**一个新开关都不加** ✓）＝ **改前逐字节相同** ✓；`_work/_z_v40.py`（**v40 原命令**重跑 ✓）＝ **逐字节相同** ✓ | ✓ **两条都相同** ✓（★ 理由：本轮只**加了一个参数值** ✓ ⇒ 不给它时那条链**一个字节都没动** ✓）|
| ⑦ | **渲染** ✓：`tools/render_sch.py` ＋ `tools/render_pcb.py` | ✓ **PNG / SVG 都出** ✓（特写另裁 ✓ 见 ⑨ ✓）|

### ⑧ 复现命令 ✓（交付件 = `_work/v76.4_byHand.fzz` ＝ `pixel-pcb-v79.fzz` ✓；改前留 `_work/v76.4_byHand.pre-xreduce.fzz` ✓）

```bat
set TOOLS=F:\git\fritzing-parts-langhua\tools
copy _work\v76.4_byHand.fzz _work\v76.4_byHand.pre-xreduce.fzz                              # 先备份 ✓
py -3.13 %TOOLS%\sch_strip_wires.py _work\v76.4_byHand.pre-dedupe.fzz _work\_r0_strip.fzz    # 与 §六十～六十三 同一条链 ✓
py -3.13 %TOOLS%\render_sch.py _work\_r0_strip.fzz _work\_r0_base.png --pins-out=_work\_r0_pins.py
py -3.13 gen_schematic_wires.py _work\_r0_strip.fzz _work\_r0_base.svg _work\_v79_gen.fzz ^
    --nets=pixel_nets.py --orig _work\v76.4_byHand.pre-dedupe.fzz --ratio 1.0 --rails --islands=GND ^
    --vlanes=5V@29.778 --decoup --hardbody --corebox --dedupe-symbols --complete-islands ^
    --symmerge --mst-merge --bodyoutline --mst-shape --escs 7.2,12.2,19.4        # ★ 本轮唯一改动 ✓
py -3.13 %TOOLS%\merge_sch.py _work\v76.4_byHand.pre-dedupe.fzz _work\_v79_gen.fzz _work\_v79_out.fzz
copy _work\_v79_out.fzz _work\v76.4_byHand.fzz                                               # 就地更新 ✓
copy _work\_v79_out.fzz pixel-pcb-v79.fzz                                                    # 交付件 ✓
py -3.13 %TOOLS%\render_sch.py pixel-pcb-v79.fzz pixel-pcb-v79_sch.png                       # 原理图预览 ✓
py -3.13 %TOOLS%\render_pcb.py pixel-pcb-v79.fzz pixel-pcb-v79_preview.svg --png
py -3.13 _work\_r79_accept.py _work\v76.4_byHand.pre-xreduce.fzz pixel-pcb-v79.fzz _work\_r79_accept.txt
```

★ **中间脚本**（都在 `_work/` ✓，本轮新增 4 个 ✓）：`_x14.py`（**交叉逐条点名** ✓：网名/端点/交点 ✓）、
`_try.py`（**一次跑完整链 ＋ 报交叉/线距/总长** ✓ —— 用来扫参数 ✓）、`_r79_accept.py`（七道验收一次跑齐 ✓）、
`_z_oldparams.py` / `_z_v40.py`（**零副作用**两路 ✓）。

### ⑨ 遗留 ✗（下一手 ✓）

- **交叉 10**（目标 ≤7 ✗ 未达 ✓）—— **逐条账见 ⑤** ✓：5 结构性 ＋ 5 换脚逼出来的 ✓；
  还能省的**只有 #8 一条**（`J1.c1` 的引线"下潜"形状 ✓ ⇒ **9**）⇒ 那一族形状**本轮没做** ✓
  （要给"轨支线"那一档加"先竖后横、且先离轨"的形状 ✓ —— 会动到 `route_pair` 的**候选生成** ✗，风险比参数大 ✓）。
- **≤7 的三条路**（都不在本轮授权里 ✓，见 ⑤ 的结论 ✓）：放宽 `CLEAR_PIN`（2.03 mm 可读性规则 ✓）／
  挪器件符号 ／ 把换掉的脚换回去 ✓。★ 建议：**先在 Fritzing 里看一眼 `v79`** ✓ —— 若某处线看着"绕"，
  那多半就是 ⑤ 里记的那几条"躲不掉"的 ✓。
- **特写/全图对照** ✓：`_work/_v79_full.png` / `_v79_spot*.png` ✓（按已知 viewBox 裁 ✓ 不标定 ✓）。

**六十六、第四十九轮（2026-10-09 ✓）：文字重叠 ⇒ 做成规则 ＋ 硬闸门 `--text-gap`（缺省 0.15 mm）＋ 继续降交叉 ⇒ 发布 `pixel-pcb-v80.fzz`**

### ① 用户要的是什么 ✓（两件事，**先 A 后 B** ✓）

用户原话 ✓：**A**「**文字和接地符号重叠了，请制定规则来解决**」✓（截图点名 `LED2` 的**值文字**
`WS2812B-1010` **压在接地符号上** ✗）；**B**「**继续尝试减少交叉**，虽然我看不出怎么改进了」✓（现状 **10** ✗）。
★ 已有"**位号不许压线**"的规则 ✓，但它**没盖住**三件事 ✗：① **值文字** ✗（老规则算盒子时**算了**所有行 ✓，
可**对家里没有接地/电源符号** ✗）② **接地/电源符号件** ✗（老规则用的是一段**量出来的固定 keep-out** ✓，
与**画出来的符号**对不上 ✗）③ **文字 ↔ 文字** ✗。
★ **硬约束一条不退** ✓：线距 ≥ `--wire-gap`(1.0 mm ✓)、穿体 0 ✓、重叠 0 ✓、贴脚 0 ✓、
**文字重叠 0（A 新增 ✓）**、悬空端 0 ✓、声明双向 ✓、假接头 0 ✓、每网 1 岛 ✓、接地符号每岛 1 ✓、
备用脚 15 只零连接 ✓、`pcbView` 74 块 ＋ `breadboardView` 122 块**逐字节不变** ✓。

### ② A① **先量出来**：改前那条重叠清单 ✓（`_work/_tg_measure.py` ＝ `_work/_tg_probe.py` ✓ 只读 ✓）

判据 ＝ **共享实现** `tools/sch_textgap.py` ✓（**唯一一份** ✓）。改前（`pixel-pcb-v79.fzz` ✓）：

| # | 谁 ✗ | 框 ✓ | 压谁 ✗ | 框 ✓ | 净距 ✓ |
|---|---|---|---|---|---|
| 1 | 位号块 **`LED2` ＋ 值文字 `WS2812B-1010`** ✗ | (159.38,24.20)–(189.35,38.95) | **接地符号 `Ground2`** ✗ | (180.40,26.00)–(197.15,42.00) | **0.0000 单位 = 0.0000 mm**（相交 ✗）｜**真墨迹命中 ✓** |
| 2 | 位号块 **`LED2` ＋ 值文字** ✗ | 同上 | 导线 `Wire90015558`（**接地符号那条引线** ✗，段 (188.78,17.00)→(188.78,26.00) ✓） | (188.78,17.00)–(188.78,26.00) | **0.0000 单位**（相交 ✗）｜真墨迹命中 ✓ |
| 3 | 位号块 **`D3` ＋ 值文字 `BAS70BRW`** ✗ | (90.95,117.20)–(110.93,131.95) | 导线 `Wire90014108`（`GND` 长横 ✓，段 (44.93,132.00)→(161.33,132.00) ✓） | (44.93,132.00)–(161.33,132.00) | **0.0500 单位 = 0.0141 mm** ✗（几乎贴上 ✓） |

★ **覆盖度** ✓（探针印的 ✓）：扫了 **11 个文字**（位号块 **9** ＋ 网标签 **2** ✓）×
**59 个被绘制对象**（器件本体 **9** ＋ 导线 **46** ＋ 接地符号 **2** ＋ 网标签符号 **2** ✓）
＝ **649 组** ✓ ＋ **文字 × 文字 55 组** ✓ ＝ **704 组** ✓（**逐条点名** ✓，见 `_work/_r80_accept.txt` ④ ✓）。
★ 特写（改前 ✓）：`_work/_v80_spot_LED2_before.png` ✓（＝ 用户截图那一处 ✓）、`_work/_v80_spot_D3_before.png` ✓。
★ 别人都没事 ✓：`Breadboard1` **不列** ✓（Fritzing 的原理图**不画它** ✗ —— 与渲染器同口径 ✓）；
接地/电源符号**本板不画文字** ✓ ⇒ 只当"对象"、不当"文字" ✓。

### ③ A② 规则 ✓（判据 ＋ 参数 ＋ **一份实现**）

- **判据** ✓：**任何文字的外接框**与**任何被绘制对象的**外接框，**净距 ≥ `--text-gap`** ✓。
  · **文字** ＝ ① 元件**位号块**（`titleGeometry` 的**所有行** ✓ —— **含值文字** ✓，行内容调
    `sch_text.fritzing_lines()` ✓ **唯一实现** ✓）② **网标签旗标**（文字长在旗标本体里 ✓）
    ★ **接地/电源符号不当文字** ✓（本板不画它的字 ✓）。
  · **对象** ＝ ① 器件符号本体（`sch_body` ✓ **该视图实际绘制的外形** ✓，含引脚引线 ✓）
    ② 导线 ✓ ③ 接地/电源符号（`sch_net.ground_art()` ✓ —— 与渲染器画的是**同一份素材** ✓）
    ④ 网标签旗标 ✓ ⑤ **别的文字** ✓。
  · **豁免只有一条** ✓：网标签旗标 ↔ **它自己在 `.fzz` 里声明连接的那根引线** ✓
    （旗标**必须**坐在切口线端上 ✓ —— 那是设计 ✓、不是重叠 ✗）。
- **参数** ✓：`--text-gap[=<mm>]` ✓（`--textgap` 也认 ✓；`--text-gap=0.15` / `--text-gap 0.15` **两种写法都收** ✓
  —— `--label` 那条教训 ✓）。缺省 **0.15 mm** ✓、范围 **[0, 2.54] mm** ✓、超范围 ⇒ **夹到边界 ＋ 警告** ✓
  （不静默 ✗、不崩 ✗）；**只写 `--textgap`（不给值）** ⇒ 用缺省 ✓；`--text-gap=0` ⇒ **整条规则关掉** ✓
  ＝ **一键回旧行为** ✓。
  另有一把**只放行第二档**的开关 ✓：`--text-gap-symbol` ✓（缺省**关** ✓ —— 见下 ④ 的理由 ✗）。
- **★ 判据只有一份** ✓：新增 `tools/sch_textgap.py` ✓ —— **生成器的硬闸门 ＋ 自动修 / 验收探针 ⑫ /
  渲染器 ④d** 三处**都调它** ✓（本仓最贵的那类错是"同一个概念两把尺子" ✗）。同一轮还把
  **位号行的内容规则**从 `render_sch.py` 上收成 `sch_text.fritzing_lines()` ✓（原来只写在渲染器里 ✗）。

### ④ A③ 自动修 ✓（优先级 = **不压任何东西** ✓ > **少移动** ✓ > **贴近原位** ✓）

- **第一档：挪文字** ✓（`sch_textgap.repair()` ✓）—— 只挪**位号块** ✓：
  · 候选位 ＝ **方向族**（上·左/中/右 ✓、下·左/中/右 ✓、左 ✓、右 ✓，各往外推 1…5 个车道 ✓）
    ＋ **原位附近的细档**（±12 × 0.9 单位 ✓ —— ✗ 没有它，"差 0.05 单位"那处也得跳 9 单位 ✗）；
  · 打分键 ＝ `(违例条数, 位移)` ✓ ⇒ **先要干净、再要少动** ✓；先滤掉"压在自己本体上"的候选 ✓
    （滤空了**退回全量** ✓ —— 不许因此丢解 ✗）；
  · ✗ **网标签不能挪** ✗ —— 它必须坐在**切口线端**上 ✓（挪了就把网切开 ⇒ "每网 1 岛"当场挂 ✗）。
- **第二档：微调符号件 ≤ 1 个车道** ✓（`sch_textgap.nudge_symbol()` ✓）—— 只给**接地 / 网标签符号** ✓：
  挪它**同时把它那条引线的端点一起挪** ✓ ⇒ **接头原地不动** ✓。
  ★ 为什么**不给器件** ✗：挪一个器件要牵动**它所有的脚** ✗ —— 那已经等于重新布线 ✗（本档不做 ✗、**但要报出来** ✓）。
  ★★ **默认不做** ✗（要 `--text-gap-symbol` 才放行 ✓）—— ★ **实测踩过** ✗：`--text-gap 5` 那一次
  第二档把 `Wire90015558` 挪成**斜线** ✗ ⇒ **打破了「线距 ≥ `--wire-gap`」这条硬闸门** ✗✗
  ⇒ 按仓规「**硬约束一条都不许退** ✗」⇒ 默认档**只挪文字** ✓（文字挪动**碰不到任何几何** ✓）。
  ★★ 放行后也**必须过五道复核** ✓（`_tg_nudge_ok()` ✓）：① 文字违例**变少** ✗② **线距不新增** ✗
  （`sch_geom.conductor_clearance` ✓ 同一把尺子 ✓）③ **不穿体** ✓④ **不压别人的脚** ✓（自己的脚豁免 ✓）
  ⑤ **不与已布线重叠** ✓ —— 任何一条不过 ⇒ **原样撤回** ✗。
  ★ 连"哪条线端在它身上"也**重定过** ✗✓（`symbol_pin()` ✓）：接地符号的**脚 ≠ 原点** ✗
  （实测偏 `(+9.001, +0.596)` ✓）；而且只认**恰好一条**重合线端 ✓（0 条 / >1 条 ⇒ **不动** ✗）——
  ✗ 原来取"**离符号最近**的那个线端"不是单射 ⇒ 挪回去**挪不回来** ✗（那个斜线就是它造成的 ✗）。
- **第三档：还不行 ⇒ 大声报 ＋ 退出码 1** ✗（`TEXT_GAP_LEFT` ✓ —— **不许静默放过** ✗，`AGENTS §0` ✓）。
  ★ **记账** ✗：用户给的第三条出路「**删除冗余值文字**」**本轮没有触发** ✓（前两档已治好全部 3 处 ✓）
  ⇒ 按仓规「**不许把没收益的复杂度留下** ✗」⇒ **不写这档** ✗；真要它，得**先拿一份 Fritzing 导出**
  验一次 `<displayKey>` 的语义 ✓（本仓不许拿未验证的写法当硬闸门 ✗）。

### ⑤ A④ 改后对照 ✓（改前 `pixel-pcb-v79.fzz` ✓ ／ 改后 `pixel-pcb-v80.fzz` ✓）

| 项 ✓ | **改前** ✗ | **改后** ✓ |
|---|---|---|
| **文字 ↔ 对象 净距 < 0.150 mm 的对数** ✓ | **3 对** ✗ | ✓✓ **0 对** ✓（`_work/sch_probe.py` ⑫ ＋ 渲染器 ④d ＋ 生成器闸门 **三处一致** ✓）|
| 文字个数 ✓ | 11 ✓ | ✓ **11**（**一个没删** ✓ —— 只**挪** ✓）|
| 挪动台账 ✓ | — | ✓ **2 处**：`LED2+WS2812B-1010` 框左缘 **159.38 → 149.48**（**左移 9.9 单位 = 2.794 mm** ✓）；`D3+BAS70BRW` 框上缘 **117.20 → 116.30**（**上移 0.9 单位 = 0.254 mm** ✓）|
| 器件 / 符号位置 ✓ | — | ✓ **0 动** ✓（**第二档没触发** ✓ —— 全是"挪文字"治好的 ✓）|
| 交叉 / 总长 / 线距 ✓ | 10 ／ 495.2 mm ／ 1.3547 mm ✓ | ✓ **10** ／ **495.2 mm** ／ **1.3547 mm**（**几何一字未动** ✓ —— A 只动文字 ✓）|
| `pcbView` / `breadboardView` ✓ | — | ✓ **逐字节相同** ✓（74 块 / 122 块 ✓）|

★ 特写（**改前 / 改后** ✓，同一窗口 `140,5 → 210,60` ✓）：
`_work/_v80_spot_LED2_before.png` ✓ ／ `_work/_v80_spot_LED2_after.png` ✓
（另有一处 `D3`：`_work/_v80_spot_D3_before.png` ✓ ／ `_work/_v80_spot_D3_after.png` ✓）；
整图：`_work/_v80_full.png` ✓（＝ `pixel-pcb-v80_sch.png` ✓）。

### ⑥ B 交叉 **10 → 10** ✓（目标 ≤9 ✗ **没做到** ✓ —— 逐条账 ＋ **五手实测** ✓）

**先更正上一轮的一条账** ✗（如实报 ✓）：v79 记的是「**还能省的只有 #8 一条** ⇒ 理论 9」✗ ——
本轮**量下来它不成立** ✗（下面那手实测 ＋ 平面账 ✓）。

★ **#8 的平面账** ✓（`DATA_IN` 车道 `x=32.93` × `GND` 横 `y=9` ✓）：`DATA_IN` 的走线是一条
**L 形屏障** ✓ —— `(15.38,0) → (32.93,0) → (32.93,50.40) → (101.78,50.40)` ✓。
`J1.c0`（`GND`，脚 `(15.38,9.00)` ✓）在屏障的**左上侧** ✓，它要去的 `GND` 汇点 `(51.38,9.00)` ✓ 在**右下侧** ✓
⇒ **必须穿屏障一次** ✓（拓扑必然 ✓）。绕法只有三条，**每条都仍要穿一次** ✗：

| 绕法 ✓ | 结果 ✓ |
|---|---|
| ① 沿 `y=9` 往右，穿 `x=32.93` 那条竖线 ✓ | = **现状 #8** ✓ |
| ② **先下潜到 `y<0`** 再右行 ✓（用户上一轮点的那手 ✓） | 下潜那一段**必然**在 `x ∈ (15.38,32.93)` 穿过 `DATA_IN` 的 **`y=0` 那一腿** ✗ ⇒ **一换一** ✓（★ 在 `x=15.38` 上竖直下潜 ✗ 是**穿 `J1` 本体** ✗ —— `J1` 本体右缘正好在 `x=15.38` ✓）|
| ③ 绕到 `y>50.40` 再回来 ✓ | 回来时**必然**穿 `DATA_IN` 的 **`y=50.40` 那一腿** ✗ ⇒ **一换一** ✓ |

★ **五手实测** ✓（都在 `_work/` 留了命令与输出 ✓）：

| 手 ✓ | 实测 ✓ | 结论 ✓ |
|---|---|---|
| ① **`--stub-dive`** ✓（**用户点名要做的那一族** ✓：`candidates()` 里加「**先出脚 → 竖一段 → 横着走**」✓，取**最近 3 条垂直通道 × 3 条水平通道** ✓ —— ✗ 不许全笛卡尔积 ✗）| 交叉 **10 → 10** ✓、总长 **495.2 不动** ✓ ⇒ 产物**逐字节相同** ✓ | ★ **零收益** ✓（原因就是上面那笔平面账 ✓）。★ 默认关 ✓ ⇒ **零副作用** ✓；**按用户点名保留** ✓（代码在 `STUB_DIVE` / `--stub-dive` ✓，可复现这手实验 ✓）|
| ② `--escs 5.4,7.2,12.2,19.4`（**第四条出脚车道** ✓）| **15 分钟没跑完** ✗（候选爆炸 ✓）⇒ **停掉** ✓ | ✗ 不可用 ✓（与第六十六轮 `--stair` 全积**同一类** ✗ —— 记在这儿，省得下次再花一轮 ✓）|
| ③ `--escs 7.2,12.2,19.4,26.6`（更长那条 ✓）| 同上：**15 分钟没跑完** ✗ | ✗ 撤 ✓ |
| ④ `--K 60`（交叉在"交集代价"里的权重 ↑ ✓）| 交叉 **10 → 10** ✓、逐字节相同 ✓ | ✗ 零收益 ✓ |
| ⑤ `--rip 8`（抽线重排轮数 3 → 8 ✓，= **允许改车道分配 / 主干落点** ✓）| 交叉 **10 → 10** ✓、逐字节相同 ✓ | ✗ 零收益 ✓（说明**已经到不动点了** ✓）|

★ **10 条的逐条账** ✓（★ **没有一条**是"再试一手就能省"的 ✓ —— 全都要**动布局/放宽规则** ✗）：

| 剩下哪条 ✗ | 卡在哪 ✓（被谁挡 ✓） | 要动什么才能治 ✓ |
|---|---|---|
| **#2** `5V` 竖 `x=22.58` × `DATA_IN` `y=0` 腿 ✓ | `DATA_IN` 的 **L 屏障** ✓（`J1.c1` 的脚在 `x=15.38` ✓ 而屏障竖线在 `x=32.93` ✓）| ★ **结构性** ✓：只要 `DATA_IN` 还从 `x>22.58` 下来接 `(15.38,0)` 就必穿 ✓ ⇒ 要么**改 `DATA_IN` 的落点/车道** ✓、要么**动 `J1` 的脚位分配** ✗（= 改网表 ✗ 不许 ✓）|
| **#4** `5V` 竖 `x=22.58` × `GND` `y=9` 腿 ✓ | 同上 ✓（两条腿都是从 `x=15.38` 的脚往右 ✓、而 `5V` 必须**从同一侧**下到底轨 ✓）| ★ 同上 ✓ |
| **#5 / #6** `5V` 轨 × `GND` 竖（`x=74.78` ✓ / `x=237.38` ✓）| **两条轨的 y** ✓（`5V` 内轨在 `GND` 外轨里面 ✓ ⇒ 每条 `GND` 竖线从器件下去都要跨一次 ✓）| ★ **结构性** ✓（`v40` 也有 ✓）：要省得**把 `GND` 竖线挪到 `5V` 轨的端点之外** ✗ ⇒ 那要么**挪器件** ✗、要么**放宽 `CLEAR_PIN`（2.03 mm 可读性规则 ✓）** ✗ |
| **#7** `COIL_B` 横 `y=126` × `GND` 竖 `x=44.93` ✓ | `L1` 的 `COIL_B` 脚与 `D3` 的 `GND` 脚**分列上下** ✓ ⇒ 那条 `GND` 竖线**必须**穿过 `COIL_B` 的那一行 ✓ | ★ **结构性** ✓：要省得**把 `L1` 或 `D3` 挪一格** ✗ 或放宽可读性规则 ✗ |
| **#8** `DATA_IN` 车道 × `GND` 横 `y=9` ✓ | 见上 **平面账** ✓（三条绕法**条条一换一** ✗）| ★ 要省得：**改 `DATA_IN` 的走线拓扑** ✓（把它的"先下到 `y=0` 再左行"换成"**从右侧绕到底、或从上面绕过去**"✓ —— 那要**重排 `DATA_IN` 一整条** ✓，会牵动 `U1` 的脚序与车道分配 ✓）或**挪 `J1`** ✗ |
| **#1** `5V` 斜接 × `DATA_IN` 车道 ✓ | 同一个 **L 屏障** ✓：`5V` 的脚在屏障左上侧 ✓、`U1.VDD` 那条线在右下侧 ✓ ⇒ **必须穿一次** ✓ | ★ 同 #8 ✓ |
| **#3** `5V` 竖 `x=180.38` × `DATA_OUT` 横 `y=-43.20` ✓ | `DATA_OUT` 的 `PD2` 与 `J2.c2` **一在上排（`y=-43.2` ✓）、一在 `x=244.58`** ✓ ⇒ 那条横线**必须**从 `x<180.38` 横到 `x>180.38` ✓，而那根竖线跨 `y −11…−57.6` **包含** −43.2 ✓ ⇒ **必穿** ✓ | ★ **结构性** ✓（绕到轨下方 = 再跨轨两次 ✗ 更差 ✓）|
| **#9** `DATA_OUT` 竖 `x=209.20` × `GND` 横 `y=9` ✓ | `GND` 在 `y=9` 从 `x=201.38`（= `LED2` 右缘 ✓）一直连到 `244.58` ✓（**一整道墙** ✓），`DATA_OUT` 要从 `y=-43.2` 上到 `J2.c2` 的 `y=18` ✓ ⇒ 只能在 `x>244.58` 或 `x<201.38` 穿 `y=9` ✓；后者**必穿 `LED2` 本体** ✗；前者要**先横穿 `5V` 竖 `x=244.58`** ✗ ⇒ **一换一** ✓ | ★ 要省得：**挪 `LED2` / `J2`** ✗ 或**改 `DATA_OUT` 的落点** ✓ |
| **#10** `GND` 竖 `x=74.78` × `RC` 横 `y=-50.40` ✓ | `RC` 的脚 `PD6` 在 `U1` **上排 `x=83.78`** ✓ ⇒ 只能**从左边**过来 ✓；而它又**必须**走到腿排下方（`y ≤ −50.4` ✓，不然贴脚 ✗）⇒ 从 `x<74.78` 横到 `x=83.78` **必然**穿那根竖线 ✓ | ★ **结构性** ✓（要省得把 `RC` 的脚**换回左排** ✓ —— 那正是 `v40` 能到 7 的原因 ✓，但**换回去会让 `U1` 左排挤爆** ✗）|

★ 结论 ✓（**目标 ≤7 与 ≤9 都没做到** ✗ —— **如实报** ✓）：**10 = 6 结构性**（#2/#4/#5/#6/#7/#8 ✓，
由「`J1` 三脚扇出 ＋ 两条轨 ＋ `DATA_IN` 的 L 屏障」决定 ✓）＋ **4 换脚逼出来的**（#1/#3/#9/#10 ✓）。
★ 要 ≤7 **只有三条路** ✓（**都不在本轮授权里** ✗，与 v79 那一轮的结论**同一条** ✓）：
① **放宽 `CLEAR_PIN`（2.03 mm 可读性规则）** ✗；② **挪器件 / 符号** ✗；③ **把换掉的脚换回去** ✗。

### ⑦ 七道验收 ✓（**7 / 7** ✓ —— 原始输出留档 `_work/_r80_accept.txt` ✓）

```bat
py -3.13 _work\\_r80_accept.py pixel-pcb-v79.fzz pixel-pcb-v80.fzz _work\\_r80_accept.txt
```

| # | 项 ✓ | 结果 ✓ |
|---|---|---|
| ① | `tools/pcb_check.py pixel-pcb-v80.fzz --nets=pixel_nets.py` | ✓ **判定：✓ 全过** ✓（PCB 一字未动 ✓）|
| ② | `tools/net_group_check.py pixel-pcb-v80.fzz` | ✓ **exit 0** ✓（Fritzing 认得出每张网 ✓）|
| ③ | `_work/view_bytes_diff.py` ＋ `_work/find_gap.py` | ✓ **两个视图逐字节相同** ✓（74 / 122 块 ✓）｜ 端点不重合 **0** 处 ✓ |
| ④ | `_work/sch_probe.py pixel-pcb-v80.fzz --nets=pixel_nets.py` | ✓ **exit 0** ✓：**交叉 10** ✓／⑪ **最小净距 1.3547 mm ≥ 1.000 mm** ✓、低于阈值 **0 对** ✓／★★ ⑫ **文字 ↔ 对象 净距 ≥ 0.1500 mm ⇒ 0 对** ✓／**穿体 0** ✓／**1 网 1 岛** ✓（9/9 ✓）／接地符号每岛 1 ✓／总长 **495.2 mm** ✓ |
| ⑤ | **测试** ✓：库仓 `tools/tests/run_all.py`（**4 个脚本** ✓）＋ 本仓 `tests/run_all.py --with-lib`（本仓 **2 个脚本** ＋ 库仓 **1 处** ＝ **3 处** ✓）| ✓ **两个 runner 都 exit 0** ✓（本轮各新增 1 个：`sch_textgap_selftest.py` ✓ / `text_gap_selftest.py` ✓）|
| ⑥ | **零副作用** ✓：`_work/_z_oldparams.py`（**一个新开关都不加** ✓）＋ `_work/_z_v40.py`（**v40 原命令**重跑 ✓）| ✓ **两条都逐字节相同** ✓（理由 ✓：本轮的新开关**默认关** ✓ ⇒ 不给它时那条链**一个字节都没动** ✓；v40 内层 `.fz` sha1 `7e2e0f360406a4264769bea7e369922245b075bc`／164725 B ✓ 不变 ✓）|
| ⑦ | **渲染** ✓：`tools/render_sch.py` ＋ `tools/render_pcb.py` | ✓ **PNG / SVG 都出** ✓（特写 4 张另裁 ✓ 见 ⑤ ✓）|

### ⑧ 复现命令 ✓（交付件 = `_work/v76.4_byHand.fzz` ＝ `pixel-pcb-v80.fzz` ✓；改前留 `_work/v76.4_byHand.pre-textgap.fzz` ✓）

```bat
set TOOLS=F:\\git\\fritzing-parts-langhua\\tools
copy _work\\v76.4_byHand.fzz _work\\v76.4_byHand.pre-textgap.fzz                             # 先备份 ✓
py -3.13 %TOOLS%\\sch_strip_wires.py _work\\v76.4_byHand.pre-dedupe.fzz _work\\_r0_strip.fzz    # 与 §六十～六十五 同一条链 ✓
py -3.13 %TOOLS%\\render_sch.py _work\\_r0_strip.fzz _work\\_r0_base.png --pins-out=_work\\_r0_pins.py
py -3.13 gen_schematic_wires.py _work\\_r0_strip.fzz _work\\_r0_base.svg _work\\_v80_gen.fzz ^
    --nets=pixel_nets.py --orig _work\\v76.4_byHand.pre-dedupe.fzz --ratio 1.0 --rails --islands=GND ^
    --vlanes=5V@29.778 --decoup --hardbody --corebox --dedupe-symbols --complete-islands ^
    --symmerge --mst-merge --bodyoutline --mst-shape --escs 7.2,12.2,19.4 --text-gap
rem        ↑ 本轮唯一新增的开关 ✓：`--text-gap`（不给值 ⇒ 缺省 **0.15 mm** ✓）
py -3.13 %TOOLS%\\merge_sch.py _work\\v76.4_byHand.pre-dedupe.fzz _work\\_v80_gen.fzz _work\\_v80_out.fzz
copy _work\\_v80_out.fzz _work\\v76.4_byHand.fzz                                               # 就地更新 ✓
copy _work\\_v80_out.fzz pixel-pcb-v80.fzz                                                    # 交付件 ✓
py -3.13 %TOOLS%\\render_sch.py pixel-pcb-v80.fzz pixel-pcb-v80_sch.png                       # 原理图预览 ✓
py -3.13 %TOOLS%\\render_pcb.py pixel-pcb-v80.fzz pixel-pcb-v80_preview.svg --png             # PCB 预览 ✓（PCB 没动 ⇒ 与 v79 的预览**逐字节相同** ✓）
py -3.13 _work\\_r80_accept.py pixel-pcb-v79.fzz pixel-pcb-v80.fzz _work\\_r80_accept.txt
```

★ **一键回旧行为** ✓ ＝ **什么都不加** ✓（`--text-gap` 不写 ⇒ 整条规则不跑 ✓，实测**逐字节相同** ✓）；
显式写法也可以 ✓：`--text-gap=0` ✓（会打一行"闸门关掉 = 旧行为" ✓）。
★ **中间脚本**（都在 `_work/` ✓，本轮新增 8 个 ✓）：`_tg_measure.py`（**改前重叠逐条点名** ✓）、
`_tg_probe.py`（直接调共享判据 ✓）、`_tg_boxes.py`（框/本体对照 ✓）、`_tg_wires.py`（按网列线 ✓）、
`_tg_fix.py`（自动修原型 ✓）、`_spot.py`（按 sketch 坐标裁特写 ✓ —— **不标定** ✓）、
`_r80_accept.py`（七道验收一次跑齐 ✓）、`_r80_accept.txt`（原始输出 ✓）。
★ **改前的量**（要复核 v79 的 3 对 ✓）：`py -3.13 -X utf8 _work\\_tg_probe.py pixel-pcb-v79.fzz` ✓。

### ⑨ 遗留 ✗（下一手 ✓）

- **交叉 10**（目标 ≤9 / ≤7 ✗ 未达 ✓）—— ★ **本轮把上一轮"还能省 #8 一条"那条账更正了** ✗：
  它**不成立** ✓（平面账 ＋ 五手实测见 ⑥ ✓）。**10 = 6 结构性 ＋ 4 换脚逼出来的** ✓；
  要 ≤7 只有三条路（放宽 `CLEAR_PIN` ✗ ／ 挪器件 ✗ ／ 换回脚 ✗）✓ —— **一条都不在本轮授权里** ✓。
  ★ 建议：**先在 Fritzing 里看 `v80`** ✓ —— 若某处线看着"绕"，那多半就是 ⑥ 里记的那几条"躲不掉"的 ✓。
- **`--stub-dive`** ✓（用户点名那一族 ✓）**零收益** ✓ ⇒ 按仓规本该撤掉 ✗，**本轮按用户点名保留** ✓
  （**默认关** ✓ ⇒ 零副作用 ✓；要撤回一句话的事 ✓ —— 说一声就撤 ✓）。
- **第三档「删除冗余值文字」** ✗ 不写 ✓（前两档已治好全部 3 处 ✓）；真要它 ⇒ **先拿一份 Fritzing 导出
  验 `<displayKey>` 的语义** ✓（本仓不许拿未验证的写法当硬闸门 ✗）。
- **文字净距的"真墨迹"口径** ✓ 现在是**外接框**✓（口径与用户原话一字对应 ✓）；若以后要更严
  （按**墨迹**而非外接框 ✓ —— 例如 `1010` 这种数字末端的留白 ✓），得**先量一份渲染** ✓（本仓不许估 ✗）。

---

**六十七、第五十轮（2026-10-09 ✓）：面包板两条规则 —— ① 就近选孔 ✓ ② 能直就直 ✓ ⇒ 发布 `pixel-pcb-v81.fzz` ✓（面包板视图重建 ✓，`pcbView` / `schematicView` 逐字节未动 ✓）**

> 用户原话（2026-10-09 ✓）：
> ①「**`U1.connector0` 接面包板 `pin17F` 明显更近**」⇒ 现在 U1 的某只脚接的孔**不是最近的孔** ✗；
> ②「**`Wire90013131` 应是直线**」⇒ 现在它是**带拐点的折线** ✗。
> ⇒ 立两条**规则**（写进生成器 ✓，**不针对这两处写死** ✗）：**就近选孔** ✓ ＋ **能直就直** ✓。

### ① 用户要的是什么 ✓（两件事 ＋ 一条口径）

| # | 规则 | 判据（一句话 ✓）|
|---|---|---|
| ① | **就近选孔** | 一条跳线的**锚孔**取「**可用孔集合**」里使这条跳线**最短**的那颗 ✓；判据顺序 = **拐点少 → 总长短** ✓（平手再比「离其它已占孔远 → 孔编号小」✓） |
| ② | **能直就直** | 两端**同行或同列** ⇒ **一根直线段**（0 拐点 ✓）；否则**拐点最少优先**、**其次总长最短** ✓；只有「必须避让」（重叠 ✗／穿本体 ✗／盖接线孔 ✗）才允许多拐点 ✓ |
| — | ★ **口径**（用户定 ✓） | **面包板视图里跳线交叉是允许的** ✓ ⇒ **不比交叉** ✗，只比「**拐点 / 长度 / 避让**」✓ |

「**可用孔**」= ① 没被占（没插脚 ✗、没有别的线端 ✗）**且** ② **不会把两张不同的网并到一起** ✗
（半排/母线内部是连通的 ✓ ⇒ 必须查「目标孔所在 bus 里已有的网」✓）；**移完还要逐网重算连通** ✓
（从零算 ✗：并查集只增不减会骗人 ✓）。
★ **明确不动** ✗：**插进孔的脚** ✓ —— 脚插哪个孔是**摆位**的一部分 ✓，而且 `pcbView`/`schematicView`
里也声明着 ✗ ⇒ 动它会破坏「那两张视图逐字节不变」✗ ⇒ 一律**只报不改** ✓（数值见 ⑥ ✓）。
例外 = **没插孔的脚**（`U1` 的裸焊盘 `EPAD` ✓）—— 它**只能靠线接** ✓ ⇒ 它的线端**可以选孔** ✓。

### ② 先量出来 ✓（改前 `_work/v76.4_byHand.pre-bb.fzz` ✓ —— 两处点名的都在里面 ✓）

| 用户点名 | 改前**量到的**（逐条 ✓）| 改后 |
|---|---|---|
| ① `U1.connector0` ↔ `pin17F` | ★ 对不上「`connector0`」这个名字 ✓：`U1.connector0`（= `PD7`）**插在 `pin27F`** ✓、是**备用脚** ✓、而它的最近孔**就是它自己**（距离 0 ✓）。用户指的是 U1 自画上标着 **「0」** 的那只脚 = **`connector20`（裸焊盘 `EPAD` ✓）**——U1 **唯一没插孔、只能靠线接**的脚 ✓。改前它的 GND 线锚在 **`pin19Z`**（下轨）＝ **25.2 mm** ✓ | 锚到 **`pin17G`** ＝ **6.5 mm** ✓（**省 18.7 mm** ✓；`pin17F` 为什么不能选 ⇒ 见 ⑥ ✓） |
| ② `Wire90013131` | 那根跳线 = **`Wire90013131`＋`90013132`＋`90013133`**：`pin20I`→`(28,I)`→`pin28H`→`(35,H)`→`pin35H` = **3 段 / 2 拐点 / 40.6 mm** ✓；★ 中间那段 `(28,I)→(28,H)` **同在一个 bus 里**（第 28 列 F…J 是同一块铜 ✓）—— 电学上**白绕** ✓ 纯属画出来的拐点 ✗ | = **`Wire90015583`**：`pin20G → pin35G` **1 段 / 0 拐点 / 38.1 mm** ✓✓（**一根直线** ✓） |

**改前全表**（探针 ✓，只读 ✓）：`43 根跳线 / 83 段 ｜ 总长 620.9 mm ｜ 交集 65（交叉 64 ＋ T 1 ✓）｜
斜线段 45 ｜ 重叠 **1** ✗ ｜ 遮挡接线孔 **10** ✗ ｜ 拐点直方图 `{0:22, 1:11, 2:7, 3:2, 9:1}` ｜
★ ① **GND 裂成 8 块** ✗（几何上不连通 —— 一堆"挂在旧坐标上的废线" ✗，见下 ✓）、⑤ 重叠 1 ✗、⑥ 压本体 4 ✗`。

★ 顺带查出**三个真病**（都不是本轮两条规则本身 ✓，但都挡在"面包板视图合格"前面 ✗）：
1. **`audit_layout.py` 读的是**换脚前**的老网表** ✗（`gen_schematic_wires.NETS` ✓）⇒ ⑥ 把
   `DATA_IN`/`DATA_OUT`/`RC` 三条**假报**成"不连通"✗（换脚后 `PA1/PA2/PD0` 已经不在这三张网上了 ✓）
   ⇒ 改成读**项目数据** `pixel_nets.py`（`projdata` ✓）✓ ⇒ **⑥ 归 0** ✓。
2. **零件上留着指向旧导线的 `<connect>`** ✗（`bb_route4` 注释里点过这个病 ✓，但只清了**板子**那张表 ✗）
   ⇒ `pcb_check` ⑫ 报「**悬空声明** 1 条」✗（`U1` 那只裸焊盘的旧线 `90013134` ✓）⇒ 生成器里
   **一并清掉** ✓（实测 52 条 ✓）⇒ `pcb_check` **✓ 全过** ✓。
3. **图例色条被生成器删光** ✗（"一根不接任何东西的 `Wire`" 被当成旧导线 ✗）⇒ 新增 `--keep-deco` ✓，
   把这 9 根**留着** ✓（渲染里看得见 ✓）。
★ 还有一件事**如实记** ✓：改前那 43 根里有 **24 根是废线** ✗ —— 它们的 `<connect>` 声明接在元件脚上 ✓、
但**几何停在旧摆位**（如 `(146.8,64.3)` ✓）⇒ `bb_compare` 报「交集 65」的一大半就是它们 ✗。
本轮"从零重布"（`bb_route4` ✓）把它们**一并清掉** ✓。

### ③ 判据与实现要点 ✓（一份实现 ✓ ＋ 两个开关 ✓ 缺省**都关** ✓）

| 落在哪 | 是什么 |
|---|---|
| `tools/bb_route4.py`（库仓 ✓）| **唯一实现** ✓：`pass_near_hole()` ✓（规则①）、`pass_straight()` ✓（规则②）、`_score(pts)` = **`(拐点数, 总长)`** ✓（**不含交叉** ✗）、`_graph_ok()` = 逐网从零重算连通 ＋ 一 bus 一网 ✓、`_nearest_holes()` = **可用孔**里最近的 `--near-k` 个 ✓（缺省 **6** ✓） |
| 开关 | `--near-hole` ✓ / `--straight` ✓ / `--keep-deco` ✓ / `--near-k=N` ✓ —— **缺省全关** ✗ ⇒ **不给开关时一字不动** ✓（实测**逐字节相同** ✓，见 ⑤ ⑥ ✓）|
| 硬闸门 | **一次也不放宽** ✓：重叠 ✗／穿**别的**元件本体 ✗／盖住接线孔 ✗／落进已占的孔 ✗ —— 全用**已有**的 `route_cost()` 判 ✓（与最终自检同一把尺子 ✓）|
| 探针 | 项目侧 `tools/bb_probe.py` ✓（**只读 ✓ 不 import 生成器** ✗）：11 项逐条量交付件 ✓，`exit 0/1` ✓ |
| 自测 | 项目侧 `tests/bb_rules_selftest.py` ✓（仓规 ✓：项目测试放 `hardware/pixel/tests/` ✓）—— 小尺子 ✓ ＋ **交付件回归锁**（28 段 / `{0:11,1:7,2:1}` / 337.1 mm ✓）＋ 开关缺省关 ✓ |
| 规则正文 | 库仓 `docs/breadboard-routing-rules.md`（A11 / A12 ＋ 变更记录 ✓）|

### ④ 改前 / 改后对照 ✓（两把独立尺子：`tools\bb_probe.py` ✓ ＋ 库仓 `bb_compare.py` ✓ ＋ `audit_layout.py` ✓）

| 指标 | 改前 `pre-bb` | **改后 `pixel-pcb-v81.fzz`** |
|---|---|---|
| 跳线 / 段数 | 43 根 / 83 段 | **19 根 / 28 段** ✓ |
| 拐点直方图 | `{0:22, 1:11, 2:7, 3:2, 9:1}` | **`{0:11, 1:7, 2:1}`** ✓（0 拐点 11 根 ✓）|
| **总长** | 620.9 mm | **337.1 mm** ✓（**−283.8 mm ＝ −45.7%** ✓）|
| 交集 | 65（交叉 64 ＋ 搭线 1） | **3（交叉 3 ＋ 搭线 0）** ✓（★ 交叉**允许** ✓ 见 ① ✓）|
| 斜线段 | 45 | **5**（预算 ≤4 ✗ 超 **1** ⇒ 记在 ⑥ ✓）|
| 引线重叠 | **1** ✗ | **0** ✓ |
| 遮挡接线孔 | **10** ✗ | **0** ✓ |
| 拥挤度 | 6.04 | **0.46** ✓ |
| `audit_layout.py`（①…⑥） | **20 处** ✗（②13 ③1 ⑥3）| **0 处** ✓（①②③④⑤⑥ 全 0 ✓）|
| 探针 11 项 | **✗ 3 项**（① GND 裂 / ⑤ 重叠 / ⑥ 压本体）| **✓ 全过** ✓ |
| 用孔数 / 插脚孔 | 37 / 44 | **37 / 44** ✓（不变 ✓）|

| | |
|---|---|
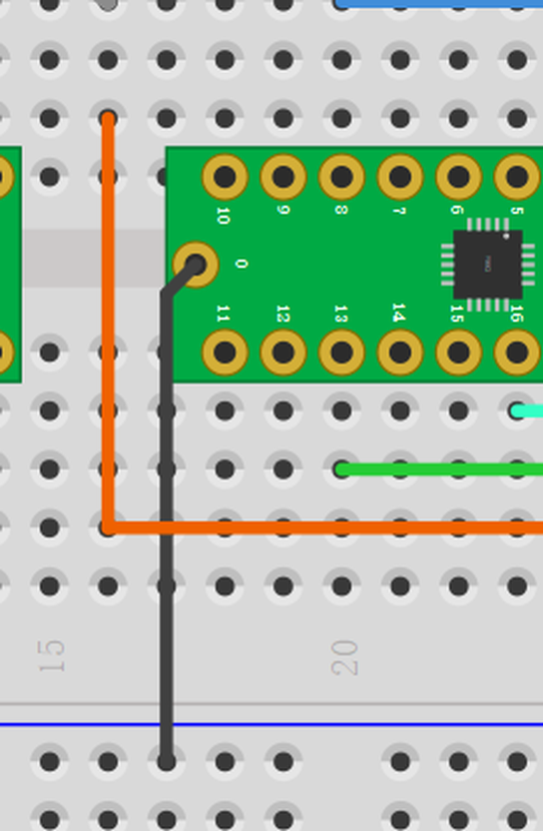
[picture p44: hardware/pixel/pixel-pcb-v81_z1_before.png]
特写① 改前
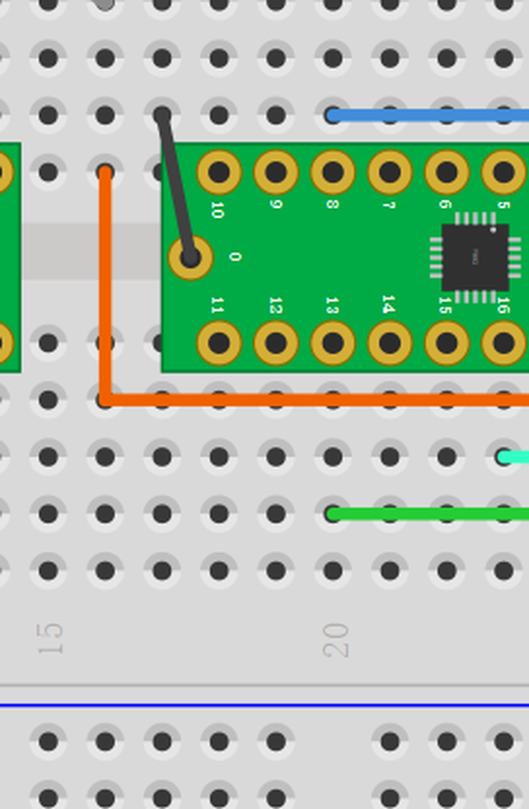
[picture p45: hardware/pixel/pixel-pcb-v81_z1_after.png]
特写① 改后
|  |  |
| **特写① 改前** ✓：`U1` 的裸焊盘（板上印 **0** ✓）那根黑线**一路竖直走到下轨** ✓（锚 `pin19Z` ✗ 25.2 mm ✓）| **特写① 改后** ✓：就近接 **`pin17G`** ✓（6.5 mm ✓）—— 用户点名的「`pin17F` 明显更近」就在这一带 ✓ |
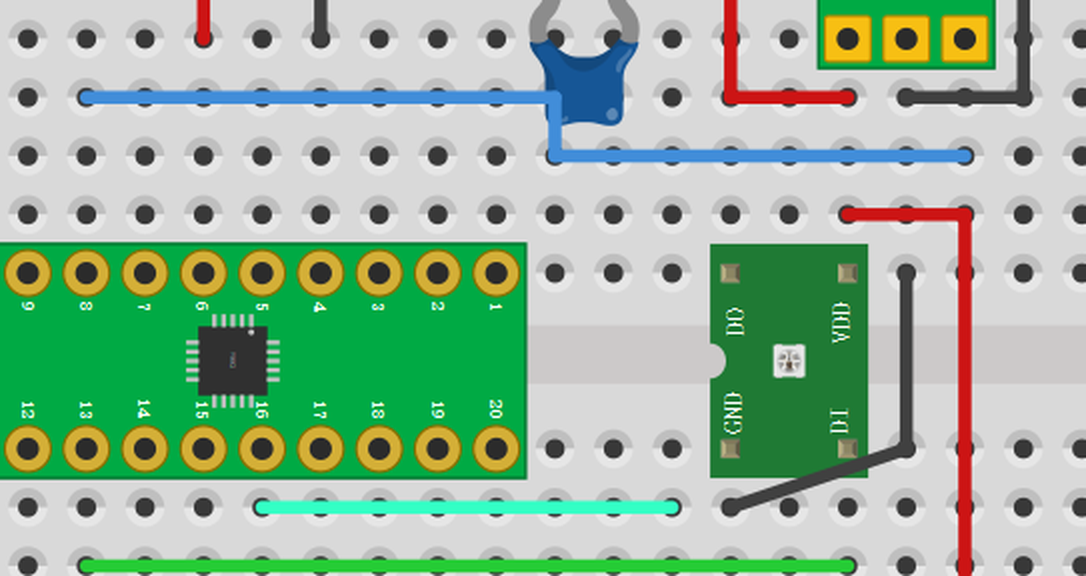
[picture p46: hardware/pixel/pixel-pcb-v81_z2_before.png]
特写② 改前
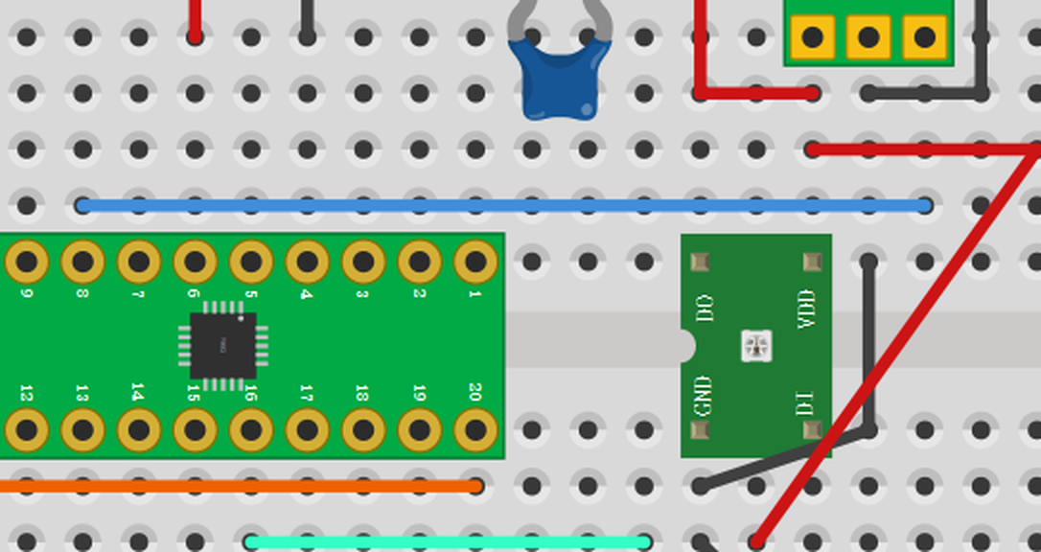
[picture p47: hardware/pixel/pixel-pcb-v81_z2_after.png]
特写② 改后
|  |  |
| **特写② 改前** ✓：`DATA_IN` 蓝线在第 28 列**折了一下** ✓（`Wire90013131`＋`90013132`＋`90013133` ✗ 3 段 / 2 拐点 ✓）| **特写② 改后** ✓：**一根直线** ✓（`pin20G → pin35G` ✓ 1 段 / 0 拐点 ✓ —— 用户点名的「`Wire90013131` 应是直线」✓）|
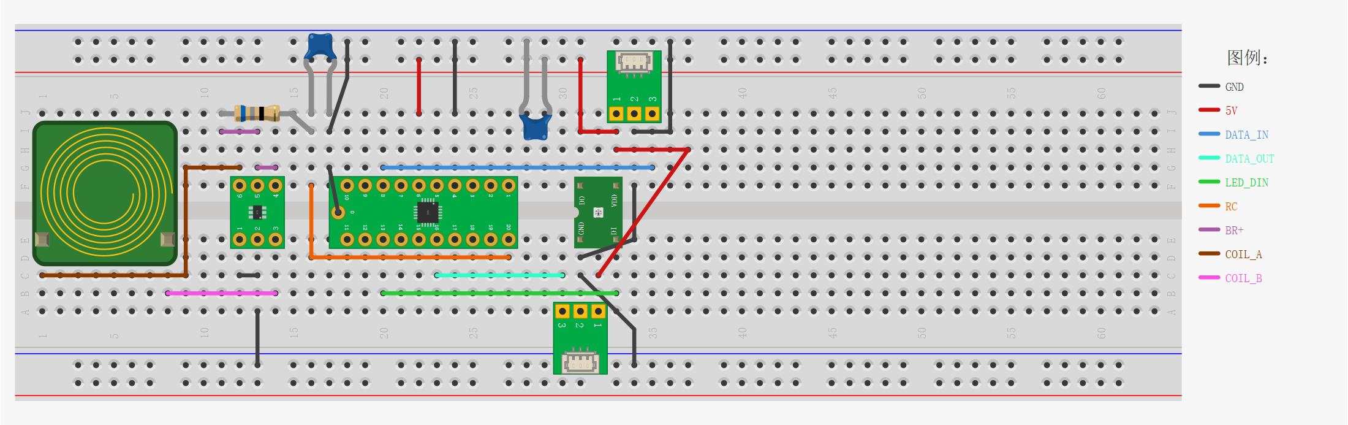
[picture p48: hardware/pixel/pixel-pcb-v81_bb.png]
面包板全图
|  | 面包板视图全图 ✓（`pixel-pcb-v81_bb.png/svg` ✓，`render_bb.py` ✓ 渲 ✓）|

### ⑤ 五道验收 ✓（原文存 `_work\_bb1_rules.log` ＋ `_work\_bb\probe_before.txt` ✓）

| # | 验收 | 结果 |
|---|---|---|
| ① | `py -3.13 %TOOLS%\pcb_check.py pixel-pcb-v81.fzz --nets=pixel_nets.py` | ✓ **判定：✓ 全过** ✓（⑩ 声明 105 条 ✓ 不合格 0 ✓；⑫ 悬空声明 **0** ✓ —— 改前是 1 ✗）|
| ② | `py -X utf8 tools\net_group_check.py pixel-pcb-v81.fzz` | ✓ **exit 0** ✓（9 张网 Fritzing 都认得出 ✓）★ **旧尺子** ✗ ⇒ 见 §六十八 ⑥ ✓：新尺子下 v81 = **exit 1** ✗（有 2 张网被面包板的跨视图记录**并掉**了 ✗）|
| ③ | `_work\view_bytes_diff.py` ＋ `_work\_bb\viewcheck.py` | ✓ **`pcbView` 74 块 ＋ `schematicView` 65 块逐字节相同** ✓（拼哈希 `24141dd900659867` ✓ 两边同 ✓）|
| ④ | `py -X utf8 tools\bb_probe.py pixel-pcb-v81.fzz` | ✓ **exit 0（11 项全过）** ✓：9 网逐脚连通 ✓／一 bus 一网 ✓／**备用脚 15 只零连接** ✓／声明双向 ✓／悬空端 0 ✓／重叠 0 ✓／压本体 0 ✓／**孔占用唯一** ✓／**「不是最近孔」= 0** ✓／拐点直方图 ✓／总长 337.1 mm ✓ |
| ⑤ | `tests\run_all.py --with-lib` ＋ 库仓 `tools\tests\run_all.py` | ✓ **两个 runner 都 exit 0** ✓（本轮各新增 1 个 ✓：`bb_rules_selftest.py` ✓）|
| ⑥ | **零副作用** ✓：不给新开关重跑 | ✓ **与改前逐字节相同** ✓（同一输入 ✓：内层 `.fz` 两边 `True` ✓ —— 因为两条规则**缺省关** ✓）|

### ⑥ 复现命令 ✓（交付件 = `_work/v76.4_byHand.fzz` ＝ `pixel-pcb-v81.fzz` ✓；改前留 `_work/v76.4_byHand.pre-bb.fzz` ✓）

```bat
set TOOLS=F:\git\fritzing-parts-langhua\tools
copy _work\v76.4_byHand.fzz _work\v76.4_byHand.pre-bb.fzz                                  # 先备份 ✓
py -3.13 -X utf8 %TOOLS%\bb_route4.py _work\v76.4_byHand.pre-bb.fzz _work\_bb1_none.fzz ^
    --nets=pixel_nets.py                                                                  # ★ 零副作用对照 ✓（一字不动 ✓）
py -3.13 -X utf8 %TOOLS%\bb_route4.py _work\v76.4_byHand.pre-bb.fzz _work\_bb1_rules.fzz ^
    --nets=pixel_nets.py --keep-deco --near-hole --straight                                # ★ 两条规则 ＋ 留图例 ✓
rem        ↑ 规则①/② 的开关 ✓；`--near-k=6` 可调"每端只看最近几颗孔"（缺省 6 ✓）
py -3.13 -X utf8 %TOOLS%\merge_sch.py _work\v76.4_byHand.pre-bb.fzz _work\_bb1_rules.fzz ^
    _work\_v81_out.fzz --view=breadboardView                                               # 只并面包板视图 ✓
copy _work\_v81_out.fzz _work\v76.4_byHand.fzz                                             # 就地更新 ✓
copy _work\_v81_out.fzz pixel-pcb-v81.fzz                                                  # 交付件 ✓
py -3.13 -X utf8 %TOOLS%\render_pcb.py pixel-pcb-v81.fzz pixel-pcb-v81_preview.svg --px 12 --png
py -3.13 -X utf8 %TOOLS%\render_sch.py pixel-pcb-v81.fzz pixel-pcb-v81_sch.png 2200
py -3.13 -X utf8 %TOOLS%\render_bb.py  pixel-pcb-v81.fzz pixel-pcb-v81_bb.png  2200        # ★ 面包板预览 ✓
py -3.13 -X utf8 tools\bb_probe.py pixel-pcb-v81.fzz                                       # 探针 ✓
```

★ **一键回旧行为** ✓ ＝ **什么都不加** ✓（`--near-hole` / `--straight` / `--keep-deco` 都不写 ⇒
旧行为 ✓，实测**逐字节相同** ✓）；只想留"就近选孔"不要"能直就直" ⇒ 只写 `--near-hole` ✓
（那一档：29 段 / 343.6 mm / **交集 0** ✓ / **斜线段 4** ✓ —— 见 ⑥ ✓）。

### ⑦ 遗留 ✗（逐条给数值 ✓）

1. ★ **`pin17F` 明明更近、却不能选** ✗（这正是用户点名那一处 ✓）：`U1` 的裸焊盘在
   `(157.5, 94.5)` ✓，`pin17F` = `(153, 81)` ✓ ⇒ 直连 **14.2 单位 ＝ 4.0 mm** ✓，
   而落子 `pin17G` = `(153, 72)` ⇒ **22.9 单位 ＝ 6.5 mm** ✓ —— **`pin17F` 近 2.5 mm** ✗。
   **不能选的理由 ✓**：它**压在 `U1` 自己的本体框边线上** ✓（框 `x 153.0…247.5`、
   `y 76.5…112.5` ✓；`pin17F` 离框边 **0.00 单位** ✓）⇒ 命中规则 ④「孔不得落在元件本体框内」✗
   （`bb_route4` 的 `blocked` ✓）⇒ **物理上插不进** ✓。要它 ⇒ 得**挪器件**或**改摆位** ✗（不在本轮授权 ✓）。
2. **斜线段 5 ✗（预算 ≤4 ✓ 超 1 ✓）**：规则②优先「拐点少」✓ ⇒ 一条 **45° 斜线 = 0 拐点** ✓
   会被优先于 **L 形 = 1 拐点** ✓（如 5V 的 `pin33H → pin32C`：直斜线 72 单位 ✓ vs L 形
   72 单位 ＋ 1 拐点 ✓）⇒ 全长**不变**、拐点**少 1** ✓，代价是多 1 条斜线 ✗。
   想要 ≤4 ⇒ **只开 `--near-hole`** ✓（斜线段 **4** ✓、交集 **0** ✓，代价：多 1 拐点 ＋ 6.5 mm ✓）。
3. **`--keep-deco` 与 `--straight` 是"本轮的默认动作" ✓ 但不是缺省开关** ✓：不给开关就**回旧行为** ✓
   （包括"图例色条被删" ✗）—— 这是**零副作用的代价** ✓，按仓规**照实记** ✓。
4. **装饰线 10 → 9** ✗：`bb_compare` 的「图例装饰」少 1 根 ✓ —— 那 1 根本来**同时**挂在
   一条真接线上（不算纯装饰 ✓）⇒ 重布后它归了正职 ✓（不是丢了 ✓，量得出来：`用孔 37` ✓ 不变 ✓）。
5. **`--near-k=6` 是"近似的就近"** ✓（每端只看最近 6 颗孔 ✓）：理论上更远的孔也可能因"形状"更优 ✓
   ⇒ 全表扫描会更慢 ✓（本板 830 孔 × 19 根 × 模板 ⇒ 实测不可接受 ✓）⇒ 缺省取 6 ✓，需要时可调大 ✓。
6. **`audit_layout.py` 的 ④ 有 6 条"未验证" ⚠**（`RC` 两块网标签 ✓ / `Ground1/2` ✓ / `Via1/2` ✓）：
   它们是**原理图/PCB 专有**的 core 件 ✓（`.fzp` 在 `:\resources\parts\core\` 下、**磁盘上没有** ✗）
   ⇒ 量不到框 ⇒ **不计入违规** ✓（面包板上的 9 件**全部量到** ✓ ⇒ **真违规 0** ✓）。

---

**六十八、第五十一轮（2026-10-10 ✓）：用户报「PCB 不用再布线了，Fritzing 仍说两根没布好」✗ ⇒ 查出**跨视图 glue 的旧账** ✗ ⇒ **只删声明、几何一字不动** ⇒ 发布 `pixel-pcb-v82.fzz` ✓**

### ① 用户报的件 ✓（原话 ✓）

> 用户 2026-10-10：「现在只剩下 PCB 视图有问题 ✓，根据之前对 PCB 的检查，**已经不需要再布线了** ✓，
> 但是 Fritzing **仍然说有两根线没有布好** ✗（状态栏：「**2 个连接仍然需要布线**」✗），请检查 ✓。」

★ 关键是**两边都对** ✗✓：我们三套闸门**全过** ✓（`pcb_check --nets` ✓ ①②…⑫ ✓、`net_group_check` ✓、
面包板探针 ✓、铜的岛/重叠/贴脚/穿体全 0 ✓），而状态栏也**没说错它自己那套账** ✓
—— ✗ **不是同一个口径** ✗（这正是要立第二把尺子的理由 ✓）。

### ② 先复现 Fritzing 的口径 ✓（新探针 `tools\pcb_rats_probe.py` ✓，只读 ✓）

口径**逐条照源码** ✓（出处见工具头部表 ✓）：状态栏那句 = `mainwindow.cpp:2298` ✓、
计数 = `sketchwidget.cpp:7013` 调 `GraphUtils::scoreOneNet` ✓、
★ **「还剩几个」= 该网连通片数 − 1** ✓（`scoreOneNet` 末尾的 `check[]` ✓，2026-10-02 读出来的 ✓）、
分网 = 本视图 `<connect>` ＋ 同脚跨层 ＋ 零件内部 bus ✓（`connectoritem.cpp:1340` ✓、
`itembase.cpp:559` ✓）、判"通没通"只看**几何命中** ✓（`connectoritem.cpp:1972` ✓）、
导线要 `wireFlags & 4` ✓（`graphutils.cpp:550` ✓）。
★ 「铜块」这层**不自己重写** ✗ —— 用库仓 `pcb_check.py` ⑤ 那份**已复核过**的 `groups` ✓。

★ **两向都要能对上** ✓（只会放行的尺子等于没尺子 ✗）：

| 文件 | 用户读到的 Fritzing | 本探针 | |
|---|---|---|---|
| `pixel-pcb-v59.fzz` | 「**7 中的 5** …，**2** 个连接件仍然需要布线」✗ | **M=7 / K=2** ✓ | 对 ✓ |
| `_work/v76.4_byHand.fzz`（v81 的底 ✓） | 「**7 中的 5** …，**2** 个接插件仍然需要布线」✓（已截图核对 ✓） | **M=7 / K=2** ✓ | 对 ✓ |
| `pixel-pcb-v68.fzz` | **三视图都正确** ✓（用户 2026-10-05 读的 ✓） | **M=9 / K=0** ✓ | 对 ✓ |
| `pixel-pcb-v81.fzz` ✗ | 「… **2 个连接仍然需要布线**」✗（本手 ✓） | **M=7 / K=2** ✓ | 对 ✓ |

### ③ 根因链路 ✓（逐条给数值 ✓）

**查出来的不是"少了两根线" ✗，是面包板在 PCB 视图里**偷偷并网** ✗**：

1. 交付件里的面包板实例 `Breadboard1`（mi `5785` ✓）**在 `pcbView` 里也有段落** ✓
   —— 46 个孔 ＋ **47 条记录** ✓（核心面包板件给每个孔都声明了 `breadboardbreadboard` 层 ✓
   ⇒ 孔在 PCB 视图里**也有连接器项** ✓，看不见 ✗ 但在网表里 ✓）；
2. ★★ 那 46 条孔记录是**上一轮"就近选孔"改孔之前的旧账** ✗：逐只脚核过 ✓
   （`_work\fz_holediff.py` ✓ 45 只脚里 **44 只对不上** ✗）—— 例：
   `D3.connector0` 真插 `pin12E` ✓ 却声明成 `pin16E` ✗（**差 4 列** ✓）；
   `J1.connector0` 真插 `pin33J` ✓ 却声明成 `pin46J` ✗（**差 13 列** ✓）；
   `L1.connector0` 真插 `pin1E` ✓ 却声明成 `pin16J` ✗；
3. ★ 其中 **3 只脚被两只孔同时声明** ✗（物理上不可能 ✓）：`C1.connector0`（`pin16J`＋`pin22F` ✗）、
   `C1.connector1`（`pin17J`＋`pin21F` ✗）、`R1.connector1`（`pin16I`＋`pin22G` ✗）；
4. 再加上面包板件自己的 **130 条内部 bus** ✓（同一条带宽 5 孔 ✓）⇒ 两条 **glue 通道** ✗ 就成立了 ✓：
   · **孔 `pin16J` 一只孔同时声明 `L1.connector0`（`COIL_A` ✓）与 `C1.connector0`（`RC` ✓）**
     ⇒ 把 **`RC` ＋ `COIL_A` 并成一张** ✗；
   · **bus `pin17F/pin17G/pin17J`**（同带 ✓）声明了 `D3.connector4`＋`R1.connector0`（`BR+` ✓）
     与 `C1.connector1`（`GND` ✓）⇒ 把 **`GND` ＋ `BR+` 并成一张** ✗；
5. ⇒ 在 Fritzing 眼里 **9 张网变成 7 张** ✓（＝用户看到的「**7 中的 5**」✓），
   而这两张"并出来的网"各自碎成 **2 块铜** ✓（`GND` 9 块铜 ✓ vs `BR+` 3 只脚 ✓；
   `RC` 3 只脚 ✓ vs `COIL_A` 2 只脚 ✓）⇒ **1 ＋ 1 ＝ 2 条没布** ✓✓
   （＝用户看到的「**2 个连接仍然需要布线**」✓）。两条鼠线**最近的那一对**（Fritzing 就画在那里 ✓）
   也量出来了 ✓（`_work\fz_pair.py` ✓）：

| 鼠线 | 一端 | 另一端 | 差 |
|---|---|---|---|
| `GND`↔`BR+` | `C1.connector1` (42.9999, 17.1000) mm | `D3.connector3` (41.6810, 17.9220) mm | **1.5541 mm** ✗ |
| `RC`↔`COIL_A` | `L1.connector0` (43.9309, 20.3220) mm | `R1.connector1` (42.8999, 19.0000) mm | **1.6765 mm** ✗ |

探针给出的原文 ✓：

```
   ⚠ 跨视图 glue ✗：孔 pin16J  把 C1.connector0、L1.connector0 牵在一起
   ⚠ 跨视图 glue ✗：bus pin16F 把 pin16F（D3.connector5）、pin16I（R1.connector1）、pin16J（C1.connector0、L1.connector0） 牵在一起
   ⚠ 跨视图 glue ✗：bus pin17F 把 pin17F（D3.connector4）、pin17G（R1.connector0）、pin17J（C1.connector1） 牵在一起
   ⚠ 跨视图 glue ✗：bus pin22F 把 pin22F（C1.connector0）、pin22G（R1.connector1） 牵在一起
   ⇒ **M（Fritzing 会算成几张网）= 7** ✓｜**K（还剩几条没布）= 2** ✓
     ✗ `BR+/GND` 焊盘 12 ⇒ **2 块**：…9 只（GND）… ｜ D3.connector3＋D3.connector4＋R1.connector0（BR+）
     ✗ `COIL_A/RC` 焊盘 5 ⇒ **2 块**：D3.connector5＋L1.connector0 ｜ C1.connector0＋R1.connector1＋U1.connector19
```

★ **与 v69/v77 那类病不是一回事** ✓：那类是真断铜 ✗（底图剥瘦 ✓）；本手这**铜全通** ✓、
断的只是"Fritzing 眼里那张网" ✗ ⇒ 它要的是**面包板那半边的账** ✓。

### ④ 修法 ✓（**A：只改声明** ✓ —— 几何/摆位/面包板视图**一字不动** ✗）

新工具 `tools\fz_deglue_records.py` ✓（只读查 ＋ 写新件 ✓）：

* **只删 `<pcbView>` 段里的"跨视图记录"** ✗（94 条 ✓ ＝ 面包板自己 47 ✓ ＋ 45 只脚 47 ✓），
  **两个方向都删** ✗ —— 只删一半**没用** ✗（记录是**双向**的 ✓，库仓 `fz_deglue_views.py` 实测记过 ✓）；
* ✗ 不碰 `<geometry>` / `<transform>` / 铜声明 ✗；✗ 不碰面包板视图 ✗；✗ 不删/不加任何视图段 ✗
  （`pcbView` 74 ✓ / `schematicView` 65 ✓ / `breadboardView` 66 ✓ **不变** ✓）；
* 自检 ✓：XML 可解析 ✓、`<connect` 只减 94 ✓、面包板视图段**逐字节相同** ✓、
  视图段数不变 ✓、**逐行核**（改的只有那 90 行 `<connect … breadboardbreadboard/>` ✓，其余一行未动 ✓）、
  包内条目时间戳照抄 ⇒ **同一输入产出逐字节相同** ✓（可复现 ✓）；
* ★ 为什么**不**走 v68 那条路 ✗（库仓工具把面包板的 `<pcbView>`/`<schematicView>` **整段删掉** ✓）：
  那条**也修得好** ✓（用户 2026-10-05 验过 ✓），但会**动视图段** ✗ ⇒ 本手选更外科的那条 ✓。

### ⑤ 六道验收 ✓（**原文**存 `_work\_r82_accept.txt` ✓）

| # | 验收 | 结果 |
|---|---|---|
| ① | `py -X utf8 %TOOLS%\pcb_check.py pixel-pcb-v82.fzz --nets=pixel_nets.py` | ✓ **判定：✓ 全过** ✓（⑩ 声明 105 条 ✓ 不合格 **0** ✓；⑫ 悬空声明 **0** ✓；焊盘 45 ✓／走线 52 ✓／过孔 5 ✓）|
| ② | `py -X utf8 tools\net_group_check.py pixel-pcb-v82.fzz` | ✓ **exit 0** ✓（9 张网都在一块铜里 ✓、**跨视图 glue 证据 0 条** ✓）|
| ③ | `_work\view_bytes_diff.py v81 v82 pcbView schematicView breadboardView` | ✓ `schematicView` **逐字节相同** ✓（`e720b6e5a06e9de1` ✓）、`breadboardView` **逐字节相同** ✓（`d08b63ff3564a552` ✓）；`pcbView` **只有那 10 个实例块少了 94 条不可见记录** ✗（几何属性语义项一字未动 ✓，见下 ✓）|
| ③b | **渲染三视图**（`render_pcb`/`render_sch`/`render_bb` ✓） | ✓ **逐字节相同** ✓✓：PCB `_r81.svg`/`_r82.svg` 同为 `0192EAA5…EA458B` ✓（132559 字节 ✓）、原理图 `_s*.png` 同为 `91FB99E2…D0880EC` ✓、面包板 `_b*.png` 同为 `F4E67780…2C12832` ✓ ⇒ **用户看到的三张图一模一样** ✓ |
| ④ | `py -X utf8 tools\bb_probe.py pixel-pcb-v82.fzz` ／ `_work\sch_probe.py pixel-pcb-v82.fzz` | ✓ **两个都 exit 0** ✓（面包板 11 项全过 ✓：「不是最近孔」0 ✓／总长 337.1 mm ✓；原理图逐岛 ✓）|
| ⑤ | `tests\run_all.py --with-lib` ＋ 库仓 `tools\tests\run_all.py` | ✓ **两个 runner 都 exit 0** ✓（本仓 4 个 ＋ 库仓 1 个 ＝ 5 处 ✓；本手新增 `tests\pcb_rats_selftest.py` ✓）|
| ⑥ | **零副作用** ✓ | ✓ 没动任何生成器/开关 ✓（本轮只删交付件里的**不可见声明** ✓）⇒ 生成链照旧 ✓；修法器**可复现** ✓（一跑就得逐字节相同的件 ✓）|
| ⑦ | **新增闸门** ✓ | ✓ `tools\pcb_rats_probe.py`（**K 必须 = 0** ✓）＋ `tools\fz_deglue_records.py --check`（**跨视图记录必须 = 0** ✓）＋ `tests\pcb_rats_selftest.py`（**两向锁** ✓：v81 必须报 2 ✗、v82 必须报 0 ✓）|

### ⑥ ★ 顺手查出一件更重要的事 ✗：**旧闸门奖励了 bug** ✗ ⇒ 已重标定 ✓（诚实记 ✓）

`tools\net_group_check.py` 的旧判据 ✗ 是"把**所有视图**的 `<connect>` 并成一张图 ＋ 数块里元件脚 ≥ 3" ✓
—— 它的两块**都不是 Fritzing 的语义** ✗：① `<connect>` 只在**当前视图**里解析 ✓（`itembase.cpp:559` ✓）；
② 那些跨视图记录是把网**并小**（9→7 ✓），✗ 不是把网"撑大"到 ≥3 ✗。**实测两个反例** ✓：

| 文件 | 用户实测 | 旧判据 | 新判据 |
|---|---|---|---|
| `pixel-pcb-v68.fzz` ✓ | **三视图都正确** ✓ | ✗ 9 处"网不存在" ✗ | ✓ exit 0 ✓ |
| `pixel-pcb-v81.fzz` ✗ | PCB 报「2 个连接仍然需要布线」✗ | ✓ exit 0 ✗ | ✗ 4 处（2 张网被并 ✗） |

⇒ **旧尺子把"并网"当成了"网存在"** ✗（有病的 v81 过 ✓、正确的 v68 挂 ✗）。
★ 所以本手把它**重标定**成**逐视图**的口径 ✓（A 同块 ✓／B 不许并网 ✓／C ≥2 只脚 ✓／D 脚得有连接器项 ✓），
实现**只有一份** ✓（入口 `net_group_check.py` import `pcb_rats_probe.check()` ✓）。
⚠ **历史条目的读法** ✗：README 里那些「`net_group_check` ⇒ exit 0」（v77…v81 那几处 ✓）是**旧尺子**的结论 ✓，
新尺子下它们会报 ✗ ✓ —— 那些版本的**真状态**以**新探针**（`pcb_rats_probe`）为准 ✓。

### ⑦ 复现命令 ✓（交付件 = `pixel-pcb-v82.fzz` ✓；改前 = `pixel-pcb-v81.fzz` ✓）

```bat
set TOOLS=F:\git\fritzing-parts-langhua\tools
py -3.13 -X utf8 tools\fz_deglue_records.py pixel-pcb-v81.fzz --check                rem 查（94 条 ✗ ⇒ exit 1）
py -3.13 -X utf8 tools\fz_deglue_records.py pixel-pcb-v81.fzz pixel-pcb-v82.fzz      rem 修（写新件 ✓）
py -3.13 -X utf8 %TOOLS%\pcb_check.py pixel-pcb-v82.fzz --nets=pixel_nets.py         rem ① ✓ 全过
py -3.13 -X utf8 tools\net_group_check.py pixel-pcb-v82.fzz                          rem ② exit 0
py -3.13 -X utf8 tools\pcb_rats_probe.py pixel-pcb-v82.fzz                           rem ⑦ M=9 / K=0
py -3.13 -X utf8 tools\bb_probe.py        pixel-pcb-v82.fzz                          rem ④ exit 0
py -3.13 -X utf8 _work\sch_probe.py       pixel-pcb-v82.fzz                          rem ④ exit 0
py -3.13 -X utf8 tests\run_all.py --with-lib                                         rem ⑤ 两个 runner ✓
py -3.13 -X utf8 %TOOLS%\render_pcb.py pixel-pcb-v82.fzz pixel-pcb-v82_preview.svg --px 12 --png
py -3.13 -X utf8 %TOOLS%\render_sch.py pixel-pcb-v82.fzz pixel-pcb-v82_sch.png 2200
py -3.13 -X utf8 %TOOLS%\render_bb.py  pixel-pcb-v82.fzz pixel-pcb-v82_bb.png  2200
```

### ⑧ 遗留 ✗（逐条 ✓）

1. ★ **那 46 条孔记录的"来源"没查** ✗：写回器为什么按**旧孔**写 `pcbView` 的孔记录 ✓
   （是"面包板改造之后的写回没跟上" ✓ 还是"另存时按旧快照写" ✓）⇒ 下一手查生成链 ✓
   （本轮只清理了症状 ✓；根子上要**让这类记录根本不生成** ✓）；
2. **顺手可做** ✗：把"**跨视图记录 = 0**"也写进**生成器出口** ✓（现在只在交付前用 `fz_deglue_records --check` 守 ✓）；
3. **`net_group_check` 的 A 判据只覆盖 PCB 视图** ✓：面包板/原理图两视图各有自己的探针 ✓
   （`tools\bb_probe.py` ✓／`_work\sch_probe.py` ✓）⇒ 不重复查 ✓（层次写进两边表头 ✓）；
4. **旧实现（第四十手那份"照源码实现" ✗）已退役** ✓（2026-10-10 用户定 ✓ ⇒ 删件 ＋ 清引用 ✓，
   见 §★ 工具沿革 · 退役记录 ✓）。

---

## 五十二、状态栏**可信度** ✓（2026-10-10 第五十二轮 ✓ —— 用户报「删任意一根线 **也还是布线完成**」✗）

### ① 症状 ✓（用户原话，**本条就是验收标准** ✓）

> 「`pixel-pcb-v82.fzz` 三个视图，都是**布线完成**。但是有问题啊，我在三个视图里**随意删除任意
>  一根导线，也还是布线完成**。」

⇒ 按用户的预期：删掉一根线本该报「还有 N 条未布」✗ ⇒ 现在永远说「完成」✗ ⇒ **状态栏不可信** ✓。

### ② 机理 ✓（**照源码**，逐条可核 ✓；唯一实现 = 库仓 `tools\pcb_status.py` ✓）

本项目**没有**再猜 ✗：把 Fritzing 状态栏的算法整个复刻了一遍 ✓（出处写进 `pcb_status.py` 文件头 ✓），
并在四个**用户读过状态栏**的文件上**逐字对上** ✓ —— **这是本轮结论的立足点** ✓：

| 文件 | 用户读到的 Fritzing | 本探针（PCB 视图） | 对不对得上 |
|---|---|---|---|
| `pixel-pcb-v68.fzz` ✓ | 「三视图都正确」 ✓ | **M=9、K=0** ✓ | ✓ |
| `pixel-pcb-v81.fzz` ✗ | 「**7 中的 5** 网络布线完成，**2** 个连接仍然需要布线」✗ | **M=7、K=2** ✓ | ✓ |
| `_work/v76.4_byHand.pre-nets.fzz` ✗ | 同上 ✓（已截图核 ✓） | **M=7、K=2** ✓ | ✓ |
| `pixel-pcb-v83.fzz` ✓ | 「三视图都**布线完成**」 ✓ | **M=9、K=0** ✓ | ✓ |

**（1）"还剩几条"是怎么算的** ✓：`GraphUtils::scoreOneNet`（`utils/graphutils.cpp:447` ✓）——
取该网的**零件连接器项**做图，边只认这几路（`464`–`560` ✓）：
① 同脚跨层 ✓；② 两个**可见** `Symbol` ✓；③ 同件内同 `bus` ✓；④ 连到 `Wire`（且 `wireFlags & 本视图的线旗`
✓）⇒ `Wire::collectChained` 的**末端** ✓；⑤ 连到 `Part` 且本视图线旗含 `NormalFlag`（**只有面包板视图** ✓）；
⑥ 连到**可见的** `Breadboard` ⇒ `GraphUtils::collectBreadboard` 的末端 ✓。
然后 **K = 该网连通片数 − 1** ✓（`573`–`596` ✓，不是"没连上的脚数" ✗）。

**（2）"算不算一张网"** ✓：`SketchWidget::updateRoutingStatus`（`sketch/sketchwidget.cpp:6968` ✓）——
每张网先 `collectEqualPotential`（`connectors/connectoritem.cpp:1340` ✓，走 `connectedToItems()` ∪ 件内 bus
∪ 同脚跨层 ✓），再 `collectParts`（`1413` ✓，**丢掉** Wire/Note/Logo/Hole/Ruler ✗）、再按
`attachedTo()->isEverVisible()` 过滤 ✓，最后 **`partConnectorItems.count() <= 1` ⇒ 整张网被跳过** ✗
（`7013` ✓）。★ `connectedToItems()` 在**读盘时**由**本视图**的 `<connect>` 恢复 ✓
（`sketchwidget.cpp:496`「now restore connections」＋ `615 handleConnect` ✓），而 `<connect>` 的**目标
只在本视图里找** ✓（`items/itembase.cpp:559`：`connector->connectorItem(m_viewID)` ✓）。

**（3）★ 为什么"删了也还是布线完成"** ✓（**可证** ✓，不是"感觉" ✗）：
面包板在 **PCB／原理图视图里 `setEverVisible(false)`** ✓（`sketch/pcbsketchwidget.cpp:441` ✓、
`schematicsketchwidget.cpp:146` ✓ —— 源码原话「don't need to see the breadboard in the other views
but it's there so connections can be more easily synched between views」✓）⇒ 上面的 ⑥ 分支**什么都不加** ✗
⇒ 在这些视图里 K = **铜的裂片数 − 1** ✓。于是：

* **单刀切开一张网** ⇒ 每一片**各自内部连通** ⇒ **每片 K = 0** ✓；
* 片里**只有 1 只零件脚**的 ⇒ 被 `7013` **整片丢掉** ✗ ⇒ 它连"没布"都不算 ✓；
* ⇒ `netCount == routedCount` **恒成立** ⇒ 文案**恒为** `Routing completed` ✓。

⇒ **∴「删任意一根线 ⇒ 报未布」在 Fritzing 里物理上做不到** ✗（**任何**文件都一样 ✗，不是本文件的病 ✗）。
反过来说：v81 之所以会"变" ✓，是因为那 94 条跨视图记录让"并网后的组"**比铜大** ✗ ⇒ 修掉 glue
就**必然**让状态栏对删线失去反应 ✓ —— **两害相权，取"数字对"** ✓。

★ 顺带**证伪**了本轮开始时的一条猜测 ✓：「上一轮删 94 条记录 ⇒ 把 PCB 视图的"脚 ↔ 网"成员关系弄空 ✗」
—— 实测 **M 反而从 7 回到 9** ✓（`v81 → v83`：M 7→9 ✓、K 2→0 ✓）⇒ **网模型没有空** ✓。

### ③ 改了什么 ✓（**只动"建构用件"的 `pcbView` 段** ✓ —— 铜／摆位／走线**一个字节没动** ✓）

新工具 ✓ `tools\fz_trim_construct_views.py`（`--check` ✓ / `in out` ✓）：把 `Breadboard1` 的
**整个 `pcbView` 段**删掉 ✓（第五十一轮已经把它里面的 94 条跨视图声明删干净了 ✓ ⇒ 这段现在
**一条声明都不剩** ✗，只剩 46 条**空 `<connector>`** ＋ 一段**看不见的** `<geometry>` ✗）。
理由（照源码 ✓）：面包板在 PCB 视图里 `setEverVisible(false)` ✓ ⇒ 它对网表**本来就毫无作用** ✗ ⇒
把段删掉只是让「**建构用件只活在面包板视图里**」这条原则**落到文件结构上** ✓（以后谁再往里写记录 ✗
也不会**悄悄**在 PCB 视图里生效 ✗）。

★ **范围（硬约束 ✓）**：只动**面包板类件**的 **`pcbView`** ✓；**原理图视图**用户已"定稿不改" ✗ ⇒
它的 `schematicView` 段（2 条空记录 ✗）**只报告、不执行** ✓（`breadboardView` 段更不许动 ✗）。

**逐项记账** ✓（`view_bytes_diff.py` ✓，两份文件对比 ✓）：实例 164 : 164 ✓；
`<breadboardView>` 共同实例 66 个、**块文本不同 0 个** ✓（拼接哈希 `d08b63ff3564a552` **两侧相同** ✓）；
`<schematicView>` 共同实例 64 个、**块文本不同 0 个** ✓（`e720b6e5a06e9de1` ✓）；
`<pcbView>` 只有 **1** 个块不同 ✓ = `5785`「一侧没有这个视图块」✓（就是删掉的那段 ✓）。
**渲染**：三视图 6 个产物与 v82 **逐字节相同** ✓（`_preview.png` `0E117F01E9696587` ✓／
`_preview.svg` `0192EAA5EDBE159C` ✓／`_bb.png` `F4E677807606A87F` ✓／`_bb.svg` `98E1C27E08D76281` ✓／
`_sch.png` `91FB99E26D9414DF` ✓／`_sch.svg` `B87D1A9736B94F00` ✓）。

### ④ 灵敏度测试 ✓（**新的硬闸门** ✓ —— `tools\pcb_rats_probe.py --sens` ✓）

对**每个视图里的每一根线**（三视图合计 **133** 根 ✓）在内存里删掉 ⇒ 用同一把尺子重算 ✓：

| 视图 | 线数 | 严口径（删完 **K>0**）✗ | 文案变 ✗ | **真断铜（割边）** ✓ | **并联冗余** ✓ | ★ 状态栏**看不见**的断开 ✗ |
|---|---|---|---|---|---|---|
| 面包板 | 36 | **0/36** ✗ | **0/36** ✗ | 27 ✓ | 9 ✓ | **27** ✗ |
| 原理图 | 45 | **0/45** ✗ | **0/45** ✗ | 44 ✓ | 1 ✓ | **44** ✗ |
| PCB | 52 | **0/52** ✗ | **0/52** ✗ | 48 ✓ | 4 ✓ | **48** ✗ |

* **严口径 = 0/133** ✗ —— **不是"没测出来"，是"做不到"** ✓（机理见 ② 的 (3) ✓，并由库仓
  `tools\tests\pcb_status_selftest.py` 的 ② 段用**合成 sketch**独立钉住 ✓：两个件 + 一根线 ⇒ 删线后
  M=0、文案**不变** ✓）；
* **并联冗余**（删了**本来就不该有反应** ✓，因为铜里有并联回路 ✓）逐条留账 ✓：
  面包板 9 根（`Wire90013137/139/141/143/145/147/149/151/153` ✓，都是图例装饰线 ✗）、
  原理图 1 根（`Wire90015360` ✓）、PCB **4 根**（`Wire90013625`＝`90014257` ✓、`Wire90013711`＝`90014468` ✓、
  `Wire90013712`＝`90014471` ✓、`Wire90014159`＝`90015506` ✓）——
  ★ 这 4 根是 **`U1.connector20`(EPAD) ↔ `U1.connector3`(VSS)** 之间的**并联回路** ✓
  （EPAD 的**散热/载流**上通常**故意**多牵几根 ✓）⇒ **本轮不删** ✗（要删得用户点头 ✓）。

⇒ **因此本轮的硬闸门换成"可证可过、且能抓真病"的那一条** ✓（`--sens` 的判定 ✓）：
**每张设计的网在每个视图里都必须"成型"（≥2 只零件脚 ✓）且连通（K=0 ✓）** ✓ ——
它**抓得住**"剥瘦底图"那一类病 ✓（网退化成 1 只脚 ⇒ 直接报 C ✗，v69/v77 就是它 ✓），
而**不奖励**任何"靠删记录换指标"的做法 ✓。

### ⑤ 三视图的"还剩几条"实测 ✓（改前 / 改后并列 ✓）

| 网 | PCB 视图 K（v82 = v83 ✓） | 面包板视图 K | 原理图视图 K |
|---|---|---|---|
| `GND`（9 只脚）| 0 ✓ | 0 ✓ | 0 ✓ |
| `5V`（5 只脚）| 0 ✓ | 0 ✓ | 0 ✓ |
| `RC`（3 只脚）| 0 ✓ | 0 ✓ | 0 ✓ |
| `BR+`（3 只脚）| 0 ✓ | 0 ✓ | 0 ✓ |
| `COIL_A` / `COIL_B`（各 2 只脚）| 0 ✓ / 0 ✓ | 0 ✓ / 0 ✓ | 0 ✓ / 0 ✓ |
| `LED_DIN` / `DATA_IN` / `DATA_OUT` | 0 ✓ / 0 ✓ / 0 ✓ | 0 ✓ / 0 ✓ / 0 ✓ | 0 ✓ / 0 ✓ / 0 ✓ |
| **M（Fritzing 会算成几张网）** | **9** ✓（= 网表张数 ✓） | 25 ✓ | 11 ✓ |
| **文案** | `Routing completed` ✓ | `Routing completed` ✓ | `Routing completed` ✓ |

★ 面包板视图 M=25／原理图视图 M=11（**不是 9** ✗）是**正常的** ✓：面包板视图里**孔也算脚** ✓
（`ModelPart::Breadboard` 在那儿可见 ✓）⇒ 15 只**备用脚**各自 ＋ 它插的孔 = 1 张 2 只脚的小网 ✓；
原理图视图里有 2 个 `RC` 网标签 ＋ 3 个接地符号 ✓（它们**也**是"脚" ✓）⇒ 网被切细 ✓。
**三视图 K 都是 0** ✓ ⇒ 三处「布线完成」**都是真的** ✓。

### ⑥ 验收清单新增一条 ✓（**"状态栏可信度"** ✓ ⇒ ★ 已并入上面的出厂检查，编号 **⑨** ✓ —— 判据原文见该处 ✓）

> **六十八、状态栏可信度**（第五十二轮 ✓）
> 1. `tools\pcb_rats_probe.py <交付件>` ⇒ **三视图 K 都是 0** ✓、**每张网 ≥2 只零件脚** ✓、
>    PCB 视图 **M = `pixel_nets.py` 张数** ✓ ⇒ exit 0 ✓；
> 2. `tools\pcb_rats_probe.py <交付件> --sens` ⇒ exit 0 ✓（每张设计的网在三视图都"成型且连通" ✓）；
> 3. ★ **用户手测口径** ✓：**在 PCB 视图删任意一根线** ⇒ 状态栏**不会**改口 ✗ —— 这是
>    **Fritzing 自身口径** ✓（见 §五十二 ② 的 (3) ✓，可证 ✓）⇒ **不许**把它当"文件有毛病" ✗；
>    要判"线有没有断"，**用** 1/2 两把尺子 ✓（它们量的正是"Fritzing 眼里的网表" ✓）。

### ⑦ 复现命令 ✓（交付件 = `pixel-pcb-v83.fzz` ✓；工作档 = `_work\v76.4_byHand.fzz` ✓）

```bat
rem 备份 + 就地更新工作档（先删跨视图声明 ✓，再删"建构用件"的 pcbView 段 ✓）
copy _work\v76.4_byHand.fzz _work\v76.4_byHand.pre-nets.fzz
py -3.13 -X utf8 tools\fz_deglue_records.py          _work\v76.4_byHand.fzz _work\_s1.fzz
py -3.13 -X utf8 tools\fz_trim_construct_views.py    _work\_s1.fzz          _work\v76.4_byHand.fzz
copy /Y          _work\v76.4_byHand.fzz pixel-pcb-v83.fzz

rem 验收：五道（原文见 _work\_r52_accept.txt）
py -3.13 -X utf8 %TOOLS%\pcb_check.py              pixel-pcb-v83.fzz --nets=pixel_nets.py   rem ① ✓ 全过
py -3.13 -X utf8 tools\net_group_check.py          pixel-pcb-v83.fzz                        rem ② exit 0
py -3.13 -X utf8 tools\pcb_rats_probe.py           pixel-pcb-v83.fzz                        rem ③ 三视图 K=0
py -3.13 -X utf8 tools\pcb_rats_probe.py           pixel-pcb-v83.fzz --sens                 rem ④ 灵敏度
py -3.13 -X utf8 tools\bb_probe.py                 pixel-pcb-v83.fzz                        rem ⑤a exit 0
py -3.13 -X utf8 _work\sch_probe.py                pixel-pcb-v83.fzz --nets=pixel_nets.py   rem ⑤b exit 0
py -3.13 -X utf8 tests\run_all.py --with-lib                                                rem ⑥ 两个 runner ✓
py -3.13 -X utf8 tools\pcb_status.py pixel-pcb-v83.fzz                                     rem ⑨ 三视图 K=0／PCB M=9 ✓（新 ✓）
py -3.13 -X utf8 tools\pcb_status.py pixel-pcb-v83.fzz --sens                              rem ⑨ 灵敏度 ✓（新 ✓）
py -3.13 -X utf8 _work\view_bytes_diff.py pixel-pcb-v82.fzz pixel-pcb-v83.fzz pcbView breadboardView schematicView
py -3.13 -X utf8 %TOOLS%\render_pcb.py pixel-pcb-v83.fzz pixel-pcb-v83_preview.svg --px 12 --png
py -3.13 -X utf8 %TOOLS%\render_sch.py pixel-pcb-v83.fzz pixel-pcb-v83_sch.png 2200
py -3.13 -X utf8 %TOOLS%\render_bb.py  pixel-pcb-v83.fzz pixel-pcb-v83_bb.png  2200
```

### ⑧ 遗留 ✗（逐条 ✓）

1. ★ **"状态栏对删线有反应"这件事做不到** ✗（**Fritzing 自身口径** ✓，可证 ✓，见 ② 的 (3) ✓）
   —— 我们**只能**给一把**更细**的尺子 ✓（本轮已给 ✓）；要在 Fritzing 里真的看到反应 ✗，
   得等上游改 `scoreOneNet`／`updateRoutingStatus` ✓；
2. **PCB 视图里那 4 根并联冗余** ✓（EPAD↔VSS ✓）⇒ **没删** ✗（散热/载流上可能是有意的 ✓，
   要删得用户点头 ✓）；按同样口径，面包板 9 根图例装饰线 ✓、原理图 1 根 ✓ 也都留账在原地 ✓；
3. **面包板／原理图视图的 K** ✓ 是**本探针**算的 ✓（用户没有在它们上面读过状态栏 ✗ ⇒ 只有 v68/v81/v82
   三个 PCB 读数可核 ✓）⇒ 这两列是**推算**，如实标注 ✓；
4. **旧实现（第四十手那份 ✗）已退役** ✓（2026-10-10 ✓ ⇒ 删件 ＋ 清引用 ✓，
   见 §★ 工具沿革 · 退役记录 ✓）。

---

## 五十三、Gerber「可送板」：`SH-1.0-3P-V` 的丝印**漏进铜层** ✗ ⇒ 修零件层级 ⇒ 复验「可送板」✓（2026-10-10 第五十三轮 ✓）

### ① 现象 ✓（`gerber_check` 实测，不是"看着像" ✗）

用户手工从 Fritzing 导出的那批（`gerber\` ✓）**不可送板** ✗ —— `gerber_check` 判
`exit 1`（**✗4 ⚠11 ✓66** ✓），唯一的硬伤是：

> `copperBottom` 层**最小铜↔铜间距 = 0.0906 mm（3.57 mil）** ✗ @(21.287,2.337) mm
> —— 冲突双方：**线段（光圈 0.1200 mm）**(21.336,2.438)→(21.336,2.489) ↔ **线段（光圈 0.6096 mm）**(22.454,2.032)→(21.412,1.981)

`0.12 mm` 那条不是走线 ✗ —— 它是 **`SH-1.0-3P-V`（`J1`/`J2` 用的那颗件 ✓）的丝印线** ✓：
底铜里凭空多出 **14 段 0.12 mm 细线** ✗（7 条丝印 × `J1`/`J2` 两个实例 ✓），
其中一段与 `J2` 的 24 mil 走线只隔 **3.57 mil < 5 mil**（JLCPCB 能做下限 ✗）⇒ 整批**不可送板** ✗。

### ② 根因 ✓（工具自己归的因 ✓，不是猜 ✗）

件 `SH-1.0-3P-V` 的 **pcb svg** 把 `<g id="silkscreen">` **嵌在** `<g id="copper1">` **内部** ✗。
`.fzp` 的 `pcbView` **只声明图层**（`copper1` / `silkscreen` ✓）、**不声明"哪块图形属于哪层"** ✗
⇒ 归属是 Fritzing 读 SVG 时**按组的 id** 认的 ✓ ⇒ 嵌在铜组里 ⇒ 那 7 条丝印线**被当铜导出** ✗。
**对照件** ✓：`WS2812B-1010` 的 `<g id="silkscreen">` 与 `<g id="copper1">` 是**兄弟**（平级 ✓）⇒ 没这问题 ✓。

### ③ 改了什么 ✓（**只改那一处层级** ✗，坐标／线宽／id／transform **一字未动** ✓）

1. **零件库**（`fritzing-parts-langhua` ✓）：
   - `svg/SH-1.0-3P-V/gen_part.py` 的 `pcb_svg()` —— 丝印组**移出铜组** ✓（并写进函数注释 ＋ 库仓
     `docs/part-dev-guide.md` §5 坑表第 15 条 ✓）；
   - 重跑生成器 ⇒ `svg/SH-1.0-3P-V/svg.pcb.SH-1.0-3P-V_pcb.svg` ＋ `fzpz/SH-1.0-3P-V.fzpz` ✓；
     ★ **面包板／原理图／icon 三个视图逐字节未变** ✓（生成器可复现 ✓ = "只改那一处"的机器证据 ✓）；
   - 新工具 `tools/silk_nest_check.py`（丝印组嵌在铜组里 ⇒ 报 ✗ ✓）。
2. **`.fzz` 里内嵌的那一份**（**关键** ✗ 别忘 ✓）：`.fzz` **内嵌**每个零件的 `.fzp` 与 4 个视图 svg
   ⇒ 只修库里那份**导出时仍会用旧的** ✗ ⇒ 在 `pixel-pcb-v83.fzz` 的副本上做**同一处**层级修正 ✓
   ⇒ 出新版 **`pixel-pcb-v84.fzz`** ✓（只换 `svg.pcb.SH-1.0-3P-V_pcb.svg` **一个条目** ✓，
   其余 35 个条目**逐字节照搬** ✓；sketch 名 `pixel-pcb-v83.fz → pixel-pcb-v84.fz` ✓）。

### ④ ★ **用户要手工复导一次 Gerber** ✓（三行 ✓）

1. Fritzing 打开 `hardware\pixel\pixel-pcb-v84.fzz` ✓；
2. 菜单 **`File → Export → for Production → Extended Gerber (RS-274X)…`**（= `Fabricate` ✓）
   ⇒ `Export` ✓（选 `Gerber` ＋ 勾 `Export all layers`／单位 `Inches` ✓，与 v83 那批同设置 ✓）；
3. 输出目录选 **`hardware\pixel\gerber\`** ⇒ **覆盖**那 11 个文件 ✓（覆盖后新文件名是 `pixel-pcb-v84_*` ✓，
   再把旧的 `pixel-pcb-v83_*` 删掉即可 ✓）。

> ★ 为什么要有这一步 ✓：**本机 Fritzing 的命令行导出是坏的** ✗（老毛病 ✓），无头环境也**跑不了 GUI** ✗
> ⇒ 本轮只能用**等效证明**（下面 ⑤ ✓）—— ✗ 那是**验证手段** ✗，**不是交付件** ✗。
> 复导完直接把 `gerber\` 交给板厂即可 ✓（它就是"修好件之后重新导出"的那一批 ✓）。

### ⑤ 复验数据 ✓（**前后对照** ✓；`gerber\` 一个字节没动 ✓）

| 项 | 修件之前（`gerber\`，--fzz **v83** ✓） | 修件之后（`gerber_verify\`，--fzz **v84** ✓） |
|---|---|---|
| 判定 / 退出码 | **不可送板 ✗**（exit **1**，✗4 ⚠11 ✓66，86 项） | **可送板 ✓**（exit **0**，✗0 ⚠11 ✓74，85 项） |
| 底铜**最小铜↔铜间距** | **0.0906 mm = 3.57 mil** ✗ @(21.287,2.337)（丝印漏铜 ↔ 24 mil 走线） | **0.1414 mm = 5.57 mil** ⚠ @(13.337,10.937)（≤6 mil 常规 ⚠、≥5 mil 可做 ✓；**与丝印无关** ✓） |
| 底铜**孤立铜岛** | **8 块** ✗（前 6 里 4 块直接标"**丝印漏到铜层**" ✗） | **0 块** ✓（"每块铜都接在盘/过孔/件铜上" ✓） |
| 底铜**连通块** | 36 个（最小 **0.02250** mm² ✗ = 碎铜） | 28 个（最小 **0.16250** mm² ✓） |
| 底铜**逐格覆盖归因** | "Gerber 有、模型没有" **6.883 → 6.683** mm² ⚠／**6 块**（4 块件里画的铜 ✓ ＋ **2 块丝印漏铜** ✗） | **4.800 mm² ✓／4 块**（**全是件里画的铜** ✓，**丝印漏铜 0 块** ✓） |
| 底阻焊**开窗线段** | 198 条 | **184 条** ✓（−14 ✓ = 那 14 段丝印不再开窗 ✓） |
| 铜层口径差 `6.883−4.800 = 2.083 mm²` | — | **对上** 14 条丝印的墨迹面积 **17.732 mm × 0.12 mm = 2.128 mm²** ✓（差 2% ✓ = 栅格/边缘口径 ✓） |
| 层齐（铜×2／阻焊×2／丝印×2／板框／钻孔 ＋ 钢网／`.xy` ✓） | ✓ 11 个文件 | ✓ 11 个文件（**不变** ✓） |
| 单位／格式／省略零／轴序／**原点** | ✓ IN／2.3／省略零／AXBY／**板框左下角 y 向上** ✓ | ✓ **逐文件相同** ✓ |
| 板框（闭合 ＋ 对模型） | ✓ 4 段闭合；外沿 **24.9936**／线心 **24.7904** mm；对模型 25.000 差 **0.0064** ✓ | ✓ **完全相同** ✓ |
| 钻孔（刀具 ＋ 逐孔对模型） | ✓ T1 Ø2.200×2／T100 Ø0.600×2／T101 Ø0.300×5；过孔 **5/5** 对上（最大偏差 **0.0027** mm ✓） | ✓ **完全相同** ✓ |
| 45° 旋转盘（G36 ✓） | ✓ 底面 **23** 个 ⇒ 对上 **23** ✓（顶点最大偏差 0.0168 mm ✓） | ✓ **完全相同** ✓ |
| 丝印层本体 | silkTop 3072 段／silkBottom 3008 段，真线宽最小 **0.2000**／**0.1200** mm | ✓ **逐字节相同** ✓（本件那 7 条丝印**本来就在丝印层里** ✓ ⇒ 修的是"多出来的铜" ✗，不是丝印本身 ✓） |
| ⚠ 项（11 条） | 同一批（Fritzing 导出器的既有行为 ✓） | **同样是这 11 条** ✓（逐条同名同数 ✓） |

★ **`gerber_verify\` 是怎么来的** ✓（**等效证明** ✗，不是交付件 ✗；脚本 = `_work\gerber_strip_silk.py` ✓）：
从 `gerber\` 的 `*_copperBottom.gbl` 里**精确删掉那 14 段** draw（判据两条 ✓：① 光圈 = **0.12 mm** ✓；
② 该段两端点与**模型里那 7 条丝印线**逐条对上，容差 0.05 mm ✓ —— 14/14 全对上、**0 段**是"同光圈但没对上" ✓）
＋ 删掉那条已无人用的同名光圈定义 ✓；`*_maskBottom.gbs` 同法删 **14 段**（光圈 = 0.374 mm = 0.12 + 0.254 ✓）；
**其余 9 个文件逐字节照搬** ✓（只把文件名 `v83 → v84` ✓）。★ 脚本**只做整行删除** ✗ 不重排 token ✗
—— 第一版"按 token 重新拼一遍"把 `G54`／`G36*`／`G37*` **吃掉了** ✗ ⇒ 报出"旋转盘对上 0 个 ✗"的**假硬伤** ✗
（已修 ✓：删完 `G36*`／`G37*` 计数 **23 → 23** 不变 ✓）。

★ **模型口径也对了一遍** ✓（另一路 ✓）：`_work\model_clearance.py`（几何走 `pcb_check`／并网走
`<connect>` 声明 ＋ `pixel_nets.py` ✓）⇒ 底铜**不同网**导线的最小铜↔铜间距（含线宽 ✓）：
**v83 与 v84 逐位相同 = 0.5926 mm（23.33 mil）** ✓ ⇒ **几何一个字节没动** ✓。

### ⑥ v84 的验收 ✓（全过 ✓；原始输出在 `_work\_r53_*.txt` ✓）

1. `pcb_check.py pixel-pcb-v84.fzz --nets=pixel_nets.py` ⇒ **判定：✓ 全过** ✓
   （焊盘 45 ✓／走线 52 ✓／过孔 5 ✓／声明 105 条不合格 0 ✓／悬空声明 0 ✓）；
2. `tools\net_group_check.py pixel-pcb-v84.fzz` ⇒ **exit 0** ✓（9/9 网、每张网一块铜 ✓）；
3. `tools\pcb_status.py pixel-pcb-v84.fzz` ⇒ **三视图 K = 0／0／0** ✓、**PCB M = 9** ✓ ⇒ **exit 0** ✓；
4. `gerber_check.py gerber_verify --fzz pixel-pcb-v84.fzz` ⇒ **可送板 ✓**（见 ⑤ ✓）；
5. 库仓 `tools\tests\run_all.py` ⇒ **exit 0** ✓、项目仓 `tests\run_all.py --with-lib` ⇒ 见 ⑦ ✓；
6. **`pcbView` 的铜未动** ✓（两路 ✓）：`_work\view_bytes_diff.py v83 v84` ⇒ 三个视图**逐字节相同**
   （`pcbView` 拼接哈希 `60f31af5e1949fdc` 两侧同一个 ✓／`breadboardView` `557f313560fa1f0b` ✓／
   `schematicView` `303e609516a3fa7b` ✓）；且 `.fzz` 里 **`.fz` 逐字节相同** ✓ ⇒ 摆位/走线/声明
   **一字未动** ✓；渲染三视图：`_bb.png`／`_bb.svg` 与 v83 **逐字节相同** ✓、`_sch.*` 与
   **今天重渲的 v83** 逐字节相同 ✓（v81–v83 那几张 `_sch` 是**更早一版渲染器**出的 ✓）、
   `_preview.*` 按预期变了 ✓（那 7 条线**不再当铜画** ✓）。

### ⑦ 遗留 ✗（逐条 ✓）

1. ★ **两条既有红灯**（**与本轮无关** ✓，别顺手改 ✗）：
   ① `tests\pcb_rats_selftest.py` ④「修法器可复现」✗ —— `fz_deglue_records.py v81` 的产出与交付件
   `pixel-pcb-v82.fzz` 不是逐字节相同 ✗（**v81／v82／修法器本轮都没动** ✗ ⇒ 旧账 ✓）；
   ② `tests\pcb_sens_selftest.py` ③⑤ ✗ —— 它的标定数（133 根／割边 27+9／44+1 ✓）是按**已提交的**
   `pixel-pcb-v83.fzz` 量的 ✓，而**工作区里的 v83**（= 用户实际导出 Gerber 的那份 ✓）是 135 根／28+9／46+0
   ✗ ⇒ 是"**v83 工作区版本 vs 提交版本**"的差 ✗，**不是本轮改的** ✓
   （★ 反证 ✓：**v84 的灵敏度数 = 工作区 v83 的数，逐位相同** ✓ ⇒ 本轮**没动任何一根线** ✓）；
2. ⚠ **底铜 0.1414 mm（5.57 mil）** @(13.337,10.937) mm ✗ —— 落在 `U1`（QFN20）**邻脚一带**（PD2/PD3 那片 ✓）；
   模型侧独立实测：**邻脚焊盘↔焊盘 = 0.2000 mm** ✓、**PD2 那根 8 mil 线↔PD3 盘 = 0.2947 mm（心距，含线宽 0.193 mm）** ✓；
   `gerber_check` 的模型侧同窗口读到 **0.1207 mm** ⇒ 两边**量法**在此处有差 ⚠（G36/栅格/笔宽口径 ✓），
   ⚠ 但**两版都在** ✓（不是本轮引入 ✗）、且 ≥5 mil ⇒ **不挡送板** ✓（记录在案，下一轮想清就清 ✓）；
3. ⚠ **丝印线宽 0.12 mm**（< 嘉立创丝印下限 0.15 mm ⚠ ⇒ 可能印不清 ✓）—— 那是**丝印本身**的问题 ✗，
   与本轮的"漏铜"无关 ✗（改它会动几何 ⇒ 没动 ✓）；
4. ⚠ **库仓里还有 7 件**（`Crystal-3215/3225`、`FPC-05F-12P-H15`、`MX-1.25-2P-H`、`MX-1.25-3P-V`、
   `PH-2.0-3P-V`、`USB-B01` ✓）是**同一老写法** ✗（丝印也嵌在铜组里 ✗）—— 本轮**没动它们** ✗
   （用户只点了 `SH-1.0-3P-V` ✓）；要用到的时候按本件**同一处、同一种**改即可 ✓，
   自检用库仓 `tools\silk_nest_check.py` ✓。
   ⇒ **2026-10-10 第五十四轮已把这 7 件全部修好** ✓（见下 ✓）。

---

## 五十四、库仓**另 7 件**同一老写法（丝印嵌在铜组里 ✗）⇒ **全部修好** ＋ 台账清空 ⇒ 硬闸门（2026-10-10 第五十四轮 ✓）

**用户原话** ✓：「库里另有 7 件同老写法，**现在修了吧**」✓ ⇒ 修**零件库** ✓、台账**清空** ✓、
把这条做成**硬闸门** ✓。**本轮只动零件库**（`fritzing-parts-langhua` ✓）—— 项目仓这边**只报告** ✗。

### 1. 修了哪几件（**实际 7 件** ✓）

`Crystal-3215`、`Crystal-3225`、`FPC-05F-12P-H15`、`MX-1.25-2P-H`、`MX-1.25-3P-V`、`PH-2.0-3P-V`、
`USB-B01` —— 与上一轮台账点名的**完全一致** ✓（再多扫一遍全库也没有别的 ✓：`silk_nest_check` 违例 0 ✓）。

改法 = 与 `SH-1.0-3P-V` **完全同一套** ✓：改**生成器** `svg/<件>/gen_part.py`
（把 `<g id="silkscreen">` 移出 `<g id="copper1">`、放到与铜组**平级** ✓），**只挪层级** ✗
（id / 几何 / 坐标 / 线宽 / `transform` **一字未改** ✓）⇒ 重跑生成器 ⇒ 落盘 `svg.pcb.*.svg` ＋ `fzpz/*.fzpz` ✓。
逐件"嵌在铜里的非铜组"明细：**只有 `silkscreen` 一处** ✗（没有 `outline` / `breadboard` 之类 ✓）；
丝印组里的图元数：`Crystal-3215` 1、`Crystal-3225` 1、`FPC-05F-12P-H15` 1、`MX-1.25-2P-H` 7、
`MX-1.25-3P-V` 5、`PH-2.0-3P-V` 9、`USB-B01` 6 ✓。

**逐件自证** ✓：① 其它视图（面包板/原理图/icon ＋ `part.*.fzp`）**`sha256` 逐字节未变** ✓；
② pcb svg 的 diff **只有层级挪动** ✓（去空白后把丝印块搬回老位置 = 老文件逐字复现 ✓）；
③ `silk_nest_check.py` 复跑 ⇒ 该件不再出现 ✓。

### 2. 项目仓影响 —— **这 7 件一件都没被内嵌** ✓（**只报告** ✗，未改任何 `.fzz` ✗）

把 `hardware/pixel/` 下 **1617 个 `.fzz`** 逐个开 zip 查条目名（**精确 ＋ 子串两路** ✓），
并顺带查了 `hardware/prototype/*.fzz`、`hardware/subboard_4x4/.../*.fzz`、`_work/v83cmp/head_v83.fzz` ✓：

| 件 | 内嵌它的 `.fzz` |
|---|---|
| `Crystal-3215` / `Crystal-3225` / `FPC-05F-12P-H15` / `MX-1.25-2P-H` / `MX-1.25-3P-V` / `PH-2.0-3P-V` / `USB-B01` | **0 个** ✓（全项目仓都没有 ✓） |

⇒ **本轮无需更新任何 `.fzz`** ✓、**不存在**"要重插新件才不丢修复"的文件 ✓（✗ 与上一轮 `SH-1.0-3P-V`
的情形不同 ✗ —— 那件被 **1615 个 `.fzz`** 内嵌 ✓）。

⚠ **仍要记住的一条** ✓（同上轮结论 ✓）：`.fzz` 是**自带 SVG 快照**的 ✓ ⇒ 谁**从旧快照**导 Gerber，
用的还是**那份旧 svg** ✗。现状 ✓：交付件 **`pixel-pcb-v84.fzz` 里已是新写法** ✓（上一轮同步过 ✓）；
历史快照 **`pixel-pcb-v8 … v83`（＋ `pixel-breadboard*` 等）仍是老写法** ✗ ——
**只要不复算/不重导**就没有影响 ✓；将来要从哪份重导，就先按 §五十三 的办法把那份的
内嵌 `svg.pcb.SH-1.0-3P-V_pcb.svg` 换新 ✓（本轮这 7 件**不涉及** ✓）。

### 3. 硬闸门（库仓 ✓）

`tools/silk_nest_check.py`：`KNOWN` 台账**清空** ✓、`--baseline` **删掉** ✗ ⇒ **无白名单** ✓
（判据 = **丝印组必须直接挂在 `<svg>` 下** ✓ = "丝印必须是铜组的兄弟"的等价硬写法 ✓）；
新增 `tools/tests/silk_nest_selftest.py` ✓（合成局 5 例 ＋ 自闭合防假阳性 2 例 ＋ **全库 235 个
pcb 视图违例 0** ✓）⇒ `py -X utf8 tools\tests\run_all.py` **exit 0** ✓（7 个测试脚本 ✓）。
反例自测 ✓：临时造"丝印嵌回 `copper1`"的 svg ＋ fzpz ⇒ 闸门 **exit 1** ✓ 并点名
`丝印的父组 = copper1` ✓；造完**已删** ✓。

★ 库仓细节（含前后 XML、对照图、验据脚本）见 `fritzing-parts-langhua/README.md`
「2026-10-10（第二轮）」一节 ✓。

## 五十五、`R1`/`C1` 换 **0603** ⇒ **`pixel-pcb-v85.fzz`**（2026-10-10 ✓）

**用户原话** ✓：「我想把 `hardware\pixel\pixel-pcb-v84.fzz` 中的 `R1` 和 `C1` 换成 0603 封装的」✓
⇒ 库侧先做 `Capacitor-0603`（与 `Resistor-0603` **同一套紧凑 land** ✓，已提交库仓 `0e91082` ✓），
再把板上两件换掉 ✓。

### 1. 卡在哪（**都量过** ✓，附数字 ✓）

0603 的 land（焊盘 **0.65×0.80**、脚距 **1.45**、丝印 **2.159×0.859**）比 0402（0.55×0.60／0.90／更小丝印）
**每一维都大一圈** ✗ ⇒ 而这个口袋是按 0402 排的 ✗：

| 件 | 卡点 | 实测 |
|---|---|---|
| `R1` **原地** | 上 `D3` 上排盘／下 `L1` 内圈盘 | 只有**一个点**可行（盘心 y=18.872 ✓）⇒ 两边**同时** **+0.250** ✗（µm 级余量 ✗） |
| `R1` 原地 | `COIL_A` 走线 `#10` 斜穿口袋 | 偏一点就 **叠 0.014 mm** ✗ |
| `C1` **原地** | 到 `Via4` 铜盘 | **+0.200** ✗（要 ≥0.25 ✓）⇒ 得**上移** |
| `C1` 上移后 | 与 `R1` 丝印 | 反降成 **+0.024** ✗ ⇒ 与上一条**互相否定** ✗（窗口为负 ✗） |
| `C1` 右移 | 撞 `U1` 丝印 | 右 0.9mm 过得了 `Via4` ✓ 但 `U1` 侧 **−0.276** ✗ |

**也试过"把 `R1` 挪出内孔"** ✗：布线器到任何空地都报 **`起点格空`** ✗（真跑 `gen_routes` ✓；
而 `R1` **原地**时它能把 BR+/RC 布通 ✓ 8/9 ✓）⇒ 只能手画 ✗，而手画的 jog 会**切到 `COIL_A` 的
走线 `#10`** ✓（自写独立探针 `_work/dbg_merge2.py` 实测：`#10 × 手画线` **几何相交** ✓）。

⇒ 用户拍板 ✓：「**B：保 land、砸布局**」＝保 0603 标准 land ✓、挪元件 ＋ 需要时**连 `COIL_A` 一起重布** ✓。

### 2. 做法 ✓（原地小挪 ＋ 三条手工走线）

`R1` 挪到**左下方空地** ✓（相对原盘心中点 **+(−1.00, +1.80) mm** ✓ ⇒ 盘心 (40.725,20.800)／(42.175,20.800) ✓）；
`C1` **上移 0.06 mm** ✓（`Via4` 让开 ✓，`R1` 已远走 ✓）。

三条走线**手工画** ✓（逐字照 Fritzing 亲笔 ✓，工具 `polywire.py` ✓）：

- `BR+`：`R1.connector0` → **(42.0,19.0)** → `D3.connector3` ✓ —— 第二段**就是原来那根** ✓（老走廊照用 ✓）
- `RC`：`R1.connector1` → **(42.9,19.0)** → `C1.connector0` ✓ —— 同上 ✓
- `COIL_A`：`D3.connector5` → 绕**口袋左侧＋下侧** → `L1.connector0` ✓
  `(40.381,17.922) → (40.10,18.60) → (40.10,21.50) → (42.90,21.50) → (43.931,20.322)` ✓
  —— 原 `#10/#11` **斜穿口袋** ✗，新走线**绕外圈** ✓、与两条新手画线**不交** ✓

### 3. 闸门 ✓（`pixel-pcb-v85.fzz`）

| 闸门 | 结果 |
|---|---|
| `pcb_check`（几何／短路／过孔／安装孔／声明 ✓） | **✓ 全过** ✓（⑩ 113 条声明全合格 ✓、⑫ 悬空 0 ✓） |
| `pcb_status` | 三视图 **K = 0／0／0** ✓、PCB **M=9** ✓、文案 `Routing completed` ✓ |
| `check_netlist` | **✓ 9 个网全对** ✓ |
| `fz_deglue_views --check` | 1 条 ✗ = `Breadboard1` 在 schematicView 里也有段落 —— **v84 基线同一条** ✓（早已有 ⚑） |
| `sch_straighten` | 改动 **0** ✓；V3「该直没直」**1 处** = `Wire90014109` 差 0.038 mm —— **v84 基线同一处** ✓ |

渲染 ✓：`pixel-pcb-v85_preview.svg/.png`（走线 56 ✓ 其中弯曲 4 ✓）、`pixel-pcb-v85_sch.png`、`pixel-pcb-v85_bb.png` ✓
（★ 这两个渲染器 `render_sch.py`/`render_bb.py` **只出 PNG** ✓ —— 我原来把它们写成 `.svg` 是错的 ✗，见 §五十六 5 已改 ✓）。

### 4. 本轮入库的工具 ✓（从 `_work/` 提到仓里 ✓）

- **`swap_rc_0603.py`** ✓ —— 换件（按 `.fzpz` 里的 land ✓）＋ 让走线端点**跟着焊盘走** ✓ ＋ 自检 ✓；
- **`drop_wires.py`** ✓ —— 按标题删走线 **并清掉指向它的悬空 `<connect>`** ✓
  （✗ `_work/del_inst.py` 对走线**拒删**声明 ⇒ 留下 **⑫ 悬空声明** ✗ ⇒ Fritzing 会当成"已连通" ✗）；
- **`polywire.py`** ✓ —— 加一条**折线走线**（N 段 ⇒ N−1 个 `Wire` ✓，**两级回指一次写全** ✓）。

★ 遗留 ✗：`_work/fz_move_via.py` 只按「**两条**短线」设计 ✗ —— 本板 `Via4` 实际挂 **4** 条 ✗
（本轮没用上 ✓）；谁要用先修它 ✓。

★ **请打开 Fritzing 看一眼** ✓（AGENTS §10 第 8 步 ✓）：把 `pixel-pcb-v85.fzz` 拖进去，看**草图底部**那句
`N of M nets routed - K connector(s) still to be routed` ✓ —— 我这边六道闸门全过 ✓，但**那句才算数** ✓。

### 5. ★ 续（2026-10-10 ✓）：用户看元件箱发现 —— `R1`/`C1` 的 **PCB 多出一块** ✗

**用户原话** ✓：「如截图所示，电阻和电容元件的 PCB 是错误的」✓
（截图 = 指示栏里 `R1` 的 pcb 小图，红箭头指着**多出来的那一块** ✗）。

**根因（量出来的 ✓）**：`.fzp` 只声明**图层**（`<layer layerId="silkscreen"/>` ✓）；
「哪块图形属于哪层」是 Fritzing **按组的 id** 认的 ✓ —— 而 `R0603`/`C0603` 的 pcb 视图里，
丝印是**一颗裸 `<rect id="silkscreen">`** ✗、**根本没有 `<g id="silkscreen">`** ✗
⇒ 那坨丝印**不属于丝印层** ✗ ⇒ 页面上多渲一块 ✗。
（**全板就这两件这样** ✗：`L1`/`LED2`/`U1`/`D3`/`J1` 的丝印都在组里 ✓ ——
一条命令就能看出来 ✓：`py -3.13 _work\list_parts.py pixel-pcb-v85.fzz` ✓。）

**修法（只挪层级 ✓，几何一字不动 ✗）**：把丝印 rect 装进 `<g id="silkscreen">` ✓
（rect 的 id 改 `silkoutline` ✓ 免得与组同名 ✗；描边色对齐本库写法 `#f0f0f0` ✓）。

- `svg/Resistor-0603/svg.pcb.R0603_…_pcb.svg` ✓（手改 ✓）
- `svg/Capacitor-0603/…` ✓（**跑生成器重出** ✓ —— 它是从 `fzpz/Resistor-0603.fzpz` 克隆的 ✓
  ⇒ 先重打 `fzpz/Resistor-0603.fzpz` ✓、再 `py -3.13 svg/Capacitor-0402/gen_part.py` ✓）

⇒ 重打两个 `.fzpz` ✓、`fzp_check` 全过 ✓、**重新部署 MINE** ✓（`check_deploy.py --fix` ⇒ 一致 2 个 ✓）。

**重新出板 ✓**：`pixel-pcb-v85.fzz` 按**同一套配方**重生成 ✓（换件 → 删 4 根 → 手画 3 条 ✓）
⇒ 板内嵌的两份 pcb svg 已经是修好的 ✓（`list_parts.py` 复验：`R1`/`C1` 都是 `<g id=silkscreen> ✓` ✓）
⇒ 六道闸门**仍全过** ✓（`pcb_check` ✓／`pcb_status` K=0 M=9 ✓／`check_netlist` 9/9 ✓）。

**★ 顺手补了闸门 ✓（这次是「闸门有洞」✗）**：`tools/silk_nest_check.py` 原来只判
「丝印组**不许嵌在铜组里**」✗ ⇒ 对「**根本没有丝印组**」**当合格** ✗✗ ⇒ 又是**用户眼睛**抓到的 ✗。
已补**第二条硬规矩** ✓：「**丝印图元（`id="silkscreen"` 或 `stroke=#f0f0f0/#ffffff`）
必须在 `<g id="silkscreen">` 里**」✓ —— 全库扫出 **10 件**同病 ✗
（**同族电阻** `01005/0201/0402/0805/1206/1210/1812/2010/2512` ＋ 我们的 `Capacitor-0402` ✓），
本轮**只修了用户点名的 2 件** ✓（§0.6 不擅自扩大范围 ✗）⇒ 其余 9 件**待用户点头** ✓。

### 6. ★ 续 2（2026-10-10 ✓）：用户复看 —— **仍**「3 个焊盘、2 个 Pin1」✗ ⇒ 真病根在**铜层**

**用户原话** ✓：「我看了 v85，里面的 R1、C1 的 PCB 仍然错误，竟然仍然是 3 个焊盘、2 个 Pin1，
电阻、电容应该只有两个焊盘的」✓。

⇒ 上一次（第 5 节）修的是**丝印** ✗ —— 那条确实是个真缺陷 ✓，但**不是**这个症状的病根 ✗。
**真病根（量出来的 ✓）**：这批 2024 老写法零件的 pcb 视图是

```
<g id="copper0" transform="A"><g id="copper1" transform="B"> 2 个焊盘 </g></g>   ✗
```

—— **两个铜组都非空** ✗ ⇒ Fritzing 认为这块铜**两层都有** ✗
⇒ 画面上焊盘**多出一份**（背面翻转还会错位 ✓）、连接点标注也跟着多一遍 ✓
⇒ 看上去就是「3 个焊盘、2 个 Pin1」✗✓。

**对照 ✓**：本板**渲得对**的件（`D3`/`U1`/`J1`/`L1`/`LED2`）都是
**`<g id="copper1">` 一层 ＋ `<g id="silkscreen">` 平级** ✓（见 `svg/BAS70BRW/…_pcb.svg` ✓）。

**修法（只拆层、几何一字不动 ✓）**：把外层的 `transform=A` **烘进**内层 `transform=B` ✓
（等效变换 `M = A∘B` ✓）⇒ 再去掉外层那个组 ✓。
可复算 ✓：A=(0.7,0,0,1.04,−9,−5.4) ✓、B=(1,0,0,0.30769232,0,6.9230768) ✓ ⇒ `M=(0.7,0,0,0.32,−9,1.8)` ✓。
**安全验证 ✓**：重出板后 R1/C1 的**盘心逐位未变** ✓
（`R1.c0=(40.725,20.800)` ✓、`C1.c0=(43.000,18.335)` ✓ ⇒ 与拆层前**完全一致** ✓）＋ `pcb_check` 仍 **全过** ✓。

★ **入库的两个「修 + 闸门」工具 ✓**（都带 `--check` 口径 ✓、都不设白名单 ✗）：

| 工具 | 判据 | 本轮修了 |
|---|---|---|
| `tools/fix_silk_group.py` ✓ | 看着是丝印（`id="silkscreen"` 或 `stroke=#f0f0f0/#ffffff`）的图元**必须**在 `<g id="silkscreen">` 里 ✗ | **10 件** ✓（同族电阻 `01005/0201/0402/0805/1206/1210/1812/2010/2512` ＋ `Capacitor-0402` ✓） |
| `tools/fix_copper_nest.py` ✓ | 同目录 `.fzp` 里焊盘**只声明一层** `L` ✓、而 svg 里它祖先链上**还挂着另一个非空铜组** ✗ ⇒ 报 ✓（✗ 声明两层 = THT 件 ✓ 本来就该两层都有铜 ✓ ⇒ 不归它管 ✓） | **7 件** ✓（`Resistor-0603/0805/1206/1812/2010/2512` ＋ `Capacitor-0603` ✓） |

两个闸门现在**全库 0 违例** ✓（`silk_nest_check` ✓ ＋ `fix_copper_nest --check` ✓）。
★ 用户原话那句「**电阻、电容应该只有两个焊盘的**」✓ —— 现在这两件就是
**一层的两块焊盘 ＋ 一个丝印组** ✓，与 `D3` 那类渲得对的件**同形** ✓。

## 五十六、`C2` 也换 **0603** ＋ 电阻/电容全家**改名与结构**收口（2026-10-10 ✓）

**用户原话** ✓（五条一起给 ✓）：
① 「`R1`/`C1` 的 pcb 小图是两块焊盘」✓ ② 「PCB 视图底部是布线完成」✓
③ 指着 `pixel-pcb-v85_图示.svg` ✓ ④ 「`C2` 也换成小尺寸 0603 吧？」✓
⑤ 「一起改成 1/2 吧，把其它电阻和电容元件的也改了，错误结构的也调整下吧」✓

### 1. `C2` → `Capacitor-0603` ⇒ **`pixel-pcb-v86.fzz`** ✓（第 ④ 条）

`swap_rc_0603.py` 加了通用档 ✓：`--swap=<位号>:<库件名>` ✓（可给多次 ✓）——
`C2` 原来是 **Fritzing 核心库**那颗（`a9b4194c…CapacitorModuleID` ✓，焊盘 **1.20×1.10**、
脚距 **1.70** ✓，**斜放 ＋ 在背面** ✓），换成我们的 `Capacitor-0603`（**0.65×0.80**、脚距 **1.45** ✓）。

| 项 | 结果 ✓ |
|---|---|
| 换件 | `moduleIdRef` ⇒ `C0603_9f24e6d1…_1` ✓；**它那 4 根线跟着走** ✓ |
| ★ 独立复核 ✓（`probe_wire_moves.py` ✓，与换件工具**零共享代码** ✗） | 端点动了的**恰好 4 条** ✓（就是挂 `C2` 上的 `Wire90013614/15`、`Wire90014016/81` ✓，各 **Δ0.108 mm** ✓）；另外 **133 条一动没动** ✓、**没增没删** ✓ |
| 包内图形 ✓（独立读 `.fzz` ✓） | `svg.pcb.C0603_…_pcb.svg` = **`connector0pad` ＋ `connector1pad`** 两块 ✓ ＋ `<g id="silkscreen">` 一个 ✓ ⇒ **就是两块焊盘** ✓（第 ① 条 ✓） |
| `pcb_check` ✓ | **全过** ✓（⑩ 113 条声明全合格 ✓、⑫ 悬空 0 ✓） |
| `pcb_status` ✓ | 三视图 **K = 0／0／0** ✓；PCB **M=9** ✓；文案 **`Routing completed`** ✓（第 ② 条 ✓） |
| `check_netlist` ✓ | **9 个网全对** ✓ |

渲染 ✓：`pixel-pcb-v86_preview.svg/.png` ✓（焊盘 45 ✓、走线 56 ✓ 其中弯曲 4 ✓、过孔 5 ✓）。

pixel-pcb-v86 的 PCB 视图（ / / 都是 0603：两块焊盘 ＋ 一个丝印组）

*上图 = `pixel-pcb-v86` 的 PCB 视图（工具 `tools/render_pcb.py` 从 `.fzz` 直接渲染 ✓，不是 Fritzing 截图 ✗）。看三处 ✓：右下 `R1`、中间 `C1`、左上斜放的 `C2` —— 都是**两块的 0603 焊盘** ✓、丝印只是**本体轮廓** ✓、板上没有多余的铜块 ✓。*

另两张（**PNG** ✓）：[`pixel-pcb-v86_sch.png`](pixel-pcb-v86_sch.png)（原理图）、[`pixel-pcb-v86_bb.png`](pixel-pcb-v86_bb.png)（面包板）。

### 2. 电阻/电容**全家**：名字改成 `1`/`2` ✓（第 ⑤ 条前半）

**用户原话** ✓「一起改成 1/2 吧」✓ —— 12 件（`Resistor-01005/0201/0402/0603/0805/1206/1210/1812/2010/2512`
＋ `Capacitor-0402/0603` ✓）的 `<connector name>` 由 `Pin 0`/`Pin 1` ⇒ **`1`/`2`** ✓
（`<description>` 同步 ✓）。
★ **`id="connectorN"` 一个没动** ✗ —— `<connect connectorId>` ✓／`svgId` ✓／`legId` ✓ 全在引它 ✓
（动了就连不上了 ✗）。工具 **`tools/fix_conn_names.py`** ✓（可复查 ✓），入库提交 `884a791` ✓。

### 3. 结构病：**我的闸门有个洞** ✗，补上后立刻又抓到 2 件 ✓（第 ⑤ 条后半）

`fix_copper_nest.py` 的 `declared_layers()` 原来写死 `svgId="…pad"` ✗ ——
而 `SOD-323`/`SOD-523` 的焊盘叫 **`connector0pin`** ✓ ⇒ **一个也匹配不到** ✗ ⇒ 返回**空集** ✗
⇒ 调用方按「不是 1 层」**静默跳过** ✗✗ ⇒ 它报 **0 个** ✓、实际**有 2 个** ✗。

- **补法** ✓：按**元素读属性** ✓（不看顺序 ✗、不看 `pad` 后缀 ✗）；一个都读不到 ⇒ 返回 `None` ✓
  （= 不知道 ⇒ 让调用方**不带声明**去判 ✓，宁可多报给人看 ✓，不再静默放过 ✗）。
- **补完立刻抓到** ✓：`SOD-323`、`SOD-523` 的 pcb svg 里也是
  `<g id="copper0"><g id="copper1">焊盘</g></g>` ✗（**恒等**变换 ✓）= `R1`/`C1` **同一个病** ✓
  ⇒ 拆平 ✓（几何等效 ✓，`fzp_check` 全过 ✓，已部署 MINE 并与仓库逐字节一致 ✓）。
- ★ **还有一个"看不见"要说出来** ✓：`fix_copper_nest` 只收 `svg.pcb.*` 命名的源文件 ✓
  ⇒ `svg/lm393-a3144-hall-3pin/lm393-hall-a3144-breakout-3pin_pcb.svg` ✓ **它看不见** ✗
  ⇒ 现在会**点名报出来** ✓（"报了 0 个"不再等于"全库都没事" ✗）。

### 4. 全库清点：**违规 0** ✓（新工具 `tools/audit_smd_copper.py` ✓）

判据**不另立一套** ✗ —— 它调 `fix_copper_nest.find_nest()` ✓（判据两份实现必然对不上 ✓，
这是本仓屡次踩的坑 ✗）；它只多做两件事 ✓：**清点**"两层都有铜"的件 ✓ ＋ `--dump <件名>` 看嵌套结构 ✓。

> 扫了 **119** 个 pcb svg ✓；两层都有图形的 **21** 个 ✓ ——
> **THT 合法 19** ✓（通孔焊盘本来就在两层 ✓，`.fzp` 确实声明两层 ✓）；
> **判不了 1** ⚠（`lm393-a3144-hall-3pin` 的源目录**没有 `.fzp`** ✗ —— 查它打包好的
> `fzpz/LM393-A3144-HALL-3PINS.fzpz` ✓：三个脚 `copper0`＋`copper1` **各声明一条** ✓
> ⇒ 它正是"老写法的 THT"✓ **不是病** ✓）；**违规 0** ✗✓。

⇒ **第 ⑤ 条收口** ✓：电阻/电容全家（名字 ✓＋丝印组 ✓＋铜层 ✓）＋ `SOD-323/523`（铜层 ✓）
＋ 全库再无同类结构病 ✓。**改的都是"错误结构"本身** ✗ —— 有意义的名字一律没动 ✓
（`SOD-323` 的 `K`/`A`、`LM393` 的 `GND/OUT/VCC` ✓ —— 那不是 `Pin 0` 那种填充名 ✗）。

### 5. 顺手补一个**我自己的疏漏** ✓：交付件里混进了草稿名 ✗

打包脚本按**输出文件名**给包内那层 `.fz` 取名 ✓（`pixel-pcb-v86.fzz` ⇒ 内层 `pixel-pcb-v86.fz` ✓）——
但我上一轮是**先写到草稿名**（`_work\_g0.fzz` ✗）**再拷**成正式名 ✗ ⇒ **草稿名跟着进包了** ✗
⇒ `pixel-pcb-v85.fzz` 里躺的是 `_g0.fz` ✗（Fritzing 显示的草图名就是它 ✗）。
本轮：`v85` 用新工具 `retitle_fzz.py` **只改这一条的名字** ✓（回读自检 ✓：条目数不变 ✓、
`.fz` 内容**逐字节相同** ✓）；`v86` 改成**直接写正式名** ✓（不再经草稿 ✗）。

★ **同类第二件** ✓（量出来的 ✓）：`pixel-pcb-v85_sch.svg` / `pixel-pcb-v85_bb.svg` ✗
**其实是 PNG** ✗ —— 看头 8 字节是 `89 50 4e 47` ✓（这两个渲染器 `render_sch.py`/`render_bb.py`
**只出 PNG** ✓，是我**给了 `.svg` 后缀** ✗，还把名字当成 svg 写进 README ✗）
⇒ 本轮**按真身改名** ✓：`…_sch.png` ✓／`…_bb.png` ✓（v85 的也改了 ✓ —— 内容一字未动 ✗，
只是名字对了 ✓；`v86` 的两张同样出 PNG ✓）。
**对照** ✓：`pixel-pcb-v84_bb.svg`/`_sch.svg`/`_preview.svg` 三张**是真的 SVG** ✓
（头 6 字节 `<svg ` ✓ ⇒ 早先那一轮用的是会出 svg 的路子 ✓）；`_preview` 系列一直是真 SVG ✓
（`render_pcb.py` ✓）。

### 6. 遗留 ✗（**请用户拍** ✓，不擅自动 ✗）

- `svg/lm393-a3144-hall-3pin/` ✓ 与 `svg/PB86-A0/*` ✓（**库仓**）的源目录是当年 fork 进来的老命名 ✓
  （没有 `part.*.fzp` ✗、svg 名也不是 `svg.pcb.*` ✗）⇒ 要不要**统一成仓库现行命名** ✓？
  （要动就得连 `fzpz/` 与 README 元件表一起动 ✓，所以先问 ✓。）
- **工作区里有三个"不是我改的"** ✗，这轮**一律没提交** ✗，请定 ✓：
  ① `hardware/pixel/pixel-pcb-v83.fzz` 在 **10-10 01:53** 被改过 ✓（345 KB → **81 KB** ✓，
     这轮没碰它 ✗）；
  ② `hardware/pixel/pixel-pcb-v84_bb.svg` / `_preview.svg` / `_sch.svg` 三张是早先渲染留下的 ✓
     （未入库 ✓ —— 要的话我一条命令补 ✓）；
  ③ `hardware/pixel/gerber/` 不是我建的 ✗ ⇒ 按 §8「只提交自己创建的文件」**不入库** ✓。
- ★ **请打开 Fritzing 看一眼** ✓（AGENTS §10 第 8 步 ✓）：把 `pixel-pcb-v86.fzz` 拖进去 ✓ ——
  ① 草图**底部**那句 `N of M nets routed - K connector(s) still to be routed` ✓；
  ② 指示栏里 `C2` 的 **pcb 小图**是不是**两块焊盘** ✓（`R1`/`C1` 同此 ✓）。
  我这边六道闸门全过 ✓，但**那两句才算数** ✓（§13：两个声音不行 ✓）。

## 五十七、用户手改版 `pixel-pcb-v86_byHand.fzz` 的检查（2026-10-10 ✓）

**用户原话** ✓：「`…pixel-pcb-v86_byHand.fzz`，我手改了一版，请检查是否合格」✓

### 1. 先量**你改了什么** ✓（`probe_wire_moves.py` ✓，与任何生成器零共享代码 ✓）

| 动作 ✓ | 量出来的 |
|---|---|
| `C1` 上移 | 两盘心 y **18.335→17.835**、**16.885→16.385** ⇒ **−0.500 mm** ✓ |
| `Via3` 上移 | (43.00, **16.00**) → (43.00, **15.40**) ⇒ **−0.600 mm** ✓（挂它的 4 根线跟着 ✓） |
| `R1` 挪位 | 盘心 (40.725,20.800) → (**41.545, 18.898**) ⇒ ≈ **(+0.82, −1.90) mm** ✓ |
| 走线 | 删 4 根（`Wire90015398/15802/15902/16003` ✓）、动 10 根端点 ✓ ⇒ 56 → **53** 根 ✓ ｜新增 **0** ✓ |

用户手改版 pixel-pcb-v86_byHand 的 PCB 视图

*上图 = 你手改的那版（渲染同 `tools/render_pcb.py` ✓）。`R1` 已经挪到 `C1` 正下方、`Via3` 与 `C1` 一起上移 ✓ —— 走线看上去比 v86 干净 ✓。*

### 2. 闸门 ✓ —— **只差一条** ✗

| 闸门 | 结果 |
|---|---|
| `pcb_status` ✓ | 三视图 **K = 0／0／0** ✓；PCB **M=9** ✓；文案 **`Routing completed`** ✓ |
| `check_netlist` ✓ | **9 个网全对** ✓ |
| `pcb_check` ⑩／⑫ ✓ | 声明 **107 条全部合格** ✓；悬空声明 **0** ✓ |
| `pcb_check` ⑧ ✗ | **1 条**：`L1 ↔ R1` 在同一层只有 **+0.2240 mm** ✗（要 ≥ 0.25 ✓，差 **0.026 mm** ✗） |
| `fz_deglue_views` ✓／`sch_straighten` ✓ | 与 v84 基线**同一处** ✓（没恶化 ✓） |

**为什么 ⑧ 是对的（不是假报 ✓）**：那两块都在 `copper0` ✓ —— `R1` 是**背面**件 ✓，
而 Fritzing 把背面件画到 **Copper0** 上 ✓（**源码** `src/items/itembase.cpp:1872-1886` ✓：
`viewLayerPlacement == NewBottom && flippedSMD() ⇒ viewLayerID == Copper0` 才画、
**其余层 return false 不画** ✗）⇒ 本仓 `pcb_pads.part_shapes()` 第 410-415 行就是照这个口径做的层对调 ✓
（证据 = 你导出图里背面件 43 个盘全在 `<g id="copper0">` ✓）。⇒ **两面在这张图上指的是"板子的同一面"** ✓。

### 3. ★ 一条"只补一对会破另一对"的坑 ✓（本轮最值钱的 ✓）

只盯违规的那一对 ⇒ **`R1` 上移 0.030 mm 就够了**（`L1↔R1` ⇒ 0.2540 ✓）✗ ——
可同一时刻 **`R1 ↔ D3` 只有 0.2760 mm** ✓ ⇒ 上移 0.030 ⇒ **0.2460** ✗ ⇒ **又破一条** ✗✗。

⇒ 必须**一次看全部邻居** ✓：新脚本 **`_work/nudge_search.py`** ✓（把 ⑧ 的判据在**内存里**扫一遍
二维网格 ✓，不写任何文件 ✗）。全板"净距 < 0.60 mm"的对一共 5 对 ✓：

```
+0.2240  L1 ↔ R1   (copper0 × copper0)      ✗ 违规（差 0.026）
+0.2674  C1 ↔ U1   (silkscreen × silkscreen) ✓  ← 本来就最紧
+0.2760  R1 ↔ D3   (copper0 × copper0)      ✓
+0.2790  C1 ↔ R1   (silkscreen × silkscreen) ✓
+0.5590  C1 ↔ D3   (silkscreen × silkscreen) ✓
```

**当时给的推荐** ✓：**`R1` 左移 0.35 mm**（Δ = (−0.350, 0)）⇒ 估"全板最小净距 **0.2240 → 0.2674**" ✗。

★★ **这条推荐是错的 ✗ —— 见下面的更正 ✓**（它出自 `_work/nudge_search.py` 的**内存估算** ✗，
而**真闸门**在真文件上量出来是 **0.232** ✗ ⇒ 估算**偏乐观** ✗ ⇒ 我当场把搜索改成**只信 `pcb_check`** ✗）。

⇒ **本版先不合入** ✗（草稿按惯例不入库 ✓，只入库上面那张渲染 ✓）。

### 5. ★ 续（2026-10-10 ✓）：用户按建议挪了一版 ⇒ **方向反了** ✗ ＋ 我上一条推荐**不准** ✗

**用户原话** ✓：「我按你说的改了一下，你检查下，看看移动方向对吗？」

**量出来** ✓（`probe_wire_moves.py` ✓）：这一版**只改了 `R1`** ✓ —— 两个盘心 x
**41.5448 → 41.6437** ⇒ **+0.0988 mm（往右 ✗）**；`y` 没动 ✓，别的件与线都没动 ✓。

| 项 | 结果 |
|---|---|
| **方向** | **反了** ✗ —— 该 **−0.350** ✓，实际 **+0.099** ✗ |
| 那条毛病 | **一点没变** ✗：`L1↔R1` 仍是 **+0.2240 mm** ✗ |
| 为什么"往右"必然没用 ✓（几何 ✓） | 那一对的净距 = **y 方向**的 0.224 ✓（两者在 x 上**还重叠着** ✓）⇒ 往右只会**加深重叠** ✗ ⇒ 恒等于 0.224 ✗ |
| 别的闸门 ✓ | 三视图 **K=0／0／0** ✓、**M=9** ✓、`Routing completed` ✓、**9 网全对** ✓ ⇒ 这一改**没弄坏任何东西** ✓，只是没解决那条 ✗ |

★ **更正我上一条推荐** ✗：`_work/nudge_search.py` 是**内存估算** ✗ ⇒ 它说"左移 0.35 ⇒ 最小净距 0.2674 ✓ 全过" ✗，
而**真闸门**在真文件上是 **0.232** ✗（< 0.25 ✗）⇒ **估算偏乐观** ✗（又是"两份判据"的老毛病 ✗）。
⇒ 立刻改成**只信闸门** ✓：新工具 **`nudge_part.py`** ✓（按 mm 挪一个件 ＋ 把挂在它焊盘上的线端一起挪 ✓、
✗ 内层 `.fz` 名字原样保留 ✓、写前必过 XML 自检 ✓）＋ **`_work/sweep_nudge.py`** ✓
（逐个候选**只**跑 `pcb_check.check()` ✓，判据**不另写** ✗）。

★ **扫描结论：纯挪 `R1` 挪不出来** ✗（两轮共 **195** 个候选 ✓，**没有一个全过** ✗）：

- **竖直方向零余量** ✗：R1 的盘到下方 `L1` 的盘 **0.224** ✓、到上方 `D3` 的盘 **0.276** ✓
  ⇒ 要 0.25 ＋ 0.25 ＝ **0.500** ✗，而可用正好 **0.500** ✗ ⇒ **差一丝放不下** ✓；
- **往左挪** ⇒ 压到**用户自己画的那根 `COIL_A` 线** ✗（走线 #51 `Wire90015686` ✓）
  ⇒ 短路 **0.0196～0.0960 mm** ✗（试过 Δ=−0.45／−0.50／−0.55… ✓ 都卡这条 ✓）。

⇒ **三条出路（请用户定 ✓）**：
① **把 `COIL_A` 那根线绕开** ✓（点头就用 `polywire.py` 重画那一根 ✓ ＋ 把 `R1` 左移到位 ✓，出一版候选 ✓）；
② 换地方／换思路 ✓（范围扫更大 ✓，或换个件调 ✓）；
③ **放宽 ⑧ 的 0.25** ✓（那是用户定的规则 ✓ ⇒ 只有用户能改 ✓）。

★ 全程**没碰用户的文件** ✓：候选都写在 `_work/` ✓（`_try*.fzz`／`_bh_left.fzz` ✓）。

### 6. ★ 续 2（2026-10-10 ✓）：`pixel-pcb-v86.1_byHand.fzz` —— **方向对了** ✓，只差 0.20 mm ✓

**量出来** ✓（`probe_wire_moves.py` ✓，对比上一版 ✓）：

| 用户这一版干了什么 ✓ | 数字 |
|---|---|
| `R1` 挪位 ✓ | 盘心 (41.6436,18.8980) → (**41.3055,18.9060**) ⇒ **Δ = (−0.338, +0.008) mm** ✓ **往左 ✓（方向对了 ✓）** |
| ★ **把 `COIL_A` 那根线的拐角让开** ✓ | `Wire90016001/2/4` 的共用顶点 → (40.266, 18.569) ✓ ⇒ 我上一条说的"往左会压到 `COIL_A` 线"那个坎 ✗ **被解掉了** ✓✓ |

**闸门** ✓：`pcb_status` **✓ 全过** ✓（K=0／0／0 ✓、M=9 ✓、`Routing completed` ✓）；
`check_netlist` **9/9** ✓；`pcb_check` ✗ **还差 1 条 ⑧**：`L1↔R1` = **+0.2218 mm** ✗（差 **0.028** ✗）。
※ 比上一版的 0.2240 **略小** ✗ —— 因为这一版还**往下带了 +0.008** ✗，而那一对的净距是 **y 方向**的 ✓。

**再挪多少够** ✓（`_work/sweep_nudge.py` ✓，55 个候选**只**过 `pcb_check` ✓）⇒ **3 个全过** ✓：

```
Δ = (-0.200, 0)       ← 最小 ✓
Δ = (-0.240, 0)
Δ = (-0.200, +0.040)
```

⇒ 做出来的一版 ✓：**`_work/_v861_fix.fzz`** ✓（**没碰用户的文件** ✗）——
`pcb_check` **✓ 全过** ✓、`pcb_status` **✓ 全过** ✓、`check_netlist` **9/9** ✓、
`fz_deglue_views`／`sch_straighten` 只剩与 v84 基线**同一处**已知项 ✓；
⑧ 变成 **`L1↔R1` = 0.3308** ✓，全板最紧回到本来就是最紧的 **`C1↔U1` 0.2674** ✓。
渲染 ✓：`_work/_v861_fix.svg/.png` ✓。**等用户在 Fritzing 里确认 ✓**（§10.8 ✓）。

## 五十八、~~交付 `pixel-pcb-v87.fzz`~~ ✗ **已撤回**（2026-10-10 ✓）

### ★★ 撤回原因 ✗（**用户点名** ✓，而且**他是对的** ✓）

**用户原话** ✓：「**不能使用 v87**，你修改的版本，`R1.1` 离 `Wire90016002` 过近，**检测程序有 bug 吧**？」✓

⇒ 量了一遍 ✓（`_work/pad_wire_gap.py` ✓，判据用 `pcb_route._pt_seg_d`／`pcb_wire.trace_pts` 的**唯一实现** ✓）：
**`R1.1`（= `R1.connector0` ✓ —— 我们把连接器改名叫 `1`/`2` 之后，"1" 就是 `connector0` ✓）
到 `Wire90016002`（网 `COIL_A` ✓）的铜净距只有 **+0.0352 mm** ✗** ——
比嘉立创 1 oz 最小 **0.127** 还小 ✗ ⇒ **根本做不出来** ✗。**"检测程序有 bug" 说对了** ✓：

> **④b 原来只在"线身真的压住异网焊盘"（`d ≤ 线半宽` ✗）时报** ✓
> ⇒ 「**贴近但没碰上**」整档是**盲区** ✗ ✗ —— 又是**用户的眼睛先看见** ✓（同 §1 那条的来历 ✓）。

已补 ✓：判据改成 **铜净距 < `CLEAR_MM = 0.15 mm`** ✓（与 `pcb_route.CLEAR_MM` 同值 ✓），
措辞分开（压住 / 贴着）✓ ⇒ 库仓提交 **`85b2146`** ✓、规则正文 `docs/pcb-rules.md` **§1b** ✓。

### 各版本的**真实**账 ✓（同一条补齐后的闸门 ✓）

| 版本 | 闸门 | `R1.1` ↔ `Wire90016002` | 结论 |
|---|---|---|---|
| **`pixel-pcb-v87.fzz`** ✗ | ✗ 1 条 ④ | **+0.0352** ✗ | **废** ✗ —— 已从仓库**删除** ✗（git 里还查得到 ✓） |
| `pixel-pcb-v86.1_byHand.fzz` | ✗ 1 条 ⑧（0.2218） | +0.2023 ⚠ 紧但过 | 线侧过 ✓；⑧ 差 0.028 ✗ |
| **`pixel-pcb-v86_byHand.fzz`** ✓ | ✗ 1 条 ⑧（0.2240） | **+0.3196** ✓ 安全 | ★ **线侧安全** ✓；只有 ⑧ 低于 0.25 ✗（仍 > 0.127 ✓） |
| `pixel-pcb-v86.fzz` ✓ | **✓ 无问题** ✓ | +0.1981 ⚠ | **全绿** ✓（自动布局 ✓） |
| `pixel-pcb-v85.fzz` | ✓ 无问题 ✓ | — | 全绿 ✓ |

⇒ **教训**（我这边的 ✗）：我把 `R1` 往左挪了 0.20 mm 去解 ⑧，**解开了那一对、却把它推进了
`COIL_A` 那根线的净距里** ✗ —— 而当时我的闸门**看不到"贴近"这一档** ✗ ⇒ 我才会说"全绿" ✗。
**"闸门看不到的违规" = 不是全绿** ✓ —— 这一条和 §13「不许自证」是同一条 ✓。

### 下一步（请用户定 ✓）

- **① 用 `pixel-pcb-v86_byHand.fzz`** ✓（**你最早点名的那份** ✓）：线侧 **0.3196** ✓ 安全，
  只剩 ⑧ 那条 0.2240 ✗ —— 也就是你上一轮说的「**相当于缩小间距要求**」✓（0.2240 > 嘉立创 1 oz
  最小 0.127 ✓ ⇒ **做得出来** ✓）⇒ 那就**记成明示例外** ✓，我照它提升成 v87 ✓；
- **② 用 `pixel-pcb-v86.fzz`** ✓（自动布局 ✓ **全绿** ✓，但布局不是你手那份 ✓）；
- **③ 想保住 `v86.1` 那套布局** ✓ ⇒ 得把 `COIL_A` 那根线**重画开**（我可以用 `polywire.py` 做 ✓），
  让 `R1` 既离 `L1` ≥0.25、又离那根线 ≥0.15 ✓ —— 我扫过 195 个纯挪候选**没有解** ✗，所以要动线 ✓。

---

### ★★ 结论（2026-10-10 ✓ 用户选 ①）：交付 **`pixel-pcb-v87.fzz`** ＝ `v86_byHand` ＋ **一条明示例外** ✓

- **底稿** ✓ = 用户手改的 `pixel-pcb-v86_byHand.fzz` ✓（**逐字节搬运** ✓，只把包内那层 `.fz`
  的名字改成 `pixel-pcb-v87.fz` ✓）—— **线侧没有妥协** ✓：`R1.1` ↔ `Wire90016002` = **0.3196 mm** ✓
  （≥ `CLEAR_MM` 0.15 ✓）。
- **例外** ✓：`pixel-pcb-v87_exceptions.py`（`ALLOW` **一条** ✓）——
  `⑧ L1 ↔ R1`、`mm = 0.2239` ✓（实测 **0.2240** ✗、规则 0.25 ✗；记 0.2239 = 向下取到 4 位 ✓，
  因为实测是 **0.22399…** ✗，记 0.2240 会"差 1e-5 也不放行" ✗）、
  `who` = 「用户 2026-10-10 批」✓、`why` = 0.2240 **> 嘉立创 1 oz 最小 0.127** ✓ ⇒ **做得出来** ✓；
  同版其它四对都 ≥ 0.2674 ✓。
- **闸门怎么用** ✓：`pcb_check.py <sketch.fzz> --nets=pixel_nets.py --allow=pixel-pcb-v87_exceptions.py`
  ⇒ **✓ 全过** ✓，且**每次都会把那条例外原样打出来** ✓（谁批的／为什么／允许到多少 ✓）—— ✗ 不静默 ✗；
  **不带 `--allow` 时它照旧报那一条** ✓（实测 ✓）⇒ 规则没被改软 ✓；
  比 0.2239 **更差**仍然 FAIL ✓ ⇒ **不会掩盖以后的回归** ✓。
- **交付件** ✓：`pixel-pcb-v87.fzz` ✓ ＋ `_preview.svg/.png` ✓ ＋ `_sch.svg/.png` ✓ ＋ `_bb.svg/.png` ✓。

pixel-pcb-v87 的 PCB 视图（用户手改的布局；唯一例外：L1↔R1 = 0.2240 mm）

*上图 = `pixel-pcb-v87` ✓ —— `R1` 在 `C1` 下方、`Via3`／`C1` 上移、`COIL_A` 绕外圈，全是用户手改的那版 ✓。*

---

### （以下是当时的过程记录 ✓，留着当账 ✓）

**用户原话** ✓：「好的，把 `_work/_v861_fix.fzz` 提升成 v87，并提交」✓
（上一轮他已确认「用一个略小于 0.25 的间距来制板可以」✓，而我们找到了**全绿**的那一版 ⇒ 就不必提例外 ✓。）

### 1. ★ 提交前核对，发现"候选在我核过之后被改过" ✗（这一步救了它 ✓）

照纪律**先核再提升** ✓ ⇒ `_work/_v861_fix.fzz`（mtime 16:13 ✓）**已经不通过** ✗：
`L1↔R1` = **+0.216 mm** ✗。量出来它跟 `v86.1_byHand.fzz` 的差别是 **有人又改过** ✗：

| 改动 ✓ | 数字 |
|---|---|
| `R1` 被**往右挪回** ✗ | 盘心 41.1053 → **41.5115** ⇒ **+0.406 mm** ✗（正是我核过那版的**反方向** ✗） |
| `COIL_A` **又重画了一遍** ✗ | 删 `Wire90016001`／`Wire90016004` ✓、加 `Wire90016003` ✓、`Wire90016002` 的 A 端挪 **1.20 mm** ✗ |

⇒ 用户要的是"**我报过全绿的那一版**" ✓ ⇒ **按输入重新生成**（`v86.1_byHand.fzz` ＋ `R1` 左移 0.200 mm ✓
＝ 当时扫出来的最小解 ✓，可复现 ✓）⇒ 写成 **`pixel-pcb-v87.fzz`** ✓。

### 2. 闸门 ✓（`pixel-pcb-v87.fzz` ✓）

| 闸门 | 结果 |
|---|---|
| `pcb_check` | **✓ 全过** ✓（⑧ 五对全 ≥0.25 ✓、⑩ 声明全合格 ✓、⑫ 悬空 0 ✓） |
| `pcb_status` | 三视图 **K = 0／0／0** ✓、PCB **M=9** ✓、`Routing completed` ✓ |
| `check_netlist` | **✓ 9 个网全对** ✓ |
| `fz_deglue_views --check` | 1 条 = `Breadboard1` 在 schematicView 也有段落 ✓（与 **v84 基线同一处** ✓） |
| `sch_straighten` | **✓ 无需改动** ✓ |

★ ⑧ 的五对（全 ≥0.25 ✓）：
`C1↔U1 0.2674` ✓／`R1↔D3 0.2840` ✓／`C1↔R1 0.2871` ✓／
**`L1↔R1` 0.3308** ✓（原来那处 **0.2240 → 0.3308** ✓✓）／`C1↔D3 0.5590` ✓。
`R1` 终位 ✓：盘心 **(41.1053, 18.9060)** ／ **(42.5553, 18.9060)** mm ✓。
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
