langhua/AuroraTessellation-NFC/hardware/pixel/pixel-breadboard36_preview.png

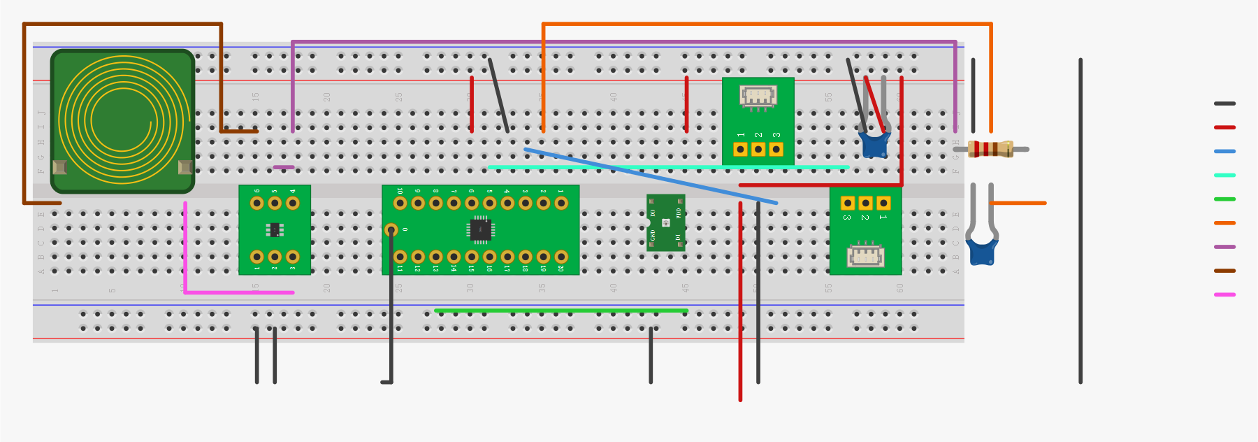
hardware/pixel/pixel-breadboard36_preview.png
