langhua/AuroraTessellation-NFC/hardware/pixel/pixel-breadboard40_preview.png

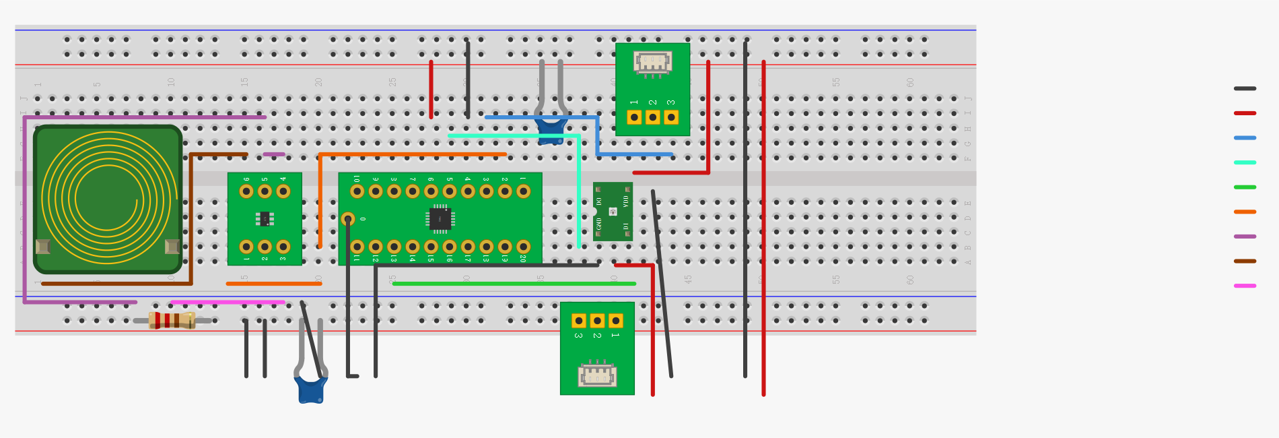
hardware/pixel/pixel-breadboard40_preview.png
