langhua/AuroraTessellation-NFC/hardware/pixel/pixel-breadboard44_preview.png

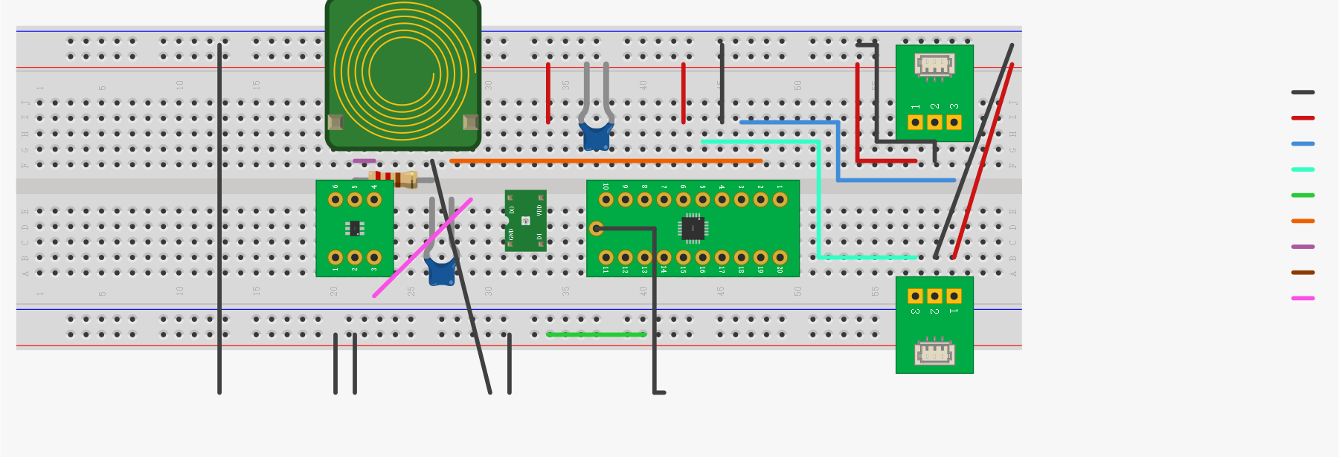
hardware/pixel/pixel-breadboard44_preview.png
