langhua/AuroraTessellation-NFC/hardware/pixel/pixel-breadboard46_preview.png

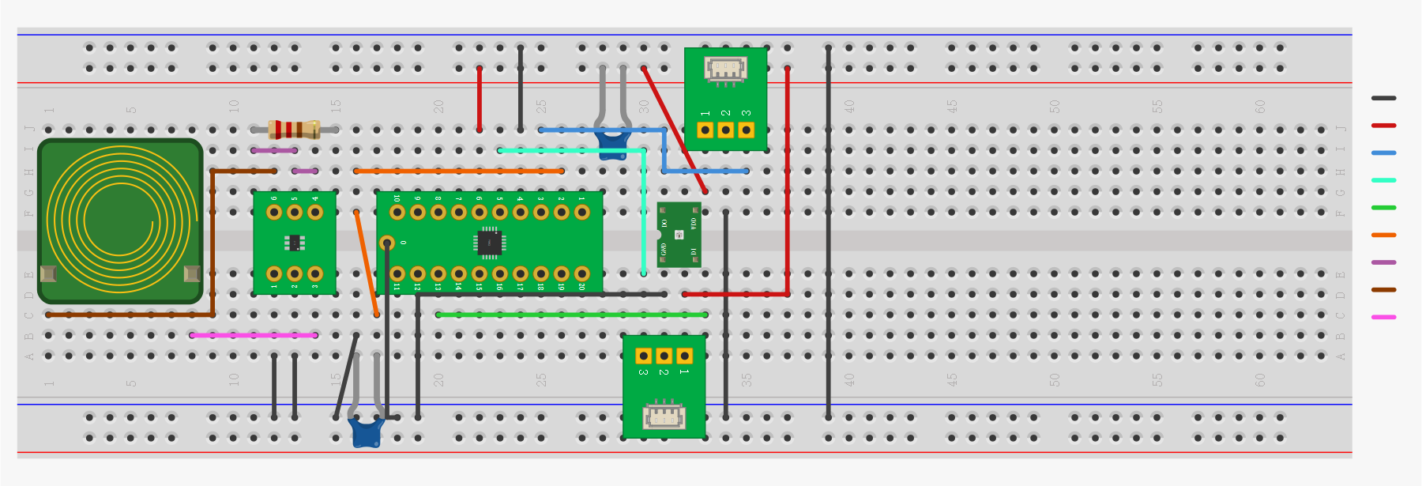
hardware/pixel/pixel-breadboard46_preview.png
