langhua/AuroraTessellation-NFC/hardware/pixel/pixel-breadboard57_preview.png

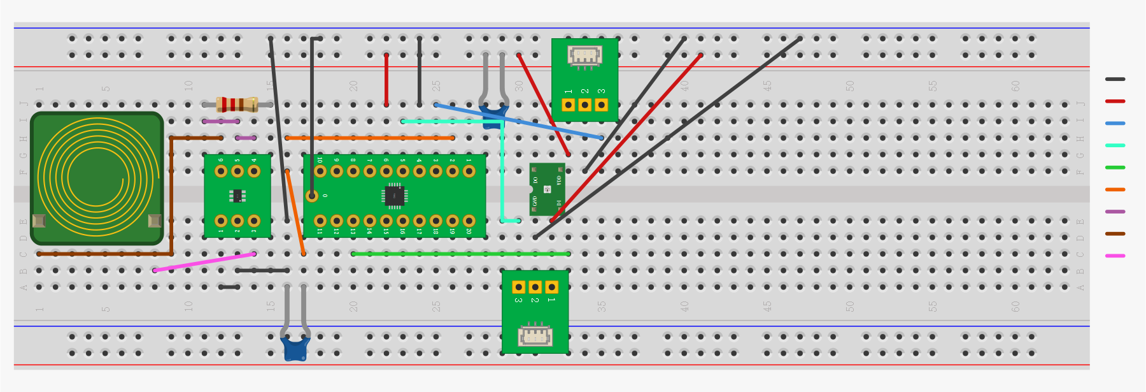
hardware/pixel/pixel-breadboard57_preview.png
