langhua/AuroraTessellation-NFC/hardware/pixel/pixel-breadboard62_preview.png

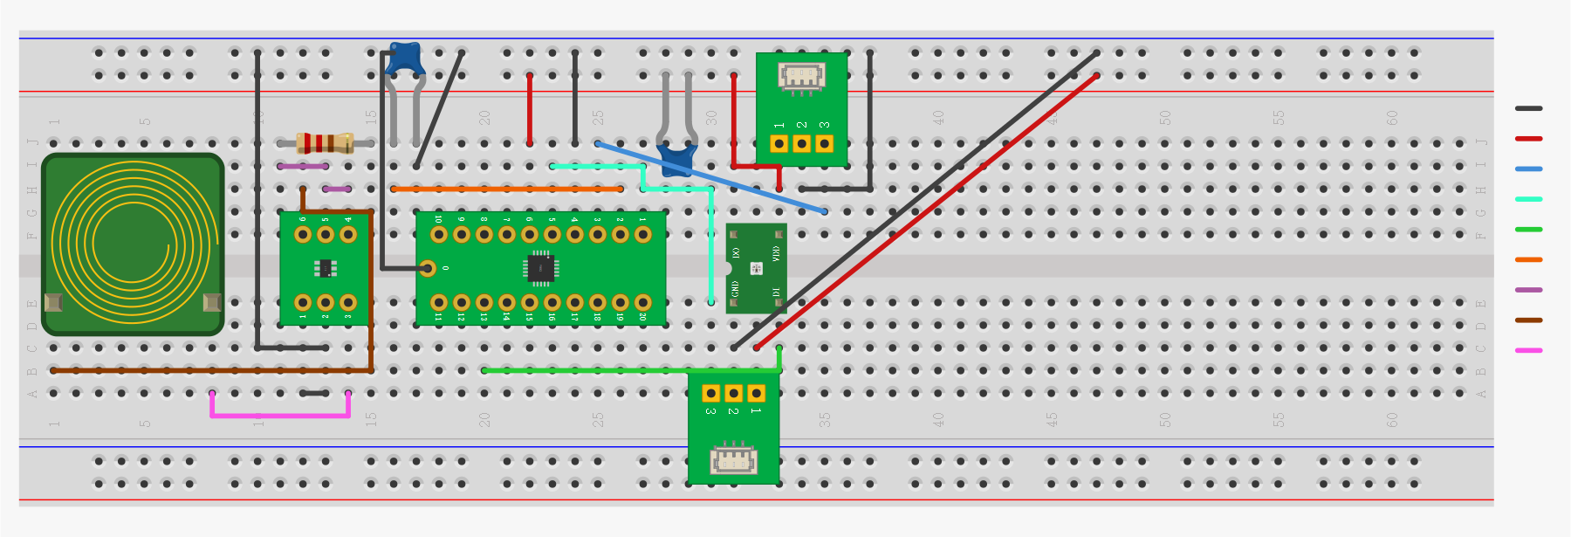
hardware/pixel/pixel-breadboard62_preview.png
