langhua/AuroraTessellation-NFC/hardware/pixel/pixel-breadboard94_preview.png

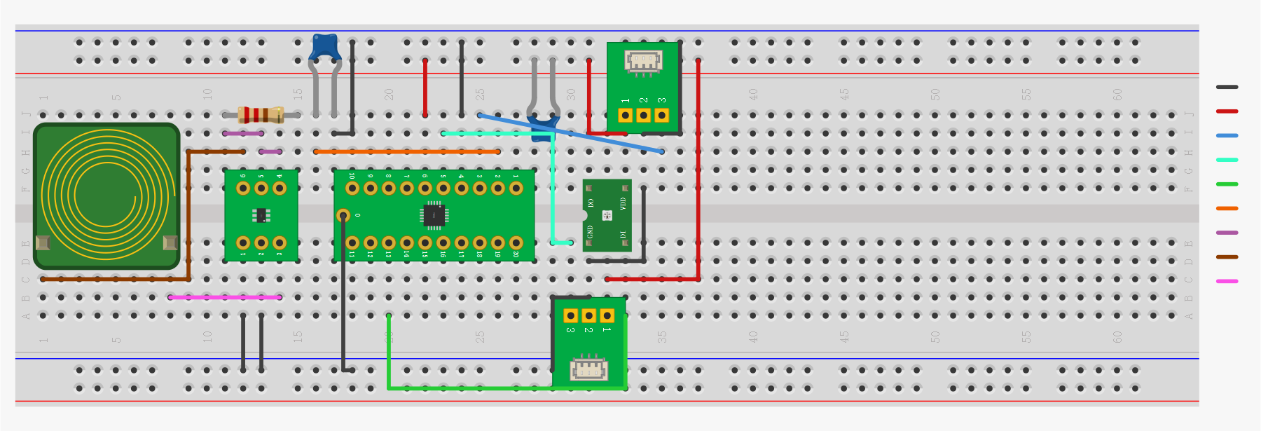
hardware/pixel/pixel-breadboard94_preview.png
