langhua/AuroraTessellation-NFC/hardware/pixel/pixel-pcb-v4_preview.png

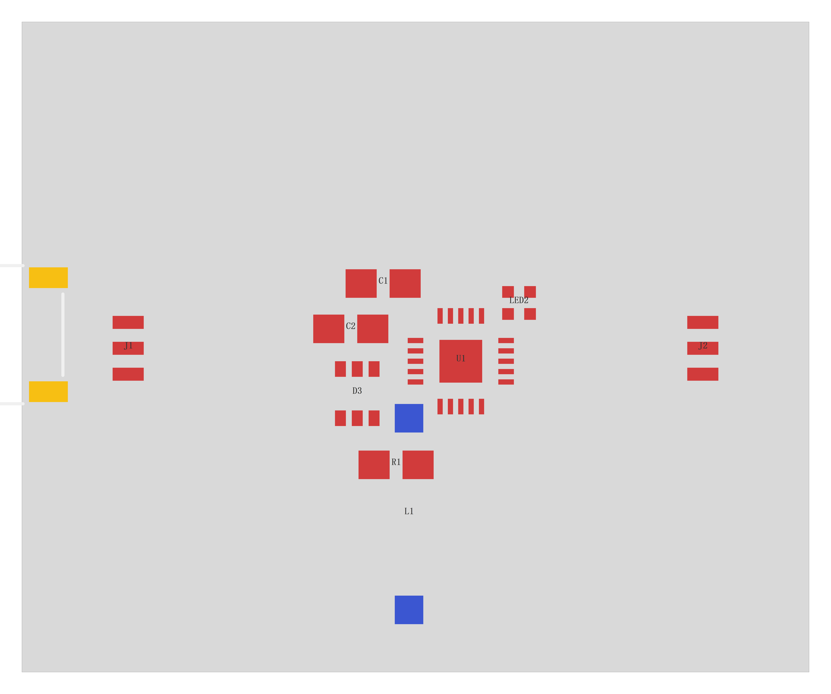
hardware/pixel/pixel-pcb-v4_preview.png
