langhua/AuroraTessellation-NFC/hardware/pixel/pixel-pcb-v15_preview.png

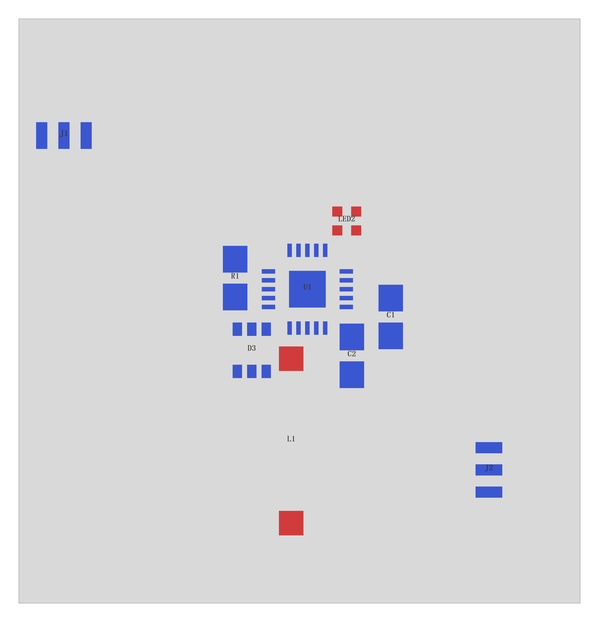
hardware/pixel/pixel-pcb-v15_preview.png
