langhua/AuroraTessellation-NFC/hardware/pixel/pixel-pcb-v17_preview.png

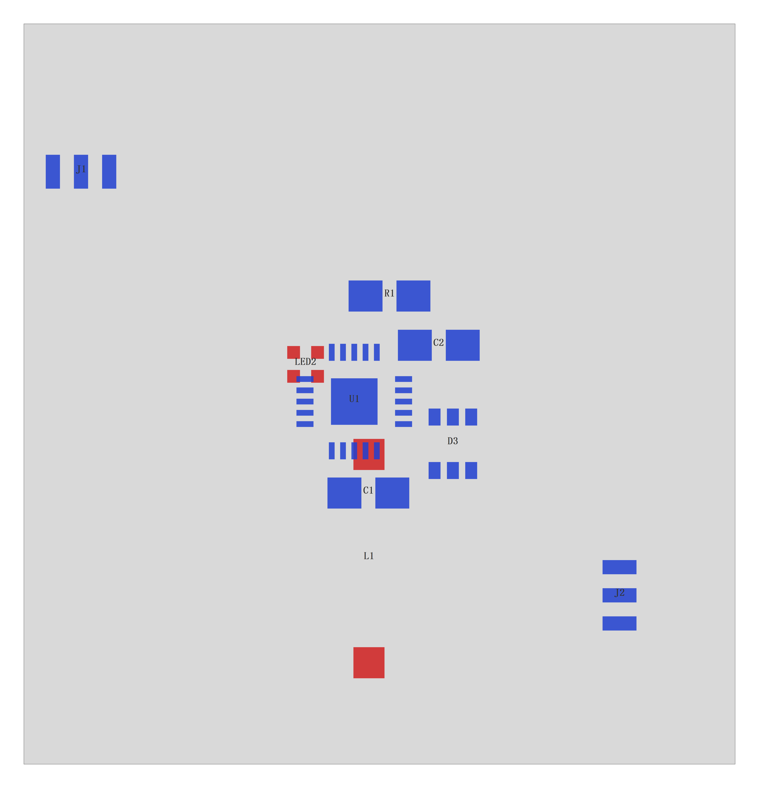
hardware/pixel/pixel-pcb-v17_preview.png
