langhua/AuroraTessellation-NFC/hardware/pixel/pixel-pcb-v25_preview.png

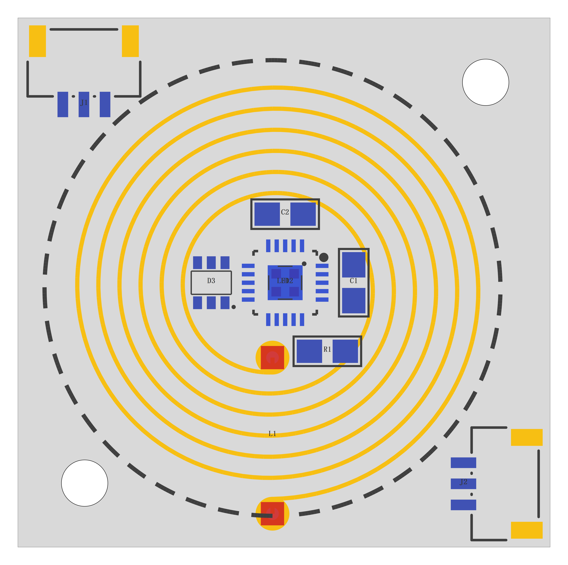
hardware/pixel/pixel-pcb-v25_preview.png
