langhua/AuroraTessellation-NFC/hardware/pixel/pixel-pcb-v26_preview.png

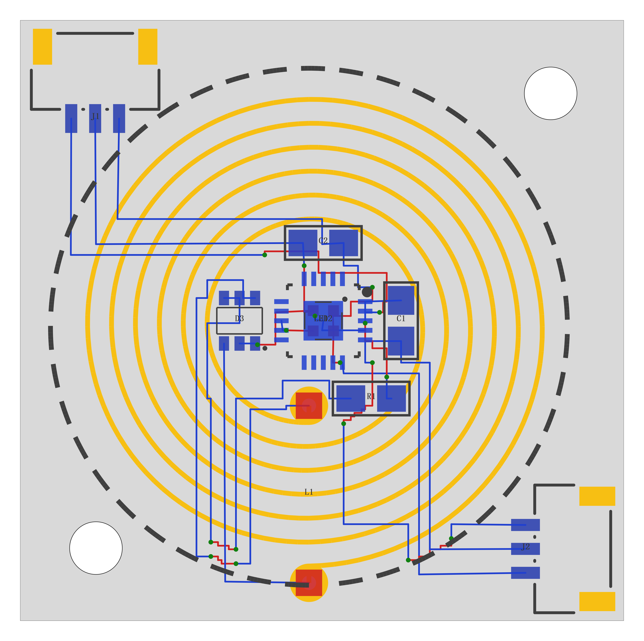
hardware/pixel/pixel-pcb-v26_preview.png
