langhua/AuroraTessellation-NFC/hardware/pixel/pixel-pcb-v48_preview.png

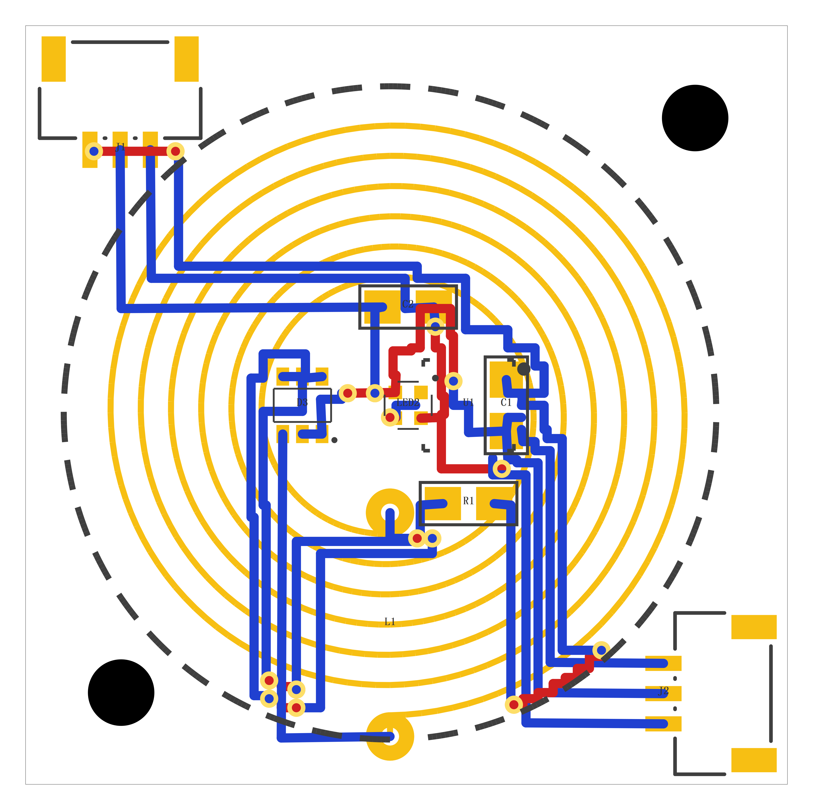
hardware/pixel/pixel-pcb-v48_preview.png
