langhua/AuroraTessellation-NFC/hardware/pixel/pixel-pcb-v50-partial_preview.png

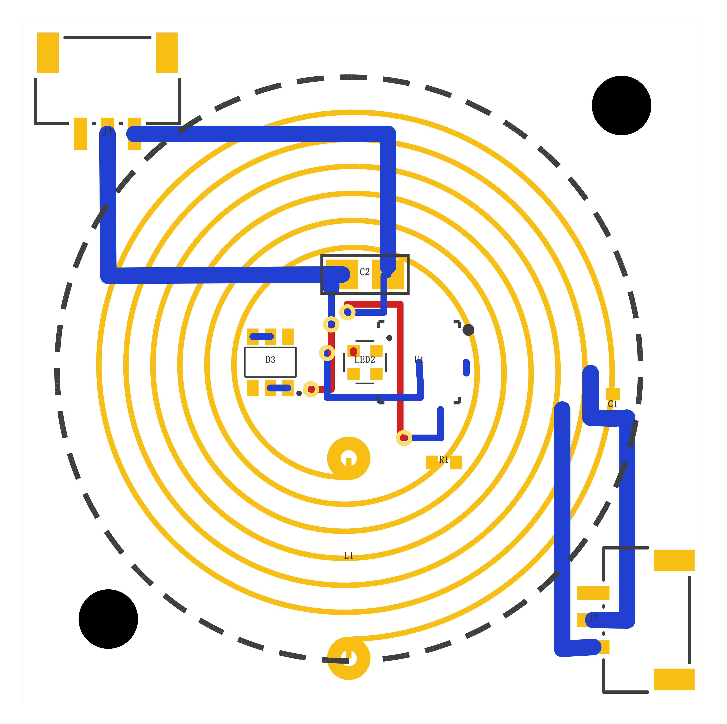
hardware/pixel/pixel-pcb-v50-partial_preview.png
