langhua/AuroraTessellation-NFC/hardware/pixel/pixel-pcb-v51_preview.png

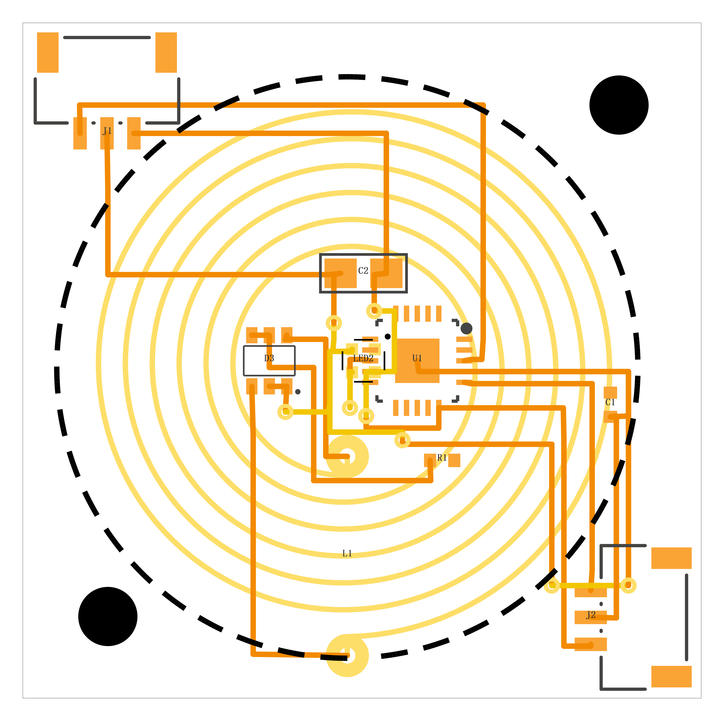
hardware/pixel/pixel-pcb-v51_preview.png
