langhua/AuroraTessellation-NFC/hardware/pixel/pixel-pcb-v78_sch.png

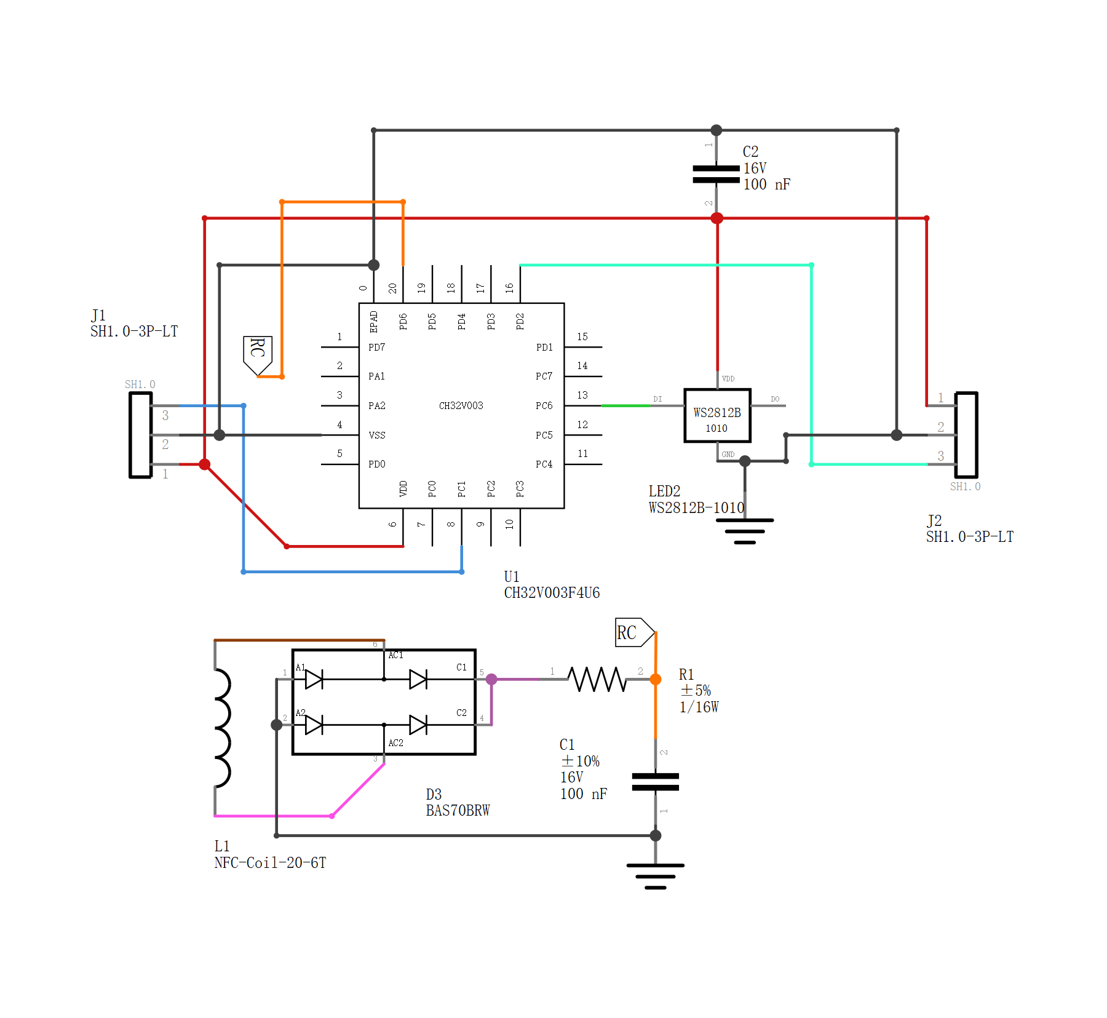
hardware/pixel/pixel-pcb-v78_sch.png
