langhua/AuroraTessellation-NFC/hardware/pixel/pixel-pcb-v83_copperBottom.png

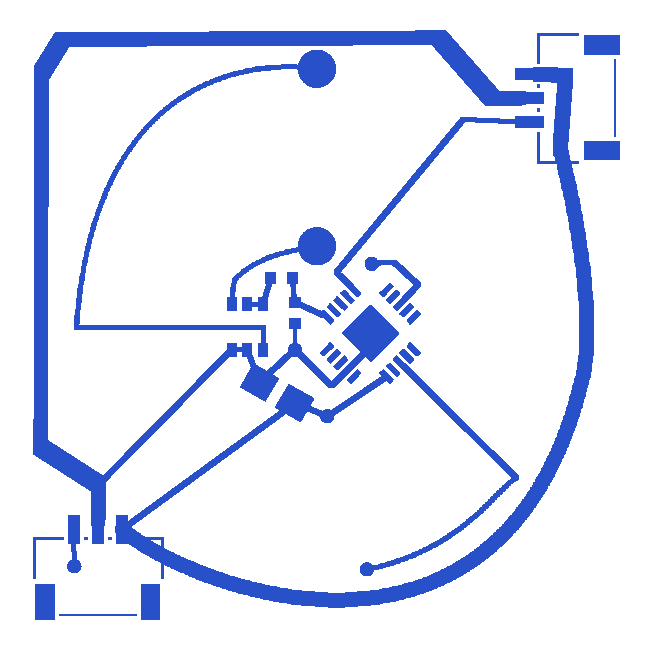
hardware/pixel/pixel-pcb-v83_copperBottom.png
