langhua/AuroraTessellation-NFC/hardware/pixel/pixel-pcb-v83_overlay.png

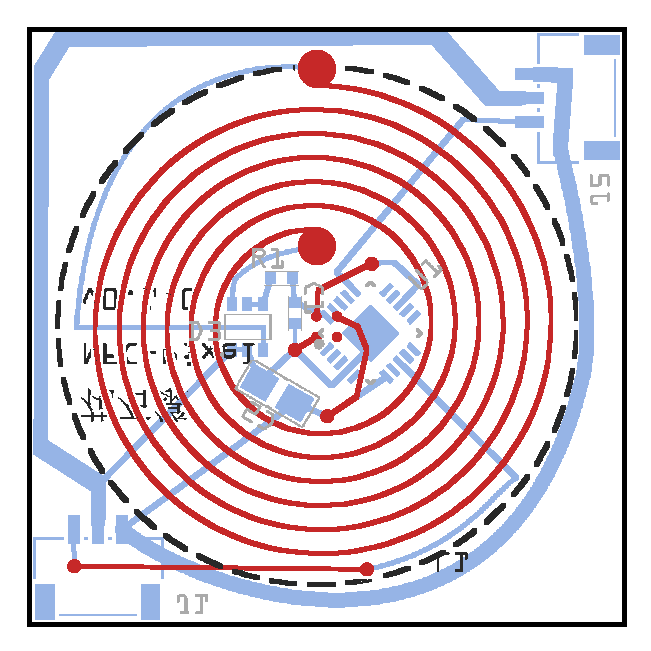
hardware/pixel/pixel-pcb-v83_overlay.png
