langhua/AuroraTessellation-NFC/hardware/pixel/pixel-pcb-基线-板内_preview.png

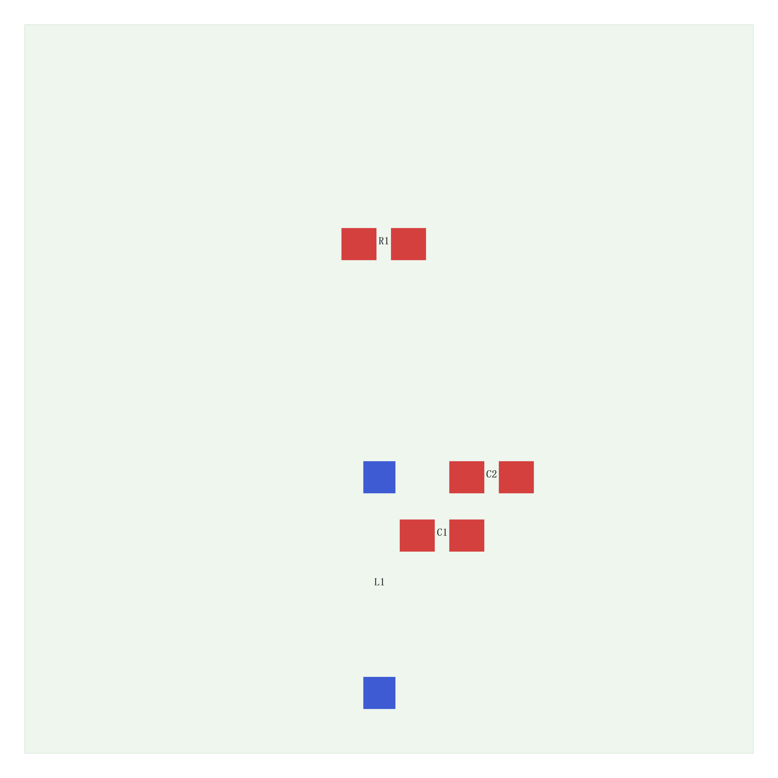
hardware/pixel/pixel-pcb-基线-板内_preview.png
