langhua/AuroraTessellation-NFC/hardware/pixel/pixel-pcb-基线_preview.png

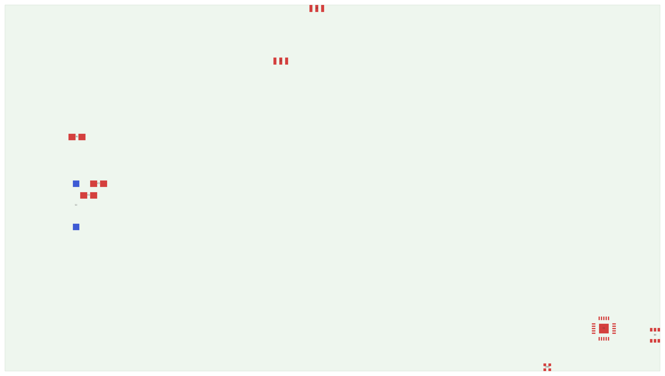
hardware/pixel/pixel-pcb-基线_preview.png
