langhua/AuroraTessellation-NFC/hardware/pixel/pixel-schematic-v7_preview.png

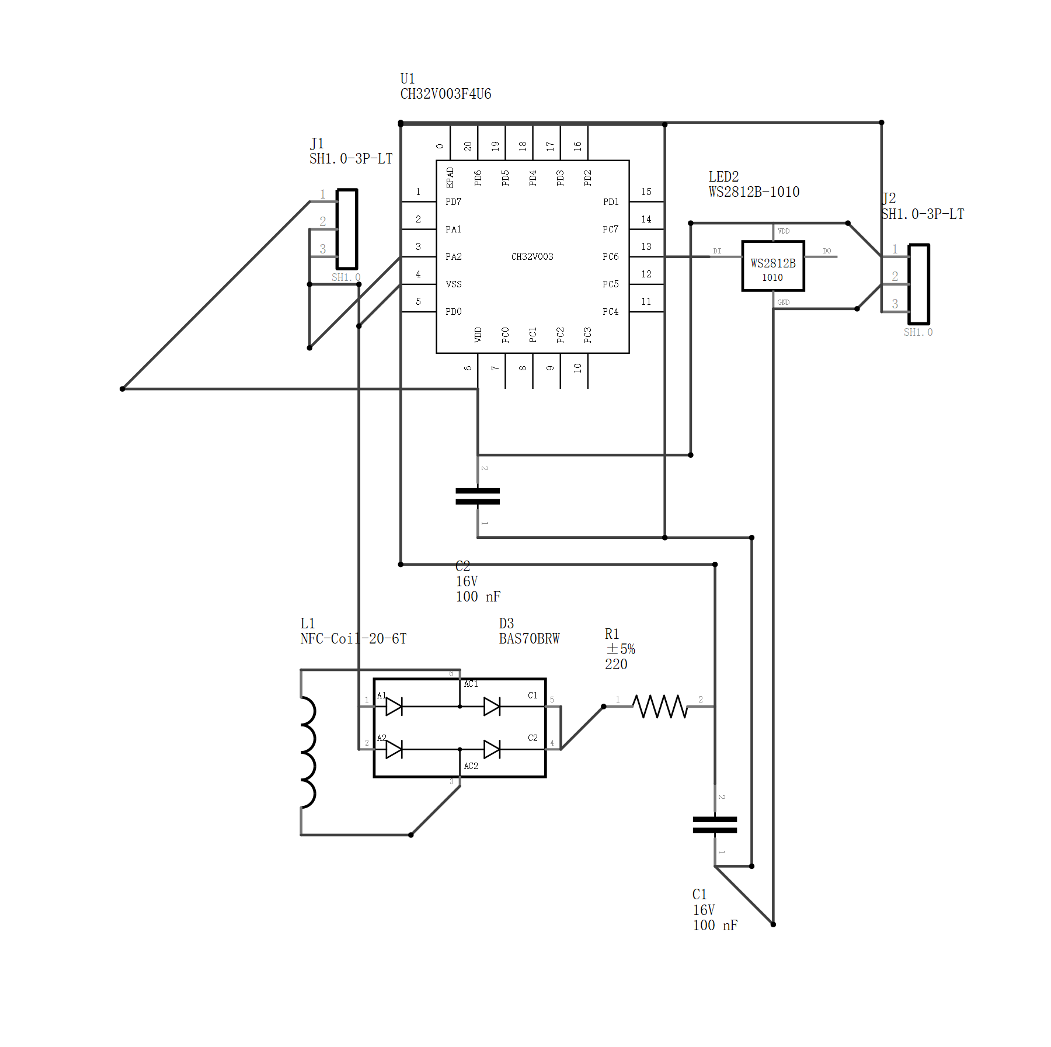
hardware/pixel/pixel-schematic-v7_preview.png
