langhua/AuroraTessellation-NFC/hardware/pixel/pixel-schematic-v9_preview.png

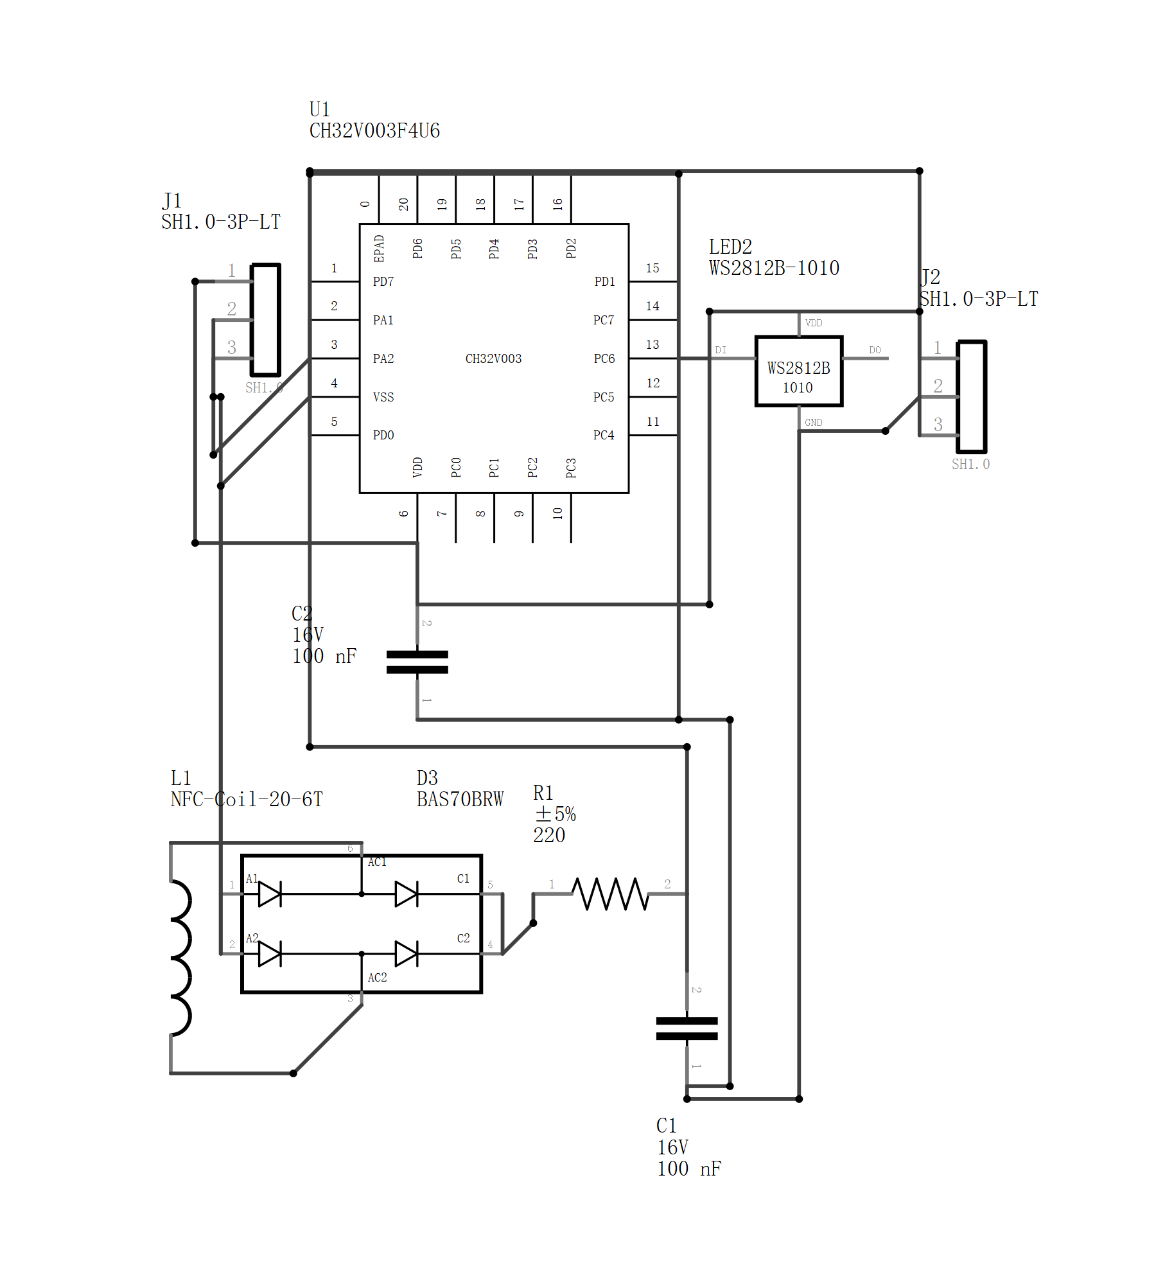
hardware/pixel/pixel-schematic-v9_preview.png
