langhua/AuroraTessellation-NFC/hardware/pixel/pixel-schematic-v10_preview.png

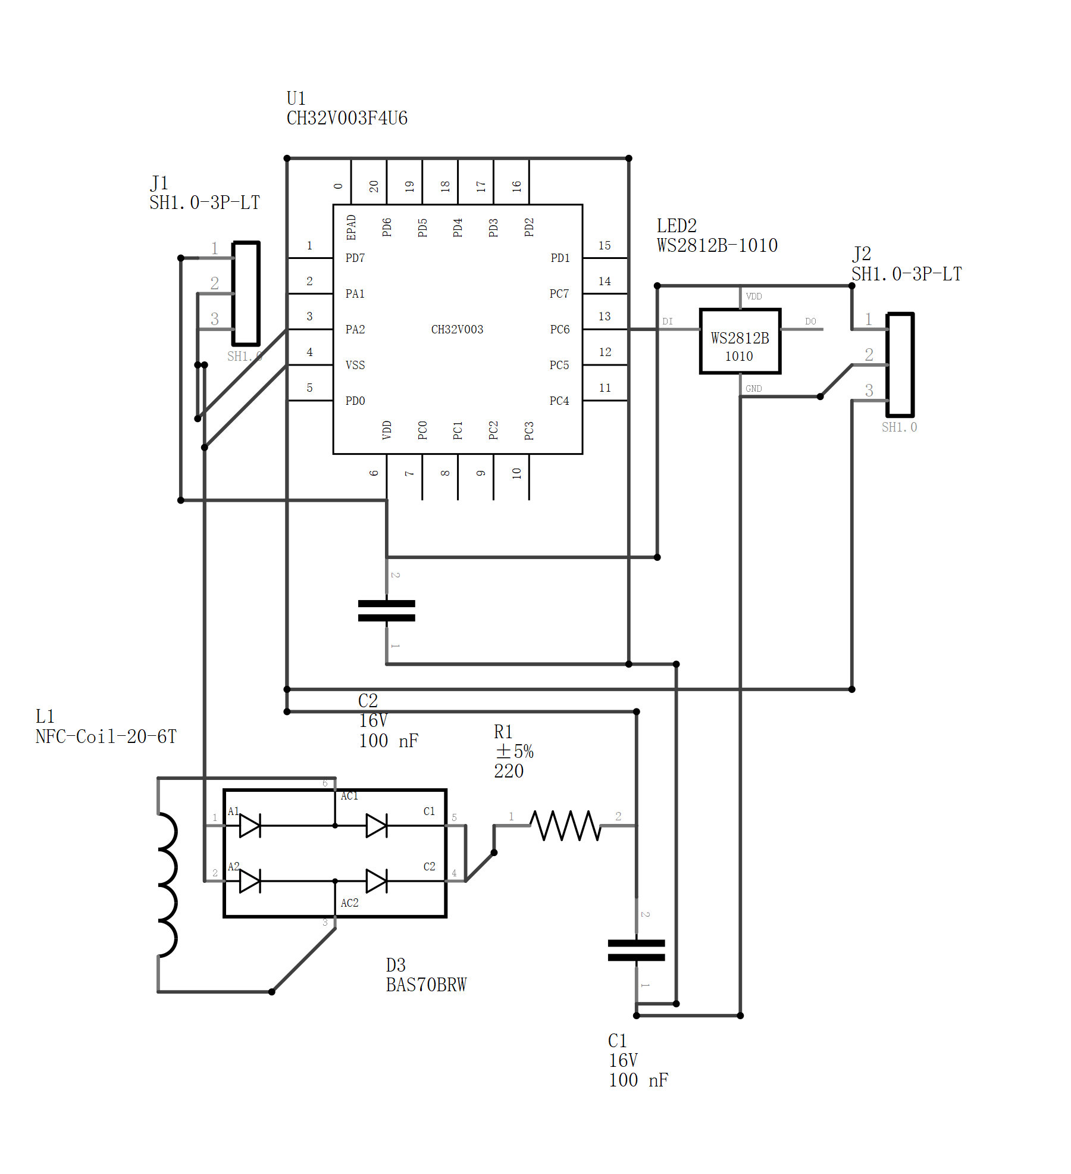
hardware/pixel/pixel-schematic-v10_preview.png
