langhua/AuroraTessellation-NFC/hardware/pixel/pixel-schematic-v38_preview.png

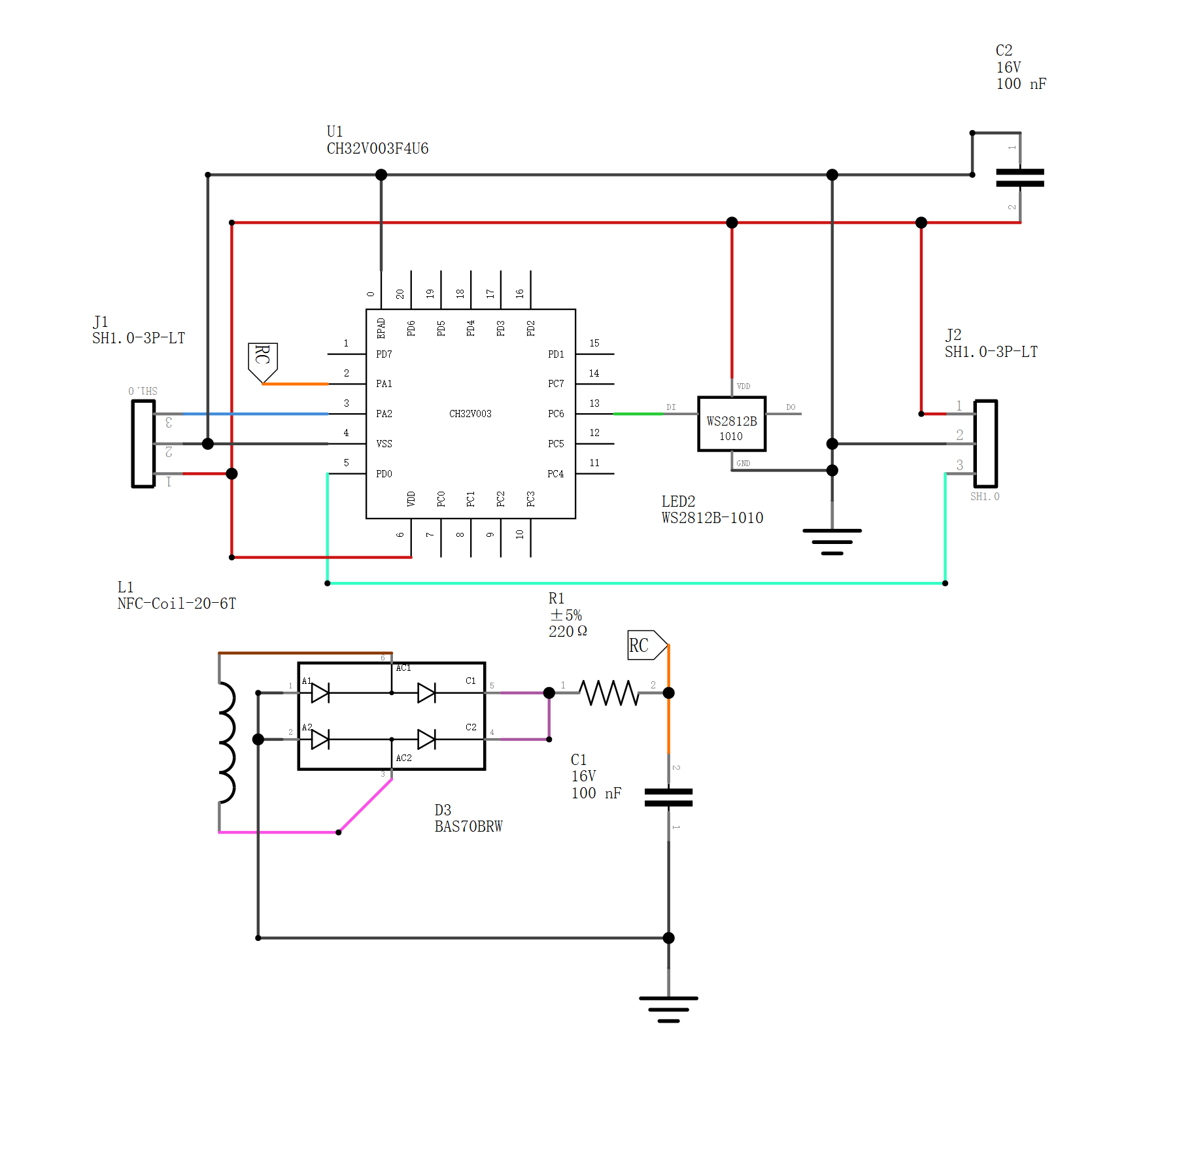
hardware/pixel/pixel-schematic-v38_preview.png
